colemandlut/MP2645A-BMS/design/02_afe-review-opus-r2.md

# 02_afe 第 2 轮独立复核（复核方：Claude Opus；画图方：DeepSeek）

> 时间：2026-09-27 JST
> 输入：
> - 快照 `review/02-r2/`（sch、erc.json、netlist.xml、sch.pdf 第 3 页）；
> - 第 1 轮快照 `review/02-r1/netlist.xml`；
> - `hardware/mp2645a-bms.kicad_pro`（网络类）；
> - 第 1 轮报告 `design/02_afe-review-opus.md`。
>
> 纪律：只读，没有改任何工程文件，没有运行 git。ERC 和网表由我在 `/tmp/r02/` 下独立重跑。
> **判定：P0 = 0，P1 = 0，P2 = 13（第 1 轮沿用 11 条，本轮新增 2 条版面小项）。02 页判为完成。**

## 0. 独立复跑

| 项 | 结果 |
|---|---|
| `cmp hardware/02_afe.kicad_sch review/02-r2/02_afe.kicad_sch` | 一致，快照就是现行图纸 |
| ERC `--severity-all`（根图） | 共 6 条，全部是 `isolated_pin_label`：DSG_G、CHG_G、SRP、SRN、FET_MID、PACK+。这些都是 01 页还没画的网络，与第 1 轮相同，0 error |
| 重跑网表与快照 `netlist.xml` 比较 | 去掉日期和 tstamp 后，diff 为空 |
| **r1 与 r2 网表逐项比较**（按网络节点集合、网络名、器件的 值/封装/LCSC/DNP、网络类） | 连接拓扑差异 **0**，网络名差异 **0**。器件只有 C209–C211 的 Value 字段变了。网络类只有 VCP 变了 |

## 1. 第 1 轮 P1 的落实情况

| # | 核对内容 | 结论 |
|---|---|---|
| P1-1 | C209、C210、C211 的 Value：`100nF 50V` → **`100nF 16V`**。LCSC 仍是 C1525，封装仍是 0402，两者都没变。与 BOM 第 26、27 行一致 | ✅ 关闭 |
| P1-2 | `.kicad_pro` 里的 `*/VC?` 已拆成 `*/VC0` … `*/VC8` 共 9 条。网表中 VC0–VC8 都是 `CELL_SENSE`，VCP 从 `CELL_SENSE,HV_SIG` 变为 **`HV_SIG`**。VTOP、PACKP、VMID、REG_C 仍是 HV_SIG，没有受影响 | ✅ 关闭 |
| P1-3 | 在 PDF 第 3 页目视逐项核对，见下面 9 个小项 | ✅ 关闭 |

P1-3 的逐项核对：
1. 标题栏 comment 已缩短为「8S LiFePO4 200A BMS · MPS MP2797 AFE · 8S 采集与保护」，完全在图框内。
2. 页首的画图过程文字（「第 1 轮已画完…164 个网表节点」）已删除。
3. §10 标题与说明不再重叠。
4. §4 标题已改为「8 串 9 路」。
5. C226 的「100nF 100V DNP」已回到 C226 下方，C220 旁边不再有 DNP 字样。
6. C219 的值已挪离 C226 的红叉。
7. C213、C221 的 GND 标签不再压在引脚上。
8. REG_C 的两个标签已上下分开。
9. SRN_F 与 GND 已分开。

## 2. P2（全部交用户定夺）

**第 1 轮沿用，P2-1 至 P2-11**，原文见 `design/02_afe-review-opus.md`：
1. GATE 类的间距应提到 0.6mm。
2. C212 在 29V 直流偏压下容量下降。
3. C213 在 29V 直流偏压下容量下降。
4. C221 可改用 C0G。
5. NTC 出板线缺少限流和 ESD 保护。
6. BAT+ 缺失时，C8 会反灌 VTOP/BAT+。
7. VTOP 进入 UVLO 后，整包会变砖。
8. 固件要清除 CELL_DEAD 持久标志。
9. CNTCB 10nF 和 CVREF 0402 的余量问题（U-9）。
10. Q201 的功耗上界为 285mW。
11. PACKP 的负向尖峰。

**本轮新增（纯版面，不影响网表）**：

| # | 位置 | 现象 | 建议 |
|---|---|---|---|
| P2-12 | §6，C219 | C219 的值「100nF 100V」挪到了电容左侧，紧挨着 R214 的「100Ω 1%」，读起来像 R214 的第二行参数 | 把值放到 C219 本体右侧（C219 位号的正下方） |
| P2-13 | §6 / §9 | ① C226 的位号压在它自己的 DNP 红叉下面，看不清。② 「§9 电源」标题的下沿贴着第一行说明「U1.45 VTOP…」。③ PACKP 与 C221 之间仍然叠着两个 `PACKP` 标签（与第 1 轮 REG_C 的情况相同） | 位号挪到红叉外面；标题下移约 1 格；删掉一个多余的标签 |

## 3. 覆盖清单（本轮）

- ⓪ 断线/死头、⓪b 同网多名：ERC 复跑为 0 error；网表拓扑与 r1 完全相同。第 1 轮已逐项核对的结论（48 脚、Figure 27/Table 18 外围件、均衡、耐压、极性件、J5、跨页接口）仍然有效。✅
- LCSC 与 BOM：53 个位号全部一致。C222–C226 带 dnp 属性，图上有红叉。✅
- 网络类：CELL_SENSE 与 HV_SIG 不再交叉匹配。✅
- 可读性：第 1 轮的 P1-3 已全部关闭。剩下的两项小瑕疵列为 P2-12 和 P2-13。✅
- 未核：01 页全部内容、PCB 布局（与第 1 轮相同）。
