colemandlut/MP2645A-BMS/design/02_afe-draw-report.md

# 02_afe 画图报告（第 1 轮 · 分段 A + B）

> **分段 B 的内容在 §6**（2026-09-27 17:00–17:15 JST），§1–§5 是分段 A 的原文（只订正了 §5.1 的
> D201 脚号说法，见 §6.5）。
> 时间戳：2026-09-27 16:00–17:15 JST　画图方：Claude（DeepSeek 画图泳道）
> 设计依据：`design/02_afe-spec.md`（含 §12.1b 用户决定 2026-09-27）
> 本段写入的文件**只有 4 个**：`hardware/02_afe.kicad_sch`、`hardware/gen/gen_02_afe.py`、
> `hardware/gen/check_02_layout.py`、本报告。库 / BOM / docs / 根图 / 其它子图都没动，
> 没跑 `tools/gen_kicad_skeleton.py`，没碰 git。

---

## 0. 本段结论（一句话）

分段 A 的三块（U1 48 脚、§9 电源、§6 高边驱动）已画完并跑通：
`check_02_layout.py` 检查 1–9 **全 PASS**（含 79 项网表逐脚核对），
`kicad-cli sch erc` 只剩 **18 条 `isolated_pin_label`**，全部是「标签挂在一根光棍上等 B/C 段接件」的预期现象，
已逐条列在本报告 §3。**净零意外**：ERC 里没有 `lib_symbol_issues`、没有 `footprint_link_issues`、
没有 `global_label_dangling`、没有 `pin_to_pin` 冲突。

---

## 1. 已画位号（17 个）

| 位号 | 值 / LCSC | 网络（脚 1 ↔ 脚 2，或 1/2/3） | 依据 |
|---|---|---|---|
| **U1** | MP2797DFP-0000-T / C18198873 | 48 脚全部引出，逐脚见 §2 | spec §1.3 |
| R212 | 20Ω 1% / C22950 | `BAT+` ↔ `VTOP` | §9.1 U-1 |
| C212 | 470nF 100V / C5375914 | `VTOP` ↔ `GND` | Table 18 Required |
| R213 | 510Ω 1% / C23193 | `BAT+` ↔ `REG_C` | §9.1 |
| C213 | 1µF 100V / C282823 | `REG_C` ↔ `GND` | §9.1 |
| Q201 | MMBT5551 / C2145 | 1=B `REGCTRL`、2=E `REGIN`、3=C `REG_C` | §9.1 外置 NPN |
| C214 | 10µF 10V / C19702 | `REGIN` ↔ `GND` | §9.1（U-4 改料） |
| C215 | 1µF 25V / C52923 | `AFE_3V3` ↔ `GND` | §1.3 脚 26（局部网络，**不接 +3V3**） |
| C216 | 1µF 25V / C52923 | `AFE_VDD` ↔ `GND` | §1.3 脚 27 |
| C217 | 1µF 25V / C52923 | `AFE_VREF` ↔ `GND` | §1.3 脚 22 |
| C218 | 10nF 50V / C15195 | `NTCB` ↔ `GND` | §1.3 脚 21（Table 18 上限 10nF） |
| R214 | 100Ω 1% / C25076 | `FET_MID` ↔ `VMID` | §6.3 |
| C219 | 100nF 100V / C28233 | `VCP` ↔ `VMID` | §6.3 |
| **C226** | 100nF 100V / C28233，**DNP** | `VCP` ↔ `VMID` | §6.3 备位，**见 §4.2 改名说明** |
| C220 | 100nF 100V / C28233 | `VMID` ↔ `GND` | §6.3 |
| R215 | 100Ω 1% / C25076 | `PACK+` ↔ `PACKP` | §6.4 |
| C221 | 10nF 100V / C282516 | `PACKP` ↔ `GND` | §6.4（Table 18「不得增减」） |

**U1 的 48 脚分布**：电芯脚 17（9 个接 `CELL0–CELL8` 的 RC 网络由 B 段补，8 个并到 `VC8`）、
电源/参考/地 10、电流采样 2、NTC 4、驱动/PACKP 3、通讯/中断 4、**NC 8**（29/33/34/35/36/37/40/41，都放了 NC 标志）。
`C9–C16` 用一条竖干（x=147.32，脚 6 的引线延长线）并到 `VC8`，干上 7 个 junction。

---

## 2. 脚本结构

### 2.1 `hardware/gen/gen_02_afe.py`（生成器，覆盖写出 02 页）

照 `gen_05_mcu_comm.py` 的骨架写，通用函数（`uid/fmt/esc/read_symbol/parse_pins`）是移植的，没改 04/05 的任何文件。

- `COMPONENTS` 是唯一的布局真源，9 元组 `(ref, 符号, 值, LCSC, x, y, rot, dnp, mirror)`。
- **U1 用 `(mirror y)`**（rot 0）——这样符号右侧的电芯脚落到图纸**左**边（x=152.4）朝向 B 段的 RC 阵，
  符号左侧的通讯/NTC/采样脚落到**右**边（x=187.96），符合 spec §11.3 的首选版面。
- 画法沿用 05 页的「标签岛」：每个两脚件自己一段 `[标签]—短线—件—短线—[标签]`，
  件与件之间**不拉导线**，靠标签同名连通。这样没有一根导线会横穿版面，§11.3「交叉少」自然满足。
  `hpart()` / `vpart()` 两个helper 封装这个惯用法（`vpart` 是 rot=90，脚 2 在上、脚 1 在下）。
- 符号从 `hardware/lib/jlc/jlc.kicad_sym` **原样复制**进 `lib_symbols`，只把顶层名改成 `jlc:NAME`；
  引脚名/类型/坐标一字未改。
- 全部端点落 1.27mm 栅格；uuid 用 `uuid5(NS, name)` 派生，脚本可反复跑、产物稳定。
- 版面分区写在本文件末尾的注释块里（①J5+NTC ②电芯 RC ③U1 ④右侧：§9 电源 / §6 驱动 / §5 采样 / §7 NTC / §8 通讯），
  B/C 段照着往里填即可。

### 2.2 `hardware/gen/check_02_layout.py`（自检，9 项）

1–8 项从 `check_05_layout.py` 移植（导线穿过非端点引脚 / 导线穿本体 / T 接点缺 junction /
标签压导线 / 引脚名互相粘连 / 字段压自己本体 / **跨器件**图元盒两两相交 / pymupdf 渲染文字复核），
只改了「符号变换要带 `(mirror y)`」这一处：`pin_world` 与 `pin_dir_world` 多一个 `mirror` 参数，
`load()` 从实例的 `(mirror y)` 读。

**第 9 项是本段新增的网表逐脚核对**（下面 §4.1 说明为什么非加不可）：
以**根图**为准导网表（`--format kicadxml`），
- 9a：U1 的 48 个脚逐个对 spec §1.3 的预期网络；
- 9b：8 个 NC 脚必须在 `unconnected-…` 网络上，且该网只有自己一个节点；
- 9c：分段 A 已画的 16 个外围件的每个端子对 §1.3/§6/§9 的预期网络（共 33 个端子）；
- 9d：DNP 件必须带 `(dnp yes)`，且非 DNP 件不许带；
- 9e：`U1.26`（3V3）不许落到 `+3V3`（§1.3 特别注明「局部，不接 +3V3」）；
- 9f：位号必须是「字母前缀 + 纯数字」（§4.2 的教训）。

环境变量 `AFE_HW` 可换掉硬件目录，专供负例验证用（**第 2 轮补了 10–13 项**，见 §8.3）。

**第 2 轮补充（2026-09-27）**：`check_02_layout.py` 里新增 **墨迹盒**模型
（`ink_width` / `ink_bbox`，标定见 §8.3）与检查 **10/11/12/13**：
标签墨迹压本体、标签叠标签、字段归属跑到别人器件那边、说明文字互压。
`labels` 元组从 8 元扩到 11 元（补字高/水平对齐/垂直对齐），`prop_texts` 从 9 元扩到 10 元。

### 2.3 跑法

```bash
python3 hardware/gen/gen_02_afe.py                    # 生成（幂等）
python3 hardware/gen/check_02_layout.py               # 13 项自检（1–9 + 墨迹版面 10/11/12/13）
AFE_HW=review/02-r1 python3 hardware/gen/check_02_layout.py   # 负例：对冻结的第 1 轮快照跑（应 FAIL 10 条）
kicad-cli sch erc -o /tmp/erc.rpt --severity-all hardware/mp2645a-bms.kicad_sch   # ERC 必须以根图为准
```

**本段实测结果**（2026-09-27 17:0x JST）：

```
图元解析：导线 74 段，junction 7 个，实例 17 个，引脚 81 个，文字 77 处，引脚名 81 个，图元盒 132 个
渲染复核：PDF 文字串 256 段（去重+合并后），字段认领 34/34 个
网表核对：逐脚核对 81 项（U1 48 脚 + 外围件 33 端子）
PASS：检查 1/2/3/4/5/6/7/8/9 全部通过          exit=0

Found 18 violations
```

---

## 3. ERC 的 18 条（全部是预期，全部是 `isolated_pin_label`）

标签只挂了一个脚。这 18 个网络的对端件分别在 B/C 段或 01 页，本段就是「先立柱、后接件」：

| 网络 | 归属 | 等谁来接 |
|---|---|---|
| `VC0`–`VC7` | U1.14–7 | B 段：R201–R208 + C201–C208（电芯 RC） |
| `SRP_F`、`SRN_F` | U1.15/16 | B 段：R210/R211 + C209/C210/C211 |
| `NTC_CELL1/2`、`NTC_FET`、`NTC_SHUNT` | U1.20/19/18/17 | C 段：R216–R219 + C222–C225 + J5 |
| `FET_MID` | R214.1 | 01 页（`FET_MID` 是跨页全局标签，01 页已有） |
| `PACK+` | R215.1 | 01 页 |
| `DSG_G`、`CHG_G` | U1.39/44 | 01 页（驱动网络） |

`BAT+`、`GND`、`+3V3`、`AFE_ALERT`、`AFE_WAKE`、`I2C_SCL`、`I2C_SDA`、`CELL0–CELL8` 这些跨页标签**没有**告警——
它们在根图范围内找到了对端（U6/F11 那侧），说明接口契约是通的。

---

## 4. 本段挖出来的两个坑（都已写进知识库）

### 4.1 `(mirror y)` 会把字段的**水平对齐一起翻转**；连带发现检查 1–8 对 mirror 不敏感

U1 镜像后，位号字段锚点 154.94 却渲染在 152.16–154.70（PDF 实测），
也就是 `(justify left)` 被镜像翻成了**右对齐**，自检的 8a（文字中心 = 锚点）连报两条 FAIL。
**正解：U1 的字段一律用「居中」对齐（干脆不写 `justify` 节点）**——居中对镜像免疫，也正好符合 8a 的判据。

更要紧的是**负例验证的结果**：按知识库的规矩「新检查写完要做负例验证，否则可能是空跑」，
我把 `pin_world`/`pin_dir_world` 的 mirror 分支屏蔽掉（`AFE_HW` 指向一份把 U1 的 `(mirror y)` 删掉的副本），
**检查 1–8 依旧全 PASS**——因为它们比的全是「我自己算的几何 vs 我自己算的几何」，镜像一错就两边一起错。
那次副本的网表里 `U1.1` 已经接到了 `VCP` 上（灾难性接错），几何检查一声不吭。
**这就是第 9 项（网表逐脚核对）的由来**：它量的是 KiCad 自己连出来的网，不吃我自己的几何。

九项检查的负例验证记录：

| 检查 | 负例做法 | 结果 |
|---|---|---|
| 1–8 | `AFE_HW` 指向「U1 去掉 `(mirror y)`」的副本 | **不报**（见上，故补第 9 项） |
| 9a | 同上 | 报 45 条，如 `[9a] U1.1 网络 'VCP'，规格书 §1.3 要求 'VC8'` ✅ |
| 9b | 伪造「NC 网络挂了 2 个节点」的网表喂进去 | 报 `[9b] NC 网络 unconnected-(U1-WDT-Pad29) 挂了 2 个节点` ✅ |
| 9c | 内存里把 `R214.2` 的预期改成 `PACKP`、加一个不存在的 `C999` | 报 `R214.2 网络 'VMID' 要求 'PACKP'`、`网表里没有 C999` ✅ |
| 9d | 把副本里的 `C226` 改名回去 | 报「找不到 C226」「C219B 意外标了 (dnp yes)」✅ |
| 9e | —— | **本页不会触发的守卫**（专盯 §1.3 脚 26 那条注），未做负例 |
| 9f | 把副本里的 `C226` 改回 `C219B` | 报 `[9f] 位号 'C219B' 不合法` ✅ |

### 4.2 规格书 §6 的位号 `C219B` 是**非法位号**，已改 `C226`

根图导网表一直报 `Warning: schematic has annotation errors`。查了一圈：全工程 0 个 `?` 位号、
0 个跨页重号、02 页单独导出**不报**。二分定位到 **`C219B` 这一个实例**——
KiCad 的 annotator 只认「字母前缀 + 纯数字」，尾随字母解析不出序号，于是整张图被判「标注有错」。
改名 `C226`（2xx C 段里 222–225 已留给 NTC 的 DNP 电容）后警告消失。
**这位号是 spec 写的，B 段/C 段画图时别再照抄；`docs/02-BOM.csv` 需要主代理同步这一格。**

> 顺带确认：`Warning: schematic has annotation errors` 与「B/C 段未画」无关，是本段引入的真缺陷，已修。

---

## 5. 留给分段 B / C 的清单

### 5.1 分段 B（电芯 RC + 采样 + 通讯，版面在 x 65–133 与 x 300–360）

| 位号 | 值 / LCSC | 网络 | 备注 |
|---|---|---|---|
| R201–R209 | 33Ω 1% 0805 / C17634 | `CELL0`→`VC0` … `CELL8`→`VC8` | 每只最坏 67mW，§4.3 |
| C201–C208 | 100nF 50V X7R **0402** / C307331 | `VC1`–`VC0` … `VC8`–`VC7` | **8 只不是 9 只**，C0 对地没有电容 |
| D201 | BZT52C3V3 / C353528 | **K→`VC0`，A→`GND`** | 脚 1 在左（脚名 `C`）、脚 2 在右（`A`），见 §6.5 |
| R210, R211 | 100Ω 1% / C25076 | `SRP`→`SRP_F`、`SRN`→`SRN_F` | |
| C209 | 100nF / C1525 | `SRP_F` ↔ `SRN_F` | 差模 |
| C210, C211 | 100nF / C1525 | 各对 `GND` | 共模 |
| R220, R221 | 2.2k 1% / C25879 | `I2C_SCL`/`I2C_SDA` 上拉到 `+3V3` | |
| R222 | 100k 1% / C25741 | `AFE_ALERT` 下拉到 `GND` | **`AFE_ALERT` 是全局标签，A 段已用 `output` 形状，这里必须照抄 `output`**，否则 ERC 报 `pin_to_pin` |
| R223 | 10k 1% / C25744 | `AFE_WAKE` 上拉到 `+3V3` | `AFE_WAKE` 在 A 段是 `input` |

### 5.2 分段 C（J5 + 线束 NTC + 收尾）

| 位号 | 值 / LCSC | 网络 | 备注 |
|---|---|---|---|
| R216–R219 | 10k 1% / C25744 | NTC 各脚上拉到 `NTCB` | |
| C222–C225 | **1nF DNP** / C1523，带 `(dnp yes)` | NTC 各脚到 `GND` | 值写「1nF DNP」 |
| J5 | XH 2.50mm 13P / C40669 | 线束 NTC、均衡、温度 | 1 脚方焊盘 |
| RT1–RT4 | —— | **不在本页** | 移到线束（U-2）/ 01 页 |

### 5.3 给 B/C 的三条硬约束

1. **全局标签的形状必须与 A 段一致**（同页同名标签形状不同会触发 ERC 冲突）。
   A 段 `SHAPE` 表：`output` = `CHG_G`/`DSG_G`/`AFE_ALERT`；`input` = `BAT+`/`PACK+`/`FET_MID`/`GND`/`+3V3`/`AFE_WAKE`/`I2C_SCL`/`I2C_SDA`；
   `passive` = `CELL0..CELL8`/`SRP`/`SRN`/`NTC_*`。新加的同名标签照抄。
2. **U1 是 `(mirror y)` 的**：字段对齐只能用居中（不写 `justify`），写 `justify left` 会渲染成右对齐。
   U1 左边（x=147.32）是电芯脚、右边（x=193.04）是通讯/NTC/采样脚，别按符号库的左右直觉摆。
3. **每加一批件，`check_02_layout.py` 的 `PART_EXPECT` 要同步扩表**，否则 9c 覆盖不到新件
   （这也是「网表核对 81 项」这个数字会随分段变大的原因）。

---

## 6. 分段 B 完成情况（2026-09-27 17:00–17:15 JST）

> 本段只动 4 个文件：`hardware/02_afe.kicad_sch`、`hardware/gen/gen_02_afe.py`、
> `hardware/gen/check_02_layout.py`、本报告。库 / BOM / docs / 根图 / 其它子图**未动**，
> 未跑 `tools/gen_kicad_skeleton.py`，未碰 git。
> 产物 md5：**`d92a9e7589aff4462ca441d922095520`**（连跑两次一致）。

### 6.1 本段新增 24 个位号（分段 A 的 17 个未改）

| 位号 | 值 / LCSC | 网络（脚 1 ↔ 脚 2） | 依据 |
|---|---|---|---|
| J5 | XH-13A 13P / C40669 | 1 `NTC_CELL1`、2 `GND`、3 `NTC_CELL2`、4 `GND`、5–13 `CELL0`–`CELL8` | spec §10 |
| R201–R209 | 33Ω 1% 0805 / C17634 | `CELLn` → `VCn`（n = 0…8） | §4.1 |
| C201–C208 | 100nF 50V X7R 0402 / C307331 | `VCn` ↔ `VCn+1`（n = 0…7，**8 只**） | §4.1 |
| D201 | BZT52C3V3 / C353528 | 1（脚名 `C`）→ `VC0`，2（脚名 `A`）→ `GND` | §4.2 |
| R210 | 100Ω 1% / C25076 | `SRP` → `SRP_F` | §5 |
| R211 | 100Ω 1% / C25076 | `SRN` → `SRN_F` | §5 |
| C209 | 100nF 50V / C1525 | `SRP_F` ↔ `SRN_F`（差模） | §5 |
| C210 | 100nF 50V / C1525 | `SRP_F` ↔ `GND`（共模，rot 90） | §5 |
| C211 | 100nF 50V / C1525 | `SRN_F` ↔ `GND`（共模，rot 90） | §5 |

至此本页共 **41 个实例 / 140 个引脚**。三种网络类的字面匹配核对：

- `*/VC?`：本页 `VC0`–`VC8` 全部以局部标签出现（`lbl`），共 9 个名字，U1.6–14 侧同样以 `VC0`–`VC8` 命名 → **匹配上**。
- `KELVIN`：`SRP`/`SRN` 是全局标签（沿用 A 段 `passive` 形状），`SRP_F`/`SRN_F` 是本页局部标签，
  与 U1.15/16 的脚名对应 → 网络类按 `SRP`/`SRN`/`SRP_F`/`SRN_F` 匹配即可。
- 本页**不出现任何 `BAL*` 网络**（9g 专门守这条，spec §4.4）。

### 6.2 版面说明

- **J5** 落在 **(44.45, 88.90)**，脚 1 的世界坐标 x = 40.64，脚 1…13 的 y = 73.66 → 104.14（2.54 间距）。
  每脚一根 2.54mm 短线往左到 x = 38.10 再挂标签，13 个标签同列竖直排开，不与 §4 的 RC 阵相碰。
  位号/值字段用 `PROP_OVERRIDE` 压到 J5 本体的上下方（`center`，避开 13 根引脚名）。
- **§4 电芯 RC 阵**在 ②区，x ≈ 62–136。行距取 **7.62mm**（不是 5.08mm）：0402 本体 ±2.03 高，
  5.08 行距下相邻两行的预测字段盒会相交；7.62 下每行左右并排放
  `位号 (x−6.35, y−3.81)` / `值 (x+6.35, y−3.81)`，居中，互不重叠。
- **§5** 在 x ≈ 305–375、y 105–150。R210/R211 同一列（x = 325.12，y = 127.00 / 146.05），
  C210/C211 rot 90 挂在同一 y 上，C209 横跨 `SRP_F`↔`SRN_F`。
- **§4 文字块的 1.27mm 上移**（重要，见 §6.3 的教训）：第三行说明文字原锚在 61.60，
  渲染墨迹到 y = 64.0，正好压住第 0 行（R201/D201）的字段文字（y 63.9–65.8）。
  现把整块上移 1.27mm：标题 50.80、正文 55.25 / 57.79 / 60.33，渲染墨迹止于 62.7 →
  **净空 1.2mm**。推导过程写在生成器源码里 §4 文字段上方的注释中。

### 6.3 本段实测

```
图元解析：导线 133 段，junction 7 个，实例 41 个，引脚 140 个，文字 149 处，引脚名 140 个，图元盒 263 个
渲染复核：PDF 文字串 409 段（去重+合并后），字段认领 82/82 个
网表核对：逐脚核对 140 项（U1 48 脚 + 外围件 92 端子）
PASS：检查 1/2/3/4/5/6/7/8/9 全部通过          exit=0

 ** ERC messages: 8  Errors 0  Warnings 8     （全部 isolated_pin_label，见 §6.4）

python3 -m unittest discover -s tests   →  Ran 21 tests … OK
make -C firmware test                   →  38/38 checks passed
```

生成器幂等：连跑两次 md5 均为 `d92a9e7589aff4462ca441d922095520`。

本段新增/改动的检查都做了负例验证（照知识库「新检查不做负例可能是空跑」的规矩）：

| 检查 | 负例做法 | 结果 |
|---|---|---|
| 9g（无 `BAL*` 网络） | 内存里把 `R201.2` 的预期网络改成 `BAL0` 喂进去 | 报 `[9g] R201.2 落在均衡网络 'BAL0' 上…` ✅ |
| 9c（本段新件） | 内存里把 `C210.1` 的预期从 `GND` 改成 `SRN_F` | 报 `C210.1 网络 'GND' 要求 'SRN_F'` ✅ |
| 9c（D201 极性） | 内存里把 `D201` 的两个端子对调 | 报 `D201.1 网络 'GND' 要求 'VC0'` ✅ |

### 6.4 ERC 的 8 条（全部预期，全部 `isolated_pin_label`）

A 段的 18 条里有 10 条被本段接掉了（`VC0`–`VC7`、`SRP_F`、`SRN_F` 都找到了对端），
ERC 从 18 条降到 **8 条**，Errors 0。剩下的 8 条按「等谁接」分两类：

| 网络 | 挂在哪 | 等谁接 |
|---|---|---|
| `NTC_FET`、`NTC_SHUNT` | U1.18/17 | **分段 C**：R216–R219 + C222–C225 |
| `SRP`、`SRN` | R210.1 / R211.1 | **01 页**（开尔文取样来自分流器，跨页全局标签） |
| `FET_MID` | R214.1 | **01 页**（驱动回路中点） |
| `PACK+` | R215.1 | **01 页**（电池组正极） |
| `DSG_G`、`CHG_G` | U1.39/44 | **01 页**（高边驱动栅极） |

已 grep 确认：01 页与其余子图**当前都还没有**这 8 个网络，所以它们是「接口先立、对端后到」，
不是本页缺陷；`BAT+`/`GND`/`+3V3`/`AFE_ALERT`/`AFE_WAKE`/`I2C_SCL`/`I2C_SDA`/`CELL0`–`CELL8`
在根图范围内都能找到对端，**无告警**。

> **订正（分段 C，见 §7.4）**：本段把 `NTC_FET`/`NTC_SHUNT` 接掉（R216–R219 + C222–C225），
> ERC 从 8 条降到 **6 条**。剩下 6 条（`SRP`/`SRN`/`FET_MID`/`PACK+`/`DSG_G`/`CHG_G`）**全部**是
> 01 页的对端 —— 01 页与 03 页**至今仍是空壳子图**，所以这 6 条在第 1 轮结束时的正确状态就是「等 01 页」，
> 不是本页缺陷。01 页画完后应当归零。

### 6.5 两处订正

1. **§5.1 表里 D201 的「脚号」说法已订正**：库符号里 `C`/`A` 是**引脚名**，
   **引脚号是 `1`/`2`**。`PART_EXPECT` 按引脚号（网表口径）写，故为 `{"1": "VC0", "2": "GND"}`。
   画法上 `hpart()` 脚 1 在左、脚 2 在右 → 阴极（`C`）朝 `VC0`、阳极（`A`）朝 `GND`，与规格书一致。
2. **`C219B` → `C226` 已同步**：主代理改了规格书/BOM，本段生成器与 A 段一致沿用 `C226`，
   9f/9d 都会守这条。`docs/02-BOM.csv` 里那一格仍需主代理同步（本段不许改 docs）。

### 6.6 留给分段 C 的清单（更新版）

| 位号 | 值 / LCSC | 网络 | 备注 |
|---|---|---|---|
| R216–R219 | 10k 1% / C25744 | NTC 各脚上拉到 `NTCB` | 接 U1.21 与 J5.1/3 |
| C222–C225 | **1nF DNP** / C1523，带 `(dnp yes)` | NTC 各脚到 `GND` | 值写「1nF DNP」，**并把 C222–C225 加进 9d 的 DNP 清单** |
| R220, R221 | 2.2k 1% / C25879 | `I2C_SCL`/`I2C_SDA` 上拉到 `+3V3` | 形状照抄 A 段 `input` |
| R222 | 100k 1% / C25741 | `AFE_ALERT` 下拉到 `GND` | `AFE_ALERT` 是全局标签，A 段用的是 **`output`**，必须照抄，否则 ERC 报 `pin_to_pin` |
| R223 | 10k 1% / C25744 | `AFE_WAKE` 上拉到 `+3V3` | `AFE_WAKE` 在 A 段是 `input` |

C 段还要做：`RT1–RT4` **不在本页**（移到线束，U-2）；J5 上还剩 4 个空脚位（1/2/3/4 已用），
线束 NTC 的接法按 spec §7 / §10 落；收尾把本页的「分段 A+B 已画…」进度文字改成全页版。

---

# 7. 分段 C 完成情况 / 第 1 轮完成（2026-09-27 JST · 收尾段）

## 7.1 本段新增 12 个位号（A 段 17 + B 段 24 未改，17+24+12 = 全页 53 件）

| 位号 | 值 | LCSC | DNP | 网络 / 说明 |
|---|---|---|---|---|
| R216–R219 | 10k 1% | C25744 | | NTC_CELL1/2、NTC_FET、NTC_SHUNT 各上拉到 `NTCB`（**不是 3V3**） |
| C222–C225 | 1nF | C1523 | **DNP** | NTC 各脚到 `GND`，值写「1nF DNP」并带 `(dnp yes)` |
| R220 | 2.2k 1% | C25879 | | `I2C_SCL` 上拉 `+3V3` |
| R221 | 2.2k 1% | C25879 | | `I2C_SDA` 上拉 `+3V3` |
| R222 | 100k 1% | C25741 | | `AFE_ALERT` **下拉**到 `GND`（xALERT 推挽、ALERT_POL 默认高有效） |
| R223 | 10k 1% | C25744 | | `AFE_WAKE` 上拉 `+3V3`（**不是 `AFE_3V3`**） |

## 7.2 全页位号表（53 件，与本页 BOM 一一对应）

| 位号 | 值 | LCSC | DNP |
|---|---|---|---|
| U1 | MP2797DFP-0000-T | C18198873 | |
| R201–R209 | 33Ω 1% | C17634 | |
| C201–C208 | 100nF 50V | C307331 | |
| D201 | BZT52C3V3 | C353528 | |
| R210, R211, R214 | 100Ω 1% | C25076 | |
| R215 | 100Ω 1% | C25076 | |
| C209–C211 | 100nF 50V | C1525 | |
| C212 | 470nF 100V | C5375914 | |
| R213 | 510Ω 1% | C23193 | |
| R212 | 20Ω 1% | C22950 | |
| C213 | 1µF 100V | C282823 | |
| Q201 | MMBT5551 | C2145 | |
| C214 | 10µF 10V | C19702 | |
| C215–C217 | 1µF 25V | C52923 | |
| C218 | 10nF 50V | C15195 | |
| C219, C220, C226 | 100nF 100V | C28233 | C226 = **DNP** |
| C221 | 10nF 100V | C282516 | |
| J5 | XH-13A 13P | C40669 | |
| R216–R219, R223 | 10k 1% | C25744 | |
| C222–C225 | 1nF | C1523 | **4 件 DNP** |
| R220, R221 | 2.2k 1% | C25879 | |
| R222 | 100k 1% | C25741 | |

**本页具名外部器件（不在本页、由线束或别的页承担）**：RT1–RT4（NTC 热敏电阻，改为线束件 U-2，
本页用 J5.1/3 引出 `NTC_CELL1/2`，`NTC_FET`/`NTC_SHUNT` 到 01 页）；Q_DRV/DZ/PNP 快关网络与
分流器 SRP/SRN 本体在 01 页；`AFE_ALERT`/`AFE_WAKE`/`I2C_SCL`/`I2C_SDA` 的对端是 05 页的 U6。

## 7.3 U1 48 脚逐脚复核：**通过**

网表（根图导出的 kicadxml）逐脚核对 164 项（U1 48 脚 + 外围 116 端子），结论：

- **8 个 NC 脚**（29 WDT / 33 SDO / 34 / 35 GPIO2 / 36 GPIO1 / 37 GPIOHV1 / 40 N/C / 41 SBYDSG）
  在网表里全部是 `unconnected-…` / `N/C-Pad…` 伪网络 → NC 标志生效，**WDT 未接任何东西**；
- **C9–C16（脚 5,4,3,2,1,48,47,46）全部在 `VC8`** 上，不串电阻、不加电容（Table 23 directly connect）；
- 脚 42 = `VCP`，与 `VMID` 之间只有 C219（`C220` 才是 VMID→GND）；
- 电芯链路：`CELLn —R20(n+1)— VCn`（8 条）、`VC(n−1) —C20(n+1)— VCn`（8 条，C201 跨 VC0–VC1 … C208 跨 VC7–VC8）；
- D201：脚 1（C，阴极）→ `VC0`，脚 2（A，阳极）→ `GND`；
- 通讯：`AFE_ALERT` = R222 + U1.28 + U6.40，`AFE_WAKE` = R223 + U1.30 + U6.41，
  `I2C_SCL` = R220 + U1.31 + U6.42，`I2C_SDA` = R221 + U1.32 + U6.43 —— **05 页那四个网络已不是单脚网络**。

## 7.4 自检结果

`python3 hardware/gen/check_02_layout.py` → **`PASS：检查 1/2/3/4/5/6/7/8/9 全部通过`**

```
图元解析：导线 157 段，junction 7 个，实例 53 个，引脚 164 个，文字 192 处，引脚名 164 个，图元盒 323 个
渲染复核：PDF 文字串 494 段（去重+合并后），字段认领 106/106 个，自由文字两两比对 579 段（原始 span）
网表核对：逐脚核对 164 项（U1 48 脚 + 外围件 116 端子）；Footprint/LCSC 核对 53 件
```

- 幂等：连续两次 `gen_02_afe.py` 的 md5 一致 = **`2edd200d19fc3adc0ca4ba8d5560984f`**（209495 字节）。
  （任务书里的 `d92a9e7589aff4462ca441d922095520` 是分段 B 的产物 md5，本段改动后自然变化。）
- 根图 ERC：**6 条 `isolated_pin_label`**，全部是 01/03 页尚未画出的网络，逐条列出：
  `DSG_G`(02:147.32,124.46)、`CHG_G`(02:147.32,182.88)、`SRP`(02:314.96,127.00)、
  `SRN`(02:314.96,146.05)、`FET_MID`(02:320.04,66.04)、`PACK+`(02:320.04,86.36)。
  对端分别是 01 页的隔离驱动/分流器/功率回路，本页无一条属于「本页该配的对端没配」。
  单跑 02 页 ERC 另有 53 条 `lib_symbol_issues` + 53 条 `footprint_link_issues`，那是缺工程库配置的
  固有噪声（知识库已记），**判据以根图为准**。
- 测试：`python3 -m unittest discover -s tests` = **21/21 OK**；`make -C firmware test` = **38/38 checks passed**。
- 出图目视：`kicad-cli sch export pdf` → PNG 全页 + 局部 600dpi 裁图逐块看过（§4–§10 各段、标题栏、J5、NTC、通讯）。

## 7.5 负例验证（本段新增/改写的检查项，逐条记）

| 检查 | 缺陷怎么造的 | 结果 |
|---|---|---|
| 8e（原始 span 两两比） | 把 §9 第 4 行改回改短前的长文本（真实缺陷：压住 `AFE_3V3` 标签） | 报 2 条，纵向重叠 1.026mm = 较矮 span 的 **54%**，无假报 |
| 8f（越框） | 把 §9 第 3 行的 x 从 210.82 改成 370 | 报 1 条：`(369.92, 50.294) → (420.318, 53.19)` 越出 410 |
| 9d/9h/9i（DNP / Footprint+LCSC / 逐脚） | 分段 B 已做过，本段沿用 | 见 §6.3，结论未变 |

反面证据（说明旧的 8e 为什么是空跑）：改 8e 之前，**上面那条真实缺陷在页面上存在了整整两段而检查全 PASS**，
因为旧的 8e 比的是合并后的 runs，而**互相压着的两段文字水平间隙是负的、必然被合并成一段**。

## 7.6 本段挖出来的坑（都已写进知识库）

1. **合并 span 会让重叠检查失明**（最重要）。`rendered_runs()` 的合并规则是「同一行、水平间隙 ≤1.6mm
   就并」，压着的两段文字间隙为负 → 必并 → 8e 永远看不见。新增 `rendered_spans()`（去重但不合并），
   8e 改用它之后立刻报出 **3 类、共 13 处**此前被藏起来的真缺陷。
2. **pymupdf 的 span bbox 不是墨迹**：含字体上/下伸部。同一段文字块里相邻两行（标题 2.4 号压正文 1.8 号）
   的 bbox 会互相穿 0.948mm；J5 位号字段压说明文字 0.929mm。所以 8e 的判据最终定成
   **「纵向重叠 / 较矮 span 高度 > 45%」**（真缺陷 54% vs 假重叠 ≤39%，实测标定）。
   曾试过「按左端是否对齐分档」，失败：同一行文字会被拆成多个 span，左端并不相等。
3. **A3 图框实测**：矩形 x 10.0→410.0、y 10.0→287.0 mm（旧代码写 `PAGE_MARGIN=8.0` 是错的）；
   KiCad 自带的标题栏文字会画到 x≈418.94（**越框**），所以 8f 必须豁免标题栏区域
   `(295.0, 250.0, 420.0, 297.0)`。
4. **笔画字体步进标定**：`宽 = size × (0.9507×窄字数 + 1.3120×宽字数)`，宽字 = U+3000–303F /
   4E00–9FFF / FF00–FFEF / 2E80–2EFF。实测 §9 第 1 行预估 69.34mm、实渲 67.45mm（**高估 2.8%**，
   保守方向正确）。本段所有说明文字的重排都用它先算宽度再落笔。

## 7.7 本段订正的既有缺陷（分段 A/B 带进来的）

| # | 缺陷 | 位置 | 处理 |
|---|---|---|---|
| 1 | §9 说明与 §6 说明**同一 y 上横向压 7.9mm** | §9 x→312.7 vs §6 x 304.72 起 | §9 整块重排为 y 45.72–53.34 四行、每行 ≤89mm |
| 2 | §10 说明第 2 行（写到 x=74）压 §4 表头 | §4 表头 x 63.36–95.13 | §10 说明压到 ≤46.8mm，收在 x≤59 |
| 3 | C220 的 Value 写到 x≈413 **越框** | §6 | C220 左移到 384.81；`PROP_OVERRIDE` 给 C226 单独挪 Value（否则与 C220 同行相撞） |
| 4 | §9 第 4 行压 `AFE_3V3` 标签 1.03mm | §9 | 该行改短为「C213 1µF、R213 510Ω：REG_C→BAT+。」（实测收在 x≈262.7，留 2.3mm） |
| 5 | 本段自查时的一次失误：改 §9 时**漏删**原来 y 48.26 的那一行，页面上同一行出现新旧两段文字 | §9 | 新 8e 立刻报 13 条，删掉旧行后归零 —— 也算 8e 的一次实战负例 |

## 7.8 规格书 §13 自检清单（逐条打勾）

1. ☑ U1 48 脚逐脚对 §1.3：8 个 NC 脚都放了 NC 标志；C9–C16 都在 `VC8`；WDT 没接任何东西（见 §7.3）。
2. ☑ `CELLn`–`VCn` 之间只有 R20(n+1)（8 条）；`VC(n−1)`–`VCn` 之间只有 C20(n+1)（8 条）；
   任何 `CELLn` 都不与 `GND` 相连（J5 的 2/4 脚才是 GND）。
3. ☑ D201 阴极（1 脚）在 `VC0`、阳极（2 脚）在 `GND`。
4. ☑ `AFE_3V3` 只有 U1.26 与 C215 两个节点；`+3V3` 在本页只连 R220/R221/R223。
5. ☑ `NTCB` = U1.21 + C218 + R216–R219 上端（6 个节点），四路上拉全接 `NTCB`。
6. ☑ C219 两端 = `VCP`/`VMID`（不接 GND）；C220 = `VMID`/`GND`；R214 = `FET_MID`/`VMID`。
7. ☑ R215 两端 = `PACK+`/`PACKP`；C221 = `PACKP`/`GND`，10nF/100V C282516 未改值。
8. ☑ `SRP`→R210→U1.15、`SRN`→R211→U1.16 未接反；C209 跨 `SRP_F`↔`SRN_F`；C210/C211 各自到 GND。
9. ☑ Q201：1(B)=`REGCTRL`、2(E)=`REGIN`、3(C)=`REG_C`；R213 与 C213 都在 `REG_C` 上。
10. ☑ R222 是**下拉**到 GND；R223 接 `+3V3`（不是 `AFE_3V3`）。
11. ☑ J5：1=`NTC_CELL1`、2=`GND`、3=`NTC_CELL2`、4=`GND`、5–13=`CELL0…CELL8`；1 脚方焊盘。
12. ☑ 每颗件 `LCSC` 与 §2.2 一致（53 件逐件核过，0 缺失）；C222–C225 标 DNP；C214 = C19702。
13. ☑ ERC（本页）为 0 条真实违规；根图跨页 `isolated_pin_label` 只有 6 条，全部落在 01/03 页尚未画出的
    网络上（`DSG_G`/`CHG_G`/`SRP`/`SRN`/`FET_MID`/`PACK+`，见 §7.4）。

## 7.9 建议（给复核方 / 下一轮）

1. **合并 span 是个通用陷阱**，04/05 页的自检脚本若有「比文字盒」的项，建议照 §7.6.1 换成原始 span；
   阈值照 §7.6.2 用「重叠比例 > 45%」。
2. 页面上还有 **13 处说明文字**是分段 A/B 排的，本段只修了互相压字的那几处；复核方若再动版面，
   请先跑 `check_02_layout.py`，8e/8f 现在真的会报。
3. 01 页画完后，`DSG_G`/`CHG_G`/`SRP`/`SRN`/`FET_MID`/`PACK+` 六条应自动消失；
   若届时还在，说明 01 页的标签形状或名字对不上，**不要**改 02 页去迁就。
4. `AFE_ALERT` 的形状仍按 A 段的 `output`（若改成 `input` 会与 05 页的 MCU 脚构成 `pin_to_pin`）。
5. docs/02-BOM.csv 里 `C226` 那一格仍需主代理确认（本段不改 docs）。

---

# 8. 第 2 轮变更（按 Opus 复核改，2026-09-27 JST）

**前置核对**：动手前 `python3 hardware/gen/gen_02_afe.py` 连跑两次字节相同，
md5 = `2edd200d19fc3adc0ca4ba8d5560984f`（209495 字节），与任务书给的改前指纹一致。
改后 md5 = `3ee64cc3bd6982abc188506395bb2604`（208998 字节），再连跑两次仍相同（幂等）。

**本轮只改字段与版面，未改任何连接**：以根图 `kicad-cli sch export netlist --format kicadxml` 导出
「位号.脚 → 网络」逐行排序后与改前比，**325 行 0 差异**（含 `unconnected-…` 的 NC 网络）。

## 8.1 任务书逐条

| # | 任务书要求 | 本轮改动 |
|---|---|---|
| P1-1 | C209/C210/C211 值 `100nF 50V` → `100nF 16V` | 三行 Value 文本改掉（料号 `CL05B104KO5NNNC`/C1525 本来就是 16V，与 BOM 口径一致）；网络与料号未动 |
| P1-3a | 标题栏 comment 越框 → 缩短/去掉 | comment 1 缩成「8S LiFePO4 200A BMS · MPS MP2797 AFE · 8S 采集与保护」，渲染实测收在 **x=368.15**（改前 418.94，图框右界 410.0） |
| P1-3b | 删画图过程文字；§10 标题与下方说明重叠 → 挪开 | 「第 1 轮已画完（分段 A+B+C）…全页 53 器件、164 个网表节点」整条删除（文字从 192 处降到 191 处）；§10 标题 y 45.72 → **43.18**（墨迹 42.62–46.16，与说明首行留 1.61mm） |
| P1-3c | C226 的位号与「DNP」挪到 C226 旁边 | C226 位号/值都改成**居中于 C226 自己的轴 x=374.65**（位号 y 63.50、值 y 75.57）；C210/C211 随之右移 11.43 → x=381.00 腾开字段列（原 369.57 使两边字段都落在 374.65） |
| P1-3d | C213 的 GND 不压引脚；两个 REG_C 只留一个/分开；SRN_F 与 GND 分开 | ① C213 由 rot=90 改 **rot=0**（引脚竖直），GND 全局标签落到 (255.27, 91.44)，离本体 1.0mm；② C213 上端的 REG_C 随之从 (245.11,83.82) 移到 (250.19,78.74)，与 R213/S 段的 REG_C (238.76,86.36) 由「墨迹横向重叠 91%」变成隔开 11.43×7.62mm；③ C210/C211 右移后，C209 的 SRN_F（左对齐锚 360.68）与 C210 那对标签由 8.89mm 拉到 **20.32mm** |
| P1-3e | 标题「§4（9 串）」→「§4 电芯采样（8 串 9 路）」 | 已改（VC8 那一路是参考地，实际 8 串） |
| 3 | 自检补漏：能抓 b/c/d 四类，并用改前产物做负例 | 新增**墨迹盒模型 + 检查 10/11/12/13**，见 §8.2–8.4 |

## 8.2 新增的墨迹盒模型（`ink_width` / `ink_bbox`）

旧的 `text_width`（0.6×size/拉丁字、1.0×size/汉字）比实测**低估拉丁字约 50%**，`text_bbox`（±size/2）
纵向也偏小 —— 所以「标签压本体」「字段跑到别人器件上」这两类在检查 1–7 里根本量不出来。
本轮按 PDF 实测重新标定（`h` = 字号）：

- 墨迹高度 **1.50h**；拉丁字宽 **0.92h/字**，汉字 **1.50h/字**；
- 锚点 → 墨迹盒：`top` = `[y−0.25h, y+1.25h]`、`bottom` 对称、居中 ≈ `y±0.75h`（有约 0.2mm 系统偏差）；
- **全局标签**的文字画在图形框里，模型盒比真实文字整体偏左约 2.0mm，所以对全局标签额外
  加 `GLBL_PAD = 2.0` 的水平保守外扩（宁可多报，不可漏报）。

## 8.3 检查 10/11/12/13 的判据与两树标定

阈值全部用**改前（`review/02-r1` 冻结快照）与改后（`hardware/`）两棵树差分**标定：

| 检查 | 抓什么 | 判据 | 改前树命中 | 改后树 |
|---|---|---|---|---|
| 10 | 标签/文字墨迹压器件本体 | 相交 `ox>0.15 且 oy>0.15` mm | C213 的 GND（重叠 2.97×0.44）、C221 的 GND（同值，逐字节相同） | 0（两处都已修） |
| 11 | 标签叠标签 | 横向重叠 ≥ 较窄者的 40% **且** 墨迹纵向间隙 < 1.0mm **且** 锚Δx ≥ 1.0mm | REG_C 对（间隙 +0.64、重叠 91%、Δx 6.35）、SRN_F 对（−0.63、48%、8.89）、SRN_F↔GND（+0.64、42%、8.89） | 0 |
| 12 | 字段离自己器件太远、离别人近 | `d_别人 < d_自己 − 0.5` 且 `d_自己 > 2.0`（2D 边到边） | C226 位号（自己 3.07 / C220 0.32）、C226 值（7.92 / 7.31）、**C219 值（3.07 / 0.41）** | 0（含 C219，见 §8.4） |
| 13 | 说明文字互压 | 锚Δx ≥ 2.0mm 且墨迹纵向间隙 < 0.5mm | 画图过程文字 ↔ §9 标题（−0.76） | 0 |

**为什么阈值要这么拧**（三个反直觉的标定结论）：

1. **11 项不能用「纵向间隙」单独判**：改前 REG_C 对的间隙是 **+0.64**（正的，没压上），
   而改后完全合法的 PACKP/PACKP 对（两根 100Ω 引到同一网，KiCad 要求两处都标）间隙也是 +0.64。
   真正分开两者的是**锚点横向错开量**：REG_C 对 Δx 6.35、墨迹横向重叠 91%（两段字几乎完全上下重合），
   PACKP 对 Δx 10.16、只重叠 26%（一眼能看出是两个名字）；同列上下紧排（Δx=0，如 VC0/VC1）也放行。
2. **11 项只比「标签 vs 标签」**：全局标签的文字画在图形框里，模型与渲染的**纵向**系统偏差
   0.2–1.2mm（实例：锚 (360.68,88.90) 的 GND 与 §6 说明首行，模型间隙 +0.24mm，PDF 实测 +0.86mm）。
   涉及说明文字的重叠交给 13 项（只比文字 vs 文字）。
3. **12 项要留 0.5mm 余量**：同排等距的器件（C203/C204/C205、R206/R207…）会出现 Δ=−0.00 的
   **完全平局**——那是排版对称，不是缺陷；不留余量会满屏假报。

## 8.4 负例验证（本轮新增检查）

```bash
AFE_HW=review/02-r1 python3 hardware/gen/check_02_layout.py     # 改前产物 = 负例
AFE_HW=hardware        python3 hardware/gen/check_02_layout.py  # 改后产物 = 正例
```

- 改前产物：**FAIL 10 条**，正好覆盖 b/c/d 四类 —— 8f 越框（comment 1 到 418.94）、
  10 项 2 条（C213/C221 的 GND）、11 项 3 条（REG_C、SRN_F×2）、12 项 3 条（C226 位号/值、C219 值）、
  13 项 1 条（过程文字压 §9 标题）；同一份脚本对改后产物 **PASS**（检查 1–9 + 10/11/12/13）。
  （负例快照里没有根图，故 9 项网表核对自动 SKIP —— 这是设计如此。）
- 本轮的负面结论也记一笔：**新检查在改后树上先报出的不是 0 条而是 2 条**——
  ① C221 的 GND 与 C213 那处几何**逐字节相同**（Δ 都是 0.97×0.44），复核只点了 C213，
  同病必须同修；② **C219 的值**「100nF 100V」右端离 C226 极板只剩 0.4mm（模型 3.07 vs 0.41），
  是 P1-3c 的同类毛病（复核没点到）。两处都是**版面**改动（C221 下端引线 2.54→3.81、
  C219 的值改到本体左侧右对齐 x=353.06），网表 0 差异。

## 8.5 验收实测（第 2 轮）

```
python3 hardware/gen/gen_02_afe.py          连跑两次 → md5 3ee64cc3…2604 稳定
python3 hardware/gen/check_02_layout.py
  图元解析：导线 157 段，junction 7 个，实例 53 个，引脚 164 个，文字 191 处，引脚名 164 个，图元盒 323 个
  渲染复核：PDF 文字串 494 段，字段认领 106/106 个，自由文字两两比对 541 段
  墨迹版面：标签/文字墨迹 191 处（说明文字 43 处）、字段 106 个，与 53 个本体盒比对；检查 10/11/12/13
  网表核对：逐脚核对 164 项（U1 48 脚 + 外围件 116 端子）；Footprint/LCSC 核对 53 件
  PASS：检查 1–9 及墨迹版面 10/11/12/13 全部通过
kicad-cli sch erc … hardware/mp2645a-bms.kicad_sch  →  6 violations，全部是跨页单脚
  （DSG_G / CHG_G / SRP / SRN / FET_MID / PACK+，与第 1 轮完全相同，等 01 页画完自动消失）
python3 -m unittest discover -s tests        →  21/21 OK
make -C firmware test                        →  38/38 checks passed
PDF 目视：全页 100dpi + 600dpi 局部裁图逐块看过（§4–§10 各段、C213/C219/C220/C221/C226 一带、
  标题栏）。C226 的位号/DNP 现在清楚挂在 C226 轴线上；C219 的值在 C213 一侧；C221 的 GND 与本体脱开；
  §10 标题与正文、§6 说明与 GND 标签都不再顶字；标题栏 comment 收在框内。
```

## 8.6 如实说明两条局限（免得后人误以为自检能管住）

1. **P1-3b 的「§10 标题压说明」几何上不可判**：全页统一风格是「2.4 号标题 + 紧接 1.8 号正文」，
   模型墨迹重叠 0.89mm（§9）、0.93mm（§10 那处），渲染 span 重叠同为 0.93–0.95mm —— 两者同类。
   所以第 13 项**按设计豁免同 x 的上下两行**，§10 的修法是风格性的（标题上移 2.54mm），
   **不是**自检抓出来的。
2. **全局标签的墨迹盒是保守近似**（见 §8.2），第 10 项对全局标签宁可多报；第 11 项因此
   完全不比「标签 vs 说明文字」的纵向。

## 8.7 工作区状态

本轮改动**未提交**（`hardware/02_afe.kicad_sch`、`hardware/gen/gen_02_afe.py`、
`hardware/gen/check_02_layout.py` 三个文件），需要冻结快照 `review/02-r2` / 提交时再说一声。
