colemandlut/MP2645A-BMS/design/02_afe-review-opus.md

# 02_afe 独立复核报告（复核方：Claude Opus；画图方：DeepSeek）

> 时间：2026-09-27 17:40 JST
> 输入：`review/02-r1/`（`02_afe.kicad_sch`、`erc.json`、`netlist.xml`、`sch.pdf` 第 3 页）、`design/02_afe-spec.md`、`docs/02-BOM.csv`、`hardware/mp2645a-bms.kicad_pro`（网络类）、`hardware/lib/jlc/`（符号与封装）。
> 手册：**MP** = `datasheets/C18198873_MPS_MP2797DFP-0000-T.pdf`，页码是 PDF 页号；**TK** = `datasheets/C19626224_Tokmas_IPT012N08N5_TOKMAS.pdf`。
> 纪律：按任务书的要求，没有读画图方的报告和 `*-draw-*.out`。没有改任何工程文件，没有运行 git。ERC 和网表是我自己在 `/tmp/r02/` 下重新跑的。
> 判定：**P0 = 0，P1 = 3，P2 = 11。** 本页电路的连接可以定稿，但 P1 的 3 条（值字段写错、网络类误匹配、版面）要先改掉，再进入 PCB。

---

## 0. 独立复跑结果（判据）

| 项 | 结果 |
|---|---|
| `kicad-cli sch erc --severity-all`（根图） | 共 6 条，全部是 `isolated_pin_label`：`DSG_G CHG_G SRP SRN FET_MID PACK+`，都属于 01 页还没画的网络，与预期相符。0 error |
| 重新导出的网表与快照 `netlist.xml` 比较 | 去掉日期和 tstamp 后 **diff 为空**，快照就是现行图纸。另外 `cmp` 确认 `hardware/02_afe.kicad_sch` 与快照逐字节一致 |
| 本页器件数 | 53（U1、J5、Q201、D201、R201–R223、C201–C226） |
| ⚠ ERC 的局限 | jlc 符号的 48 个脚全部是 `passive` 类型，所以 ERC 的「输出对输出」「电源脚无驱动」这类检查在本页不起作用。下面的逐脚核对是人工做的 |

---

## P0（不能投板）

无。

---

## P1（必须改）

### P1-1　C209 / C210 / C211：Value 字段写成「100nF 50V」，实际料号 C1525 是 16V
- **现状**：三只电容的 Value 字段是 `100nF 50V`，LCSC 字段是 `C1525`，库符号是 `CL05B104KO5NNNC`。按 Samsung 的命名，KO5 表示 **16V**。
- **与其他文件不一致**：BOM 第 26、27 行写的是「100nF 16V X7R」，规格书 §2.2 也是 16V。
- **后果**：从原理图导出的 BOM 和图面都会写成 50V。以后如果有人「按值换料」，或者复核时按 Value 判断耐压，就会被误导。
- **电气上没问题**：SRP/SRN 的绝对最大值是 6V（MP p.7），16V 足够。
- **修法**：Value 改成 `100nF 16V`，只改字段，不换符号。

### P1-2　网络类误匹配：`*/VC?` 把 VCP 也匹配进了 CELL_SENSE
- **证据**：网表第 39 号网络是 `/MP2797 采集与保护/VCP`，它的 `class="CELL_SENSE,HV_SIG"`。
- **原因**：通配符 `?` 匹配单个字符，`VCP` 被 X-7 新加的 `*/VC?` 命中了。
- **后果**：KiCad 按网络类的列表顺序合成有效网络类，CELL_SENSE 排在 HV_SIG 前面，所以间距会取 CELL_SENSE 的 0.3mm。这就抵消了 HV_SIG 的 0.6mm 间距。
  - VCP 对地的电压 = VMID + 14.7V（MP p.15）≈ 44V，TVS 钳位瞬态时约 68V。
  - 按 IPC-2221 B2（外层、无涂覆），31–100V 需要 0.6mm，0.3mm 不够。
- **修法**：把 `*/VC?` 换成 9 条明确的模式 `*/VC0` … `*/VC8`（或者等效的精确写法）。改完重新导网表，确认 VCP 只属于 HV_SIG，VC0–VC8 只属于 CELL_SENSE。
- **说明**：这一条落在 `.kicad_pro`，不在本页 sch 里。但它是本页网络名触发的，而且必须在布局之前修好，所以列为 P1。

### P1-3　可读性（规则 00 ③，逐页目视 `sch.pdf` 第 3 页）
下面几项属于「重叠、越界、多余文字」，规则 00 ③ 要求一项都不能留：
1. **越界**：标题栏的 comment 1「8S LiFePO4 200A BMS · … 第 1 轮完成（分段 A+B+C）：U1 + §4 电芯 RC + §5 采样 + …」超出了图框右边线（图纸右下角）。
2. **过程性文字，应删除**：
   - 页首第 4 行「第 1 轮已画完（分段 A+B+C）… 全页 53 器件、164 个网表节点」；
   - 标题栏的同一段 comment。
   这些是画图过程的记录，不是设计说明。
3. **文字与文字重叠**：
   - 页首那一行「…164 个网表节点。」压在「§9 电源：BAT+ 供电（U-1）」标题上；
   - 「§10 J5 采样端子」标题与下面第一行说明重叠。
4. **§6 区，C219 / C226 / C220 三只电容挤在一起**：
   - C226 的位号和「100nF 100V DNP」值字段摆到了 C220 的本体和 GND 标签旁边。读图时很容易把 **C220（VMID 对地，必贴）** 看成 DNP；
   - C219 的值「100nF 100V」压到了 C226 的 DNP 红叉上。
5. **§9 区 C213**：GND 标签压在 C213 的 2 脚和本体上，值「1µF 100V」紧贴 GND 标签；同一段 REG_C 导线上还上下叠着两个 `REG_C` 标签。
6. **§5 区**：C209 右端的 `SRN_F` 标签与 C211 上端的 `SRN_F` 标签、C210 下面的 GND 标签挤成一团，互相压字。
7. **标题写错**：「§4 电芯采样 RC（9 串）」应为「8 串 / 9 路」。电池是 8S，写 9 串会误导。

以上都只是图面问题，网表不受影响。**修改前后各导出一次网表做 diff，必须为空。**

---

## P2（建议，交用户定夺）

| # | 位号 / 网络 | 问题与依据 | 建议 |
|---|---|---|---|
| P2-1 | CHG_G、DSG_G（GATE 类，间距 0.3mm） | 栅极网络最高约为 VCP ≈ BAT+ + 14.7V ≈ 44V（瞬态约 68V），比 VTOP（29V，已归入 HV_SIG 0.6mm）还高，却只有 0.3mm 间距。网络类的逻辑不一致（IPC-2221 B2：31–100V 需要 0.6mm） | GATE 类的间距改为 0.6mm。BAT+、PACK+、FET_MID（HV_POWER 0.5mm）按同一口径也改为 0.6mm |
| P2-2 | C212 470nF/100V 0805（CVTOP，Required 470nF，MP p.123） | 规格书只核了 C214 的直流偏压，没有核这一只。100V 0805 X7R 在 29V 偏压下，经验上约掉 20–35%，只剩约 300–380nF | 样板实测，或换 1206 规格。至少在规格书里补上这一项核算 |
| P2-3 | C213 1µF/100V 1206（CREG，Required 1µF，MP p.124） | 同上，29V 下约剩 0.7µF | 同上 |
| P2-4 | C221 10nF/100V X7R 0603（CPACK_FLT，「Do not use a capacitor larger or smaller」，MP p.123） | X7R 本身 ±10%，再加 29V 偏压（约 −10%）和温漂，实际可能只有 8–9nF | 如果要严格满足「不得增减」，可改用 C0G 10nF/100V（0805），它没有偏压和温漂。现用料也可接受，由用户定 |
| P2-5 | NTC_CELL1/2（U1.20/19 → J5.1/3，直接出板） | NTC 脚的绝对最大值只有 6V，HBM 只有 1.5kV（MP p.7）。线束侧的探头就贴在电芯上，绝缘一旦破损，最高 29V 可能直接加到 NTC 脚，引脚与 J5 之间没有任何限流或钳位 | 在 J5 与 U1 之间串约 1k（固定偏差可在固件里标定），并在脚侧加低容 ESD 钳位。或者保持现状，把「线束绝缘」列为系统要求 |
| P2-6 | BAT+ → R212/R213/F11（BAT+ 取电，U-1） | 反向工况：J5 已经插上而 BAT+ 主线没接（装配时，或主线脱落）。这时 C8 脚（29V）经 R209 和芯片内部结构，可能向 VTOP 和整条 BAT+（包括 04 页的 buck 输入）反灌。手册只写了「Random Cell Connection Tolerant」（p.1），没有给出这种工况的边界 | 在装配规程里规定「先接 BAT+/BAT−，后插 J5」，或者向 MPS FAE 确认 |
| P2-7 | VTOP 下限 | VTOP 的 UVLO 为 14.6–17V（MP p.8），推荐工作范围 ≥ 18V（MP p.7）。8S 在 2.125V/节时就可能进入 UVLO，这时 FET 全关。共漏接法下两只体二极管反向串联，**无法补电，整包变砖** | 固件的 UV 门限加上关断后的自耗电预算，要保证单节 ≥ 2.5V（整包 20V）。说明书里写明深放电恢复的方法 |
| P2-8 | 固件（X-6 补充） | CELL_S_CTRL 的 MTP 默认值是 0xF（16 节，MP p.42）。首次上电时 C9–C16 读数为 0V，如果 `CELL_DEAD_EN` 默认使能，就会置位**持久**的 `CELL_DEAD_LOG_STS`。这个标志在关断和重新开机之后仍然保留，并且阻止芯片进入 active mode（MP p.27、p.30） | X-6 增加一条：先写 CELL_S_CTRL = 0x7，再执行 `CELL_DEAD_DET_CLEAR` 和 `CELL_DEAD_FAULT_CLR`。或者在确认节数之前先关掉 CELL_DEAD_EN |
| P2-9 | C218 10nF ±10%（CNTCB 最大 10nF，MP p.124）；C217 1µF 0402（CVREF Required 1µF，3.3V 偏压下约 0.6µF） | 规格书里已知的余量问题，用户已定（U-9）照原值画 | 样板实测后再决定是否换 4.7nF 与 0603 1µF |
| P2-10 | Q201 MMBT5551 功耗上界 | P = (V_BAT − I·R213 − V_REGIN)·I。在 I = (V_BAT − V_REGIN)/(2·R213) = 23.6mA 时最大：29.2V 下为 **285mW**，已接近 300mW（25°C）额定。5mA 时只有 108mW，没问题 | 规格书 §9.2 的判据「实测 > 5mA 就换 BCX56」继续有效。建议把上面的上界写进规格书 |
| P2-11 | PACKP（绝对最小 −0.5V，MP p.7） | 除了 U-8 的反接充电器，PACK 短路关断时线缆电感会把 PACK+ 拉到 PACK− 以下，由 D1/D2 正向钳位，可能到 −1V 以下。PACKP 经 100Ω 灌出电流。手册拓扑本身也是这样 | 01 页的 TVS 选型核一下正向钳位电压，短路实测 PACKP 的负向尖峰 |

---

## 覆盖清单（已核对，列出结论）

### ⓪ 断线 / 死头 / 悬空；⓪b 同网多名
- ERC 复跑为 0 error。6 条 `isolated_pin_label` 与任务书预期的「01 页未画」一一对应。
- 网表中的 `unconnected-*` 只有 8 个，全部是 U1 的规定悬空脚：29、33、34、35、36、37、40、41。图上已放 NC 标志，没有两脚件悬空。
- 同网多名：网表里每个本页网络只有一个名字。`VC8` 上是 C8 与 C9–C16 共 9 个脚加 R209 和 C208，没有被别的名字吞掉。✅

### MP2797 48 脚逐脚核对（网表 pinfunction 对手册 p.6–7）
- 48 个脚的脚号与脚名全部与手册一致。封装 `LQFP-48 7×7 P0.50`：48 个焊盘，逆时针排序，没有镜像；1 脚在底边左端，即整体转了 90°，是嘉立创库的惯例。✅
- **电芯脚**：C0–C8 依次接 VC0–VC8。C9–C16（脚 5、4、3、2、1、48、47、46）直接并到 VC8，中间不串件，符合 Table 23 p.127「directly connect … to the practical maximum cell channel」。✅
- **未用脚**：
  - SDO、GPIO1–3、GPIOHV1、SBYDSG、N/C、WDT 悬空，与 Table 23 一致；
  - GPIO 要求配成 20k 上拉，规格书已写明默认值为 1。✅
- **WDT（29）**：悬空。p.24 写着「Can be pulled high externally to reset」，所以不能上拉，与规格书一致。✅
- **xALERT（28）**：R222 100k 下拉到 GND。`ALERT_POL` 的 OTP 默认值为 1，即高有效（p.48）。✅
- **NSHDN（30）**：R223 10k 上拉到全局 `+3V3`，不是 AFE_3V3。
  - 与内部 5MΩ 下拉分压后为 3.29V，高于上升门限 2.65V（p.14）；
  - 同时接到 U6.41 PB5。✅
- **I2C**：R220、R221 为 2.2k，上拉到 +3V3。VIH = 0.7 × 3V3（最大 2.43V），VIL = 0.25 × 3V3（p.16）。分别接 U6.42 PB6、U6.43 PB7，05 页没有重复的上拉。✅
- **AFE_3V3**：只接 U1.26 和 C215，没有碰全局 +3V3。✅
- **NTCB**：U1.21、C218、R216–R219 的上端。四路上拉都接 NTCB。✅
- **AGND（23）**：接 GND。按 p.6，它是本板唯一的地脚，TQFP 没有裸焊盘。✅

### ①a Figure 27 / Table 18 逐件点名（本页范围）
| 标识 | 本图 | 结论 |
|---|---|---|
| RVTOP 20Ω / CVTOP 470nF | R212（BAT+→VTOP）/ C212（VTOP→GND） | ✅（C212 的偏压见 P2-2） |
| RREG 500Ω / CREG 1µF / NPN_REGIN | R213 510Ω、C213、Q201：C=REG_C，B=REGCTRL，E=REGIN | ✅ |
| CREGIN 3.3µF | C214 10µF/10V 0603（5.1V 偏压下约 4.5µF） | ✅ |
| RCELL 20–100Ω ×9 / CCELL 100nF ×8 | R201–R209 33Ω / C201–C208 跨在相邻 VC 之间（阶梯，不接地） | ✅ 与 Fig 27 一致 |
| DAGND-C0 3.3V | D201：K（1 脚）接 VC0，A（2 脚）接 GND | ✅ |
| RSRP / RSRN 100Ω；CSRP_GND、CSRN_GND、CSRN_SRP 100nF | R210（SRP）、R211（SRN）；C210、C211 到 GND；C209 跨接 | ✅（Fig 27 中 RSRP 在 PGND-I，即电池侧） |
| RVMID 100Ω / CVMID 100nF | R214（FET_MID→VMID）/ C220（VMID→GND） | ✅ |
| CVCP ≥ ΣCiss（Table 22、p.126「按单组并联数 × Ciss」） | C219 100nF/100V 在 VCP↔VMID 之间，C226 DNP 预留。6 × 14.49nF（TK p.3，VDS = 50V）= 86.9nF → 取 100nF 一档 | ✅ |
| RPACK 100Ω / CPACK_FLT 10nF | R215（PACK+→PACKP）/ C221（PACKP→GND） | ✅（P2-4） |
| C3V3 / CVDD / CVREF / CNTCB | C215 / C216 / C217 / C218 | ✅（P2-9） |
| RNTC_PUP 10k ×4 | R216–R219 | ✅ |
| RCHG/RDSG_DRVER、RMG、R_PUP、DZ、MOSFET、CPACK_E | 在 01 页 | 本页不核（01 未画） |

### 电芯采样 RC 与均衡
- **均衡路径**（Fig 28 p.125）：内部均衡管跨在 Cn 与 Cn−1 两脚之间，所以均衡电流流过 R(n) 和 R(n−1) 两只串阻。
  - 最坏：3.65V ÷ (66 + 15Ω) = 45mA，每只 **67mW**。
  - 0805 在 85°C 降额后约 103mW（额定 125mW，70°C 起线性降到 155°C 为 0），余量 1.5 倍。✅
- **奇偶交替**（p.126）：奇数节和偶数节不同时均衡，所以不会有一只串阻同时流过两节的电流。✅
- **C20x 击穿短路**（0402 开裂）：一节电芯经两只 33Ω 短路，电流 55mA，每只电阻 100mW，0805 可以持续承受。✅
- **均衡时 C0 脚电压**：电芯 1 均衡时，VC0 被抬到约 +1.5V（45mA × 33Ω），超出 C0 的推荐范围 +0.3V，但远低于绝对最大值 5.7V，也低于 D201 的 3.3V。手册 Table 19 允许 RCELL 取到 100Ω，说明这是 MPS 已经考虑过的工况（测量与均衡分时隙进行）。可以接受。
- **CELL 与 BAL 分开**：网表中本页**没有任何 BAL\* 网络**。CELL0–8 只连 J5 和 R201–R209，不与 GND 相连。✅

### 高压耐压
| 器件 | 所在网络 | 最坏电压 | 额定 | 结论 |
|---|---|---|---|---|
| C212、C213 | VTOP、REG_C 对 GND | 29.2V（TVS 瞬态约 53V） | 100V | ✅ |
| C220、C221 | VMID、PACKP 对 GND | 同上 | 100V | ✅ |
| C219、C226 | VCP↔VMID | 14.7V（绝对最大 20V） | 100V | ✅（Table 18 要求 80V） |
| Q201 | VCE | ≤ 48V | VCEO 160V | ✅ |
| Q201 | VEB 反偏（BAT+ 突降时 C214 保持 5V） | 5V | 6V | ✅，余量小 |
| R212、R213（0603） | 稳态两端压差 | 很小 | — | ✅ |
| R214、R215（0402，额定 50V） | 两端瞬态压差 | ≤ 29V | 50V | ✅ |
| U1 | VTOP / PACKP / VMID | 53V | 绝对最大 86V（p.7） | ✅ |
| U1 | CHG / DSG / VCP | 约 68V | 绝对最大 100V（p.7） | ✅ |

- **HV_SIG 网络类**：VTOP、PACKP、VMID、REG_C 已正确归入 HV_SIG。VCP 被 CELL_SENSE 混入（P1-2）；GATE 类的口径偏低（P2-1）。

### 极性件
- **D201**：库符号 1 = C、2 = A。封装 SOD-123 的阴极色带丝印（x = −0.83 / −0.97）在 1 号焊盘一侧，1 号焊盘接 VC0。✅
- **Q201**：库符号 1 = B、2 = E、3 = C。与 SOT-23 上 MMBT5551 的标准脚位一致，网表连接正确。✅
- 本页没有电解电容或钽电容。

### J5
- **针脚定义**：1 = NTC_CELL1，2 = GND，3 = NTC_CELL2，4 = GND，5–13 = CELL0–CELL8，与网表逐针一致。✅
- **封装** `CONN-TH_13P-P2.50_XH-13A`：
  - 实测相邻中心距 12 × 2.50mm（x 从 −15.00 到 +15.00）；
  - 孔 ⌀1.0mm，1 号为方焊盘；
  - 丝印在 1 脚、13 脚两端有标记。
  - 属于板端件。✅

### 跨页接口
| 接口 | 现状 | 结论 |
|---|---|---|
| `BAT+` | 连到 R212、R213 以及 04 页的 F11.1 | 多脚，✅ |
| `AFE_ALERT` | 接 U6.40（PB4） | 多脚，✅ |
| `AFE_WAKE` | 接 U6.41（PB5） | 多脚，✅ |
| `I2C_SCL` / `I2C_SDA` | 接 U6.42 / U6.43 | 多脚，✅ |
| `+3V3`、`GND` | — | ✅ |
| `CHG_G`、`DSG_G`、`SRP`、`SRN`、`FET_MID`、`PACK+` | 单脚，是 01 页未画造成的 6 条告警 | 符合预期 |
| `NTC_FET`、`NTC_SHUNT` | 本页已有多个节点，所以 ERC **不会**因为 01 页漏画 RT3/RT4 而告警 | 01 页画完后要人工确认 RT3/RT4 已接上 |

### ① 电容完备性
- 逐电源脚都有对应电容，与 Table 18 一致：VTOP、REGIN、REG_C、3V3、VDD、VREF、NTCB、VCP↔VMID、VMID、PACKP。✅
- 容值余量的问题见 P2-2、P2-3、P2-4、P2-9。

### ② 封装下探
- R201–R209 用 0805：0603 在 85°C 只有 82mW，小于 67mW 的 1.5 倍余量要求，所以 0805 是必要的。
- R212、R213 用 0603：有脉冲和熔断考虑，可以接受。
- 100V 的 C212、C213、C219、C220、C221 已经是现有料的最小封装。
- 其余阻容全部是 0402。
- 没有发现可以继续下探的件。✅

### ③ 可读性
- 目视检查 PDF 第 3 页的发现，见 P1-3。

### LCSC 与 BOM
- 53 个位号的 LCSC 字段与 `docs/02-BOM.csv` AFE 段逐行一致。
- C222–C225、C226 都带 `dnp` 属性，图上也有红叉。
- 唯一的偏差是 C209–C211 的 Value 字段（P1-1）。✅

### 对规格书本身的质疑（已核）
- **§1.3 逐脚表、§3 点名表、§4 均衡推导、§6.3 CVCP、§8 通讯、§12.1b 用户决定**：已逐条对照手册，**成立**。
- **§0-2「WDT 不得上拉」**：p.24 原文支持。
- **§0-5 C_NTC 改 DNP**：Fig 26/27 的 NTC 脚上都没有电容，Table 18 也没有这一项，支持。
- **规格书的漏项**：
  - 只核了 C214 的直流偏压，没有核 C212、C213、C221（P2-2 至 P2-4）；
  - 网络类模式 `*/VC?` 会误匹配 VCP（P1-2）；
  - 没有考虑 CELL_DEAD 持久标志（P2-8），也没有考虑 BAT+ 缺失时的反灌（P2-6）。

### 未核
- 01 页的一切，包括拓扑 X-1、R_DRV、RMG、DZ、CPACK_E、RT3/RT4。
- PCB 布局。
- MMBT5551（C2145）的原厂手册：库里没有这份 PDF，脚位按 SOT-23 行业惯例和嘉立创库符号判定。
