colemandlut/MP2645A-BMS/design/02_afe-task-draw-r2.md

# 画图任务书：02_afe 第 2 轮（按 Opus 复核改，限时 30 分钟）

工作目录 `/home/user/MP2645A-BMS`。纪律同 `design/02_afe-task-draw-r1a.md`。依据：`design/02_afe-review-opus.md`（可读）。
**先跑 `hardware/gen/gen_02_afe.py` 确认幂等**（md5 `2edd200d19fc3adc0ca4ba8d5560984f`）再改。本轮**只改字段与版面，不改任何连接**：
改完导出网表，与改前比「位号.脚 → 网络」必须 0 差异（写进报告）。

## 要改
1. **P1-1**：C209、C210、C211 的 Value「100nF 50V」→「100nF 16V」（料号 C1525 本来就是 16V，与 BOM 一致）。
2. **P1-3 版面**：
   a. 标题栏 comment 超出图框 → 缩短或去掉；
   b. 删掉画图过程文字（「第 1 轮已画完…164 个网表节点」一类），它还压在 §9 标题上；§10 标题与下方说明重叠 → 挪开；
   c. C226 的位号与「DNP」字样挪到 C226 自己旁边，不能让人看成 C220 是 DNP；
   d. C213 的 GND 标签不能压在引脚上；两个叠放的 REG_C 标签只留一个或分开；SRN_F 标签与 GND 标签分开；
   e. 标题「§4（9 串）」改为「§4 电芯采样（8 串 9 路）」。
3. 自检补漏：让 `check_02_layout.py` 能抓到 b/c/d 这几类（标签压引脚、标签叠标签、字段离自己器件太远而靠近别的器件、文字越出图框含标题栏），并用本轮改前的产物做负例验证。

## 验收
9 项自检全过（加上新增项）；ERC 只剩 01 页那 6 条跨页单脚；网表 0 差异；幂等；PDF 目视。报告加「第 2 轮变更」。最后一行回复 `DONE`。
