colemandlut/MP2645A-BMS/design/02_afe-spec.md

# 02_afe（MP2797 AFE）设计规格书 · 供画图方照画

> 时间戳：2026-09-27 16:22–16:30 JST　编写：parts / 设计核算角色（Claude Opus）
> 纪律：本文件是本轮唯一的写入。原理图、BOM、库、docs 都没有改，也没有运行 `fetch_jlc_parts.py`、`gen_kicad_skeleton.py` 或 git。
> 库存、价格、基础库/扩展库都来自 `python3 tools/jlc_api.py`（嘉立创 SMT 接口，**嘉立创库存**，美元阶梯价），查询时间就是本文时间戳。
> 符号是否存在：逐个到 `hardware/lib/jlc/jlc.kicad_sym` 里按 `LCSC Part` 字段查（117 个符号）。
> **页码一律是 PDF 页号**（MP2797 手册的印刷页码与 PDF 页号相同）。
>
> 手册：**MP** = `datasheets/C18198873_MPS_MP2797DFP-0000-T.pdf`（Rev1.0，2023-06-28，130 页）。
> 引脚图 p.5；引脚功能 p.6–7；绝对最大值与推荐工作条件 p.7；电气特性 p.8–16；典型应用 Figure 26 p.121；外围件详图 Figure 27 p.122；Table 18 p.123–124；均衡 Figure 28 与 Table 19–21 p.125–126；Table 22、Table 23 p.127；PCB 布局 Figure 23–25 p.120。
> 其他手册：`datasheets/C19626224_Tokmas_IPT012N08N5_TOKMAS.pdf`（Ciss）。
>
> 接口契约（全局标签，以 `tools/gen_kicad_skeleton.py` 的 SHEETS 为准）：
> `CELL0..CELL8 SRP SRN CHG_G DSG_G FET_MID PACK+ NTC_CELL1 NTC_CELL2 NTC_FET NTC_SHUNT I2C_SCL I2C_SDA AFE_ALERT AFE_WAKE +3V3 GND`
> 其中 `GND = BAT-`，单点在分流器电池侧。**本文建议新增 `BAT+`**（给 VTOP 和 REGIN 供电，见 §9.1 与 U-1）。

---

## 0. 结论速览（画图方先看这一节）

1. **U1 逐脚分配见 §1.3**。符号 `jlc:MP2797DFP-0000-T` 的 48 个脚名、脚号已逐条与手册 p.6–7 对过，一致。
   - 8S 接法：C0–C8 接电芯。**C9–C16（脚 5、4、3、2、1、48、47、46）在芯片脚侧直接并到 C8（脚 6）**，依据 Table 23（p.127）原文「directly connect all unused cell channels to the practical maximum cell channel」。
   - 悬空并放 NC 标志的脚：SDO(33)、GPIO3/nCS(34)、GPIO2(35)、GPIO1(36)、GPIOHV1(37)、N/C(40)、SBYDSG(41)、**WDT(29)**，依据 Table 23。
2. **WDT 绝对不能上拉**（订正 docs/03 §3.1「xALERT / WDT 开漏上拉 10kΩ」）。
   - 手册 p.24 原文：WDT「Can be pulled high externally to reset the device」。
   - p.48 的 `WDT_RST_EN` OTP 默认值为 1。
   - 所以一上拉，AFE 会被持续复位回出厂设置。**悬空**（Table 23）。
3. **被动均衡电流要流过 VC 串阻，属于 docs/03 §3.2 的情况 B**（Figure 28 p.125：内部均衡管跨在 Cn 与 Cn−1 两脚之间，位于 RCELL_FILTER 之后）。
   - R_CELL 取 33Ω 0805：最坏每只 67mW，0805 在 85°C 时的余量是 1.5 倍（§4.3）。
   - **docs/03 §3.2 的前提写错了**：「58mA」是手册在 4V 锂电、20Ω 条件下的数（p.125）。LFP 3.65V 配 33Ω 时，典型只有 **39mA**（32–45mA）。
4. **C_CELL 是 8 只，不是 9 只**（BOM 写的是 C_CELL1–9）。按 Figure 27，电容跨接在相邻两个 Cn 滤波节点之间，8 节电芯就是 8 只。
   - C0 节点对地没有电容，只有 D_C0 稳压管。
   - 封装由 0603 下探到 **0402 50V C307331**（基础库，符号已在库里）。
5. **C_NTC1–4 由 100nF 改为 DNP**（或 1nF）。
   - 手册 Figure 26/27 的 NTC 脚上都没有电容。
   - `NTCB_DYNAMIC_ON` 的 OTP 默认值为 1（p.90），即 NTCB 只在转换期间通电。
   - 100nF 配 5–8.8kΩ 戴维南内阻，τ = 0.5–0.9ms，偏置接通后来不及稳定，温度读数会偏。见 §7.3 和 U-3。
6. **C_REGIN 由 4.7µF/16V 0603 改为 10µF/10V 0603（C19702，基础库，需取库）**。
   - 手册要求 3.3µF（Table 18 p.124，Required）。
   - 4.7µF 0603 X5R 在 5.1V 偏压下只剩约 2.6–2.8µF，不够。
7. **CVCP 建议改用 C28233（100nF/100V 0805，基础库，与 C_VMID 同料）**。
   - Table 22（p.127）规定 CVCP ≥ 总 Ciss = 6 × 14.49nF = 87nF。
   - 50V 0603 的 100nF 在约 15V 偏压下可能掉到 87nF 以下。
   - 100V 0805 同时满足 Table 18「额定 80V」的原文（不按 8/16 折算）。
8. **高边驱动拓扑（01 页的 P0，跨页事项 X-1）**：手册 Figure 26（p.121）和 Figure 27（p.122）都是**共漏**：
   - 电池 → **CHG 管（源极朝电池）** → VMID（两管漏极）→ **DSG 管（源极朝 PACK+）** → 负载。
   - RCHG_PUP / DCHG_VGS 跨在 CHG 栅极与**电池正**之间；RDSG_PUP / DDSG_VGS 跨在 DSG 栅极与 **PACK+** 之间。
   - docs/03 §2.1 是「DSG 在电池侧、**共源**、两组栅极都以 FET_MID 为参考」，与手册相反。docs/03 自己也写了「本拓扑不对就改成共漏」。
   - **02 页的接口与拓扑无关**：CHG→CHG_G、DSG→DSG_G、VMID→R_VMID→FET_MID、PACKP→R_PACK→PACK+。本页照本规格画即可，01 页按 X-1 改。
9. **SRP 接分流器电池侧（= GND 单点），SRN 接 PACK− 侧**（Figure 26 p.121；p.6 AGND「Connect AGND near the positive connection (SRP) of the low-side sense resistor」）。docs/03 §2.1 的 ASCII 图把 SRN 画在 BAT− 一侧，是反的（X-3）。
10. **AFE 自己的 3V3 输出（脚 26）是本页的局部网络 `AFE_3V3`，绝对不能接全局 `+3V3`**。
    - I2C 上拉 R_I2C1/2 和 R_WAK 接本板 `+3V3`（buck 输出）。
    - R_ALT 100k 下拉到 GND。
11. **J5 画在本页**，建议针脚定义为 1 NTC_CELL1 / 2 GND / 3 NTC_CELL2 / 4 GND / 5–13 CELL0–CELL8（§10，U-4）。
    - NTC 放在低压端，与 CELL8（29V）拉开，防止线束短路把 29V 灌进 NTC 脚（绝对最大 6V）。
    - **RT1/RT2 是 0603 贴片 NTC，装在板上测不到电芯温度**，要换成线束侧 NTC 探头（非嘉立创件，U-2）。
12. **需要取库**：只有 **C19702**（C_REGIN 新料）。本页其余用料的符号全部已在 `jlc.kicad_sym` 里。
13. **位号**：本页件数超过「2x」一段的容量（电阻 23 只、电容 25 只，R40–R42 与 R50–R60 已被 04/05 页占用），所以用**三位数 2xx 段**：R201–R223、C201–C225、D201、Q201。U1、J5 保持原号（U-6）。

---

## 1. U1 MP2797DFP-0000-T（C18198873，TQFP-48）逐脚分配

### 1.1 器件与库

| 项 | 值 | 依据 |
|---|---|---|
| 型号 | MP2797DFP-0000-T：**I2C、通讯 CRC 默认关**（固件可置 `USE_COMM_CRC`=1 打开，0xA3 bit2，p.111） | MP p.3 订购信息 |
| 嘉立创 | C18198873，扩展库，**库存 269**，$4.13（1+）/ $3.42（100+） | jlc_api |
| 符号 | `jlc:MP2797DFP-0000-T`，48 脚，脚名与脚号已逐条对过 p.6–7，一致 | 库 |
| 封装 | `jlc:LQFP-48_L7.0-W7.0-P0.50-LS9.0-BL_1`（48 焊盘，脚距 0.5mm；TQFP-48 7×7 无裸焊盘） | p.128 |
| I2C 地址 | 默认 **0x01**（7 位），`DEVICE_ADD`（0xA3 bits[14:8]，MTP） | p.42、p.111 |

**符号摆放**：库符号的电芯脚（C0–C16）、CHG、DSG、PACKP、xALERT、WDT、3V3 在**右侧**；通讯、NTC、VTOP、VCP、VMID、REGIN、SRP/SRN 在**左侧**。
本页信号流是「J5 与采样 RC 在左 → U1 → 驱动与通讯接口在右」，所以**建议把 U1 左右镜像**（KiCad 选中后按 Y）。镜像后：
- 电芯脚朝左，对着 J5；
- 通讯、NTC、电源脚朝右。

镜像只改图形，不改脚号，**不许替换符号**（规则 00 ⓪）。

### 1.2 电压域（决定哪些脚之间要拉开距离、哪些电容要 100V）

| 电压域 | 脚 | 最高电压（对 GND） |
|---|---|---|
| 电池高压 | VTOP(45)、C8(6) 及并到它的 C9–C16、VMID(43)、PACKP(38) | 29.2V 正常；TVS 钳位时约 53V（docs/03 §2.2） |
| 高压之上 | VCP(42)、CHG(44)、DSG(39) | VMID + 14.7V（p.15 VCP），约 44V，瞬态约 68V。绝对最大值 100V（p.7） |
| 电芯阶梯 | C1–C7 | n × 3.65V |
| 5V 域 | REGIN(25)、REGCTRL(24) | 5.1V（REGCTRL 5.6V） |
| 3.3V 域 | 3V3(26)、VREF(22)、NTCB(21)、NTC1–4、I2C、xALERT、WDT、GPIO | 3.3V；绝对最大值 6V（NSHDN 9V） |
| 1.8V | VDD(27) | 1.8V；绝对最大值 2V |
| 地附近 | C0(14)、SRP(15)、SRN(16)、AGND(23) | C0：−0.25~+0.3V（推荐）；SRP/SRN：±100mV（推荐） |

### 1.3 逐脚表（48 脚，画图方逐行照画）

「网络」列：带 `全局` 的是全局标签，其余是本页局部标签（全部用 `_` 分隔，不含 `/`，符合规则 00 ⓪c）。

| 脚 | 名称 | 类型 | 网络 | 外围件（新位号） | 依据 |
|---|---|---|---|---|---|
| 1 | C13 | I | `VC8` | 未用，并到 C8（6 脚） | Table 23 p.127 |
| 2 | C12 | I | `VC8` | 同上 | 同上 |
| 3 | C11 | I | `VC8` | 同上 | 同上 |
| 4 | C10 | I | `VC8` | 同上 | 同上 |
| 5 | C9 | I | `VC8` | 同上 | 同上 |
| 6 | C8 | I | `VC8` | R209 33Ω ← `CELL8`（全局）；C208 100nF 跨 VC8–VC7 | p.6；Fig 27；Table 18 |
| 7 | C7 | I | `VC7` | R208 ← `CELL7`；C207 跨 VC7–VC6 | 同上 |
| 8 | C6 | I | `VC6` | R207 ← `CELL6`；C206 跨 VC6–VC5 | 同上 |
| 9 | C5 | I | `VC5` | R206 ← `CELL5`；C205 跨 VC5–VC4 | 同上 |
| 10 | C4 | I | `VC4` | R205 ← `CELL4`；C204 跨 VC4–VC3 | 同上 |
| 11 | C3 | I | `VC3` | R204 ← `CELL3`；C203 跨 VC3–VC2 | 同上 |
| 12 | C2 | I | `VC2` | R203 ← `CELL2`；C202 跨 VC2–VC1 | 同上 |
| 13 | C1 | I | `VC1` | R202 ← `CELL1`；C201 跨 VC1–VC0 | 同上 |
| 14 | C0 | I | `VC0` | R201 ← `CELL0`；**D201 BZT52C3V3：K 接 VC0，A 接 GND** | p.6 C0「negative pin of cell 1」；Fig 26/27 DAGND-C0；Table 18 3.3V |
| 15 | SRP | I | `SRP_F` | R210 100Ω ← `SRP`（全局）；C210 100nF 到 GND；C209 100nF 跨 SRP_F–SRN_F | Fig 27；Table 18 |
| 16 | SRN | I | `SRN_F` | R211 100Ω ← `SRN`（全局）；C211 100nF 到 GND | 同上 |
| 17 | NTC4 | I | `NTC_SHUNT`（全局） | R219 10k 上拉到 NTCB；C225 DNP（U-3）。热敏电阻 RT4 在 01 页 | p.6；Fig 26；bms_config.h：NTC 通道 3 = 分流器 |
| 18 | NTC3 | I | `NTC_FET`（全局） | R218 10k 上拉到 NTCB；C224 DNP。RT3 在 01 页 | 同上：通道 2 = MOSFET |
| 19 | NTC2 | I | `NTC_CELL2`（全局） | R217 10k 上拉到 NTCB；C223 DNP；经 J5.3 到线束 NTC | 同上：通道 1 = 电芯 2 |
| 20 | NTC1 | I | `NTC_CELL1`（全局） | R216 10k 上拉到 NTCB；C222 DNP；经 J5.1 到线束 NTC | 同上：通道 0 = 电芯 1 |
| 21 | NTCB | O | `NTCB` | C218 10nF 到 GND（贴脚）；R216–R219 的上端 | p.6；Table 18（**最大 10nF**） |
| 22 | VREF | P | `AFE_VREF` | C217 1µF 到 GND（贴脚） | p.7；Table 18 |
| 23 | AGND | P | `GND`（全局） | 星形接地，见 §9.5 | p.6；Fig 23 p.120 |
| 24 | REGCTRL | P | `REGCTRL` | Q201 基极 | p.6；Fig 27 |
| 25 | REGIN | P | `REGIN` | Q201 发射极；C214 10µF 到 GND（贴脚） | p.6「external 3.3µF bypass」；Table 18 |
| 26 | 3V3 | P | `AFE_3V3`（**局部，不接 +3V3**） | C215 1µF 到 GND（贴脚） | p.6；Table 18 0.47–10µF |
| 27 | VDD | P | `AFE_VDD` | C216 1µF 到 GND（贴脚） | p.6；Table 18 |
| 28 | xALERT | O（推挽） | `AFE_ALERT`（全局） | **R222 100k 下拉到 GND** | p.24；p.48 ALERT_POL 默认 1（高有效）；用户已定 |
| 29 | WDT | I/O | — | **悬空，放 NC 标志**。严禁上拉 | Table 23；p.24；p.48 WDT_RST_EN=1 |
| 30 | NSHDN | I | `AFE_WAKE`（全局） | **R223 10k 上拉到 `+3V3`（全局，buck 轨）** | p.6；p.14；05 规格书 X-4；用户已定 |
| 31 | SCL/SCK | I | `I2C_SCL`（全局） | R220 2.2k 上拉到 `+3V3` | p.36「must be connected to … pull-up」 |
| 32 | SDA/SDI | I/O | `I2C_SDA`（全局） | R221 2.2k 上拉到 `+3V3` | 同上 |
| 33 | SDO | O | — | 悬空，NC | Table 23 |
| 34 | GPIO3/nCS | I/O | — | 悬空，NC。复位后默认已开 20k 上拉（GPIO3_PUP=1，p.48） | Table 23 |
| 35 | GPIO2 | I/O | — | 悬空，NC（GPIO2_PUP=1） | Table 23；FET_SRC 默认 0 = 寄存器控制（p.44），GPIO 不参与 FET 控制 |
| 36 | GPIO1 | I/O | — | 悬空，NC | 同上 |
| 37 | GPIOHV1 | I/O | — | 悬空，NC（不用待机 P-MOS 旁路） | Table 23 |
| 38 | PACKP | I/O | `PACKP` | R215 100Ω ← `PACK+`（全局）；C221 10nF/100V 到 GND（贴脚） | Fig 27；Table 18「不得增减」 |
| 39 | DSG | O | `DSG_G`（全局） | 本页不串件；R_DRV2、DZ、R_PUP、PNP 快关都在 01 页 | Fig 27；用户已定 |
| 40 | N/C | — | — | NC | p.6 |
| 41 | SBYDSG | O | — | 悬空，NC | Table 23 |
| 42 | VCP | P | `VCP` | C219 100nF 跨 VCP–VMID（贴脚） | p.6；Table 18；Table 22 |
| 43 | VMID | P | `VMID` | R214 100Ω ← `FET_MID`（全局）；C220 100nF/100V 到 GND（贴脚） | Fig 27；Table 18 |
| 44 | CHG | O | `CHG_G`（全局） | 本页不串件（R_DRV1 等在 01 页） | Fig 27 |
| 45 | VTOP | P | `VTOP` | R212 20Ω ← `BAT+`（**建议新增全局标签**，U-1）；C212 470nF/100V 到 GND（贴脚） | p.6；Fig 26/27；Table 18 Required |
| 46 | C16 | I | `VC8` | 未用，并到 C8 | Table 23 |
| 47 | C15 | I | `VC8` | 同上 | 同上 |
| 48 | C14 | I | `VC8` | 同上 | 同上 |

**统计**：
- 电芯脚 17 个：9 个接 CELL0–8，8 个并到 C8。
- 电源/参考/地 10 个：VTOP、REGCTRL、REGIN、3V3、VDD、VREF、NTCB、VCP、VMID、AGND。
- 电流采样 2 个；NTC 4 个；驱动与 PACKP 3 个（CHG、DSG、PACKP）；通讯/中断 4 个（SCL、SDA、xALERT、NSHDN）。
- **NC 8 个**：29、33、34、35、36、37、40、41。
- 核对：17 + 10 + 2 + 4 + 3 + 4 + 8 = 48 ✅

**C9–C16 并到 C8 的画法**：
- 在 U1 右侧（镜像后在左侧）用一条竖线把脚 5、4、3、2、1、48、47、46 连到脚 6 的网络，或者给每个脚挂一个局部标签 `VC8`。
- 这 8 个脚**不再串电阻、不加电容**：Table 23 的原文是「directly connect」。
- 固件必须把 `CELL_S_CTRL` 写成 **0x7**（8 节，p.42），把它锁进 MTP。它的 MTP 默认值是 0xF（16 节）；不改的话，C9–C16 两两之间的压差是 0V，会被判为 UV。见 X-6。

---

## 2. 完整器件表（02 页）

### 2.1 位号规则

- U1 保持不变，J5 保持不变（连接器全板统一编号）。
- 无源件与分立件用本页的**三位数 2xx 段**：R201–、C201–、D201、Q201。
- 为什么不用两位数的 2x 段：本页电阻 23 只、电容 25 只，R20–R29/C20–C29 只有 10 个号；往下借 3x 会与 03 页撞号，R40–R42 和 C40–C45 已被 04 页占用。
- 04、05 页是两位数（R40、C50…），这里改三位数，由用户确认（U-6）。

### 2.2 器件表

「库」列：基=基础库，扩=扩展库。「符号」列：✅ 表示 `hardware/lib/jlc/jlc.kicad_sym` 里有这个 LCSC 号的符号（冒号后是符号名）。库存为嘉立创库存，价格为 1+ 单价（美元）。

| 新位号 | BOM 旧位号 | 值 | LCSC | 库 | 库存 / 单价 | 符号（jlc:） | 封装（jlc:） | 状态 |
|---|---|---|---|---|---|---|---|---|
| U1 | U1 | MP2797DFP-0000-T | C18198873 | 扩 | 269 / $4.13 | ✅ `MP2797DFP-0000-T` | `LQFP-48_L7.0-W7.0-P0.50-LS9.0-BL_1` | 贴 |
| R201–R209 | R_CELL1–9 | 33Ω 1% 125mW 0805（R201=CELL0 … R209=CELL8） | C17634 | 基 | 164 万 / $0.0047 | ✅ `0805W8F330JT5E` | `R0805` | 贴 |
| C201–C208 | C_CELL1–9 | 100nF 50V X7R **0402**（C201 跨 VC1–VC0 … C208 跨 VC8–VC7） | **C307331**（原 C14663 0603） | 基 | 1423 万 / $0.0089 | ✅ `CL05B104KB54PNC` | `C0402` | 贴（**BOM 改：9→8 只，0603→0402**） |
| D201 | D_C0 | BZT52C3V3 3.3V 500mW SOD-123 | C353528 | 扩 | 64031 / $0.014 | ✅ `BZT52C3V3_C353528`（1=K，2=A） | `SOD-123_L2.8-W1.8-LS3.7-RD` | 贴 |
| R210, R211 | R_SNS1, R_SNS2 | 100Ω 1% 0402（R210→SRP，R211→SRN） | C25076 | 基 | 466 万 / $0.0012 | ✅ `0402WGF1000TCE` | `R0402` | 贴 |
| C209 | C_SNSD | 100nF 16V X7R 0402（SRP_F–SRN_F 差模） | **C1525**（原 C14663 0603） | 基 | 2466 万 / $0.0045 | ✅ `CL05B104KO5NNNC` | `C0402` | 贴（**BOM 改**） |
| C210, C211 | C_SNSC1, C_SNSC2 | 100nF 16V X7R 0402（SRP_F、SRN_F 各对地） | **C1525** | 基 | 同上 | ✅ | `C0402` | 贴（**BOM 改**） |
| R212 | R_VTOP | 20Ω 1% 0603 | C22950 | 基 | 185 万 / $0.0025 | ✅ `0603WAF200JT5E` | `R0603` | 贴 |
| C212 | C_VTOP | 470nF 100V X7R 0805 | C5375914 | 扩 | 84771 / $0.0247 | ✅ `TCC0805X7R474K101FT` | `C0805` | 贴 |
| R213 | R_REG | 510Ω 1% 0603 | C23193 | 基 | 437 万 / $0.0024 | ✅ `0603WAF5100T5E` | `R0603` | 贴 |
| C213 | C_REG | 1µF 100V X7R 1206 | C282823 | 扩 | 228130 / $0.0488 | ✅ `TCC1206X7R105K101HT` | `C1206` | 贴 |
| Q201 | Q_REG | MMBT5551 NPN 160V 600mA 300mW SOT-23 | C2145 | 基 | 190 万 / $0.0152 | ✅ `MMBT5551_C2145`（1=B，2=E，3=C） | `SOT-23-3_L2.9-W1.3-P1.90-LS2.4-BR` | 贴 |
| C214 | C_REGIN | **10µF 10V X5R 0603**（原 4.7µF/16V C19666） | **C19702** | 基 | 1126 万 / $0.0319 | ❌ **需取库**（CL10A106KP8NNNC） | 取回的 C0603 | 贴（**BOM 改**） |
| C215 | C_LDO1 | 1µF 25V X5R 0402（3V3 脚） | C52923 | 基 | 648 万 / $0.0099 | ✅ `CL05A105KA5NQNC` | `C0402` | 贴 |
| C216 | C_LDO2 | 1µF 25V X5R 0402（VDD 脚） | C52923 | 基 | 同上 | ✅ | `C0402` | 贴 |
| C217 | C_VREF | 1µF 25V X5R 0402（VREF 脚） | C52923 | 基 | 同上 | ✅ | `C0402` | 贴 |
| C218 | C_NTCB | 10nF 50V X7R 0402 | C15195 | 基 | 444 万 / $0.005 | ✅ `CL05B103KB5NNNC` | `C0402` | 贴（见 §7.4 关于「最大 10nF」） |
| C219 | C_VCP | **100nF 100V X7R 0805**（原 50V 0603 C14663） | **C28233** | 基 | 174 万 / $0.0356 | ✅ `CL21B104KCFNNNE` | `C0805` | 贴（**BOM 改**，§6.3） |
| R214 | R_VMID | 100Ω 1% 0402 | C25076 | 基 | — | ✅ | `R0402` | 贴 |
| C220 | C_VMID | 100nF 100V X7R 0805 | C28233 | 基 | 174 万 / $0.0356 | ✅ `CL21B104KCFNNNE` | `C0805` | 贴 |
| R215 | R_PACK | 100Ω 1% 0402 | C25076 | 基 | — | ✅ | `R0402` | 贴 |
| C221 | C_PACK | 10nF 100V X7R 0603 | C282516 | 扩 | 440657 / $0.0054 | ✅ `TCC0603X7R103K101CT` | `C0603` | 贴 |
| R216–R219 | R_NTC1–4 | 10k 1% 0402（R216→NTC1 … R219→NTC4） | C25744 | 基 | 2362 万 / $0.0034 | ✅ `0402WGF1002TCE` | `R0402` | 贴 |
| C222–C225 | C_NTC1–4 | **DNP**（值标「1nF DNP」；原 100nF C14663） | C1523（1nF 50V 0402，调试时需要才贴） | 基 | 382 万 / $0.0042 | ✅ `0402B102K500NT` | `C0402` | **DNP**（U-3） |
| R220, R221 | R_I2C1, R_I2C2 | 2.2k 1% 0402（R220→SCL，R221→SDA） | C25879 | 基 | 248 万 / $0.0053 | ✅ `0402WGF2201TCE` | `R0402` | 贴 |
| R222 | R_ALT | 100k 1% 0402，xALERT 下拉 | C25741 | 基 | 977 万 / $0.0025 | ✅ `0402WGF1003TCE` | `R0402` | 贴 |
| R223 | R_WAK | 10k 1% 0402，NSHDN 上拉到 +3V3 | C25744 | 基 | — | ✅ | `R0402` | 贴 |
| J5 | J5 | XH 2.50mm 13P 立式板端座 | C40669 | 扩 | **244** / $0.0418 | ✅ `XH-13A`（1–13） | `CONN-TH_13P-P2.50_XH-13A`（实测 12 × 2.50mm，孔 1.0mm，1 脚方焊盘） | 贴 |
| （移出本页） | RT1, RT2 | 电芯 NTC 改为线束侧探头（非嘉立创件） | — | — | — | — | — | **U-2** |
| （移出本页） | RT3, RT4 | 画在 01 页：RT3 贴 MOSFET、RT4 贴分流器，另一端接 GND | C52155402 | 扩 | 136302 | ✅ `ANTC1608-103F3380FB` | `R0603` | 01 页 |

合计：本页 **1 + 23 R + 25 C（其中 4 只 DNP）+ 1 D + 1 Q + 1 J = 52 个位号**。

### 2.3 BOM 旧位号 → 新位号对照（供主代理改 `docs/02-BOM.csv`）

| 旧 | 新 | 变化 |
|---|---|---|
| R_CELL1–9 | R201–R209 | — |
| C_CELL1–9 | C201–C208 | **9 → 8 只**；C14663 0603 → **C307331 0402** |
| D_C0 | D201 | — |
| R_SNS1 / R_SNS2 | R210 / R211 | — |
| C_SNSD | C209 | C14663 0603 → **C1525 0402** |
| C_SNSC1 / C_SNSC2 | C210 / C211 | C14663 0603 → **C1525 0402** |
| R_VTOP / C_VTOP | R212 / C212 | — |
| R_REG / C_REG | R213 / C213 | — |
| Q_REG | Q201 | — |
| C_REGIN | C214 | C19666 4.7µF → **C19702 10µF**（需取库） |
| C_LDO1 / C_LDO2 | C215（3V3）/ C216（VDD） | — |
| C_VREF | C217 | — |
| C_NTCB | C218 | — |
| C_VCP | C219 | C14663 → **C28233**（100V 0805） |
| R_VMID / C_VMID | R214 / C220 | — |
| R_PACK / C_PACK | R215 / C221 | — |
| R_NTC1–4 | R216–R219 | — |
| C_NTC1–4 | C222–C225 | 100nF C14663 → **DNP**（1nF C1523 备用） |
| R_I2C1 / R_I2C2 | R220 / R221 | — |
| R_ALT / R_WAK | R222 / R223 | — |
| RT1–RT4 | RT3/RT4 → 01 页；RT1/RT2 → 线束探头 | U-2 |

**成本与上料费的变化**：
- 扩展库种数不变，仍是 6 种：C18198873、C5375914、C282823、C353528、C282516、C40669。
- 基础库方面：C14663 从本页消失；新增 C307331、C19702。基础库没有上料费。
- 单板增量：
  - C_CELL：9 × $0.0122 → 8 × $0.0089，−$0.039。
  - C_SNS：3 × ($0.0122 → $0.0045)，−$0.023。
  - C_REGIN：+$0.0025。
  - C_VCP：+$0.023。
  - C_NTC：4 只 DNP，−$0.049。
  - 合计约 **−$0.09/块**（约 −¥0.6）。**上料费增量 ¥0**。

---

## 3. Figure 27 / Table 18 外围件逐件点名清单（画图方与复核方都按这张核）

依据：Figure 27（p.122）上的每一个标注，Table 18（p.123–124），Table 22（p.127）。「页」列写该件所在的原理图页。

| # | 手册标识 | 手册值 / 要求 | 手册连接 | 本设计 | 页 | 状态 |
|---|---|---|---|---|---|---|
| 1 | RVTOP_FLT | 20Ω（Required） | 电池正 → VTOP | R212 20Ω 0603：BAT+ → VTOP | 02 | ✅（BAT+ 待 U-1） |
| 2 | CVTOP_FLT | 470nF（Required） | VTOP → 地 | C212 470nF/100V 0805 | 02 | ✅ |
| 3 | DBATT | TVS | 电池正 → PGND-I | D3 SMDJ33A | 01 | ✅ |
| 4 | RREG | 500Ω | 电池正 → NPN 集电极 | R213 510Ω 0603 | 02 | ✅ |
| 5 | CREG | 1µF | NPN 集电极 → 地 | C213 1µF/100V 1206 | 02 | ✅ |
| 6 | NPN_REGIN | 外置 BJT（EC 表 p.13 用 FZT853TA 测试） | C = RREG 下端，B = REGCTRL，E = REGIN | Q201 MMBT5551 | 02 | ✅（功耗见 §9.2） |
| 7 | CREGIN | 3.3µF（Required） | REGIN → AGND | C214 10µF/10V 0603（5V 偏压下约 4.5µF） | 02 | ✅（**改料**） |
| 8 | RCELL_FLT ×（N+1） | 20–100Ω（Required） | 电芯抽头 → Cn | R201–R209 33Ω 0805 | 02 | ✅ |
| 9 | CCELL_FLT × N | 100nF（Required） | 相邻 Cn 与 Cn−1 滤波节点之间 | C201–C208 100nF 0402 50V | 02 | ✅（**8 只**） |
| 10 | DAGND-C0 | 3.3V 稳压管 | C0 滤波节点（K）→ AGND（A） | D201 BZT52C3V3 | 02 | ✅ |
| 11 | CSRP_GND | 100nF | SRP 滤波节点 → 地 | C210 | 02 | ✅ |
| 12 | CSRN_GND | 100nF | SRN 滤波节点 → 地 | C211 | 02 | ✅ |
| 13 | CSRN_SRP | 100nF | SRP、SRN 滤波节点之间 | C209 | 02 | ✅ |
| 14 | RSRP_FLT | 100Ω | 分流器**电池侧** → SRP | R210 | 02 | ✅ |
| 15 | RSRN_FLT | 100Ω | 分流器**负载侧** → SRN | R211 | 02 | ✅ |
| 16 | RSENSE | 0.2 / 2 / 5mΩ（最小 / 典型 / 最大） | PGND-I 与 PGND-E 之间 | RS1 0.1mΩ（用户定，低于下限） | 01 | ⚠ 已知偏离 |
| 17 | CVMID | 100nF（Required） | VMID 脚 → 地 | C220 100nF/100V 0805 | 02 | ✅ |
| 18 | RVMID | 100Ω（Required） | 两管中点 → VMID 脚 | R214：FET_MID → VMID | 02 | ✅ |
| 19 | CVCP | 47nF 起，按 Table 22 取 ≥ ΣCiss；额定 80V（16 节），可按节数折算 | VCP ↔ VMID 脚 | C219 100nF/100V 0805 | 02 | ✅（**改料**） |
| 20 | MCHG | N-MOS | **源极朝电池**，漏极朝 VMID | Q7–Q12（docs/03 现为 DSG 在电池侧，**反了**） | 01 | ❌ **X-1** |
| 21 | MDSG | N-MOS | 漏极朝 VMID，**源极朝 PACK+** | Q1–Q6 | 01 | ❌ **X-1** |
| 22 | RMG × 2（每管） | 100Ω（Required） | 各管栅极串联 | RG1–RG12 | 01 | ✅ |
| 23 | RCHG_DRVER | 100Ω（Required） | CHG 脚 → CHG 栅极母线 | R_DRV1（01 页；布局时靠近 U1 的 44 脚） | 01 | ✅ |
| 24 | RDSG_DRVER | 100Ω（Required） | DSG 脚 → DSG 栅极母线 | R_DRV2（同上，靠近 39 脚） | 01 | ✅ |
| 25 | RCHG_PUP | 10MΩ | CHG 栅极母线 ↔ **CHG 源极（电池正）** | R_PUP1（docs/03 现接 FET_MID） | 01 | ⚠ X-1 |
| 26 | RDSG_PUP | 10MΩ | DSG 栅极母线 ↔ **DSG 源极（PACK+）** | R_PUP2（同上） | 01 | ⚠ X-1 |
| 27 | DCHG_VGS | 16V 稳压管（阴极接栅极） | CHG 栅极 ↔ CHG 源极 | DZ1 MM3Z15 | 01 | ⚠ X-1 |
| 28 | DDSG_VGS | 16V 稳压管 | DSG 栅极 ↔ DSG 源极 | DZ2 MM3Z15 | 01 | ⚠ X-1 |
| 29 | RPACK_FLT | 100Ω（Required） | PACK+ → PACKP | R215 | 02 | ✅ |
| 30 | CPACK_FLT | 10nF（Required，「不得增减」） | PACKP → 地 | C221 10nF/100V | 02 | ✅ |
| 31 | DPACK_E | TVS | PACK+ → PGND-E | D1、D2 | 01 | ✅ |
| 32 | CPACK_E | **47µF 典型 / 200µF 最大** | PACK+ → PGND-E | 现为 C1–C4 共 4µF（100V 1206） | 01 | ⚠ **X-4** |
| 33 | C3V3 | 1µF（0.47–10µF，Required） | 3V3 → 地 | C215 | 02 | ✅ |
| 34 | CNTCB | ≤10nF | NTCB → 地 | C218 10nF | 02 | ✅ |
| 35 | RNTC_PUP × 4 | 10k（宜等于 NTC 的 R25） | NTCB → NTCx | R216–R219 | 02 | ✅ |
| 36 | RNTC × 4 | 10k NTC | NTCx → AGND（星形） | 线束探头 ×2（U-2）+ RT3/RT4（01 页） | 02/01/线束 | ⚠ U-2 |
| 37 | CVDD | 1µF（Required） | VDD → 地 | C216 | 02 | ✅ |
| 38 | CVREF | 1µF（Required） | VREF → 地 | C217 | 02 | ✅ |
| — | CLOAD | 系统负载电容 | — | 板外 | — | — |
| — | PGND-I / PGND-E | 电池侧 / 负载侧功率地 | — | BAT− / PACK−（01 页） | 01 | ✅ |

Figure 26（p.121）比 Figure 27 多出来的元素：
- MCU 与 WDT、GPIO1–3 的连线：本设计不接，全部悬空（§8）。
- SBYDSG 待机 P-MOS 与它的电阻、稳压管：本设计不用，SBYDSG、GPIOHV1 悬空。
- NTC 回线星形接到 AGND：见 §7、§9.5。
- REGIN NPN 集电极串联的元件：Figure 26 在集电极上画的是电阻 + 一个带箭头的元件（像 PTC）。Figure 27 与 Table 18 只要求 RREG 500Ω，本设计按 Table 18 取值。

---

## 4. 电芯采样 RC（CELL0..8 → VC0..VC8）

### 4.1 被动均衡电流走不走 VC 串阻：走（情况 B）

- Figure 28（p.125）的「Internal Balancing」子图：集成均衡 MOSFET 接在芯片的 Cn 与 Cn−1 两脚之间，也就是 RCELL_FILTER[n] 与 RCELL_FILTER[n−1] **之后**。
- p.125 原文：「The amount of current … is easily derived by following the RCELL_FILTER resistor value and considering the integrated MOSFET balancing resistance」，并给出算例：4V 电芯、RCELL = 20Ω 时为 58mA。
- 反算：4V / (2 × 20 + 28) = 58.8mA ✅（RDS(ON)_BAL_FET 典型 28Ω，p.13）。
- **结论：均衡电流 = V_cell / (2·R_CELL + R_on)，两只串阻各流过全部电流，属于 docs/03 §3.2 的情况 B。**

### 4.2 取值：R = 33Ω，C = 100nF

- Table 18 与 Table 19（p.123、p.125）：RCELL 20–100Ω（Required），CCELL 100nF（Required）。并注明「If RCELL_FILTER increases, CCELL_FILTER should be proportionally decreased」。33Ω 在范围内，所以 C 保持 100nF。
- 差模转折频率 = 1 / (2π · 2R · C) = 1 / (2π × 66Ω × 100nF) = **24kHz**。
- 33Ω 远小于 1kΩ，所以固件的 `CELL_1K_COMP` 保持关闭（p.126：1kΩ 级才需要打开）。
- 均衡电流（RDS(ON)_BAL_FET 取 15 / 28 / 50Ω，即 p.13 的最小 / 典型 / 最大值）：

| V_cell | Ron 15Ω（最坏发热） | Ron 28Ω（典型） | Ron 50Ω |
|---|---|---|---|
| 2.5V | 30.9mA | 26.6mA | 21.6mA |
| 3.3V | 40.7mA | 35.1mA | 28.4mA |
| 3.65V（OV 门限） | **45.1mA** | **38.8mA** | 31.5mA |

**订正 docs/03 §3.2 与 §4.4**：
- docs/03 用「3.65V ÷ (2R + Ron) ≈ 58mA」反推出 R ≈ 30Ω。但 58mA 是 4V 电芯、20Ω 的数，**LFP 上达不到**。
- 33Ω 时典型 39mA，最大 45mA。「MP2797 内部 58mA 被动均衡」应改为「约 39mA（32–45mA）」。
- 若想要更大的被动电流，可以取 20Ω：最坏 66mA，每只 88mW。但 0805 在 85°C 时的余量只剩 1.17 倍，**不推荐**。

### 4.3 每路功耗与封装（规则 00 ②逐档下探）

每只 R_CELL 的最坏功耗：P = I² · R = 45.1mA² × 33Ω = **67mW**（Ron 最小、电芯在 OV 门限）。
- 手册 p.126：同一时刻只均衡奇数节或偶数节。所以一只 R_CELL(n)（被第 n 节和第 n+1 节共用）不会同时流过两节的电流。
- 均衡按 30ms 时隙交替进行（Figure 13 p.34）。
  - 单节连续均衡时占空比约 50%，平均功耗约 34mW。
  - 按连续 67mW 核算，留出余量。

| 封装 | 额定（70°C） | 85°C 降额后（线性降到 155°C 为 0） | 余量 | 结论 |
|---|---|---|---|---|
| 0402 | 62.5mW | 51mW | 0.77 | ✗ |
| 0603 | 100mW | 82mW | 1.22 | ✗ 余量不够：板温可达 70–85°C，因为 MOSFET 的 Tj 约 105°C（docs/03 §2.2） |
| **0805** | 125mW | 103mW | **1.53** | ✅ **采用 C17634**（基础库） |

- AFE 自身的发热：同时均衡 4 节 × 42mW（典型）= 0.17W。按 θJA 46.6°C/W（p.7）估，温升约 **8°C**。固件按 p.33 要求监视片温。
- C_CELL 的耐压：每只电容只承受一节电压（≤ 3.65V；Cx−Cx−1 绝对最大值 10V，p.7）。选 50V，是为了线束随机插接时电容串的瞬态分压（手册 p.1 写明「Random Cell Connection Tolerant」，但电容本身也要扛住）。
  - 0402 50V X7R（C307331，基础库）在 3.65V 下几乎不掉容。
  - 所以 **0603 → 0402**。

### 4.4 接法（画图方照画）

```
J5.5  CELL0 ─ R201 33Ω ─ VC0 ─ U1.14 (C0)       D201: K→VC0, A→GND
J5.6  CELL1 ─ R202 33Ω ─ VC1 ─ U1.13 (C1)       C201 100nF: VC1 ↔ VC0
J5.7  CELL2 ─ R203 33Ω ─ VC2 ─ U1.12 (C2)       C202: VC2 ↔ VC1
J5.8  CELL3 ─ R204 33Ω ─ VC3 ─ U1.11 (C3)       C203: VC3 ↔ VC2
J5.9  CELL4 ─ R205 33Ω ─ VC4 ─ U1.10 (C4)       C204: VC4 ↔ VC3
J5.10 CELL5 ─ R206 33Ω ─ VC5 ─ U1.9  (C5)       C205: VC5 ↔ VC4
J5.11 CELL6 ─ R207 33Ω ─ VC6 ─ U1.8  (C6)       C206: VC6 ↔ VC5
J5.12 CELL7 ─ R208 33Ω ─ VC7 ─ U1.7  (C7)       C207: VC7 ↔ VC6
J5.13 CELL8 ─ R209 33Ω ─ VC8 ─ U1.6  (C8)       C208: VC8 ↔ VC7
                          VC8 ─ U1.5,4,3,2,1,48,47,46 (C9–C16，直连，不加件)
```

- 电容做成「阶梯」：每只跨在相邻两个 VC 之间，**不接地**（Figure 26/27）。
- **CELLn 与 03 页的 BALn 在任何一页都不许相连**。采样线与均衡线只在电芯极柱上汇合（docs/03 §2.4）。否则安培级的开关电容均衡电流会在采样线上产生几十 mV 的误差。
  - 本页不出现任何 `BAL*` 标签。
  - 复核时在网表里确认 CELLn 与 BALn 是两个网络。
- `CELL0` 是电芯 1 负极的**采样线**，不是 GND。两者只在电芯极柱与分流器电池侧那一段铜排上等电位。
  - C0 对 AGND 的推荐范围是 −0.25 ~ +0.3V（p.7）。200A 时 BAT− 铜排压降约 16mV（docs/03 §2.4：150mm、80µΩ），在范围内。
  - C0 对 AGND 的误差项（p.9）要求 C0 − AGND ≥ −0.25V，才能保证电芯 1 的误差小于 15mV ✅。
- 开路检测：上拉/下拉电流各 100µA（p.32），在 33Ω 上只产生 3.3mV，不影响判定。

---

## 5. 电流采样 SRP / SRN

### 5.1 极性与开尔文接法

- **SRP = 分流器电池侧（BAT−，也是 GND 单点），SRN = 分流器 PACK− 侧**。依据：
  - Figure 26（p.121）：AGND 与 SRP 在电池负极一侧，SRN 在 Pack− 一侧；
  - p.6 AGND「Connect AGND near the positive connection (SRP) of the low-side sense resistor」。
- 由此得到的电流符号：
  - 放电时电流从 PACK− 经 RS1 流向 BAT−，V(SRN) > V(SRP)，读数为负；
  - 充电时读数为正。
  - 这与 `firmware/src/bms_config.h`「充电为正」一致 ✅。
- **docs/03 §2.1 的 ASCII 图把 `↑SRN` 画在 BAT− 旁、`↑SRP` 画在 PACK− 旁，是反的**。01 页必须按上面的定义引出（X-3）。
- 开尔文接法（p.120 第 6、7 条与 Figure 25）：
  - SRP、SRN 两根线从 RS1 两端焊盘的**内侧专用取样点**引出，不走功率铜。
  - 两线平行、紧耦合，一路走到 R210/R211。
  - 本页收到的 `SRP`/`SRN` 已经是 01 页引出的开尔文线。

### 5.2 滤波 RC（Figure 27 + Table 18 原值）

```
SRP (全局) ─ R210 100Ω ─ SRP_F ─ U1.15      C210 100nF: SRP_F → GND
SRN (全局) ─ R211 100Ω ─ SRN_F ─ U1.16      C211 100nF: SRN_F → GND
                                            C209 100nF: SRP_F ↔ SRN_F
```

| 量 | 算式 | 值 | 判据 |
|---|---|---|---|
| 差模转折 | 1 / (2π · 2R · (C_d + C_c/2)) | 1 / (2π × 200Ω × 150nF) = **5.3kHz** | IADC 每次转换 2ms（p.8），积分型，够用 |
| 差模 τ | 2R · (C_d + C_c/2) | **30µs** | SC 最快检测 120µs（p.11），去抖最小 100µs（p.69）。30µs 延迟可以接受 ✅ |
| 共模转折 | 1 / (2π · R · C_c) | 15.9kHz | — |
| 满量程 | 0.1mΩ × I | 200A = 20mV；SCP 800A = 80mV | IADC 范围 ±100mV（p.8）✅ |
| 差分输入电流误差 | 0.5µA × 200Ω | 0.1mV | 相对 20mV 为 0.5%，被标定吸收 |

**0.1mΩ 带来的硬件门限分辨率**（用户已定 0.1mΩ，这里只列后果，供固件与 01 页参考）：
- SC 放电：RNG0 的 LSB 是 5.5mV = 55A；800A = 80mV ≈ 14.5 LSB ✅（Table 8 p.25）。
- OC1/OC2 放电：LSB 2.5mV = 25A；400A = 40mV = 16 LSB ✅（Table 4）。
- **OC 充电**：LSB 1.6mV = 16A。132A 只能取 128A 或 144A。精度 ±15% ±1.5mV（p.12），合起来约 **±35A**。所以 OCC 132A 只能靠固件软件保护，硬件门限设宽（例如 160A）只作兜底（X-6）。
- **单管导通时**（只开 CHG 或只开 DSG，另一组靠体二极管导通）：OC 门限被强制压到 min(设定值, 17.5mV)，去抖压到 ≤16ms（p.24）。
  - 手册设这条是为了保护体二极管。但在 0.1mΩ 下，17.5mV 对应 **175A**。
  - 6 只体二极管流过 175A 时，按 VSD 约 0.9V 计约 **160W**，这条硬件兜底基本不起作用（0.2mΩ 时为 87.5A）。
  - 所以固件必须保证：单管状态下一旦检测到反向电流，就立即把另一组管也打开（常规做法），或者直接关断（X-6）。

### 5.3 与 01 页的接口

- 01 页只引出两根开尔文线 `SRP`、`SRN`，**不放任何滤波件**。滤波件（R210/R211/C209–C211）全部放在本页，布局时紧贴 U1 的 15/16 脚。
- SRP 与 GND 在 RS1 电池侧焊盘上是同一块铜，但在原理图上是两个网络。01 页需要用 **Net-Tie**（KiCad `NetTie_2`）把 `SRP` 与 `GND`/`BAT−` 在该焊盘处连起来，否则 ERC 会报同网多名，或者两者被合并（X-3）。
- 网络类：`KELVIN` 目前只匹配 `SRP`、`SRN`，建议把本页的 `SRP_F`、`SRN_F` 也加进去（X-7）。

---

## 6. 高边驱动（CHG / DSG / VCP / VMID / PACKP）

### 6.1 本页与 01 页的分界（哪些网络在哪页）

| 网络 | 本页 | 01 页 |
|---|---|---|
| `CHG_G`（全局） | U1.44 直连，不串件 | R_DRV1 100Ω → D4 → 栅极母线（RG1–6 → 各管栅极）；R_PUP1、DZ1、Q17 PNP 快关、RQB1 |
| `DSG_G`（全局） | U1.39 直连 | R_DRV2 → D5 → 栅极母线；R_PUP2、DZ2、Q18、RQB2 |
| `FET_MID`（全局） | R214 100Ω → `VMID`（U1.43）；C220 100nF VMID→GND；C219 100nF VCP↔VMID | 两组 MOSFET 的公共节点（按手册是**漏极**公共点，X-1） |
| `PACK+`（全局） | R215 100Ω → `PACKP`（U1.38）；C221 10nF PACKP→GND | PACK+ 端子、TVS D1/D2、C1–C4 |
| `BAT+`（全局，建议新增） | R212 → VTOP；R213 → Q201 集电极 | BAT+ 端子、F1、TVS D3、C5/C6 |

**「参考脚接 FET_MID」只对 VMID 成立**：
- MP2797 没有单独的「栅极参考脚」。VMID 是电荷泵的参考（VCP − VMID = 14.7V，p.15；绝对最大 20V，p.7），经 RVMID 接两管中点。
- **CHG、DSG 驱动的关断电平参考的是各自的源极**：
  - p.14–15 的测试条件：RCHG_ON/OFF 是「PACKP = VTOP」，RDSG_OFF 是「DSG = PACKP + 5V」，说明 DSG 驱动以 PACKP 为参考；
  - Figure 27 中，RCHG_PUP/DCHG_VGS 回到电池正，RDSG_PUP/DDSG_VGS 回到 PACK+。
  - 所以在手册的共漏拓扑里，**CHG 管源极 = 电池正（≈VTOP），DSG 管源极 = PACK+（= PACKP）**，驱动器正是按这两个节点关断栅极。

### 6.2 为什么 docs/03 的共源拓扑不行（X-1 的论证）

docs/03 §2.1 的接法是 BAT+ → DSG（D 接 BAT+，S 接 FET_MID）→ FET_MID ← S CHG D → PACK+，两组栅极的 R_PUP、DZ、PNP 集电极都回到 FET_MID。

| 工况 | 共源（docs/03）下会发生什么 | 依据 |
|---|---|---|
| 两管都关、PACK+ 被短路或拉低（SC 之后） | CHG 驱动器把 CHG 脚拉向 VTOP（≈26V）。经 R_DRV1 → D4 正偏 → CHG 栅极母线被抬到约 25.7V，而 FET_MID 被 CHG 管拉到 PACK+ ≈ 0V → **CHG 管被意外打开**，Vgs 由 DZ1 钳在 15V。DZ1 持续电流约 (26 − 15) / (840 + 100)Ω ≈ **12mA，功耗 0.18W**，接近 MM3Z15 的额定 200mW，而且只要 AFE 保持关断就一直持续 | RCHG_OFF 840Ω（p.15） |
| 两管都关、接上充电器（PACK+ = 30V > BAT+） | DSG 驱动器把 DSG 脚拉向 PACKP = 30V → D5 正偏 → DSG 栅极约 29.7V。FET_MID 被 DSG 体二极管钳在 ≤ BAT+ + 0.7V → **DSG 管 Vgs 为 3–15V，被意外打开** | RDSG_OFF 以 PACKP 为参考（p.15） |
| DSG 软启动（p.23） | 软启动控制的是 DSG 相对 PACKP 的斜率，要求 DSG 源极就是 PACK+。共源时 DSG 源极是 FET_MID，只有 CHG 已导通时才近似成立 | p.23 |
| 待机模式（p.22） | 手册原文：「conducts through the CHG N-channel MOSFET's body diode」，即 CHG 管在电池侧、体二极管顺放电方向。共源拓扑下 CHG 在 PACK 侧，体二极管方向相反 | p.22 |

- 这几种情况下保护方向碰巧没有失效：另一只管的体二极管仍然挡住了危险方向。但栅极处在手册以外的状态，DZ 长期过载。
- **判为 01 页 P0，按 docs/03 §2.1 自己写的「本拓扑不对就改成共漏」执行**，并报用户确认（X-1）。
- 共漏的改法（01 页）：
  - BAT+ → F1 → **CHG 管组（S 朝 BAT+，D 朝 FET_MID）** → FET_MID → **DSG 管组（D 朝 FET_MID，S 朝 PACK+）** → PACK+。
  - R_PUP1、DZ1、Q17 集电极回到 **BAT+ 侧的 CHG 源极母线**。
  - R_PUP2、DZ2、Q18 集电极回到 **PACK+**。
- **本页的接法在两种拓扑下完全相同**，不必等 01 页定案。

### 6.3 CVCP 与电荷泵

- Table 22（p.127）规定 CVCP ≥ 总 Ciss。一组 6 只 Tokmas IPT012N08N5，Ciss = 14.49nF（VDS = 50V，Tokmas 手册），合计 87nF。按 Table 22 取 **100nF**，也是表里的最大一档。
- 耐压：Table 18 要求 80V（16 节），「can be proportionally reduced」→ 8 节为 40V。
- 实际偏压：VCP − VMID ≈ 14.7V（p.15）。
- 取值比较：

| 方案 | 15V 偏压下的有效容量（经验值） | 结论 |
|---|---|---|
| C14663 100nF/50V X7R 0603（BOM 现值） | 约 −15 ~ −25%，即 75–85nF，**< 87nF** | ✗ 不满足 Table 22 |
| **C28233 100nF/100V X7R 0805**（基础库，C220 也用它） | 约 −5 ~ −10%，即 90–95nF | ✅ **采用**。同时满足 80V 原文，不增加料种 |

- **风险提示（P2）**：Table 22 按手册 Ciss 取值。Ciss 是 VDS = 50V 时测得的，导通瞬间 VDS → 0，Ciss 会变大。若按 Qg 等效：6 × 240nC / 10V = 144nF，已经超出 Table 22 的最大档。
  - 样板实测 CHG/DSG 开通时 VCP 的跌落，以及 `FET_TIMEOUT`（p.49）。
  - 若开通失败，在 C219 旁预留一个 0805 焊盘（C226，默认 DNP），并联到 200nF，再找 MPS FAE 确认。**本版建议预留焊盘**（U-7）。

### 6.4 VMID、PACKP 的 RC

- R214 100Ω（RVMID Required）+ C220 100nF（CVMID Required），τ = 10µs。C220 必须贴在 U1.43 旁边，接 GND。
- R215 100Ω（RPACK_FLT Required）+ C221 10nF（CPACK_FLT Required，「Do not use a capacitor larger or smaller than the recommended value」），τ = 1µs。
  - 这个 τ 影响 PACKP 比较器、短路恢复与负载检测的时序（p.15：PACKP 上拉/下拉 250µA）。**不许改值**。
- 电压：PACK+、FET_MID 最高约 53V（TVS 钳位），所以 C220、C221 用 100V。R214/R215 是 0402，额定 50V。
  - 稳态两端压差为 0。瞬态时电容电压跟不上，电阻两端的阶跃电压按最坏 53 − 29 = 24V 计，小于 50V ✅。
  - 能量：24²/100 × 1µs ≈ 6µJ，可以忽略。
- **反接风险（P2，报用户）**：PACKP 的绝对最小值是 −0.5V（p.7）。如果 PACK 端反接了充电器（PACK+ ≈ −30V），PACKP 经 100Ω 灌出 0.3A，芯片必坏。手册拓扑本身不防反接。要防的话需要系统级方案（例如 PACK 端反接检测，或串二极管，但会影响 PACKP 精度），本版不做（U-8）。

---

## 7. NTC ×4

### 7.1 通道分配（与固件一致）

| MP2797 脚 | 固件通道（bms_config.h） | 网络 | 热敏电阻位置 | 模式（NTCx_TYPE_SEL） |
|---|---|---|---|---|
| NTC1（20） | 0：电芯 1 | `NTC_CELL1` | **线束探头**，贴电芯表面（中间那一节），经 J5.1/J5.2 | Cell monitor |
| NTC2（19） | 1：电芯 2 | `NTC_CELL2` | **线束探头**，贴电芯表面（边缘那一节），经 J5.3/J5.4 | Cell monitor |
| NTC3（18） | 2：MOSFET | `NTC_FET` | 01 页 RT3（0603），贴 MOSFET 散热区 | PCB monitor |
| NTC4（17） | 3：分流器 | `NTC_SHUNT` | 01 页 RT4（0603），贴 RS1 | PCB monitor |

模式依据：p.26。电芯 NTC 有充电/放电各自的冷、热门限；PCB NTC 只有一个热门限。

### 7.2 接法（Figure 26 p.121、Figure 27 p.122）

```
NTCB (U1.21) ─┬─ C218 10nF → GND（贴脚）
              ├─ R216 10k ─ NTC_CELL1 ─ U1.20 ；C222 DNP → GND ；→ J5.1 → 探头 → J5.2 → GND
              ├─ R217 10k ─ NTC_CELL2 ─ U1.19 ；C223 DNP        ；→ J5.3 → 探头 → J5.4 → GND
              ├─ R218 10k ─ NTC_FET   ─ U1.18 ；C224 DNP        ；→ 01 页 RT3 → GND
              └─ R219 10k ─ NTC_SHUNT ─ U1.17 ；C225 DNP        ；→ 01 页 RT4 → GND
```

- **上拉接 NTCB，不接 3V3 或 +3V3**。NTC 读数与 NTCB 成比例（p.26 Figure 10），NTCB 的漂移会被消掉。
- NTC 回线在 AGND 处星形汇合（p.120 第 8 条）。J5.2/J5.4 的 GND 用独立走线回到 U1 的 AGND 附近，再进 GND 平面，不要就近打到功率地。
- 板外两路 NTC 用双绞线（p.120 第 9 条），对应 J5 相邻两针（1/2、3/4）。

### 7.3 为什么 C_NTC 由 100nF 改为 DNP

- 手册 Figure 26、27 的 NTC 脚上**都没有电容**，Table 18 里也没有 NTC 滤波电容这一项。
- `NTCB_DYNAMIC_ON`（0x47 bit10）的 OTP 默认值为 1（p.90）：「Enables dynamic bias on NTCB during ADC conversions」。也就是说，NTCB 只在转换时通电，平时关断；如果保持常开，4 路分压会长期消耗约 0.66–1.2mA，待机不可接受。
- 偏置接通后，NTC 节点按 τ = R_th · C 充电，R_th = 10k ∥ R_NTC：

| 温度 | R_NTC（B3380） | R_th | τ（100nF） | τ（1nF） |
|---|---|---|---|---|
| −20°C | 75.0k | 8.8k | **0.88ms** | 8.8µs |
| 25°C | 10.0k | 5.0k | 0.50ms | 5.0µs |
| 100°C | 1.02k | 0.93k | 0.09ms | 0.9µs |

- 要稳定到 11 位（0.05%）需要约 7.6τ。100nF 时是 **3.8–6.7ms**，比一次 ADC 转换（2ms，p.9）还长。NTCB 自身只允许 ≤10nF（Table 18），可见手册预期的建立时间是几十微秒量级。
- 所以 100nF 会让温度读数系统性偏向 NTCB 接通瞬间的电平。**低温时偏得最多，正好在 0°C 禁充门限附近**。
- 处理：
  - C222–C225 保留 0402 焊盘，**默认 DNP**。
  - 值栏写「1nF DNP」：EMC 调试时如果需要，贴 C1523 1nF（τ ≤ 8.8µs，7.6τ ≤ 67µs）。
  - 待用户定（U-3）。

### 7.4 其它核算

- **NTCB 负载**：最热时（100°C）每路 3.3V / (10k + 1.02k) = 0.30mA，4 路共 1.2mA。小于 INTCB_MAXLOAD 的最小值 3.2mA（p.13）✅。
- 单路 NTC 线束对地短路时，该路 0.33mA，其它路不受影响 ✅。
- **CNTCB 10nF 在「最大 10nF」边上**：Table 18 p.124 的 10nF 填在 Max 列。C15195 容差 ±10%，最坏 11nF。
  - 若要严格不超，改用 4.7nF（C1538，基础库，库里有 `0402B472K500NT` 符号）。
  - 这是用户按 Table 18 定过的值，列入 P2（U-9），**本版照 10nF 画**。
- **R_NTC 精度**：1% 上拉 + 1% NTC（C52155402），25°C 时误差约 ±0.5°C，满足保护需要。docs/03 §3.3 提过的 0.1% 上拉没有列进 BOM，这里不强求。
- **温度阈值**要按 APV 的 R-T 表复核 MTP 与固件（B25/50 = 3380K），见 X-6。

---

## 8. 通讯与中断

| 信号 | U1 脚 | 外接 | 核算 / 依据 |
|---|---|---|---|
| `I2C_SCL` | 31 | R220 2.2k → `+3V3` | p.36：SDA/SCL 为开漏，必须上拉。VIH = 0.7 × AFE_3V3，最坏 0.7 × 3.465 = 2.43V < 3.3V ✅（p.16）。上升时间 0.8473 × 2.2k × 50pF ≈ 93ns < 300ns（400kHz）✅。低电平灌电流 3.3 / 2.2k = 1.5mA ✅ |
| `I2C_SDA` | 32 | R221 2.2k → `+3V3` | 同上 |
| CRC | — | — | -0000 版本 CRC 默认关（p.3）。固件初始化时写 `USE_COMM_CRC` = 1（0xA3 bit2，p.111），之后每帧带 CRC-8（多项式 x⁸ + x² + x + 1，p.37–38） |
| `AFE_ALERT` | 28 xALERT | R222 100k → GND | 推挽输出，高电平为 3.3V（p.24）；`ALERT_POL` 的 OTP 默认值为 1，即高有效（p.48）。空闲为低，下拉不耗电；报警为高时耗电 33µA。AFE 关断或未上电时，由 R222 保持为低，表示无中断 ✅ |
| `AFE_WAKE` | 30 NSHDN | R223 10k → `+3V3` | 内部下拉 5MΩ（p.14）：3.3 × 5M / 5.01M = 3.29V > 上升门限 2.65V ✅。MCU 的 PB5 开漏拉低时 < 0.4V，低于下降门限 1V ✅；灌电流 0.33mA。进入关断有 8ms 去抖（p.14）；退出关断后等 ≥ 5ms 再发 I2C（p.22）。NSHDN 的绝对最大值是 9V（p.7） |
| WDT | 29 | **悬空**（NC） | 见 §0 第 2 条。p.24：外部拉高就会复位 MP2797；p.48：`WDT_RST_EN` 默认为 1；Table 23 要求悬空。WDT 输出的是 10ms **高**脉冲（p.14），与 CH32 的 NRST（低有效）极性相反，不接 MCU（05 规格书 §1.5 同一结论） |
| SDO、GPIO3/nCS | 33、34 | 悬空 | I2C 版本不用 SPI。GPIO3 复位后默认开 20k 上拉（p.48），Table 23 的附注已经满足 |
| GPIO1、GPIO2 | 36、35 | 悬空 | `FET_SRC` 默认为 0，即寄存器控制（p.44），GPIO 不参与 FET 开关。GPIO1/2 默认开 20k 上拉（p.47–48）。**固件不得把 FET_SRC 改成 1**，否则悬空脚会决定 FET 状态 |
| GPIOHV1、SBYDSG | 37、41 | 悬空 | 不用待机 P-MOS。固件保持 `STBY_STATE_EN` = 0（p.45） |

**本页不放 MCU 侧的任何件**：MCU 侧的 PB4/PB5/PB6/PB7 已在 05 页直连（05 规格书 §1.3）。

---

## 9. 电源

### 9.1 VTOP 与 REGIN 的来源：从 BAT+ 取（建议新增全局标签，U-1）

- 手册依据：
  - p.6 VTOP「must be connected to the top of the battery stack」；
  - Figure 26/27 中，RVTOP_FLT 和 RREG 都从电池正的**功率线**取电，位置在 CHG 管之前，而不是从某根采样线。
- 契约里本页**没有 BAT+**，只有 CELL8。两种接法对比：

| 方案 | 做法 | 优点 | 缺点 |
|---|---|---|---|
| **A（推荐）** | 本页新增全局标签 `BAT+`（04 页已经在用），R212、R213 的上端接 BAT+ | 与手册一致。REGIN 的 mA 级电流不流过 CELL8 采样线。J5 拔掉时 AFE 仍然有电，开路检测可以报警 | 需要改契约（`gen_kicad_skeleton.py` 的 SHEETS 与 docs/03 §1），X-5 |
| B | R212、R213 的上端接 `CELL8`，接在 J5 一侧、R209 之前 | 不改契约 | REGIN 电流流过 CELL8 采样线。按 5mA、线阻 0.1Ω 计为 0.5mV，而且随负载跳动，会叠加到第 8 节的读数上。J5 一掉线，AFE 就掉电 |

**本规格按 A 画**；用户选 B 时只改 R212、R213 上端的标签。
- 取电点在 F1 之前还是之后：由 01 页的 BAT+ 定义决定。docs/03 §2.1 的 BAT+ 在 F1 之前，所以 F1 熔断后 AFE 仍然供电，可以上报故障 ✅。
- **VTOP 下限**：推荐工作范围 18–75.2V（p.7）。8 × 2.5V（UV 门限）= 20V，余量 2V。VTOP 的 UVLO 在 14.6–17V（p.8）。与 docs/03 §3.1 一致。

### 9.2 REGIN 外置 NPN（Q201 MMBT5551）

```
BAT+ ─ R213 510Ω ─ REG_C ─┬─ C213 1µF/100V → GND
                          └─ Q201.3 (C)
REGCTRL (U1.24) ─ Q201.1 (B)
REGIN   (U1.25) ─ Q201.2 (E) ─ C214 10µF → GND（贴 25 脚）
```

- REGCTRL 输出 5.6V（p.13），REGIN = 5.6 − VBE ≈ 5.0V（p.13：4.65–5.4V）。REGIN 的推荐工作范围是 4.5–5.5V（p.7）。
- 手册在 EC 表里只给了关断电流（1µA）和安全模式电流（23µA）（p.8），**没有给工作模式下 REGIN 的电流**。考虑到内部 ADC、电荷泵（静态只需维持 R_PUP 2 × 1µA 等）、NTCB 动态偏置（每次 1.2mA，只在转换期间），以及 xALERT（33µA），估算平均 < 3mA，按 5mA 核算。
- 功耗核算：P_Q = (V_BAT − I·R213 − 5.1V) · I；P_R = I² · 510Ω。

| I_REGIN | V_BAT | V_CE | P_Q201 | P_R213 |
|---|---|---|---|---|
| 2mA | 29.2V | 23.1V | 46mW | 2mW |
| 5mA | 29.2V | 21.5V | **108mW** | 13mW |
| 5mA | 53V（TVS 钳位瞬态） | 45.4V | 227mW（瞬态） | 13mW |
| 10mA | 29.2V | 19.0V | 190mW | 51mW |

- MMBT5551 额定 300mW（25°C），θJA 按 (150 − 25) / 0.3 ≈ 417°C/W 估。5mA 时温升 45°C，环境 45°C 时 Tj ≈ 90°C ✅。**10mA 时 Tj ≈ 124°C，余量不足**。
- VCEO 160V ≫ 53V ✅。hFE 200–300（嘉立创标注档位）：REGCTRL 驱动能力 1mA（p.13 的测试条件）× 200 = 200mA，远大于需求 ✅。
- 沿用 BOM 的判据：**样板实测 REGIN 电流，> 5mA 时换 BCX56（C24280，SOT-89，扩展库，库存 39.6 万）**。换料时要重新取库（库里没有 C24280），并按规则 0b 核封装。
- R213 0603：5mA 时功耗 13mW，额定 100mW ✅。
  - 3V3 对地短路时，REGIN 限流 55–80mA（p.13），实际被 R213 限到 (29 − 5) / 510 ≈ 47mA，R213 功耗 1.1W。0603 会开路，相当于一只熔丝，C213 与 Q201 不会被连带烧坏。可以接受。
- C213 1µF/100V 1206：电压 = BAT+（约 29V，瞬态 53V），100V ✅。C212 同理。

### 9.3 内部 LDO 输出

| 脚 | 网络 | 电容 | 要求（Table 18） | 偏压下的有效容量 | 结论 |
|---|---|---|---|---|---|
| 25 REGIN | `REGIN` | C214 10µF/10V X5R 0603 | 3.3µF（Required） | 5.1V 下约 4.5µF（−55%） | ✅（原 4.7µF 只剩 2.6–2.8µF ✗） |
| 26 3V3 | `AFE_3V3` | C215 1µF/25V X5R 0402 | 0.47–10µF，典型 1µF | 3.3V 下约 0.6–0.7µF | ✅（> 0.47） |
| 27 VDD | `AFE_VDD` | C216 1µF/25V X5R 0402 | 1µF | 1.8V 下约 0.8µF | ✅ 略低于标称，P2 |
| 22 VREF | `AFE_VREF` | C217 1µF/25V X5R 0402 | 1µF | 3.3V 下约 0.6–0.7µF | ⚠ P2：VREF 是 ADC 基准；可改 0603 1µF/50V C15849（基础库，库里有符号），3.3V 下约 0.9µF（U-9） |
| 21 NTCB | `NTCB` | C218 10nF | ≤ 10nF | — | ✅（见 §7.4） |

- **AFE_3V3 只接 C215**，外面不带任何负载，也不和板上的 `+3V3` 相连。MCU 由 04 页 buck 供电（05 规格书 X-4 的前提）。
- C215、C216 用的是 C52923（0402，用户降本已定）。按规则 00 ② 的表，1µF 本应默认 0603。这里 0402 仍然满足 3V3 的下限；VDD、VREF 的余量偏小，列为 P2，不改。

### 9.4 逐电源脚去耦（规则 00 ①）

| 电源脚 | 去耦 | 回流 | 摆放 |
|---|---|---|---|
| 45 VTOP | C212 470nF/100V（前面串 R212 20Ω） | GND | 贴 45 脚 |
| 25 REGIN | C214 10µF | GND | 贴 25 脚（Figure 24 p.120 点名） |
| Q201 集电极 | C213 1µF/100V（前面串 R213） | GND | 贴 Q201 |
| 26 3V3 | C215 1µF | GND | 贴 26 脚（Figure 24 点名） |
| 27 VDD | C216 1µF | GND | 贴 27 脚（Figure 24 点名） |
| 22 VREF | C217 1µF | GND | 贴 22 脚（Figure 24 点名） |
| 21 NTCB | C218 10nF | GND | 贴 21 脚（Figure 24 点名） |
| 42 VCP | C219 100nF → **VMID**（不是 GND） | VMID | 贴 42/43 脚 |
| 43 VMID | C220 100nF/100V（前面串 R214） | GND | 贴 43 脚 |
| 38 PACKP | C221 10nF/100V（前面串 R215） | GND | 贴 38 脚 |

- MP2797 的每个供电或内部稳压脚，都有手册规定的电容，逐脚无遗漏 ✅。
- **不另外加 100nF**：手册对这几脚的电容都给了定值（C3V3 最大 10µF、CNTCB 最大 10nF、CPACK「不得增减」），多加反而越界。
- 整轨储能：AFE 的各条轨都是片内 LDO 的输出，不需要额外的 bulk 电容。BAT+ 的 bulk 在 01 页（C5/C6）。

### 9.5 AGND 与接地

- p.6：AGND 靠近分流器的 SRP 端连接。
- Figure 23（p.120）：AGND 单独一块地平面，经一只 0Ω 接到电池组负极；二极管等保护件接 PGND。
- 本设计中，全板 `GND` 就是在分流器电池侧开尔文点单点汇合的信号地（docs/03 §1），等效于 Figure 23 的做法，**U1.23 直接接 `GND`，不另设 AGND 网络**。
- 布局要求：
  - U1 下方与周围在顶层铺一小块地，汇集 C214–C218、C210/C211、D201、NTC 回线的回流，再用多个过孔进 In1 的 GND 平面。
  - GND 平面与功率地 BAT− 只在分流器电池侧相连（01 页 Net-Tie，X-3）。
  - **不要让 BAT−/PACK− 的功率电流从 U1 附近的地流过**。

### 9.6 上电时序，以及 05 页「AFE_ALERT 选 5V 容忍脚」的前提是否成立

实际时序（按本规格）：
1. 接上电池：BAT+ 建立。VTOP 经 20Ω/470nF 在约 10µs 内跟上。U1 处于关断模式（NSHDN 被内部 5MΩ 下拉），REGIN 只是松散稳压（p.22）。
2. 04 页 buck 起振，`+3V3` 建立。R223 把 NSHDN 拉高，U1 进入安全模式：FET 全关，通讯可用，AFE_3V3 建立。
3. MCU 起动。**NSHDN 变高后至少等 5ms 再发 I2C**（p.22）。

- 所以在正常上电中，AFE_3V3 **晚于**本板 +3V3，因为 NSHDN 由 +3V3 拉高。05 规格书 §1.2 的说法「AFE 的 3V3 … 上电顺序也与本板的 buck 无关」**不准确**。
- **但「选 5V 容忍脚」这个结论仍然成立**，理由换成下面两条：
  1. 本板 +3V3 可能先掉（F11/R42 熔断、buck 故障、欠压），而 AFE 由 VTOP 独立供电。NSHDN 跌落后要经过 8ms 去抖（p.14）才进入关断；而且 3V3 可以配置成在关断模式下保持开启（p.22、p.32）。这段时间里 xALERT 可能输出 3.3V，而 MCU 的 VDD 已经为 0。
  2. xALERT 是推挽输出（p.24），会主动输出高电平。
- 一个副作用（报用户，不改）：本板 +3V3 一掉，NSHDN 随之变低，8ms 后 AFE 进入关断，FET 全关，PACK 断电。这是**失效安全**的方向，但也意味着 buck 故障会让整包停止输出。
- I2C 反灌：SCL/SDA 的绝对最大值只对 AGND 规定（−0.3~6V，p.7），没有「≤ 3V3 + 0.3」的限制。据此推断这两只脚对 AFE_3V3 没有钳位二极管：AFE 关断、总线被 +3V3 上拉时，不会经引脚向 AFE_3V3 反灌。这是推断，**样板实测确认**：在 NSHDN 为低时测 AFE_3V3 是否被抬起。

---

## 10. 连接器 J5（采样端子）

### 10.1 器件

- **C40669 BOOMELE XH-13A**：XH 2.50mm 13P 立式板端座，扩展库，**嘉立创库存 244**（够 244 块，量产前备货）。
  - 封装 `jlc:CONN-TH_13P-P2.50_XH-13A`，`fp_compare.py` 实测：13 个 PTH，孔 ⌀1.0mm，相邻中心距 12 × 2.50mm ✅，1 脚为方焊盘，丝印有方向标记，有 courtyard。
  - 板端件 ✅（线束端胶壳是 XHP-13）。
  - 采样与 NTC 线的电流只有 µA–mA 级；被动均衡最大 45mA。XH 额定 2–3A，余量充足。
- 备选：C22366169（Megastar，封装实测 2.50mm，库里有符号 `ZX-XH2.54-13PZZ`）。

### 10.2 针脚定义（推荐，U-4）

| J5 针 | 网络 | 说明 |
|---|---|---|
| 1 | `NTC_CELL1` | 电芯 NTC1 信号 |
| 2 | `GND` | NTC1 回线（与针 1 双绞） |
| 3 | `NTC_CELL2` | 电芯 NTC2 信号 |
| 4 | `GND` | NTC2 回线（与针 3 双绞） |
| 5 | `CELL0` | 电芯 1 负极（采样线，**不是 GND**） |
| 6 | `CELL1` | 电芯 1 正极 / 电芯 2 负极 |
| 7 | `CELL2` | — |
| 8 | `CELL3` | — |
| 9 | `CELL4` | — |
| 10 | `CELL5` | — |
| 11 | `CELL6` | — |
| 12 | `CELL7` | — |
| 13 | `CELL8` | 电芯 8 正极（栈顶，约 29.2V） |

理由：
- NTC 脚的绝对最大值只有 6V（p.7）。把 NTC 放在低压端，与它相邻的最高电位只有 CELL0（约 0V），线束或端子一旦短路，也不会把 CELLn 的高压灌进 NTC 脚。
- CELL0–8 按电位顺序排列，相邻两针的压差只有一节电芯（≤ 3.65V）。这样线束随机插接、相邻针短路时，最多只是短路一节电芯；这时由 R_CELL 33Ω 限流，3.65 / 66Ω = 55mA ✅。
- NTC 回线单独占两针，**不与 CELL0 共用**：CELL0 在均衡时流过最多 45mA，共用会给 NTC 读数叠加毫伏级误差（p.120 第 8 条要求星形接地）。
- ⚠ 线束侧：采样线直接从电芯引出，**线束磨破时，单节电芯短路电流可达上千安**。板上的 R_CELL 保护不了线束本身。建议在电芯端的采样线上串保险丝，或者用可熔断的细线段（系统级，列入 U-4 一并确认）。

### 10.3 画在哪一页

- **J5 画在本页**，放在最左侧。
- `CELL0–8` 与 `NTC_CELL1/2` 仍然按契约用全局标签，名字保持不变，便于网络类（`CELL*`）匹配，也便于跨页查找。虽然目前它们只在本页使用，但全局标签只在一页出现不影响 ERC 判读。
- **J6（均衡端子 BAL0–8）在 03 页**，本页不出现。

---

## 11. 规则 00 ② 封装下探、规则 00 ① 电容完备性、版面建议

### 11.1 封装下探（逐颗问「能不能再小一号」）

| 位号 | 现封装 | 能否更小 | 判据 |
|---|---|---|---|
| R201–R209 | 0805 | ✗ 0603 余量 1.22（85°C） | 最坏 67mW（§4.3） |
| C201–C208 | 0603 → **0402** | ✅ 已下探 | 3.65V 工作，50V 0402 基础库 |
| R210/R211、R214、R215、R216–R223 | 0402 | 已经最小 | 功耗 ≪ 1mW；R214/R215 瞬态 24V < 50V |
| C209–C211 | 0603 → **0402** | ✅ 已下探 | SRP/SRN ≤ 6V（绝对最大），16V 0402 足够 |
| R212 VTOP 20Ω | 0603 | ✗ | 稳态几乎无功耗。但 C212 被击穿短路时，电阻两端是 29V：P = 29² / 20 = 42W，哪个封装都会开路。0603 可以承受 VTOP 上 TVS 钳位的瞬态（ΔV 24V，脉冲能量 ½CV² = 0.13mJ）。0402 的额定电压 50V 虽然够，但脉冲耐量偏小。**保持 0603** |
| R213 510Ω | 0603 | ✗ | 3V3 短路时充当熔丝（§9.2）。0402 在正常 5mA 下也够（13mW），但留 0603 让熔断行为可预期，并与 BOM 一致。**保持**。P2：如果用户接受 0402，可以下探 |
| C212 470nF/100V | 0805 | ✗ | 100V 的 470nF 没有 0603 基础库料，也要考虑偏压下的容量 |
| C213 1µF/100V | 1206 | ✗ | 100V 1µF 只有 1206（C282823 与 01、04 页同料，不增加料种） |
| C214 10µF/10V | 0603 | ✗ | 容量与偏压 |
| C215–C217 1µF | 0402 | 已经最小（用户已定） | 见 §9.3 的 P2 |
| C218 10nF、C222–C225 | 0402 | 已经最小 | — |
| C219、C220 100nF/100V | 0805 | ✗ | 100V 且要求偏压下 ≥ 87nF（§6.3） |
| C221 10nF/100V | 0603 | ✗ | 100V 的 10nF 没有 0402 料 |
| D201 BZT52C3V3 | SOD-123 | 可以换 SOD-323（C173439，扩展库，200mW），**不建议** | 随机插接时 C0 钳位可能要吸收百毫安级的瞬态。500mW 的 SOD-123 更稳，而且是用户按 Table 18 定过的料 |
| Q201 | SOT-23 | 已经最小 | 108mW / 300mW |
| J5 | THT | — | 结构件 |

### 11.2 电容完备性（逐 IC、逐电源脚）

| IC | 电源脚 | 去耦 | 状态 |
|---|---|---|---|
| U1 MP2797 | 45 VTOP | C212 470nF（+R212） | ✅ |
| | 25 REGIN | C214 10µF | ✅（改料） |
| | Q201 集电极（REGIN 前级） | C213 1µF | ✅ |
| | 26 3V3 | C215 1µF | ✅ |
| | 27 VDD | C216 1µF | ✅ |
| | 22 VREF | C217 1µF | ✅（P2） |
| | 21 NTCB | C218 10nF | ✅ |
| | 42 VCP ↔ 43 VMID | C219 100nF | ✅（改料） |
| | 43 VMID | C220 100nF | ✅ |
| | 38 PACKP | C221 10nF | ✅ |

**docs/03 §7 的 MP2797 行可以关闭**：原写「BAT/VDD 输入、内部 LDO 输出、电荷泵 — 待核」，逐脚结果见上表。

### 11.3 版面建议（A3，从左到右）

```
┌──────────────────────────────────────────────────────────────────────────────────┐
│ 标题：02 AFE：MP2797（8S，C9–C16 并到 C8；WDT 悬空；xALERT 高有效 100k 下拉）      │
├───────────────┬───────────────────┬────────────────────┬─────────────────────────┤
│ ① J5 + NTC 回线│ ② 电芯采样 RC       │ ③ U1（镜像）         │ ④ 右侧：电源/驱动/通讯      │
│ J5 竖放        │ R201–R209 一列      │ 左：C0–C16、CHG、   │ 上：BAT+ → R212/C212 →  │
│ 针 1–4 NTC     │ C201–C208 阶梯      │  DSG、PACKP、       │  VTOP；R213/C213/Q201/ │
│ 针 5–13 CELL   │ D201（VC0→GND）     │  xALERT、3V3        │  C214 → REGIN          │
│ 全局标签 CELLn │ C9–C16 并线到 VC8   │ 右：通讯、NTC、      │ 中：FET_MID → R214/C220 │
│ 朝左           │                     │  VTOP、VCP、VMID、  │  C219；PACK+ → R215/C221│
│               │ 下：SRP/SRN →        │  REGIN、SRP/SRN     │  CHG_G、DSG_G 全局标签  │
│               │ R210/R211、C209–C211│                    │ 下：R220–R223 → I2C_*、│
│               │                     │                    │  AFE_ALERT、AFE_WAKE   │
│               │                     │                    │ 最下：NTCB、R216–R219、 │
│               │                     │                    │  C218、C222–C225；      │
│               │                     │                    │  C215–C217             │
└───────────────┴───────────────────┴────────────────────┴─────────────────────────┘
```

- U1 镜像以后，CHG/DSG/PACKP/xALERT 与电芯脚同在左侧（原符号的右侧），在电芯列的**上方**。所以 CHG_G、DSG_G、PACK+、AFE_ALERT 的标签从 U1 左上方引出后向上走，再绕到右上角的驱动区。
  - 如果觉得绕，就不镜像：J5 与 RC 放右侧，信号流改成从右到左。两种都可以，由画图方目视选交叉少的一种。**规则 00 ③ 的判据是交叉少、不重叠**。
- 全局标签只用于契约里的名字，外加 `BAT+`（U-1）。页内网络全部用局部标签：
  `VC0…VC8 SRP_F SRN_F VTOP REG_C REGCTRL REGIN AFE_3V3 AFE_VDD AFE_VREF NTCB VCP VMID PACKP`。
  全部用下划线分隔，不含「/」，也不与全局名重名。
- 左侧标签朝左长（justify right），右侧朝右（规则 00 ⓪c）。
- 页内文字只写本页的要点，不写旧型号：MP2797、8S、C9–C16 并到 C8、WDT 悬空、R222 下拉、R223 接 +3V3。

### 11.4 PCB 布局要点（供布局阶段，按手册 p.120）

- 去耦件紧贴对应脚（Figure 24）：C214 贴 25 脚，C215 贴 26，C216 贴 27，C217 贴 22，C218 贴 21，C219 贴 42/43，C220 贴 43，C221 贴 38，C212 贴 45。
- R210/R211 与 C209–C211 紧贴 15/16 脚。SRP/SRN 从 RS1 起成对平行走线（Figure 25）。
- R201–R209 与 C201–C208 靠近 U1 的电芯脚，J5 可以稍远，因为采样线本身只流过 mA 级电流。
- U1 放在中部 AFE 区，远离 MOSFET 和分流器的功率铜（docs/03 §9）。RT3/RT4 在 01 页贴热源，它们的回线单独走到 U1 的地（p.120 第 8 条）。
- R_DRV1、R_DRV2（01 页）在布局时放在 U1 的 44/39 脚附近，`CHG_G`/`DSG_G` 按 GATE 网络类走线。
- 高压信号网络（VTOP、PACKP、VMID、VCP、CHG_G、DSG_G、FET_MID 引线、BAT+ 引线）与 3.3V 信号之间，按 60V 留间距（嘉立创外层，IPC-2221 B2 约 0.6mm）。建议建一个 `HV_SIG` 网络类：0.25mm 线宽、0.6mm 间距（X-7）。

---

## 12. 待用户定清单与跨页事项

### 12.1 待用户定

| # | 事项 | 选项 | 推荐 |
|---|---|---|---|
| **U-1** | VTOP、REGIN 从哪取电 | A：本页新增全局 `BAT+`（改契约）；B：接 CELL8（J5 侧） | **A**（§9.1，手册 Fig 26/27） |
| **U-2** | 电芯温度 NTC 放在哪 | ① 线束侧探头 ×2（10k、B25/50 = 3380K，与固件表同口径），从 BOM 删去 RT1/RT2，另列「非嘉立创件」；② 保留 RT1/RT2 0603 放板上（测的是板温，不是电芯温度）；③ ① 加 ② 的 DNP 焊盘 | **①**。docs/01 §温度写的就是「电芯表面（中间与边缘各一）」 |
| **U-3** | C_NTC1–4（C222–C225） | DNP（手册做法）/ 1nF / 原 100nF | **DNP，值栏写 1nF 备用**。100nF 与 NTCB 动态偏置冲突（§7.3） |
| **U-4** | J5 针脚定义与线束保护 | §10.2 表；电芯端采样线加保险丝 | 按 §10.2。线束保险丝由系统定 |
| **U-5** | BOM 改料（全部是基础库，上料费 ¥0） | C_CELL 9 → 8 只、0603 → 0402 C307331；C_SNS ×3 → C1525；C_REGIN → C19702 10µF（需取库；不取库时可用 2 只 C19666 并联代替）；C_VCP → C28233 | 全改 |
| **U-6** | 位号段 | 三位数 2xx（R201…、C201…）/ 两位数 R20–R39（与 03 页冲突） | **2xx** |
| **U-7** | VCP 电容扩展焊盘 | C219 旁预留 0805 焊盘 C226（DNP） | **预留**（§6.3：按 Qg 等效为 144nF，超出 Table 22 范围，样板实测后再定） |
| **U-8** | PACK 反接保护 | 不做 / 系统级方案 | 本版不做。PACK 反接会烧 PACKP（§6.4） |
| **U-9** | 两处容值余量（P2） | CNTCB 10nF → 4.7nF C1538（Table 18 为最大 10nF）；C_VREF 0402 → 0603 C15849 | 本版照原值画，样板实测 VREF 与 NTC 读数后再议 |
| **U-10** | MTP 编程（NSHDN 需加 7.5V，p.36） | ① 不做 MTP，固件每次上电写寄存器（绝大多数配置寄存器是 R/W）；② 预留测试点，编程时断开 PB5 | **①**。注意：PB5 是 FT 脚，但 7.6V 超出它的耐压，不能在线直接加 7.5V。安全模式下 FET 默认全关，未配置前是安全的 |

### 12.1b 用户决定（2026-09-27，画图方照此画）

用户已对本规格书作出决定，**以下为定稿，§0–§11 中写成「推荐」「待用户定」的地方一律按此执行**：

| # | 决定 | 对本页画图的含义 |
|---|---|---|
| X-1 | 01 页功率管**改为手册共漏拓扑**：CHG 组在电池侧、DSG 组在 PACK 侧，FET_MID 是漏极公共点；R_PUP、DZ、PNP 快关的参考点随之改到各组源极 | 本页不变：CHG→`CHG_G`，DSG→`DSG_G`，VMID→R214→`FET_MID`，PACKP→R215→`PACK+` |
| U-1 | VTOP、REGIN **从 BAT+ 取电**；02 页契约加入 `BAT+`（`gen_kicad_skeleton.py` 的 SHEETS 已记录） | R212、R213 的上端挂全局标签 `BAT+` |
| U-2 | 电芯 NTC **改为线束探头**（非嘉立创件）；BOM 删除 RT1/RT2；RT3/RT4 画在 01 页 | 本页不画任何 RT；NTC_CELL1/2 经 J5 出板 |
| U-3 | C222–C225 **DNP**，值栏写「1nF DNP」（C1523） | 放焊盘，标 DNP |
| U-4 | J5 针脚：1 NTC_CELL1 / 2 GND / 3 NTC_CELL2 / 4 GND / 5–13 CELL0–CELL8；线束侧电芯端的采样线加保险丝（线束件） | 按 §10.2 画 |
| U-5 | 改料全部采纳：C201–C208 共 8 只，用 C307331 0402；C209–C211 用 C1525；C214 用 **C19702**（已由主代理取库，符号 `jlc:CL10A106KP8NNNC`）；C219 用 C28233 | 按 §2.2 |
| U-6 | 位号用 2xx 段 | 按 §2.2 |
| U-7 | 预留 **C226**（100nF/100V 0805 C28233，**DNP**），与 C219 并联在 VCP↔VMID | 在 C219 旁画 C226，标 DNP |
| U-8 | 本版不做 PACK 反接保护 | — |
| U-9 | C218 10nF（C15195）、C217 0402（C52923）照原值画 | — |
| U-10 | 不做 MTP；固件每次上电写寄存器 | 不加 NSHDN 编程测试点 |
| X-4 | 01 页 PACK+ 加 47µF/63V 电解 C48971005（BOM 占位 `C_PACK_E`，01 页画图时再编号） | 与本页无关 |
| X-7 | 网络类已写入 `hardware/mp2645a-bms.kicad_pro`：`CELL_SENSE` 加 `*/VC?`；`KELVIN` 加 `*/SRP_F`、`*/SRN_F`；新建 `HV_SIG`（0.25mm 线宽 / 0.6mm 间距），匹配 `*/VTOP`、`*/PACKP`、`*/VMID`、`*/VCP`、`*/REG_C` | 局部标签名必须严格用 §11.3 列出的名字，否则网络类匹配不上 |

BOM（`docs/02-BOM.csv`）与 docs/03 已按上表同步。

### 12.2 跨页事项（交主代理 / 01 / 03 / 05 页 / 工具 / 固件）

| # | 对象 | 内容 | 等级 |
|---|---|---|---|
| **X-1** | **01 页 + docs/03 §2.1–2.2** | MP2797 手册（Fig 26 p.121、Fig 27 p.122、p.14–15 驱动器参考、p.22 待机模式）是**共漏**：CHG 管在电池侧、源极朝 BAT+；DSG 管在 PACK 侧、源极朝 PACK+；FET_MID 是两组的**漏极**公共点。R_PUP1、DZ1、Q17 集电极回 CHG 源极（BAT+ 侧母线）；R_PUP2、DZ2、Q18 集电极回 PACK+。docs/03 的共源拓扑在两管全关时，会被驱动器把某一组栅极顶开，并让 DZ 长期流过约 12mA（§6.2）。**02 页不受影响**。D4/D5 + PNP 快关（用户已定保留）的参考点要跟着改；闸口 A 专项复核。MOSFET 的发热与 NTC_FET 位置不变 | **P0（01 页）** |
| **X-2** | docs/03 §3.1、§3.2、§4.4、§7 | ① 「xALERT / WDT 开漏上拉 10kΩ」改为：xALERT 推挽，R222 100k 下拉；**WDT 悬空，严禁上拉**（p.24：拉高即复位）。② §3.2 的「58mA、R ≈ 30Ω」改为「33Ω 时典型 39mA、最大 45mA，情况 B 已由 Fig 28 确认」。③ §4.4「58mA 被动均衡」同改。④ §3.1 表中 C_CELL1–9 改为 8 只。⑤ §7 的 MP2797 行按本文 §11.2 关闭。⑥ §3.1 C_REGIN 与 C_VCP 的料号按 U-5 | P1（文档） |
| **X-3** | 01 页 + docs/03 §2.1 图 | **SRP = RS1 电池侧（BAT−/GND 单点），SRN = RS1 PACK− 侧**（Fig 26；p.6 AGND 条）。docs/03 的 ASCII 图画反了。01 页用 Net-Tie 把 `SRP` 开尔文线与 `GND`/`BAT−` 在 RS1 电池侧焊盘处连起来（否则 ERC 会报同网多名，或者两者被合并）。RS1 的开尔文焊盘按 Fig 25 做 | P1 |
| **X-4** | 01 页 | Table 18：**CPACK_E 典型 47µF、最大 200µF**（PACK+ → PACK−）。现在只有 C1–C4 共 4µF（1206 陶瓷，29V 下有效约 2.4µF）。建议在 PACK+ 加一只 47µF/63V 电解（C48971005，与 04 页 C40 同料，不增加料种），它也给短路关断时的 PACK+ 尖峰提供阻尼。需要用户确认（成本约 ¥0.4） | P1 |
| **X-5** | `tools/gen_kicad_skeleton.py` SHEETS + docs/03 §1 | 按 U-1 在 02_afe 的对外网络里加入 `BAT+` | 跟随 U-1 |
| **X-6** | 固件（`firmware/`） | ① `CELL_S_CTRL` = 0x7（p.42，MTP 默认 0xF）。② `USE_COMM_CRC` = 1（p.111）。③ NSHDN 拉高后等 ≥ 5ms 再通讯（p.22）。④ `ALERT_POL` 保持 1。⑤ `FET_SRC` 保持 0；`STBY_STATE_EN` = 0；GPIO1–3 保持 20k 上拉。⑥ `NTCB_DYNAMIC_ON` 保持 1。NTC1/2 设为 Cell 模式，NTC3/4 设为 PCB 模式；门限按 APV R-T 表计算。⑦ `CELL_1K_COMP` = 0。⑧ 硬件门限按 0.1mΩ 换算：SC 800A = 80mV（RNG0）；OC 放电 400A = 40mV；OC 充电硬件设宽，132A 由软件管（§5.2）。⑨ 单管导通时的 17.5mV = 175A 兜底不足以保护体二极管，检测到反向电流就打开另一组管（§5.2）。⑩ 被动均衡按 39mA 典型值估时；均衡期间监视片温（p.33）。⑪ 不依赖 WDT 引脚。⑫ `bms_config.h` 的 `BAL_PASSIVE_*` 注释里的 58mA 改为 39mA | 固件 |
| **X-7** | 网络类（`gen_kicad_skeleton.py` NETCLASSES、`.kicad_pro`） | ① `KELVIN` 加入 `*SRP_F`、`*SRN_F`。② `CELL_SENSE` 加入 `*VC?`（本页的 VC0–VC8）。③ 新建 `HV_SIG`（0.25mm 线宽 / 0.6mm 间距），匹配 `*VTOP`、`*PACKP`、`*VMID`、`*VCP`、`*REG_C`（§11.4） | P2 |
| **X-8** | 03 页 | CELLn 与 BALn 严禁在板上相连（§4.4）；本页不出现 BAL 标签。J6 在 03 页 | 提醒 |
| **X-9** | 05 页规格书 §1.2 | 「AFE 的 3V3 … 上电顺序与本板 buck 无关」不准确：NSHDN 由 +3V3 拉高，正常上电时 AFE_3V3 晚于 +3V3。但 PB4 选 FT 脚的结论仍然成立，理由改为「+3V3 先掉、AFE 仍在工作的 ≥ 8ms 窗口」（§9.6）。05 页图纸不用改 | P2（文档） |
| **X-10** | 取库（规则 0e） | **C19702**（CL10A106KP8NNNC，10µF 10V 0603，基础库）。按 U 项的选择，可能还要取：C24280（BCX56，仅当 REGIN > 5mA）、C1538（仅当 U-9 改 4.7nF）、C15849 已在库 | 取库方 |
| **X-11** | BOM（`docs/02-BOM.csv`） | 按 §2.3 改位号与料号；RT1–RT4 按 U-2 拆分；新增「线束 NTC 探头 ×2（非嘉立创件）」一行 | 主代理 |

---

## 13. 画图方自检清单（画完逐条打勾，复核方逐条复核）

1. U1 的 48 脚逐脚对 §1.3：
   - 8 个 NC 脚放了 NC 标志；
   - C9–C16 共 8 个脚都在 `VC8` 上；
   - WDT 没有接任何东西。
2. 网表中 `CELLn` 与 `VCn` 之间只有 R20x；`VCn` 与 `VC(n−1)` 之间只有 C20x；**任何 `CELLn` 都不与 `GND` 相连**。
3. D201 的方向：阴极（1 脚）在 `VC0`，阳极（2 脚）在 `GND`。
4. `AFE_3V3` 网络只有 U1.26 与 C215 两个节点；`+3V3` 网络在本页只连 R220、R221、R223 三只电阻。
5. NTCB 网络：U1.21、C218、R216–R219 的上端。四路 NTC 的上拉都接 NTCB，不接任何 3V3。
6. C219 的两端是 VCP 和 VMID（**不接 GND**）；C220 的两端是 VMID 和 GND；R214 的两端是 FET_MID 和 VMID。
7. R215 的两端是 PACK+ 和 PACKP；C221 为 10nF/100V（C282516），不许改值。
8. SRP → R210 → U1.15，SRN → R211 → U1.16，没有接反；C209 跨在两个滤波节点之间，C210/C211 各自到 GND。
9. Q201：1 脚（B）接 REGCTRL，2 脚（E）接 REGIN，3 脚（C）接 REG_C；R213 与 C213 都在 REG_C 上。
10. R222 下拉（不是上拉）；R223 接 `+3V3`（不是 `AFE_3V3`）。
11. J5 的针脚定义符合 §10.2，1 脚方焊盘对应 NTC_CELL1。
12. 每颗件的 `LCSC` 字段与 §2.2 一致；C222–C225 标 DNP；C214 取库后使用 C19702 的符号与封装，**不用其它料的符号顶替**。
13. ERC（本页）为 0。根图的跨页 `isolated_pin_label` 只允许出现在 01/03 页尚未画出的网络上。
