colemandlut/MP2645A-BMS/design/05_mcu_comm-review-qwen-adjudication.md

# 05 页第二复核（qwen3.8-27b）P0/P1 裁决（主代理，2026-09-27 JST）

依据：封装文件焊盘坐标（`hardware/lib/jlc/jlc.pretty/*.kicad_mod`）。**KiCad 封装坐标 y 轴向下**（y 为正 = 图上/板上的下方）。
qwen 报告把 y>0 当成「上」，导致下面两条的方位全部上下颠倒。

| 条目 | qwen 结论 | 焊盘实测（y 向下换算后） | 手册 | 裁决 |
|---|---|---|---|---|
| P0-1 Y1 `CRYSTAL-SMD_4P-L3.2-W2.5-BL` | pad1 左上，与手册 Top View #1 左下 180° 错位 | pad1 (−1.10,+0.85)=**左下**、pad2 右下、pad3 右上、pad4 左上；1 脚丝印圆 (−1.60,+1.25)=左下 | Top View：#1 左下、#2 右下、#3 右上、#4 左上 | **不成立**：逐脚一致 |
| P1-1 L2 `FILTER-SMD_4P-..._ACT1210` | pad2/4 与 TDK 4/2 互换 | pad1 (−0.5,+1.57)=左下、pad2 右下、pad3 右上、pad4 左上（长轴竖放）→ 同一端成对 {1,2}、{3,4}，绕组 1↔4、2↔3 各在同一长边 | TDK：1 左上、2 左下、3 右下、4 右上（长轴横放），同端成对 {1,2}、{4,3}，绕组 1↔4、2↔3 | **不成立**：旋转 90° 后同构，编号走向一致 |
| P1-4 SW1 90°/270° 贴装 | 贴装旋转错会让按键恒按下 | 封装 {1,2} 在同一边、{3,4} 在另一边，与手册内部两极一致 | — | **降为 P2（PCB/CPL 阶段注意）**：属贴片坐标旋转核对，不是原理图/封装错误 |
| P1-2、P1-3 | JP1 叠放、r2 空引脚名 | r3/r4 已修 | — | 已关闭 |

结论：第二复核对 r2 快照 **P0 = 0、P1 = 0**（P1-2/P1-3 已在后续轮次关闭）；P2 三条（规格书 §3.3 「±40V」应按 TI SLOS346K p6 订正、J7 符号名 XH2.54 与实测 2.50mm 不符、绿灯算式留档）并入待用户定的 P2。
教训：给第三方复核方的任务书里写明「KiCad 封装坐标 y 轴向下」。
