colemandlut/MP2645A-BMS/design/05_mcu_comm-review-qwen.md

# 05_mcu_comm 第二复核报告（review2 / qwen3.8-27b）

- 复核方：review2（阿里云 qwen3.8-27b，规则 00c 第 6 泳道）；画图方 DeepSeek、第一复核方 Opus，三方不同厂商。
- 快照：`review/05-r2/`（`05_mcu_comm.kicad_sch`、`erc.json`、`netlist.xml`、`sch.pdf`，05 页在 PDF 第 6 页）
- 规格书：`design/05_mcu_comm-spec.md`（第一复核方 Opus 按手册编写，本报告对其前提与页码依据独立质疑）
- 用户决定（docs/03 第 6 节、docs/02-BOM.csv MCU 段）：RS485 不画；调试口 J8 1×6 2.54 DNP；CAN 待机超标接受；HSE 负载电容 33pF；绿灯限流 330Ω；删 PWR_EN；CAN 终端为 R55 串 JP1 跳线可选（已画）。
- 纪律：未读画图方报告（`05_mcu_comm-draw-report.md`、`*-draw-*.out`）与生成脚本注释，独立重推。
- 开工时间：2026-09-27 13:13 JST；收稿 2026-09-27 15:5x JST。
- 方法：网表逐网络重推 + 每颗 IC 按本地数据手册逐脚核对 + 封装与数据手册引脚位/推荐焊盘几何比对 + ERC 复算 + PDF 第 6 页目视。证据图存 `/tmp/`（c9002_*.png、c95572_p3.png、sw1_*.png、sch_p6_05.png 等）。

## P0（停线）

### P0-1  Y1 晶振封装 pin 号与 YXC 数据手册 180° 错位（0°/180° 贴装 HSE 必死）

- 位号/网络：Y1，HSE_IN（pad1）、HSE_OUT（pad3）、GND（pad2/4）。
- 封装 `jlc:CRYSTAL-SMD_4P-L3.2-W2.5-BL`（`hardware/lib/jlc/jlc.pretty/`）：
  pad1 (−1.10,+0.85)=左上、pad2 (+1.10,+0.85)=右上、pad3 (+1.10,−0.85)=右下、pad4 (−1.10,−0.85)=左下；pin1 丝印圆在左上 (−1.60,+1.25)。
- 数据手册 `datasheets/C9002.pdf`（YXC YSX321SL，3225）实读（6x 渲染）：
  - **Top View（贴装后顶视外观，marking 面朝上）：#1 左下、#2 右下（GND）、#3 右上、#4 左上（GND）**，长边 3.20 水平；
  - Bottom View（底视）：#1 左上、#2 右上、#3 右下、#4 左下 —— 与 Top View 沿长边翻转 180°（y→−y、x 不变），两图物理自洽，无二义；
  - Top View Crystal Connection 图确认：#1/#3 为振脚、#2/#4 为 GND（GND 对角=左上–右下，振脚对角=右上–左下）。
- 设计：Y1.1=HSE_IN→pad1（左上）、Y1.3=HSE_OUT→pad3（右下）、Y1.2/4=GND。
- 推演（贴装顶视=数据手册 Top View 方位）：
  - **0°/180° 贴装**：左上位置是物理 #4（GND）而该处焊盘为 pad1=HSE_IN → **HSE_IN 直短 GND**；右下位置是物理 #2（GND）而该处焊盘为 pad3=HSE_OUT → **HSE_OUT 直短 GND**。HSE 不起振，MCU 时钟链（12MHz PLL×144MHz）建立失败。
  - 90°/270° 贴装正确（晶振两电极无极性，270° 时两振脚互换无碍）。对角正交关系决定了 0/180 无法靠旋转自救。
- 定性：r2 快照无 PCB，属**潜在 P0**——默认 0° 贴装即失效，且封装自身 pin1 丝印圆（左上）与数据手册 pin1 位（左下）直接矛盾。
- 修复（库级，二选一，须实物或 JLC 官方封装佐证）：
  (a) 换 pad 号：pad1→左下、pad2→右下、pad3→右上、pad4→左上（即 1↔3、2↔4 互换），并同步修正 pin1 丝印圆；
  (b) 若实物 corner cut 在左上（即数据手册印刷错误），则封装正确、数据手册作废——**两者必居其一错，下单打样前必须用实物裁决**。
- 附注：封装 descr 写「10PPM」而 BOM 写「±20ppm」（见观察项 O6），修库时一并改。

## P1（必改）

### P1-1  L2 共模电感封装 pad2/4 与 TDK 引脚 4/2 互换（贴 L2 时 CAN 总线短接）

- 位号/网络：L2，CAN_H_X（pad1）、CAN_L_X（pad2）、CAN_L（pad3）、CAN_H（pad4）。
- 数据手册 `datasheets/C95572.pdf`（TDK EMC ACT1210-510，4 页）p3 实读：
  物理引脚位 **1 左上、4 右上、2 左下、3 右下**；电路原理图 **绕组 1=pin1↔4（上对）、绕组 2=pin2↔3（下对）、No polarity**；参数 51µH@100kHz、CM 阻抗 2600Ω@10MHz、DCR 0.7Ω、200mA max、80V max、AEC-Q200 —— 与规格书 §3.5 全对。
- 封装 `jlc:FILTER-SMD_4P-L3.2-W2.5-BL_ACT1210`：pad1 左上、pad2 右上、pad3 右下、pad4 左下 → **pad2↔TDK4、pad4↔TDK2 互换**（pad1/3 巧合对）。
- 推演：L2 实际贴装时绕组 A（左上↔右上）把 **CAN_H_X 与 CAN_L_X** 接成、绕组 B（左下↔右下）把 **CAN_H 与 CAN_L 以 ~0.7Ω 直流短接** → CAN 差分总线死短，节点必进错误态。
- 定性：L2 现 DNP 且首版贴 R56/R57 0Ω 旁路（CAN_H_X→R56→CAN_H 直通），**首版无碍；贴 L2 前必须库级修复**（pad 2↔4 换号）。

### P1-2  JP1 与 R55 符号叠放（可读性，r2 页 6 目视确认）

- 位号：JP1（2P 排针）、R55（120Ω 0603）。r2 快照两符号图形重叠，走线/引脚号不可辨。
- 修复：挪开其一（r3 已挪开，git log 可查；本报告针对 r2 如实记录）。

### P1-3  r2 快照 4 类内嵌符号空引脚名，与库符号不一致

- 现象（r2 快照 `05_mcu_comm.kicad_sch`）：
  - X322512MSB4SI（Y1）4 脚全空，库符号为 OSC1/OSC2/GND/GND；
  - 0402CG330J500NT（C56/C57）2 脚空；
  - FC-2012HRK-620D（R55 所用 0603 库符号）2 脚空，库为 −/+；
  - 0805G（LED3）2 脚空，库为 A/K。
- 影响：仅显示层，网表连接按 pin 号不受影响（0 差异）；但冻结快照内嵌副本与库漂移，后续 diff/复核失准。
- 备注：git log 示 r4 已做库级修复（≤4 脚符号 pin_names hide、两脚无源件 pin_numbers hide，`fetch_jlc_parts` 自动执行），本报告仅对 r2 如实记录。

### P1-4  SW1 布局约束：90°/270° 贴装将 KEY 与 GND 常态短路（PCB 阶段强制执行）

- 位号/网络：SW1，{1,2}=KEY（下边一对）、{3,4}=GND（上边一对）。
- 数据手册 `datasheets/C318884_TS-1187A-B-A-B.pdf`（XKB TS-1187A）实读：
  电路图 **A—B（上对）一极、C—D（下对）另一极**，单一触点；顶视 A 左上、B 右上、C 左下、D 右下；引脚距 6.5×3.7（外端距），推荐 PCB 焊盘 7.0/5.0（横）×4.5/3.0（竖）→ 焊盘 1.0×0.75、pitch 6.0×3.75。
- 封装 `jlc:SW-SMD_4P-L5.1-W5.1-P3.70-LS6.5-TL_H1.5`：pad1 左下、pad2 右下、pad3 左上、pad4 右上，1.0×0.75 —— **与数据手册 PCB layout 吻合**（6.5 为引脚外端距，中心距 6.5−0.5=6.0；3.7 vs 3.75 在 ±0.05 容差内）。
- 推演：0°/180° 贴装时 {pad1,2}=下对={C,D} 一极→KEY、{pad3,4}=上对={A,B} 一极→GND，**正确**（按下=KEY 拉低）。**90°/270° 贴装时下对焊盘落到左/右边=横跨两极**，每个内部极（接触片）同时接 KEY 与 GND → 未按时 KEY 恒低，按键恒按。
- 定性：原理图与封装均正确，属 **PCB 阶段硬约束**：SW1 相对本体极轴只能 0°/180° 摆放，须在 PCB 复核时专项检查（漏检症状像固件 bug，难定位）。

## P2（建议）

### P2-1  规格书 §3.3「总线脚绝对最大 ±40V」与 TI 手册不符

- TI SLOS346K（C12084）p6 Absolute Maximum：DC **−4V~+16V**；瞬态（via 100Ω）**±25V**；ESD HBM **±16kV**。
- 「±40V」查无出处；设计本身无误（U8 钳位+用户接受 CAN 待机超标），建议修正规格书文字以免误导 ESD 评估。

### P2-2  J7 符号名 ZX-XH2.54-4PZZ 与实测 2.50mm 间距名不符

- BOM 行 86 备注「封装实测 2.50mm」，封装 `jlc:CONN-TH_4P-P2.50_4PIN` 亦为 2.50。
- 功能无碍（孔距 2.50 正确）；建议统一符号名或 BOM 标注，避免采购/装配按 2.54 对件。

### P2-3  绿灯 LED3@330Ω 偏暗（算式留档，用户已定）

- 算式：(3.3V−VF)/330Ω，VF 2.6–3.1V → **0.6–2.1mA**（红灯 LED1/2@1kΩ：VF 1.5–2.6V → 0.7–1.8mA，中值 ~1.2mA，状态灯可接受）。
- 用户已决定 330Ω（BOM 行 90：1k 只有 0.2–0.7mA 太暗）。留档防后人误改；若要更亮可换高亮绿管或 220Ω（0.9–3.2mA）。

## 观察项（不计 P 级）

- O1  I2C_SCL/I2C_SDA/AFE_WAKE/AFE_ALERT 单节点全局标签（erc.json 根 sheet 5 条 isolated_pin_label 中 4 条）：对端 MP2797 在 02 页未画（WIP，预期）。AFE_WAKE 在 05 页无可见上拉（R_WAK 在 02 页），**02 页画完后须回核**。
- O2  BAT+ 全局标签仅 F11.1 一处（01 页范围，05 页不涉）。
- O3  红 LED ~0.7–1.8mA 偏暗属状态灯正常量级；LED1/2/3 极性已三层证据核过（数据手册 VF/阳极 + 封装丝印三角 + 网表阳极接 +3V3、阴极经限流电阻接 MCU 低有效脚），无接反。
- O4  J8.1=+3V3 带「下载器勿从 1 脚供电」注释；J8 引脚定义（3V3/SWDIO/SWCLK/GND/TX/RX）与 WCH-LinkE 标准 2×5 不同（无 RST、多 TX/RX），BOM 备注「接 WCH-LinkE」实际需转接线——规格书/BOM 建议注明。
- O5  BOM 行 69 备注「原 20pF C1554 频偏约 +34ppm」：34ppm 超出 12MHz 3225 晶振典型牵引范围（~±1ppm 量级），建议实测复核（不影响 33pF 选型：Cext=(33×33)/66+Cstray=16.5+(2–7)=**18.5–23.5pF**，跨 CL20pF，符合 Table 4-11（p46））。
- O6  封装 descr「YSX321SL 12MHZ 20PF **10PPM**」vs BOM「**±20ppm**」：C9002 两档均有，BOM 为准；P0-1 修库时一并修正。
- O7  SW1 电气参数 50mA/12V、100mΩ max、−30~+85℃，按键用途裕量充足；BOM 行 91 规格列为空（小瑕疵）。

## 覆盖清单（33 器件 + BOM 仅件）

| 位号 | 结论 |
|---|---|
| U6 CH32V203C8T6（C3001172，LQFP-48） | 已核对无问题：48 脚符号与 WCH 手册 p18（PDF p21）LQFP48 逐脚 100% 一致、功能映射全对；电源脚 9（1/9/24/36/48=VDD）/GND 8（8/23/35/47）全接，去耦 C50–C54 五颗 100nF+C55 4.7µF 完备；NRST 内部上拉 30–50kΩ（Table 4-22/Fig 4-7，p50-51）+C58 100nF；BOOT0 经 R50 10k 下拉=正常启动；HSE CL 计算合规（O5）；未用脚 20 个 NC 标志齐全 |
| Y1（C9002，3225） | 电气设计正确（33pF×2 跨 CL20pF）；**封装 P0-1**；descr 10PPM 出入 O6 |
| C56/C57（C1562，33pF C0G 0402） | 已核对无问题：值/算式/BOM 一致；O5 涉原 20pF 版 |
| C50–C54（5×C1525，100nF 0402） | 已核对无问题：+3V3–GND 去耦，BOM C1525 与 C58/C59 同料一致 |
| C55（C19666，4.7µF 0603） | 已核对无问题：MCU 储能 |
| C58（C1525，100nF） | 已核对无问题：NRST 滤波，符合 Fig 4-7 |
| C59（C1525，100nF） | 已核对无问题：U7 去耦 |
| R50（C25744，10k） | 已核对无问题：BOOT0 下拉 |
| R51/R52（C25741，100k） | 已核对无问题：PRECHG_EN/BAL_CLK 复位安全态=停（与 BOM 备注一致） |
| R53（C25744，10k） | 已核对无问题：D 脚低有效（HGSEMI C55259679 p3「LOW for dominant」；TI p3 Table 2 D=H/Open→Recessive）→ 复位 GPIO 浮空时 D 被拉高=总线隐性，BOM 备注成立（**此前 P1 候选「复位 dominant」作废**） |
| R56/R57（C17168，0Ω） | 已核对无问题：L2 DNP 时 CAN_H_X→CAN_H / CAN_L_X→CAN_L 直通 |
| R54（C17168，0Ω） | 已核对无问题：Rs=0Ω→GND=高速模式（TI p2/p3 Rs 三模），BOM 备注正确 |
| R55（C22787，120Ω 0603） | 已核对无问题：串 JP1 跳线可选终端（跳线帽合上=120Ω 跨 CANH–CANL）；符号叠放 **P1-2** |
| R58/R59（C11702，1k） | 已核对无问题：红 LED 限流 0.7–1.8mA；极性正确（O3） |
| R60（C25104，330Ω） | 已核对无问题：绿 LED 限流 0.6–2.1mA，用户已定（P2-3 留档）；极性正确（O3） |
| U7 SN65HVD230M（C55259679，SOIC-8） | 已核对无问题：1=D→CAN_TXD（R53 上拉）、2=GND、3=VCC（C59 去耦）、4=RXD→U6.32、5=NC（手册 NC 脚）、6=CANL→CAN_L_X、7=CANH→CAN_H_X、8=Rs→R54=0Ω→GND（高速）；TI C12084 引脚兼容，BOM 备注正确 |
| U8 PESD2CAN（C2687131，SOT-23-3） | 已核对无问题：1/2=CANH/CANL 对称钳位、3=GND；VRWM 24V/VC 41V@5A 覆盖 TI p6 绝对最大（DC −4~+16V、瞬态 ±25V@100Ω） |
| L2（C95572，DNP） | 电气连接正确（绕组对 TDK 引脚映射无误）；参数与规格书 §3.5 全对（51µH/2600Ω/200mA/80V/AEC-Q200）；**封装 P1-1** |
| J7（C7429634，XH 2.50mm 4P THT） | 已核对无问题：1=CAN_H、2=CAN_L、3/4=GND；符号名 2.54 与实测 2.50 出入 **P2-2** |
| J8（C492405，1×6 2.54 THT，DNP） | 已核对无问题：1=+3V3、2=SWDIO、3=SWCLK、4=GND、5=DBG_TX、6=DBG_RX，与 BOM 一致；O4（与 WCH-LinkE 标准定义不同需转接线） |
| JP1（C492401，1×2 2.54 THT） | 已核对无问题：1=CAN_TERM（→R55→CAN_H）、2=CAN_L，跳线可选方案 B 正确；叠放 **P1-2** |
| JP1-CAP（C100114，BOM 仅件） | 已核对无问题：机械件手工装+打胶，不入原理图，符合预期 |
| LED1/LED2（C84256，红 0805） | 已核对无问题：阳极→+3V3、阴极→R58/R59→U6.26/27（低有效驱动）；极性三层证据无接反（O3） |
| LED3（C2297，绿 0805） | 已核对无问题：阳极（pad1）→+3V3、阴极（pad2）→R60→U6.28；极性正确（O3）；P2-3 亮度留档 |
| SW1（C318884，SMD 5.1×5.1） | 0°/180° 正确（{1,2} 下对=一极、{3,4} 上对=另一极，电路图 A—B/C—D 证实）；封装与数据手册 PCB layout 吻合；**P1-4 旋转约束**；电气参数充足（O7） |

**网络层**：⓪ 断线/死头/悬空——05 页 20 个 `unconnected-` 全为预期 NC（U6 未用脚 19 个+U7.5），无意外；⓪b 同网多名——网表逐网重推无重名；跨页接口——全局标签无 RS485 残留（RS485 不画，用户决定）；ERC 5 条警告全定性（O1/O2，05 页自身 0 违规）。
**可读性**：PDF 第 6 页目视，除 P1-2 叠放外布局/标注清晰。
**LCSC 字段**：BOM MCU 段 34 行（行 67–91）LCSC 号、封装、规格与网表/封装文件全对上。

## 未核项（如实标注）

1. Y1 实物裁决：P0-1 修复方案 (a)/(b) 需实物 corner cut 或 JLC 官方封装佐证（本地数据手册与封装矛盾，二者必居其一错）。
2. AFE_WAKE 上拉（R_WAK 在 02 页）：02 页 MP2797 未画，画完后回核。
3. J8 与 WCH-LinkE 实插验证（引脚定义非标准，需转接线，O4）。
4. BOM「原 20pF +34ppm」实测复核（O5）。
5. 02/03 页与本页跨页网络（I2C、AFE_WAKE、AFE_ALERT、BAL_CLK、PRECHG_EN 对端）的最终一致性：待各页复核完成后汇总。
