colemandlut/MP2645A-BMS/design/05_mcu_comm-review-opus-r4.md

# 05_mcu_comm 第 4 轮复核（只看图面）（复核方 Claude Opus）

> 2026-09-27 13:32 JST
> 快照：`review/05-r4/`。只读不改工程，本文件是唯一的写入。
> 复跑：用 kicad-cli 10.0.6 对 `hardware/mp2645a-bms.kicad_sch` 重新做了 ERC 和网表导出。网表去掉日期行后与快照完全一致；hardware/ 下 04、05 两页的原理图文件与快照逐字节相同。

## 结论：**P0 = 0，P1 = 0，P2 = 8（全部沿用），05 页判定完成**

---

## 判据逐条核实

### ① 网表：本轮零差异 ✅

- **05 页**：`review/05-r3/netlist.xml` 对 `review/05-r4/netlist.xml`，去掉日期行后 **diff 为空**。
  - 这是整个根图的网表，所以器件、LCSC、封装、网络成员、pinfunction、网络类也都没变。
- **04 页**：把 `review/04-r6/netlist.xml` 和本快照中属于 `/辅助电源/` 的器件与网络逐条比对：
  - 器件与 LCSC 完全一致。
  - 04 页自己的网络（包括 C40–C45、D7、L1、R40–R42、U4、F11 的全部节点和 pinfunction）完全一致。
  - 唯一的差异在 `+3V3` 和 `GND`：本快照多出了 05 页的节点。04-r6 做快照时 05 页还没并入，这不是 04 页的变化。
- **ERC**（`--severity-all`）：05 页和 04 页都是 0。
  - 根图仍有 5 条跨页的 `isolated_pin_label`：BAT+、I2C_SDA、I2C_SCL、AFE_WAKE、AFE_ALERT。原因是 01–03 页还没画，与前几轮相同。
  - 没有 `lib_symbol_mismatch`。

### ② 嵌入符号与库一致 ✅

- 方法：用 kisexp 把图纸中嵌入的每个符号与 `hardware/lib/jlc/jlc.kicad_sym` 逐节点比对，比对时去掉 `jlc:` 前缀，数值按浮点归一化。
- 结果：
  - 05 页 20 个符号，差异 0。
  - 04 页 12 个符号，差异 0。
- 库的现状：117 个符号里 99 个带 `(pin_names (hide yes))`，与主代理说的一致。
- 嵌入副本确实带上了新属性：
  - LED（`FC-2012HRK-620D`、`0805G`）和 Y1（`X322512MSB4SI`）：只隐藏引脚名，脚号仍显示；
  - 两脚、且引脚名就是「1」「2」的电阻/电容：引脚名和脚号都隐藏；
  - U6、U7、J8（多于 4 脚）：不动。
- 引脚名本身都保留了。网表里仍有 `LED1.1(-_1)`、`LED1.2(+_2)`、`LED3.1(A_1)`、`LED3.2(K_2)`、`Y1.1(OSC1_1)`、`Y1.3(OSC2_3)`，极性语义没有丢。

### ③ 05 页图面（PDF 第 6 页，放大到 220–400dpi）✅

| 对象 | 看到的 | 结论 |
|---|---|---|
| LED1、LED2 | 本体内没有「+」或「−」字样。三角形尖和短竖线在左，左边是 1 脚（阴极）接 R58/R59，右边是 2 脚（阳极）接 +3V3 | ✅ 极性清楚，不误导 |
| LED3 | 本体内没有 A/K 字样。阴极在左，左边是 2 脚接 R60，右边是 1 脚接 +3V3 | ✅ |
| Y1 | 不再出现「GNDOSC2」「OSC1GND」；脚号 1–4 清楚；「12MHz」贴在本体下方 | ✅ 第 3 轮 P1-R3 关闭 |
| C56、C57 | 不再有「1」「2」压在电容极板和导线上；数值「33pF 50V」在本体外 | ✅ |
| 其它 R/C（R50–R60、C50–C59） | 本体内的「1 2」字样都消失了，图面更干净 | ✅ 第 3 轮 P2-R3b 关闭 |
| J7、U8、SW1、L2、JP1 | J7、U8、SW1、L2 只隐藏了引脚名，脚号还在，接线可读；JP1 的脚号也隐藏了，它是跳线、没有方向，不影响读图 | ✅ |
| 全页 | 目视没有新的文字↔文字、文字↔器件、文字↔导线重叠，也没有越界 | ✅ |

### ④ 04 页图面（PDF 第 5 页）没有变坏 ✅

| 对象 | 看到的 | 结论 |
|---|---|---|
| D7 SS210 | 本体内的 K/A 字样消失了；脚号 1（阴极竖线侧）接 SW_3V3，脚号 2 接 GND，续流二极管方向一目了然 | ✅ 老毛病已消失 |
| C45、C41–C44、C43 | 本体内的「1」「2」字样消失了 | ✅ 老毛病已消失 |
| C40（47µF/63V 电解） | 引脚名和脚号隐藏后，**符号图形里自带的「+」号和弧形负极板仍然可见**，极性清楚 | ✅ 有极性的电容没有因隐藏引脚名而丢掉极性标识 |
| R40、R41、R42、F11、L1、U4 | 位置和文字都与改前相同，没有新的重叠 | ✅ |

---

## P0（0 条）· P1（0 条）

无。

## P2（8 条，全部沿用，交用户定夺，不阻塞本页完成）

| 编号 | 内容（详见第 1–3 轮报告） | 状态 |
|---|---|---|
| P2-R3a | JP1 的数值「2P 排针」夹在「R55」和「120Ω 1%」两行字中间，容易看成 R55 的属性；「JP1」位号贴近 CAN_H 标签。建议把 JP1 的文字挪到它本体右侧 | 沿用 |
| P2-N3 | 布局时 JP1、R55 要紧贴 CAN 差分对的直通道，终端支路尽量短；跳线帽要核外壳净空 | 沿用 |
| P2-1 | HSE 激励功率：规格书把 CH32 手册的「HSE drive current」当成了晶体电流，这个前提不成立。负载电容改成 33pF 后，激励功率约升 2.4 倍。建议在 OSC_OUT 预留一颗 0Ω 串联电阻，样板实测后再定值 | 沿用 |
| P2-2 | R55 最坏功耗按 3² / 120 算是 75mW，85°C 降额后余量只有约 1.1 倍；规格书写的是「3 倍」 | 沿用 |
| P2-3 | U8 PESD2CAN 的工作电压 24V 低于 8S 满充 29.2V；钳位电压 41V 高于收发器总线脚的 ±40V | 沿用 |
| P2-4 | BOOT0 和 NRST 没有引出到 J8，J8 不能做串口 ISP 下载 | 沿用 |
| P2-5 | 规格书页码订正（Table 4-19 在 PDF p.49，不是 p.50）；固件注意事项要补一条：不要置 TIM1 的 CC1NE 和 BKE | 沿用 |
| P2-6 / P2-11 | 绿灯亮度离散；KiCad 不会把 CAN_H/CAN_L 识别成差分对 | 沿用（算两条） |

第 3 轮的 P2-R3b（R/C 的脚号画在本体内）已随本轮的库级修复关闭。

---

## 覆盖清单（第 4 轮）

| 对象 | 核对 | 结论 |
|---|---|---|
| 05 页全部 33 个器件与网络 | 网表与第 3 轮 diff | 0 差异 |
| 04 页器件与自有网络 | 与 04-r6 逐条比对 | 0 差异 |
| 两页嵌入符号（20 + 12 个） | 与库逐节点比对 | 0 差异 |
| 05 页图面：LED1–3、Y1、C56/C57、其余 R/C、J7、U8、SW1、L2、JP1 | 目视 | 无引脚名或脚号压在本体上，极性可辨 |
| 04 页图面：D7、C40–C45、R40–R42 | 目视 | 老毛病已消失；C40 的「+」仍可见 |
| 安全态、LCSC、封装 | 网表未变 | 沿用第 1 轮「已核对无问题」 |

## 给主代理

- 05 页满足「P0 = P1 = 0」，**判定完成**。P2 交给用户定夺。
- 本轮的库级修复对 01–03 页同样有效。那几页画完后，照同一判据核一遍即可：网表 diff、嵌入符号与库比对、目视引脚名。
- 建议写进知识库：`hide_small_pin_labels()` 这个做法，以及它的验收三件套（网表零差异、嵌入符号与库逐节点零差异、PDF 目视）。
- 本复核只读，没有写 obsidian-vault。
