colemandlut/MP2645A-BMS/design/05_mcu_comm-review-opus-r3.md

# 05_mcu_comm 第 3 轮独立复核（复核方 Claude Opus）

> 2026-09-27 13:29 JST
>
> - **快照**：`review/05-r3/`
> - **纪律**：同前。没有读画图方的报告和脚本，只读不改工程，本文件是唯一的写入。
> - **复跑**：用 kicad-cli 10.0.6 对 `hardware/mp2645a-bms.kicad_sch` 重新跑 ERC、导出网表。网表去掉日期行后，与快照完全一致。

## 结论

| 档 | 条数 |
|---|---|
| **P0** | **0** |
| **P1** | **1**（Y1、LED 的引脚名重新压回本体，第 1 轮 P1-3 的 b/c 两项回退） |
| **P2** | **9**（新增 2 条，沿用 7 条） |

第 2 轮的 P1-N1（R55 与 JP1 叠放）已关闭，但**本页还不能判定完成**。原因是 P2-N1 的修法恢复了引脚名，却没有用别的办法把它们挪开或隐藏，第 1 轮已经关闭的两处可读性问题又出现了。电气连接没有问题。

---

## 1. 本轮变更逐条核实

### 网表 diff（第 2 轮 → 第 3 轮，本页范围）

| 项 | 变化 | 结论 |
|---|---|---|
| JP1 的 Value | `终端跳线` → `2P 排针`，与 BOM 第 83 行一致 | ✅ 第 2 轮 P2-N2 关闭 |
| 三条 LED 阴极网络 | `Net-(LED1-Pad1)` → `Net-(LED1--)`，LED2 同理；`Net-(LED3-Pad2)` → `Net-(LED3-K)`。成员不变 | ✅ 符合预期 |
| pinfunction | LED1/2 恢复 `-`/`+`，LED3 恢复 `A`/`K`，Y1 恢复 `OSC1`/`GND`/`OSC2`/`GND`，C56/C57 恢复 `1`/`2` | ✅ 网表恢复了极性语义 |
| 其它 | 没有任何网络成员或器件变化 | ✅ |

- ERC（`--severity-all`）：本页 0 条，**没有 `lib_symbol_mismatch`**。根图仍有 5 条 `isolated_pin_label`（BAT+ 属于 04 页，另外 4 条是 AFE_ALERT、AFE_WAKE、I2C_SCL、I2C_SDA），原因是 01–03 页还空着，与前两轮相同。
- 需要注意：第 2 轮引脚名被清空时 ERC 同样没有报 mismatch，所以 **ERC 在这一项上不能当判据**。下面改用逐节点比对。

### 嵌入符号与库是否一致（自写比对）

- **方法**：用 kisexp 解析 `review/05-r3/05_mcu_comm.kicad_sch` 的 `lib_symbols`，与 `hardware/lib/jlc/jlc.kicad_sym` 逐节点比对。比对时去掉 `jlc:` 前缀，数值按浮点数归一化。
- **结果**：**20 个嵌入符号，全部与库一致，差异 0 个** ✅。第 2 轮 P2-N1 关闭。

### 第 2 轮 P1-N1（R55 与 JP1 叠放）：**已关闭**

- 在 PDF 第 6 页放大到 500dpi 看：JP1 已移到 R55 右侧，两个本体不再重叠。
- 连线清楚：R55.1 经 CAN_TERM 到 JP1.1，JP1.2 在节点处并入 CAN_L。
- 网表确认：`CAN_TERM` = {R55.1, JP1.1}，`CAN_L` 包含 JP1.2。

---

## P0（0 条）

无。

## P1（1 条）

### P1-R3 Y1 和 LED 的引脚名又压回本体里，LED 的 `+` 画在阴极一侧（第 1 轮 P1-3 的 b/c 回退）

在 PDF 第 6 页放大到 450dpi 看：

| 位号 | 现象 | 为什么不行 |
|---|---|---|
| Y1 | 引脚名又粘成「GNDOSC2」「OSC1GND」，压在本体上（第 1 轮 P1-3b） | 规则 00 ③：文字↔元件重叠一律不允许 |
| LED1、LED2 | 引脚名 `+` 画在三角形内部、**靠阴极竖线的左侧**（第 1 轮 P1-3c） | 读图的人会以为左边是 `+`。实际左侧 1 脚是阴极 `−`，右侧 2 脚才是 `+`（网表 `LED1.1(-_1)` → R58，`LED1.2(+_2)` → +3V3）。**极性件的图面误导** |
| LED3 | 引脚名 `A` 和 `K` 叠在三角形内 | 同上：文字重叠，而且名字的位置与引脚方向不对应 |

- **原因**：这几个库符号（EasyEDA 转换出来的）没有 `pin_names` 设置，KiCad 按默认偏移把引脚名画在本体内侧。挪位号、数值这些字段的位置，**挪不动引脚名**，所以「靠字段位置规避」这个修法对引脚名无效。
- **改法**（同时满足三点：库与图一致、网表带引脚名、图上不重叠）：
  1. 在**工程库** `hardware/lib/jlc/jlc.kicad_sym` 里，给 `FC-2012HRK-620D`、`0805G`、`X322512MSB4SI` 三个符号加 `(pin_names (hide yes))`。
     - 引脚名本身保留，所以网表仍带 `+`、`−`、`A`、`K`、`OSC1`、`OSC2`。
     - 只改显示属性，不改引脚和图形。
     - 在取库记录 `fetch_report.md` 里注一笔，符合规则 0e「工程级库、不改全局库」。
  2. 在原理图里执行「与库符号同步」，嵌入副本随之更新，库与图继续保持一致。
  3. 重跑 ERC、网表 diff（应为 0 变化）和上面的逐节点比对，再出 PDF 目视确认。
- **定级**：电气连接完全正确。但第 1 轮已把这一项定为 P1，本轮属于回退，而且涉及极性件的图面误导，所以维持 P1。

---

## P2（9 条）

### 新增

**P2-R3a JP1 的数值文字夹在 R55 的两个字段中间，JP1 位号贴着 CAN_H 标签**
- 「2P 排针」落在「R55」和「120Ω 1%」之间，一眼看去像是 R55 的第二行属性。
- 「JP1」位号的上沿几乎碰到 `CAN_H` 全局标签的外框。
- 不算重叠，但读图容易看错。建议把 JP1 的位号和数值移到 JP1 本体的右侧。

**P2-R3b R、C 符号的脚号「1」「2」画在本体内（全工程通病）**
- 这批 EasyEDA 转出的电阻、电容符号（例如 `0402WGF…`、`CL05B…`、`0402CG330J500NT`）都把引脚名「1」「2」画在本体矩形内。
- 在 C56、C57 上还与本体线条交叠。
- 与 P1-R3 同一个根因。建议借同一次改库，对 R、C 类符号统一加 `(pin_names (hide yes))`，其它页一起受益。

### 沿用（本轮图纸和规格书都没有改到这些点）

| 编号 | 内容（详见第 1、2 轮报告） | 状态 |
|---|---|---|
| P2-N3 | JP1、R55 布局时要紧贴 CAN 差分对的直通道，终端支路尽量短；跳线帽要核外壳净空 | 沿用 |
| P2-1 | 晶振激励功率：规格书把「HSE drive current」当成晶体电流，前提不成立；33pF 使激励功率约升 2.4 倍，建议在 OSC_OUT 预留 0Ω 串联电阻 | 沿用 |
| P2-2 | R55 最坏功耗 75mW，85°C 下余量约 1.1 倍；规格书仍写「余量 3 倍」 | 沿用 |
| P2-3 | U8 工作电压 24V 低于 8S 满充 29.2V；钳位 41V 高于收发器 ±40V | 沿用 |
| P2-4 | BOOT0、NRST 没有引出，J8 做不了串口 ISP | 沿用 |
| P2-5 | 规格书页码订正（Table 4-19 在 PDF p.49，不是 p.50）；补 TIM1 的 CC1NE/BKE 固件注意 | 沿用 |
| P2-6 / P2-11 | 绿灯亮度离散；KiCad 不会把 CAN_H/CAN_L 识别成差分对 | 沿用（两条） |

---

## 覆盖清单（第 3 轮）

| 对象 | 本轮核对 | 结论 |
|---|---|---|
| 全页连通性 | ERC、网表与第 2 轮 diff | 无问题（只有预期的网络改名和 JP1 数值） |
| 20 个嵌入符号 | 与 `jlc.kicad_sym` 逐节点比对 | 全部一致 |
| JP1 / R55 | 叠放是否消除、拓扑、Value | 叠放已消除；P2-R3a |
| LED1–3 | 网表极性、图面引脚名 | 网表正确；**P1-R3** |
| Y1 / C56 / C57 | 网表、图面引脚名 | 网表正确；**P1-R3**，P2-R3b |
| 其余器件与安全态 | 网络未变 | 沿用第 1 轮「已核对无问题」 |

## 给主代理

- **05 页还不能判定完成**：P1 = 1。修完 P1-R3 后跑一轮只看图面的第 4 轮复核即可。第 4 轮的判据：
  - 网表 diff 为 0；
  - 嵌入符号与库比对差异为 0；
  - PDF 上 LED 和 Y1 没有引脚名压在本体上。
- 建议写入知识库的经验：**引脚名的重叠只能在符号的 `pin_names` 上解决。给工程库的符号加 `hide`，再与库同步；不要清空引脚名，也指望不上挪字段。**
- 本复核只读，没有写 obsidian-vault。
