colemandlut/MP2645A-BMS/design/05_mcu_comm-draw-report.md

# 05_mcu_comm（MCU 与通讯）画图报告 · 第 3 轮（含第 1、2 轮）

- 生成脚本：`hardware/gen/gen_05_mcu_comm.py`（幂等，UUID 用 `uuid.uuid5` 派生，跑两次 md5 相同）
- 自检脚本：`hardware/gen/check_05_layout.py`（几何检查 1–8，直接解析生成的 `.kicad_sch`；7 = 符号本体/字段两两不相交，8 = 出 PDF 用 pymupdf 读真实文字盒）
- **第 3 轮改动只涉及上面两个文件 + `hardware/05_mcu_comm.kicad_sch` 产物 + 本报告**，库 / BOM / docs / 根图 / 其它子图一个字未动（任务书 §0 纪律）

---

## 第 3 轮变更（2026-09-27）

### 0. 改动前先验幂等（任务书要求）

| 时刻 | md5 | 字节 | 说明 |
|---|---|---|---|
| 改前（基线，连跑两次） | `61b5aba59189b24463741d270b088539` | 164185 | 与任务书给的基线**一致** ✅ 幂等 ✅ |
| 改后（连跑三次） | `2697abea03f53aeb4afe7b35c33f2186` | 164184 | 三次完全相同 ✅ 幂等 ✅ |

### 1. 本轮改动清单

| # | 任务书条目 | 处理 | 结果 |
|---|---|---|---|
| **P1（新）** | R55 与 JP1 符号叠放，JP1 本体压住 R55 的位号与数值 | JP1 沿 CAN_TERM 水平走线（y=143.51）由 `(347.98,139.70)` 右移到 **`(365.76,139.70)`**，朝向/旋转/封装/DNP 均不变；位移 **17.78 mm**（要求 ≥10 mm）。R55 本体右沿 343.92 ↔ JP1 本体左沿 361.95，**净空 18.03 mm**；R55 的数值「120Ω 1%」右端 353.31 ↔ JP1 数值「2P 排针」左端 354.31，**净空 1.00 mm**。JP1 的位号居中放在本体上沿与 CAN_H 走线之间（y=134.62，CAN_H 在 y=133.35 上方 1.27 mm 处经过但不压字），数值左对齐放在本体左侧走道 | ✅ 无重叠，串联关系 CAN_H → R55 → CAN_TERM → JP1 → CAN_L 一目了然 |
| **P2-N1** | 恢复嵌入符号与库完全一致（第 2 轮清空引脚名是错的做法） | 4 个被改动的符号（`FC-2012HRK-620D`、`0805G`、`X322512MSB4SI`、`0402CG330J500NT`）连同全部 20 个嵌入符号，**除 `jlc:` 库名前缀外与 `hardware/lib/jlc/jlc.kicad_sym` 逐字一致**（脚本化比对：不一致 0 个）；引脚名全部回来了：LED `-`/`+`、LED3 `A`/`K`、Y1 `OSC1`/`GND`/`OSC2`/`GND`、C56/C57 `1`/`2`、JP1 `1`/`2`。**没有用 `(pin_names (hide yes))`**——库符号本身没写这个开关，写了就又和库不一致 | ✅ 网表 `pinfunction` 恢复（LED1.1=`-_1`、LED3.2=`K_2`、Y1.3=`OSC2_3`…），极性语义回来了 |
| | 引脚名造成的重叠改用器件朝向/位置/字段位置规避 | LED1–3 值已在本体外、Y1 值在本体下方、C56 值在极板下方、C57 值移到 Y1.2 的 GND 标签右侧空带（见 §1.1） | ✅ 检查 7/8 全过 |
| **P2-N2** | JP1 的 Value 与 BOM 不一致 | Value「终端跳线」→ **「2P 排针」**，与 `docs/02-BOM.csv` 第 83 行一致；页头说明文字仍保留「JP1 插帽接入 120Ω 终端，拔帽不用」 | ✅ |

### 1.1 顺手修掉的一个自己引入的缺陷（检查 8 之外，靠目视发现）

按 P2-N1 把 9 颗竖放电容的 Value 从 y+2.54 下移到 y+3.81 后（避开本体内伸出的极板），**C57 的数值「33pF 50V」压住了 Y1.2 的 `GND` 全局标签文字**：
数值文字盒 y 209.87–211.90 ↔ GND 标签文字 y 211.23–213.26，重叠 0.67 mm（300 dpi 图上「33」被标签框盖住）。
C57 正下方的空带只有 2.19 mm，放不下 2.03 mm 的字，所以改为**右移**到 GND 标签文字右端（122.11）之外：
`("C57", 120.65, 201.93)` + `("Value", 123.50, 210.82)`，距标签文字 1.39 mm、距本页导线 2.9 mm。已渲染复核（§2 第 5 项）。

> **这是第 2 轮 6 项自检的一个漏洞**：第 2 轮只比「字段 ↔ 自己的本体」和「字段 ↔ 字段」，**画在纸上的标签文字（全局标签/局部标签/说明文字）没有任何检查看着**。
> 本轮因此把检查 8 加了一条 **`[8d]`：每个可见字段的真实渲染文字盒，与任何一段「不属于本符号」的渲染文字都不许相交**（本符号本体范围内的文字——即库自带、画在本体内的引脚名/脚号——豁免，属符号库 quirk）。
> 负例验证：把 C57 的值放回旧位置，`[8d]` 会准确报出上面那 0.67 mm 的重叠（详见 §2 第 1 项）。

### 2. 验收自检（第 1 轮任务书 §4 全部项 + 第 3 轮新增项）

| # | 检查 | 命令 | 结果 |
|---|---|---|---|
| 1 | **符号本体/字段两两不相交（第 3 轮新增）** | `python3 hardware/gen/check_05_layout.py` | ✅ **PASS，检查 1–8 全过，0 条**。元数据：导线 113 段 / junction 7 / 实例 33 / 引脚 131 / 文字 100 处 / 引脚名 131 个 / 图元盒 230 个；渲染复核：PDF 文字串 390 段、字段认领 66/66 个 |
| | ↑ 检查 7（本体↔本体，含字段文字与引脚名） | 同上 | ✅ 0 条。**负例验证**：对第 2 轮产物跑同一脚本 → **17 条 FAIL**，其中 `[7] JP1 的本体 (344.17,135.89,351.79,140.97) 与 R55 的字段Reference/Value 相交`、`[8b] JP1 Value「终端跳线」与 R55 Value「120Ω 1%」相交` —— 正是本轮要消灭的 P1，说明新检查确实抓得住这一类 |
| | ↑ 检查 8d（字段文字 ↔ 非本符号文字） | 同上 | ✅ 0 条。**负例验证**：把 C57 值放回旧位置 → **1 条 FAIL** `[8d] C57 字段「Value」渲染文字「33pF50V」(120.634,209.872,129.765,211.899) 与另一段渲染文字「GND」(118.242,211.233,122.112,213.26) 相交` |
| 2 | ERC（`--severity-all`，根图） | `kicad-cli sch erc --format json --severity-all -o /tmp/erc05.json hardware/mp2645a-bms.kicad_sch` | ✅ **error 0 条 / warning 5 条**，5 条全是跨页预期的 `isolated_pin_label`（BAT+ 属 01 页；I2C_SCL/I2C_SDA/AFE_ALERT/AFE_WAKE 属 02 页，两页都还没画）→ **05 页 0 条** |
| 3 | 网表 Footprint/LCSC | `kicad-cli sch export netlist --format kicadxml` | ✅ 33 器件（本页）Footprint/LCSC **全部非空、无 `Pad??`**，无两脚件一端悬空/自短路；`pinfunction` 已恢复 |
| 4 | `sch_conn.py`（仓库技能脚本） | `python3 skills/pcb-workflow/scripts/sch_conn.py hardware/mp2645a-bms.kicad_sch` | ✅ **P0 = 0**（全脚悬空 0 / 两端悬空 0 / 自短路 0）；P1 = 10（= 5 条 isolated_pin_label + 5 条同名单脚网络，均跨页预期，与第 2 轮相同）；③ 本页 图元 252 / 导线 113 / **同网多名 0 / 死头 0 / 孤立引脚 0**、图上网络名 34 个找不到的 0 个 |
| 5 | PDF 渲 PNG 目视（≥200 dpi） | 150 dpi 全页 + 300 dpi 分区（CAN 链 / 晶振组 / 去耦列） | ✅ CAN 链：R55「120Ω 1%」与 JP1「2P 排针」各自清晰、不压本体；晶振组：C57「33pF 50V」已在 GND 标签右侧、不再被盖；去耦列：6 个值全部落在极板下方空带 |
| 6 | 幂等 | 连跑 3 次 `md5sum` | ✅ 均为 `2697abea03f53aeb4afe7b35c33f2186` |
| 7 | 回归测试 | `python3 -m unittest discover -s tests`、`make -C firmware test` | ✅ **21/21**、**38/38 通过** |

### 3. 网表差异（第 2 轮 vs 第 3 轮，`位号.脚 → 网络` 逐条对比）

- 网络数量 51 ↔ 51、节点数 131 ↔ 131；**新增网络 0 / 删除网络 0**。
- **JP1 挪位只带来坐标变化，连通性一字未改** ✅（`位号.脚 → 网络` 差异条数 = 6，全部来自下面这一条）。
- 唯一差异 = 任务书允许的 **3 条 LED 阴极网络改名**（成员集合完全相同）：

| 第 2 轮（引脚名被清空时的自动名） | 第 3 轮（引脚名恢复后的自动名） | 成员（两边相同） |
|---|---|---|
| `Net-(LED1-Pad1)` | `Net-(LED1--)` | {LED1.1, R58.2} |
| `Net-(LED2-Pad1)` | `Net-(LED2--)` | {LED2.1, R59.2} |
| `Net-(LED3-Pad2)` | `Net-(LED3-K)` | {LED3.2, R60.2} |

- `CAN_TERM` = {JP1.1, R55.1}、`CAN_L` 含 JP1.2、`CAN_H` 含 R55.2 —— 与第 2 轮完全一致。

### 4. 符号库 quirk（按任务书要求记录，**不改符号**）

| 符号 | quirk | 本图处理 |
|---|---|---|
| `PZ254V-11-02P`（JP1，C492401） | 引脚名 `1`/`2` 画在本体矩形内 | 本体左侧留走道放数值；引脚名压本体属库自身画法，无法靠挪器件规避 |
| `0402CG330J500NT`（C56/C57，C1562） | 引脚名 `1`/`2` 画在本体内；极板伸到局部 y=±2.03，Value 放 y+2.54 必压极板 | 值下移到 y+3.81（C56）或右移到标签外（C57） |
| `X322512MSB4SI`（Y1，C9002） | 4 个引脚名 `GND`/`OSC2`/`OSC1`/`GND` 沿本体上下边内侧排布，渲染后「GND」「OSC2」相邻读起来像 `GNDOSC2` | 值「12MHz」放本体下方；引脚名属库自身画法。**根治建议**：取库脚本 `tools/fetch_jlc_parts.py` 归一化时给二脚无源件加 `(pin_names (hide yes))`——注意是设隐藏开关，**不是清空引脚名** |
| `FC-2012HRK-620D` / `0805G`（LED1–3） | 引脚名 `-`/`+`、`A`/`K` 画在本体内 | 值移到本体外；极性靠引脚名 + 脚号 + 封装丝印三重可辨 |

> 第 2 轮为规避这些重叠而清空引脚名的做法**已全部撤销**，本表改回「记录 quirk、不改符号」的口径。

---
- 产物：`hardware/05_mcu_comm.kicad_sch`
- 依据：`design/05_mcu_comm-spec.md`（Opus，逐条照画）+ 用户 2026-09-27 决定 U-1…U-9、L2 + `design/05_mcu_comm-task-draw-r2.md`（第 2 轮）
- 参考样板：`hardware/gen/gen_04_power_supply.py` / `check_04_layout.py`（04 页 6 轮踩坑全部沿用）

---

## 第 2 轮变更（2026-09-27）

### 0. 脚本与产物同步（任务书 §0）
重跑 `gen_05_mcu_comm.py`，产物 **md5 = `61b5aba59189b24463741d270b088539`（164185 字节）**，跑两次完全一致（幂等 ✅）。
第 1 轮冻结文件 `review/05-r1/05_mcu_comm.kicad_sch` 实测 **md5 = `ee2841cbe1d97c2531a0e64cea2090fa`（159251 字节）**——与任务书 §0 里写的预期 md5（`6cfdbb…`）不符，以冻结文件实测为准。
两者差异 = 本轮全部改动（见下表），脚本为准（脚本已含第 2 轮改动，产物为其幂等输出）。

### 1. 本轮改动清单（依据任务书 §1）
| # | 项 | 处理 |
|---|---|---|
| P1-1 | CAN 终端改跳线可选 | R55 120Ω 串 **JP1**（`jlc:PZ254V-11-02P`，封装 `jlc:HDR-TH_2P-P2.54-V-M`，LCSC **C492401**，值「终端跳线」）；新增本页网络 **`CAN_TERM`**：CAN_H → R55 → CAN_TERM → JP1 → CAN_L。说明文字改「JP1 插帽接入 120Ω 终端，拔帽不用」 |
| P1-3a | BOOT0 标签横穿 I2C_SDA 连线 | 标签挪开，不再压线 |
| P1-3b | Y1 引脚名「GNDOSC2」「OSC1GND」粘连 | Y1（X322512MSB4SI）引脚名隐藏（`(name …)""`），不再粘连 |
| P1-3c | LED 引脚名画在本体内、值压本体 | LED1/LED2（FC-2012HRK-620D）、LED3（0805G）**引脚名隐藏**（符号自带、无法挪位）；值文字挪到本体外。极性仍可无歧义确认：阳极→+3V3（LED1.2/LED2.2/LED3.1），阴极→R58–R60→MCU `LEDx_K` 脚，配合封装阴极丝印，不会误导 |
| P2 | 可读性小项 | 「12MHz」值文字靠近 Y1；CAN_RXD 标签下拉 1 格（2.54mm）与 +3V3 拉开；「L2 与 R56/R57 二选一」去重（仅 1 处）；加注释「I2C 上拉 R_I2C1/2 在 02 页」；L2 Value 去「(DNP)」（DNP 仅由 `(dnp yes)` 属性表示） |

> 引脚名隐藏的副作用：KiCad 对无名引脚按焊盘号自动生成网络名，导致 3 个 LED 阴极短桩网络改名（见 §3 网表差异，纯名称、拓扑不变）。

### 2. 验收自检（任务书 §2，6 项全部重跑）
| # | 检查 | 结果 |
|---|---|---|
| 1 | `check_05_layout.py` 几何 1–6 | ✅ **PASS 全部 6 项**（导线 113 / junction 7 / 实例 33 / 引脚 131 / 文字 100 / 引脚名 117） |
| 2 | ERC `--severity-all` | ✅ **05 页 0 条**；全图 5 条 `isolated_pin_label` 均跨页预期（BAT+/I2C_SCL/I2C_SDA/AFE_ALERT/AFE_WAKE） |
| 3 | 网表 `kicadxml` | ✅ 46 器件（本页 33 + 04 页 13）Footprint/LCSC 全部非空、无 `Pad??`、无两脚件一端悬空/自短路；**JP1 存在**、Footprint/LCSC 非空；`CAN_TERM` 只连 R55 与 JP1 各一脚；**R55 不再跨接 CAN_H/CAN_L** |
| 4 | `sch_conn.py` | ✅ **P0 = 0**、同网多名 = 0、死头 = 0、孤立引脚 = 0、网表找不到 = 0；P1 = 10（5 条 isolated_pin_label + 5 条同名单脚网络，均跨页预期） |
| 5 | PDF→PNG（200dpi）目视 | ✅ 左/中/右分区清晰，差分对 CAN_H/CAN_L 平行直通道，无穿本体/压线 |
| 6 | 幂等 | ✅ 跑两次 md5 相同（`61b5aba59189b24463741d270b088539`） |

### 3. 网表差异（R1 冻结 vs R2，`(位号.脚) → 网络` 节点集合对比）
- **拓扑变更（本轮预期，仅 2 处）**：
  - 新增网络 `CAN_TERM` = {JP1.1, R55.1}
  - `CAN_L` 成员 {J7.2, L2.3, R55.1, R57.2, U8.2} → {J7.2, **JP1.2**, L2.3, R57.2, U8.2}（R55.1 移入 CAN_TERM，JP1.2 加入）
  - `CAN_H` 不变
- **网络名变更（非电气，引脚名隐藏副作用，节点集合完全相同）**：3 个 LED 阴极短桩网络
  `Net-(LED1--)`→`Net-(LED1-Pad1)`、`Net-(LED2--)`→`Net-(LED2-Pad1)`、`Net-(LED3-K)`→`Net-(LED3-Pad2)`
  （LED1.1↔R58.2、LED2.1↔R59.2、LED3.2↔R60.2 的连接关系一字未变，仅自动命名变化）
- **器件值**：无任何变化。

---

## 0. 本页概览

33 器件、131 脚、113 段导线、7 个 junction、19 个 U6 NC 标志 + 1 个 U7.5 NC 标志。
版面（spec §9）：左 = 电源/时钟/复位（去耦列 C50–C55 + 偏置列 C58/R50–R52 + 晶振组 Y1/C56/C57）；
中 = U6 CH32V203C8T6；右 = CAN 链（J7→U8→R55→JP1→R56/R57‖L2→U7，差分对 CAN_H/CAN_L 平行）+ U7 外围 R53/C59/R54 + J8 调试口 + LED1–3/R58–R60 + SW1。

**用户决定全部落实**：RS485 不画（PA2/PA3/PA4 放 NC）；J8 1×6 2.54mm DNP（`(dnp yes)`，针序 3V3/SWDIO/SWCLK/GND/TX/RX）；
R55 120Ω 串 JP1 跳线做终端（插帽接入/拔帽不用）；SW1=用户键（PB12，KEY）；CAN 待机超标接受（不加断电 MOS）；
晶振负载 33pF C1562（C56/C57）；J7 针序 1 CAN_H / 2 CAN_L / 3 GND / 4 GND；绿灯 330Ω C25104（R60）；PWR_EN 删除；
L2 共模电感 C95572 DNP + R56/R57 0Ω 旁路默认贴。

---

## 1. 位号对照（新位号 ↔ BOM 旧位号）

| BOM 旧位号 | 本图新位号 | 器件（LCSC） | 值 | 封装（取库符号值） |
|---|---|---|---|---|
| U6 | U6 | CH32V203C8T6（C3001172） | CH32V203C8T6 | jlc:LQFP-48_L7.0-W7.0-P0.50-LS9.0-BL |
| Y1 | Y1 | X322512MSB4SI（C9002） | 12MHz | jlc:CRYSTAL-SMD_4P-L3.2-W2.5-BL |
| C_Y1/C_Y2 | **C56/C57** | 0402CG330J500NT（**C1562**，原 C1554 20pF） | **33pF 50V** | jlc:C0402 |
| C_DEC1–5 | **C50–C54** | CL05B104KO5NNNC（C1525） | 100nF 16V | jlc:C0402 |
| C_BULK | **C55** | CL10A475KO8NNNC（C19666） | 4.7µF 16V | jlc:C0603 |
| （新增） | **C58** | CL05B104KO5NNNC（C1525） | 100nF 16V | jlc:C0402 |
| C_CAN | **C59** | CL05B104KO5NNNC（C1525） | 100nF 16V | jlc:C0402 |
| R_BOOT | **R50** | 0402WGF1002TCE（C25744） | 10k 1% | jlc:R0402 |
| （新增） | **R51** | 0402WGF1003TCE（C25741） | 100k 1% | jlc:R0402 |
| （新增） | **R52** | 0402WGF1003TCE（C25741） | 100k 1% | jlc:R0402 |
| （新增） | **R53** | 0402WGF1002TCE（C25744） | 10k 1% | jlc:R0402 |
| R_RS | **R54** | 0402WGF0000TCE（C17168） | 0Ω | jlc:R0402 |
| R_T | **R55** | 0603WAF1200T5E（C22787） | 120Ω 1% | jlc:R0603 |
| （新增） | **R56/R57** | 0402WGF0000TCE（C17168） | 0Ω | jlc:R0402 |
| R_LED_A/B | **R58/R59** | 0402WGF1001TCE（C11702） | 1k 1% | jlc:R0402 |
| R_LED_C | **R60** | 0402WGF3300TCE（**C25104**，原 1k C11702） | **330Ω 1%** | jlc:R0402 |
| U7 | U7 | SN65HVD230M_TR-HG（C55259679） | SN65HVD230M | jlc:SOIC-8_L5.0-W4.0-P1.27-LS6.0-BL |
| U8 | U8 | PESD2CAN_C2687131（C2687131） | PESD2CAN | jlc:SOT-23-3_L2.9-W1.3-P1.90-LS2.4-BR |
| （新增） | **L2**（DNP） | ACT1210-510-2P-TL00（**C95572**） | 51µH CMC | jlc:FILTER-SMD_4P-L3.2-W2.5-BL_ACT1210 |
| J7 | J7 | ZX-XH2.54-4PZZ（C7429634） | XH 2.50mm 4P | jlc:CONN-TH_4P-P2.50_4PIN |
| （新增，取代 SWD 2×5 1.27） | **J8**（DNP） | PZ254V-11-06P（**C492405**） | 1×6 2.54mm | jlc:HDR-TH_6P-P2.54-V-M |
| LED1/LED2 | LED1/LED2 | FC-2012HRK-620D（C84256） | 红 0805 | jlc:LED0805-RD |
| LED3 | LED3 | 0805G（C2297） | 绿 0805 | jlc:LED0805-R-RD |
| SW1 | SW1 | TS-1187A-B-A-B（C318884） | 按键 | jlc:SW-SMD_4P-L5.1-W5.1-P3.70-LS6.5-TL_H1.5 |

删除：JP1、U9、D8、C60、R61–R63（RS485/跳线方案件，用户 U-1/U-3 决定）。PWR_EN 删除（U-9）。

---

## 2. 每颗 IC 外围件点名（spec §7，逐件核对）

### 2.1 U6 CH32V203C8T6（CH32 手册 Fig 4-1/4-5/4-7）

| 手册要求 | 本设计对应 | 状态 |
|---|---|---|
| VDDx/VSSx 各 0.1µF | C52（24 脚）、C53（36 脚）、C54（48 脚） | ✅ 各 100nF |
| VDDA–VSSA 0.1µF | C51（8/9 脚） | ✅ |
| VBAT 接 1.8–3.6V | 接 +3V3 + C50 100nF（1 脚） | ✅ |
| HSE 晶振 + CL1=CL2 | Y1 12MHz + C56/C57 33pF（§2.4 核算） | ✅ |
| LSE | 不用，PC14/15 放 NC | ✅ |
| NRST 0.1µF 到地 | C58 100nF | ✅ |
| BOOT0 下拉 | R50 10k | ✅ |
| 板级储能 | C55 4.7µF（+3V3 轨） | ✅ |

### 2.2 U7 SN65HVD230M（HVD 手册 p.19/20 Figure 20）

| Fig 20 件 | 本设计 | 状态 |
|---|---|---|
| R1（D 上拉/偏置） | R53 10k 上拉到 +3V3；串阻不加 | ✅ |
| C2/C3（VCC 旁路+储能） | C59 100nF 贴脚 + C55 4.7µF 共用 | ✅ |
| R3（Rs 模式） | R54 0Ω 到地（高速）；C4 不加 | ✅ |
| R4（Vref） | Vref 悬空 + NC 标志（p.19 允许） | ✅ |
| R5/R6+C6（分裂终端） | 单电阻 R55 120Ω（用户已定） | ✅ |
| C5/C7（总线对地） | 不加（有理由，见 spec §7.2） | 不采用 |
| D1（TVS 紧靠连接器） | U8 PESD2CAN 紧靠 J7 | ✅ |
| J1 连接器 | J7 | ✅ |

### 2.3 U8 PESD2CAN：1→CAN_H、2→CAN_L、3→GND，无其它外围 ✅

### 2.4 Y1：1/3 接 OSC_IN/OUT，2/4 接 GND ✅

### 2.5 L2（DNP）：绕组 1–4 串 CAN_H、2–3 串 CAN_L，与 R56/R57 二选一 ✅

---

## 3. 48 脚逐脚核对（spec §1.3，网表回读）

| 脚 | 名称 | 网络 | 处理 | 核对 |
|---|---|---|---|---|
| 1 | VBAT | +3V3 | C50 100nF 就近 | ✅ 网表 +3V3 含 U6.1 |
| 2 | PC13/TAMPER_RTC | — | NC | ✅ no_connect |
| 3 | PC14/OSC32IN | — | NC | ✅ |
| 4 | PC15/OSC32OUT | — | NC | ✅ |
| 5 | OSC_IN/PD0 | HSE_IN | Y1.1 + C56 | ✅ HSE_IN={U6.5,C56.2,Y1.1} |
| 6 | OSC_OUT/PD1 | HSE_OUT | Y1.3 + C57 | ✅ HSE_OUT={U6.6,C57.1,Y1.3} |
| 7 | NRST | NRST | C58 100nF | ✅ NRST={U6.7,C58.1} |
| 8 | VSSA | GND | — | ✅ |
| 9 | VDDA | +3V3 | C51 100nF | ✅ |
| 10 | PA0/WKUP/ADC0 | — | NC | ✅ |
| 11 | PA1/ADC1 | PRECHG_EN | R51 100k 下拉 | ✅ PRECHG_EN={U6.11,R51.1} |
| 12 | PA2/ADC2 | — | NC（RS485 不画） | ✅ |
| 13 | PA3/ADC3 | — | NC | ✅ |
| 14 | PA4/ADC4/DAC0 | — | NC | ✅ |
| 15–17 | PA5/PA6/PA7 | — | NC | ✅ |
| 18 | PB0/ADC8 | — | NC | ✅ |
| 19 | PB1/ADC9 | — | NC | ✅ |
| 20 | PB2/BOOT1 | — | NC | ✅ |
| 21 | PB10 | — | NC | ✅ |
| 22 | PB11 | — | NC | ✅ |
| 23 | VSS_1 | GND | — | ✅ |
| 24 | VDD_VIO_1 | +3V3 | C52 100nF | ✅ |
| 25 | PB12 | KEY | SW1（用户键） | ✅ KEY={U6.25,SW1.1,SW1.2} |
| 26 | PB13 | LED1_K | R58 1k → LED1 阴极 | ✅ |
| 27 | PB14 | LED2_K | R59 1k → LED2 阴极 | ✅ |
| 28 | PB15 | LED3_K | R60 330Ω → LED3 阴极 | ✅ |
| 29 | PA8 | BAL_CLK | R52 100k 下拉 | ✅ BAL_CLK={U6.29,R52.1} |
| 30 | PA9 | DBG_TX | J8.5（DNP） | ✅ |
| 31 | PA10 | DBG_RX | J8.6 | ✅ |
| 32 | PA11 | CAN_RXD | U7.4 | ✅ |
| 33 | PA12 | CAN_TXD | U7.1 + R53 10k 上拉 | ✅ CAN_TXD={U6.33,U7.1,R53.1} |
| 34 | PA13/SWDIO | SWDIO | J8.2 | ✅ |
| 35 | VSS_2 | GND | — | ✅ |
| 36 | VDD_2 | +3V3 | C53 100nF | ✅ |
| 37 | PA14/SWCLK | SWCLK | J8.3 | ✅ |
| 38 | PA15 | — | NC | ✅ |
| 39 | PB3 | — | NC | ✅ |
| 40 | PB4 | AFE_ALERT | 直连（02 页 R_ALT） | ✅（单脚，跨页预期） |
| 41 | PB5 | AFE_WAKE | 直连开漏（02 页 R_WAK） | ✅（跨页预期） |
| 42 | PB6 | I2C_SCL | 直连（02 页上拉） | ✅（跨页预期） |
| 43 | PB7 | I2C_SDA | 直连 | ✅（跨页预期） |
| 44 | BOOT0 | BOOT0 | R50 10k 到 GND | ✅ BOOT0={U6.44,R50.1} |
| 45 | PB8 | — | NC（可留 CAN_STB） | ✅ |
| 46 | PB9 | — | NC | ✅ |
| 47 | VSS_3 | GND | — | ✅ |
| 48 | VDD_VIO_3 | +3V3 | C54 100nF | ✅ |

统计：电源/地 9 脚、时钟/复位/启动 4 脚、GPIO 已接 19 脚（含 PA9/PA10 → J8 DNP 焊盘）、**NC 19 脚**
（2/3/4/10/12/13/14/15/16/17/18/19/20/21/22/38/39/45/46）。9+4+19+19 = 51 ≠ 48？

> 说明：spec §1.3 原文「NC 16 脚 + RS485 3 脚 = 19 脚」，统计式 9+4+19+16=48。
> 本页 RS485 不画（U-1 选①），故 NC = 16+3 = **19 脚**，已接 GPIO = 19 脚（含 PA9/PA10 → J8），
> 9 + 4 + 19 + 19 = 51？实际为 **9（电源/地）+ 4（时钟/复位/启动）+ 16（已接 GPIO，不含 PA9/PA10 另算）+ 19（NC）** ——
> 其中 PA9/PA10 既在「已接 GPIO」又各自落在 J8 焊盘上，spec 统计口径是「PA9/PA10 也算已连接」：
> 已接 GPIO = 19（PA1、PA8、PA9、PA10、PA11、PA12、PA13、PA14、PB4、PB5、PB6、PB7、PB12、PB13、PB14、PB15 + RS485 不画省下的 PA2/3/4 为 NC）。
> 逐一核对：48 脚全部在网表中有归属（有网络或 NC），**无遗漏、无错接**。spec 的「9+4+19+16=48」在「RS485 不画时 19 NC」口径下应为 **9+4+16+19=48**（16 已接 GPIO 不含 PA9/PA10，因为 PA9/PA10 属调试串口、接 J8 焊盘）。

**关键网表回读**（`kicad-cli sch export netlist`，局部网名前缀 `/MCU 与通讯/` 已省略）：

| 网络 | 节点 |
|---|---|
| CAN_H（全局） | J7.1, L2.4, R55.2, R56.2, U8.1 |
| CAN_L（全局） | J7.2, L2.3, R55.1, R57.2, U8.2 |
| CAN_H_X（局部） | L2.1, R56.1, U7.7 |
| CAN_L_X（局部） | L2.2, R57.1, U7.6 |
| CAN_TXD | U6.33, U7.1, R53.1 |
| CAN_RXD | U6.32, U7.4 |
| CAN_RS | U7.8, R54.2 |
| HSE_IN | U6.5, Y1.1, C56.2 |
| HSE_OUT | U6.6, Y1.3, C57.1 |
| NRST | U6.7, C58.1 |
| BOOT0 | U6.44, R50.1 |
| KEY | U6.25, SW1.1, SW1.2 |
| LED1_K/LED2_K/LED3_K | U6.26/27/28, R58.1/R59.1/R60.1 |
| BAL_CLK | U6.29, R52.1 |
| PRECHG_EN | U6.11, R51.1 |
| +3V3 | 21 节点（含 U6 5 个电源脚 + U7.3 + LED 阳极 + R53.2 + J8.1 + C50–C55/C59） |
| GND | 35 节点 |

差分对顺序（规则 0c）核对：**J7 → U8 → R55 → R56/R57‖L2 → U7** 一条直通道；
L2 绕组 1–4 = CAN_H、2–3 = CAN_L（L2.1/L2.2 在收发器侧 = CAN_H_X/CAN_L_X，L2.4/L2.3 在连接器侧 = CAN_H/CAN_L），与 spec §3.5 一致。

---

## 4. 极性件核对（规则 00 ② / 任务 §2）

| 器件 | 符号引脚名/号（库读回） | 封装 1 脚 | 本图接法 | 结论 |
|---|---|---|---|---|
| LED1/LED2（C84256，符号 `FC-2012HRK-620D`） | **pin1 = `-`（阴极，左 x=−5.08）、pin2 = `+`（阳极，右 x=+5.08）** | `jlc:LED0805-RD` pad1（x=−1.10 左）/pad2（x=+1.10 右） | 阳极(pin2)→+3V3，阴极(pin1)→R58/R59→MCU 灌电流 | ✅ 符号 pin1 阴极 ↔ 封装 pad1（左）同侧；灌电流低电平点亮正确 |
| LED3（C2297，符号 `0805G`） | **pin1 = `A`（阳极，右 x=+5.08）、pin2 = `K`（阴极，左 x=−5.08）** | `jlc:LED0805-R-RD` pad1（x=+1.05 右）/pad2（x=−1.05 左） | 阳极(pin1)→+3V3，阴极(pin2)→R60→MCU | ✅ 符号 pin1 阳极 ↔ 封装 pad1（右）同侧 |

- 两种 LED 符号引脚号定义相反，本图**按引脚名接**：红灯阳极在右（pin2）、绿灯阳极也在右（pin1），
  网表回读 LED1.2/LED2.2/LED3.1 均落 +3V3，阴极经限流电阻落 MCU 灌电流脚，方向一致。
- ⚠ **遗留（spec X-6）**：C84256 的库符号名 `FC-2012HRK-620D` 与嘉立创型号 `NCD0805R1` 不一致，
  且 `LED0805-RD` 封装**无极性丝印标记**（`fp_poly` 为空）。本图已按符号引脚名保证电气方向正确，
  但贴片方向需按 `NCD0805R1` 手册阴极标记再核一次（取库方/复核方在后续轮处理）。

---

## 5. 自检结果

> **本节是第 1 轮的历史记录**，其中 `check_05_layout.py` 只有 1–3 项、pymupdf 文字重叠是另写的一次性脚本。
> 第 3 轮的检查 1–8 全量结果见本报告顶部「第 3 轮变更 §2」；第 2 轮的见其 §2。

| # | 检查 | 结果 |
|---|---|---|
| 1 | `check_05_layout.py` 几何 1/2/3（导线不穿本体/不经过非端点引脚/T 接点有 junction） | ✅ **PASS，0 条**（导线 110 / junction 6 / 实例 32 / 引脚 129） |
| 2 | ERC `--severity-all`（根图） | ✅ **05 页 0 条**；全图 5 条 `isolated_pin_label` 均为**跨页预期**：BAT+（01 页未画）、I2C_SCL/I2C_SDA/AFE_ALERT/AFE_WAKE（02 页未画） |
| 3 | 网表 `kicadxml` | ✅ 45 器件（本页 32 + 04 页 13）Footprint/LCSC **全部非空**，无 `Pad??`，无两脚件一端悬空，无自短路 |
| 4 | `sch_conn.py`（仓库技能脚本，KiCad 版） | ✅ ②③ **P0 = 0**、同网多名 = 0、死头 = 0、孤立引脚 = 0、网表里找不到的名字 = 0；P1 = 10（= 5 条 isolated_pin_label + 5 条同名单脚网络，均为跨页预期） |
| 5 | 文字 bbox 不重叠（pymupdf 逐 span，容差 0.2mm²） | ⚠ 537 个 span 去重后 **11 处**重叠，全部为**符号级 quirk**（见下）：LED1/2 引脚名 `-`/`+` 与值「红」、LED3 引脚名 `A`/`K` 与值「绿」（各 3 处）、C56/C57（33pF ±3.81）引脚名 `1`/`2`（2 处）。与 04 页 D7 K/A、C45 1/2 同类，不改库无法消除 |
| 6 | PDF 渲 PNG（200dpi）目视 | ✅ 左/中/右分区清晰，CAN_H/CAN_L 差分对平行直通道，无导线穿本体，无文字压线 |
| 7 | 幂等 | ✅ 跑两次 md5 相同（`ee2841cbe1d97c2531a0e64cea2090fa`） |
| 8 | DNP 属性 | ✅ J8、L2 均为 `(dnp yes)`；其余 30 器件 `(dnp no)` |

### 5.1 符号级文字重叠 quirk（第 1 轮记录；**第 2 轮靠清空引脚名「消除」，第 3 轮已撤销该做法**）

> 第 2 轮按当时的任务书对 Y1、LED1–3、C56/C57 的符号引脚名做了清空（`(name …)""`）来「隐藏」它们。
> 第 3 轮任务书 P2-N1 判定这是错的（与库不一致、网表丢 `pinfunction`、将来库同步会被撤销），**已恢复为与库逐字一致的符号**；
> 由此回来的 3 类引脚名重叠改为**靠字段位置规避**，规避不掉的按符号库 quirk 记录（见本报告顶部「第 3 轮变更 §4」），**不动符号**。

1. **LED1/LED2（FC-2012HRK-620D）引脚名 `-`/`+` 与值「红 0805」重叠**（第 3 轮：值已移到本体外 ✅，引脚名保留）。
2. **LED3（0805G）引脚名 `A`/`K` 与值「绿 0805」重叠**（第 3 轮：值已移到本体外 ✅，引脚名保留）。
3. **C56/C57（0402CG330J500NT，33pF，引脚距 ±3.81）引脚名 `1`/`2` 压极板**（第 3 轮：值下移/右移 ✅，引脚名保留）。
   根治需在 `fetch_jlc_parts.py` 库侧归一化时给二脚无源件加 `(pin_names (hide yes))`（04 页复核 P2-6 同建议）——
   **是设隐藏开关，不是清空引脚名**。

---

## 6. 建议 / 遗留（待主代理）

1. **跨页 `isolated_pin_label`**：BAT+（01 页未画）、I2C_SCL/I2C_SDA/AFE_ALERT/AFE_WAKE（02 页未画）——
   对应页画好后自动消失，非本页问题。
2. **spec X-3（网络类）**：`CAN_DIFF` 目前只匹配 `CAN_H`/`CAN_L`/`RS485_A`/`RS485_B`，需把 `CAN_H_X`/`CAN_L_X` 加进
   `mp2645a-bms.kicad_pro` 的 `netclass_patterns`（本任务「只改本页」，未动 `.kicad_pro`）。
3. **spec X-2 / X-4（02 页）**：R_ALT 改 100k 下拉、R_WAK 接 +3V3（本板 buck 轨）——02 页画图时处理。
4. **spec X-1（docs）**：docs/03 §6 的 PWR_EN 删除、SWD 2×5 1.27 改 J8 1×6 2.54 DNP、CH32 VDD 脚数 N=5 关闭。
5. **spec X-6（取库核对）**：C84256 符号名与 NCD0805R1 型号不一致、LED0805-RD 封装无极性丝印（§4 已记录）。
6. **U5 待机超标（用户接受）**：SN65HVD230 高速模式隐性 1–2mA，超 <300µA 待机目标，本版按 U-5 接受，PB8 留空（可作日后断电 MOS 控制）。
7. **文档记录**：晶振负载电容 C1562 33pF、绿灯 330Ω C25104 两处换料已落 BOM（本任务未改 BOM，需主代理确认 docs/02-BOM.csv 与图一致——已核对一致）。
8. **取库脚本（第 3 轮新增建议）**：`tools/fetch_jlc_parts.py` 库侧归一化时给二脚无源件（电阻/电容/电感/跳线）加 `(pin_names (hide yes))`，
   一次根治 LED/Y1/C56/C57/JP1 这几类「引脚名画在本体内」的重叠（04 页复核 P2-6 同建议）。
   **注意是设隐藏开关，不是把 `(name …)` 清空**——清空会让符号与库不一致、网表丢 `pinfunction`（本轮 P2-N1 的教训）。
9. **自检方法论（第 3 轮新增，建议写进知识库）**：
   - 「符号本体/字段两两不相交」必须**跨器件**比对，只比「自己的字段 ↔ 自己的本体」会漏掉「A 的字段压 B 的本体」（第 2 轮的洞）。
   - 比完几何还要**比渲染**：字段文字压到**标签文字/别人的图形文字**上，几何检查看不见——本轮靠给检查 8 加 `[8d]`（字段渲染盒 ↔ 非本符号渲染盒）补上。

最后一行回复 `DONE`。
