colemandlut/MP2645A-BMS/design/05_mcu_comm-review-opus-r2.md

# 05_mcu_comm 第 2 轮独立复核（复核方 Claude Opus）

> 2026-09-27 13:03 JST
>
> - **快照**：`review/05-r2/`。
> - **纪律**：同第 1 轮任务书 `design/05_mcu_comm-task-review.md`。没有读画图方的报告和脚本注释，只读不改工程；本文件是唯一的写入。
> - **复跑**：用 kicad-cli 10.0.6 对 `hardware/mp2645a-bms.kicad_sch` 重新跑 ERC、导出网表。网表去掉日期行后，与快照 `netlist.xml` 完全一致。
> - **比对**：把第 1 轮和第 2 轮网表中本页的器件与网络逐条做了 diff（结果见 §1）。

## 结论

| 档 | 条数 |
|---|---|
| **P0** | **0** |
| **P1** | **1**（新发现：R55 与 JP1 两个符号叠在一起） |
| **P2** | **9**（新增 3 条，沿用第 1 轮 6 条） |

第 1 轮的三条 P1 中，P1-1（JP1）和 P1-2（网络类）已关闭；P1-3（文字重叠）的三处都已改好，但新画的 JP1 又造成了一处同类重叠，记为新的 P1。

---

## 1. 本轮变更逐条核实

### 与第 1 轮网表的 diff（本页范围）

| 变化 | 内容 | 是否符合预期 |
|---|---|---|
| 新增器件 | JP1：`PZ254V-11-02P`，C492401，封装 `jlc:HDR-TH_2P-P2.54-V-M`，贴装（dnp no） | ✅ |
| 新增网络 | `/MCU 与通讯/CAN_TERM` = {R55.1, JP1.1} | ✅ |
| 网络变化 | `CAN_L`：去掉 R55.1，加入 JP1.2 | ✅ |
| 网络不变 | `CAN_H` 仍含 R55.2 | ✅ |
| 字段变化 | L2 的 Value 由 `51µH CMC (DNP)` 改为 `51µH CMC`，DNP 属性仍在 | ✅ |
| 网络改名 | 三条 LED 阴极网络改名，成员不变 | ✅ 见 §1 第 3 项 |
| 字段变化 | LED1/2/3、Y1、C56、C57 的 pinfunction 变成空 | ⚠ 见 P2-N1 |
| 其它 | 没有任何其它网络变化 | ✅ |

- 本页 ERC 为 0。根图仍有 5 条 `isolated_pin_label`（BAT+ 属于 04 页；AFE_ALERT、AFE_WAKE、I2C_SCL、I2C_SDA 只接到 U6），原因同第 1 轮：01–03 页还没画。
- `sch_conn.py`：两脚件一端悬空 0、死头 0、孤立引脚 0、同网多名 0、网络名消失 0。
- 本页 NC 标志 20 个，与 20 个本页 `unconnected-*` 网络（U6 的 19 个空脚 + U7.5）一一对应 ✅。

### 1. 第 1 轮 P1-1（JP1）：**已关闭**

**拓扑**：CAN_H ─ R55 ─ CAN_TERM ─ JP1 ─ CAN_L，与用户 2026-09-27 的决定一致。
- 插上跳线帽 = 120Ω 接入；拔掉 = 开路。
- 电流路径只经过 R55 和跳线帽，跳线帽接触电阻远小于 120Ω。

**封装**：实测 2 个焊盘，中心距 2.54mm，1 脚方形，PTH 孔 ⌀1.2mm。

**LCSC 与 BOM**：C492401 与 `docs/02-BOM.csv` 第 83 行一致。跳线帽 C100114 是机械件，不进原理图，符合 BOM 第 84 行。

### 2. 第 1 轮 P1-2（CAN_DIFF 网络类）：**已关闭**

- `.kicad_pro` 的 CAN_DIFF 模式现在是 `CAN_H`、`CAN_L`、`*CAN_H_X`、`*CAN_L_X`，RS485 已删。
- **判据**：以网表为准，不只看配置文本。网表的 net 节点里，`/MCU 与通讯/CAN_H_X`、`/MCU 与通讯/CAN_L_X`、`CAN_H`、`CAN_L` 都是 `class="CAN_DIFF"` ✅。
- `tools/gen_kicad_skeleton.py` 第 63 行已同步；第 48、50 行的 RS485 残留也删了（第 1 轮 P2-10 前半条关闭）。
- `CAN_TERM` 属于 Default 类。它是终端电阻的短支路，电流约 25mA 级，默认线宽够用，不需要进差分类。

### 3. 第 1 轮 P1-3（文字重叠）：**原来的三处都已改好**

| 位置 | 核实结果 |
|---|---|
| a. BOOT0 | 标签文字已移到 44 脚竖线左侧，不再横穿 43 脚（I2C_SDA）的线，也不碰其它线 ✅ |
| b. Y1 | 引脚名已不显示，脚号 1–4 清楚；数值「12MHz」已贴在 Y1 下方 ✅ |
| c. LED | 引脚名已不显示，数值「红 0805」「绿 0805」已移到本体外 ✅ |

**隐藏引脚名后，LED 极性在图上是否仍可辨（逐颗放大到 350dpi 看）**：可辨，不误导。
- 三颗都是标准二极管图形：三角尖和短竖线都在左侧，也就是阴极朝左，接限流电阻、再到 MCU 的灌电流脚；阳极朝右，接 +3V3。
- 与网表完全吻合：
  - LED1、LED2 的 1 脚是阴极，接 R58/R59；
  - LED3 的 2 脚是阴极，接 R60。
- LED1/2 的阴极是 1 脚，LED3 的阴极是 2 脚，编号不一样，但图形方向一致，人看图不会弄错。

**阴极网络由 `Net-(LED1--)` 改名为 `Net-(LED1-Pad1)` 有没有影响**：没有电气影响。
- 这是 KiCad 自动生成的网络名。改名的原因是引脚名被清空后，KiCad 改用焊盘号来命名。
- 没有任何标签、网络类模式或跨页引用用到这个名字。
- `mp2645a-bms.kicad_pcb` 目前还没有同步本页的封装，所以也不影响 PCB。
- 以后每次从原理图更新 PCB（F8），只会出现「网络改名」一类的提示。
- 如果希望名字稳定，可以给这三个网络加局部标签，例如 `LED1_C`。这一点并入 P2-N1。

### 4. 第 1 轮可读性小项（P2-8、P2-9）：**已关闭**

- 「12MHz」已靠近 Y1。
- U7 左侧 `CAN_RXD` 标签改为经短线引出，不再贴着 +3V3 标签。
- 「L2 与 R56/R57 二选一」只剩 L2 旁一处，页头改写为 JP1 的用法。
- 已加「I2C 上拉 R_I2C1/2 在 02 页。」。
- L2 的 Value 已去掉 DNP 字样。
- docs/03 §6 的去耦一行已关闭为 N = 5（第 1 轮 P2-10 后半条关闭）。

---

## P0（0 条）

无。

## P1（1 条）

### P1-N1 R55 与 JP1 的符号叠在一起（规则 00 ③「重叠一律不允许」）

- **现状**：
  - R55 的符号在 (342.90, 138.43)，旋转 90°；JP1 的符号在 (347.98, 139.70)，旋转 90°。两者 x 只差 5.08mm。
  - 在 PDF 第 6 页放大到 500dpi 看：**JP1 的本体矩形压住了 R55 的位号「R55」和数值「120Ω 1%」**；JP1 的数值「终端跳线」与 R55 的数值叠成一团；JP1 的脚号「1」「2」也压在本体边上。
  - 电气上是对的（网表见 §1），但图上读不出哪颗是电阻、哪颗是跳线。
- **改法**：
  - 把 JP1 在 CAN_TERM 这条线上往右或往下挪出至少 10mm，使 R55 与 JP1 串联一目了然：CAN_H → R55 → CAN_TERM → JP1 → CAN_L。
  - 两颗器件的位号、数值各自放在本体外侧。
  - 改完重跑 ERC 和网表 diff，应当只有坐标变化。

## P2（9 条）

### 新增

**P2-N1 为了「隐藏引脚名」，把嵌入符号的引脚名清空了，而不是设置成隐藏**
- **现状**：图纸内嵌的 `lib_symbols` 中，下面 4 个符号的 `(name ...)` 已被改成空字符串，而工程库 `hardware/lib/jlc/jlc.kicad_sym` 里仍是原名。
  - `jlc:FC-2012HRK-620D`：原名 `-`、`+`
  - `jlc:0805G`：原名 `A`、`K`
  - `jlc:X322512MSB4SI`：原名 `OSC1`、`GND`、`OSC2`、`GND`
  - `jlc:0402CG330J500NT`：原名 `1`、`2`
- **后果**：
  1. 网表的 pinfunction 丢失，LED 的极性语义只剩图形和脚号，自动核对工具与后续复核没法再按引脚名核极性。
  2. 图纸里的符号与库符号不一致（ERC 这次没有报 `lib_symbol_mismatch`），将来谁执行一次「与库符号同步」，引脚名就会回来，本轮的可读性修复会被悄悄撤销。
  3. 偏离规则 0e「符号从嘉立创取、原样使用」的精神。
- **建议**：恢复原引脚名，改用符号属性里的「显示引脚名」开关（`(pin_names (hide yes))`）隐藏。这样网表仍带 `+`/`−`/`A`/`K`。如果需要稳定的网络名，再给三个阴极节点加局部标签。
- **定级理由**：不影响电气连接，所以列 P2；建议下一轮顺手改掉。

**P2-N2 JP1 的 Value 与 BOM 描述不一致**
- JP1 的 Value 是「终端跳线」，BOM 第 83 行的值是「2P 排针」。
- BOM 按 LCSC 字段出，所以不会出错，只是对账时会报差异。可以统一成「2P 排针（终端跳线）」。

**P2-N3（布局提示）JP1 是直插件，挂在差分对上**
- JP1 和 R55 应当紧贴 CAN_H/CAN_L 的直通道放置，放在 U8 与 L2/R56/R57 之间，让 CAN_TERM 支路尽量短，不要让差分对绕过去找它（规则 0c）。
- 跳线帽高于板面，要核外壳净空；BOM 已注明振动场合打胶。

### 沿用第 1 轮（本轮图纸和规格书都没有动，结论不变）

| 编号 | 内容（详见 `design/05_mcu_comm-review-opus.md`） | 状态 |
|---|---|---|
| P2-1 | HSE 激励功率：规格书 §2.4 把「HSE drive current 0.53mA」当成晶体电流，前提不成立；33pF 会使激励功率约升 2.4 倍，建议在 OSC_OUT 预留 0Ω 串联电阻，样板实测。规格书第 260 行仍写「不需要 Rext」 | 沿用 |
| P2-2 | R55 最坏功耗 3²/120 = 75mW；收发器没有显性超时；85°C 降额后余量约 1.1 倍。规格书第 329 行仍写「余量 3 倍」 | 沿用 |
| P2-3 | U8 的 VRWM 24V 低于 8S 满充 29.2V，线束误接到 PACK+ 时 U8 会烧毁；钳位 41V 高于收发器 ±40V | 沿用 |
| P2-4 | BOOT0、NRST 没有引出，J8 的 USART1 做不了 ISP 下载；建议各加一个测试焊盘 | 沿用 |
| P2-5 | 规格书页码订正：Table 4-19 在 PDF p.49，规格书第 77 行仍写 p.50；「显性 35mA」是推算值；另外需要补 TIM1 的 CC1NE/BKE 固件注意事项（原 P2-7） | 沿用（合并了原 P2-7） |
| P2-6 | 绿灯 LED3 电流 0.6–2mA，单板之间亮度可能差约 3 倍 | 沿用 |
| P2-11 | KiCad 不会把 CAN_H/CAN_L 识别成差分对（它只认 `_P`/`_N` 或 `+`/`-` 后缀），布线时要按网络类手动约束 | 沿用 |

- 第 1 轮 P2-9 的后半句（出 BOM 时要确认 DNP 件 J8、L2 被剔除）留到出 BOM 时由 `jlc_fab.py` 检查，这里不再单列。

---

## 覆盖清单（第 2 轮）

| 对象 | 本轮核对 | 结论 |
|---|---|---|
| 全页连通性 | ERC、网表 diff、sch_conn 几何、NC 标志计数 | 无问题 |
| JP1 / R55 / CAN_TERM | 拓扑、LCSC、封装间距、BOM | 电气无问题；P1-N1（重叠），P2-N2，P2-N3 |
| CAN_DIFF 网络类 | 网表里的 class 属性 | 已关闭 |
| LED1–3 | 图形极性与网表一致、网络改名的影响 | 无电气问题；P2-N1 |
| Y1 / C56 / C57 | 连接不变，可读性已改好 | P2-N1（引脚名被清空） |
| U6 / U7 / U8 / L2 / R50–R54 / R56–R60 / C50–C59 / J7 / J8 / SW1 | 网表与第 1 轮 diff 为零（L2 只改了 Value） | 沿用第 1 轮「已核对无问题」 |
| 安全态（BAL_CLK、PRECHG_EN、CAN TXD、AFE_WAKE） | 相关网络未变 | 沿用第 1 轮结论，满足「复位即停」 |
| 跨页标签 | 契约 10 个名字，无 RS485、无 PWR_EN | 无问题 |
| LCSC 与 BOM | 33 个器件（新增 JP1） | 一致 |

## 给主代理

- 本复核只读，没有写 `obsidian-vault/`。
- 建议记一条经验：隐藏引脚名要用 `pin_names hide`，不要清空引脚名，否则网表会丢掉极性语义，而且与库同步后会被撤销。
