colemandlut/MP2645A-BMS/design/05_mcu_comm-task-draw-r3.md

# 画图任务书：子图 05_mcu_comm，第 3 轮（按 Opus 复核第 2 轮改）

工作目录 `/home/user/MP2645A-BMS`。纪律同第 1 轮任务书 `design/05_mcu_comm-task-draw-r1.md`。
依据：`design/05_mcu_comm-review-opus-r2.md`（你可以读）。**先跑一遍脚本确认幂等**（当前产物 md5 `61b5aba59189b24463741d270b088539`）再改。
时间：一次改完、一次验收，不要反复重排整页版面。

## 要改
1. **P1（新）R55 与 JP1 符号叠在一起**：两者只差 5.08mm，JP1 本体压住 R55 的位号与「120Ω 1%」。把 JP1 沿 CAN_TERM 挪开（≥10mm），
   两者的位号/数值互不重叠。改完网表应只有坐标变化（导出前后「位号.脚 → 网络」对比为 0 差异）。
   **补一项自检**：符号本体 ↔ 符号本体（含字段文字）两两不相交——第 2 轮的 6 项自检没抓到这一类，说明检查有漏洞，补上并在全页跑一遍。
2. **P2-N1 不要清空引脚名**：第 2 轮为了「隐藏引脚名」把嵌入符号里 LED（`-`/`+`、`A`/`K`）、Y1（OSC1/OSC2）、C56/C57 的引脚名清空了，
   使嵌入符号与库不一致、网表丢了极性语义，且将来与库同步会被撤销。**恢复为与库完全相同的嵌入符号**（从 `hardware/lib/jlc/jlc.kicad_sym` 原样复制）。
   引脚名造成的重叠改用**器件朝向/位置/字段位置**来避开；实在避不开的（符号自带的引脚名压在本体内），在报告里列为符号库 quirk，不要改符号。
   恢复后 LED 阴极网络名会变回 `Net-(LED1--)` 这类，正常。
3. **P2-N2**：JP1 的 Value 改为 `2P 排针`（与 BOM 一致）；说明文字里保留「JP1 插帽接入 120Ω 终端，拔帽不用」。

其余 P2 不改。

## 验收
第 1 轮任务书第 4 节全部项 + 新的「符号本体/字段两两不相交」检查全过；ERC 本页 0 条（跨页 isolated_pin_label 除外）；
网表与第 2 轮相比只允许 LED 阴极网络名变化；幂等。报告开头加「第 3 轮变更」+ 自检结果 + 网表差异。最后一行回复 `DONE`。
