colemandlut/MP2645A-BMS/design/05_mcu_comm-task-draw-r2.md

# 画图任务书：子图 05_mcu_comm，第 2 轮（接续第 1 轮）

工作目录 `/home/user/MP2645A-BMS`。纪律同第 1 轮任务书 `design/05_mcu_comm-task-draw-r1.md`（全部沿用）。

## 0. 接续说明（上一轮在收尾时因 API 余额不足中断）
- 前任脚本：`hardware/gen/gen_05_mcu_comm.py`、`hardware/gen/check_05_layout.py`；产物 `hardware/05_mcu_comm.kicad_sch`；报告 `design/05_mcu_comm-draw-report.md`（已基本写完）。
  这些都在 git 提交 `0b8bb53` 里，也冻结在 `review/05-r1/05_mcu_comm.kicad_sch`。
- 主代理核查：第 1 轮 ERC 本页 0 条、几何自检 PASS、网表逐脚与规格书一致，Opus 复核 P0 = 0。
- **先跑一遍脚本**确认输出与 `review/05-r1/05_mcu_comm.kicad_sch` 是否逐字节相同（上一轮末尾脚本与产物可能不同步：
  主代理重跑时文件大小 158967 vs 159251）。不同就先查清差在哪、以脚本为准，在报告里说明。

## 1. 本轮要改（依据 `design/05_mcu_comm-review-opus.md`，你可以读它）

1. **P1-1 CAN 终端改跳线可选（用户 2026-09-27）**：R55 120Ω 串 **JP1**（`jlc:PZ254V-11-02P`，封装 `jlc:HDR-TH_2P-P2.54-V-M`，LCSC **C492401**，值 `终端跳线`）。
   CAN_H → R55 → 新本页网络 `CAN_TERM` → JP1 → CAN_L（或 R55/JP1 顺序对调，版面顺手为准）。插跳线帽 = 接入终端。
   跳线帽 C100114 是机械件，不画。在说明文字里加一句「JP1 插帽接入 120Ω 终端，拔帽不用」。
2. **P1-3 三处重叠**：
   a. `BOOT0` 标签文字横穿 I2C_SDA 的连线——挪开；
   b. Y1 的引脚名粘成「GNDOSC2」「OSC1GND」——调整 Y1 朝向/周边走线或字段位置，使引脚名不相互粘连、不压线；
   c. LED 的引脚名（`+`/`A` 等）画在本体内阴极一侧、值文字压在本体上——值文字挪到本体外；引脚名若是符号自带无法挪，在报告里说明并确认极性标注不会误导（必要时在 LED 旁加一个小字「A→K」方向注释）。
   你的文字重叠自检要能抓到这几类（标签文字 vs 导线、引脚名 vs 引脚名、字段 vs 符号本体），抓不到就补检查项。
3. **P2 可读性小项（无争议，一并改）**：「12MHz」值文字靠近 Y1；CAN_RXD 与 +3V3 标签不要贴边；删掉重复出现的「L2 与 R56/R57 二选一」说明（只留一处）；
   加一句注释「I2C 上拉 R_I2C1/2 在 02 页」；L2 的 Value 去掉「(DNP)」字样（DNP 只用 `(dnp yes)` 属性表示）。

**其余 P2 不要改**（交用户定）。

## 2. 验收（全部重跑）
第 1 轮任务书第 4 节 6 项全部通过；另外：
- 网表里 JP1 存在、Footprint/LCSC 非空；`CAN_TERM` 只连 R55 与 JP1 各一脚；R55 不再直接跨接 CAN_H/CAN_L。
- 除 JP1/CAN_TERM 与上面列出的文字位置外，「位号.脚 → 网络」映射与第 1 轮完全一致（导出前后网表对比，写进报告）。

## 3. 交付
更新脚本、原理图、报告（开头加「第 2 轮变更」+ 自检结果 + 网表差异）。最后一行回复 `DONE`。
