colemandlut/MP2645A-BMS/design/05_mcu_comm-review-opus.md

# 05_mcu_comm 独立复核报告（复核方 Claude Opus）

> 时间戳：2026-09-27 11:19 JST　快照：`review/05-r1/`　任务书：`design/05_mcu_comm-task-review.md`
> 纪律：没有读画图方报告和 `*-draw-*.out`；没有改工程文件。本文件是唯一写入。
> 复跑：`kicad-cli 10.0.6 sch erc` 和 `sch export netlist`（在 `hardware/` 下，输出到 /tmp/r05）。**网表与快照 `netlist.xml` 逐行一致**（去掉日期行后 diff 为空），说明快照就是当前工程。另外跑了 `sch_conn.py`。
> 手册页码一律是 **PDF 页号**。简称：CH32 = `C3001172_WCH_CH32V203C8T6.pdf`，HVD = `C55259679.pdf`，ESD = `C2687131.pdf`，XTAL = `C9002.pdf`（YSX321SL），CMC = `C95572.pdf`，LEDR = `C84256_NCD0805R1.pdf`，LEDG = `C2297.pdf`，SW = `C318884.pdf`，LVC = `C7394021_SN74LVC1G17DBVR_UMW.pdf`。

## 结论

| 档 | 条数 |
|---|---|
| **P0 不能投板** | **0** |
| **P1 必须改** | **3**（其中 P1-1 是用户 2026-09-27 定的已知待改项） |
| **P2 建议** | **11** |

本页的连通性、48 个脚的分配、外设复用、极性件、安全态都核对无误。P1 只有三类：已知待画的 JP1、差分网络类没配、原理图文字重叠。

---

## ⓪ 连通性（ERC 与网表）

- ERC（`--severity-all`）共 5 条，全部是根图的 `isolated_pin_label`：`AFE_ALERT`、`AFE_WAKE`、`I2C_SCL`、`I2C_SDA`（都只接 U6），另外一条 `BAT+` 属于 04 页。
  - 原因是 01–03 页还是空的（网表里只有 04、05 两页的器件），02 页画完后这几条应该自动消失。
  - **不算本页问题，但整合时要复查。**
  - `/MCU 与通讯/` 页本身 ERC 为 0。
- 网表 `unconnected-*` 共 20 个：U6 的 19 个空脚（2、3、4、10、12–22、38、39、45、46）加 U7.5 Vref。
  - 20 个都是单节点，图上 `no_connect` 也正好 20 个，与规格书 §1.3「RS485 不画时 19 个 NC」一致 ✅。
- `sch_conn.py` 的结果：两脚件一端悬空 0、自短路 0、死头 0、孤立引脚 0、同网多名 0、网络名消失 0 ✅。
- ⓪b 同网多名：ERC 没有 `multiple_net_names`，几何并查集也是 0 ✅。
- 全局标签只有契约里的名字：`I2C_SCL I2C_SDA AFE_ALERT AFE_WAKE BAL_CLK PRECHG_EN CAN_H CAN_L +3V3 GND`。**图上没有 RS485 或 PWR_EN 残留** ✅。
- DNP 属性：L2、J8 都是 `(dnp yes)`，其余器件都是 `dnp no` ✅。

---

## P0（0 条）

无。

---

## P1（3 条）

### P1-1 【已知待改项】R55 / JP1：CAN 终端还没有做成跳线可选

- **现状**：网表中 `CAN_H = {J7.1, U8.1, R55.2, R56.2, L2.4}`，`CAN_L = {J7.2, U8.2, R55.1, R57.2, L2.3}`。R55 120Ω 直接跨接在 CAN_H 和 CAN_L 之间。
- **依据**：用户 2026-09-27 的决定（docs/03 §6「CAN 终端」一行、`docs/02-BOM.csv` 第 83–84 行）：R55 要串 JP1（C492401，2P 2.54 排针），加跳线帽 C100114（机械件）。本快照还没画 JP1。
- **改法**：把 R55 的一端（例如 R55.1）从 CAN_L 断开，接一个局部网络 `CAN_TERM`，经 JP1 1–2 回到 CAN_L。
  - JP1 的 LCSC 字段填 C492401。C492401 已在 `lib/jlc/fetch_report.md` 第 7 行，库已取回。
  - 跳线帽没有焊盘，不进原理图，只在 BOM 里记为机械件。
  - 按规则 00c 纪律，改完要重跑 ERC 和网表。
- **功耗前提复核**：见 P2-2，终端电阻功耗按最坏工况只有约 1.1 倍余量。

### P1-2 CAN_H_X / CAN_L_X 没有进 CAN_DIFF 网络类（规格书 X-3 未落实）

- **现状**：`mp2645a-bms.kicad_pro` 的 `netclass_patterns` 里 CAN_DIFF 只匹配 `CAN_H`、`CAN_L`、`RS485_A`、`RS485_B`。
  - 收发器一侧的局部网络名是 `/MCU 与通讯/CAN_H_X` 和 `/MCU 与通讯/CAN_L_X`，现在会落到 Default 类。
  - 于是 R56/R57（或 L2）到 U7.6/7 这一段在布线时没有差分线宽和线距约束。
- **依据**：规则 0c 第 3 条，差分线宽/线距必须在布局前写进设计规则，并把这对网络划进该网络类。
- **改法**：
  - 在 `.kicad_pro` 和 `tools/gen_kicad_skeleton.py` 第 63 行加入 `*CAN_H_X` / `*CAN_L_X`（或者直接用全路径名）。
  - 同时删掉 RS485_A/B 的模式（RS485 本版不画）。
- 这条改的是工程设置，不是图，但必须在进 PCB 之前完成，所以列 P1。

### P1-3 原理图有文字与导线、文字与器件的重叠（规则 00 ③「重叠一律不允许」）

逐处目视 `sch.pdf` 第 6 页（放大到 300–400dpi）：

| # | 位置 | 问题 | 改法 |
|---|---|---|---|
| a | U6 上边 44 脚 | 局部标签 `BOOT0` 的文字向右长，**横穿 43 脚 `I2C_SDA` 的竖线** | 标签改为朝左（justify right），或把 BOOT0 线往上多拉一段再放标签 |
| b | Y1 | 符号引脚名互相粘连，显示成「GNDOSC2」「OSC1GND」；C56 的脚号「2」压在电容本体上 | 隐藏 Y1 的引脚名（脚号保留），或换一个引脚名不重叠的符号摆放 |
| c | LED1、LED2、LED3 | 引脚名 `+`、`A` 画在符号本体内阴极一侧，与三角形重叠，而且**容易被误读成阳极在左**；数值「红 0805」「绿 0805」压在本体下沿 | 隐藏 LED 的引脚名，把数值挪到本体外 |

---

## P2（11 条，交用户定夺）

### P2-1 Y1 激励功率：规格书的前提不成立，33pF 会把激励功率抬高约 2.4 倍

- **规格书的推导**：§2.4 用 CH32 p.46 Table 4-11 的「HSE drive current 0.53mA @20pF」当作流过晶体的电流，算出 P = 80 × 0.53² ≈ 22µW。
- **问题**：这个 I2 是振荡器自身的耗电（与 STM32 数据手册同一格式的参数），不是晶体的 RMS 电流。所以这个前提不成立。
- **正确的估算**：激励功率 ≈ ESR × (2πf · C_L2′ · Vrms)²。
  - 取 C_L2′ ≈ 33 + 4 pF，OSC 脚幅值 1Vpp 时约 78µW；2Vpp 时约 310µW，**超过 XTAL 的 DL 上限 200µW**（XTAL p.1）。
  - 负载电容从 20pF 改到 33pF，同幅值下激励功率约升 (37/24)² ≈ 2.4 倍。
  - CH32 手册没有给 OSC 脚的幅值，不能算定。
- **建议**：
  - 在 OSC_OUT 与 Y1.3 之间预留一颗 0402 0Ω 串联电阻（Rext，C17168，基础库，零上料费），样板实测幅值后再定值；
  - 或者至少在样板阶段测一次晶体电流。
- **33pF 这个选择本身是对的**：CL = 16.5 + 杂散 2–7pF（CH32 p.47）= 18.5–23.5pF，把 20pF 包在中间 ✅。
  - 起振裕量已复核：gm_crit = 4 × 80 × (2π × 12M)² × (23p)² = 0.96mA/V，手册 gm = 17.5mA/V（CH32 p.46），裕量 18 倍 ✅。
  - 规格书 +34ppm 的频偏估算里 C1 = 5fF 是假设值，手册没给。好在 CAN 的时钟容差是 0.1% 级，这个数只作参考。

### P2-2 R55 功耗：规格书用典型值，最坏工况余量只有约 1.1 倍

- **规格书**：§3.4 按 VOD = 2V（典型）算出 33mW，得出「余量 3 倍」。
- **按最大值算**：HVD p.5 的 VOD(D) 最大是 3V，P = 3² / 120 = **75mW**。
- **为什么要按连续显性算**：这颗 HGSEMI 收发器没有 TXD 显性超时（手册里找不到 dominant time-out）。固件把 PA12 卡在低电平时，总线会一直处于显性，R55 连续承受上述功率。
- **降额**：0603 额定 100mW 在 70°C 以上线性降额，85°C 时约 82mW，**余量约 1.1 倍**。
- 结论：仍在额定内，0603 不必改；但规格书的「3 倍」应订正。固件要避免 TXD 被长时间拉低。R53 已经保证复位时为隐性。

### P2-3 U8 PESD2CAN 的额定值与 8S 系统的关系

- 击穿电压：VRWM = 24V，VBR = 26.1–30.2V（ESD p.3）。8S LFP 满充 29.2V，**如果线束把 CAN 线误接或短到 PACK+，U8 会持续击穿并烧毁**。
- 钳位电压：41V@5A（ESD p.3），比 HVD 总线脚的绝对最大值 ±40V（HVD p.4）高 1V。
- J7 只有 CAN 和 GND，线束里没有 PACK+ 时风险很低。规格书 §3.3 已经记录并接受了钳位这一点，这里补上误接 PACK+ 的场景，交用户确认线束。

### P2-4 J8 上的 USART1 做不了 ISP 下载，前提缺 BOOT0

- **规格书说法**：§1.2 称「WCH 的 ISP 引导程序也走 USART1」。
- **问题**：进入 System Boot 需要 BOOT0 = 1。现在 BOOT0 只有 R50 10k 下拉，J8 上也没有 BOOT0，所以串口 ISP 实际用不了。另外 NRST 也没有引出。
- **影响**：SDI（SWDIO/SWCLK）下载不受影响。
- **建议**：给 BOOT0 和 NRST 各加一个测试焊盘（不花钱）。或者在规格书里订正为「J8 的 TX/RX 只作调试打印」。

### P2-5 规格书的手册页码与引用订正

- **漏电流、弱上拉/下拉表的页码**：Table 4-19（Ilkg 1µA/3µA，RPU/RPD 30–50k）在 **CH32 PDF p.49**，规格书写的是 p.50。p.50 是 Table 4-20 和 NRST 表。
- **CAN 显性电流**：「显性 ≈35mA（HVD p.5，加 60Ω 负载）」这个数不在 HVD p.5 上。p.5 只给了空载 ICC 1–2mA，35mA 是 2V/60Ω 推算出来的，应注明「推算」。
- **VDDA 必须与 VIO 同压**：依据实际在 CH32 p.14–15（§2.5.3）和 p.39 Table 4-2 两处，结论正确。
- **BAL_CLK 安全态**：规格书写「VT− 约 0.6V 量级」，已按 LVC 手册核实为：
  - VT− 最小值：VCC = 2.3V 时 0.56V，VCC = 1.65V 时 0.35V（LVC p.6）；
  - 输入漏电流 ±1µA（LVC p.7）。
  - 最坏情况 (3µA + 1µA) × (100k ∥ 1M) = 0.36V < 0.56V ✅，结论成立。
  - 但如果电芯低到约 2V，VT− 最小值会低于 0.36V。此时只剩 BMS 的欠压保护兜底，影响很小。

### P2-6 绿灯 LED3 电流余量偏薄

- LEDG p.3：VF = 2.6–3.1V @5mA。
- 330Ω 时 I = (3.3 − 0.1 − VF) / 330 ≈ 0.6–2mA（VF 在小电流下取 2.5–3.0V），单板之间亮度可能差约 3 倍。
- 规格书已经把 1k 改为 330Ω，方向正确。如果嫌暗，可以再降到 220Ω（C25091，要先核是否基础库）。低优先级。

### P2-7 固件注意：TIM1 的互补通道与 LED/按键脚复用

- PB13、PB14、PB15 是 TIM1_CH1N、CH2N、CH3N，PB12 是 TIM1_BKIN（CH32 p.25、p.37）。
- BAL_CLK 用的是 TIM1_CH1（PA8），固件**不得置 CC1NE、BKE**，LED 脚保持 GPIO 模式；否则 PB13 会输出互补 PWM，或者按一下 SW1 就刹停均衡时钟。
- 建议补进规格书 X-5。

### P2-8 可读性小项（不算重叠）

- Y1 的数值「12MHz」离本体约 10mm，孤零零放在下方，应挪到 Y1 旁边。
- U7 左侧的 `CAN_RXD` 局部标签与 `+3V3` 全局标签几乎贴边，应拉开 1 格。
- 「L2 与 R56/R57 二选一」写了两次（页头说明和 L2 旁），留一处即可。
- 规格书 §9 要求加的注释「I2C 上拉 R_I2C1/2 在 02 页」没有单独写。页头只写了「I2C1 PB6/7→02 页 MP2797」。

### P2-9 L2 的 Value 字段里带了「(DNP)」

- L2 的 Value 是 `51µH CMC (DNP)`，BOM 第 79 行是 `51µH`。DNP 应当只用属性表达，Value 与 BOM 保持一致，否则 BOM 对账会报差异。
- 另外，J8 和 L2 都是 `in_bom yes` 加 `dnp yes`。出嘉立创 BOM 时要确认 `jlc_fab.py` 会剔除 DNP 件。

### P2-10 工程其它位置还有残留

- `tools/gen_kicad_skeleton.py` 第 48、50 行的 SHEETS 契约里还有 `RS485_A`、`RS485_B` 和「RS485 可选」。
- docs/03 §6「去耦」一行还写着「【VDD 脚数待手册】」，应按规格书关闭为 N = 5（VBAT、VDDA 和 3 个 VDD）。

### P2-11 KiCad 不会把 CAN_H / CAN_L 识别成差分对

- KiCad 的「布线(差分)」只认 `_P`/`_N` 或 `+`/`-` 后缀（规则 0c 第 1 条）。
- 契约名是用户定的，不建议改名。布线时可以按网络类手动等长，或者只在 PCB 侧另起别名。在这里记一笔，免得到布线时才发现。

---

## ①a 逐 IC 按手册典型应用点名

### U6 CH32V203C8T6（CH32 Fig 4-1 p.38、Fig 4-5 p.46、Fig 4-7 p.51、Fig 4-13 p.56、Note 4–6 p.35）

| 手册要求 | 网表实况 | 结论 |
|---|---|---|
| 每对 VDDx/VSSx 一颗 0.1µF | 24 脚 C52、36 脚 C53、48 脚 C54，另一端都接 GND；23、35、47 脚接 GND | ✅ |
| VDDA–VSSA 0.1µF；VDDA 与 VIO 同压（p.15、p.39） | 9 脚接 +3V3，C51；8 脚接 GND | ✅ |
| VBAT 接 1.8–3.6V（p.38、p.39） | 1 脚接 +3V3，C50 | ✅ |
| NRST 接 0.1µF 到地，内部上拉 30–50k（p.50–51） | 7 脚接 NRST 网络，C58 到 GND | ✅（τ = 4ms，远小于 tRSTTEMPO 24–30ms，p.40） |
| BOOT0 下拉（p.35 Note 6 是 BOOT0/PB8 合封型号的 4.7k 建议；LQFP48 的 BOOT0 是独立脚） | 44 脚经 R50 10k 到 GND | ✅（ISP 可用性见 P2-4） |
| HSE：晶振加 CL1 = CL2（p.46–47） | 5 脚接 HSE_IN（Y1.1，C56 到 GND）；6 脚接 HSE_OUT（Y1.3，C57 到 GND） | ✅（激励功率见 P2-1） |
| LSE 不用 | 3、4 脚放 NC | ✅ |
| 板级储能 | C55 4.7µF 0603（BOM 为 16V X5R） | ✅ |

**48 脚逐脚核对**：

- 引脚号与名称：对照 CH32 p.21 引脚图和 p.23–26 Table 3-1-1 的 LQFP48 列，与库符号的 pinfunction 逐一核对，一致。
- 电源与地：1 VBAT、9 VDDA、24、36、48 接 +3V3；8、23、35、47 接 GND ✅。
- 时钟、复位、启动：5 HSE_IN、6 HSE_OUT、7 NRST、44 BOOT0 ✅。
- 用到的 GPIO：

| 脚 | 口 | 网络 |
|---|---|---|
| 11 | PA1 | PRECHG_EN |
| 25 | PB12 | KEY |
| 26 / 27 / 28 | PB13 / PB14 / PB15 | LED1_K / LED2_K / LED3_K |
| 29 | PA8 | BAL_CLK |
| 30 / 31 | PA9 / PA10 | DBG_TX / DBG_RX |
| 32 / 33 | PA11 / PA12 | CAN_RXD / CAN_TXD |
| 34 / 37 | PA13 / PA14 | SWDIO / SWCLK |
| 40 / 41 | PB4 / PB5 | AFE_ALERT / AFE_WAKE |
| 42 / 43 | PB6 / PB7 | I2C_SCL / I2C_SDA |

- NC（19 脚）：2、3、4、10、12–22、38、39、45、46 ✅。

**外设复用核对**（CH32 p.25–26 的 Table 3-1-1、p.36–37 的 Table 3-2）：

| 外设 | 手册默认复用 | 本设计 | 结论 |
|---|---|---|---|
| I2C1 | PB6 = I2C1_SCL、PB7 = I2C1_SDA（默认复用，不需重映射） | 同 | ✅ |
| CAN1 | PA11 = CAN1_RX、PA12 = CAN1_TX（默认） | 同 | ✅（与 USBD 共用 512B SRAM，不用 USB，无冲突，p.20） |
| TIM1_CH1 | PA8 = TIM1_CH1（默认） | 同 | ✅（144MHz / 1920 = 75.000kHz；PCLK2 最高 144MHz，p.39） |
| USART1 | PA9 = TX、PA10 = RX（默认） | 同 | ✅ |
| SDI | PA13 = SWDIO、PA14 = SWCLK，复位后即为主功能（p.25、p.20 §2.5.23） | 同 | ✅ |
| FT 脚 | PB4、PB5、PB6、PB7、PA8、PB12–15 都是 FT（p.24–26） | AFE 相关的 4 根线都在 FT 脚上 | ✅ |

### U7 SN65HVD230M（HVD p.3 引脚表、p.18–19 文字、p.20 Figure 20）

| 脚 | 手册要求 | 实况 | 结论 |
|---|---|---|---|
| 1 D | 弱偏置，建议外接 1k–10k 上拉或下拉（p.19） | 接 CAN_TXD（U6.33），R53 10k 上拉到 +3V3 | ✅ 复位时为隐性 |
| 2 GND | — | GND | ✅ |
| 3 VCC | 100nF 贴脚（p.18） | +3V3，C59 100nF，C55 共用储能 | ✅ |
| 4 R | VOH ≥ 2.4V（p.5） | 接 CAN_RXD（U6.32）。PA11 是 FT 脚，VIH = 0.42 × (3.3 − 1.8) + 1 = 1.63V（CH32 p.49） | ✅ |
| 5 Vref | 不用时可悬空（p.19） | NC 标志 | ✅ |
| 6 / 7 CANL / CANH | — | CAN_L_X / CAN_H_X，经 R57 / R56（或 L2）到总线 | ✅ |
| 8 Rs | 强下拉到 GND = 高速模式（p.3） | R54 0Ω 到 GND | ✅ |

- D 脚电平：MCU 的 VOH ≥ VDD − 0.4 = 2.9V（CH32 p.50），大于 VIH 2V（HVD p.4）✅。

### U8 PESD2CAN（ESD p.1 引脚图）

- 手册：1、2 脚是两条数据线，3 脚是公共端。
- 实况：U8.1 接 CAN_H，U8.2 接 CAN_L，U8.3 接 GND ✅。
- 封装：`SOT-23-3_L2.9-W1.3-P1.90`，1、2 脚在同侧，3 脚在对侧，与手册一致 ✅。额定值见 P2-3。

### Y1 12MHz（XTAL p.1 Top View Crystal Connection）

- 手册：#1、#3 是晶体两端，#2、#4 接 GND。
- 实况：Y1.1 接 HSE_IN，Y1.3 接 HSE_OUT，Y1.2 和 Y1.4 接 GND ✅。
- 封装：焊盘 1（−1.1, +0.85）、2（+1.1, +0.85）、3（+1.1, −0.85）、4（−1.1, −0.85），与手册顶视图的 #1 左下、#2 右下、#3 右上、#4 左上一致 ✅。
- 负载电容：CL = 16.5 + 2–7 = 18.5–23.5pF，包住 20pF ✅。ESR 在 12MHz 档最大 80Ω，C0 最大 3pF ✅。

### L2 ACT1210-510（CMC p.3 Circuit Diagram）/ R56 / R57

- 手册：绕组 1–4 为一路、2–3 为另一路，1、2 在同一侧（同名端）。
- 实况：
  - L2.1 接 CAN_H_X，L2.4 接 CAN_H；
  - L2.2 接 CAN_L_X，L2.3 接 CAN_L；
  - 两路绕组同向，是共模接法 ✅（接成 1→4 与 3→2 就会变成差模扼流，那样是错的，这里没有）。
- 封装：焊盘 1、2 在同侧，间距 1.0mm；1 对 4、2 对 3 隔着本体，间距 3.14mm；外形 4.29 × 1.15 与推荐焊盘 4.1 / 2.0 / 0.6 相符 ✅。有 1 脚丝印点 ✅。
- R56 跨接 CAN_H_X 与 CAN_H，R57 跨接 CAN_L_X 与 CAN_L，都是 0Ω，与 L2 二选一 ✅。L2 为 DNP ✅。

---

## 极性件（接反即 P0）

| 位号 | 符号引脚名 | 网表 | 封装焊盘 | 手册极性 | 结论 |
|---|---|---|---|---|---|
| LED1 / LED2（C84256，符号 `FC-2012HRK-620D`） | 1 = `−`，2 = `+` | 1 脚接 R58/R59（阴极侧），2 脚接 +3V3 | `LED0805-RD`：焊盘 1 在 x = −1.1，丝印倒角和 1 脚点也在 −x 侧 | LEDR p.2：绿色阴极标记在左侧，符号三角指向左 | ✅ 阴极对阴极 |
| LED3（C2297，符号 `0805G`） | 1 = A，2 = K | 1 脚接 +3V3，2 脚接 R60 | `LED0805-R-RD`：焊盘 2 在 x = −1.05，丝印倒角和三角尖都朝 −x | LEDG p.2：①为 `+`，②为 `−`，绿色标记在②端 | ✅ |
| SW1 | 1 = A，2 = B，3 = C，4 = D | 1、2 接 KEY；3、4 接 GND | 焊盘 1、2 在同一排（y = −1.85），3、4 在另一排 | SW p.1：A–B 常通、C–D 常通，按下时两组接通；焊盘间距 6.0 / 3.7 与手册 7.0/5.0、4.5/3.0 的中心距一致 | ✅ |
| U6 / U7 / J7 / J8 | — | — | LQFP48 与 SOIC-8 都是逆时针编号，且有 1 脚点；J7、J8 的 1 脚是方形焊盘 | — | ✅ |

---

## 安全态（MCU 复位或高阻时）

| 信号 | 串在哪、并在哪 | 最坏工况 | 结论 |
|---|---|---|---|
| BAL_CLK（PA8，FT） | 本页 R52 100k 到 GND，并联 03 页第 1 节的 1M 下拉（RB），再经 R_CLK 1k 到 UD1 输入 | (3µA + 1µA) × 91k = 0.36V，小于 VT− 最小值 0.56V @VCC 2.3V（LVC p.6） | ✅ 复位即停。MCU 跑飞时 PWM 仍会输出，需要靠 IWDG（固件 X-5） |
| PRECHG_EN（PA1） | R51 100k 到 GND | 1µA × 100k = 0.1V | ✅ |
| CAN TXD（PA12） | R53 10k 到 +3V3 | 输入电流最大 10µA（HVD p.5），10µA × 10k = 0.1V 压降，D 脚约 3.2V，大于 VIH 2V，为隐性 | ✅（无 TXD 超时，见 P2-2） |
| AFE_WAKE（PB5，开漏） | 02 页 R_WAK 10k 上拉到 +3V3（BOM 第 30 行），本页没有重复放 | MCU 高阻时 NSHDN 为高，AFE 保持工作，自主保护不中断 | ✅ 语义是「MCU 复位不关 AFE」。02 页画完后要核 R_WAK 确实接在板级 +3V3 上 |
| LED1–3 | 灌电流接法 | 引脚高阻时 LED 熄灭 | ✅ |

---

## ① 电容完备性

| IC | 电源脚 | 去耦 | 结论 |
|---|---|---|---|
| U6 | 1 VBAT | C50 | ✅ |
| U6 | 9 VDDA | C51 | ✅ |
| U6 | 24 VDD_VIO_1 | C52 | ✅ |
| U6 | 36 VDD_2 | C53 | ✅ |
| U6 | 48 VDD_VIO_3 | C54 | ✅ |
| U7 | 3 VCC | C59，C55 共用储能 | ✅ |
| +3V3 轨 | — | C55 4.7µF（3.3V 偏置下约 3.5µF）加 04 页 C43 22µF | ✅ |

- U8、Y1、L2 没有电源脚。

## ② 封装下探

- 电阻 R50–R54、R56–R60 为 0402；电容 C50–C54、C56–C59 为 0402 ✅。
- R55 为 0603：卡在这一档，0402 的 62.5mW 小于最坏 75mW（P2-2），更不能下探 ✅。
- C55 为 0603：按偏压下的有效容量卡在这一档 ✅。
- LED 统一 0805：用户已接受，维持。
- 其余器件按器件本身，不适用。

## ③ 可读性

- 重叠问题见 P1-3，小项见 P2-8。
- 无越界，无废弃线（死头 0），无旧型号文字，也没有 RS485、PWR_EN 残留。
- 局部标签统一用下划线分隔，没有 `/` ✅。

## LCSC 字段与 BOM

- 32 个器件的 LCSC 字段与 `docs/02-BOM.csv` 第 67–91 行逐位号一致：
  - U6 C3001172、Y1 C9002、C56/C57 C1562、C50–C54 C1525、C55 C19666、C58 C1525、C59 C1525；
  - R50 C25744、R51/R52 C25741、R53 C25744、R54 C17168、R55 C22787、R56/R57 C17168；
  - R58/R59 C11702、R60 C25104；
  - U7 C55259679、U8 C2687131、J7 C7429634、J8 C492405（DNP）、L2 C95572（DNP）；
  - LED1/LED2 C84256、LED3 C2297、SW1 C318884。
- 唯一缺的是 JP1 C492401（P1-1）。
- 14 个封装文件在 `hardware/lib/jlc/jlc.pretty` 下全部存在。实测间距：
  - J7 2.50mm（XH，与 BOM 一致）；
  - J8 2.54mm，孔径 1.1mm；
  - LQFP48 0.5mm，SOIC-8 1.27mm。

---

## 覆盖清单（逐器件）

| 位号 | 已核对项 | 结论 |
|---|---|---|
| U6 | 48 脚逐脚、复用、电源、NRST、BOOT0、HSE、VBAT、VDDA、封装、LCSC | 无问题（ISP 见 P2-4，TIM1 复用见 P2-7） |
| U7 | 8 脚逐脚、Rs、Vref、VCC 去耦、D 上拉、电平、封装、LCSC | 无问题 |
| U8 | 引脚、封装、LCSC | 额定值见 P2-3 |
| Y1 | 脚位、封装方位、CL 算式、起振裕量 | 激励功率见 P2-1 |
| C50–C55 | 值、网络、封装、LCSC | 无问题 |
| C56 / C57 | 33pF，网络、LCSC | 无问题 |
| C58 | NRST 电容 | 无问题 |
| C59 | U7 去耦 | 无问题 |
| R50 | BOOT0 下拉 | 无问题 |
| R51 | PRECHG_EN 下拉 | 无问题 |
| R52 | BAL_CLK 下拉，已算最坏电平 | 无问题 |
| R53 | TXD 上拉 | 无问题 |
| R54 | Rs 0Ω | 无问题 |
| R55 | 终端电阻 | P1-1（JP1 待画），P2-2 |
| R56 / R57 | L2 旁路 | 无问题 |
| L2 | 绕组方向、共模接法、封装、DNP | P2-9（Value 字段） |
| R58 / R59 / LED1 / LED2 | 极性、电流 1.4mA | 无问题（引脚名重叠见 P1-3c） |
| R60 / LED3 | 极性、电流 | P2-6，P1-3c |
| SW1 | 触点对、焊盘 | 无问题 |
| J7 | 针脚（U-7 待用户确认线束）、2.50mm | 无问题 |
| J8 | 针脚、2.54mm、DNP | P2-4 |
| 跨页标签 | 契约 10 个名字、无 RS485、无 PWR_EN | 无问题；ERC 的 isolated_pin_label 待 02 页画完后复查 |
| 工程设置 | 网络类 | P1-2，P2-10 |

## 给主代理

- 按 CLAUDE.md，新结论要写回 `obsidian-vault/`。本复核只读，**没有写**。
- 建议写回以下几条：P1-2 的网络类缺口；HSE「drive current」是耗电不是晶体电流；R55 最坏功耗 75mW；J8 不能做 USART ISP。
