colemandlut/MP2645A-BMS/design/05_mcu_comm-spec.md

# 05_mcu_comm（MCU 与通讯）设计规格书 · 供画图方照画

> 时间戳：2026-09-27 00:44 UTC　编写：parts / 设计核算角色（Claude Opus）
> 纪律：本文件是本轮唯一的写入。没有改原理图、BOM、库或 docs，也没有运行 `fetch_jlc_parts.py` 或 `gen_kicad_skeleton.py`。手册用 `tools/fetch_datasheets.py` 下载到 `datasheets/`，不进 git。
> 库存、价格、基础库/扩展库一律来自 `python3 tools/jlc_api.py`（嘉立创 SMT 实时接口，**嘉立创库存**，价格为美元阶梯价），查询时间为本文时间戳。
> **页码一律是 PDF 页号**（例如 CH32 手册印刷页码 33 对应 PDF 第 38 页）。
>
> 手册简称：
>
> | 简称 | 文件 | 器件 |
> |---|---|---|
> | **CH32** | `datasheets/C3001172_WCH_CH32V203C8T6.pdf`（V2.8，64 页） | U6 CH32V203C8T6 |
> | **MP** | `datasheets/C18198873_MPS_MP2797DFP-0000-T.pdf`（Rev1.0，130 页） | 02 页 MP2797，只用它来确定 AFE 接口 |
> | **HVD** | `datasheets/C55259679.pdf`（HGSEMI V1.1，23 页） | U7 SN65HVD230M |
> | **ESD** | `datasheets/C2687131.pdf`（UMW，7 页） | U8 PESD2CAN |
> | **XTAL** | `datasheets/C9002.pdf`（YXC YSX321SL，1 页，扫描件） | Y1 12MHz |
> | **SW** | `datasheets/C318884.pdf` | SW1 TS-1187A |
> | **LEDG / LEDR** | `datasheets/C2297.pdf`、`datasheets/C84256.pdf` | LED3 绿、LED1/2 红 |
> | **CMC** | `datasheets/C95572.pdf`（TDK ACT1210） | L2 共模电感（DNP） |
> | **485** | `datasheets/C8963.pdf`（Exar SP3485） | U9（仅当 RS485 要画时用） |
>
> 接口契约（全局标签，名字以 `tools/gen_kicad_skeleton.py` 的 SHEETS 为准）：
> `I2C_SCL I2C_SDA AFE_ALERT AFE_WAKE BAL_CLK PRECHG_EN CAN_H CAN_L RS485_A RS485_B +3V3 GND`
> **RS485_A/RS485_B 是否保留，见 §9 待用户定 U-1。**

---

## 0. 结论速览（画图方先看这一节）

1. **U6 引脚分配**（详见 §1）：
   - I2C1 用默认脚 PB6/PB7，不重映射。
   - CAN1 用默认脚 PA11/PA12，不重映射。本板不用 USB，所以没有冲突。
   - BAL_CLK 用 **PA8 = TIM1_CH1**：144MHz ÷ 1920 = 75.000kHz，分频是整数，频率没有误差。
   - AFE_ALERT 接 **PB4**。选它是因为它是 5V 容忍（FT）脚，AFE 的 3V3 比 MCU 先上电时也不会往 MCU 灌电流。
   - AFE_WAKE 接 **PB5**，驱动 MP2797 的 **NSHDN**，开漏输出。
   - PRECHG_EN 接 PA1。
   - RS485 预留 PA2/PA3/PA4（USART2 + DE）。
   - LED 接 PB13/PB14/PB15，按键接 PB12。
   - SWD 用 PA13/PA14。
   - 其余 16 个脚悬空，放 NC 标志；RS485 不画时是 19 个。
2. **PWR_EN 删除**：v0.3 已取消电源自保持，LMR16006 的 SHDN 悬空即常开（docs/03 §5）。docs/03 §6 外设分配表里的 PWR_EN 需要主代理同步删掉。
3. **AFE_WAKE 就是 MP2797 的 NSHDN**：MP2797 没有叫 WAKE 的脚（MP p.5–6 引脚表）。
   - NSHDN 拉低进入关断，拉高退出关断（MP p.22）。
   - 上拉用 02 页已有的 R_WAK 10k 到 +3V3，**05 页不重复放**。
   - MCU 用开漏输出。MCU 复位时引脚高阻，NSHDN 由上拉保持为高，**AFE 不会因为 MCU 复位而关断**，FET 也不会掉。
4. **MCU 复位时各输出都进安全态**：
   - BAL_CLK：05 页加 100k 下拉（R52）。PA8 是 FT 脚，漏电流最大 3µA（CH32 p.50）；只靠 03 页的 1M 下拉，入口电平会被抬到 3V，**不够**。
   - PRECHG_EN：05 页加 100k 下拉（R51）。
   - CAN 的 TXD：05 页加 10k 上拉（R53），复位时总线保持隐性（HVD p.19）。
5. **晶振负载电容 20pF → 33pF**（C1562，基础库）：Y1 的 CL = 20pF，手册给的杂散电容是 2–7pF（CH32 p.47）。
   - 用 20pF 时有效 CL 只有 12–17pF，频率偏高约 30ppm，超出晶振 ±20ppm 的标称。
   - 用 33pF 时有效 CL 为 18.5–23.5pF，正好把 20pF 包在中间。
   - 详见 §2.4。**需要改 BOM（C_Y1/C_Y2），并且要取库。**
6. **绿灯限流电阻 1k → 330Ω**（C25104，基础库）：KT-0805G 的 VF 是 2.6–3.1V@5mA（LEDG p.2）。3.3V 串 1k 时只有 0.2–0.6mA，灯会很暗。
7. **调试口推荐 1×6 2.54mm 焊盘，默认不贴（DNP）**：顺序是 3V3 / SWDIO / SWCLK / GND / TX / RX，直接接 WCH-LinkE 的杜邦线。不贴就没有上料费，样板手焊一根排针即可。**待用户定**（U-2）。
8. **需要取库的 C 编号**（`hardware/lib/jlc/jlc.kicad_sym` 里没有）：
   - 必需：**C1562**（33pF）、**C25104**（330Ω）、**C95572**（共模电感，DNP）、**C492405**（1×6 排针封装，DNP）。
   - 视 §9 的决定而定：C8963、C32677（RS485）；C492401、C100114（终端跳线方案 B）；C2691448（1×4 排针备选）。
9. **全部新增料都是基础库或 DNP，上料费增量为 ¥0**。
   - BOM 新增 3 行基础库料：C1562、C25104、C25741。其中 C25741 已在库里，但 BOM 里的 MCU 段没有它。
   - 还有 2 行 DNP：C95572、C492405。

---

## 1. U6 CH32V203C8T6（C3001172，LQFP-48）逐脚分配

### 1.1 依据与原则

- **引脚号与名称**：CH32 p.21 的引脚图（CxT6 LQFP48），以及 p.23–26 的 Table 3-1-1 LQFP48 列，逐脚对过。
  库符号 `jlc:CH32V203C8T6` 的 48 个脚名、脚号也已逐条对过，与手册一致（例如 35=VSS_2、36=VDD_2、44=BOOT0）。
- **复位后状态**：
  - 除 OSC_IN/OSC_OUT 外，所有 GPIO 复位后都是**浮空输入**（CH32 p.23 Table 3-1-1「Main function (after reset)」列为 PAx/PBx，默认功能在参考手册的 GPIO 章节）。
  - PA13/PA14 复位后就是 SWDIO/SWCLK（p.25「Main function (after reset)」= SWDIO/SWCLK）。
  - PD0/PD1 复位后是 OSC_IN/OSC_OUT（p.35 Note 4）。
- **FT（5V 容忍）脚**：PB2、PB10–PB15、PA8–PA15、PB3–PB9（p.24–26 的「I/O structure」列为 FT）。
  - PA0–PA7、PB0、PB1、PC13–PC15 **不是** FT，输入电压上限 VDD+0.3V（p.38 Table 4-1）。
  - 漏电流：普通脚 1µA，FT 脚 3µA；内部弱上拉/弱下拉 30–50kΩ（p.50 Table 4-19）。
- **跨页信号**只在本页挂全局标签（04 页的风格：`+3V3`、`GND` 也用全局标签，不用电源符号）。页内网络用局部标签。

### 1.2 外设分配与选脚理由

| 功能 | 外设 / 脚 | 理由（依据） |
|---|---|---|
| AFE 通讯 | **I2C1：PB6=SCL、PB7=SDA**（默认，不重映射） | 两脚都是 FT（p.26）。MP2797 的 I2C 最高 400kHz，VIH = 0.7×AFE_3V3（MP p.16）。**上拉用 02 页的 R_I2C1/R_I2C2 2.2k 到 +3V3，本页不放**（BOM 第 28 行）。上升时间：设总线电容约 50pF，tr ≈ 0.8473 × 2.2k × 50pF ≈ 93ns，小于 400kHz 的上限 300ns ✅ |
| CAN | **CAN1：PA11=CAN_RX、PA12=CAN_TX**（默认映射） | 手册 p.25、p.36。**与 USB 的关系**：PA11/12 同时是 USBD 的 DM/DP，CAN 和 USBD 共用 512B 专用 SRAM（p.20 §2.5.18）；本板不用 USB，所以没有冲突。用默认映射，固件不需要配置 AFIO。PA11/12 的 HBM 是 3kV，其余脚 4kV（p.39），CAN 这两脚只在板内走线，外部 ESD 由 U8 承担。备选是 PB8/PB9（CAN1_*_2，重映射 10b），本版不用 |
| 均衡时钟 | **TIM1_CH1：PA8 → BAL_CLK** | ① 144MHz / 75kHz = 1920，取 PSC=0、ARR=1919、CCR1=960，得到 **75.000kHz、50% 占空比**，没有误差。② TIM1 是高级定时器，调试暂停时「计数器冻结、PWM 输出被禁止」（p.19），停机状态由 OIS1=0 定为低。③ MCU 复位后 PA8 是浮空输入，由 R52 100k 下拉保持为低，UD1 输入低，均衡停止（见 §1.4）。④ 用 IWDG 兜住 MCU 跑飞：定时器是硬件，MCU 死机时 PWM 会继续输出，**固件必须开 IWDG**（LSI 40kHz，与 LSE 无关），看门狗复位后 GPIO 回到浮空，均衡停止 |
| AFE 中断 | **PB4 ← AFE_ALERT**（EXTI4） | 选 FT 脚：AFE 的 3V3 由 MP2797 自己的 LDO 供电，最高 3.465V（MP p.13 ±5%），上电顺序也与本板的 buck 无关。如果接非 FT 脚，MCU 的 VDD 还没起来时，电流会经钳位二极管灌入。以 MP2797 GPIO 推挽上拉电阻 430Ω（MP p.14）估算，约 (3.3−0.6)/430 ≈ 6mA，**超过注入电流上限 ±5mA**（CH32 p.39）。PB4 与 PB5/PB6/PB7 同在芯片上边，四根 AFE 线可以一起走。代价是放弃 PA0 的 Standby 模式唤醒；固件待机用 STOP 模式（docs/03 §5），任何 EXTI 都能唤醒，不受影响 |
| AFE 唤醒 / 关断 | **PB5 → AFE_WAKE（= MP2797 NSHDN）**，开漏输出 | 见 §1.5 |
| 预充使能 | **PA1 → PRECHG_EN**，推挽输出，高电平有效 | 01 页的预充整块默认 DNP。本页 R51 100k 下拉保证复位时为低（Q20 NPN 不导通）。PA1 不是 FT，但只输出 3.3V，没有问题 |
| RS485 | **USART2：PA2=TX→DI、PA3=RX←RO；PA4 = DE/RE（GPIO）** | USART2 默认脚（p.23）。CH32 的 USART 没有 STM32F0 那种硬件 DE 模式，所以 DE 用 GPIO。**如果 RS485 本版不画（U-1），这三个脚放 NC，但不要分配给别的功能，留给下一版** |
| 调试 | **PA13 = SWDIO、PA14 = SWCLK** | 复位后默认就是这两个功能（p.25）。**固件不得把它们改成 GPIO**，否则只能用 BOOT0 救砖 |
| 调试串口（可选） | **PA9 = USART1_TX、PA10 = USART1_RX** → J8 的 5/6 脚 | WCH 的 ISP 引导程序也走 USART1（参考手册 Boot 章节）。只引到 J8 的 DNP 焊盘上，不贴件，零成本（U-2） |
| LED ×3 | **PB13 → LED1（红，故障）、PB14 → LED2（红，均衡中）、PB15 → LED3（绿，运行）**，灌电流接法、低电平点亮 | 复位时引脚浮空，LED 熄灭。见 §5 |
| 按键 | **PB12 ← SW1**，按下接 GND，用内部上拉 | 用户键（清故障、唤醒、查状态），**不是复位键**（U-4）。PB12 是 FT。去抖由固件做（≥20ms） |
| ~~PWR_EN~~ | **删除** | v0.3 取消了电源自保持与唤醒或门（docs/03 §5 SHDN 行、obsidian 方案笔记第 56 行）。LMR16006 SHDN 悬空即常开 |

### 1.3 逐脚表（48 脚，画图方逐行照画）

「处理」列的说明：
- **NC** = 引脚悬空，放「无连接」标志（快捷键 Q）。
- 固件把 NC 脚设为**带下拉的输入**（p.35 Note 5 对 PB2 有此建议，其余脚同样处理，避免 STOP 模式下浮空耗电）。

| 脚 | 名称（手册 / 库符号） | 网络名 | 方向 | 复位默认态 | 处理 / 外接 |
|---|---|---|---|---|---|
| 1 | VBAT | `+3V3` | 电源 | — | 不用备份电池，直接接 +3V3，C50 100nF 就近到 GND（Fig 4-1，p.38） |
| 2 | PC13/TAMPER_RTC | — | — | 浮空输入 | NC（PC13–15 只能输出 3mA 级弱电流，不用） |
| 3 | PC14/OSC32IN | — | — | 浮空输入 | NC（不用 LSE，见 §2.5） |
| 4 | PC15/OSC32OUT | — | — | 浮空输入 | NC |
| 5 | OSC_IN/PD0 | `HSE_IN` | 模拟 | OSC_IN（p.35 Note 4） | 接 Y1.1；C56 33pF 到 GND |
| 6 | OSC_OUT/PD1 | `HSE_OUT` | 模拟 | OSC_OUT | 接 Y1.3；C57 33pF 到 GND |
| 7 | NRST | `NRST` | 输入 | 内部上拉 30–50k（p.51） | C58 100nF 到 GND（Fig 4-7）。不另加外部上拉，不接按键（U-4） |
| 8 | VSSA | `GND` | 地 | — | 接 GND |
| 9 | VDDA | `+3V3` | 电源 | — | 接 +3V3，C51 100nF 贴脚（Fig 4-13，p.56）。VDDA 必须与 VIO 同压（p.15 §2.5.3） |
| 10 | PA0/WKUP/ADC0 | — | — | 浮空输入 | NC（非 FT，不接 AFE_ALERT，理由见 §1.2） |
| 11 | PA1/ADC1 | `PRECHG_EN`（全局） | 输出（推挽） | 浮空输入，由 R51 保持为低 | R51 100k 到 GND |
| 12 | PA2/ADC2 | `RS485_DI` | 输出（USART2_TX） | 浮空输入 | 接 U9.4（若画）；否则 NC |
| 13 | PA3/ADC3 | `RS485_RO` | 输入（USART2_RX） | 浮空输入 | 接 U9.1 + R63 10k 上拉（若画）；否则 NC |
| 14 | PA4/ADC4 | `RS485_DE` | 输出 | 浮空输入 | 接 U9.2/U9.3 + R62 10k 下拉（若画）；否则 NC |
| 15 | PA5 | — | — | 浮空输入 | NC |
| 16 | PA6 | — | — | 浮空输入 | NC |
| 17 | PA7 | — | — | 浮空输入 | NC |
| 18 | PB0 | — | — | 浮空输入 | NC |
| 19 | PB1 | — | — | 浮空输入 | NC |
| 20 | PB2/BOOT1 | — | — | 浮空输入 | NC。BOOT0=0 时 BOOT1 不起作用；固件设为下拉输入（p.35 Note 5） |
| 21 | PB10 | — | — | 浮空输入 | NC |
| 22 | PB11 | — | — | 浮空输入 | NC |
| 23 | VSS_1 | `GND` | 地 | — | 接 GND |
| 24 | VDD_VIO_1 | `+3V3` | 电源 | — | C52 100nF 贴 23/24 脚 |
| 25 | PB12 | `KEY` | 输入（内部上拉） | 浮空输入 | 接 SW1 的 A/B 脚（SW1 的 C/D 脚接 GND） |
| 26 | PB13 | `LED1_K` | 输出（灌电流） | 浮空输入，LED 灭 | 接 R58 1k → LED1 阴极 |
| 27 | PB14 | `LED2_K` | 输出（灌电流） | 浮空输入，LED 灭 | 接 R59 1k → LED2 阴极 |
| 28 | PB15 | `LED3_K` | 输出（灌电流） | 浮空输入，LED 灭 | 接 R60 330Ω → LED3 阴极 |
| 29 | PA8 | `BAL_CLK`（全局） | 输出（TIM1_CH1 PWM） | 浮空输入，由 R52 保持为低 | R52 100k 到 GND，放在 MCU 旁 |
| 30 | PA9 | `DBG_TX` | 输出（USART1_TX） | 浮空输入 | 接 J8.5（DNP 焊盘） |
| 31 | PA10 | `DBG_RX` | 输入（USART1_RX） | 浮空输入 | 接 J8.6（DNP 焊盘） |
| 32 | PA11/USB1DM | `CAN_RXD` | 输入（CAN1_RX） | 浮空输入 | 接 U7.4（R） |
| 33 | PA12/USB1DP | `CAN_TXD` | 输出（CAN1_TX） | 浮空输入，由 R53 保持隐性 | 接 U7.1（D）+ R53 10k 上拉到 +3V3 |
| 34 | PA13/SWDIO | `SWDIO` | 双向 | SWDIO | 接 J8.2 |
| 35 | VSS_2 | `GND` | 地 | — | 接 GND |
| 36 | VDD_2 | `+3V3` | 电源 | — | C53 100nF 贴 35/36 脚 |
| 37 | PA14/SWCLK | `SWCLK` | 输入 | SWCLK | 接 J8.3 |
| 38 | PA15 | — | — | 浮空输入 | NC |
| 39 | PB3 | — | — | 浮空输入 | NC |
| 40 | PB4 | `AFE_ALERT`（全局） | 输入（EXTI4） | 浮空输入 | 直连，外接电阻在 02 页（R_ALT，见 X-2） |
| 41 | PB5 | `AFE_WAKE`（全局） | 输出（**开漏**） | 浮空输入；02 页 R_WAK 上拉使 NSHDN 为高，AFE 保持工作 | 直连，上拉在 02 页（R_WAK 10k） |
| 42 | PB6 | `I2C_SCL`（全局） | 开漏（I2C1_SCL） | 浮空输入 | 直连，上拉在 02 页 |
| 43 | PB7 | `I2C_SDA`（全局） | 开漏（I2C1_SDA） | 浮空输入 | 直连，上拉在 02 页 |
| 44 | BOOT0 | `BOOT0` | 输入 | — | R50 10k 到 GND（从用户 Flash 启动）。p.35 Note 6 建议 4.7k，那条是针对 BOOT0/PB8 合封的型号；LQFP48 的 BOOT0 是独立脚，10k 足够，并与 BOM 一致 |
| 45 | PB8 | — | — | 浮空输入 | NC（可留作 CAN_STB 控制，见 U-5） |
| 46 | PB9 | — | — | 浮空输入 | NC |
| 47 | VSS_3 | `GND` | 地 | — | 接 GND |
| 48 | VDD_VIO_3 | `+3V3` | 电源 | — | C54 100nF 贴 47/48 脚 |

**统计**：
- 电源/地 9 脚：1、8、9、23、24、35、36、47、48。
- 时钟/复位/启动 4 脚：5、6、7、44。
- 用到的 GPIO 19 脚：PA1、PA2、PA3、PA4、PA8、PA9、PA10、PA11、PA12、PA13、PA14、PB4、PB5、PB6、PB7、PB12、PB13、PB14、PB15。其中 PA9/PA10 只接 J8 的 DNP 焊盘，也算已连接。
- **NC 16 脚**：2、3、4、10、15、16、17、18、19、20、21、22、38、39、45、46。**RS485 不画（U-1 选①）时再加 12、13、14，共 19 脚。**
- 核对：9 + 4 + 19 + 16 = 48 ✅

### 1.4 每个信号的方向、复位默认态与安全态核算

| 信号 | 方向（MCU 视角） | MCU 复位 / 死机时的电平 | 核算 |
|---|---|---|---|
| BAL_CLK | 出 | **低**（R52 100k 下拉）→ 均衡停止 | PA8 是 FT 脚，漏电最大 3µA（p.50）。只靠 03 页的 RB1 1M：3µA × 1M = 3.0V，**可能被判成高电平** ✗。加 R52 后下拉为 100k∥1M = 91k，3µA × 91k = **0.27V**，低于 74LVC1G17 在 VCC≥2.3V 时的负向阈值（UD1 手册 VT− 最小值约 0.6V 量级），可判为低 ✅。正常输出时，100k 负载只多 33µA |
| PRECHG_EN | 出 | **低**（R51 100k 下拉） | PA1 漏电 1µA × 100k = 0.1V ✅。01 页 Q20 的基极网络 DNP 与否都不影响 |
| AFE_WAKE | 出（开漏） | **高**（02 页 R_WAK 10k 到 +3V3）→ AFE 保持工作 | NSHDN 内部下拉 5MΩ（MP p.14），分压得 3.31 × 5M/(5M+10k) = **3.30V** > 退出关断门限 2.65V（MP p.14）✅。MCU 拉低时 VOL < 0.4V，低于门限 1V，灌电流 0.33mA ✅。进入关断有 8ms 去抖（MP p.14）。从关断唤醒后，**至少等 5ms 再发 I2C**（MP p.22）。**固件严禁把 PB5 配成推挽**：推挽高电平也能工作，但会失去复位时的上拉保护语义 |
| AFE_ALERT | 入 | 取决于 02 页 R_ALT，MCU 内部下拉 | 见 §1.5 与 X-2 |
| I2C_SCL/SDA | 开漏 | 高（02 页上拉） | — |
| CAN_TXD | 出 | **高 = 隐性**（R53 10k 上拉） | HVD 的 D 脚内部偏置很弱，p.19 建议外加 1k–10k。浮空时如果被噪声拉到显性，会阻塞整条总线 |
| LED1–3 | 出（灌电流） | 高阻 → 灭 | — |
| KEY | 入 | 内部上拉 | — |

### 1.5 AFE_WAKE / AFE_ALERT 的接法依据（MP2797）

- **MP2797 没有 WAKE 脚**。与主机相关的脚只有这些（MP p.5–7）：xALERT（28）、WDT（29）、NSHDN（30）、SCL（31）、SDA（32）、SDO（33）、GPIO3/nCS（34）。
  - NSHDN 是「Active-low shutdown input」（p.6）。拉低进入关断，拉高进入安全模式（p.22）。
  - 所以契约里的 **AFE_WAKE = NSHDN，高电平 = AFE 工作**。网络名保持不变，含义与电平方向一致。
  - NSHDN 的绝对最大值是 9V（p.7），3.3V 驱动没有问题。
  - **7.6V 是 MTP 编程电压**（VNSHDN_PROG，p.14），本板不产生这个电压，没有风险。
- **WDT（29 脚）不接 MCU**：它在咬狗事件时输出 10ms 的**高**脉冲（p.14、p.24），而 CH32 的 NRST 是低有效，直接接会反相。
  - 按 MP Table 23（p.127）的「Float this pin if it is not used」悬空（由 02 页处理）。
  - 所以 docs/03 §3.1「WDT 开漏上拉 10kΩ」一句需要 02 页复核：WDT 不用就不上拉。
- **xALERT 是推挽输出，不是开漏**：手册写「configured to be an active high **(3.3V)** or active low」（p.24）。**OTP 默认 ALERT_POL = 1，即高有效**（p.48 PINS_CFG 0x0D Bit[0]，Reset 0x1）。
  - 02 页 BOM 的 R_ALT 是「开漏上拉 10k」。在默认的高有效模式下，空闲时引脚被 AFE 拉低，10k 上拉就会**持续消耗 0.33mA**，这对待机目标 < 300µA 是明显的负担。
  - 交 02 页定夺，见 X-2。
  - **本页不管 02 页怎么选，都只做直连 + MCU 内部下拉。**

---

## 2. 电源与时钟外围（规则 00 ①、①a）

### 2.1 电源脚逐一点名去耦（CH32 Fig 4-1 p.38、Fig 4-13 p.56）

手册的典型电源方案（Fig 4-1）：
- 每对 VDDx/VSSx 一颗 0.1µF；
- VDDA/VSSA 一颗 0.1µF；
- VBAT 接 1.8–3.6V 电源。本板不用备份电池，VBAT 接 +3V3，并加一颗 100nF（这是常规做法；手册只说 VBAT 是「Optional backup power supply」，p.15）。

| 电源脚 | 配对地脚 | 去耦 | 位号 | 摆放 |
|---|---|---|---|---|
| 1 VBAT | 47 VSS_3（就近 GND 过孔） | 100nF 0402 C1525 | C50 | 贴 1 脚 |
| 9 VDDA | 8 VSSA | 100nF 0402 C1525 | C51 | 贴 8/9 脚之间 |
| 24 VDD_VIO_1 | 23 VSS_1 | 100nF 0402 C1525 | C52 | 贴 23/24 脚 |
| 36 VDD_2 | 35 VSS_2 | 100nF 0402 C1525 | C53 | 贴 35/36 脚 |
| 48 VDD_VIO_3 | 47 VSS_3 | 100nF 0402 C1525 | C54 | 贴 47/48 脚 |
| +3V3（MCU 区整体） | GND | 4.7µF 0603 16V C19666 | C55 | MCU 与 U7 之间，两者共用 |

- 5 个电源脚对应 5 颗 100nF（BOM 的 C_DEC1–5 共 5 颗），与手册一致 ✅。
- **VDDA 不加磁珠**：本板 ADC 不采精密量（电芯电压、温度都由 AFE 采），而且手册要求 VDDA 与 VIO 同压（p.15）。
- **C55 容量核算**：
  - 4.7µF/16V X5R 0603 在 3.3V 偏置下约剩 3.5µF。
  - 最大负载阶跃按 CAN 显性 ≈ 2V/60Ω ≈ 33mA、持续 2µs 计：ΔV = I·t/C = 33mA × 2µs / 3.5µF ≈ **19mV** ✅。
  - 另外 04 页 C43（22µF，有效约 10µF）也在这条 +3V3 轨上。

### 2.2 NRST（CH32 Fig 4-7 p.51、Table 4-22 p.50）

- 手册电路是：NRST 接 0.1µF 到地，另有一只可选按键到地，芯片内部上拉 RPU 30–50kΩ。
- 本设计：**C58 100nF 0402（C1525）接 NRST–GND，不加外部上拉，不接按键**（U-4）。
- 核算：
  - τ = 40k × 100nF = 4ms。
  - 芯片内部上电复位延时 tRSTTEMPO = 24–30ms（p.40），比 τ 长得多，RC 只起滤波作用。
  - 滤波脉宽 100ns 以内的毛刺被滤掉（p.51 VF(NRST)）。
- NRST 不引到 J8：CH32V203 的 2 线调试不需要 NRST。WCH-LinkE 靠 SWD 命令复位。

### 2.3 BOOT0

R50 10k 0402（C25744）接 BOOT0–GND，从用户 Flash 启动。PB2/BOOT1 悬空（BOOT0 = 0 时 BOOT1 不起作用）。依据：p.35 Note 5/6。

### 2.4 HSE 12MHz：Y1 C9002 与负载电容核算

**晶振参数**（XTAL；嘉立创接口也返回「12MHz 20pF 80Ω ±10ppm ±20ppm」）：

| 参数 | 值 |
|---|---|
| CL | 20pF |
| 12MHz 档 ESR 最大 | 80Ω |
| C0 最大 | 3pF |
| 激励功率 | 10–200µW |
| 脚位 | **1、3 = 晶体两端，2、4 = GND**（库符号：1 OSC1 / 2 GND / 3 OSC2 / 4 GND） |

**负载电容公式**（CH32 p.47）：CL = CL1·CL2/(CL1+CL2) + Cstray，Cstray 典型值 **2–7pF**。取 CL1 = CL2 = C：

- C = 2 × (CL − Cstray) = 2 × (20 − 2…7) = **26–36pF**，取中值约 31pF。

| 选项 | 有效 CL（Cstray 2–7pF） | 结论 |
|---|---|---|
| BOM 现值 **20pF C1554** | 10 + 2…7 = **12–17pF** | 偏小 3–8pF。频偏 Δf/f ≈ (C1/2)·[1/(C0+CL′) − 1/(C0+CL)]，C1 取 12MHz 3225 典型值约 5fF、C0 = 3pF、CL′ = 14.5pF：Δf/f = 2.5fF × (1/17.5 − 1/23)pF⁻¹ ≈ **+34ppm**，超出晶振 ±20ppm 的标称（对 CAN 500k 的 0.1% 级容差仍够用）|
| **推荐 33pF C1562**（0402 C0G，**基础库**，库存 1 103 358，$0.0039） | 16.5 + 2…7 = **18.5–23.5pF** | 20pF 落在区间中间 ✅，不增加上料费 |
| 30pF C1570 | 17–22pF | 扩展库，不选 |
| 27pF C1557 | 15.5–20.5pF | 扩展库，不选 |

**起振裕量**：
- 临界跨导 gm_crit = 4·ESR·(2πf)²·(C0+CL)² = 4 × 80 × (2π × 12MHz)² × (23pF)² ≈ **0.96mA/V**。
- 手册给的 gm = 17.5mA/V（p.46 Table 4-11），裕量 **18 倍**（要求 ≥ 5）✅。

**激励功率**：
- 手册给的 HSE 驱动电流是 0.53mA @20pF（p.46）。
- P = ESR·I² = 80 × (0.53mA)² ≈ **22µW**，小于晶振上限 200µW ✅。
- 不需要串联限流电阻 Rext。

**PLL**：HSE 12MHz × 12 = 144MHz。PLL 输入范围 3–25MHz（p.48 Table 4-15），12MHz 在范围内 ✅。固件 HSE_VALUE = 12MHz（BOM 第 67 行备注）。

**⚠ 这一条需要改 BOM**：C_Y1/C_Y2 由 C1554 20pF 改为 **C1562 33pF**。按规则 0b，先改原理图再改 BOM，由主代理报用户确认（见 U-6）。

### 2.5 LSE：不需要

- RTC 不要求走时（时间戳由上位机给）。IWDG 用内部 LSI 40kHz（p.47），不依赖 LSE。
- PC14/PC15 放 NC。
- 如果日后需要 RTC 计时，另加 32.768kHz 晶振 + 2×12pF（p.47 推荐约 12pF）。本版不做。

### 2.6 功耗与待机（报告性质）

| 负载 | 电流 |
|---|---|
| MCU 运行 | 约 10–20mA（p.41–43） |
| CAN 收发器隐性 | 1–2mA，显性 ≈ 35mA（HVD p.5，加 60Ω 负载） |
| LED | 每只 1–2mA |

**待机的一个硬伤（报用户，U-5）**：
- SN65HVD230 即使把 Rs 拉到高电平进入 Standby，也要 **400µA 典型 / 600µA 最大**（HVD p.5 ICC Standby）。
- 本版 Rs 经 0Ω 接地（常在高速模式），隐性状态就要 1–2mA。
- **单这一颗就已经超过 docs/03 §5 的待机目标 < 300µA**。
- 如果目标必须满足，要给 U7 的 VCC 加 P-MOS 开关（例如 AO3401A C15127，已在库），由 MCU 控制。本规格书不加这颗管，只点出问题。

---

## 3. CAN（U7 / U8 / 终端 / 共模电感 / J7）

### 3.1 信号链与顺序（规则 0c：连接器 → ESD → 芯片）

```
J7.1 CAN_H ─┬─ U8.1 ─┬─ R55 120Ω ─ [终端选择，见 U-3] ─┬─ R56 0Ω ─ CAN_H_X ─ U7.7 CANH
J7.2 CAN_L ─┴─ U8.2 ─┴────────────────────────────────┴─ R57 0Ω ─ CAN_L_X ─ U7.6 CANL
            U8.3 → GND                                 └─ L2 共模电感（DNP，与 R56/R57 并联占位：L2.1–L2.4 串在 CAN_H，L2.2–L2.3 串在 CAN_L）
```

- 全局标签 `CAN_H`/`CAN_L` 挂在 J7 一侧（连接器、ESD、终端都在这个网络上）。
- 收发器一侧用局部标签 `CAN_H_X`/`CAN_L_X`。
- **终端放在共模电感的连接器侧**：终端属于总线本身，不应隔着电感。
- **⚠ 需要主代理配合改网络类**：`CAN_DIFF` 目前只匹配 `CAN_H`、`CAN_L`、`RS485_A`、`RS485_B` 四个名字（gen_kicad_skeleton.py 第 63 行）。要把 `CAN_H_X`/`CAN_L_X` 加进去（见 X-3）。

### 3.2 U7 HGSEMI SN65HVD230M/TR-HG（C55259679，SOP-8）逐脚

依据：HVD p.3 引脚表。库符号 `jlc:SN65HVD230M_TR-HG` 的脚名、脚号逐条对过，一致。

| 脚 | 名称 | 接法 | 依据 |
|---|---|---|---|
| 1 | D（TXD） | `CAN_TXD` ← U6.33（PA12）；**R53 10k 上拉到 +3V3** | p.19：「internal pull up and pull down biasing … is weak … an external 1k to 10k ohm pull-up or down resistor should be used」 |
| 2 | GND | GND | — |
| 3 | VCC | +3V3，**C59 100nF 0402 贴脚** | 工作电压 3–3.6V（p.4）。p.19 Figure 20 的 C2/C3 是旁路 + 储能：储能由 C55 4.7µF 共用（距离 ≤ 10mm） |
| 4 | R（RXD） | `CAN_RXD` → U6.32（PA11），直连 | 推挽输出，VOH ≥ 2.4V（p.5）。R2 串阻可选，不加 |
| 5 | Vref | **NC**（放无连接标志） | p.19：「If this feature is not used, the pin can be left floating」。本版不用分裂终端，Vref 无用 |
| 6 | CANL | `CAN_L_X` | — |
| 7 | CANH | `CAN_H_X` | — |
| 8 | Rs | **R54 0Ω（C17168）到 GND = 高速模式** | p.3：「strong pull down to GND = high speed mode … 10kΩ to 100kΩ = slope control」。BOM 第 74 行 R_RS = 0Ω，用户已定。保留焊盘，EMC 过不了时改 10k–47k 限斜率 |

### 3.3 U8 UMW PESD2CAN（C2687131，SOT-23）

- 引脚（ESD p.1 Pinning）：**1、2 = 两条数据线（对称，可互换），3 = 公共端接 GND**。库符号 `PESD2CAN_C2687131` 的脚名只有 1/2/3，按此接：**1 → CAN_H、2 → CAN_L、3 → GND**。
- 参数（ESD p.3）：VRWM 24V、VBR ≥ 26.1V、钳位 41V@5A、Cj 25pF。
  - CAN 共模工作范围 −2…7V（HVD p.4），VRWM 24V 足够。
  - 钳位电压 41V@5A 比收发器总线脚的绝对最大值 ±40V（HVD p.4）**高 1V**。但 41V 是 5A、8/20µs 大脉冲下的值，常见的 ESD 事件电流远小于此；收发器总线脚本身还有 HBM ±16kV（HVD p.4）。这是业界通用组合（Nexperia 原型号参数相同），接受，并在此记录。
- 摆放：**紧贴 J7**，GND 脚打两颗过孔到 In1 地平面（HVD p.19「Use at least two Vias」）。

### 3.4 终端 R55 120Ω 0603（C22787，基础库）

- 功耗：显性 VOD ≈ 2V（HVD p.5 典型值），P = 2²/120 = **33mW**。
  - 0603 额定 100mW，余量 3 倍 ✅。
  - 0402 额定 62.5mW 余量不足 2 倍，所以不下探（规则 00 ② 原例）。
- 「跳线可选」的三个实现方案，**待用户定（U-3）**：

| 方案 | 做法 | 料号 | 成本 | 优缺点 |
|---|---|---|---|---|
| **A（默认推荐）** | 只放 R55，下单时决定贴不贴（BMS 通常是总线一端，默认**贴**） | R55 C22787 | ¥0 | 零成本。现场要改只能用烙铁拆 0603 |
| B | R55 串 JP1 2P 2.54 排针 + 跳线帽 | JP1 **C492401** PZ254V-11-02P（扩展库，库存 1 305 855，$0.0186）+ 跳线帽 **C100114**（扩展库，库存 588 290，$0.0093，手工装） | 贴装时 +1 种扩展料上料费（¥8–20）；排针也可样板手焊 | 现场插拔可改。跳线帽会被振动震掉，需要打胶 |
| C | R55 串一个焊盘桥（常开，需要时用焊锡短接） | 无 C 编号，属规则 0e「非嘉立创件」，需用户批准手画 | ¥0 | 现场可改。违反「只用嘉立创库」，需用户裁定 |

### 3.5 共模电感 L2（DNP 预留）+ 旁路 R56/R57

- **L2：TDK ACT1210-510-2P-TL00，C95572**。
  - 51µH@100kHz，200mA，80V，AEC-Q200，是专为 CAN 设计的系列（CMC p.1）。
  - 扩展库，库存 10 907，$0.6464。**DNP**：不贴就不收上料费。
  - 绕组：**1–4 为一路、2–3 为另一路**（CMC p.3 外形图：1、2 在左，4、3 在右，线圈横向）。所以 CAN_H 走 1→4，CAN_L 走 2→3。
  - 备选 C48928231（ACT1210-510 仿制型号，$0.238，库存 1 469）。
- **R56、R57：0Ω 0402（C17168，基础库，已在库）**，默认贴装，分别跨接 CAN_H↔CAN_H_X、CAN_L↔CAN_L_X。
- 装 L2 时**必须同时拆掉 R56/R57**。画图时在这组器件旁加文字注释：「L2 与 R56/R57 二选一」。
- 布局：R56/R57 的焊盘紧挨 L2 的焊盘，放在同一段直线通道上。L2 属于电感，**下方禁铜**（规则 2d）。

### 3.6 J7 XH 2.50mm 4P 立式（C7429634，扩展库，库存 1 178 916）

- 封装已实测为 2.50mm（BOM 第 77 行）。库封装是 `jlc:CONN-TH_4P-P2.50_4PIN`。取库方仍需用 `fp_compare.py` 回读焊盘间距与 1 脚标记（规则 0d）。
- **针脚定义（推荐，待用户对照对端线束确认，U-7）**：

| 针 | 网络 | 理由 |
|---|---|---|
| 1 | CAN_H | 差分对放在相邻的 1/2 针，线束可以用双绞线直接压接，两针之间没有其它信号 |
| 2 | CAN_L | 同上 |
| 3 | GND（CAN_GND） | ISO 11898 要求节点之间共地（收发器共模范围只有 −2…7V，HVD p.4）。没有 CAN_GND，逆变器与 BMS 的地电位差会让通讯出错 |
| 4 | GND（屏蔽 / 排扰线） | 给屏蔽双绞线的排扰线一个落点，同时第二根地线降低回流阻抗。XH 带防反插结构，不存在插反问题。**不留 NC**：悬空针会在 ESD 测试时成为放电点，也容易被对端误接 |

- 说明：CAN_GND = GND = BAT−（分流器电池侧）。
  - 逆变器的 DC− 接 PACK−，两者之间只隔着分流器，满载时压差 = 200A × 0.1mΩ = 20mV，远在收发器共模范围内。
  - CAN 地线会与分流器并联一条旁路：若线束地线电阻约 0.1Ω，旁路电流约 0.2A，相当于 200A 的 0.1%，对计量的影响可以忽略。**不需要隔离。**

---

## 4. 缺料补齐（BOM 里没有的）

### 4.1 调试口（docs/03 原写 SWD 2×5 1.27mm）

**评估**：
- CH32V203 的调试接口是 2 线 SWDIO/SWCLK，没有 JTAG（p.25）。
- WCH 官方下载器 WCH-LinkE 用的是 2.54mm 杜邦针。
- 2×5 1.27mm 是 ARM Cortex Debug 的标准口：用 WCH-LinkE 时需要转接线，料也贵（C22438120 $0.084），而且只有扩展库。
- **结论：改用 2.54mm 单排。**

| 方案 | 料号 | 库 | 嘉立创库存 | 单价 | 结论 |
|---|---|---|---|---|---|
| **推荐：J8 1×6 2.54mm 直插，DNP（只留焊盘）** | **C492405** PZ254V-11-06P | 扩展 | 105 498 | $0.0405 | 零上料费。样板手焊排针，量产用弹簧顶针夹具直接压焊盘 |
| 1×4 2.54mm（只接 SWD） | **C2691448** PZ254V-11-04P | 扩展 | 1 009 513 | $0.0273 | 备选，少了调试串口 |
| 2×5 1.27mm 直插 | C22438120 HX PZ1.27-2x5P ZZ | 扩展 | 29 831 | $0.0843 | 不推荐（需转接线、贵、间距小不便手焊） |
| 2×5 1.27mm 贴片 | C41376037 | 扩展 | 52 769 | $0.097 | 不推荐 |

- **J8 针脚**：1 = +3V3（仅作参考电平），2 = SWDIO（PA13），3 = SWCLK（PA14），4 = GND，5 = DBG_TX（PA9），6 = DBG_RX（PA10）。
- 丝印要标注每一针的功能。
- ⚠ 板子由电池供电时，**下载器不要从 1 脚往板上供电**（WCH-LinkE 可关断 3V3 输出），否则两路 3.3V 电源会对顶。在丝印旁加注。
- **取库规则**：C492405 取回后，用 `fp_compare.py` 实测间距必须是 **2.54mm**（规则里 XH 2.50mm 冒充 2.54mm 的教训），孔径约 1.0mm。这是板端件（公针座），不是线束件。

### 4.2 RS485（DNP 预留，还是本版不画）—— **待用户定（U-1）**

**如果要画**，全部用基础库，贴装时也不收上料费：

| 位号 | 料号 | 型号 | 库 | 嘉立创库存 | 单价 | 说明 |
|---|---|---|---|---|---|---|
| U9 | **C8963** | SP3485EN-L/TR（MaxLinear/Exar），3.3V 半双工，10Mbps，SOIC-8 | **基础** | 322 778 | $0.2661 | 引脚（485 p.4）：1 RO / 2 RE（低有效）/ 3 DE（高有效）/ 4 DI / 5 GND / 6 A / 7 B / 8 VCC |
| D8 | **C32677** | PSM712-LF-T7（Protek），RS485 专用非对称 TVS（−7V/+12V），600W，SOT-23 | **基础** | 150 515 | $0.3227 | 紧贴连接器 |
| C60 | C1525 | 100nF 0402 | 基础 | — | — | U9.8 去耦 |
| R61 | C22787 | 120Ω 0603 终端 | 基础 | — | — | 默认 DNP |
| R62 | C25744 | 10k 0402 | 基础 | — | — | RE/DE 下拉：复位时处于接收态，驱动器高阻 |
| R63 | C25744 | 10k 0402 | 基础 | — | — | RO 上拉：发送态 RE=1 时 RO 高阻，USART RX 不浮空 |

**推荐：本版不画，并从接口契约中删除 RS485_A/RS485_B。** 理由：
1. **没有连接器落点**：J7 的 4 针已经给了 CAN（§3.6），RS485 还需要另一个 3P/4P 端子，而本页契约里没有它。
   如果只画全局标签 RS485_A/B，其它页不会引用，ERC 会报「全局标签只出现一次」。
2. **协议未定**：docs/03 §0 写着「RS485 可选（DNP），对接逆变器协议待定」。CAN 是主通讯口。
3. **板面**：目标 130×90mm（docs/00 0f），右侧通讯区还要放 CAN 的直通道。
4. **保留升级路径**：PA2/PA3/PA4（USART2 + DE）不挪作他用，下一版可以直接加。

如果用户选择「画」：J7 改为 XH 6P，或另加 J9 XH 3P（A/B/GND），料号由取库方再查。

---

## 5. LED 与按键

- **接法：灌电流、低电平点亮**。LED 阳极接 +3V3，阴极经电阻接 MCU。MCU 复位时引脚高阻，LED 熄灭；不需要下拉。

| 位号 | 颜色 / 料号 | VF（手册） | 限流 | 电流核算（MCU 灌电流 VOL ≈ 0.1V） |
|---|---|---|---|---|
| LED1 | 红 NCD0805R1 **C84256**（基础） | 2.0（1.5–2.6）V @20mA（LEDR p.1） | R58 1k C11702 | 低电流时 VF 约 1.8V：(3.3 − 0.1 − 1.8)/1k ≈ **1.4mA** ✅ |
| LED2 | 同上 | 同上 | R59 1k C11702 | 同上 |
| LED3 | 绿 KT-0805G **C2297**（基础） | **2.6–3.1V @5mA**（LEDG p.2） | **R60 330Ω C25104**（基础，BOM 原为 1k） | VF 在低电流时约 2.5–2.8V：(3.2 − 2.5…2.8)/330 ≈ **1.2–2.1mA** ✅。原来用 1k 时只有 0.2–0.7mA，亮度只有 5mA 时的 1/10 左右 ✗ |

- **⚠ 两种 LED 符号的引脚号定义相反，必须按引脚名接**：
  - C84256 的库符号叫 `FC-2012HRK-620D`，**1 脚是「−」（阴极）、2 脚是「+」**。
  - C2297 的库符号 `0805G`，**1 脚是 A（阳极）、2 脚是 K（阴极）**。
  - 另外，C84256 的库符号名（FC-2012HRK-620D）与嘉立创型号（NCD0805R1）不一致。**取库方需用 `fp_compare.py` 核对封装极性标记与 NCD0805R1 手册的阴极标记是否同侧**（规则 2 第 0 条「极性丝印」）。
- **SW1 TS-1187A-B-A-B（C318884，基础）**：
  - SW p.1 内部连接：**A–B 常通、C–D 常通，按下时 AB 与 CD 接通**。
  - 库符号 1=A、2=B、3=C、4=D；封装焊盘 1(−3,−1.85)、2(3,−1.85)、3(−3,1.85)、4(3,1.85)，上排 A/B、下排 C/D，与手册的 PCB layout 一致。
  - 接法：**1、2 → KEY（PB12）；3、4 → GND**。四脚都要接，不要留一对悬空，否则焊盘是孤岛。
  - 触点额定 50mA/12V，本处电流约 80µA ✅。

---

## 6. 完整器件表（05 页）

位号规则：IC、晶振、连接器、LED、按键沿用 BOM 位号（U6/U7/U8/Y1/J7/SW1/LED1–3）；无源件按 04 页先例改为「前缀 + 数字」的 5x 段；新增件接着 BOM 已用的号往下排（J8、L2、U9、D8、JP1）。

| 新位号 | BOM 旧位号 | 值 | LCSC | 库 | 符号（jlc.kicad_sym） | 封装 | 状态 |
|---|---|---|---|---|---|---|---|
| U6 | U6 | CH32V203C8T6 | C3001172 | 扩展 | `jlc:CH32V203C8T6` ✅ | `jlc:LQFP-48_L7.0-W7.0-P0.50-LS9.0-BL` | 贴 |
| Y1 | Y1 | 12MHz 20pF ±20ppm | C9002 | 基础 | `jlc:X322512MSB4SI` ✅ | `jlc:CRYSTAL-SMD_4P-L3.2-W2.5-BL` | 贴 |
| C56, C57 | C_Y1, C_Y2 | **33pF** 50V C0G 0402（原 20pF C1554） | **C1562** | 基础 | ❌ **需取库**（0402CG330J500NT） | C0402 | 贴（**改 BOM**） |
| C50–C54 | C_DEC1–5 | 100nF 16V X7R 0402 | C1525 | 基础 | `jlc:CL05B104KO5NNNC` ✅ | `jlc:C0402` | 贴 |
| C55 | C_BULK | 4.7µF 16V X5R 0603 | C19666 | 基础 | `jlc:CL10A475KO8NNNC` ✅ | `jlc:C0603` | 贴 |
| C58 | —（新增） | 100nF 0402（NRST） | C1525 | 基础 | ✅ | C0402 | 贴（**BOM 新增**） |
| C59 | C_CAN | 100nF 0402 | C1525 | 基础 | ✅ | C0402 | 贴 |
| R50 | R_BOOT | 10k 1% 0402 | C25744 | 基础 | `jlc:0402WGF1002TCE` ✅ | `jlc:R0402` | 贴 |
| R51 | —（新增） | 100k 1% 0402（PRECHG_EN 下拉） | C25741 | 基础 | `jlc:0402WGF1003TCE` ✅ | R0402 | 贴（**BOM 新增**） |
| R52 | —（新增） | 100k 1% 0402（BAL_CLK 下拉） | C25741 | 基础 | ✅ | R0402 | 贴（**BOM 新增**） |
| R53 | —（新增） | 10k 1% 0402（CAN_TXD 上拉） | C25744 | 基础 | ✅ | R0402 | 贴（**BOM 新增**） |
| R54 | R_RS | 0Ω 0402 | C17168 | 基础 | `jlc:0402WGF0000TCE` ✅ | R0402 | 贴 |
| R55 | R_T | 120Ω 1% 0603 | C22787 | 基础 | `jlc:0603WAF1200T5E` ✅ | `jlc:R0603` | 贴（U-3） |
| R56, R57 | —（新增） | 0Ω 0402（L2 旁路） | C17168 | 基础 | ✅ | R0402 | 贴（**BOM 新增**） |
| R58, R59 | R_LED_A, R_LED_B | 1k 1% 0402 | C11702 | 基础 | `jlc:0402WGF1001TCE` ✅ | R0402 | 贴 |
| R60 | R_LED_C | **330Ω** 1% 0402（原 1k） | **C25104** | 基础 | ❌ **需取库**（0402WGF3300TCE） | R0402 | 贴（**改 BOM**） |
| U7 | U7 | SN65HVD230M/TR-HG | C55259679 | 扩展 | `jlc:SN65HVD230M_TR-HG` ✅ | `jlc:SOIC-8_L5.0-W4.0-P1.27-LS6.0-BL` | 贴 |
| U8 | U8 | PESD2CAN | C2687131 | 扩展 | `jlc:PESD2CAN_C2687131` ✅ | `jlc:SOT-23-3_L2.9-W1.3-P1.90-LS2.4-BR` | 贴 |
| L2 | —（新增） | ACT1210-510-2P 51µH CMC | **C95572** | 扩展 | ❌ **需取库** | 取回的 SMD-4P 3.2×2.5 | **DNP** |
| J7 | J7 | XH 2.50mm 4P 立式 | C7429634 | 扩展 | `jlc:ZX-XH2.54-4PZZ` ✅ | `jlc:CONN-TH_4P-P2.50_4PIN` | 贴 |
| J8 | —（新增，取代「SWD 2×5 1.27」） | 1×6 2.54mm 直针 | **C492405** | 扩展 | ❌ **需取库** | 取回的 1×6 P2.54 | **DNP**（U-2） |
| LED1, LED2 | LED1, LED2 | 红 0805 | C84256 | 基础 | `jlc:FC-2012HRK-620D` ✅（名不符，见 §5） | `jlc:LED0805-RD` | 贴 |
| LED3 | LED3 | 绿 0805 | C2297 | 基础 | `jlc:0805G` ✅ | `jlc:LED0805-R-RD` | 贴 |
| SW1 | SW1 | 5.1×5.1 轻触开关 | C318884 | 基础 | `jlc:TS-1187A-B-A-B` ✅ | `jlc:SW-SMD_4P-L5.1-W5.1-P3.70-LS6.5-TL_H1.5` | 贴 |
| JP1 | — | 2P 2.54 + 跳线帽 | C492401 + C100114 | 扩展 | ❌ 需取库 | — | **仅方案 B**（U-3） |
| U9 | — | SP3485EN-L/TR | C8963 | 基础 | ❌ 需取库 | SOIC-8 | **仅 U-1 选「画」时，DNP** |
| D8 | — | PSM712-LF-T7 | C32677 | 基础 | ❌ 需取库 | SOT-23 | 同上 |
| C60, R61–R63 | — | 100nF / 120Ω 0603 / 10k / 10k | C1525 / C22787 / C25744 / C25744 | 基础 | ✅ | — | 同上 |

**BOM 旧位号 → 新位号对照**（供主代理改 `docs/02-BOM.csv`）：

| 旧 | 新 |
|---|---|
| C_Y1 / C_Y2 | C56 / C57（值 20pF → 33pF，C1554 → C1562） |
| C_DEC1–5 | C50–C54 |
| C_BULK | C55 |
| C_CAN | C59 |
| R_BOOT | R50 |
| R_RS | R54 |
| R_T | R55 |
| R_LED_A–C | R58–R60（R60 值 1k → 330Ω，C11702 → C25104） |

新增：C58、R51、R52、R53、R56、R57（均为基础库），以及 L2、J8（DNP）。

**成本增量**（10 块板，汇率按 `tools/cost.py` 的 7.10）：
- 新增基础库件约 9 颗/块，合计约 $0.02/块 ≈ ¥0.15/块。
- 20pF → 33pF、1k → 330Ω 两处替换，差价可以忽略。
- 上料费增量：**¥0**。DNP 件不收上料费；如果以后贴 J8 或 L2，每种各加一次上料费。

---

## 7. 每颗 IC 的 Typical Application 外围件点名清单（画图方与复核方都按这张核）

### 7.1 U6 CH32V203C8T6

| 手册图 / 页 | 手册要求的外围件 | 本设计对应 | 状态 |
|---|---|---|---|
| Fig 4-1（p.38）电源方案 | VDDx/VSSx 各 0.1µF | C52（24 脚）、C53（36 脚）、C54（48 脚） | ✅ |
| Fig 4-1 / Fig 4-13（p.56） | VDDA–VSSA 0.1µF | C51 | ✅ |
| Fig 4-1 | VBAT 接 1.8–3.6V | 接 +3V3 + C50 | ✅ |
| Fig 4-5（p.46）HSE | 晶振 + CL1 = CL2 | Y1 + C56/C57 33pF | ✅（值已按 §2.4 核算） |
| Fig 4-6（p.47）LSE | 32.768k + 2×约 12pF | 不用，PC14/15 放 NC | ✅（不需要） |
| Fig 4-7（p.51）NRST | 0.1µF 到地（按键可选） | C58 | ✅ |
| Note 6（p.35）BOOT0 | 下拉 | R50 10k | ✅ |
| Note 5（p.35）PB2/BOOT1 | 低功耗时设为下拉输入 | 固件处理，引脚 NC | ✅ |
| 板级储能 | — | C55 4.7µF | ✅ |

### 7.2 U7 SN65HVD230M（HVD p.19 文字 + p.20 Figure 20）

| Fig 20 件 | 作用 | 本设计 | 状态 |
|---|---|---|---|
| R1（D 串阻 / 上拉） | 限流 / 偏置 | **R53 10k 上拉**；串阻不加 | ✅ |
| C1（D 滤波） | 可选 | 不加（会拖慢 TXD 边沿，影响 1Mbps） | 不采用，有理由 |
| C2、C3（VCC 旁路 + 储能） | 必需 | C59 100nF 贴脚 + C55 4.7µF 共用 | ✅ |
| R2（R 串阻） | 可选 | 不加 | 不采用 |
| R3、C4（Rs） | 模式选择 | R54 0Ω 到地（高速）；C4 不加 | ✅ |
| R4（Vref） | 接分裂终端中点 | Vref 悬空 + NC 标志（p.19 允许） | ✅ |
| R5、R6 + C6（分裂终端） | 共模滤波 | 用户已定单电阻终端（BOM 备注「去掉分裂终端」），用 R55 | ✅（用户决定） |
| C5、C7（总线对地滤波） | 可选 | 不加（每只会给总线增加几十 pF 负载，限制节点数与速率）；EMC 由 L2 的 DNP 预留兜底 | 不采用，有理由 |
| D1（TVS，紧靠 J1） | 必需 | U8 PESD2CAN 紧靠 J7 | ✅ |
| J1 | 连接器 | J7 | ✅ |

### 7.3 U8 PESD2CAN

1/2 脚接 CAN_H/CAN_L，3 脚接 GND，GND 打两颗过孔。没有其它外围件 ✅。

### 7.4 Y1

1、3 脚接 OSC_IN/OUT，**2、4 脚接 GND**（不能悬空，XTAL 接线图标 GND）✅。

### 7.5 L2

1–4 串在 CAN_H，2–3 串在 CAN_L，与 R56/R57 二选一 ✅。

### 7.6 U9 SP3485（仅当画 RS485 时）

- 手册应用电路：VCC 0.1µF、A/B 间终端电阻、RE/DE 控制。本设计对应 C60、R61（DNP）、R62、R63、D8。
- 失效保护偏置电阻（A 上拉 / B 下拉，约 680Ω）：总线是否需要取决于对端设备，本版不放。

---

## 8. 规则 00 ② 封装下探、规则 00 ① 电容完备性

### 8.1 封装下探（逐颗问「能不能再小一号」）

| 位号 | 现封装 | 能否更小 | 结论 |
|---|---|---|---|
| R50–R54、R56–R60（R62、R63） | 0402 | 0201 嘉立创可贴，但手工返修困难，信号电阻用 0402 已是规则 00 ② 的默认值 | **0402** ✅ |
| R55 120Ω（R61） | 0603 | 0402 额定 62.5mW，而显性功耗 33mW，余量不足 2 倍（规则 00 ② 原例） | **0603** ✅（卡在 0603） |
| C50–C54、C58、C59（C60） | 0402 | 100nF 去耦的默认档 | **0402** ✅ |
| C56、C57 33pF | 0402 | — | **0402** ✅ |
| C55 4.7µF | 0603 16V | 0402 4.7µF 有 C23733（10V，基础库），但 3.3V 偏置下 0402 X5R 约剩 40–50%（≈ 2µF），0603 16V 约剩 3.5µF。§2.1 的 19mV 核算以 3.5µF 为前提 | **0603** ✅（按偏压有效值卡在 0603） |
| LED1–3 | 0805 | 红灯有 0603 基础库 C2286；绿灯 0603 没有有货的基础库料（C72043 扩展库，库存 1）。为三只 LED 统一外观、统一封装，保持 0805 | **0805**（P2：红灯可换 C2286 0603，面积约省 1mm²/只，收益很小） |
| SW1、J7、J8、U6、U7、U8、Y1、L2 | 按器件本身 | 不适用 | — |

### 8.2 电容完备性（逐 IC、逐电源脚）

| IC | 电源脚 | 去耦 | 状态 |
|---|---|---|---|
| U6 | 1 VBAT | C50 100nF | ✅ |
| U6 | 9 VDDA | C51 100nF | ✅ |
| U6 | 24 VDD_VIO_1 | C52 100nF | ✅ |
| U6 | 36 VDD_2 | C53 100nF | ✅ |
| U6 | 48 VDD_VIO_3 | C54 100nF | ✅ |
| U6 | 整体储能 | C55 4.7µF | ✅ |
| U7 | 3 VCC | C59 100nF + C55 共用 | ✅ |
| U9（若画） | 8 VCC | C60 100nF | ✅ |
| +3V3 轨 | 04 页 C43 22µF（有效约 10µF）+ 本页 C55 | 阶跃核算见 §2.1 | ✅ |

docs/03 §7 表中 CH32V203C8T6 一行的「待核 N（按 C3001172 手册）」可以关闭：**N = 5**（VBAT、VDDA、3 个 VDD），另加 1 颗 4.7µF。

---

## 9. 版面建议（A3 图纸，从左到右）

```
┌──────────── 左 ────────────┬──────── 中 ────────┬──────────────── 右 ────────────────┐
│ 电源 / 时钟 / 复位          │ U6 CH32V203        │ CAN 链（差分对，标 CAN_H/CAN_L）      │
│  +3V3/GND 全局标签          │ （符号放大、四边   │  J7 → U8 → R55 → R56/R57‖L2 → U7   │
│  C50–C55 去耦列（逐脚标注   │  引脚照手册顺序）  │   → CAN_TXD/CAN_RXD（局部）+ R53    │
│   所属引脚号）              │                    │  R54、C59 贴 U7                      │
│  Y1 + C56/C57               │ AFE 组（上边）：   │ 调试：J8（1×6，DNP）                 │
│  C58（NRST）                │  PB4–PB7 → 全局    │ 人机：LED1–3 + R58–R60、SW1          │
│  R50（BOOT0）               │  标签 AFE_ALERT/   │ （RS485 若画：U9、D8、R61–R63、C60） │
│                             │  AFE_WAKE/I2C_SCL/ │                                      │
│                             │  I2C_SDA           │                                      │
│                             │ BAL_CLK + R52、    │                                      │
│                             │ PRECHG_EN + R51    │                                      │
└─────────────────────────────┴────────────────────┴──────────────────────────────────────┘
```

- **差分对**：CAN_H/CAN_L 与 CAN_H_X/CAN_L_X 在原理图上平行走线，旁边加文字「差分对 120Ω，规则 0c：J7 → U8 → L2 → U7 直通道，顶层，不换层」。
- 全局标签只用于契约里的那 12 个名字（RS485 两个视 U-1 而定）。页内网络全部用局部标签：`HSE_IN HSE_OUT NRST BOOT0 CAN_TXD CAN_RXD CAN_RS CAN_H_X CAN_L_X KEY LED1_K LED2_K LED3_K SWDIO SWCLK DBG_TX DBG_RX`（以及 RS485 的 `RS485_DI RS485_RO RS485_DE`），全部用下划线分隔，不含「/」（规则 00 ⓪c）。
- NC 脚（16 个，RS485 不画时 19 个）逐一放无连接标志；U7.5 Vref 也要放。
- 加文字注释：
  - 「AFE_WAKE = MP2797 NSHDN，高 = 工作；上拉 R_WAK 在 02 页」
  - 「I2C 上拉 R_I2C1/2 在 02 页」
  - 「L2 与 R56/R57 二选一」
  - 「J8 DNP，下载器勿从 1 脚供电」
- 画图用幂等脚本生成（规则 00c「可接续」）。按 04 页已记录的教训：换符号时，二脚件的内部朝向可能不同，一律按引脚世界坐标接线。

---

## 10. 待用户定清单

| # | 事项 | 选项 | 本规格书的建议 |
|---|---|---|---|
| **U-1** | RS485 画不画 | ① 不画，并从接口契约删除 RS485_A/B（改 `gen_kicad_skeleton.py` SHEETS 与 docs/03 §1）；② 画成 DNP（全部基础库，另需 3P/4P 端子） | **①**（§4.2 的 4 条理由）；PA2/PA3/PA4 保留不挪用 |
| **U-2** | 调试口形式 | ① 1×6 2.54mm 焊盘 DNP（C492405）；② 1×4（C2691448）；③ 原 2×5 1.27mm | **①** |
| **U-3** | 终端 120Ω 跳线 | A 只放 R55（下单时决定贴不贴）；B 2P 排针 + 跳线帽；C 焊盘桥（非嘉立创件） | **A，默认贴**（BMS 是总线一端） |
| **U-4** | SW1 的作用 | ① 用户键（PB12）；② 复位键（接 NRST） | **①**（复位可由 SWD 或断电完成；用户键能清故障、唤醒） |
| **U-5** | 待机功耗与 CAN | 收发器 Standby 最小也要 400–600µA，超过 < 300µA 的目标。① 接受；② 加 P-MOS 给 U7 断电（AO3401A C15127 + 1 个 GPIO，如 PB8）；③ Rs 改由 GPIO 控制，只能降到 400µA | 由用户按待机指标定；本版默认 ①，PB8 留空 |
| **U-6** | 晶振负载电容 20pF → 33pF（C1562，基础库） | 改 / 不改 | **改**（§2.4 算式） |
| **U-7** | J7 针脚定义 | 1 CAN_H / 2 CAN_L / 3 GND / 4 GND | 按对端线束确认 |
| **U-8** | 绿灯 1k → 330Ω（C25104） | 改 / 不改 | **改**（§5 算式） |
| **U-9** | PWR_EN 删除 | 删除，并同步 docs/03 §6 | **删** |

### 跨页事项（交主代理 / 02 页 / 工具）

| # | 事项 |
|---|---|
| **X-1** | docs/03 §6 需要同步：「PWR_EN」删除；「调试 SWD 2×5 1.27mm」改为 J8 1×6 2.54mm DNP；「每个 VDD 脚 100nF…【VDD 脚数待手册】」关闭为 N = 5。docs/03 §7 的 CH32 行关闭 |
| **X-2** | **02 页 R_ALT**：MP2797 的 xALERT 是推挽输出，OTP 默认高有效（MP p.24、p.48）。现在 BOM 是 10k 上拉，空闲时持续消耗 0.33mA。建议二选一：(a) R_ALT 改为 **100k 下拉**，保持默认高有效（零电流，AFE 关断时读到低 = 无中断）；(b) 保留上拉，固件在初始化时把 ALERT_POL 置 0（低有效），但 AFE 每次复位后到固件重新配置之前仍会耗电。**推荐 (a)**。同时 docs/03 §3.1「xALERT / WDT 开漏上拉 10kΩ」一句要订正：WDT 不接，悬空（MP p.127） |
| **X-3** | `CAN_DIFF` 网络类要加入 `CAN_H_X`、`CAN_L_X`（`tools/gen_kicad_skeleton.py` 第 63 行，以及 `.kicad_pro`） |
| **X-4** | 02 页 R_WAK 10k 必须接在 NSHDN 与 **+3V3（本板 buck 轨）** 之间，不能接 MP2797 自己的 3V3 脚：关断状态下 AFE 的 3V3 可能是关闭的（MP p.14 NSHDN rising 2V/2.65V 两档说明），接到那里就再也唤不醒 |
| **X-5** | 固件（`firmware/`）要点：①TIM1 PSC=0、ARR=1919、CCR1=960、OIS1=0，调试暂停时停 TIM1；② 必须开 IWDG；③ PB5 只能配置为开漏；④ NC 脚设为下拉输入；⑤ AFE 唤醒后等 ≥5ms 再发 I2C；⑥ CAN 500k 示例：PCLK1 = 72MHz，BRP = 9，1 + 13 + 2 = 16tq，采样点 87.5% |
| **X-6** | 取库清单（规则 0e，取回后都要跑 `fp_compare.py`）：**C1562、C25104、C95572、C492405**；按决定可能还要 C8963、C32677、C492401、C100114、C2691448。另外核对 C84256 的符号名与封装极性（§5） |
