colemandlut/MP2645A-BMS/design/04_power_supply-review-opus-r3.md

# 04_power_supply（辅助电源）独立复核报告 · 第 3 轮（复核方 Claude Opus）

> 时间戳：2026-09-26 15:26 UTC
> 快照：`review/04-r6/`。`04_power_supply.kicad_sch` 的 md5 为 `81c8c50b…`，与 `hardware/04_power_supply.kicad_sch` 逐字节相同。
> 独立复跑：在本机用 `kicad-cli 10.0.6` 对根图重跑 ERC（`--severity-all`），本页 0 条；根图只有 1 条 `isolated_pin_label BAT+`（01 页还没画）。网表与快照一致：13 个器件，全部带封装。
> 纪律：只读不改工程，没有读画图方报告和脚本注释。取料报告 `design/04_power_supply-parts-r5.md` 只用作线索，下面的数值都是独立复算的。
> 手册简称（页码均为 PDF 页号）：
> - FCR = `datasheets/C153337.pdf`
> - JDT = `C136343.pdf`
> - Tokmas = `C54823941.pdf`
> - RV = `C48971005.pdf`
> - CCTC = `C282823.pdf`

## 结论速览

| 档 | 条数 |
|---|---|
| **P0 不能投板** | **0** |
| **P1 必须改** | **0** |
| **P2 建议** | **15**（本轮新增 3 条；沿用第 2 轮 7 条，其中 2 条部分关闭；沿用第 1 轮 5 条） |

### 第 2 轮 P1 的关闭情况

| 第 2 轮 | 本轮结论 | 依据 |
|---|---|---|
| P1-1 R42/F11 保护协调 | ✅ **关闭**，残余风险转为本轮 P2-N1（需台架验证） | 见 §1 |
| P1-2 输入陶瓷与尖峰余量 | ✅ **关闭** | R42 = 56Ω 后我独立复算的最坏值是 **39.2V**，与取料方一致；C45 100nF 已贴近 VIN（手册第 14 页要求）。见 §2 |

---

## 1. R42 = C153337（Ever Ohms FCR1206，56Ω ±5% 熔断型）专项核算

**手册依据（FCR）**
- 第 2 页：1206 额定 0.25W @70°C，**Max Hold-Off Voltage 200V**，**「Fusing Time & Min. Fusing Power：< 30 sec at 5W」**。56Ω 落在 48–470Ω 档，TCR ±400ppm。
- 第 6 页：短时过载 2.5×RCWV，5 秒。
- 第 7 页：推荐焊盘。
- 全部 9 页都**没有**阻燃（UL94 / flame）声明，也**没有**脉冲曲线。

### 1.1 VIN_F 对地短路：谁先断、多久、多少能量
回路电阻 = R42 56Ω + F11 冷阻 0.49Ω（JDT 第 3 页）。R42 取 5% 公差下限 53.2Ω 时，功耗会略高于下表。

| 电池电压 | 短路电流 I | R42 功耗 | 相对 5W 熔断门槛 | 熔断时间（手册） | 熔断前能量上限 | F11 |
|---|---|---|---|---|---|---|
| 16.9V 及以下 | ≤0.30A | ≤5.0W | ≤1× | **不保证熔断** | 持续发热 ≤5W | 0.3In，不动作 |
| 20V（欠压点） | 0.354A | 7.0W | 1.4× | < 30s | ≤210 J | 0.35In，不动作 |
| 29.2V（满充） | 0.517A | 15.0W | 3.0× | < 30s（实际应短得多） | ≤450 J | 0.52In，不动作 |
| 53V（瞬态） | 0.938A | 49W | 9.9× | < 30s | — | 0.94In，不动作 |

- **协调方向已经正确**：VIN_F 短路时，F11 在所有电压下都不到 1In，不会动作；由 R42 受控熔断开路。熔断后 R42 两端 ≤53V，在 200V 隔离电压内。✅
- **F11 作 VIN_R 短路的二级保护**：VIN_R（F11 与 R42 之间）对地短路时，电流 = 29.2/0.49 ≈ 60A，在 JDT 150A@32Vdc 的分断能力内。✅
  53V 瞬态下约 108A，超过 50A@63V，所以布局上仍要把 VIN_R 做短（沿用第 2 轮 P2-7）。
- 残余风险有两项：
  - 电池 ≤16.9V（约 2.1V/节，已深度过放）时，手册不保证熔断，1206 可能持续承受最多 5W（额定值的 20 倍）。
  - 16.9V 以上时手册只保证 < 30s，熔断前最多有数百焦耳的热量进入板子。
  - 手册没有阻燃声明，这是本轮 **P2-N1** 的内容。

### 1.2 上电冲击（C40 47µF + 陶瓷约 1µF + C45，合计 ≈ 48µF）
| 工况 | R42 吸收能量 ≈ ½CV²·R/(R+0.49+ESR) | 峰值电流 / 峰值功率 | τ | F11 上电 I²t（占熔化 I²t 0.10 A²s 的比例） |
|---|---|---|---|---|
| 0→29.2V | ≈19–20 mJ | 0.52A / 15W | ≈2.7–2.9 ms | 29.2²×48µ/(2×57) ≈ 3.6×10⁻⁴ A²s（0.4%）✅ |
| 0→53V（假想上界） | ≈64–67 mJ | 0.94A / 49W | 同上 | 1.2×10⁻³ A²s（1.2%）✅ |

- 绝热温升估算（手册没有脉冲曲线，这是估算）：
  - 2.7ms 内氧化铝的热扩散深度 √(α·t) ≈ √(1×10⁻⁵ × 2.7×10⁻³) ≈ 0.16mm；
  - 受热体积 ≈ 膜区 2.9mm² × 0.16mm ≈ 0.46mm³，热容 ≈ 1.4 mJ/K；
  - 温升：**29.2V 约 14K，53V 约 48K**，远低于熔断所需温度。✅
- 对照手册的短时过载项（FCR 第 6 页）：RCWV = √(0.25×56) = 3.74V，2.5 倍 = 9.35V，即 1.56W 持续 5s、共 7.8 J 不劣化。上电能量只有它的 1/400～1/120。
- 快关尖峰时 R42 吸收的能量（§2 的仿真）：270V/3.3µs 约 3.2mJ，90V/13µs 约 0.8mJ。✅ 但极端情况下 R42 两端瞬时约 240V，超过 200V（见 P2-N2）。

### 1.3 56Ω 对 buck 正常工作的影响（Tokmas U4）
- **稳态**：负载 80mA 时 Pin ≈ 3.3×0.08/0.75 ≈ 0.35W。
  - 20V 电池时解 V² − 20V + 56×0.35 = 0，得 VIN_F = **18.96V**。R42 压降 1.04V，I_in = 18.6mA，功耗 **19mW**（额定值的 8%）。✅
  - 16V 时 VIN_F = 14.7V。
  - Tokmas 要求 VIN ≥ Vo + 4.5V = 7.8V（第 3 页），UVLO 3.9V（第 4 页），余量都很大。✅
- **启动**：Tokmas 内部软启动 5ms（第 4 页）。
  - C43 有效约 10µF 充到 3.3V 只需约 7mA；全板 3V3 电容若按 50µF 计，约 33mA。加 80mA 负载，合计约 0.12A 输出，Pin ≈ 0.5W。
  - 20V 电池时 VIN_F ≈ 18.5V。✅
  - U4 上电前 C40 经 R42 充电（τ ≈ 2.7ms），UVLO 很快就能越过。
- **负阻稳定**：
  - 源阻抗 |Zs| ≤ 56Ω；buck 的负输入阻抗 |Zin| = V²/P ≈ 18.96²/0.35 ≈ 1.0kΩ，比值约 18 倍。✅
  - 直流工作点稳定的条件是 R < V²/(4P) ≈ 284Ω。✅
- **能力上限**：最大可传输功率 V²/(4R)，20V 时约 1.8W 输入，折合约 0.4A @3.3V。超过这个负载，VIN_F 会塌陷。本设计负载 <80mA，没有问题，但要写进设计约束（P2-N3）。

---

## 2. P1-2 复算：VIN_F 尖峰峰值
模型与第 2 轮相同：R = 56.49Ω → 陶瓷 C1 ∥（C40 47µF 串联 ESR）。数值积分步长 1ns。尖峰伏秒按 L·I = 800µV·s 计。

| BAT+ 尖峰 | 陶瓷有效 C1 | ESR 1Ω | ESR 4Ω | ESR 10Ω |
|---|---|---|---|---|
| 270V / 3.3µs | 0.9µF | 33.4V | **39.2V** | 41.9V |
| 270V / 3.3µs | 1.2µF | 33.2V | 37.5V | 39.2V |
| 400V / 2.16µs（更极端） | 0.9µF | 35.2V | 40.8V | 42.9V |
| 90V / 13µs（FET 雪崩限幅） | 0.9µF | 30.5V | 33.3V | 36.7V |
| D3 钳在 53V 持续 1ms | 0.9µF | — | 37.3V | — |

- 与取料方的 39.2V **完全一致**。即使 ESR 取到 10Ω、尖峰取到 400V，也 ≤ 43V，距离 Tokmas 推荐上限 60V、绝对最大 65V 还有 17V 以上。
- 只有 BAT+ 持续高于 60V（D3 不存在或失效）时，VIN_F 才会跟随超限。这是 01 页的问题（沿用第 2 轮 P2-7）。
- C45（CL21B104KCFNNNE，100nF/100V X7R 0805，C28233）满足 Tokmas 第 14 页「0.1µF … as close as possible to the VIN pin」，在 PCB 上要紧贴 U4.5/U4.2。
- 输入陶瓷有效容量仍然低于 Tokmas 推荐的 4.7µF。但 R42 = 56Ω 后，输入纹波只取决于本地电容：80mA 负载、600kHz 下 ΔV ≈ 0.08/(1.0µ×600k) × 0.11 ≈ 15mV，可以接受。
- 结论：**P1-2 关闭。**
- CCTC 手册只给出了容量范围表（第 13–15 页），没有直流偏压曲线。0.9–1.2µF 是估算值，建议上板实测 VIN_F 纹波。

---

## P0 不能投板
无。

## P1 必须改
无。

## P2 建议

**本轮新增：**

**P2-N1　R42 的熔断只有一个保证点（≥5W 时 < 30s），手册没有阻燃声明，需要台架验证后才能认定 VIN_F 短路是受控失效**
- 依据：FCR 第 2 页；全 9 页没有 flame/UL94 条目。
- 风险等级判定为 P2，理由：
  - 触发条件是二次故障（VIN_F 短路），器件本身就是专门的熔断型；
  - 嘉立创上没有更好的有货料（取料报告 §1.1 的检索记录我复核过，合理）。
- **台架项**（建议在投板前用样品做，至少各 3 片）：
  1. 限流电源分别以 16V / 20V / 29.2V 短接 VIN_F，记录熔断时间、表面最高温度、有无明火或冒烟、PCB 是否碳化；
  2. 上电冲击 100 次（29.2V）后 ΔR ≤ 2%（FCR 第 6 页 5% 档判据是 ±(2.0%+0.1Ω)）。
- **布局**：R42 周围 ≥1mm 净空，下方不走其它网络，远离电解电容和线束。
- 16.9V 以下不保证熔断：这时电芯已过放到约 2.1V/节，AFE 早已报 UV，属于三重故障叠加，可以记录为已知限制。

**P2-N2　极端尖峰时 R42 两端瞬时超过 200V**
- 270V/3.3µs 情况下，R42 两端约 240V，持续约 3µs，超过 FCR 第 2 页的 200V（手册没有给出瞬态耐压）；能量 3.2mJ。
- 只在 01 页 D3 电流远超 IPP 的极端假设下才会出现。建议在 01 页复核 SCP 关断速率时一并确认，或者在台架上用浪涌源（2µs 级、250V）验证 R42 不劣化。

**P2-N3　56Ω 限制了 3V3 的可用功率，并且型号字段不统一**
- **功率上限**：20V 电池时 VIN_F 最多能提供约 1.8W 输入，折合约 0.4A @3.3V；超过后 VIN_F 塌陷。建议在详细设计 §5 写明「3V3 总负载 ≤ 0.3A（含启动时的电容充电）」，防止以后加负载（例如 RS485、LED）时误用。
- **型号字段**：原理图的 Value/libsource 用的是嘉立创商品名 `FCR1206J56RP055W`，而库符号的 `MPN` 与手册编码（FCR 第 2 页：FCR 1206 J 56R0 P 05 Z）是 **`FCR1206J56R0P05Z`**。BOM 的「制造商型号」列应填真实 MPN。
- **焊盘**：`jlc:R1206` 已被 C153337 覆盖，焊盘 1.208×1.701mm、中心 ±1.48mm，内间隙约 1.75mm。FCR 第 7 页推荐 A = 2.20mm（内间隙）、B = 4.20、C = 1.80。按规则 0e 以嘉立创封装为准，但两者差异要在 PCB 阶段用 `fp_compare` 确认可焊性。

**沿用第 2 轮：**
- **沿用第 2 轮 P2-1**：EN 直接接 VIN。页面说明文字仍写「SHDN 悬空=常开」，符号引脚名仍是 SHDN。
- **沿用第 2 轮 P2-2**：C43 有效约 10µF，环路裕量无法从手册核实。建议 2×C59461 并联，或上板做负载阶跃测试。
- **沿用第 2 轮 P2-3**：待机电流预算（Tokmas IQ 最大 109µA + C40 漏电流规格 ≤29.6µA + 分压约 13µA）。R42 对待机电流没有影响。
- **沿用第 2 轮 P2-4**：SW 负压绝对最大 −0.6V，SS210 在短路限流时压降超过这个值，需上板实测。
- **沿用第 2 轮 P2-5（部分关闭）**：U4 的 Datasheet 已改为 C54823941 ✅。F11 仍然用共享的 `jlc:F1206`，而这个文件现在的 `LCSC Part` 已经被覆盖成 **C163126**（另一颗保险丝），焊盘 1.19×1.728mm、中心 ±1.45mm，与 JDT 推荐焊盘（1.52×2.03mm、间隙 1.52mm，JDT 第 2 页）不同。共享封装名被不同料号反复覆盖，这是库管理层面的风险：建议按料号命名封装，或逐颗用 `fp_compare` 确认。
- **沿用第 2 轮 P2-6（部分关闭）**：T 形连接的结点已补齐 ✅（(215.9,104.14)、(241.3,104.14)、(289.56,71.12)、(304.8,71.12) 四处都有）。但两脚件的引脚名仍然压在符号本体上（R42「1 2」、各电容「1|2」、D7「K/A」）。新增的 C45 符号（CL21B104KCFNNNE）引脚较短（±3.81mm），「1/2」与极板重叠得更严重。建议在库里设置 `(pin_names hide)`。
- **沿用第 2 轮 P2-7**：01 页仍然是空的，D3 不在网表里；VIN_R 在 53V 瞬态下对地短路时约 108A，超过 50A@63V，所以布局上 VIN_R 要做短。

**沿用第 1 轮：**
- **P2-2**：R40/R41 放大 10 倍（330k/100k），可省约 12µA 待机电流。
- **P2-3**：+3V3 短路时 D7 耗散约 1.1W，结温超过 125°C。
- **P2-4**：L1 的 Isat 保证值是 1.60A。详细设计 §5 仍写 1.9A（那是典型值），应改。
- **P2-7（D7 部分）**：D7 可以从 SMA 换 SOD-123FL，但会从基础库变成扩展库。
- **P2-8 第 3 点**：封装文件里 `LCSC Part` 的旧编号问题，同上面第 2 轮 P2-5 的覆盖问题。

---

## 覆盖清单

### A. 连通性
| 项 | 结果 |
|---|---|
| 本页 ERC / 根图 ERC | 0 / 1（`isolated_pin_label BAT+`，跨页项）✅ |
| 单节点网络 | 只有 `unconnected-(U4-SHDN-Pad4)`（有 NC 标志）|
| 两脚件一端悬空 / 同网多名 / 名字消失 | 无 ✅ |
| 网络 | BAT+ = {F11.1}；VIN_R = {F11.2, R42.1}；VIN_F = {R42.2, C40.1(+), C42.2, C44.2, C45.2, U4.5}；CB_3V3 = {U4.1, C41.1}；SW_3V3 = {U4.6, C41.2, D7.K, L1.1}；+3V3 = {L1.2, C43.2, R40.1}；FB_3V3 = {U4.3, R40.2, R41.1}；GND = {U4.2, C40.2, C42.1, C43.1, C44.1, C45.1, D7.A, R41.2} ✅ |
| 导线几何 | 没有导线端点落在另一段导线中间；4 处 T 形连接都有结点 ✅ |

### B. 手册外围件（Tokmas 第 13 页 Figure 13）
| 手册 | 本图 | 结论 |
|---|---|---|
| C1 0.1µF（VIN 旁路） | **C45 100nF/100V 0805** | ✅ 本轮补齐 |
| C2 / C3（输入陶瓷） | C42、C44（2×1µF/100V，C282823）+ C40 | 低于推荐值，但尖峰和纹波都已核算通过（§2）✅ |
| C4 BOOT 0.1µF | C41 | ✅ |
| L1 | L1 22µH | ✅（沿用第 1 轮 P2-4）|
| D1 | D7 SS210，阴极接 SW | ✅（沿用第 2 轮 P2-4）|
| R1 / R2 | R40 / R41，Vout = 3.311V | ✅ |
| C5 输出电容 | C43 | 沿用第 2 轮 P2-2 |
| EN（R3/R4 可选） | 悬空 | 沿用第 2 轮 P2-1 |

### C. 器件级（符号 ↔ 封装 ↔ LCSC ↔ BOM ↔ 额定值）
| 位号 | LCSC（原理图 / BOM 第 54–65 行） | 封装 | 额定值 / 工况 | 结论 |
|---|---|---|---|---|
| U4 | C54823941 / 同 | SOT-23-6 | 见第 2 轮核算 | ✅ |
| F11 | C136343 / 同 | F1206（共享封装）| 72V/50A；VIN_F 短路时 <1In 不动作；上电 I²t 占 0.4% | ✅（沿用第 2 轮 P2-5）|
| **R42** | C153337 / 同 | R1206（C153337 自己的封装）| 0.25W / 200V / ≥5W 时 <30s 熔断；正常功耗 19mW | ✅（P2-N1～N3）|
| C40 | C48971005 / 同 | 6.3×7.7，焊盘 1 = + | 63V | ✅ |
| C41 | C1525 / 同 | 0402 | 16V，BOOT–SW ≤6.5V | ✅ |
| C42、C44 | **C282823** / 同 | C1206 | 100V X7R | ✅（有效容量为估算）|
| **C45** | **C28233** / 同 | C0805 | 100V X7R；VIN 最高 ≤43V | ✅ |
| C43 | C59461 / 同 | C0603 | 6.3V X5R | 沿用第 2 轮 P2-2 |
| D7 | C14996 / 同 | SMA，焊盘 1 = K | 100V | ✅ |
| L1 | C68434 / 同 | 5×5 | Isat 1.6A | 沿用 |
| R40、R41 | C25779、C25744 / 同 | 0402 | — | ✅ |

### D. 电容完备性 / 封装下探
- VIN：C45（高频）+ C42/C44（陶瓷）+ C40（电解，工业输入必须有电解）✅。
- BOOT：C41 ✅。
- 输出：C43 ✅。
- 封装下探：R42 必须用 1206 熔断型（嘉立创有货且合规的只有这一档）；C45 用 0805 是因为 100V（0603 的 100nF/100V 可选，但 C28233 是基础库且 BOM 已在用）。其余器件结论与第 2 轮相同。

### E. 可读性（PDF 第 5 页目视，规则 00 ③）
| 项 | 结果 |
|---|---|
| 多余文字 / 废弃线 / 越界 | 无 ✅ |
| 网络名按功能命名 | ✅ |
| 交叉线 | 无 ✅ |
| T 形结点 | 已补齐 ✅ |
| 文字重叠 | 引脚名压在符号本体上（沿用第 2 轮 P2-6）；U4 的 Value「LMR16006XDDCR (Tokmas)」右端离 C45 导线约 1.5 格，没有重叠 |
| 说明文字 | 「SHDN 悬空」应改为 EN（沿用第 2 轮 P2-1）|
