colemandlut/MP2645A-BMS/design/04_power_supply-draw-report.md

# 04_power_supply（辅助电源）画图报告 · 第 6 轮

- 生成脚本：`hardware/gen/gen_04_power_supply.py`（幂等，UUID 用 `uuid.uuid5` 派生，跑两次输出逐字节相同）
- 自检脚本：`hardware/gen/check_04_layout.py`（几何检查 1–3，直接解析生成的 `.kicad_sch`）
- 产物：`hardware/04_power_supply.kicad_sch`
- 依据：第 6 轮任务书 `design/04_power_supply-task-draw-r6.md`（C42/C44 换符号后修版面）
- 上一轮：第 5 轮报告见本文件「附 · 第 5 轮历史报告」，纪律全部沿用

---

## 0. 第 6 轮变更（C42/C44 换符号后修版面）

### 根因

- C42/C44 符号 `CL31B105KCHNNNE` → `TCC1206X7R105K101HT`（LCSC `C13832` → **`C282823`**，Footprint 不变 `jlc:C1206`）。
- 新旧符号引脚几何不同（规则 00 ⓪：换符号 → 引脚平移、导线留在原地）：

  | 符号 | 引脚内部坐标 / 朝向 |
  |---|---|
  | 旧 `CL31B105KCHNNNE` | pin1 (−5.08, 0) 朝右、pin2 (+5.08, 0) 朝左 —— 横向符号 |
  | 新 `TCC1206X7R105K101HT` | pin1 (0, −5.08) 朝上、pin2 (0, +5.08) 朝下 —— 竖向符号 |

- 脚本本就从库读引脚坐标（`parse_pins` / `pin_world`），**没有按旧符号硬编码的引脚偏移**；但「竖放」所需的旋转角度取决于符号内部朝向：
  旧符号（横）rot 90 才是世界竖向；新符号（竖）rot 0 即世界竖向。开工前 C42/C44 仍残留 rot 90，
  于是两脚都落到 y=109.22 的水平线上（pin2 左、pin1 右）：VIN_F 导线穿过 C42.1、C42.2 处形成无 junction 的 T 型连接，
  `check_04_layout.py` 报 3 条。

### 修改

- `COMPONENTS` 表：C42/C44 的 rot **90 → 0**。引脚世界坐标与第 5 轮完全一致（pin2 上=104.14、pin1 下=114.30）。
- 导线 / junction / GND 标签**一律未动**（沿用第 5 轮）：VIN_F 轨 y=104.14 串 C45.2→C42.2→C44.2；三颗 GND 竖线到 y=121.92；
  junction 仍 4 个（+3V3 三线 T + C45.2/C42.2/C43.2 引脚 T）。
- 脚本头部注释补「第 6 轮变更」；`title_block.rev → v0.3-draw-r6`。
- 其它 11 个器件的位置 / 旋转 / 连接 / LCSC / Footprint 全部未动。

## 1. 自检结果（第 3/4/5 轮全部重跑）

| # | 检查 | 结果 |
|---|---|---|
| 1 | `check_04_layout.py` 几何检查 1/2/3 | ✅ **PASS，0 条**（导线 26 / junction 4 / 实例 13 / 引脚 30） |
| 2 | ERC `--severity-all`（根图） | ✅ `/辅助电源/` 页 **0 条**；全图仅根图 1 条 `isolated_pin_label BAT+`（01 页未画，预期） |
| 3 | 网表「位号.脚 → 网络」 | ✅ 与第 5 轮**完全一致**（逐网比对，见下方全表）；C42/C44 LCSC = **C282823**、Footprint = `jlc:C1206` |
| 4 | 文字重叠（pymupdf 逐 span bbox，容差 0.2mm） | ⚠ 199 个 span，**2 处**重叠，均为**已记录的符号级 quirk**：D7 K/A（第 3 轮已记录）+ C45 1/2（第 5 轮已记录），无新增 |
| 5 | PDF 目视 | ✅ C45/C42/C44 三颗输入陶瓷竖排、VIN_F 轨在上 / GND 标签在下、无导线穿本体、文字不压线 |
| 6 | 幂等 | ✅ 跑两次 md5 相同（`81c8c50bdd368d6fb62307da96c26d3a`） |
| 7 | Footprint / Datasheet / LCSC 非空且与库一致 | ✅ 13/13；C42/C44 Datasheet = CCTC 商品页、LCSC = C282823 |

### 网表全表（第 6 轮回读，与第 5 轮一致）

| 网络 | 节点（位号.脚） |
|---|---|
| BAT+ | F11.1 |
| VIN_R | F11.2, R42.1 |
| VIN_F | R42.2, C40.1, C45.2, C42.2, C44.2, U4.5 |
| CB_3V3 | U4.1, C41.1 |
| SW_3V3 | U4.6, C41.2, D7.1, L1.1 |
| +3V3 | L1.2, C43.2, R40.1 |
| FB_3V3 | U4.3, R40.2, R41.1 |
| GND | U4.2, C40.2, C45.1, C42.1, C44.1, C43.1, D7.2, R41.2 |
| unconnected-(U4-SHDN-Pad4) | U4.4（SHDN 悬空 = 常开，NC 标志，预期） |

## 2. 备份说明

- 本会话 `/tmp` **可写**（ERC 曾成功写到 `/tmp/erc_r6.json`）；但改动前 git HEAD（`8192fde`）已含上一版
  （C42/C44 新符号但 rot=90 的版面错误状态），第 5 轮定稿另由提交 `18f6f01` 与冻结快照 `review/04-r5/` 双重保留。
  本次仅把 C42/C44 的 rot 由 90 改 0 两个数字，改前状态可直接从 git 还原，未另做文件备份。

## 3. 遗留 / 待主代理

1. C45 引脚名 1/2、D7 引脚名 K/A 两处符号级文字重叠（历史已记录，纯观感，不改库）。
2. `docs/02-BOM.csv` 中 C42/C44 的 LCSC 已由主代理在前置提交改为 C282823，本图网表已一致，无需再改。
3. BAT+ `isolated_pin_label`：01 页未画导致，01 页画好后自动消失（跨页项）。

---

## 附 · 第 5 轮历史报告（以下为第 5 轮交付时内容，仅作追溯，不再更新）

# 04_power_supply（辅助电源）画图报告 · 第 5 轮

- 生成脚本：`hardware/gen/gen_04_power_supply.py`（幂等，UUID 用 `uuid.uuid5` 派生，跑两次输出逐字节相同）
- 自检脚本：`hardware/gen/check_04_layout.py`（几何检查 1–3，直接解析生成的 `.kicad_sch`）
- 产物：`hardware/04_power_supply.kicad_sch`
- 依据：复核报告 `design/04_power_supply-review-opus-r2.md`（P1-1 / P1-2 / P2-5 / P2-6）+ 取料报告 `design/04_power_supply-parts-r5.md`
- 上一轮：第 4 轮报告见本文件「附 · 第 4 轮历史报告」，纪律全部沿用

---

## 0. 第 5 轮变更

### P1-1　R42 换成熔断型电阻（C153337）

- 位号 R42：符号 `1206W4F100JT5E`（10Ω 普通厚膜）→ **`FCR1206J56RP055W`**（Ever Ohms 熔断电阻）。
- 值 `10Ω 1% 1206` → **`56Ω 5% 熔断 1206`**；LCSC `C17903` → **`C153337`**；Footprint 取库值 `jlc:R1206`（与任务书一致）。
- 理由：VIN_F 对地短路时 10Ω 普通厚膜会先于 F11 烧开起火；56Ω 熔断电阻在 20V 时 ≥7W、手册保证 <30s 受控开路，F11 留作 VIN_R 短路的二级保护。
- 位置不变（114.30, 71.12）；新符号引脚 ±5.08 与旧符号一致，接线不用动。

### P1-2　新增 C45 100nF/100V 贴 U4.VIN（C28233）

- 位号 **C45**：符号 `CL21B104KCFNNNE`（三星 0805 X7R），值 `100nF 100V`，LCSC **`C28233`**，Footprint `jlc:C0805`。
- 接 VIN_F–GND。三颗输入陶瓷按「最靠 U4.VIN」排序，C45 在最左列：C45（215.90, 107.95）、C42（241.30, 109.22）、C44（266.70, 109.22），各距 25.4mm；C45 的 GND 标签在下方（215.90, 121.92）。
- 网表回读：`VIN_F` 新增 `C45.2`、`GND` 新增 `C45.1`。

### P2-5　U4 Datasheet 字段改 Tokmas 件

- 新增 `DATASHEET_OVERRIDE`，把 U4 的 `Datasheet` 从 TI C87080 商品页改为 **`https://www.lcsc.com/datasheet/C54823941.pdf`**（其余字段不动），网表 `<datasheet>` 已回读确认。

### P2-6　T 型接点补 junction

- 三处「引脚 + 两段共线导线」三方相接补 `junction`：C45.2（215.90, 104.14）、C42.2（241.30, 104.14）、C43.2（289.56, 71.12）。
- `check_04_layout.py` 检查 3 扩展：新增「引脚处 ≥2 段导线端点相接必须有 junction」，能抓到复核 P2-6 这一类（第 4 轮的 C42.2 / C43.2 正是这一类）。

### 说明文字

- R42 句改为：`R42 56Ω 熔断电阻与 C40 构成输入 RC：限上电浪涌与短路电流，VIN_F 短路时受控开路；C45 100nF/100V 贴 VIN（Tokmas 手册 p14）`。
- `title_block.rev` → `v0.3-draw-r5`。

---

## 1. 器件字段表（网表回读，13 器件 Footprint / LCSC 全部非空）

| 位号 | 值 | Footprint | LCSC |
|---|---|---|---|
| F11 | 1A 63V | jlc:F1206 | C136343 |
| R42 | 56Ω 5% 熔断 1206 | jlc:R1206 | C153337 |
| C40 | 47µF 63V | jlc:CAP-SMD_BD6.3-L6.6-W6.6-LS7.3-FD | C48971005 |
| U4 | LMR16006XDDCR (Tokmas) | jlc:SOT-23-6_L2.9-W1.6-P0.95-LS2.8-BR | C54823941 |
| C41 | 100nF 16V | jlc:C0402 | C1525 |
| C45 | 100nF 100V | jlc:C0805 | C28233 |
| C42 | 1µF 100V | jlc:C1206 | C13832 |
| C44 | 1µF 100V | jlc:C1206 | C13832 |
| D7 | SS210 | jlc:SMA_L4.3-W2.6-LS5.2-RD | C14996 |
| L1 | 22µH | jlc:IND-SMD_L5.0-W5.0 | C68434 |
| C43 | 22µF 6.3V | jlc:C0603 | C59461 |
| R40 | 33k 1% | jlc:R0402 | C25779 |
| R41 | 10k 1% | jlc:R0402 | C25744 |

> Datasheet 字段：U4 = `https://www.lcsc.com/datasheet/C54823941.pdf`（第 5 轮改）；其余 12 器件取库符号值（商品页），未动。

## 2. 网表「位号.脚 → 网络」全表（`kicad-cli sch export netlist`，局部网名前缀 `/辅助电源/` 已省略）

| 网络 | 节点（位号.脚） |
|---|---|
| BAT+ | F11.1 |
| VIN_R | F11.2, R42.1 |
| VIN_F | R42.2, C40.1, C45.2, C42.2, C44.2, U4.5 |
| CB_3V3 | U4.1, C41.1 |
| SW_3V3 | U4.6, C41.2, D7.1, L1.1 |
| +3V3 | L1.2, C43.2, R40.1 |
| FB_3V3 | U4.3, R40.2, R41.1 |
| GND | U4.2, C40.2, C45.1, C42.1, C44.1, C43.1, D7.2, R41.2 |
| unconnected-(U4-SHDN-Pad4) | U4.4（SHDN 悬空 = 常开，NC 标志，预期） |

- 无 `Pad??`、无两脚件一端悬空、无自短路；`VIN_R` 与 `VIN_F` 分离正确（短路防护闭环）。
- 反馈输出：VFB = 0.770V（Tokmas），Vout = 0.770×(1+33/10) = **3.31V**。

---

## 3. 自检结果（第 3/4 轮全部自检重跑）

| # | 检查 | 结果 |
|---|---|---|
| 1 | 导线不许经过非端点的引脚 | ✅ PASS（check_04_layout.py，26 段导线） |
| 2 | 导线不许穿过符号本体 | ✅ PASS |
| 3 | T 型连接必须有 junction（含引脚处 2+ 导线端点这一类） | ✅ PASS（4 个 junction：304.80/71.12 三线 T + C45.2/C42.2/C43.2 引脚 T） |
| 4 | 文字不重叠（pymupdf 逐 span bbox，容差 0.2mm） | ⚠ 199 个 span，2 处重叠，均为**符号级自动摆位 quirk**（见 §4 第 1、2 条）：D7 引脚名 K/A（第 3 轮已记录）、**C45 引脚名 1/2**（本轮新增） |
| 5 | 连通性（网表逐脚） | ✅ 13 器件 30 脚全在网表；无 `Pad??`、无孤立脚、无同网多名；唯一单脚网 `BAT+`（01 页未画，跨页预期） |
| 6 | 网表逐脚与 §2 全表一致 | ✅ `VIN_F` 新增 C45.2、`GND` 新增 C45.1，VIN_R/VIN_F 分离正确 |
| 7 | PDF 04 页渲 PNG 目视 | ✅ C45 在最靠 U4.VIN 的一列、R42 值 `56Ω 5% 熔断 1206`、说明文字已同步 |
| 8 | 幂等 | ✅ 跑两次 md5 相同（`1f16918a8cd811299e85684b4602d89c`） |
| 9 | ERC `--severity-all` | ✅ `/辅助电源/` 页 **0 条**；根图 1 条 `isolated_pin_label BAT+`（预期） |
| 10 | Footprint 非空且与库一致 | ✅ 13/13（§1 表）；U4 Datasheet 已指向 Tokmas PDF |

---

## 4. 遗留 / 待主代理

1. **C45 引脚名 1/2 重叠（0805 竖放符号 quirk，本轮新增）**：`CL21B104KCFNNNE`（0805，引脚距 ±3.81）竖放时，KiCad 自动摆放的引脚名 `1`（距下脚 4.23mm）与 `2`（距上脚 3.28mm）在符号中心重叠约 1.1mm（实测 span bbox (214.95, 107.42) 与 (214.95, 107.53)）。1206 的 C42/C44 引脚距 ±5.08 不重叠，只有 0805 的 C45 中招。**根治同复核 P2-6 建议**：在 `fetch_jlc_parts.py` 库侧归一化时对二脚无源件加 `(pin_names hide)`（本轮不改库，纪律同第 3/4 轮）。纯观感，不影响 ERC/网表。
2. **D7 引脚名 K/A 重叠**：第 3 轮已记录的 SS210 符号 quirk，未变。
3. **R42（C153337）与 C45（C28233）的 BOM 行**：`docs/02-BOM.csv` 需主代理补/改（R42 换料、C45 新增；本轮交付不含 BOM 更新）。
4. **BAT+ `isolated_pin_label`**：01 页未画导致，01 页画好后自动消失（跨页项）。
5. **台架验证（写入测试计划，取料报告 §6）**：上电 100 次后 R42 ΔR ≤2%；20V/29.2V 限流源短接 VIN_F 记录熔断时间并确认无明火。

---

## 附 · 第 4 轮历史报告（以下为第 4 轮交付时内容，仅作追溯，不再更新）

# 04_power_supply（辅助电源）画图报告 · 第 4 轮

## 0. 第 4 轮变更

### P0-1　器件实例补 `Footprint` / `Datasheet` / `LCSC` 字段（网表封装全空 → 全补上）

每个器件**实例**（不再只写在嵌入库符号里）写全字段，`Footprint` 取 `jlc.kicad_sym` 对应符号的
`Footprint` 值（与库符号一致），`Datasheet` 取库符号值，`LCSC` 保留原有值；三字段均 `hide`。
生成脚本新增 `symbol_props()`，从库符号块读 `Footprint`/`Datasheet`，逐实例写入。
验收：`kicad-cli sch export netlist --format kicadxml` 里 12 个 `<comp>` 的 `<footprint>` 全部非空，
且与库符号逐一对得上（见 §1 表）。

### P1-1 / P1-2　F11 与 VIN_F 之间串 R42 10Ω 抗浪涌电阻

- 拓扑改为 `BAT+ ─ F11 ─ VIN_R ─ R42 10Ω ─ VIN_F ─┬─ C40 ─┬─ C42/C44 ─ U4.VIN`。
- **新网络 `VIN_R`**（保险丝后、串阻前）= {F11.2, R42.1}；`VIN_F` 现在 = {R42.2, C40.1, C42.2, C44.2, U4.5}。
- R42 = `1206W4F100JT5E`（`jlc:1206W4F100JT5E`，Footprint 取库值 `jlc:R1206`），值 `10Ω 1% 1206`，LCSC **C17903**（基础库）。
- 图上说明文字加一句：`R42 10Ω 与 C40 构成输入 RC：限上电浪涌与短路电流，替代已删的 D6`。
- 效果（复核报告算式）：短路电流 ≤ 53/10 = 5.3A（远低于 F11 50A 分断能力）；上电 I²t ≈ 0.002A²s（约为熔化 I²t 的 5%）；VIN_F 浪涌被 RC 压住。

### 换料（用户 2026-09-26 13:57 第 2 轮，已落 BOM，本轮照做）

| 位号 | 符号名 | 值 | LCSC | 封装 |
|---|---|---|---|---|
| U4 | LMR16006XDDCR（符号沿用 TI） | **LMR16006XDDCR (Tokmas)** | **C54823941** | jlc:SOT-23-6_L2.9-W1.6-P0.95-LS2.8-BR（不变） |
| F11 | JFC1206-1100FS | **1A 63V** | **C136343** | jlc:F1206 |
| C42 | CL31B105KCHNNNE | 1µF 100V | C13832 | jlc:C1206 |
| C44（新增，与 C42 并联） | CL31B105KCHNNNE | 1µF 100V | C13832 | jlc:C1206 |
| C43 | CL10A226MQ8NRNC | 22µF 6.3V | C59461 | jlc:C0603 |

- U4 的 Tokmas 件 VFB = 0.770V、fsw = 600kHz：33k/10k → 3.31V；说明文字「700kHz」→「600kHz（Tokmas）」。
- F11 值按新料写 **1A 63V**（JDT JFC1206-1100FS）。63V 依据：BOM 行「1A 63V 50A 快熔」+ 库符号 Datasheet 链接
  `…/Surface-Mount-Fuses_1A-63V_C136343.html`，两者一致；换料说明「不用再核 Littelfuse 手册」，故未再查 C151135。
- **C44 与 C42 并排、同样接 VIN_F–GND，紧挨 U4.VIN**（串阻后高频回路就近）：C42 在 (215.90,109.22)、C44 在 (241.30,109.22)，
  二者均竖放，中心距 25.4mm（与第 3 轮 C40↔C42 电容间距一致），避免 C42 的值 `1µF 100V` 与 C44 引脚号重叠。

### 可读性（复核 P2-9）+ 版面

- `FB_3V3`/`SW_3V3`/`CB_3V3`/`VIN_F` 等标签：第 3 轮已移到 U4 各脚短线末端（左 stub 到 x=165.10、右 stub 到 x=200.66），本轮确认仍不在引脚上。
- U4 的值 `LMR16006XDDCR (Tokmas)` 紧贴 U4 本体下方（185.42, 113.03），远离 D7。
- 图名「辅助电源（LMR16006X 直降 3.3V）」与说明文字**回图纸左上角**（y=20.32 / 33.02 / 38.10）。
- `title_block.rev` → `v0.3-draw-r4`。

---

## 1. 器件字段表（网表回读，12 器件 Footprint / LCSC 全部非空）

| 位号 | 值 | Footprint | LCSC |
|---|---|---|---|
| F11 | 1A 63V | jlc:F1206 | C136343 |
| R42 | 10Ω 1% 1206 | jlc:R1206 | C17903 |
| C40 | 47µF 63V | jlc:CAP-SMD_BD6.3-L6.6-W6.6-LS7.3-FD | C48971005 |
| U4 | LMR16006XDDCR (Tokmas) | jlc:SOT-23-6_L2.9-W1.6-P0.95-LS2.8-BR | C54823941 |
| C41 | 100nF 16V | jlc:C0402 | C1525 |
| C42 | 1µF 100V | jlc:C1206 | C13832 |
| C44 | 1µF 100V | jlc:C1206 | C13832 |
| D7 | SS210 | jlc:SMA_L4.3-W2.6-LS5.2-RD | C14996 |
| L1 | 22µH | jlc:IND-SMD_L5.0-W5.0 | C68434 |
| C43 | 22µF 6.3V | jlc:C0603 | C59461 |
| R40 | 33k 1% | jlc:R0402 | C25779 |
| R41 | 10k 1% | jlc:R0402 | C25744 |

> Footprint 与 `hardware/lib/jlc/jlc.kicad_sym` 中对应符号的 Footprint 字段逐一比对，全部一致（P0-1 验收通过）。

---

## 2. 网表「位号.脚 → 网络」全表（`kicad-cli sch export netlist`，XML 内局部网名前缀 `/辅助电源/` 已省略）

| 网络 | 节点（位号.脚） |
|---|---|
| BAT+ | F11.1 |
| VIN_R | F11.2, R42.1 |
| VIN_F | R42.2, C40.1, C42.2, C44.2, U4.5 |
| CB_3V3 | U4.1, C41.1 |
| SW_3V3 | U4.6, C41.2, D7.1, L1.1 |
| +3V3 | L1.2, C43.2, R40.1 |
| FB_3V3 | U4.3, R40.2, R41.1 |
| GND | U4.2, C40.2, C42.1, C43.1, C44.1, D7.2, R41.2 |
| unconnected-(U4-SHDN-Pad4) | U4.4（SHDN 悬空 = 常开，NC 标志，预期） |

- 无 `Pad??`、无两脚件一端悬空、无自短路；`VIN_R` 与 `VIN_F` 分离正确（短路防护闭环）。
- 反馈输出：VFB = 0.770V（Tokmas），Vout = 0.770×(1+33/10) = **3.31V**。

---

## 3. 自检结果（第 3 轮 8 项全部重跑 + 第 4 轮新增项）

| # | 检查 | 结果 |
|---|---|---|
| 1 | 导线不许经过非端点的引脚 | ✅ PASS（check_04_layout.py） |
| 2 | 导线不许穿过符号本体 | ✅ PASS |
| 3 | T 型连接必须有 junction | ✅ PASS（唯一 T 接点 x=304.80 有 junction） |
| 4 | 文字不重叠（pymupdf 逐 span bbox，容差 0.2mm） | ✅ 187 个 span，仅 **1 处**重叠：D7 符号自带引脚名 K/A（符号级 quirk，同第 3 轮 §1.1） |
| 5 | `sch_conn.py` 连通性 | ✅ **P0 = 0**；P1 = 2（`isolated_pin_label` + 网络名单脚，均为 BAT+，01 页未画的跨页预期）；同网多名 0、死头 0、孤立引脚 0、网表找不到的名字 0 |
| 6 | 网表逐脚 | ✅ 12 器件 28 脚 + 1 NC，与 §2 全表一致；`VIN_R` 新增正确 |
| 7 | PDF 04 页渲 PNG 目视 | ✅ 图名/说明回左上角、无导线穿 U4 本体、C42/C44 间距足够、文字不压线 |
| 8 | 幂等 | ✅ 跑两次 md5 相同（`0d2f6dc5a4b1eb13708ec55b6e4f6275`） |
| 9 | ERC `--severity-all` | ✅ `/辅助电源/` 页 **0 条**；根图 1 条 `isolated_pin_label BAT+`（预期） |
| 10 | Footprint 非空且与库一致 | ✅ 12/12（§1 表） |

---

## 4. 遗留 / 待主代理

1. **R42（C17903，10Ω 1% 1206）是新器件，`docs/02-BOM.csv` 尚无该行**，需主代理补 BOM 行（本轮交付不含 BOM 更新）。
2. **D7 引脚名 K/A 重叠**：嘉立创 SS210 符号的引脚名 K/A 无显式位置、被 KiCad 自动摆到本体中心彼此重叠，纯观感、
   不影响 ERC/网表（第 3 轮已记录在案）；若要在图内消除只能改本图嵌入符号（得不偿失），留主代理定夺。
3. **BAT+ `isolated_pin_label`**：01 页（功率回路）未画导致，01 页画好后自动消失（跨页项）。
4. `lib_symbol_mismatch`（L1 电感 arc 归一化误报）本轮 ERC **未再出现**（与第 3 轮一致），无需处理。

---

## 附 · 第 3 轮历史报告（以下为第 3 轮交付时内容，仅作追溯，不再更新）

# 04_power_supply（辅助电源）画图报告 · 第 3 轮

- 生成脚本：`hardware/gen/gen_04_power_supply.py`（幂等，UUID 用 `uuid.uuid5` 派生，跑两次输出逐字节相同）
- 自检脚本：`hardware/gen/check_04_layout.py`（几何检查 1–3，直接解析生成的 `.kicad_sch`）
- 产物：`hardware/04_power_supply.kicad_sch`
- 依据：`docs/03-详细设计.md` 第 5 节 + `datasheets/C87080_TI_LMR16006XDDCR.pdf` 第 3 / 11 / 13 页
- 上一轮：第 2 轮报告见本文件「历史（第 2 轮）」章节，纪律全部沿用

---

## 0. 第 3 轮变更（版面返工，只改版面不改连接）

1. **消灭「VIN_F 导线横穿 U4 本体」P0**：U4 每个脚引 ≥5.08mm 短线，线端放局部标签
   （`VIN_F`/`SW_3V3`/`CB_3V3`/`FB_3V3`）或 `GND` 全局标签，组与 U4 之间靠同名标签相连。
   不再有任何导线穿过 U4 本体或其它引脚端点。
2. **分组重排（左→右、电源上地在下）**：输入保护（BAT+→F11→C40/C42）一组 →
   续流/电感/输出（D7→L1→C43）一组 → 反馈（R40→R41）一组；C41 自举电容放 U4 上方，
   两端各用 `CB_3V3`/`SW_3V3` 标签；D7 改为横放（阴极左接 SW、阳极右接 GND）。
3. **位号/值重排**：竖放两脚件位号与值都放器件右侧、水平书写（字段角 `(360−rot)%360`
   抵消符号旋转）；横放件位号在上、值在下；U4 位号在上、值在下。修正「4.7µF 100V 竖排压线」、
   「LMR16006XDDCR 跑到 D7 下方」「C40/C42/C43 位号值压线」等第 2 轮问题。
4. **放大布局**：器件间距 ≥12.7mm，电路居中偏上（约 x 40–320mm / y 66–128mm），
   说明文字移到电路下方（y≈175/188），不与任何图元重叠。
5. `title_block.rev` → `v0.3-draw-r3`。

**网表逐脚与第 2 轮完全一致**（只改版面，不改连接）：见 §1 自检第 6 项。

---

## 1. 自检结果（第 3 轮任务书 8 项）

| # | 检查 | 结果 |
|---|---|---|
| 1 | 导线不许经过非端点的引脚 | ✅ PASS（`check_04_layout.py`，22 段导线逐一判） |
| 2 | 导线不许穿过符号本体 | ✅ PASS（符号 rectangle/polyline/arc/circle 包络 + 实例坐标变换） |
| 3 | T 型连接必须有 junction | ✅ PASS（唯一 T 接点 x=304.80 已放 junction） |
| 4 | 文字不重叠（pymupdf 逐 span bbox，容差 0.2mm） | ✅ 电路区 143 个 span 两两检查 **0 重叠**（唯一例外：D7 符号自带的引脚名 K/A 重叠，见 §1.1） |
| 5 | `sch_conn.py --show` | ✅ ②③ 部分 **P0 = 0**；③「同网多名」= 0；ERC 只剩 BAT+ `isolated_pin_label`（P1，预期） |
| 6 | 网表逐脚与第 2 轮一致 | ✅ 24 脚「位号.脚→网络名」映射 **0 diff** |
| 7 | PDF 04 页渲 PNG 目视 | ✅ 问题 1–3 全部消失（无导线穿 U4 本体、文字不压线、布局放大居中偏上） |
| 8 | 幂等 | ✅ 跑两次 md5 相同（`7c6c3570328407a6e9d7e61621cfc988`） |

### 1.1 自检第 4 项的唯一例外（符号级 quirk，非本图文字摆放问题）

`D7`（jlc:SS210 二极管）的**引脚名 `K`/`A`** 被 KiCad 自动摆到符号本体中心、彼此重叠约 1.9mm。
- 证据：pymupdf 实测 `K` bbox=(227.8,79.2,229.1,81.1)、`A` bbox=(228.1,79.2,229.2,81.1)（mm），
  二者几乎完全重合；而引脚号 `1`/`2` 分别正确落在左右引脚处。
- 根因：SS210 库里两条 pin 的 `(name "K")`/`(name "A")` 未给显式位置，KiCad 自动摆放时把两个
  名字都归到本体中心。这与第 2 轮 `lib_symbol_mismatch`（电感 arc）同类，属**嘉立创符号库 quirk**。
- 影响：仅 D7 一处、纯观感；不影响 ERC/网表/连通（第 5、6 项已证）。横放、竖放都重叠。
- 处置：不改库（纪律）；若要在图内消除，只能改本图嵌入符号（会在 `lib_symbol_mismatch` 上新增一条，
  得不偿失），故本轮记录在案、留主代理定夺是否值得为 D7 单独处理。

---

## 附 · 第 2 轮历史报告（以下为第 2 轮交付时的内容，仅作追溯，不再更新）

## 第 2 轮变更（主代理核查结论，全部照做）

1. **lib_id 带库昵称 `jlc:`**：嵌入 `(lib_symbols …)` 的顶层符号名写 `(symbol "jlc:NAME" …)`（与 lib_id 完全一致），
   其下子单元仍写 `(symbol "NAME_0_1" …)`（不带昵称）。改后第 1 轮 11 条 `lib_symbol_issues`
   （"does not include the symbol library ''"）**全部消失**。
2. **引脚电气类型不再在脚本里改**：库 `jlc.kicad_sym` 全部 497 脚已由 `fetch_jlc_parts.py` 归一为 `passive`，
   本图从库**原样复制**（只改顶层符号名加 `jlc:` 前缀），保证嵌入符号与库一致。
3. **位号统一「前缀+数字」40 段**（见 §1 对照表）：`C_IN_E→C40`、`C_BST→C41`、`C_IN1→C42`、
   `C_OUT1→C43`、`R_FB1→R40`、`R_FB2→R41`；`U4/F11/D7/L1` 不变。
4. **删 D6（SMBJ33A）**：BAT+ 上 01 页 D3 SMDJ33A 已钳位 ≈53V < LMR16006 VIN 绝对最大 65V，本页不再有输入 TVS。
5. **C40（原 C_IN_E）换料**：JIERR **RV63V47M6X8**，47µF **63V** 105℃，LCSC **C48971005**，
   封装 `jlc:CAP-SMD_BD6.3-L6.6-W6.6-LS7.3-FD`。电解正负极引脚号已重新核对（见 §3）。
6. 电路说明文字同步（去掉 D6、标注 C40 47µF/63V）；title_block `rev` → `v0.3-draw-r2`。

**新发现（需主代理定夺）**：改对后 ERC 出现 1 条 `lib_symbol_mismatch`（L1 电感），经二分定位是
KiCad 10.0.6 对电感符号「4 段半圆 arc」的失配误报，**本图嵌入符号与库逐字节一致**，非本图电路问题。详见 §4.1。

---

## 1. 位号对照表（新位号 ↔ `docs/02-BOM.csv` 旧位号，BOM 由主代理统一改）

| BOM 旧位号 | 本图新位号 | 器件（LCSC） | 值 | 封装 |
|---|---|---|---|---|
| C_IN_E | **C40** | RV63V47M6X8（C48971005） | 47µF **63V** | jlc:CAP-SMD_BD6.3-L6.6-W6.6-LS7.3-FD |
| C_BST | **C41** | CL05B104KO5NNNC（C1525） | 100nF 16V | jlc:C0402 |
| C_IN1 | **C42** | FS32X475K101EGG（C381466） | 4.7µF 100V | jlc:C1210 |
| C_OUT1 | **C43** | CL21A226MAQNNNE（C45783） | 22µF 25V | jlc:C0805 |
| R_FB1 | **R40** | 0402WGF3302TCE（C25779） | 33k 1% | jlc:R0402 |
| R_FB2 | **R41** | 0402WGF1002TCE（C25744） | 10k 1% | jlc:R0402 |
| U4 / F11 / D7 / L1 | 不变 | LMR16006XDDCR / 0466001.NRHF / SS210 / SWPA5040S220MT | — | — |
| D6 | **删除** | （SMBJ33A，本轮删） | — | — |

---

## 2. 手册外围件点名表（规则 00 ①a，第 11 页 Figure 9）

Figure 9 是「5V/0.6A 典型应用」，逐件与本图对应（第 1 轮已核，位号按 §1 更新）：

| Figure 9 外围件 | 功能 | 本图位号 | 连接 | 核对 |
|---|---|---|---|---|
| Cboot 100nF | 自举电容 | **C41** | U4.CB(1) — C41 — SW_3V3 | ✅ 手册 Pin 1「Connect Cboot cap between CB and SW」 |
| L1 22µH | 输出电感 | **L1** | SW_3V3 — L1 — +3V3 | ✅ 22µH |
| D1（续流肖特基） | 非同步 buck 续流 | **D7** | 阴极接 SW_3V3、阳极接 GND | ✅ 手册 Pin 6；方向：阴极接 SW |
| Cin | 输入电容 | **C40 + C42** | VIN_F — GND | ✅ 电解 47µF/63V + 陶瓷 4.7µF/100V |
| R1（上分压） | 反馈上电阻 | **R40** | +3V3 — FB_3V3 | ✅ 33k |
| R2（下分压） | 反馈下电阻 | **R41** | FB_3V3 — GND | ✅ 10k |
| Cout | 输出电容 | **C43** | +3V3 — GND | ✅ 22µF/25V |
| SHDN 100k 上拉 | 使能 | —（未画） | SHDN 悬空 | 见 §5 建议 |

**Pin Functions（第 3 页）逐脚点名**（U4 = LMR16006XDDCR，TSOT-6）：同第 1 轮，未变（1=CB、2=GND、3=FB、4=SHDN、5=VIN、6=SW）。

**续流二极管反压校核（第 13 页）**：手册要求 ≥1.25×VIN_max；VIN_max = 53V → 66.25V；SS210 = 100V ✅。

---

## 3. 极性件引脚核对（本轮重点：新 C40 电解）

| 器件 | 符号引脚名/号 | 封装极性丝印 | 本图方向 | 结论 |
|---|---|---|---|---|
| **C40 RV63V47M6X8** | 符号（横放）：pin 1 在左、带「+」号（两条线段交叉），pin 2 在右、弧形极板（负极） | 封装 `CAP-SMD_BD6.3-L6.6-W6.6-LS7.3-FD`：pad 1（x=−2.67，左）丝印「+」（竖条 + 横条交叉），pad 2（x=+2.67，右）丝印单横条「−」 | 正极(pin1)→VIN_F，负极(pin2)→GND | ✅ 符号 pin1=正极 ↔ 封装 pad1=正极 一致；接线正极接高电位 |
| D7 SS210 | 1=K（阴极）、2=A（阳极） | SMA 封装色带标阴极 | 阴极→SW_3V3，阳极→GND | ✅ 续流管方向正确（阴极接 SW） |

> 核对方法：读符号 `pin name/number`（RV63V47M6X8 的 pin 1 在符号坐标 x=−5.08 侧、附近画有「+」；
> pin 2 在 x=+5.08 侧、对应弧形极板）与 `jlc.pretty/CAP-SMD_BD6.3-L6.6-W6.6-LS7.3-FD.kicad_mod` 的
> 3 个 `fp_poly` 丝印（左竖条+左横条交叉成「+」= 正极；右单横条 = 负极）。符号与封装一致。
> 网表回读确认 C40 pin1 落在 VIN_F、pin2 落在 GND。

---

## 4. 连接表（网表逐脚回读，`kicad-cli sch export netlist`）

| 网络 | 节点（引脚） |
|---|---|
| BAT+ | F11.1 |
| VIN_F（局部） | F11.2、U4.5、C40.1、C42.2 |
| +3V3 | L1.2、C43.2、R40.1 |
| SW_3V3（局部） | U4.6、D7.1、L1.1、C41.2 |
| CB_3V3（局部） | U4.1、C41.1 |
| FB_3V3（局部） | U4.3、R40.2、R41.1 |
| GND | U4.2、C40.2、C42.1、D7.2、C43.1、R41.2 |
| unconnected-(U4-SHDN-Pad4) | U4.4（无连接标志，预期） |

- **无 `Pad??`** ✅；**无 `unconnected-*`**（除 SHDN 预期的 no_connect）✅。
- 每个器件实例的 **`LCSC` 字段在网表可见**（`<property name="LCSC" value="…">`），值与 §1 一致 ✅。
- 反馈输出电压：VFB=0.765V，Vout = 0.765×(1+33/10) = **3.29V** ✅。
- 与第 1 轮连接逐网一致（仅位号变化、D6 删除）。

---

## 5. 自检结果

| 检查 | 结果 |
|---|---|
| 幂等性 | ✅ 跑两次输出 md5 相同（`e10b0aa9370acc2d04ccef1272cddd65`） |
| ERC：`lib_symbol_issues` | ✅ **0 条**（第 1 轮 11 条「library ''」全部消失） |
| ERC：其余 | `isolated_pin_label` ×1（BAT+，01 页画好后消失，预期）；`lib_symbol_mismatch` ×1（L1，KiCad 误报，见 §5.1） |
| 网表逐脚核对 | ✅ 全部 10 器件、28 脚 + 1 no_connect 与 §4 一致 |
| 断线/死头 | ✅ 无 `pin_not_connected`（除 SHDN 预期）、无 `unconnected_wire_endpoint`、无 `label_dangling` |
| 短路/同网多名 | ✅ 无 `multiple_net_names` |
| 引脚号↔符号↔封装 | ✅ 符号引脚号与手册一致；封装 `jlc:*` 均存在于 `jlc.pretty/` |
| LCSC 字段 | ✅ 每器件实例带隐藏 `LCSC` 字段，值与 BOM 一致 |
| 无交叉线 / 无越界 / 文字不压线 | ✅ 目视 PDF 第 5 页：信号左→右、电源上地在下、D6 已删、C40 标 47µF/63V |

### 5.1 `lib_symbol_mismatch`（L1）—— KiCad 10.0.6 误报，非电路问题

- **现象**：ERC 报 `Symbol 'SWPA5040S220MT' doesn't match copy in library 'jlc'`（L1 电感），severity=warning。
- **证据 1（逐字节一致）**：本图 `(lib_symbols …)` 内嵌入的 `jlc:SWPA5040S220MT` 符号与库
  `hardware/lib/jlc/jlc.kicad_sym` 中 `SWPA5040S220MT` **token 级逐字节一致**（仅顶层名加 `jlc:` 前缀、
  缩进不同），符合任务书「原样复制」要求。
- **证据 2（二分定位）**：把库与本图 L1 符号**同时**删除 4 段 `(arc …)` 后失配消失；单独改 pin length
  1.27→2.54、删 `ki_description`、反转 arc start/end 均不消除。→ 根因是电感符号的 **4 段半圆 arc**
  在 KiCad 10.0.6 的「库加载路径」与「嵌入加载路径」内部归一化不一致导致的比较误报。
- **影响面**：库中另一颗同结构电感 **SLO0618H2R2MTT**（C216189，03_balancer 用，同样 4 段半圆 arc +
  pin length 1.27），画 03 页时会遇到同样的 `lib_symbol_mismatch`。
- **建议（不擅自改，留主代理定夺）**：在 `tools/fetch_jlc_parts.py` 增加「电感 arc 归一化」（类似现有
  `normalize_pin_types`，把电感符号的 4 段 arc 按 KiCad 规范重写或替换为 polyline），重新取库后即可消除。
  此为**库侧改动**，超出本图任务范围（纪律：不改库）。
- **说明**：该 warning 不影响网表/PDF/连通性——§4 网表逐脚核对全部正确。

---

## 6. 建议（未擅自改）

1. **SHDN 是否加上拉**：Figure 9 里 SHDN 经 100kΩ 上拉到 VIN；本设计按正文「Float to enable」悬空，
   手册明说「Internal pull-up … Float to enable」，悬空是正式用法，无需外加。若担心 EMI 可加 100k 上拉（DNP），
   本轮未加。
2. **`lib_symbol_mismatch`（L1 电感）**：见 §5.1，建议库侧归一化电感 arc。
3. **运输模式**（交接 §5-5）：如需硬件断电，预留 NMOS 拉低 SHDN（DNP），本轮未画。

---

最后一行回复 `DONE`。
