colemandlut/MP2645A-BMS/design/04_power_supply-review-opus-r2.md

# 04_power_supply（辅助电源）独立复核报告 · 第 2 轮（复核方 Claude Opus）

> 时间戳：2026-09-26 14:36 UTC
> 快照：`review/04-r4/`。`04_power_supply.kicad_sch` 的 md5 为 `0d2f6dc5…`，与 `hardware/04_power_supply.kicad_sch` 逐字节相同。
> 我在本机用 `kicad-cli 10.0.6` 对根图重新导出网表、重跑 ERC（`--severity-all`），结果与快照一致。本页 ERC 为 0；根图只有 1 条 `isolated_pin_label BAT+`，原因是 01 页还没画。
> 纪律：只读不改工程；没有读画图方的报告和生成脚本的注释。
> 手册页码按 PDF 页号引用，简称如下：
> - Tokmas = `datasheets/C54823941.pdf`
> - JDT = `C136343.pdf`
> - UR = `C17903.pdf`
> - RV = `C48971005.pdf`
> - SS210 = `C14996_SS210.pdf`

## 结论速览

| 档 | 条数 |
|---|---|
| **P0 不能投板** | **0** |
| **P1 必须改** | **2** |
| **P2 建议** | **12**（新增 7 条，沿用第 1 轮 5 条） |

### 第 1 轮问题的关闭情况

| 第 1 轮 | 状态 | 核实依据 |
|---|---|---|
| P0-1 Footprint 字段为空 | ✅ 关闭 | 网表 12 个器件都有 `<footprint>`，封装名与 `jlc.kicad_sym` 一致 |
| P1-1 删 D6 的前提 / VIN 缺少限幅 | ⚠ 部分关闭 | 已加 R42 10Ω，拓扑正确（`VIN_R` = {F11.2, R42.1}，`VIN_F` = {R42.2, C40.1, C42.2, C44.2, U4.5}）。残留问题见本轮 P1-2：输入陶瓷换成 2×1µF 后，尖峰余量取决于 C40 的高频 ESR |
| P1-2 F11 分断能力 / I²t | ✅ 关闭（换 JDT 后重核）| 见下方「F11 重核」。新的保护协调问题见本轮 P1-1 |
| P2-1 SHDN 悬空 | 改写为本轮 P2-1 | Tokmas 允许把 EN 直接接 VIN |
| P2-5 C40 手册缺失 | ✅ 关闭 | `C48971005.pdf` 已入库 |
| P2-6 陶瓷电容降额 | 改写为本轮 P1-2、P2-2 | 电容已换料 |
| P2-8 BOM 位号 / 制造商 | ✅ 位号已统一；C381466 已不用 | 第 3 点（封装库里的旧 LCSC 编号）沿用 |
| P2-9 可读性 | ✅ 原有 4 项都已改好 | 本轮新问题见 P2-6 |

---

## P0 不能投板

无。

---

## P1 必须改

### P1-1　R42 与 F11 的保护协调是反的：VIN_F 对地短路时，R42（通用 250mW 厚膜）先烧，F11 反而断不了

- **位号 / 网络**：F11（JDT JFC1206-1100FS）→ `VIN_R` → R42（C17903，1206W4F100JT5E）→ `VIN_F`。

- **故障电流**：假设 VIN_F 对地短路（C42/C44 1206 MLCC 板弯裂纹、C40 短路或 U4 VIN–GND 击穿）。
  - 回路电阻 = R42 10Ω + F11 冷阻 0.49Ω（JDT 第 3 页表，1A 档 490mΩ）。
  - 短路电流 I = V/10.49：电池 20V（低电量）时 1.91A，29.2V（满充）时 2.78A，53V（TVS 钳位）时 5.05A。
  - 这只相当于 F11 额定电流的 **1.9–2.8 倍**。JDT 第 2 页时间–电流规格只写了「1.0In ≥4h，2.5In ≤5s」，所以在 1.9–2.8A 下，F11 的熔断时间是**秒级**，1.9A 时甚至不保证会断。

- **R42 的耗散**：P = I²R，20V 时 36W，29.2V 时 77W，是额定 0.25W 的 **146–308 倍**。
  - UR 手册（第 5–6 页）只给出「2.5×RCWV（√(0.25×10) = 1.58V → 3.95V，即 1.56W）持续 5s」这一项短时过载，**没有脉冲曲线，也没有熔断或阻燃规格**。
  - 按热容估算：1206 整片氧化铝约 2.6mm³ × 3mJ/(mm³·K) ≈ 7.9mJ/K。77W 下初始升温约 1×10⁴ K/s，几十 ms 内膜层就会开裂或烧断，远早于 F11 熔断。
  - 厚膜在 29V 直流下断开时可能拉弧、使 PCB 碳化。这不是一个受控的失效方式，F11 在这种场景下形同虚设。

- **正常工况下 R42 没问题**：
  - 上电冲击能量 ≈ ½·48µF·29.2² × 10/(10.49 + ESR) ≈ 14–18mJ，持续约 0.5ms。热扩散深度 √(α·t) ≈ 70µm，受热体积约 0.17mm³，温升约 30–40K。✅
  - BAT+ 快关尖峰：90V（FET 雪崩限幅）时约 4mJ、13µs，温升几十 K。✅ 270V 极端情况下约 16–18mJ、3.3µs，R42 两端 241V，超过 1206 的最大工作电压 200V、低于最大过载电压 400V（UR 第 5 页），能量集中在膜层，**裕量不清楚**。

- **改法**（由取料方选具体料号，这里不代选 C 编号）：
  1. **首选**：R42 换成**熔断型阻燃电阻**（fusible / flame-proof，手册须给出「过载功率–熔断时间」曲线和阻燃等级），同时满足抗浪涌。这样短路时由 R42 受控开路，F11 作为二级保护。
  2. 或者 R42 用有脉冲曲线的**抗浪涌**型（2512 或同级），并把 F11 换成**慢熔、小额定**的型号，使 20V 下的短路电流 ≥ 约 10·In，熔断时间降到 ms 级。约束条件：
     - 上电 I²t 0.002 A²s 必须远小于该保险丝的熔化 I²t（JDT 0.25A 档的熔化 I²t 只有 0.0004 A²s，快熔型不行）；
     - R42 在熔断前吸收的能量 I²t·R 必须落在它的脉冲曲线内。
  3. 无论选哪种：PCB 上 R42 周围留净空，避开可燃物和其它网络。

### P1-2　输入陶瓷有效容量低于 Tokmas 推荐值；在设计假定的最坏 BAT+ 尖峰下，VIN_F 的余量取决于 C40 未知的高频 ESR

- **位号 / 网络**：C42、C44（2×CL31B105KCHNNNE，1µF/100V X7R 1206，C13832）与 C40，网络 `VIN_F`。
- **与手册的差距**：Tokmas 第 14 页写明「A X7R ceramic capacitor **4.7µF to 22µF** is recommended … and a **0.1µF** ceramic bypass … as close as possible to the VIN pin」。
  - 现在是 2×1µF，在 29–53V 直流偏压下合计只有约 **0.9–1.2µF**（BOM 第 63 行备注是 0.8–1.2µF；三星手册没有偏压曲线，这里是估算）。
  - 手册要求的 0.1µF 高频旁路也没有。
- **尖峰时的 VIN_F 峰值**：用 R42 10Ω → C_cer ∥（C40 47µF + ESR）数值积分。C40 的 ESR 手册只给了 120Hz 的 tanδ 0.14（RV 第 5 页，RV63V47M6X8），折算 **3.95Ω@120Hz**，高频值不详。

  | BAT+ 尖峰（L·I = 800µV·s） | ESR 1Ω | 2Ω | 4Ω |
  |---|---|---|---|
  | 90V / 13µs（FET 雪崩限幅），C_cer 1.2µF | 35.9V | 40.1V | 46.7V ✅ |
  | 270V / 3.3µs（设计 §2.2 的 800A 全部转入 D3 外推），C_cer 1.2µF | 50.6V | **61.9V** | **71.8V ❌ >65V** |
  | 同上，C_cer 按推荐值 4.7µF | 41.1V | 43.0V | 44.2V ✅ |

  结论：realistic 情况没有问题；极端情况下能否守住 65V，取决于一个手册没给的参数。按推荐值（4.7µF）配输入陶瓷时，对 ESR 不敏感。
- **改法（二选一，交用户定夺）**：
  1. 输入陶瓷恢复到**有效容量 ≥ 约 2.2µF**（例如名义 4.7µF/100V，或 2×2.2µF/100V），并在 U4.5 旁加 **100nF/100V 0402–0603** 高频旁路（详细设计 §2.2 已在用的 100V 料，不增加扩展库种类）。
  2. 保持 2×1µF，但在 VIN_F 上（R42 之后）加一颗 **SMAJ33A 级 TVS**。R42 已经把它的电流限在 ≤(270−53)/10 ≈ 22A、约 3µs，所以现在加是安全的。它短路失效时的保护，靠 P1-1 修正后的 R42/F11 协调。
- **说明**：这一条和用户 13:57「C42/C44 = 2×1µF」的换料决定冲突。我没有评估要不要换料，只核了额定值和手册推荐值，两边的依据都列在上面，请用户裁定。

---

## P2 建议

**本轮新增：**

**P2-1　Tokmas 允许把 EN（U4.4）直接接 VIN，建议接上，不再悬空**
- 依据：Tokmas 第 2 页「This pin supports high voltage input up to VIN supply to be connected VIN directly」；第 9 页「Connecting EN pin to VIN directly starts up the device automatically」；第 3 页 EN 绝对最大 65V。
- 好处：一根线就能消除悬空节点被 SW 耦合的顾虑。
- 顺带修正：符号上的引脚名还是 TI 的「SHDN」，页面说明文字也写「SHDN 悬空」，应改为 EN；阈值改为 1.21V 上升 / 1.07V 下降（Tokmas 第 4 页），不再是 TI 的 1.25V。
- 运输模式的下拉 NMOS 仍按详细设计 §5 的【待定】处理。

**P2-2　C43（C59461，22µF/6.3V X5R 0603）在 3.3V 偏压下有效约 10µF（估算），环路裕量无法从手册核实**
- 纹波没问题：600kHz、22µH 下 ΔIL ≈ (29.2−3.3)×0.113/(22µ×600k) ≈ 0.22A，ΔV ≈ 0.22/(8×600k×10µ) ≈ 4.6mV，满足 Tokmas 式 6 的 5mV 目标（第 15 页）。
- 环路存疑：Tokmas 的特性曲线和应用例都是 L = 33µH、Cout = 22µF（第 6、13 页；第 16 页选的是 22µF/16V X7R，有效值明显更高）。手册没有给出误差放大器跨导和补偿参数。按峰值电流模式估算，交越频率 ∝ (VFB/Vout)/Cout，本设计大约是参考点的 2.4 倍，相位裕量无法核实。
- 建议：用 **2×C59461 并联**（基础库，不增加上料种类），或者在台架上做 10→80mA 负载阶跃，确认没有振铃。

**P2-3　待机电流预算（目标 < 300µA）**
- Tokmas 静态电流 IQ 80µA 典型 / **109µA 最大**（第 4 页，4–60V 范围）。
- C40 漏电流规格 ≤ 0.01CV = **29.6µA**（RV 第 1 页，63V 下 2 分钟测得；29.2V 长期极化后通常低得多）。
- 反馈分压折算到输入约 13µA（第 1 轮 P2-2）。
- 这三项加起来最坏约 150µA，已占预算一半，再加 MP2797 和 MCU STOP 电流后需要重新核算。

**P2-4　SW 负压绝对最大值 −0.6V（直流）/ −4V（≤20ns）（Tokmas 第 3 页），SS210 的续流压降接近这个值**
- SS210 手册只给出 VF 最大 0.85V@2A 和典型曲线（第 1–2 页）。
- 输出短路时（限流 1.5A 典型，Tokmas 第 4 页），VF 约 0.7–0.8V，**整个关断期间**都超过 −0.6V。
- 正常 80mA 时 VF 接近 0.5V，低温下会更高。
- 建议上板后实测 SW 负压。TI 原件的规格是 −0.3V，同样的问题只是被普遍忽略。

**P2-5　字段与封装来源（规则 0e）**
- U4 的 `Datasheet` 字段仍然指向 TI C87080 的商品页，应改为 C54823941。
- F11 用的 `jlc:F1206` 是为 C151135（Littelfuse）取的封装，焊盘 1.19×1.728mm、中心距 ±1.45mm。JDT 推荐焊盘是 1.52 × 2.03mm、间隙 1.52mm（JDT 第 2 页）。应按 C136343 重新取封装，或用 `fp_compare` 核对后再决定。
- C42/C44 的 `jlc:C1206` 内的 `LCSC Part` 是 C15008。
- U4 沿用 C87080 的封装：Tokmas 第 18 页 D 2.92、E 2.80、E1 1.60、e 0.95，与封装一致 ✅。

**P2-6　可读性（规则 00 ③，PDF 第 5 页目视）**
- **T 形连接没有结点**：(289.56, 71.12) 处，C43.2 与 L1→+3V3 的两段导线三方相接；(215.90, 104.14) 处，C42.2 与 VIN_F 的两段导线三方相接。网表是连通的，但图上没有结点圆点，读图时会怀疑是否连接。
- **两脚无源件和二极管的符号同时显示引脚号与引脚名**，文字压在符号本体上：R42 本体里写着「1 2」，各电容的极板上有「1 | 2」，D7 的三角形里有「K / A」。建议在 jlc 库里对这些符号设置 `(pin_names hide)`。
- 说明文字「SHDN 悬空=常开」要改（见 P2-1）。

**P2-7　跨页依赖与布局约束**
- 01 页仍然是空的，D3 不在网表里。本页已经不再依赖 D3 的精确钳位值，但 P1-2 表中的「极端情况」要在 01 页复核 D3 与 SCP 关断速率后才能定论。
- `VIN_R`（F11 与 R42 之间）如果在 PCB 上对地短路，电流不受 R42 限制：29.2V/0.49Ω ≈ 60A，在 JDT 150A@32Vdc 的分断能力内 ✅；53V 瞬态时 ≈ 108A，超过 50A@63V（JDT 第 3 页）。所以 `VIN_R` 的铜皮要尽量短，并远离 GND。

**沿用第 1 轮（不展开）：**
- 沿用第 1 轮 P2-2：R40/R41 放大 10 倍（330k/100k）可省约 12µA。
- 沿用第 1 轮 P2-3：+3V3 短路时 D7 耗散约 1.1W（Tokmas 限流 1.5A 典型），结温超过 125°C。
- 沿用第 1 轮 P2-4：L1 的 Isat 保证值是 1.60A，Tokmas 限流 1.5A 典型。详细设计 §5 仍写「Isat 1.9A」（那是典型值），应改。
- 沿用第 1 轮 P2-7（D7 部分）：SMA 可以换 SOD-123FL，但会从基础库变成扩展库。
- 沿用第 1 轮 P2-8 第 3 点：封装库内的 `LCSC Part` 旧编号（C0402→C1554、R0402→C17168、C1206→C15008、F1206→C151135）。BOM 只能从符号的 `LCSC` 字段导出。

---

## 专项核算（主代理本轮点名的问题）

### R42 本身
| 工况 | 算式 | 结果 |
|---|---|---|
| 正常 80mA 负载，输入 20V | I_in ≈ 3.3×0.08/(0.8×20) ≈ 16.5mA；压降 0.165V，功耗 2.7mW | ✅ |
| Tokmas 满载 1A，输入 20V | I_in ≈ 0.194A → 1.94V、**0.38W > 0.25W** | ⚠ 本设计负载 <80mA，不构成问题；但 R42 把 3V3 的可用电流限制在约 0.8A 以下（按 R42 达到 0.25W 计） |
| 上电冲击 | 14–18mJ，约 0.5ms，温升约 30–40K | ✅ |
| 快关尖峰 90V / 270V | 4mJ ✅ / 16–18mJ、241V ⚠ | 并入 P1-1 的选型要求 |
| VIN_F 对地短路 | 36–77W 持续到 F11 秒级熔断 | ❌ P1-1 |

### buck 输入稳定性（RC 滤波器与负输入阻抗）
- buck 的负输入阻抗 |Zin| = V²/P：80mA 负载、20V 输入时 ≈ 20²/0.33 ≈ 1.2kΩ；1A 满载时约 103Ω。
- RC 滤波器（没有电感）的输出阻抗 |Zs| ≤ R42 = 10Ω，所以 |Zs| ≪ |Zin|，比值大于 10–100 倍。✅
- 直流工作点稳定的条件是 R < V²/(4P)：80mA 时约 300Ω，满载时约 25Ω，都大于 10Ω。✅
- C40 的 ESR 较大（120Hz 下 3.95Ω）只会增加阻尼，对稳定性无害；它的影响只在 P1-2 的尖峰分压里体现。

### F11 重核（JDT JFC1206-1100FS，C136343）
| 项 | 手册 | 核算 | 结论 |
|---|---|---|---|
| 额定电压 / 分断能力 | 0.25–4A 档：72V/50A、63V/50A、32V/150A、24V/300A（第 3 页） | VIN_F 短路最大 5.05A ≪ 50A | ✅ |
| 熔化 I²t（10In 下测得） | 0.10 A²s | 上电 I²t = 29.2²×48µF/(2×(10.49 + ESR)) ≈ 0.0015–0.002 A²s，为熔化值的 1.5–2% | ✅ |
| 冷阻 | 490mΩ | 17mA 下压降 8mV，功耗 0.14mW | ✅ |
| 故障时的熔断速度 | 2.5In ≤5s | 短路电流只有 1.9–2.8In | ❌ P1-1 |

### Tokmas U4
| 项 | 算式 / 依据 | 结果 |
|---|---|---|
| 引脚 | Tokmas 第 2 页：1 BOOT、2 GND、3 FB、4 EN、5 VIN、6 SW；与 TI 符号的引脚号逐一对应，网表连接 CB/GND/FB/NC/VIN/SW 一致 | ✅（引脚名见 P2-1） |
| Vout | 0.770×(1+33/10) = **3.311V**。极限：0.750×(1+32.67/10.1) = 3.18V，0.790×(1+33.33/9.9) = 3.45V | 在 CH32V203（≤3.6V）和 SN65HVD230（3.0–3.6V）范围内 ✅ |
| R2 取值 | Tokmas 第 11 页建议 1k–100k；本设计 10k | ✅ |
| 最小导通时间 80ns（第 4 页），按 fsw 最高 690kHz 算，周期 T = 1.449µs | 53V：D = 3.8/53.5 = 0.071 → 103ns；60V：91ns；65V：84ns | 均 ≥ 80ns ✅（加 RC 后 VIN_F 实际 ≤ 约 47V，余量更大） |
| 输出电压上限 | Vo ≤ VIN − 4.5V（第 3 页） | VIN ≥ 7.8V 即可，而输入最低 16–20V ✅ |
| BOOT 电容 | 手册要求 ≥ 0.1µF、X5R/X7R、≥10V（第 16 页）；C41 为 100nF X7R 16V；BOOT–SW 绝对最大 6.5V | ✅ |
| 续流管 | 反压 ≥ 1.25×VIN_max = 66V；SS210 为 100V | ✅（负压见 P2-4） |
| 电感 | 按式 5（KIND 0.3、600mA）得 LMIN ≈ 28.6µH，实际 22µH 时纹波比约 0.39；80mA 负载下工作在 PSM | ✅（Isat 见沿用条目） |
| 耗散 | 导通 0.08²×0.95Ω×0.13 ≈ 0.8mW；开关损耗 < 30mW | 温升 < 3°C ✅ |

### C43 / C42 / C44
见 P2-2 与 P1-2。

---

## 覆盖清单

### A. 连通性
| 项 | 结果 |
|---|---|
| 本页 ERC / 根图 ERC | 0 / 1（`isolated_pin_label BAT+`，01 页未画，属跨页项）✅ |
| 单节点网络 | 只有 `unconnected-(U4-SHDN-Pad4)`，有 NC 标志（P2-1 建议改为接 VIN）|
| 两脚件一端悬空 / 同网多名 / 名字消失 | 无 ✅（13 个标签都在网表里；`VIN_R`/`VIN_F` 分开）|
| 网络清单 | BAT+ = {F11.1}；VIN_R = {F11.2, R42.1}；VIN_F = {R42.2, C40.1+, C42.2, C44.2, U4.5}；CB_3V3 = {U4.1, C41.1}；SW_3V3 = {U4.6, C41.2, D7.K, L1.1}；+3V3 = {L1.2, C43.2, R40.1}；FB_3V3 = {U4.3, R40.2, R41.1}；GND = {U4.2, C40.2, C42.1, C43.1, C44.1, D7.A, R41.2} ✅ |
| 第 1 轮提到的「VIN_F 导线穿过 GND 脚、共线重叠」 | 已重画，现在 24 段导线里没有共线重叠，也没有导线端点落在另一段导线中间 ✅ |

### B. 手册外围件逐一点名（Tokmas 第 13 页 Figure 13）
| Figure 13 | 本图 | 结论 |
|---|---|---|
| C1 0.1µF（VIN 旁路） | 无 | P1-2 |
| C2 2.2µF + C3 10µF（输入陶瓷） | C42 + C44（2×1µF）+ C40 电解 | P1-2 |
| C4 0.1µF（BOOT） | C41 | 已核对无问题 |
| L1 33µH | L1 22µH | 已核对（P2-2、沿用 P2-4）|
| D1 | D7 SS210，阴极接 SW | **方向正确**；P2-4 |
| R1 / R2 | R40 33k / R41 10k | 已核对无问题 |
| C5 22µF（输出） | C43 22µF/6.3V 0603 | P2-2 |
| C7 100pF 前馈（可选） | 无 | 手册标为可选；可作为 P2-2 的补救手段 |
| R3 / R4（EN 分压 UVLO，可选） | 无（EN 悬空） | P2-1 |

### C. 器件级：符号 ↔ 封装 ↔ LCSC ↔ BOM
| 位号 | 符号 / 封装 | 极性 | LCSC（原理图 / BOM） | 额定值 | 结论 |
|---|---|---|---|---|---|
| U4 | TI 符号 / SOT-23-6（尺寸与 Tokmas 一致） | — | C54823941 / C54823941 | VIN 65V 绝对最大 | 已核对（P2-1、P2-5）|
| F11 | `jlc:F1206` | — | C136343 / C136343 | 72V / 50A | P1-1、P2-5 |
| R42 | `jlc:R1206`（取库对应 C17903）；料号 1206W4F100JT5E 解码为 F = 1%、100J = 10.0Ω（UR 第 2 页）| — | C17903 / C17903 | 0.25W、最大工作电压 200V | **P1-1** |
| C40 | 6.3×7.7 封装，焊盘 1 = + | 1 接 VIN_F，正确 | C48971005 / C48971005 | 63V、纹波 63mA | 已核对（P1-2、P2-3）|
| C41 | C0402 | — | C1525 / C1525 | 16V X7R | 已核对无问题 |
| C42、C44 | C1206 | — | C13832 / C13832 | 100V X7R | P1-2 |
| C43 | C0603（取库对应 C59461）| — | C59461 / C59461 | 6.3V X5R，3.3V 下为额定的 52% | P2-2 |
| D7 | SMA，焊盘 1 = K | K 接 SW，正确 | C14996 / C14996 | 100V / 2A | P2-4、沿用 |
| L1 | IND 5×5 | — | C68434 / C68434 | Isat 1.6A（保证值）| 沿用 |
| R40、R41 | R0402 | — | C25779、C25744 / 同 | 0.25mW | 已核对无问题 |
| D6 | 已删除 | — | — | — | 本页已不再需要 D6 保护，但条件是 P1-1、P1-2 落实 |

### D. 电容完备性
- U4.5 VIN：P1-2。
- U4.1 BOOT：C41 ✅。
- +3V3 输出：C43（P2-2）。
- 工业输入电解：C40 ✅。

### E. 封装下探
- C43 已从 0805 降到 0603 ✅。
- R42 是 1206：按 P1-1，应往更可靠的方向选（熔断型 / 抗浪涌），不能再缩。
- D7 沿用第 1 轮意见。
- 其余件已经是满足约束的最小档 ✅。

### F. 可读性（PDF 第 5 页目视）
- 多余文字：无 ✅。
- 废弃线：无 ✅。
- 网络名：`VIN_R`/`VIN_F`/`*_3V3` 按功能命名 ✅。
- 越界：无 ✅。
- 重叠：两脚件的引脚名压在符号本体上（P2-6）。
- 交叉线：无 ✅。
- T 形连接缺结点：2 处（P2-6）。
