colemandlut/MP2645A-BMS/design/04_power_supply-task-draw-r3.md

# 画图任务书：子图 04_power_supply，第 3 轮（版面返工，接续第 2 轮）

工作目录 `/home/user/MP2645A-BMS`。纪律同第 1、2 轮任务书（`design/04_power_supply-task-draw-r1.md`、`-r2.md`）。
**先备份** `cp hardware/04_power_supply.kicad_sch /tmp/draw-backup/04_power_supply.r2.kicad_sch`，**先跑一遍脚本确认幂等**再改。
注意：主代理已用 `kicad-cli sym upgrade` 把 `hardware/lib/jlc/jlc.kicad_sym` 重存为 KiCad 当前格式（缩进变成 tab、去掉了重复定义），
你的脚本读库的解析逻辑若依赖旧格式要一并调整；嵌入符号仍从库**原样复制**（只把顶层名改成 `jlc:NAME`）。现在 ERC 只剩 BAT+ 一条，连接全对。

## 主代理目视 PDF 的结论：连接对，但版面不合格（规则 00 ③），本轮只改版面

1. **P0 级误导：VIN_F 的导线横穿 U4 本体**，从左侧 GND 脚（2 脚）端点上穿过、一直画到右侧 VIN（5 脚）。
   网表碰巧没把它们连上，但任何人看图都会读成「VIN 与 GND 短路」；而且 x≈（C42 右侧）处还有一条往下接 GND 标签的竖线端点落在这条 VIN_F 线上（没有结点）——同样误导。
   `sch_conn.py` 的几何并查集因此报了 `[P0] 同一连通域挂了多个网络名 ['GND', 'VIN_F']`。
2. **文字重叠**：C42 的值「4.7µF 100V」竖排压在自己的引脚和导线上；C40/C42/C43 的位号与值离器件很远或压线；
   「LMR16006XDDCR」这个值文字跑到了 D7 下方，像是 D7 的型号；CB_3V3 / FB_3V3 标签贴着 U4 引脚号。
3. **整张电路挤在 A3 左上角约 1/4 的区域**，器件间距太小。

## 本轮要求

- **U4 的引脚分布**：这个嘉立创符号左侧是 CB/GND/FB，右侧是 SW/VIN/SHDN。
  **不许让任何导线穿过符号本体或经过别的引脚端点**。做法：U4 每个脚都引出一段 ≥5.08mm 的短线，
  线端放**本页局部标签**（`VIN_F`、`SW_3V3`、`CB_3V3`、`FB_3V3`）或 `GND` 全局标签；输入保护/电容一组、续流/电感/输出一组、反馈一组，
  各组内部用导线，组与 U4 之间靠同名标签相连。自举电容 C41 放在 U4 上方，两端分别用 `CB_3V3`/`SW_3V3` 标签。
- 信号从左到右、电源在上地在下；每个接地器件的地用下方 `GND` 标签；器件间距 ≥ 12.7mm；整张电路放在图框中部偏上，放大布局，占 A3 可用区的一半左右。
- 位号与值：竖放的两脚件，位号和值都放在器件**右侧**、水平书写、互不重叠；横放的放在上方（位号）和下方（值）。U4 的位号在本体上方、值在本体下方。
- 说明文字保留一段（第 2 轮那段即可），放在电路下方，不与任何图元重叠。

## 自检（你必须写进脚本或单独的检查脚本并运行，结果写进报告）

1. **导线不许经过非端点的引脚**：对每段导线，任何引脚端点若落在它的内部（不是两端点）→ 失败。
2. **导线不许穿过符号本体**：导线段与任何符号本体矩形（用符号 rectangle/polyline 包络 + 实例坐标变换）相交且不是从引脚进入 → 失败。
3. **T 型连接必须有结点**：导线端点落在另一段导线内部时必须有 `junction`；**否则必须避免这种几何**。
4. **文字不重叠**：`kicad-cli sch export pdf` 后用 pymupdf `page.get_text("dict")` 取 04 页每个文字 span 的 bbox，两两不相交（容差 0.2mm）。
5. 跑 `python3 /tmp/pcbws/scripts/sch_conn.py hardware/mp2645a-bms.kicad_sch --show 'SW_3V3|VIN_F|FB_3V3|CB_3V3|\+3V3|GND'`：
   ② ③ 部分的 P0 必须为 0（③ 的「同网多名」也要 0），ERC 只剩 BAT+ `isolated_pin_label`。
6. 网表逐脚与第 2 轮完全一致（只改版面，不改连接）：导出前后两份网表，比较「位号.脚 → 网络名」映射，必须相同。
7. PDF 04 页渲成 PNG（dpi≥200）自己看一遍，确认上面 1–3 条问题都消失。
8. 幂等（跑两次 md5 相同）。

## 交付
更新脚本、原理图、报告（开头加「第 3 轮变更」与自检结果）。最后一行回复 `DONE`。
