colemandlut/MP2645A-BMS/design/04_power_supply-task-review.md

# 独立复核任务书：子图 04_power_supply（辅助电源）

你是**复核方**（规则 00c：与画图方不同厂商）。只读不改工程文件；报告写到
`design/04_power_supply-review-opus.md`（**必须落盘**，本轮第 N 轮的写法见文末）。
工作目录 `/home/user/MP2645A-BMS`。全部用中文。

## 纪律
- **不要读**画图方的自评/报告（`design/04_power_supply-draw-report.md`、`*-draw-*.out`），也不要读 `hardware/gen/` 里的生成脚本的注释来"采信"它的结论；独立重推。
- 输入只有：原理图 `hardware/04_power_supply.kicad_sch`、主代理导出的 ERC 与网表（路径见文末）、
  PDF 渲染（`review/04_power_supply.pdf`，可用 pymupdf 渲 PNG 目视）、数据手册 `datasheets/`、需求文档 `docs/03-详细设计.md` 第 1、5、7、8、9 节、`docs/02-BOM.csv`、上一轮复核报告（若有）。
- 可以自己跑 `kicad-cli sch erc` / `kicad-cli sch export netlist`（命令在本机可用，输出写到 /tmp）。
- 核约束时不能只问「器件在不在、值对不对」，必须问「**它串在哪里、并在哪里、电流从哪条路径走**」，并**算一遍最坏工况下每颗器件的耗散/电压应力**；推导链上游的前提也要核。

## 用户需求（原文要点）
8S LiFePO4 电池包 BMS（满充 29.2V，单节 3.65V；电池侧 TVS 钳位后最坏约 53V），持续放电 200A、充电 120A、SCP 800A。
辅助电源：由 BAT+ 直接降压到 +3V3（无 5V 轨），负载 < 80mA（MCU ~20mA、CAN 显性 ~17mA、LED/IO ~10mA），
待机目标总电流 < 300µA；器件全部用嘉立创料（符号 `LCSC` 字段），EDA 只用 KiCad。
接口契约：`BAT+`、`GND`（GND = BAT-，在 01 页分流器电池侧单点汇合，本页不出现 BAT- 标签）、`+3V3`。

## 必查清单（规则 00 原文要点）
- ⓪ 断线/死头：ERC `pin_not_connected`、`unconnected_wire_endpoint`；网表里 `unconnected-*` 单节点网络；两脚件一端悬空 = P0。
- ⓪b 短路：同一连通域两个名字（ERC `multiple_net_names`；网表里图上出现过的名字消失）。
- ①a 拓扑完备：打开 `datasheets/C87080_TI_LMR16006XDDCR.pdf`，第 3 页 Pin Functions 每一脚、第 11 页 Figure 9 每一个外围件，逐个在网表里点名。**非同步 buck 的 SW→GND 续流肖特基必须在，且方向正确（阴极接 SW）**；CB 电容接 CB–SW；反馈分压算输出电压。
- ① 电容完备：每个电源脚去耦；输入轨（工业/电池输入）**必须有电解**；陶瓷电容直流偏压降额（4.7µF/100V 在 29–53V、22µF/25V 在 3.3V 下的有效容量）；输出电容是否满足手册推荐范围与环路稳定。
- ② 封装下探：每颗无源件问"能不能再小一号"（判据：功率、耐压、电流、手焊）。
- ③ 可读性：目视 PDF——多余文字、废弃线、网络名按功能、无意义交叉、重叠、越界。
- 器件级：逐颗核**符号引脚号 ↔ 手册引脚功能 ↔ 封装焊盘**（打开 `hardware/lib/jlc/jlc.kicad_sym` 与 `hardware/lib/jlc/jlc.pretty/*.kicad_mod`），极性件（D6、D7、C_IN_E）接反 = P0；额定值（耐压、电流、功率、结温）按最坏工况算；`LCSC` 字段是否与 `docs/02-BOM.csv` 一致。
- 保护：F11（1A，0466001.NRHF）的额定电压/分断能力对 29.2V 电池源是否够；D6 SMBJ33A 的位置（保险丝前/后）与失效模式（TVS 短路失效时谁来断开）；SHDN 悬空的抗干扰与手册 Figure 9 的 100k 上拉差异；最小导通时间/占空比（29.2V→3.3V、53V→3.3V 在 700kHz 下）是否在手册能力内；续流管反压 ≥1.25×VIN_max。

## 输出格式（固定）
`P0 不能投板 / P1 必须改 / P2 建议` 三档，每条给 **位号 + 引脚/网络 + 依据（数据手册页码或算式）**，没有依据的意见不写。
另附**覆盖清单**：逐器件、逐手册外围件写「已核对无问题」或问题编号——只报问题不报覆盖的报告按未完成处理。
