colemandlut/MP2645A-BMS/docs/03-详细设计.md

# 8S LFP 200A BMS 详细设计（v0.3）

> 2026-09-26 · 上承 `01-系统设计说明.md`（v0.1 方案），本文与 v0.1 冲突处以本文为准。
> **v0.3 变更（用户指令）**：主动均衡先由 MP2645A ×2 改为 MP2643 ×7，又因成本改为**分立开关电容均衡（方案 B）**；
> 电源改为 LMR16006X 直降 3.3V；MOSFET/MCU 降本。改动集中在第 1、2.4、4、5、6、7、9、10 节与固件均衡策略。
> EDA：**KiCad 10.0.6**，工程骨架在 `hardware/`（由 `tools/gen_kicad_skeleton.py` 生成）。
> 计算：`python3 tools/bms_calc.py`，全部数值均可复算。
>
> **【待核】**＝需对照正式数据手册确认。手册已下载到 `datasheets/`（`tools/fetch_datasheets.py`），
> 第 4、5 节所用器件已按手册核对（注明出处）；其余 IC 的引脚级核对在画原理图时逐项完成
> （pcb-workflow 规则 00 ①a：按每颗 IC 手册的 Typical Application 图逐件点名外围件）。

---

## 0. 设计输入（冻结）与待确认项

| 项 | 取值 | 状态 |
|---|---|---|
| 电芯 | 8S LFP，**120Ah**（用户 2026-09-26 确认；1C = 120A，组能量 25.6V × 120Ah ≈ 3.07kWh） | ✅ 容量已定；❓ 型号/规格书待提供（持续放电倍率、充电倍率、温度窗口） |
| 放电 | 200A 持续 | 用户给定 |
| 充电 | **120A 持续（1C，同口）**，OCC 132A/3s | ✅ 用户 2026-09-26：电芯充电 1C、放电 10C |
| 通讯 | CAN 2.0B 500k（主），RS485 本版不画（用户 2026-09-27） | ❓ 对接逆变器协议待定 |
| 板框 | 占位 160×110mm，4 × M4 安装孔 | ❓ 待外壳/结构确认（规则 0 ①） |
| 板厂 | 嘉立创 4 层 1.6mm，外层 2oz / 内层 1oz【待核工艺可选项】 | — |

---

## 1. 层次划分与接口契约

| 页 | 文件 | 内容 | 对外网络 |
|---|---|---|---|
| 1 | `01_power_path` | 熔断器、CHG/DSG 各 8 并联 NMOS、栅极网络、分流器、TVS、预充、端子 | BAT+ BAT- PACK+ PACK- FET_MID CHG_G DSG_G SRP SRN NTC_FET NTC_SHUNT PRECHG_EN |
| 2 | `02_afe` | MP2797、采样 RC、NTC、通讯、采样端子 J5 | CELL0..8 SRP SRN CHG_G DSG_G FET_MID PACK+ **BAT+**（VTOP/REGIN 取电，用户 2026-09-27） NTC_* I2C_* AFE_ALERT AFE_WAKE +3V3 GND |
| 3 | `03_balancer` | 分立开关电容均衡：8 个互补半桥（AO3416/AO3415A，R-D 死区）、8 个施密特缓冲驱动、每节 100µF 本地储能、7 级飞电容、均衡节点熔断 | BAL0..8 BAL_CLK（**不含 GND**：VB0 不接 GND，首级交流耦合；用户 2026-09-27，`design/03_balancer-spec.md`） |
| 4 | `04_power_supply` | 输入保护、LMR16006X（直降 3.3V） | BAT+ BAT- +3V3 GND |
| 5 | `05_mcu_comm` | CH32V203C8T6、调试口、CAN、LED、按键（RS485 本版不画，用户 2026-09-27） | I2C_SCL I2C_SDA AFE_ALERT AFE_WAKE BAL_CLK PRECHG_EN CAN_H CAN_L +3V3 GND |

**地的定义**：`GND` = `BAT-`，在分流器**电池侧开尔文端子单点**汇合（功率地与信号地唯一汇合点，
规则 0 ⑤）。PACK- 是分流器的另一端，不是 GND。

**命名规则**：跨页一律用全局标签，统一用 `_` 分隔、按功能加前缀（`CELLn`、`BALn`、`NTC_*`、`I2C_*`），
符合规则 00 ⓪c。

---

## 2. 功率回路（01_power_path）

### 2.1 拓扑：高边、背靠背、**共漏**（用户 2026-09-27 按 MP2797 手册 Fig 26 p.121 / Fig 27 p.122 改定）

```
BAT+ ─F1─┬─ S[Q7..Q12 CHG]D ─┬─ FET_MID ─┬─ D[Q1..Q6 DSG]S ─┬─ PACK+
         │  (栅极参考=BAT+侧) │ (漏极公共点)│ (栅极参考=PACK+)  │
      TVS D3            Gate CHG_G    VMID←R214   Gate DSG_G      TVS D1,D2 + C1–C4 + C_PACK_E 47µF
BAT- ─────────── RS1 100µΩ ────────────────────────────────── PACK-
  (GND 单点, Net-Tie)  ↑SRP(电池侧)   ↑SRN(PACK− 侧)
```

- **CHG 管放电池侧，源极朝 BAT+**：关断时体二极管方向 BAT+→FET_MID，只能放电不能充电。
  **DSG 管放 PACK 侧，源极朝 PACK+**：关断时体二极管方向 PACK+→FET_MID，只能充电不能放电。
- **FET_MID 是两组的漏极公共点**，经 R214 100Ω 接 MP2797 的 VMID（电荷泵参考，VCP = VMID + 14.7V）。
- **栅极网络参考各自的源极**（手册 RCHG_PUP/DCHG_VGS 回电池正、RDSG_PUP/DDSG_VGS 回 PACK+；驱动器关断电平 CHG 参考 VTOP、DSG 参考 PACKP，p.14–15）：
  R_PUP1、DZ1、Q17 集电极接 **CHG 源极母线（BAT+ 侧）**；R_PUP2、DZ2、Q18 集电极接 **PACK+**。
- 旧版（v0.3 前）是「DSG 在电池侧、共源、两组栅极以 FET_MID 为参考」：两管全关时会被驱动器把某组栅极顶开、DZ 长期过流（论证见 `design/02_afe-spec.md` §6.2），已废弃。
- 待机模式（p.22）经 CHG 管体二极管导通，与本拓扑一致。

### 2.2 器件与取值（逐件算最坏工况耗散）

| 位号 | 器件 | 取值/型号 | 所在支路 | 最坏工况 | 耗散 / 裕量 |
|---|---|---|---|---|---|
| F1 | 熔断器 | 300A ANL/MEGA | 串联于 BAT+ | 200A 持续 | 选型 ≥1.5×，自身压降按手册 |
| Q1–Q12 | N-MOSFET | **Tokmas IPT012N08N5，C19626224**（v0.3 降本），85V/300A，Rds(on) 典型 0.9 / 最大 1.2mΩ，Qg 240nC，**Tj,max 150°C**，HSOF-8（封装 jlc:HSOF-8_IPT007N06N） | 每组 **6** 并联，两组串联 | 200A、Rds 取最大值、热态、均流偏差 15% | 单管 3.0W，**Tj≈105°C**（Rθja 20K/W，45°C 环境），距 Tj,max 余 45°C；通路 27.2W |
| RG1–12 | 栅极电阻（手册 RMG） | **100Ω 0402，C25076**（MP2797 Table 18「Required」100Ω；原 10Ω） | 与各管栅极串联 | 开关瞬态；关断 τ ≈ 100Ω×14.5nF ≈ 1.5µs | 平均功耗 ≪ 1mW |
| R_PUP1, R_PUP2 | 栅极 G-S 电阻（手册 RCHG_PUP / RDSG_PUP） | **10MΩ 0603，C7250**，每组 1 只：R_PUP1 接 CHG 栅极母线↔CHG 源极（BAT+ 侧），R_PUP2 接 DSG 栅极母线↔PACK+（共漏，用户 2026-09-27） | 并联 | Vgs 常通 | ≈0。**取代原 RGS1–12（100k×12）**：每组 6×100k=16.7kΩ 与驱动导通电阻 RDSG_ON 2.6kΩ 分压，Vgs 会从 10V 掉到约 8.6V |
| R_DRV1, R_DRV2 | 驱动输出保护电阻（手册 RCHG_DRVER / RDSG_DRVER） | **100Ω 0402，C25076**（Required） | CHG/DSG 引脚 → D4/D5 阳极与 RQB 公共点 | — | ≪ 1mW |
| DZ1, DZ2 | 栅极钳位稳压管（手册 DCHG/DDSG_VGS ≤16V） | MM3Z15，**C65676**，15V SOD-323（每组 1 只，阴极接栅极母线、阳极接本组源极：DZ1→BAT+ 侧，DZ2→PACK+） | 并联 | 驱动过冲时 | 驱动能力 mA 级，功耗 <50mW |
| Q17, Q18 | PNP 快速关断（**手册拓扑之外的增强，闸口 A 需专门复核**） | **长电 SS8550 Y2，C8542**（基础库），−25V/−1.5A，SOT-23（栅极母线 ≤15V，余量 10V） | E 接栅极母线，C 接本组源极（Q17→BAT+ 侧，Q18→PACK+，用户 2026-09-27） | 关断时释放 6×240nC = 1.44µC | 单次脉冲，平均 ≈0 |
| D4, D5 | 驱动隔离二极管 | **1N5819WS，C191023**（基础库），40V/1A，SOD-323 | 串在 R_DRV 与栅极母线之间（Vgs 少约 0.3V） | 导通时 | 电荷泵电流 µA–mA 级 |
| RQB1, RQB2 | PNP 基极电阻（原位号 RB1/RB2，与均衡 RB1–15 重号，已改名） | 1kΩ 0402 | R_DRV 之后 → PNP 基极 | — | ≪ 1mW |
| RS1 | 分流器 | **业展 ASR-S-7-0.1F，C6075508**（降本采用），100µΩ ±1%，15W，TCR ±200ppm，5930 封装（2 端子；MP2797 手册建议 0.2–5mΩ；**用户 2026-09-26 定为 0.1mΩ**，保护阈值按 0.1mΩ 换算） | 串联于 BAT-→PACK- | 200A | 4W / 15W；**TCR ±300ppm**，用 NTC_SHUNT 做固件温度补偿；2 端子，靠焊盘切分做开尔文取样；**SRP 取电池侧焊盘（=GND 单点，01 页用 Net-Tie 连 SRP 与 GND/BAT-），SRN 取 PACK- 侧**（手册 Fig 26 p.121、p.6 AGND 条；用户 2026-09-27 订正，旧 ASCII 图画反） |
| D1, D2 | TVS | SMDJ33A ×2，**DOWO C2976503**（第 1 轮可选项，用户 2026-09-26 14:46 采用）（参数同晶导微 C438163）（PACK+→PACK-） | 并联 | 关断尖峰 | VC≈53V < 80V×0.8=64V ✅ |
| D3 | TVS | SMDJ33A ×1（BAT+→BAT-） | 并联 | 电池侧线束电感能量 | 800A 下 ½LI²（L=1µH）=0.32J |
| C1–C4 | MLCC | 1µF/100V X7R 1206，**CCTC C282823**（第 1 轮可选项，用户 2026-09-26 14:46 采用），14 颗减为 6 颗 | PACK+→PACK- | 29.2V | 100V 在 29V 偏置下有效容量约 60%；只作高频旁路，浪涌能量由 TVS 吸收。**短路关断实测必须确认 PACK+ 峰值 < 64V，否则补回** |
| C5–C6 | MLCC | 1µF/100V X7R 1206，C282823 | BAT+→BAT- | 同上 | — |
| C_PACK_E（01 页画图时编号） | 电解 | 47µF/63V，**C48971005**（与 04 页 C40 同料） | PACK+→PACK- | 29.2V，尖峰 ≤53V | 手册 Table 18 CPACK_E 典型 47µF / 最大 200µF；兼作短路关断尖峰阻尼（用户 2026-09-27 采用） |

**快速关断原理**：驱动输出为高时，经 D4 给栅极母线充电，PNP 的 BE 结反偏、截止。
驱动输出拉低时，栅极母线电压高于基极，PNP 导通，直接把 6 颗管的栅极电荷（各经自己的 100Ω RMG）泄放到本组源极（CHG 组→BAT+ 侧，DSG 组→PACK+；共漏，用户 2026-09-27）。
两组各一套（充电方向短路同样需要快关）。

### 2.3 预充电路（可选，默认 DNP）

MP2797 的 DSG 软启动能限制浪涌，负载电容不大时不需要预充。若负载电容 > 10mF（如逆变器），就贴上：

| 位号 | 器件 | 取值 | 计算 |
|---|---|---|---|
| Q19 | P-MOSFET（BAT+ → 预充电阻） | Vishay SQ2361ES，**C727403**，-60V/-2.8A，177mΩ，SOT-23 | 峰值 0.97A：导通损耗 0.97²×0.177 = 0.17W，仅持续约 1s |
| Q20 | NPN / 小信号 NMOS | 电平转换，由 MCU PRECHG_EN 驱动 | — |
| RP1, RP2 | 预充电阻 | 2 × 15Ω 5W（**C334293**，是否绕线、能否承受 4.26J 脉冲【待核】；串联 = 30Ω） | 峰值 0.97A、28W；单次能量 ½CV² = **4.26J**（10mF）；t95 = 0.9s |
| DZ3 + R | PMOS 栅极钳位 | 12V 稳压管 + 10k/10k 分压 | Vgs 不超过 ±20V |

**软件保护**：预充超过 1.5s 仍 PACK+ < 90%×BAT+，判定为负载短路，立即关闭 Q19。
否则 RP 会持续承受 28W 并烧毁。电阻上消耗的能量恒等于 ½CV²，与阻值无关，所以只能靠限时保护。

### 2.4 端子与线束

| 位号 | 用途 | 型号建议 | 依据 |
|---|---|---|---|
| J1–J4 | BAT+ BAT- PACK+ PACK- | M8 螺柱 + 20×2mm 紫铜排 | 200A 下电流密度 5A/mm²；150mm 长、80°C 时 79.7µΩ、3.2W |
| J5 | 采样 CELL0..8 + NTC_CELL1/2 | **BOOMELE XH-13A，C40669**（第 1 轮可选项，用户 2026-09-26 14:46 采用）（XH 2.50mm 13P 立式，嘉立创封装实测 2.50mm、孔 1.0mm；嘉立创库存 244，量产前备货；前一版 Megastar C22366169，替代封装错成 2.54mm 的 C158025） | 规则 0b 取库教训。**画在 02 页；针脚 1 NTC_CELL1 / 2 GND（NTC1 回线）/ 3 NTC_CELL2 / 4 GND（NTC2 回线）/ 5–13 CELL0–CELL8**（NTC 放低压端，防线束短路把高压灌进 NTC 脚；用户 2026-09-27） |
| J6 | 均衡 BAL0..8 | **连欣 XDWF-C3030WV-2*5P，C18202166**（Micro-Fit 3.0 兼容 2×5 立式，手册 6A/针，嘉立创标 5A）。⚠ 封装针号之字形（奇数针 A 行、偶数针 B 行；连欣手册图上**没有针号**），**焊盘 n 接 BAL(n−1)，焊盘 10 空**（用户 2026-09-27）：A1 BAL0 / B1 BAL1 / A2 BAL2 / B2 BAL3 / A3 BAL4 / B3 BAL5 / A4 BAL6 / B4 BAL7 / A5 BAL8 / B5 空（防错位）；A 行 = 定位柱侧（手册 0.94mm），卡扣侧待样品确认。直线相邻针最多差 2 节。线束侧 Micro-Fit 胶壳按行编号，**按物理位置对针，不按针号**（`design/03_balancer-spec.md` §4） | 最重一根线 2I：300mV 时约 1A |

- **采样线与均衡线分开进板、分开连到电芯极柱**，否则安培级均衡电流会在采样线上产生几十 mV 误差。
- **每个均衡节点串 3A 快熔保险丝（1206，F300–F308（原 F2–F10），大毅 TA-I CFS12V3T3R00，C163126，32V，50A 分断，冷阻 23mΩ，工作温度 −20~105℃（第 1 轮可选项，用户 2026-09-26 14:46 采用；用户 2026-09-27 保持本料）**）。
  它们串在 J6 与板内节点之间，**只保护板上故障**（CB/CF 裂片、MOS 击穿：单节被短路时约 40–73A，约 1ms 内熔断；3.65–7.3V 下维持不了电弧，超过 50A 的低压分断按工程判断接受，用户 2026-09-27）。
- ⚠ **已知风险（用户 2026-09-27 决定）：均衡线束的电芯端暂不加保险丝**。线束磨破、相邻导线短路时，短路电流从电芯经线束直接回到电芯，**不经过板上的 F300–F308，没有任何保护**，单节电芯可提供上千安电流，存在线束烧毁/起火风险。缓解靠线束走向、护套、固定与防磨；如后续要加，建议每根 BAL 线在电芯极柱端串 5A 保险丝（大于板上 3A，保证板上故障先断板上）。
- 采样线的电流很小（被动均衡最大 45mA），板上靠 AFE 输入端的串联电阻限流（见 3.2）；**线束侧电芯端的采样线加保险丝**（线束件，用户 2026-09-27），板上电阻保护不了线束本身。

---

## 3. AFE：MP2797（02_afe）

### 3.1 外围件：按手册 Figure 27 / Table 18 逐件点名（用户 2026-09-26 同意补全；用户 2026-09-27 按 `design/02_afe-spec.md` 订正）

依据：`datasheets/C18198873_MPS_MP2797DFP-0000-T.pdf` p.122 Figure 27、p.123–124 Table 18、p.127 Table 22/23。
**逐脚分配、完整器件表与画法以 `design/02_afe-spec.md` 为准**（位号 2xx 段，用户 2026-09-27）。

| 手册位号 | 手册值 | 本设计位号 | 取值 / 料号 | 备注 |
|---|---|---|---|---|
| RVTOP_FLT / CVTOP_FLT | 20Ω / 470nF（Required） | R212 / C212 | 20Ω 0603 C22950 / 470nF 100V 0805 C5375914 | **BAT+** → VTOP（02 页接口加 BAT+，用户 2026-09-27） |
| NPN_REGIN | FZT853 示例 | Q201 | MMBT5551 C2145（160V、300mW） | 按 REGIN ≤5mA（≈0.11W）选；样板实测 REGIN 电流，>5mA 换 BCX56 C24280 |
| RREG / CREG | 500Ω / 1µF | R213 / C213 | 510Ω 0603 C23193 / 1µF 100V 1206 C282823 | BAT+ → RREG → NPN 集电极，CREG 在集电极对地 |
| CREGIN | 3.3µF（Required） | C214 | **10µF 10V 0603 C19702**（用户 2026-09-27；原 4.7µF C19666 在 5V 偏压下只剩约 2.7µF） | 5V 偏压下约 4.5µF |
| CVDD / C3V3 | 1µF / 1µF | C216 / C215 | 1µF 0402 C52923 | 3V3 脚是 AFE 自身输出（局部网络 AFE_3V3），**不接板上 +3V3** |
| CVREF | 1µF | C217 | 1µF 0402 C52923 | |
| CNTCB | ≤10nF | C218 | 10nF 0402 C15195 | |
| CVCP | ≥ΣCiss（Table 22），额定 80V×8/16=40V | C219（+C226 预留 DNP） | **100nF 100V 0805 C28233**（用户 2026-09-27；原 50V 0603 在 15V 偏压下可能 <87nF） | ΣCiss = 6 × 14.49nF = 87nF；按 Qg 等效 144nF 超表，样板实测 VCP 跌落 |
| CVMID / RVMID | 100nF / 100Ω | C220 / R214 | 100nF 100V 0805 C28233 / 100Ω 0402 | FET_MID（漏极公共点）→ VMID |
| CPACK_FLT / RPACK_FLT | 10nF（不得增减）/ 100Ω | C221 / R215 | 10nF 100V 0603 C282516 / 100Ω 0402 | |
| CSRP_GND / CSRN_GND / CSRN_SRP | 100nF ×3 | C210 / C211 / C209 | **100nF 16V 0402 C1525**（用户 2026-09-27） | |
| RSRP_FLT / RSRN_FLT | 100Ω | R210 / R211 | 100Ω 0402 | **SRP = 分流器电池侧，SRN = PACK- 侧** |
| RCELL_FLT / CCELL_FLT | 20–100Ω / 100nF | R201–R209 / **C201–C208（8 只）** | 33Ω 0805 / **100nF 50V 0402 C307331**（用户 2026-09-27） | C_CELL 跨相邻 VC 节点，8S 为 8 只（原写 9 只错）；见 3.2 |
| DAGND-C0 | 3.3V 稳压管 | D201 | BZT52C3V3 SOD-123 C353528 | K→VC0，A→GND |
| RCHG/RDSG_PUP、RCHG/RDSG_DRVER、RMG、DCHG/DDSG_VGS | 10MΩ / 100Ω / 100Ω / 16V | 见 2.2 | | 参考各自源极（共漏，见 2.1） |
| DBATT / DPACK_E / CPACK_E | TVS / TVS / 47µF | D3 / D1, D2 / C_PACK_E | SMDJ33A / 47µF 63V C48971005 | CPACK_E 为 用户 2026-09-27 新增 |
| RNTC_PUP / RNTC | 10k / 10k | R216–R219 / 线束探头 ×2 + RT3/RT4 | 上拉接 NTCB | 见 3.3 |
| RSENSE | 0.2–5mΩ | RS1 | 0.1mΩ（用户定） | 低于手册下限：电流 ADC 分辨率减半，固件温补 + 标定 |

其余（用户 2026-09-27 订正）：
- I2C 上拉 R220/R221 2.2kΩ 到 +3V3；-0000 版本通讯 CRC 默认关，固件置 `USE_COMM_CRC`=1。
- **xALERT 是推挽输出（高有效）→ R222 100k 下拉**；**WDT 悬空，严禁上拉**（手册 p.24：外部拉高即复位 MP2797；p.48 `WDT_RST_EN` 默认 1）。原文「xALERT / WDT 开漏上拉 10kΩ」作废。
- NSHDN（AFE_WAKE）R223 10k 上拉到本板 +3V3。
- 未用 C9–C16 按 Table 23 在芯片脚侧直接并到 C8；SDO、GPIO1–3、GPIOHV1、SBYDSG、N/C、WDT 悬空（Table 23）；固件 `CELL_S_CTRL` = 0x7。
- C_NTC 原 100nF 删除，改 **DNP（值 1nF 备用）**：NTCB 默认动态偏置（p.90），100nF 时 τ 0.5–0.9ms 建立不及。
- 本版不做 PACK 反接保护（PACK 反接会烧 PACKP），不做 MTP 编程（固件每次上电写寄存器）。

**VTOP 工作下限 18V**（EC 表 VTOP = 18–75.2V）：8 串 = 2.25V/节。欠压保护 2.5V/节 = 20V，余 2V；电芯过放到 2.25V/节以下时 AFE 超出规格，固件 UV 必须先于此动作。

### 3.2 电芯采样 RC 的取值（用户 2026-09-27 按手册定案：情况 B）

- **被动均衡电流流经 VC 串阻**：手册 Figure 28（p.125）的集成均衡管跨在 Cn 与 Cn−1 两脚之间，位于 RCELL_FILTER 之后；p.125 算例 4V、20Ω → 58mA（= 4 / (2×20 + 28)）。
- 取 R = 33Ω、C = 100nF（Table 18/19：R 20–100Ω，C 100nF）。均衡电流 I = V / (2R + Ron)，Ron 15/28/50Ω（p.13）：
  3.65V 时**典型 39mA、最大 45mA**（原文「58mA、R≈30Ω」是 4V 锂电 20Ω 的数，LFP 上达不到，作废）。
- 每只串阻最坏 P = 45.1mA² × 33Ω = **67mW**：0603（85°C 降额后 82mW）余量 1.22 不够，**用 0805（C17634，85°C 103mW，余量 1.5×）**。
- 同一时刻只均衡奇数节或偶数节（p.126），AFE 内部发热 4 × 42mW ≈ 0.17W，温升约 8°C。

### 3.3 NTC（用户 2026-09-27：电芯 NTC 改线束探头；RT3/RT4 在 01 页）

| MP2797 | 固件通道 | 网络 | 热敏电阻 | 模式 |
|---|---|---|---|---|
| NTC1 | 0 电芯 1 | NTC_CELL1 | **线束探头**（非嘉立创件，10k B25/50 = 3380K），经 J5.1/J5.2 双绞 | Cell |
| NTC2 | 1 电芯 2 | NTC_CELL2 | **线束探头**，经 J5.3/J5.4 双绞 | Cell |
| NTC3 | 2 MOSFET | NTC_FET | RT3 APV ANTC1608-103F3380FB C52155402（01 页，贴 MOSFET） | PCB |
| NTC4 | 3 分流器 | NTC_SHUNT | RT4 C52155402（01 页，贴 RS1） | PCB |

- 上拉 R216–R219 10k 接 **NTCB**（比例测量），均在 02 页；NTC 回线在 AGND 星形汇合（手册 p.120）。
- 板上 0603 的 RT1/RT2 测不到电芯温度，已从 BOM 删除。
- 立创标注 B 值为 **B25/50 = 3380K**，v0.1 写的“B3435”其实是这颗料的 B25/85。下表按 B25/50 = 3380K 计算，适用于 0~50°C。高温段（65°C、100°C）的保护阈值和固件查表，**直接用 APV 的 R-T 表**；线束探头须选同口径 B 值，或按其 R-T 表另建查表。

| 温度 °C | -20 | 0 | 25 | 45 | 55 | 65 | 100 |
|---|---|---|---|---|---|---|---|
| V_NTC / V_REF | 0.882 | 0.738 | 0.500 | 0.329 | 0.262 | 0.207 | 0.093 |

保护阈值（0°C、55°C、65°C、100°C）对应的比值相互间隔都 ≥ 0.05，ADC 分辨率足够区分。上拉电阻 1% 0402（C25744）。

---

## 4. 主动均衡：分立开关电容（03_balancer）—— v0.3 方案 B（用户 2026-09-26 选定；2026-09-27 按规格书修订）

> 历史：v0.2 MP2645A ×2（买不到）→ v0.3 初 MP2643 ×7（均衡部分约 ¥186/块，太贵）→ **本方案**（全部嘉立创料，均衡部分约 ¥40/块）。
> **画图以 `design/03_balancer-spec.md` 为准**（逐网连接表、J6 针脚、器件表）。用户 2026-09-27 采纳其中 U-1～U-5、U-7（保持 C163126）、U-8；U-6（线束电芯端保险丝）暂不加，见 2.4 的已知风险。

### 4.1 原理

```
板内节点 VB0…VB8（= BAL0…BAL8 经 F300–F308 之后）；每节电芯 k（VB(k-1)..VBk）一个互补半桥，输出 Xk：
    Q31k（AO3415A，S=VBk） ─┬─ Xk     GPk ← R32k 330Ω ∥ D31k（快关）← DRVk
    Q30k（AO3416， S=VB(k-1)）┘         GNk ← R31k 330Ω ∥ D30k（快关）← DRVk
    DRVk = U30k（74LVC1G17，VCC=VBk，GND=VB(k-1)）的输出
    DRVk 高 → Q30k 通 → Xk = VB(k-1)；  DRVk 低 → Q31k 通 → Xk = VBk
    每节本地储能 C31k 100µF 跨 VB(k-1)–VBk（线束只流直流）
飞电容 C33k ∥ C34k（2×100µF）接在 Xk 与 X(k+1) 之间（k = 1..7）：
    相位 1（全部高）：CFk 并在第 k 节上；  相位 2（全部低）：CFk 并在第 k+1 节上
时钟：BAL_CLK → R300 1k → C321 1nF → IN1；DRV(k-1) → C32k 1nF → INk；每节 R30k 100k 下拉到本节负极
```

全部 8 个半桥**同相**切换（每级都不反相），每个飞电容轮流并到相邻两节上，电荷自动从电压高的一节流向低的一节，**不用判断方向**。

**均衡电流**（`tools/bms_calc.py` 的 `sc_equalizer`，口径见规格书 §6.1，用户 2026-09-27 采纳）：

- 板上：R_SSL = 1/(f·C_eff) = 1/(75kHz × 100µF) = 0.133Ω（2×100µF 在 3.3V 偏置下有效约 100µF，样板实测）；
  R_FSL = 4 × (R_N 0.020 + R_P 0.042 + ESR/走线 0.015) × 1.08（死区修正）= 0.333Ω；R_板 = √(R_SSL² + R_FSL²) = 0.358Ω。
- 线束：有本地储能后线束只流直流，中间那根 BAL 线流 2I、两侧各 I，折算为 **6·R_w** 串联。R_w = 保险丝冷阻 23mΩ + 导线（0.5m 20AWG 约 17mΩ）+ J6 接触 + PCB ≈ 45mΩ，6·R_w = 0.27Ω。
- I = ΔV / (R_板 + 6·R_w) = ΔV / 0.628Ω。

| 相邻压差 | 10mV | 30mV | 100mV | 300mV |
|---|---|---|---|---|
| 典型（25°C） | 16mA | 48mA | **0.16A** | 0.48A |
| 热态 60°C / 最坏（最大 Rds、85°C、C 偏低） | 14 / 12mA | — | 0.14 / 0.12A | 0.43 / 0.37A |

- 原文的 0.19A 未计导线与端子电阻，已作废（用户 2026-09-27 改为 0.16A 口径）。
- 线束越短越粗电流越大：18AWG、≤0.3m 时约 0.18A@100mV；线束电阻为 0 时的上限约 0.28A。
- 增强选项（N/P 各并一只 + 时钟提到 100kHz）未采用。

### 4.2 器件（全部嘉立创，逐件核对手册；位号 3xx，旧位号见 `docs/02-BOM.csv` 备注）

| 位号 | 器件 | 立创 | 依据 |
|---|---|---|---|
| Q301–Q308（原 QN1–8） | PUOLOP AO3416，20V，21 典型 / 26 最大 mΩ@2.5V，Vth 0.45–1.0V | C479060 扩展库 | 1 G / 2 S / 3 D；Vgs = 本节电压 ≥ 3.0V 时约 19–20mΩ（手册 Fig 9） |
| Q311–Q318（原 QP1–8） | ElecSuper AO3415A，−20V，36/47mΩ@−2.5V（曲线约 42mΩ@−3V） | C5350990 扩展库 | 1 G / 2 S / 3 D；每管只承受一节电压 |
| U301–U308（原 UD1–8） | 74LVC1G17 非反相施密特缓冲，1.65–5.5V | C7394021（UMW） | 本节电芯供电；1 脚 NC |
| R311–R318、R321–R328（新增） | 330Ω 0402，栅极慢开 | C25104 基础库 | 与二极管组成死区网络（见 4.3） |
| D301–D308、D311–D318（新增） | 1N5819WS 肖特基，栅极快关 | C191023 基础库 | D30k：K→DRVk、A→GNk；D31k：A→DRVk、K→GPk |
| C301–C308（原 CD1–8） | 100nF/16V 0402，跨本节 | C1525 基础库 | U30k 去耦 |
| C311–C318（新增） | 100µF/6.3V X5R 1206，跨本节 | C15008 基础库 | 本地储能：没有它时线束电感（约 0.7µH）与 100nF 谐振，本节电源约 ±1V 振铃；加上后约 ±50mV；热插拔时 8 颗串联均压 |
| C331–C337、C341–C347（原 CF1–14） | 100µF/6.3V X5R 1206，每级 2 颗 | C15008 基础库 | 只承受单节电压（≤ 3.65V） |
| C321（新增）、C322–C328（原 CC2–8） | 1nF/50V 0402 | C1523 基础库 | C321：首级交流耦合；C32k：DRV(k−1) → INk |
| R301–R308（取代 RB1–15 的 1M×15） | 100k 0402，只下拉到本节负极 | C25741 基础库 | 空闲态确定为全低（见 4.3） |
| R300（原 R_CLK） | 1kΩ 0402 | C11702 | BAL_CLK（PA8，**75kHz**，50%）→ C321；限制地电位瞬变时的钳位电流 |
| F300–F308（原 F2–F10） | 3A 快熔 1206，32V，50A，冷阻 23mΩ，−20~105℃ | C163126 大毅（扩展库） | F30k 接 BALk；只保护板上故障（见 2.4） |

新增件全部是基础库且 BOM 已有同料号，上料费增量 ¥0；元器件约 +¥5.9/块。

### 4.3 时钟传递、死区与失效安全

- **死区（用户 2026-09-27 采纳 U-1）**：一个 74LVC 要驱动 N、P 两管的栅极，约 3.2nF（Qg 合计约 10.5nC），输出内阻 16–29Ω，边沿约 50–90ns，而不是手册 50pF 负载下的 2.9ns。
  共栅直驱时两管在这段时间里同时导通，估算直通峰值约 10A、每节 0.1–0.2W，而且各节不相等，会造成节间偏差。
  现在每个栅极接 330Ω（慢开）并联肖特基（快关），典型死区 20–50ns，最坏角点只剩阈值附近的小电流重叠。代价是 R_FSL 约 +8%（已计入 4.1）。
- **逐级交流耦合**：第 k−1 节的输出摆幅 VB(k−2)..VB(k−1)，经 1nF 耦合到第 k 节输入。输入只有 100k 下拉到本节负极，低于地的半波被 74LVC 输入对地钳位二极管拉住，所以输入实际摆幅约 −0.3V .. V_cell−0.3V。
  高电平比 VT+ 最大值高 0.4V 以上（发送节 3.0V、接收节 3.3V 这一最坏情况），低电平比 VT− 最小值低 1.2V。τ = 100k × 1nF = 100µs，75kHz 下下垂约 6%，**BAL_CLK 不能低于约 20kHz**。
- **首级也交流耦合，VB0 不接 GND（U-3）**：板上 GND 是分流器电池侧的 BAT−，VB0 是 BAL0 线束接的电芯 1 负极。两者在板上相连，BAL0 线束就和 200A 主回路并联，会分走约 0.8A。所以本页不用 GND，只用 BAL0..8 与 BAL_CLK。
- **失效安全（U-2）**：原方案「输入偏置到中点、靠迟滞保持最后状态」不成立（VCC 3.0V 时 VT+ 最小 1.48V，低于中点 1.50V；输入漏电 ±1µA 流过 500k 还有 ±0.5V 偏移）。一旦出现「第 k 节高、第 k+1 节低」，CFk 会长期跨在两节上（6.0–7.3V，超过 6.3V 额定）。
  现在是只接下拉：
  - MCU 停 PWM（停在低电平），或 MCU 复位（05 页 R52 100k 下拉），各节都回到**全低**：所有 P 管导通，CF1–CF7 分别并在第 2–8 节上，**无持续电流**，每颗飞电容只承受一节电压。
  - BAL_CLK 卡在高电平（MCU 死机）时，各节输入以 100µs 的时间常数衰减，也回到全低。其间最多约 30µs 的短暂混相。
  - **不需要光耦**。
- **静态功耗**：每节 74LVC 的 ICC ≤ 1µA（25°C），下拉电阻 0 电流。唯一的不对称是第 1 节上没有飞电容，少一份 MLCC 漏电，规格上限约 13µA，实际小一个数量级，可以忽略。
- **均衡运行时**：栅极驱动约 2.6mW/节（每节电芯 0.8mA），各节基本一致。整板功耗 100mV 时约 50mW，300mV 时约 0.2W。

### 4.4 约束与保护（固件，`firmware/src/bms_logic.c`）

- 只在**顶部区**（最高节 ≥ 3.40V 且压差 ≥ 30mV）或**静置 30min 且压差 ≥ 80mV** 时输出 BAL_CLK；压差 ≤ 10mV 时停止。开关电容只能按电压拉平，所以不能在 LFP 平台区常开。
- **压差 > 300mV 禁止均衡**，只告警。坏电芯或采样断线时电流可达安培级：1.3V 压差时约 2A，中间那根线流 4A，超过 3A 保险丝。
- **任一节 < 3.0V 禁止均衡**：半桥栅压取自本节电芯。
- 主动均衡结束后，仍由 MP2797 内部被动均衡做 mV 级微调（33Ω 串阻时典型 39mA、最大 45mA）。
- 单元测试：含顶部起停、平台区不开、压差异常禁止、低压禁止、静置、故障停止，以及电荷交换仿真（90mV → 10mV 收敛）。
- **规格书 X-5 的固件待办（尚未改代码）**：
  - BAL_CLK 保持 50–100kHz、50%；
  - 停时钟时停在低电平（TIM1 空闲电平 OIS1 = 0）；
  - 保留 IWDG；
  - 新增「均衡开着但相邻压差不下降」告警。BAL 线断、保险丝熔断、驱动失效，都只能这样发现，因为采样线是另一套，读 CELL 电压看不出来。

### 4.5 布局要点

- 8 节按电芯顺序排成一列：J6 在板边，F300–F308 靠近 J6。每节的半桥、本地储能 C31k、缓冲器、去耦、R-D 网络放在一起，C31k 紧贴两管源极。
- **各节的本地参考不同（VB0..VB7）**。相邻节之间只经飞电容和 1nF 耦合电容相连；均衡区不打 GND 过孔，VB0 不接 GND。
- 飞电容与两个半桥输出之间的回路尽量短而宽（最大约 1A，走线 ≥ 0.6mm）。
- 时钟耦合线远离功率 MOSFET 和分流器采样线；CELL 线与 BAL 线在板上完全分开。

### 4.6 性能说明（与 MP2643 方案对比）

- **优点**：均衡部分约 ¥40/块（MP2643 方案约 ¥186/块），全部嘉立创现货，大部分是基础库；无客供件、无光耦；固件简单。
- **缺点**：电流随压差减小（100mV 时约 0.16A）。120Ah 电芯 5% SOC 偏差（6Ah），按 0.16A 算需要约 **38h**（计 95% 效率约 39.5h）的累计顶部均衡时间；平台区基本不搬。适合**同批次、一致性好的电芯**做日常维护，电芯离散度大时应回到 MP2643 方案。

---

## 5. 辅助电源（04_power_supply）—— v0.3：LMR16006X 直降 3.3V，取消 5V 轨与 LDO

```
BAT+ ─F11 1A（JDT JFC1206-1100FS C136343，63V）─ VIN_R ─ R42 56Ω 1206 熔断电阻（C153337）─ VIN_F
        （D6 已删除；R42 与 C40 组成输入 RC：限上电 I²t、压 BAT+ 快关尖峰（最坏 VIN_F ≈39V），VIN_F 短路时 R42 受控熔断 —— 04 复核 P1，见 design/04_power_supply-parts-r5.md）
VIN_F ─┬─ C40 47µF/63V 电解（C48971005） + C42/C44 2×1µF/100V X7R 1206（C282823）+ C45 100nF/100V 0805（C28233）贴 VIN（规则 00 ①：工业输入必须带电解）
       └─ U4 Tokmas LMR16006XDDCR（C54823941）── L1 22µH ── +3V3（≤ 600mA，实际 < 80mA）；C43 22µF/6.3V 0603（C59461）
            SW→GND：D7 SS210（续流，必需）   CB–SW：C41 100nF   FB：R40 33k / R41 10k → 3.31V   SHDN：悬空 = 常开（内部上拉）
原理图位号（04 页）：U4 F11 R42 C40 C41 C42 C44 C45 C43 D7 L1 R40 R41
```

依据：`datasheets/C54823941.pdf`（Tokmas LMR16006，v0.3 第 2 轮降本采用，用户 2026-09-26）、`datasheets/C87080.pdf`（TI 原件，引脚兼容，保留作备选）。

| 检查项（规则 00 ①a 拓扑完备性） | 设计 |
|---|---|
| 器件 | **Tokmas LMR16006XDDCR，C54823941**，TSOT-23-6：VIN 4–60V（绝对最大 **65V** > 浪涌钳位 53V），1A，**600kHz**，PSM 轻载，**Iq 80µA 典型 / 109µA 最大**（TI 为 28µA，待机多约 50µA），VFB 0.770V；嘉立创库存 2670，10 片 ≈ ¥1.78（TI C87080 ¥3.40）。EasyEDA 无此料号的库，**符号/封装沿用嘉立创 C87080 的**（引脚与封装尺寸已按 Tokmas 手册逐项核对一致） |
| **非同步 buck → 续流肖特基必需** | **D7 SS210，C14996（基础库）**，100V/2A：手册要求反压 ≥ 1.25 × VIN_max（53V × 1.25 = 66V） |
| 自举电容 CBOOT（CB→SW） | 100nF 0402（C1525），手册典型应用值 |
| 电感 | 22µH SWPA5040S220MT（C68434，1.9A）：29.2V→3.3V、600kHz 纹波 ≈ 0.22A（峰值限流 1.5A < Isat 1.9A）；下方禁铜（规则 2d） |
| 反馈分压 | VFB = 0.770V（Tokmas）：R1 = 33kΩ（C25779）、R2 = 10kΩ（C25744），Vout = 0.770×(1+33/10) = **3.31V**（TI 0.765V 时 3.29V；均为基础库） |
| 输入 / 输出电容 | C_IN1、C_IN2 2×1µF/100V X7R 1206（C282823，29–53V 偏置下有效约 0.8–1.2µF）+ 47µF/63V 电解（C48971005，原 50V 低于 53V 浪涌）；C_OUT1 22µF/6.3V X5R 0603（C59461，3.3V 下有效约 10µF） |
| SHDN | 高压容忍、内部上拉，悬空即开启；拉低 < 1.25V 关断。本版常开，**不再需要 MCU 自保持和唤醒或门**；运输模式如需断电，预留一只 NMOS 拉低 SHDN（DNP）【待定】 |

**功耗预算（+3V3）**：MCU 约 20mA、CAN 显性约 17mA、LED 与 AFE IO 约 10mA，合计 < 50mA（开关电容均衡由电芯自身供电，不占 3.3V）。
**待机**：MCU 进 STOP，buck 轻载 PSM（Tokmas Iq 80µA 典型 / 109µA 最大）；总待机电流需加上 MP2797 与 MCU STOP 电流后校核（目标 < 300µA）。

---

## 6. MCU 与通讯（05_mcu_comm）

| 项 | 设计 |
|---|---|
| MCU | **WCH CH32V203C8T6，C3001172**（v0.3 降本，替代嘉立创库存为 0 的 STM32G0B1）：RISC-V 144MHz，64KB，CAN 2.0B，I2C×2，USART×4，12 位 ADC，LQFP48【引脚分配按 `datasheets/C3001172.pdf`】 |
| 时钟 | **12MHz 晶振 YXC X322512MSB4SI（C9002，基础库，降本采用；3225，±20ppm，CL=20pF）+ 2×33pF（C1562，用户 2026-09-27：CL20pF+杂散 2–7pF）**；CH32V203 HSE 12MHz × PLL12 = 144MHz（固件 HSE_VALUE 按 12MHz）（CAN 对时钟精度要求高，HSI 的 ±1% 在 500k 下余量偏小） |
| 外设分配 | I2C1 → AFE；CAN1（2.0B）→ CAN；USART2 + DE 预留（RS485 本版不画）；SWD + 调试串口 USART1（PA9/PA10）；EXTI ← AFE_ALERT；**定时器 PWM → BAL_CLK（75kHz，开关电容均衡时钟）**；GPIO → PRECHG_EN、LED×3、按键（PWR_EN 已删：v0.3 取消电源自保持，用户 2026-09-27）；逐脚分配见 `design/05_mcu_comm-spec.md` §1.3 |
| CAN 收发器 | **HGSEMI SN65HVD230M/TR-HG，C55259679**（第 2 轮降本采用，TI C12084 引脚兼容替代；待机 400µA 典型）（v0.3：**3.3V 单电源**，取消 5V 轨；VCC 一颗 100nF；**Rs 经 0Ω 接地 = 高速模式**（原 10kΩ 实为斜率控制约 15V/µs；通讯速率未定，取高速以兼容到 1Mbps；保留焊盘，EMC 不过时改 10k–47k 限斜率）） |
| CAN 终端 | 单电阻 120Ω **0603** R55（C22787，基础库；显性位约 33mW，0402 余量偏紧）**串 JP1 2P 2.54 排针（C492401）+ 跳线帽（C100114）**：插帽接入终端、拔帽不用（用户 2026-09-27）；去掉分裂终端 |
| CAN 保护 | **UMW PESD2CAN，C2687131**（SOT-23，第 2 轮降本采用，参数同 Nexperia C75176）紧靠连接器；共模电感预留（DNP） |
| RS485 | **本版不画**（用户 2026-09-27：协议未定、无连接器落点）；PA2/PA3/PA4 保留不挪用，下一版需要时按规格书 §4.2（SP3485EN C8963 + PSM712 C32677） |
| 调试 | **1×6 2.54mm 焊盘 J8（C492405，DNP）**：3V3/SWDIO/SWCLK/GND/TX/RX，接 WCH-LinkE（用户 2026-09-27） |
| 去耦 | 每个 VDD 脚 100nF 0402（N = 5，含 VDDA、VBAT；见 design/05_mcu_comm-spec.md §2.1）+ 整体 4.7µF 0603 |

---

## 7. 电容完备性表（规则 00 ①，引脚号待手册补齐）

| IC | 电源脚（按功能） | 去耦 | 状态 |
|---|---|---|---|
| MP2797 | 45 VTOP：C212 470nF（+R212 20Ω）；25 REGIN：C214 10µF；Q201 集电极：C213 1µF（+R213）；26 3V3：C215 1µF；27 VDD：C216 1µF；22 VREF：C217 1µF；21 NTCB：C218 10nF；42 VCP↔43 VMID：C219 100nF；43 VMID：C220 100nF（+R214）；38 PACKP：C221 10nF（+R215） | 全部按手册 Table 18 定值，不另加 100nF（C3V3 ≤10µF、CNTCB ≤10nF、CPACK 不得增减） | ✅ 已点名（用户 2026-09-27，见 design/02_afe-spec.md §11.2） |
| 74LVC1G17 ×8 | VCC（本节电芯） | 各 100nF | ✅ 已点名 |
| CH32V203C8T6 | 每个 VDD（含 VDDA、VBAT） | 100nF ×N + 4.7µF | 待核 N（按 C3001172 手册） |
| SN65HVD230 | VCC | 100nF | ✅ 已点名 |
| LMR16006X | VIN、CB | 4.7µF/100V + 47µF 电解；CBOOT 100nF | ✅ 已点名 |

---

## 8. 封装下探（规则 00 ②）

| 类别 | 封装 | 理由 |
|---|---|---|
| 信号/分压/上拉/栅极电阻 | **0402** | 功耗 ≪ 62.5mW |
| 电芯采样串阻（情况 B） | **0805 33Ω**（C17634 基础库） | 0.10W，0603 余量为 0 |
| CAN 终端 | **0603** | 33mW，0402 余量偏紧 |
| 100nF 去耦 | **0402** | 接电芯/BAT+/PACK+ 的用 50V **C307331**；嘉立创常用的 C1525 只有 16V，只能用在 ≤5V 轨 |
| 开关电容飞电容 100µF/6.3V | 1206（C15008 基础库） | 只承受单节电压；0805 的 100µF 多为扩展料 |
| 100V MLCC | 1206/1210 | 耐压 |
| 预充电阻 | 5W 绕线 | 4.26J 脉冲能量 |

---

## 9. PCB 规划（KiCad）

- **叠层（规则 0a，已写入骨架）**：F.Cu 信号 / In1.Cu **GND 平面** / In2.Cu **电源平面** / B.Cu 信号。
- **分区（规则 0 ④）**：左侧功率区（铜排、MOSFET、分流器、TVS，背面贴散热器）；
  中部 AFE 与均衡区（远离功率开关节点）；右侧 MCU、电源、通讯区，连接器统一放在板边。
- **网络类（已写入 `.kicad_pro`）**：

| 网络类 | 线宽 | 间距 | 过孔 | 匹配 |
|---|---|---|---|---|
| HV_POWER | 3.0 | 0.5 | 1.0/0.5 | BAT± PACK± FET_MID（主体走铜排和铺铜） |
| BAL_3A | 1.2 | 0.3 | 0.8/0.4 | `BAL?`（BAL0–BAL8，不含 BAL_CLK）、`/开关电容主动均衡/X?`、`/开关电容主动均衡/VB?`（本页局部网络的路径用图纸名，用户 2026-09-27；原 `/03_balancer/X*` 匹配不上） |
| CELL_SENSE | 0.25 | 0.3 | 0.6/0.3 | CELL*、02 页 VC0–VC8（*/VC?，用户 2026-09-27） |
| GATE | 0.4 | 0.3 | 0.6/0.3 | CHG_G DSG_G |
| KELVIN | 0.2 | 0.2 | 0.6/0.3 | SRP SRN（成对走线）、02 页 SRP_F SRN_F（用户 2026-09-27） |
| HV_SIG | 0.25 | 0.6 | 0.6/0.3 | 02 页 VTOP PACKP VMID VCP REG_C（高压信号与 3.3V 信号拉开间距，用户 2026-09-27；只写入 `.kicad_pro`，`gen_kicad_skeleton.py` 的 NETCLASSES 未同步） |
| CAN_DIFF | 0.2/0.2 占位 | 0.2 | 0.6/0.3 | CAN_H/L、RS485_A/B |
| LV_POWER / GND | 0.5 | 0.2 | 0.6/0.3 | +3V3 / GND |

  所有过孔都 ≥ 0.3/0.45mm，满足嘉立创四层板下限（规则 2b）；板框铜间距 0.3mm。
- **差分对（规则 0c，布局前定）**：CAN_H/L 120Ω、RS485_A/B 120Ω，按嘉立创实际叠层用阻抗计算器重算线宽线距；
  顺序为连接器 → ESD → 收发器，走顶层直通道。SRP/SRN 不是阻抗线，但要紧耦合成对走，远离 MOSFET。
- **禁铜区（规则 2d）**：LMR16006 电感，所有铜层都禁铜（开关电容均衡没有电感）。
- **均衡区**：8 个半桥各在本节电位上（V0..V7），不接板级 GND（见 4.5）。
- **收尾**：泪滴（规则 2c）→ DRC=0 → Gerber 自检（规则 2b）。

---

## 10. 立创选料结论

完整料表见 `docs/04-立创选料.md`（29 项，全部来自立创/LCSC 的搜索结果，没有打开过商品页）。对设计的主要影响：

- **主动均衡最终改为分立开关电容**（v0.3 方案 B）：MP2645A 买不到，MP2643 需 MPS 客供且约 ¥186/块，开关电容约 ¥35/块、全部嘉立创料。
- 分流器：立创上没有同时满足 0.1mΩ、≥10W、4 端子、锰铜的料，本版选业展 ASR-S-7-0.1F（C6075508，15W、2 端子，降本采用），并用 NTC_SHUNT 做温漂补偿。精度不够的话，就从立创以外的渠道买 4 端子锰铜分流器，这需要你来决定。
- 嘉立创库存、基础库/扩展库、单价：已可用 `python3 tools/jlc_api.py <C编号>` 直接查询（嘉立创 SMT 料号接口），成本见 `docs/05-成本估算.md`。

## 11. 阻塞项与下一步

| # | 事项 | 状态 |
|---|---|---|
| 1 | 数据手册 | ✅ 已下载 30 份到 `datasheets/`；MP2645A 手册因 MPS 官网反爬未取到（已改用 MP2643，不再需要） |
| 2 | 画图模型（规则 00c） | ❓ `models.toml` 的 cloud 配置档 draw 未配置，需用户指定（必须与复核方不同厂商） |
| 3 | 通讯协议、结构尺寸；电芯温度窗口 | ❓ 用户确认（电芯 120Ah、充电 1C、放电 10C 已定：BMS 的 200A 放电与 800A 短路阈值都在电芯能力内；CAN；160×110mm） |
| 4 | JST XH 13P 封装间距错误（嘉立创封装 2.54mm，实物 2.50mm） | ❓ 用户裁定 |
| 5 | 降本（Tokmas ×12、CH32V203、基础库阻值）已采用；Tokmas 库存 746（够 62 块） | ✅ 2026-09-26 用户同意 |

下一步：按手册逐 IC 点名外围件 → 画原理图 → 规则 00 检查 → 闸口 A 五维审查 → 布局 → 布线 → 闸口 B → 下单。
