colemandlut/MP2645A-BMS/obsidian-vault/首页.md

# 知识库首页

- [[偏好/用户偏好]]
- [[BMS/8S-LFP-200A-BMS 方案]]
- [[BMS/MPS 芯片笔记]]
- [[BMS/LFP 均衡要点]]
- [[BMS/KiCad 原理图自检要点]]
