colemandlut/MP2645A-BMS/docs/00-会话交接.md

# 会话交接（2026-09-26，第 1 个会话 → 新会话）

> 新会话开工第一件事：**完整读完本文件**，再读 `CLAUDE.md` 和 `obsidian-vault/`（用户的永久记忆知识库）。

## 0. 紧急补充（2026-09-26 11:59，降本排查代理的发现，画图前必须处理）

1. **MP2797 外围与手册 Table 18 不一致**（画 02_afe 前逐项对照 `datasheets/C18198873_*.pdf` Table 18 重新点名）：
   - BOM 缺 **REGIN 外置 NPN 管**，以及 **3.3µF、VREF、CREG** 等电容；
   - **VCP 电容应为 47nF**；**VMID 电容需 100V 耐压**；
   - 手册建议分流电阻 **0.2–5mΩ**，当前 0.1mΩ 低于下限。可选 0.2mΩ（如 C469442），但 200A 时分流器发热 8W。**这属于方案取舍，报告用户定**。
2. **开关电容均衡电流被高估**：每相回路要经过 2 只 BAL 节点保险丝（冷阻），100mV 压差下约 **0.157A**（文档写 0.207A）。
   保险丝冷阻要作为选型约束，`tools/bms_calc.py` 的 `sc_equalizer` 需把 `r_extra` 加上 2×保险丝冷阻并更新文档。
3. 降本提案见 `docs/06-降本排查.md`（推荐项全采纳 10 块档约省 ¥15/块），**均须用户同意**；其中 J5 可换 C22366169（封装实测 2.50mm，顺带修掉 C158025 的 2.54mm 问题），J6 候选针号为之字形需重新对针。

## 0b. 降本推荐项已采用（用户 2026-09-26 12:00）

`docs/02-BOM.csv` 已更新：RS1 → C6075508（5930 封装）、QP1–8 → AO3415A C5350990、Q17/18 → SS8550 C8542、
Y1 → 12MHz C9002（固件 HSE 12MHz、PLL×12）、D4/D5 → 1N5819WS C191023、J5 → C22366169（封装 2.50mm ✅）、
**J6 → C18202166（针号之字形，原理图按物理位置对针）**、J7 → C7429634、C_LDO1/2 → C52923（0402）。
开关电容均衡估算更新为 100mV ≈ 0.18A（含保险丝冷阻）。**画图以最新 BOM 为准，开工前 `git pull`。**

## 0c. 第 2 轮决定已落 BOM（用户 2026-09-26 12:18）

分流器保持 **0.1mΩ**；**MP2797 外围按 Figure 27 / Table 18 补全**（见 `docs/03-详细设计.md` 3.1，CVCP 按 Table 22 取 100nF）；
**栅极网络改为手册拓扑**：RG1–12 100Ω、RGS1–12 删除 → R_PUP1/2 10MΩ、新增 R_DRV1/2 100Ω，PNP 快关保留（闸口 A 专门复核）；
功率区 RB1/RB2 **改名 RQB1/RQB2**（与均衡 RB1–15 重号）；**D6 删除**；C_IN_E → C48971005 63V；R_RS → 0Ω（高速模式）。
**画 01_power_path、02_afe、04_power_supply、05_mcu_comm 前必须 `git pull` 取最新 BOM。**

## 0d. 第 2 轮推荐 + 可选全采用（用户 2026-09-26 13:57）

C_IN1 → C_IN1/C_IN2 2×C13832；C_OUT1 → C59461；U8 → C2687131；U4 → **Tokmas C54823941（符号/封装沿用嘉立创 C87080，已核对一致）**；
U7 → C55259679；F11 → C136343。成本 10 块 ≈ ¥166.0/块、100 块 ≈ ¥130.2/块。

## 0e. 第 1 轮可选项采用（用户 2026-09-26 14:46）

D1–D3 → C2976503；C1–C14 → **C1–C6**（6 颗）；1µF/100V 1206 全部 → C282823；QN1–8 → AO3416 C479060；
**CF 每级 2 颗（CF1–CF14），BAL_CLK 75kHz**；F2–F10 → C163126；RT1–4 → C52155402；J5 → C40669。
成本 10 块 ≈ ¥166.0/块、100 块 ≈ ¥130.2/块。**画 01/02/03 子图前 `git pull`。**
（04 子图 C42/C44 已改 C282823，见 1d10c91。）

## 0f. 布局与成本约束（用户 2026-09-27 00:30 同意交接）

1. **外层铜厚暂定 2oz**（内层 0.5oz）。200A 纯靠 PCB 铜不现实（IPC-2221 温升 30℃：2oz 单层需约 115mm 宽），
   主电流走 **20×2mm 紫铜排 + M8 螺柱**（BOM 机械件 BUS，贴片后手工装，板厂/SMT 都不做）；
   MOS 管之间与到铜排的一段在 PCB 上走：厚铜 + **开窗堆锡**（阻焊开窗）。布局时评估主电流能否全压在铜排上，能则再议外层 1oz（10 块档约 −¥32/块，但要扣铜条与手工成本）。
2. **目标板面 130×90mm**（占位 160×110）：裸板 100 块档约 −28%。
3. 待查：嘉立创有无可 SMT 的大电流贴片端子（贴片螺母/铜柱），有则端子也交贴片厂。
4. 成本全貌见 `docs/05-成本估算.md`（元器件）、`docs/08-PCB与贴片费估算.md`（裸板实时报价 `tools/pcb_quote.py` + PCBA 估算）、`docs/07-扩展库合并.md`（基础库无可替代；优选扩展库 3 项待确认是否免上料费）。
5. **库存风险**：Tokmas MOS C19626224 仅够 62 块、D1–D3 C2976503 约 241 块、J5 C40669 约 244 块、MP2797 269 片。
6. 04 子图 C42/C44 已由画图会话改为 C282823（1d10c91），04 页复核 P0=P1=0 已完成。

## 0g. 模型分工（用户 2026-09-27 规定：**有新版本就用新版本**；11:39 JST 按最新版重排）

| 角色 | 主力 | 回退 |
|---|---|---|
| 画图 draw | **deepseek-flash**（`tools/llm_agent.sh deepseek` 或 `tools/deepseek_claude.sh`；用户 13:07 JST 规定不再用 deepseek-v4-pro） | qwen3.8-27b → qwen3-coder-next |
| 复核 review | Opus 5.5（Agent 别名 opus） | Sonnet 5 |
| 第二复核 review2（规则 00c 第 6 泳道） | **qwen3.8-27b**（`tools/llm_agent.sh aliyun`；用户 13:10 JST 规定替换 qwen3.8-max） | qwen3.8-flash |
| 五维泳道 | A3/A4/B2：Opus 5.5；其余：qwen3.8-27b | Sonnet 5 |
| 取库 parts | Opus 5.5 | — |
| 跑工具 tool | Haiku 4.5 | deepseek-flash |

开工前查最新版：`python3 tools/llm.py models deepseek`；百炼 `…/compatible-mode/v1/models`（Anthropic 兼容端点不支持列表）；新模型先跑 `tools/llm_agent_selftest.sh` 再上岗。
合格测试 2026-09-27：deepseek-v4-pro 3/3（33s）、deepseek-flash 3/3（17s）、qwen3.8-max 3/3（170s，已停用）、qwen3.8-27b 3/3（52s）、qwen3.8-flash 3/3（55s）、qwen3-coder-next 3/3（32s）。旧版 qwen3-max / qwen-plus 停用。
技能压缩包 `transfer/pcb-workflow-skill.tar.gz` 已同步，新容器解压后 `python3 <skill>/scripts/models.py use cloud`。

## 1. 用户偏好（必须遵守）

- 全程中文回复；**每条回复前加时间戳，用 JST**（`TZ=Asia/Tokyo date` 实查，用户 2026-09-27 规定，不要估算——上个会话估错过多次，被迫更正）。
- **测试跑完要通知用户**（给出通过数）。
- Obsidian 知识库 = 仓库 `obsidian-vault/`：每次回复前先检索，新结论写回。
- 任何原理图/PCB/制造文件任务前加载 `pcb-workflow` 技能并严格遵守（见第 3 节恢复方法）。
- **EDA 只用 KiCad 10**；嘉立创只作板厂/贴片厂。
- **器件都用嘉立创的**（带立创 C 编号），**封装形状从嘉立创取得**（easyeda2kicad），不许用 KiCad 官方库顶替；非嘉立创件（MPS 客供等）用原厂库并核对手册。
- 选料去立创/嘉立创查；取库/选料用 Opus（parts 角色）。
- 模型分工单独放在技能的 `models.toml`，按环境分配置档，**随时可改**；画图方与复核方必须不同厂商。
- 用户在对话里发过一次 MPS 账号密码——**不要记录、不要复用**；MPS 官网有 Fastly 反爬，不要尝试绕过。

## 2. 项目现状（v0.3）

8S LiFePO4、200A 持续放电、主动均衡 BMS。分支 `claude/sleepy-sagan-yybd0a`。

| 模块 | 方案 |
|---|---|
| AFE | MPS **MP2797**（C18198873），7–16S，高边 NMOS 驱动 |
| 功率 | **Tokmas IPT012N08N5 ×12**（C19626224，每方向 6，共源背靠背，DSG 在电池侧），PNP 快关，分流器 WSLP5931 0.1mΩ（C2091034，2 端子，固件温补） |
| 主动均衡 | **分立开关电容（方案 B，用户选定）**：8 个互补半桥 AO3400A/AO3415A + 74LVC1G17（本节电芯供电），7 级飞电容 3×100µF，MCU 输出 BAL_CLK 50kHz；100mV 压差约 0.18A（含保险丝冷阻）。MP2643 方案（`hardware/lib/mps/` 原厂库）保留作备选 |
| 电源 | **Tokmas LMR16006XDDCR**（C54823941，TI C87080 兼容）直降 3.3V + 续流 SS210（C14996）；取消 5V 轨与 LDO |
| MCU/通讯 | **WCH CH32V203C8T6**（C3001172，CAN 2.0B）；CAN 收发器 **HGSEMI SN65HVD230M**（C55259679，3.3V） |
| 固件 | `firmware/`：保护状态机 + 开关电容均衡使能策略（顶部/静置、压差>300mV 或 <3.0V 禁止），主机测试 38/38 |
| 成本 | `python3 tools/cost.py`：10 块 ≈ ¥166.0/块、100 块 ≈ ¥130.2/块（元器件，不含 PCB/SMT 费） |

主要文档：`docs/03-详细设计.md`（v0.3，最权威）、`docs/02-BOM.csv`、`docs/05-成本估算.md`、
`docs/06-降本排查.md`（全器件降本提案：第 1 轮推荐项**已全部采用**，见 0b；第 2 轮进行中）、`docs/04-立创选料.md`（v0.2 旧表，部分过时）。

## 3. 环境恢复（新容器必做）

```bash
cd /home/user/MP2645A-BMS
sudo bash tools/setup_kicad.sh            # KiCad 10.0.6（Docker Hub 镜像解包 + chroot）+ Freerouting 2.4.1 + OpenJDK 25
pip install easyeda2kicad pymupdf         # 取嘉立创库 / 读 PDF
python3 tools/fetch_datasheets.py         # 手册下载到 datasheets/（PDF 不进 git）
python3 tools/fetch_jlc_parts.py          # 3D 模型（jlc.3dshapes 不进 git）
```

- chroot 挂载会随容器重启丢失：用 KiCad 前 `mountpoint -q /opt/kicad-root/home/user || sudo bash tools/setup_kicad.sh`。
- Playwright/Chromium 访问 https 需信任代理 CA：`apt-get install -y libnss3-tools && certutil -d sql:$HOME/.pki/nssdb -A -t "C,," -n ccr-agent-proxy -i /root/.ccr/agent-proxy-ca.crt`，并在 launch 时传 `proxy: {server: process.env.HTTPS_PROXY}`。
- 嘉立创料号查询：`python3 tools/jlc_api.py <C编号>` / `-k 关键词`（jlcpcb.com SMT 接口，库存/基础库/扩展库/阶梯价）。

### 恢复 pcb-workflow 技能（KiCad 版 + 模型配置）

上个会话按用户要求**只在云主机上**改写了技能（删掉嘉立创EDA、改为全 KiCad、新增规则 0e、`models.toml` + `scripts/models.py`）。
这些改动不在用户的 claude.ai 账号里，新容器会同步回旧版。压缩包随仓库带来，**解压回云主机的技能目录**（不要当作仓库技能使用）：

```bash
D=$(ls -d /root/.claude/skills/synced/*/pcb-workflow)
cp -a "$D" /tmp/pcb-workflow.orig-backup
tar -xzf transfer/pcb-workflow-skill.tar.gz -C "$D" --strip-components=1
python3 "$D/scripts/models.py" show
```

## 4. DeepSeek 画图方（用户刚在环境变量里加了 `DEEPSEEK_API_KEY`）

`models.toml` 的 `cloud` 配置档：draw = DeepSeek（vendor deepseek，launcher codex，模型名待定），review/lanes/parts = Opus，tool = Haiku。
待办：
1. `echo ${DEEPSEEK_API_KEY:+已设置}` 确认变量存在（**不要打印密钥**）。
2. `curl -s https://api.deepseek.com/models -H "Authorization: Bearer $DEEPSEEK_API_KEY"` 取实际模型名。
3. `npm i -g @openai/codex`，在 `~/.codex/config.toml` 配 DeepSeek 为 OpenAI 兼容提供方（`base_url = "https://api.deepseek.com"`、`env_key = "DEEPSEEK_API_KEY"`）和配置档 `[profiles.deepseek]`；用一个小任务实测能写文件、能跑 `kicad-cli`。
4. `python3 <skill>/scripts/models.py set cloud draw <实际模型名> --vendor deepseek --launcher codex --cmd "codex exec -p deepseek -s workspace-write --skip-git-repo-check - < {task} > {out}"`，再 `models.py show` 校验通过（画图 deepseek ≠ 复核 anthropic）。
5. 建议先拿最小的子图（`04_power_supply`）试画一轮，按规则 00c/00d 复核。

## 5. 待用户决定

1. `docs/06-降本排查.md` 第 1 轮推荐项已采用；可选项与第 2 轮提案待确认；分流器 0.1 vs 0.2mΩ、MP2797 外围补齐（见 0）。
2. 开关电容均衡是否采用增强版（N/P 各 2 并 + 100kHz，约 0.37A@100mV，+¥9/块）；样板实测直通损耗与静态漏电。
3. ~~J5 封装间距问题~~ 已换 C22366169 解决。
4. 电芯 **120Ah、充电 1C（120A，OCC 132A）、放电 10C** 已定；待定：电芯温度窗口、通讯协议、外壳尺寸（占位 160×110mm）。
5. 运输模式是否需要硬件断电（LMR16006 SHDN 预留 NMOS）。

## 6. 下一步

DeepSeek 画图链路打通 → 逐 IC 按手册点名外围件 → 画原理图（`hardware/`，层次图骨架已在）→ 规则 00 检查 → 闸口 A 五维审查 → 布局 → 布线 → 闸口 B → 下单。
