colemandlut/MP2645A-BMS/docs/07-扩展库合并.md

# 07 扩展库合并排查（parts 角色，2026-09-26 15:18）

> 只给提案和数据，**没有改** `docs/02-BOM.csv`、设计文档和库文件。
> 口径与 `06-降本排查.md` 相同：嘉立创 SMT 接口实时美元阶梯价 × 7.1，按「单板用量 × 板数」取价格档；
> 扩展库上料费按每种每单 ¥8 计（10 块档折合 ¥0.80/块，100 块档折合 ¥0.08/块）；库存指**嘉立创 SMT 库存**。

## 0. 先说结论

1. **嘉立创基础库现在只剩 351 种料。** 我用 `componentLibraryType:"base"` 把整个基础库翻完了，全表存在 scratchpad 的 `base.json`。
   里面**没有**稳压管、100V 的 10nF/470nF/1µF 电容、保险丝、NTC、功率电感、铝电解、单门施密特、CAN ESD，也没有 3kW 的 33V TVS。
   基础库里 ≥100V 的 MLCC 只有 C28233（100nF/100V 0805，BOM 已在用）和 C9196（1nF/2kV）两种。
2. **能换成基础库的只有 QN 和 QP，但换了都不划算。** QN 可换 AO3400A C20917，QP 可换 AO3401A C15127。
   可是这两颗基础库料的单价比现在的扩展库料还贵，差价超过省下的上料费；QP 换 AO3401A 还会让均衡电流少 17%。结论是**不推荐**。
   **在「只算基础库」这个口径下，没有一项能在不降裕量、不涨成本的前提下减少扩展库种类。**
3. **BOM 内部也没有能合并的料号：**
   - DZ1/DZ2 是 15–16V，D_C0 是 3.3V，电压不同，不能统一。
   - C_VTOP 手册写的是 470nF「Required」，C_PACK 手册写的是 10nF「Do not use a capacitor larger or smaller」（MP2797 Table 18，第 123 页），
     所以都不能并到 BOM 里已有的 1µF/100V（C282823）或 100nF/100V（C28233）上。
   - F11 不能并入 F2–F10，原因见表 1。
4. **另一条路是「优选扩展库」（Preferred Extended，1235 种）。** JLCPCB 官方 FAQ 的原话：*"exempt from the Feeders Loading fee for **Economic** PCB assembly"*。
   也就是说，只有经济型贴片才免上料费；标准型贴片免不免，页面没说。
   **如果这块板实际走的订单类型确实能免**，下面 3 种可以推荐：DZ1/DZ2 → BZT52C16S，D_C0 → BZT52C3V3（优选），U8 → H24VNT2B。
   三种都是同封装、同脚位、规格不降，扩展库减 3 种，10 块档每块省约 ¥2.20，100 块档每块省约 ¥0.13。
   **这一条要由用户在下单页核实（见 §3 存疑 1），核实之前不要改。**

## 1. 逐项表

「单价」是**每块板**该位号的元器件费用，单位元，格式为「10 块档 / 100 块档」。
「净变化」= 单价差 + 上料费变化，负数表示省钱。

### 表 1：候选（按位号）

| 位号 | 原料 | 候选 | 规格对比 | 封装 | 每块单价 原→新（10 / 100 块档） | 库别 | 库存（100 块需求） | 净变化/块（10 / 100） | 结论 |
|---|---|---|---|---|---|---|---|---|---|
| DZ1 DZ2 | MM3Z15 C65676（15V，13.8–15.6V，300mW） | **BZT52C16S C19077449**（宏嘉诚） | 16V，Vz 15.3–17.1V，200mW，IR 100nA。手册 DCHG/DDSG_VGS 推荐值就是 **16V**（Table 18，第 123 页，适用于 ±20V 栅压的 MOSFET）。Vz 最大 17.1V < IPT012N08N5 的 Vgs 最大 20V；驱动电压 VCHG/VDSG 最大 10.7V（第 14–15 页），离 Vz 最小值 15.3V 还有 4.6V，正常工作时不导通。功耗只在瞬态出现，200mW 够用 | SOD-323 → SOD-323 | 0.254 → 0.253 / 0.254 → 0.253 | **优选扩展** | 70 094（200）✅ | −0.80 / −0.08（**前提是免上料费**） | **推荐（有条件）** |
| DZ1 DZ2 | 同上 | BZT52C15S C19077448（宏嘉诚） | 与原件同为 15V，Vz 13.8–15.6V，200mW | SOD-323 → SOD-323 | 0.254 → 0.275 / 同左 | 优选扩展 | 408 763 ✅ | −0.78 / −0.06（有条件） | 可选（想保持 15V 时用） |
| DZ1 DZ2 | 同上 | 并入 D_C0（3.3V） | 电压不同 | — | — | — | — | — | 不可行 |
| D_C0 | 晶导微 BZT52C3V3 C353528（3.1–3.5V，500mW） | **BZT52C3V3 C19077396**（宏嘉诚） | 3.3V，Vz 3.14–3.47V，350mW，IR 5µA@1V。手册 DAGND-C0 只要求 3.3V。500mW 降到 350mW：这颗管子只在 AGND 和 C0 之间出现瞬态时导通，不影响使用 | SOD-123 → SOD-123 | 0.099 → 0.136 / 同左 | **优选扩展** | 796 207 ✅ | −0.76 / −0.04（有条件） | **推荐（有条件）** |
| U8 | UMW PESD2CAN C2687131（VRWM 24V，5A，250W，25pF） | **H24VNT2B C20615827**（宏嘉诚） | VRWM 24V，VBR 26.7–30V，**7A / 385W**（8/20µs），VC ≤55V@7A，Cj **≤36pF**（原件 25pF）。抗浪涌更强；电容多 11pF，对 CAN 1Mbps 可以接受。数据手册写明用于 CAN Bus | SOT-23 → SOT-23，**脚位相同**：1、2 脚接线，3 脚公共端（数据手册第 1 页功能图） | 0.256 → 0.417 / 0.256 → 0.334 | **优选扩展** | 196 212 ✅ | −0.64 / 0.00（有条件） | **推荐（有条件）** |
| QN1–8 | PUOLOP AO3416 C479060（20V，21/26mΩ@2.5V，Vth 0.45–1.0V） | AO3400A C20917 | 30V，24/48mΩ@2.5V，Vth 0.65–1.45V。`sc_equalizer` 算出 100mV 压差时 193 → 189mA（**−2.3%**）。Vth 更高，N/P 共栅时两管同时导通的电压窗口反而更窄。电芯 3.0V（固件允许均衡的下限）时栅压仍高于 2.5V 测试点 | SOT-23，G1 S2 D3 相同 | 2.522 → 3.851 / 1.795 → 2.954 | **基础库** | 1 069 835 ✅ | **+0.53 / +1.08** | 不推荐（基础库单价比扩展库还高） |
| QN1–8 | 同上 | HL3416 C28646273（宏嘉诚） | 20V，18/26mΩ@2.5V，Vth 0.45–1.0V，Vgs ±10V（单节电芯栅压 ≤3.65V，够用）。规格与 AO3416 基本相同，电流 +2% | SOT-23，G1 S2 D3 相同（数据手册第 1 页） | 2.522 → 3.340 / 1.795 → 2.329 | 优选扩展 | 119 062 ✅ | +0.02 / +0.45（有条件） | 不推荐（只作为 AO3416 断货时的备选，AO3416 库存 9188） |
| QP1–8 | ElecSuper AO3415A C5350990（−20V，36/47mΩ@−2.5V） | AO3401A C15127 | −30V，60/85mΩ@−2.5V。和 AO3400A 一起用时电流降到 157mA（**−19%**）；只换 QP 时降到 160mA（−17%） | SOT-23 相同 | 1.766 → 4.294 / 1.352 → 3.306 | **基础库** | 858 198 ✅ | **+1.73 / +1.87** | 不推荐（电流少 17%，而且更贵） |
| QP1–8 | 同上 | HL3415A C28646270（宏嘉诚） | −20V，41/55mΩ@−2.5V，Vgs ±12V。与 HL3416 配对时电流 −2%；与 AO3416 配对时 −4% | SOT-23 相同 | 1.766 → 2.971 / 1.352 → 2.050 | 优选扩展 | 118 382 ✅ | +0.41 / +0.62（有条件） | 不推荐 |
| D1–D3 | DOWO SMDJ33A C2976503（单向，3kW，VC 53.3V） | SMDJ33CA C42371555 | **双向**，3kW，VC 53.3V。单向管在 PACK+ 相对 PACK− 变负时（感性负载关断）会正向导通到约 1V，起续流钳位作用；换成双向后要到 −36.7V 才导通，保护行为变了。优选库里的单向 33V 只有 SMCJ33A（1.5kW），功率减半，不能用 | SMC 相同 | 3.902 → 4.795 / 2.705 → 3.376 | 优选扩展 | 32 256 | +0.09 / +0.59 | 不推荐（行为改变，而且更贵） |
| F11 | JDT JFC1206-1100FS C136343（1A 63V） | 并入 F2–F10（C163126，3A 32V） | 额定 32V < BAT+ 浪涌 53V | 1206 | — | — | — | — | 不可行 |
| F11 / F2–F10 | 两种 | 统一成一颗「3A ≥63V 低冷阻」的保险丝 | F11 如果升到 3A：下游短路电流被 R42 10Ω 限在 ≤5.3A，只有 1.8 倍额定，熔断变慢，R42 会先烧（53V²/10Ω ≈ 280W）。这降低了安全裕量 | 1206 | — | — | — | — | 不可行 |
| C_VTOP | CCTC 470nF 100V 0805 C5375914 | 并入 C1–C6 的 1µF 100V（C282823） | 手册 CVTOP_FLT「**Required capacitance** 470nF」（Table 18，第 123 页） | 0805 → 1206 | — | — | — | — | 不可行 |
| C_VTOP | 同上 | 基础库 470nF：CL21B474KBFNNNE C13967 | 只有 **50V**，低于 VTOP 浪涌 53V | 0805 相同 | — | 基础库 | — | — | 不可行（耐压不够） |
| C_PACK | CCTC 10nF 100V 0603 C282516 | 基础库 10nF：0603B103K500NT C57112 | 只有 **50V**，低于 PACK+ 53V；手册要求 10nF 不得增减，1nF/2kV（C9196）容值不符 | — | — | 基础库 | — | — | 不可行 |
| C1–C6、C42 C44、C_REG | CCTC 1µF 100V 1206 C282823 | 基础库 1µF：CL31B105KBHNNNE C1848 / CL21B105KBFNNNE C28323 | 只有 **50V**，低于 53V | — | — | 基础库 | — | — | 不可行（这一种已经被 9 个位号共用，本身就是合并后的结果） |

### 表 2：没有基础库或优选库替代的扩展库料（已查过，保留原料）

| 位号 | 原料 | 查过的方向 | 结论 |
|---|---|---|---|
| L1 | SWPA5040S220MT C68434 | 基础库只有 2 颗多层电感（10µH，mA 级）；优选库 11 颗也都是多层或信号电感，没有 22µH、Isat ≥1.5A 的功率电感 | 保留 |
| F2–F10 | CFS12V3T3R00 C163126 | 基础库和优选库都没有保险丝 | 保留 |
| F11 | JFC1206-1100FS C136343 | 同上；不能并入 F2–F10（见表 1） | 保留 |
| RT1–4 | ANTC1608-103F3380FB C52155402 | 基础库和优选库都没有 NTC（改成 B3950 也找不到基础库的料） | 保留 |
| UD1–8 | 74LVC1G17 C7394021 | 基础库只有 74HC14（六反相器，SOIC-14，2–6V）。它是**反相**的；8 个 UD 分别以 V0..V7 为参考、跨 8 个电位，一颗六反相器装不下；单节 2.5V 电源时驱动能力弱。优选库也没有单门施密特 | 保留 |
| C40 | RV63V47M6X8 C48971005 | 基础库只有钽电容（16V / 6.3V），没有铝电解；规则 00 ① 要求输入端用电解 | 保留 |
| C1–C6 等 | C282823 | 见表 1 | 保留 |
| D1–D3 | SMDJ33A C2976503 | 基础库 TVS 只有 SMBJ6.5CA 和 P6SMB6.8CA；优选库见表 1 | 保留；**库存只有 725，只够 241 块** |
| J5 / J6 / J7 | XH-13A C40669 / XDWF-C3030WV-2*5P C18202166 / ZX-XH2.54-4PZZ C7429634 | 基础库和优选库都没有连接器；三颗针数和间距各不相同，不能合并 | 保留；**J5 嘉立创库存只有 244** |
| U8 | PESD2CAN | 基础库里的 PSM712 C32677 是给 RS-485 用的（−7/+12V 不对称），单价 ¥2.3，贵约 ¥2.0/块，不划算 | 基础库方向不行；优选库方向见表 1 |

## 2. 汇总

| 方案 | 扩展库种类 | 10 块档 每块 | 100 块档 每块 |
|---|---|---|---|
| A：只换基础库（QN→AO3400A，QP→AO3401A） | −2 | **+¥2.26**（元件 +3.86，上料 −1.60） | **+¥2.95** | 
| A′：只换 QN→AO3400A | −1 | +¥0.53 | +¥1.08 |
| **B：优选扩展库，3 项推荐**（DZ→C19077449，D_C0→C19077396，U8→C20615827）<br>前提：该订单类型免上料费 | **−3** | **−¥2.20**（元件 +0.20，上料 −2.40） | **−¥0.13**（元件 +0.11，上料 −0.24） |
| B 再加 QN→HL3416 | −4 | −¥2.18 | +¥0.33 |

- 方案 A 是在花钱减种类，而且 QP 那一步还会让均衡电流少 17%。**不推荐。**
- 方案 B 的收益几乎全来自免上料费。如果订单类型不免费（例如标准型贴片照收），这 3 项的净变化是 10 块档每块 +¥0.20、100 块档每块 +¥0.11，那就**不要换**。
- 单价是 2026-09-26 15:10 左右从接口实时取的，汇率按 7.1。

## 3. 存疑（交用户定夺）

1. **优选扩展库在本项目的订单类型里免不免上料费？** JLCPCB 官方 FAQ 只说经济型贴片免。
   本板有 TOLL MOSFET、3 个直插连接器、SMC TVS，可能只能走标准型贴片。还有一点要注意：国内嘉立创下单页的计费规则可能和海外站不同。
   **建议在下单页把 C19077449 加进 BOM，看它显示的上料费是 0 还是 ¥8，再决定是否采纳方案 B。**
2. 规则 0e 要求封装从嘉立创取。方案 B 的 3 颗料封装名都相同（SOD-323 / SOD-123 / SOT-23），但**采纳前**仍要用新 C 编号跑一遍 `easyeda2kicad` 取库，
   再用 `fp_compare.py` 和原封装逐个焊盘比对；U8 还要核对符号的引脚号对应关系（1、2 脚接线，3 脚公共端）。
   本次没有取库：取库要求放行 easyeda.com，而且另一个会话正在同一分支上改图，不能动库文件。
3. DZ1/DZ2 从 15V 改成 16V 是向手册推荐值靠拢（Table 18 写的是 16V）。如果设计方有意选 15V 留裕量，就用 C19077448（15V 优选）。
4. **库存风险**：D1–D3 C2976503 的库存 725 只够 241 块，J5 C40669 的库存 244 只够 244 块。量产前要备货或另选料。
   QP 的 AO3415A 库存 5293，100 块的用量够，但库存偏少。
5. 本次按标准型上料费 ¥8/种计算。`tools/cost.py` 注释写的是「经济型 ¥20」，这与 JLCPCB FAQ「经济型免优选扩展库上料费、普通扩展库 $3/种」的说法对不上，两个站点的计费规则需要用户核实。

## 4. 数据来源

- 嘉立创 SMT 接口：`tools/jlc_api.py`。基础库的全表加了请求参数 `componentLibraryType:"base"`（共 351 条），优选扩展库的全表加了 `preferredComponentFlag:true`（共 1235 条）。
- 数据手册：`datasheets/C18198873_MPS_MP2797DFP-0000-T.pdf`（第 14–15 页、第 123 页）；`datasheets/C479060.pdf`、`C5350990.pdf`、`C20917.pdf`、`C15127.pdf`；
  候选料的手册从 `datasheet.lcsc.com/lcsc/<C编号>.pdf` 下载，放在 scratchpad（C19077449、C19077396、C20615827、C28646273、C28646270、C42371555）。
- 均衡电流：`tools/bms_calc.py` 的 `sc_equalizer(0.1)`。各管的导通电阻按「2.5V 典型值之比」缩放文档默认值：N 管 22mΩ、P 管 42mΩ。
- JLCPCB FAQ（优选扩展库）：https://jlcpcb.com/help/article/pcb-assembly-faqs
