colemandlut/MP2645A-BMS/docs/08-PCB与贴片费估算.md

# 08 PCB 与贴片费估算（2026-09-26）

> 元器件成本见 `docs/05-成本估算.md`。本文补上**裸板**与**贴片（PCBA）**两块，按 7.1 汇率折人民币。
> 数据口径：**嘉立创国际站（JLCPCB）**。国内嘉立创（jlc.com）价格体系不同（通常更便宜），下单以实际报价页为准。

## 1. 裸板：实时报价（`python3 tools/pcb_quote.py`）

重放 JLCPCB 报价页的 `calculationGoodsCostsNew` 接口（模板 `tools/jlc_pcb_quote_template.json`：FR4 TG135、1.6mm、绿油白字、HASL 有铅、单板出货、无阻抗控制），2026-09-26 15:14 UTC 实测，美元总价（每块）：

| 层 | 尺寸 mm | 外/内铜 oz | 5 块 | 10 块 | 50 块 | 100 块 |
|---|---|---|---|---|---|---|
| 4 | 160×110 | 1/0.5 | 35.9（7.18） | 46.8（4.68） | 133.6（2.67） | 222.1（2.22） |
| **4** | **160×110** | **2/0.5（当前设想）** | 74.9（14.98） | **91.6（9.16）** | 225.0（4.50） | **371.7（3.72）** |
| 4 | 160×110 | 2/1 | 92.2（18.43） | 109.6（10.96） | 248.8（4.98） | 402.8（4.03） |
| 2 | 160×110 | 2/— | 68.2（13.64） | 82.6（8.26） | 210.2（4.20） | 342.5（3.42） |
| 4 | 130×90 | 2/0.5 | 69.3（13.86） | 80.4（8.04） | 169.0（3.38） | 266.5（2.67） |

## 2. 贴片（PCBA）：按公开费率估算

焊点数由 `docs/02-BOM.csv` 按封装引脚数统计：**贴片 662 个 / 板，插件 27 个 / 板**（J5 13、J6 10、J7 4）。
费率（[JLCPCB 帮助页](https://jlcpcb.com/help/article/pcb-assembly-price)、[PCBA 成本说明](https://jlcpcb.com/blog/pcba-cost-breakdown)）：
经济型开机费 $8.18 + 钢网 $1.53、焊点 $0.0016；标准型开机费约 $25 + 钢网约 $7.9、焊点 $0.0017（标准型数值为经验值，待报价页确认）；
插件手焊 $3.68/单 + $0.02/焊点（报价页接口 `getOrderSmtMaxQty` 实测）。扩展库上料费已计入 05（国内 ¥8/种；**国际站为 $3/种 ≈ ¥21**）。

| 项（USD） | 10 块 经济型 | 10 块 标准型 | 100 块 经济型 | 100 块 标准型 |
|---|---|---|---|---|
| 开机 + 钢网 | 9.7 | 32.9 | 9.7 | 32.9 |
| 贴片焊点 | 10.6 | 11.3 | 105.9 | 112.5 |
| 插件手焊 | 9.1 | 9.1 | 57.7 | 57.7 |
| **PCBA 小计** | **29.4** | **53.2** | **173.3** | **203.1** |

经济型能否接单取决于板厚铜、TOLL 大封装与数量上限（接口 `maxQty` 为 50），布局定型后在报价页确认；保守按标准型计。

## 3. 每块总成本（人民币，4 层 160×110、外层 2oz）

| 批量 | 元器件（05） | 裸板 | PCBA | **电路板合计** | 机械件（熔断器/铜排/散热器） |
|---|---|---|---|---|---|
| 10 块 | 166.0 | 65.0 | 20.9–37.8 | **≈ ¥252–269** | ¥90–200 |
| 100 块 | 130.2 | 26.4 | 12.3–14.4 | **≈ ¥169–171** | ¥90–200 |

## 4. 优化点（按省钱多少）

1. **外层铜厚 2oz → 1oz**：10 块档每块省约 ¥32，100 块档省约 ¥10.6。前提是 200A 主回路完全走铜排（MOSFET 漏/源焊盘直接压在铜排或焊接铜条上），板上铜只走栅极、采样和均衡（≤3A）。**布局前要定主电流路径**。
2. **板面 160×110 → 130×90**：10 块档每块省约 ¥8，100 块档省约 ¥7.5（100 块时裸板 −28%）。
3. **2 层不划算**：比 4 层只省约 ¥6/块（10 块），却失去完整地平面，不建议。
4. **插件改自焊**：10 块档约省 ¥6/块，100 块约 ¥4/块，量小可以考虑，量产不值。
5. 小批量（≤10 块）时开机费、工程费占比高，**一次多做几块**比分批做便宜：4 层 2oz 从 5 块到 10 块只贵 $17。
