colemandlut/MP2645A-BMS/docs/06-降本排查.md

# 06 降本排查（元器件替代提案）

> 2026-09-26 11:55 UTC · parts（取料/选料）角色 · **只出提案，未改任何 BOM / 设计 / 库文件**。
> 依据：`docs/02-BOM.csv` 当前版（v0.3 **方案 B：分立开关电容均衡**）、`docs/05-成本估算.md`（11:40 版）、`docs/03-详细设计.md`，以及手册 `datasheets/`（本次新下载的候选料手册也放在这里，`*.pdf` 已被 .gitignore）。
> 价格：嘉立创 SMT 接口实时美元阶梯价 × 7.1，按「单板用量 × 板数」取档，与 `tools/cost.py` 的口径一致；扩展库上料费按每种每单 ¥8，基础库免（10 块档每种折合 ¥0.80/块，100 块档折合 ¥0.08/块）。
> 封装核对：候选料用 `easyeda2kicad` 取到 scratchpad，再用 pcb-workflow 的 `fp_compare.py` 与工程库现有封装逐焊盘比对；**没有写入 `hardware/lib/jlc/`，也没有覆盖 `fetch_report.md`**。

## 0. 范围

- **不在本次范围**（另有人负责）：电源模块（U4 LMR16006、D7、L1、C_BST、R_FB1/2、F11、D6、C_IN_E、C_IN1、C_OUT1），以及 CAN 收发器 U7 SN65HVD230 和它的 C_CAN、R_RS。Tokmas MOSFET、MP2797、CH32V203 不提换型号。
- **任务单里点名的 MP2643 相关料已随方案 B 作废，本报告不再评估**：C45783×14（CCU/CCL）、J6 Molex 43045-1812、F2–F10 7A 2410、L_BAL、OK1–14、C15849（4V5）、R_FB 392k 等。
- 方案 B 新增的均衡件（QN/QP、UD、CF、CC、CD、RB、F2–F10 3A、J6 2×5）按协调方给出的约束一并评估：N/P 管必须标出 Vgs=2.5V 下的 Rds(on)，越低越好；飞电容只承受 ≤3.65V；保险丝 ≥3A、快熔、≥32V。

---

## 表 1：替代提案

「每块省」= 元器件差价 + 上料费变化，写成「10 块档 / 100 块档」，单位是元/块。库存是**嘉立创 SMT 库存**，括号里是 100 块的需求量。

| # | 位号 | 原料 | 新料（C 编号 / 型号） | 规格对比 | 封装 | 10 块单价 原→新 | 每块省（10 / 100 块） | 库别变化 | 嘉立创库存（需） | 结论 |
|---|---|---|---|---|---|---|---|---|---|---|
| 1 | RS1 | Vishay WSLP5931L1000FEA C2091034 | **C6075508 业展 ASR-S-7-0.1F** | 0.1mΩ ±1%、15W@70℃（相同）；CuMnSn 合金、电子束焊；TCR **±200ppm**（原 ±300ppm，更好）；Rth 2℃/W；AEC-Q200。200A 下 4W / 15W。两端子，和原料一样 | 5931→**5930**：焊盘中心距 12.0→10.8mm，焊盘 6.0×8.5→5.5×8.8mm。需要换封装，PCB 还没画，可以接受 | ¥9.59→¥4.62 | **4.97 / 3.69** | 扩→扩 | 21012（100）✅ | **推荐** |
| 1b | RS1 | 同上 | C55113232 毫欧电子 HoLRS5930-15W-0.1mR-1% | 0.1mΩ ±1%、15W；承认书标 TCR ±100ppm（依据写的是「见实测曲线」）；最大 387A | 5930，但 EasyEDA 取封装失败，只能照承认书自己画 | ¥9.59→¥2.88 | 6.71 / 5.10 | 扩→扩 | 944（100）✅ | 可选（小厂，资料弱） |
| 2 | QP1–QP8 | AO3401A C15127（AOS） | **C5350990 ElecSuper AO3415A** | −20V（每只管只承受一节电压 ≤3.65V，够用）；Rds(on) **36 typ / 47 max mΩ @−2.5V**（原 85mΩ@−2.5V）；Vth −0.5~−0.9V；Qg 9.5nC@4.5V；4.9A。只换 P 管时，100mV 压差下的均衡电流由 0.207A 升到 **0.277A（+34%）**，按 `bms_calc.sc_equalizer` 计算 | SOT-23，焊盘 1.07×0.6@±1.24mm，原为 1.0×0.8@±1.15mm，需要换封装；引脚 1G 2S 3D，与原来相同 | ¥0.537→¥0.221 | **1.73 / 1.87**（已扣 +¥8） | **基础→扩展**（+1 种） | 5302（800）✅ | **推荐**（需实测直通电流，见存疑 6） |
| 3 | QN1–QN8 | AO3400A C20917（AOS） | C479060 PUOLOP AO3416 | 20V；Rds(on) **21 typ / 26 max mΩ @2.5V**（原 48mΩ max）；Vth 0.45–1.0V（原约 0.65–1.45V）。N、P 管都换时 100mV 下电流为 **0.334A（+61%）** | SOT-23，焊盘与工程库现有 SOT-23 逐焊盘一致（0 差异） | ¥0.481→¥0.315 | 0.53 / 1.08 | 基础→扩展（+1 种） | 9188（800）✅ | 可选（Vth 更低，直通窗口更宽，需实测） |
| 4 | CF1–CF21 | C15008 100µF/6.3V 1206 ×21 | **同料，每级 3 颗减为 2 颗（21→14 颗），BAL_CLK 由 50kHz 提到 75kHz** | C_eff 150→100µF，R_SSL = 1/(f·C) 仍为 0.133Ω，R_eq 仍为 0.483Ω（计算结果不变）。代价：开关次数和直通次数各增加 50%，每颗电容的纹波电流是原来的 1.5 倍（均衡电流 <1A，MLCC 发热可以忽略）。固件只改 PWM 频率 | 不变 | 单价 ¥0.644 不变（100 块档 ¥0.417→¥0.524，因为用量降档） | 4.51 / 1.42 | 不变（基础） | — | 可选（改固件后要实测） |
| 5 | F2–F10 | Littelfuse 0466003.NRHF C14165 | C163126 大毅 TA-I CFS12V3T3R00 | 3A、32V DC、分断 **50A@DC32V**（和原料一样）；快熔（250% 额定电流下 ≤5s；原料为 200% ≤5s、300% ≤0.2s）；冷阻 **23mΩ ±25%**（原 20mΩ，见存疑 1）；**工作温度 −20~105℃**（原 −55~90℃） | F1206，逐焊盘一致（0 差异） | ¥0.746→¥0.297 | 4.04 / 3.09 | 扩→扩 | 11220（900）✅ | 可选（需确认 −20℃ 下限能接受） |
| 6 | Q17 Q18 | Nexperia PBSS5140T C89581 | **C8542 长电 SS8550 Y2** | Vceo **−25V**（原 −40V，降级；栅极母线最高 15V，由 DZ 钳位，余量 10V）；Ic −1.5A（原 −1A，升级）；hFE 200–350@100mA、≥40@800mA；Vce(sat) −0.5V@800mA。泄放 1.44µC 的峰值电流由约 1A 降到约 0.5–1A，关断时间约从 1.5µs 变为 3µs，仍远小于 AFE 的短路延时 | SOT-23，逐焊盘一致；引脚 1B 2E 3C，与原料相同 | ¥0.790→¥0.110 | **2.16 / 0.92** | **扩→基础**（−1 种） | 107 万（200）✅ | **推荐** |
| 7 | C1–C14 | C13832 ×14 | **同料，减为 6 颗**（PACK 侧 10→4，BAT 侧 4→2） | 电气理由：浪涌能量由 TVS 吸收（D3 按 0.32J 设计），14×1µF 在 53V 下总储能只有约 20mJ，这些电容只负责高频旁路和减缓 dv/dt。风险：关断沿更陡、振铃更大 | 不变 | 单价 ¥0.351→¥0.454（用量降档） | 2.19 / 2.38 | 不变 | — | 可选（**必须在短路关断实测中确认 PACK+ 峰值 < 64V**） |
| 7b | C1–C14、C_VDD | C13832 Samsung CL31B105KCHNNNE | C282823 CCTC 三环 TCC1206X7R105K101HT | 1µF 100V X7R ±10% 1206，规格完全一致 | C1206，逐焊盘一致 | ¥0.351→¥0.273 | 1.19 / 0.94 | 扩→扩 | 228173（1500）✅ | 可选 |
| 8 | Y1 | YXC X32258MSB4SI C2682774（8MHz） | **C9002 YXC X322512MSB4SI（12MHz）** | 同系列：3225、CL 20pF（C_Y1/C_Y2 仍用 20pF）、±10ppm / ±20ppm、−40~85℃，ESR 80Ω（原 180Ω，更容易起振）。只有频率从 8MHz 改为 12MHz。CH32V203 的 HSE 支持 3–25MHz，12MHz×12 = 144MHz（原来是 8×18），CAN 仍由 APB1 分频 | 逐焊盘一致 | ¥1.370→¥0.672 | **1.50 / 0.60** | **扩→基础**（−1 种） | 66649（100）✅ | **推荐**（固件要改 HSE_VALUE 和 PLL 倍频） |
| 9 | J5 | JST B13B-XH-A C158025 | **C22366169 Megastar ZX-XH2.54-13PZZ** | 与 JST XH 兼容，2.50mm 13P 立式直插板端座（尽管型号里写 2.54，实际是 XH 系列）；额定 2A（原 3A；采样线和 NTC 线只有 µA 级电流）。**嘉立创封装实测间距 2.50mm ✅**，原 C158025 的封装错成 2.54mm，换成这颗料顺带修复 | 13 焊盘，间距 2.50，孔 0.91mm | ¥1.901→¥0.532 | **1.37 / 1.09** | 扩→扩 | 1400（100）✅ | **推荐** |
| 9b | J5 | 同上 | C40669 BOOMELE XH-13A | XH 2.50 13P 立式；封装实测 2.50mm ✅，孔 1.0mm | 同上 | ¥1.901→¥0.297 | 1.60 / 1.30 | 扩→扩 | 244（100）⚠ 余量小 | 可选 |
| 10 | J6 | CJT C3030WV-2x5P C239457 | **C18202166 连欣 XDWF-C3030WV-2\*5P** | 2×5、3.00mm、立式直插板端座，与 Micro-Fit 3.0 兼容；每针 **5A**（原标 12.5A；设计正常电流 ≤0.7A，保险丝 3A，余量够）；−55~105℃ | 焊盘网格相同（间距和排距都是 3.00mm），带 2 个定位柱（±9mm，y=−2.44，与 Molex 标准位一致；原封装 y=−2.5）。孔径 1.5→1.02mm。**针号是之字形（奇数针一排、偶数针一排），原封装是按排编号**，原理图和线束要按物理位置重新对针 | ¥3.159→¥2.110 | **1.05 / 0.73** | 扩→扩 | 2915（100）✅ | **推荐**（先买样品和线束端试插） |
| 10b | J6 | 同上 | C53151698 宏诚 HC-5557-MX3.0-2x5A | 2×5 3.00mm，5A | 嘉立创封装没有定位孔，要自己补 | ¥3.159→¥1.655 | 1.50 / 1.08 | 扩→扩 | 617（100）✅ | 可选 |
| 11 | D1–D3 | 晶导微 SMDJ33A C438163 | C2976503 DOWO SMDJ33A | 3kW@10/1000µs、Vrwm 33V、Vbr 36.7V、Vc 53.3V@56.3A，全部参数相同，满足钳位 < 64V | SMC，逐焊盘一致 | ¥1.648→¥1.301 | 1.04 / 0.94 | 扩→扩 | 725（300）✅ | 可选 |
| 11b | D1–D3 | 同上 | C2994125 MDD SMDJ33A | 参数相同 | EasyEDA 取封装失败，采纳前要重取核对 | ¥1.648→¥1.398 | 0.75 / 0.75 | 扩→扩 | 2725（300）✅ | 可选 |
| 12 | D4 D5 | CJ BAT54WS C22629 | **C191023 1N5819WS** | 40V / 1A（原 30V / 200mA，升级）；小电流下 Vf 与 BAT54 相当；IR 最大 500µA@40V（原 2µA，降级）。这两颗管导通时正偏，只在关断泄放的瞬间承受反压，漏电方向反而帮助泄放，所以不影响功能；结电容几十 pF，和 6×Ciss 相比可以忽略 | SOD-323，逐焊盘一致 | ¥0.169→¥0.097 | **0.94 / 0.15** | **扩→基础**（−1 种；新电源方案取消了唤醒或门，BAT54WS 只剩 D4/D5 在用） | 511 万（200）✅ | **推荐** |
| 13 | C_LDO1 C_LDO2 | C15849 1µF 50V 0603 | **C52923 Samsung CL05A105KA5NQNC** | 1µF 25V X5R。这两颗接 MP2797 的 3V3 / VDD 脚（3.3V / 1.8V），手册要求 C3V3 0.47–10µF、CVDD 1µF；3.3V 偏置下有效容量约 0.7µF，仍在范围内 | 0603→**0402**，封装变小 | ¥0.534→¥0.070 | **0.93 / 0.93** | 基础→基础 | 649 万（200）✅ | **推荐** |
| 14 | RT1–RT4 | Murata NCP18XH103F03RB C13564 | C52155402 APV 爱普微 ANTC1608-103F3380FB | R25 10k ±1%、B25/50 3380K、B25/85 3435K，B 值口径和数值都与 Murata 相同；−40~125℃ | R0603，逐焊盘一致 | ¥0.329→¥0.140 | 0.76 / 0.44 | 扩→扩 | 136302（400）✅ | 可选（65℃、100℃ 阈值要用 APV 的 R-T 表重核，固件现在用的是 Murata 表） |
| 15 | J7 | JST B4B-XH-A C144395 | **C7429634 Megastar ZX-XH2.54-4PZZ** | XH 2.50 4P 立式，3A；封装实测间距 2.50mm ✅ | 4 焊盘，间距 2.50，孔 1.1mm | ¥0.436→¥0.083 | **0.35 / 0.28** | 扩→扩 | 117 万（100）✅ | **推荐**（另外：原 C144395 的封装实测也是 2.50mm，BOM 里「封装间距待核」这一项可以关闭） |
| 16 | U8 | Nexperia PESD2CAN C75176 | C2687131 UMW PESD2CAN | 24V、250W@8/20µs（原 230W）、25pF（相同）、Vc 41V（相同） | SOT-23，逐焊盘一致 | ¥0.554→¥0.256 | 0.30 / 0.18 | 扩→扩 | 675185（100）✅ | 可选 |
| 17 | C_AFE1–3 | YAGEO C113803 100nF 100V 0603 | C28233 Samsung CL21B104KCFNNNE | 100nF **100V** X7R，耐压不变 | 0603→0805 | ¥0.091→¥0.253 | 0.31 / **−0.41** | **扩→基础**（−1 种） | 174 万（300）✅ | 可选（只在小批量时划算；这 3 颗的取值本身需要先按手册改，见存疑 2） |
| — | CF1–CF21 | C15008 | C380356 CCTC TCC1206X5R107M6R3HT | 规格相同 | 1206 | ¥0.644→¥0.535 | 1.48 / **−0.80** | 基础→扩展 | 246908 | 不推荐（100 块档反而更贵） |
| — | F2–F10 | C14165 | C2838898 prosemi 1206FA-3A、C136347 JDT JFC1206-1300FS | 快熔、分断能力更高，但冷阻 **48mΩ**（原 20mΩ）。每一相均衡回路经过 2 只保险丝，R_eq 会增加约 0.22Ω，均衡电流下降约 25–30% | F1206 | ≈¥0.746→¥0.44 | ≈2.8 / 2.2 | 扩→扩 | ✅ | 不推荐（性能损失大）；C182445 12H1300C 属于 High I²t 慢断型，不合规 |
| — | D1–D3 | C438163 | SMCJ33A（1.5kW，如 C438109） | 动态电阻约为原料的 2 倍：钳位到 64V 时能泄放的电流从约 94A 降到约 46A | SMC | 约省 ¥0.3/颗 | — | — | — | 不推荐（违反钳位 < 64V 约束的风险变大） |
| — | C1–C14 | C13832 | 基础库 1µF 50V 1206 C1848 | TVS 钳位 53V 高于 50V 额定电压 | — | — | — | — | — | 不合规 |
| — | DZ1 DZ2 | MM3Z15 C65676 | C5359791 FOSAN MM3Z15 | 同规格 | SOD-323 | ¥0.127→¥0.088 | 0.08 / 0.08 | 扩→扩 | ✅ | 不值得改 |
| — | UD1–UD8 | UMW SN74LVC1G17 C7394021 | — | UMW 已经是嘉立创上最便宜的 74LVC1G17（100 片档 $0.031），其他品牌都 ≥$0.033；基础库没有单路缓冲器；74HC14 这类反相器会破坏「各级同相」的时钟链 | — | — | — | — | — | 不换 |

CC2–CC8（1nF）、CD1–CD8（100nF/16V）、RB1–RB15（1M）、R_CLK 以及其余阻容都已经是基础库、单价 ≤ ¥0.03，没有继续降本的空间。

---

## 表 2：扩展库 → 基础库清单（当前 BOM，范围内的料）

当前扩展库共 25 种（见 `05-成本估算.md`）。

| 位号 | 扩展库料 | 能否换基础库 | 基础库料 / 原因 |
|---|---|---|---|
| Q17 Q18 | PBSS5140T C89581 | ✅ | **C8542 SS8550 Y2**（表 1 第 6 项） |
| D4 D5 | BAT54WS C22629 | ✅ | **C191023 1N5819WS**（表 1 第 12 项） |
| Y1 | X32258MSB4SI C2682774 | ✅（需改固件） | **C9002 12MHz**，同系列（表 1 第 8 项） |
| C_AFE1–3 | CC0603KRX7R0BB104 C113803 | ✅（小批量才划算） | C28233 100nF/100V 0805（表 1 第 17 项；先按存疑 2 定取值） |
| Q1–Q12 | Tokmas C19626224 | ✗ | 用户指定 |
| U1 / U6 | MP2797 / CH32V203 | ✗ | 用户指定 |
| RS1 | C2091034 | ✗ | 基础库没有毫欧级分流器 |
| D1–D3 | SMDJ33A C438163 | ✗ | 基础库 TVS 只有 SMBJ6.5CA / P6SMB6.8CA（600W、低压），不符合要求 |
| C1–C14、C_VDD | C13832 | ✗ | 基础库 100V 电容只有 100nF 0805（C28233）；1µF 最高只有 50V，低于 53V 钳位电压 |
| UD1–UD8 | C7394021 | ✗ | 基础库只有 74HC14（反相、6 路），不适用 |
| F2–F10 | C14165 | ✗ | 基础库没有贴片保险丝 |
| RT1–RT4 | C13564 | ✗ | 基础库没有 NTC |
| DZ1 DZ2 | C65676 | ✗ | 基础库没有 15V 稳压管 |
| J5 / J6 / J7 | 连接器 | ✗ | 基础库没有这类连接器 |
| U8 | PESD2CAN C75176 | ✗ | 基础库只有 PSM712（RS-485 用，−7/+12V 非对称），不适合 CAN，而且更贵 |
| QP1–QP8 / QN1–QN8 | （现为基础库） | 反向：如果采纳表 1 第 2、3 项，会各**增加** 1 种扩展库 | 已在「每块省」中扣除 ¥8 |
| （排除范围） | U4 C87080、L1 C68434、F11 C151135、D6 C78419、C_IN_E C92059、C_IN1 C381466、U7 C12084 | 未评估 | 由电源 / CAN 负责人处理 |

结论：范围内有 3 种可以直接改成基础库（Q17/18、D4/D5、Y1），第 4 种（C_AFE）可选，每单省 ¥24–32。只采纳「推荐」项时，QP 换料会新增 1 种扩展库，**净减少 2 种（25→23 种）**。

---

## 汇总：采纳全部「推荐」项后

> 这是第一轮（均衡 / 功率 / AFE / MCU / 连接器）的汇总。加上第二轮电源、CAN 和 MP2797 补全后的总账，见文末「第二轮汇总」。

「推荐」项：RS1、QP、Q17/18、Y1、J5、J6、D4/D5、C_LDO、J7。

| | 10 块档 | 100 块档 |
|---|---|---|
| 元器件差价 | −¥13.40/块 | −¥10.10/块 |
| 上料费变化（扩展库净减 2 种 × ¥8） | −¥1.60/块 | −¥0.16/块 |
| **合计每块下降** | **−¥15.00** | **−¥10.26** |
| 元器件合计/块（05 表 → 采纳后） | ¥202.26 → **≈¥187.3（−7.4%）** | ¥156.24 → **≈¥146.0（−6.6%）** |

按项目拆分（10 块档 / 100 块档，元/块）：RS1 4.97/3.69，Q17/18 2.16/0.92，QP 1.73/1.87，Y1 1.50/0.60，J5 1.37/1.09，J6 1.05/0.73，D4/D5 0.94/0.15，C_LDO 0.93/0.93，J7 0.35/0.28。

如果再采纳「可选」项（每行取第一方案、互不重复：CF 减量、F2–F10 TA-I、C1–C14 减量、TVS DOWO、QN AO3416、NTC APV、U8 UMW），10 块档每块还能再省约 **¥13.4**，100 块档约 **¥9.5**。推荐加可选合计：10 块档 ≈ ¥173.9/块，100 块档 ≈ ¥136.5/块。

另有一个设计层面的选项（见存疑 2）：RS1 改为 0.2mΩ 的 **C469442 ASR-M-7-0.2F**（锰铜，±100ppm，15W，¥2.63，库存 5729），比推荐的 0.1mΩ 方案每块再省约 ¥2，并且符合 MP2797 手册推荐的 0.2–5mΩ 范围；代价是 200A 下分流器发热 8W。

---

## 存疑 / 需用户确认

1. **均衡回路的串联电阻没有算全（影响保险丝选型）**：方案 B 每一相回路都经过两个 BAL 节点，也就是 2 只 F2–F10 保险丝，外加 J6 接触电阻和线束电阻。`sc_equalizer` 的 r_extra=0.015Ω 没有包括这些。只加上 2×20mΩ 的保险丝，R_eq 就从 0.483Ω 变成 0.638Ω，100mV 时的电流从 0.207A 降到 **0.157A**。所以保险丝冷阻应作为选型约束（≤ 约 25mΩ），表 1 否决 48mΩ 的两颗就是这个原因。采纳 QP（加 QN）换料后，电流能回到约 0.21–0.22A。
2. **MP2797 外围与手册 Table 18 / Figure 27 不一致**，会影响成本估算，需要设计方核对：
   - BOM 缺 **REGIN 外置 NPN**（手册用 FZT853TA，REGCTRL 驱动）、**CREGIN 3.3µF**、**CVREF 1µF**、**CREG 1µF + RREG 500Ω**、**CNTCB 10nF**。
   - **CVCP 应为 47nF**，额定电压按手册「80V × 8/16 = 40V」；**CVMID 100nF**，VMID 可能达到 PACK+ 的钳位电压 53V，需要 100V 耐压。C_AFE1–3 应按这些取值拆开再选料，所以表 1 第 17 项先列为可选。
   - VTOP 滤波手册要求 20Ω + 470nF，BOM 是 100Ω + 1µF。
   - **RSENSE 手册建议 0.2–5mΩ**，本设计 0.1mΩ 低于下限。
3. **Y1 改 12MHz** 需要固件改时钟配置（HSE=12MHz，PLL×12）。firmware 目录里还没有时钟初始化代码，现在改没有返工成本。
4. **J6 XDWF**：针号按之字形排列，与现有封装的按排编号不同；额定 5A/针（原料标 12.5A）。需要买样品，和实际使用的 Micro-Fit 线束端试插确认锁扣和针位。
5. **F2–F10 大毅 CFS12V3T3R00** 的工作温度下限是 −20℃。如果 BMS 要在更冷的环境工作，就不要采纳。
6. **QP/QN 换成低 Vth、低 Rds 的管子后**：N/P 共栅，切换沿上的直通峰值电流会更大，AO3416 的 Vth 最低只有 0.45V，需要实测直通损耗。好处是单节电压低到 3.0V 时栅驱动更充足。
7. **CF 减为 2 颗/级**：必须同时把 BAL_CLK 提到 75kHz（固件改动），然后实测均衡电流。
8. **C1–C14 减量**：必须做短路关断实测，确认 PACK+ 峰值低于 64V。
9. **4 端子分流器**：嘉立创没有合适的现货（HoFL3-9420 0.1mΩ 库存只有 55），本版仍用 2 端子加焊盘切分做开尔文取样。
10. **封装待核**：C55113232、C2994125 在 EasyEDA 取封装失败，采纳前要重取并逐焊盘核对。所有「需要换封装」的项采纳时都按规则 0b 在 PCB 上替换并复核。
11. 表 1 的品牌大多是国产二线厂（业展、ElecSuper、PUOLOP、连欣、Megastar、DOWO、APV）。「推荐」项都已核对手册参数；首批建议小批量验证，量产前再定。

---

# 第二轮（2026-09-26 12:40 UTC）：电源、CAN、MP2797 外围补全

> 仍然只出提案，没有改 BOM、设计和库文件。价格和库存口径同第一轮。候选封装仍取到 scratchpad 里比对，没有写入工程库。
> 本轮依据：`datasheets/C87080.pdf`（TI LMR16006）、`C54823941.pdf`（Tokmas LMR16006 兼容件）、`C55259679.pdf`（HGSEMI SN65HVD230）、`C18198873_MPS_MP2797DFP-0000-T.pdf`（Table 18、电气特性、Table 4–9），以及 `docs/03-详细设计.md` 第 5、6 节。

## 表 3：辅助电源与 CAN（上一轮排除的部分）

约束：VIN 浪涌最高约 53V（TVS 钳位），续流管反压 ≥ 66V，输入必须有电解（规则 00 ①），3.3V 负载 < 50mA。TI 手册要求输入陶瓷电容 1–10µF X5R/X7R；峰值限流 1.2A 典型、1.7A 最大；手册典型曲线的 Cout 为 10µF。

| # | 位号 | 原料 | 新料 | 规格对比 | 封装 | 10 块单价 原→新 | 每块省（10 / 100 块） | 库别变化 | 嘉立创库存（需） | 结论 |
|---|---|---|---|---|---|---|---|---|---|---|
| P1 | D6 | Brightking SMBJ33A C78419（**库存 47，不够 100 块**） | **C353366 晶导微 SMBJ33A**（与 D1–D3 同品牌） | 600W@10/1000µs、Vrwm 33V、Vbr 36.7–40.6V、Vc 53.3V@11.3A，参数相同 | SMB：焊盘 2.05×2.19@±2.36mm → 2.0×2.4@±2.4mm，差异很小，换封装即可 | ¥0.501→¥0.290 | 0.21 / 0.17 | 扩→扩 | 77002（100）✅ | **推荐（因为原料库存不足，必须换）**；备选 C173526 MDD，库存 17060 |
| P1b | D6 | 同上 | **直接删除 D6** | BAT+ 母线上已经有 D3 SMDJ33A（3kW，钳位 53.3V）。buck 经 F11 接在同一条母线上，VIN 绝对最大值 65V，仍高于 D3 的钳位电压 | 少一颗 SMB | — | 在 P1 基础上再省 1.09 / 0.31 | −1 种 | — | 可选（要由设计方确认 F11 之后的走线电感不会让 VIN 过冲到 65V） |
| P2 | C_IN_E | Panasonic EEE-FT1H470AP C92059（47µF **50V**，6.3×5.8） | **C48971005 jieerrui RV63V47M6X8** | 47µF ±20%，**63V**（原 50V 低于 53V 浪涌，属于升级），105℃ 2000h，纹波 63mA@120Hz（负载 <50mA，够用） | 焊盘与现有 CAP-SMD_BD6.3 逐焊盘一致（0 差异）；高度 5.8→7.7mm | ¥2.051→¥0.388 | **1.66 / 1.53** | 扩→扩 | 383429（100）✅ | **推荐**（品牌小，首批要验证；同品牌 C47023121 RVT 系列可作备选） |
| P3 | C_IN1 | 风华 FS32X475K101EGG C381466（4.7µF 100V 1210） | **2 × C13832**（1µF 100V X7R 1206，BOM 里已经在用） | 总标称容量 2µF；29–53V 偏置下有效约 0.8–1.2µF，满足 TI 手册 1–10µF 的要求。如果 C1–C14 改用 CCTC C282823，这里也跟着改 | 1210 → 2×1206，需要改 PCB | ¥1.718→2×¥0.454 | **1.61 / 0.76**（含少 1 种扩展库） | −1 种（C381466 取消） | 1215300（200）✅ | **推荐**；只换单颗料的备选：C153036 FS32X225K101EGG（2.2µF 100V 1210），每块省 1.09 / 0.87 |
| P4 | C_OUT1 | Samsung CL21A226MAQNNNE C45783（22µF 25V 0805） | **C59461 CL10A226MQ8NRNC** | 22µF 6.3V X5R 0603；3.3V 偏置下有效约 9–11µF，与 TI 典型曲线用的 10µF 相当；输出 3.3V，6.3V 耐压够用 | 0805→0603 | ¥1.561→¥0.221 | **1.34 / 1.34** | 基础→基础 | 831 万 ✅ | **推荐** |
| P5 | U4 | TI LMR16006XDDCR C87080 | C54823941 **Tokmas** LMR16006XDDCR | 引脚相同（1 BOOT、2 GND、3 FB、4 EN、5 VIN、6 SW；EN 悬空即使能）；VIN 4–60V，绝对最大 65V（与 TI 相同）；1A（TI 0.6A）；**VFB 0.770V**（TI 0.765V，现有 33k/10k 分压输出 3.31V）；**fsw 600kHz**（TI 700kHz，22µH 下纹波约增加 17%，可以接受）；**Iq 80µA 典型 / 109µA 最大**（TI 28µA，**降级**，待机多耗约 50µA） | TSOT-23-6。EasyEDA 取封装失败，需要重取核对（引脚排列已经按手册确认一致） | ¥3.402→¥1.776 | 1.63 / 1.13 | 扩→扩 | 2670（100）✅ | 可选（要看待机电流 <300µA 的目标能否接受） |
| — | U4 | 同上 | 其他 60V buck | SSP9459 C411010（Iq 860µA）、LMR16006-MS C54539952（Iq 0.7mA）静态电流太大；TPS560430 只到 36V；LM2594HV、TPS54060 等更贵，而且要改外围 | — | — | — | — | — | 不推荐 |
| P6 | F11 | Littelfuse 0466001.NRHF C151135 | C136343 JDT JFC1206-1100FS | 1A、**63V**、50A 分断、快熔（与原料相同）；冷阻约 0.49Ω，在 50mA 下压降 25mV，可以忽略 | F1206，逐焊盘一致 | ¥0.693→¥0.310 | 0.38 / 0.31 | 扩→扩 | 96611（100）✅ | 可选 |
| — | L1 | Sunlord SWPA5040S220MT C68434 | C83472 SWPA4030S220MT | 22µH，Isat 约 1.0–1.3A，低于 LMR16006 最大限流 1.7A；每块只省 ¥0.10 | 4×4 | — | 0.10 | — | — | 不推荐 |
| — | D7 / C_BST / R_FB1 / R_FB2 | SS210 等 | — | 都已经是基础库，而且单价很低 | — | — | — | — | — | 不换 |
| P7 | U7 | TI SN65HVD230DR C12084 | C55259679 HGSEMI SN65HVD230M/TR-HG | 引脚相同；VCC 3.0–3.6V；Rs 三种模式与 TI 相同；总线 ESD ±16kV HBM；5Mbps；待机电流 400µA 典型 / 600µA 最大（TI 370 / 600µA）；共模范围 −2~7V（相同） | SOIC-8：焊盘从 0.59×1.8@±2.6 变为 0.57×1.95@±2.71，差异很小 | ¥3.725→¥2.618 | 1.11 / 0.78 | 扩→扩 | 2435（100）✅ | 可选；另一个备选 C46596299 JSM，库存 20967，每块省 0.90 / 0.66，但它的手册是扫描件，没有核对参数 |
| — | C_CAN / R_RS | 基础库 | — | 不换料。但要注意：**R_RS = 10kΩ 接地是「斜率控制」模式**（手册写明 10k 约 15V/µs），不是 BOM 备注里说的「高速模式」。高速模式要把 Rs 直接接地，或者经 < 1V 压降接地。500kbps 用斜率控制一般也能工作，由设计方决定 | — | — | — | — | — | 存疑（见存疑 12） |

## 表 4：MP2797 外围按手册 Table 18 逐件点名与选料

表中「耐压」按 8 串的电位来选：VTOP 和 PACKP 取 BAT+ / PACK+，浪涌 53V，所以选 100V；VCP 按手册「80V × 8/16 = 40V」折算。

| 手册位号 | 手册值 | 所在电位 / 耐压要求 | 现 BOM | 建议嘉立创料 | 库 | 10 块单价 |
|---|---|---|---|---|---|---|
| CVTOP_FLT | 470nF（Required） | VTOP，≥63V → 100V | C_VDD 1µF 100V 1206（C13832）**值不符** | C5375914 CCTC 470nF 100V X7R 0805 | 扩（+1 种） | ¥0.175 |
| RVTOP_FLT | 20Ω（Required） | — | R_VDD 100Ω **值不符** | C22950 20Ω 0603 | 基础 | ¥0.018 |
| CPACK_FLT | 10nF（手册写明不能增大也不能减小） | PACKP，100V | **缺** | C282516 CCTC 10nF 100V X7R 0603 | 扩（+1 种） | ¥0.038 |
| RPACK_FLT | 100Ω | — | R_PACK1/2 为 2×1MΩ，**与手册不同** | C25076 100Ω 0402（BOM 里已有） | 基础 | ¥0.009 |
| RVMID | 100Ω | — | **缺** | C25076 | 基础 | ¥0.009 |
| CVMID | 100nF | VMID 可能到 PACK+ 的 53V → 100V | 在 C_AFE1–3（C113803，100V）里 | **C28233** 100nF 100V X7R 0805 | 基础 | ¥0.253 |
| CVCP | **47nF**，额定电压 80V×8/16 = 40V | VCP 到 VMID | C_AFE 为 100nF，**值不符** | **C1622** 47nF 50V X7R 0603 | 基础 | ¥0.052 |
| CVDD | 1µF | 1.8V | C_LDO1 | C52923（第一轮推荐）或维持 C15849 | 基础 | ¥0.070 |
| C3V3 | 1µF（0.47–10µF） | 3.3V | C_LDO2 | 同上 | 基础 | ¥0.070 |
| CVREF | 1µF | VREF 3.3V | **缺**（C_AFE 的第三颗可以改作 CVREF） | C52923 1µF 25V 0402 | 基础 | ¥0.070 |
| CREGIN | **3.3µF** | REGIN 4.5–5.5V | **缺** | C19666 4.7µF 16V X5R 0603（BOM 已有；5V 下有效约 3.3µF） | 基础 | ¥0.209 |
| NPN_REGIN | 手册示例 FZT853TA（SOT-223，100V） | 集电极接 VTOP（经 RREG），≥60V | **缺** | **C2145 MMBT5551**（160V、600mA、300mW、SOT-23）。REGIN 实际负载只有 MP2797 自身和少量 3V3 负载，按 ≤5mA 估算功耗约 0.11W。**如果实测超过 5mA**，改用 C24280 BCX56（80V、SOT-89，¥0.32，+1 种扩展库） | 基础 | ¥0.108 |
| RREG | 500Ω | 限流电阻 | **缺** | C23193 510Ω 0603 | 基础 | ¥0.017 |
| CREG | 1µF | Figure 27 中接在 RREG 与 NPN 之间，保守按 VTOP 电位取 100V | **缺** | C13832 1µF 100V 1206（BOM 已有，不增加种类） | 扩（不新增种类） | ¥0.454 |
| CNTCB | 10nF | NTCB 3.3V | **缺** | C15195 10nF 50V 0402（BOM 已有） | 基础 | ¥0.036 |
| CSRN_GND / CSRP_GND | 100nF ×2 | SRP/SRN 在 GND 附近 | C_SNSC1/2 为 10nF，**值不符** | C14663 100nF 50V 0603 | 基础 | ¥0.087 |
| CSRN_SRP | 100nF | — | C_SNSD 100nF ✅ | 不变 | 基础 | — |
| RSRN_FLT / RSRP_FLT | 100Ω | — | R_SNS1/2 100Ω ✅ | 不变 | 基础 | — |
| RCELL_FLT / CCELL_FLT | 20–100Ω / 100nF | — | 33Ω / 100nF ✅ | 不变 | 基础 | — |
| RCHG_PUP / RDSG_PUP | **10MΩ** ×2 | 栅极上拉 | **缺**（BOM 用的是 RGS 100kΩ×12，G-S 下拉） | C7250 10MΩ 0603 ×2 | 基础 | ¥0.026 |
| RCHG_DRVER / RDSG_DRVER | 100Ω ×2 | 驱动输出保护 | **缺**（BOM 用 D4/D5 加 PNP 快关结构） | C25076 ×2 | 基础 | ¥0.009 |
| RMG | 100Ω / 管 | 栅极电阻 | RG1–12 为 10Ω，**值不符** | 改用 C25076（价格与原料相当） | 基础 | ≈0 |
| DCHG-VGS / DDSG-VGS | 16V 稳压管 | — | DZ1/DZ2 MM3Z15 15V ✅（≤16V 可以用） | 不变 | — | — |
| DAGND-C0 | 3.3V 稳压管（Recommended） | AGND 到 C0 | **缺** | C353528 晶导微 BZT52C3V3 SOD-123 | 扩（+1 种；嘉立创基础库没有稳压管） | ¥0.099 |
| RNTC_PUP / RNTC | 10k / 10k | — | ✅ | 不变 | — | — |
| RSENSE | 0.2–5mΩ | — | 0.1mΩ，**低于手册下限** | 见表 5 | — | — |
| CPACK_E | 47–200µF | 负载侧（逆变器输入电容），不在本板 | — | 不计入 BOM | — | — |

### 补全前后的差异与成本

- **取消或替换**：C_AFE1–3（C113803×3）、C_VDD（C13832）、R_VDD（100Ω）、R_PACK1/2（1M×2）、C_SNSC1/2（10nF×2）。
- **新增或替换为**：CVCP、CVMID、CVREF、CREGIN、CREG、RREG、NPN_REGIN、CVTOP、RVTOP、CPACK、RPACK、RVMID、RCHG/RDSG_PUP×2、RCHG/RDSG_DRVER×2、CSRN/CSRP_GND×2、CNTCB、DAGND-C0，共 20 颗。
- **成本**：原来这些料 10 块档 ¥0.84/块，补全后 ¥1.79/块，差价 **+¥0.95/块**。扩展库种类 −1（C113803）+3（C5375914、C282516、C353528），**净增 2 种**，10 块档上料费 +¥1.60/块。
- **合计补全后 AFE 模块新增：10 块档 +¥2.55/块，100 块档 +¥1.05/块**。
- RG 从 10Ω 改 100Ω、RGS 100kΩ 与手册 10MΩ 上拉不一致这两处，需要设计方按 Figure 27 定拓扑，成本影响约为 0，所以没有计入。

## 表 5：分流器 0.1mΩ 与 0.2mΩ 对比（数据供用户决定，不替用户做选择）

依据 MP2797 电气特性（电流 ADC ±100mV、16 位、失调 ±12µV）、Table 4（放电 OC：RNG0 每档 2.5mV、满量程 80mV；RNG1 每档 7.5mV、满量程 240mV）、Table 6（充电 OC：每档 1.6mV、满量程 51.2mV）、Table 8（放电 SC：RNG0 每档 5.5mV、满量程 176mV）、Table 9（充电 SC：RNG0 每档 2.5mV、满量程 80mV），以及手册 p25「只有单侧 MOS 导通时 OC 限值取配置值与 17.5mV 中较小者」。阈值取自 `firmware/src/bms_config.h` 和 `03-详细设计.md`。

| 项 | 0.1mΩ（C6075508 ASR-S-7-0.1F） | 0.2mΩ（**C469442 ASR-M-7-0.2F**） |
|---|---|---|
| 规格 | CuMnSn，±1%，TCR ±200ppm，15W，5930 | 锰铜 CuMn，±1%，**TCR ±100ppm**，15W，5930（封装同一系列） |
| 单价（10 / 100 块） | ¥4.62 / ¥3.56 | **¥2.63 / ¥1.98**（再省 1.99 / 1.58） |
| 嘉立创库存 | 21012 | 5729 |
| 是否在手册推荐范围 0.2–5mΩ 内 | 否（低于下限） | 是 |
| 200A 持续发热 / 120A 充电 | 4.0W / 1.44W | **8.0W / 2.88W**（15W 额定下用到 53%；热量进 PCB 和铜排，要重新做热评估） |
| 800A 短路脉冲（200µs） | 64W，12.8mJ | 128W，25.6mJ（脉冲能量很小，没有问题） |
| 200A 时 SRP−SRN | 20mV | 40mV |
| 电流 ADC 量程 / 分辨率 / 失调 | ±1000A / 30.5mA / ±120mA | ±500A / 15.3mA / **±60mA**（待机库仑计误差减半） |
| SCP 800A（放电 SC，RNG0） | 80mV，每档 55A（可设 770A 或 825A） | 160mV，每档 27.5A（可设 797.5A 或 825A） |
| 硬件 OCD 400A / 10ms | 40mV，RNG0 每档 25A，可以精确设到 400A | 80mV，**正好是 RNG0 满量程**，只能改用 RNG1（每档 37.5A，可设 375A 或 412.5A） |
| 固件 OCD1 220A / OCD2 300A | 22mV / 30mV（RNG0 每档 25A） | 44mV / 60mV（RNG0 每档 12.5A） |
| OCC 132A（充电 OC，每档 1.6mV） | 13.2mV，每档 16A（可设 128A 或 144A） | 26.4mV，每档 8A（可设 128A 或 136A） |
| 充电短路（Table 9 RNG0） | 每档 25A，满量程 800A | 每档 12.5A，满量程 400A |
| 单侧 MOS 导通时的 OC 上限（17.5mV） | 175A | **87.5A**：预充阶段或欠压后只开 CHG 管充电时，充电电流超过 87.5A 就会触发；120A 满流充电必须在两侧 MOS 都导通后才能进行 |
| 固件需要改的地方 | — | 电流换算系数 ×2、OCD 量程改用 RNG1、单侧导通状态的电流限制 |

## 表 6：第一轮「可选」项的补充核对

| 项 | 规格（已查手册） | 封装 | 价格 / 库存 | 结论 |
|---|---|---|---|---|
| D1–D3 → C2976503 DOWO SMDJ33A | 手册：3000W，Vbr 36.70–40.60V，Ipp 56.29A，Vc 53.3V，与原料一致 | SMC，0 差异 | 省 1.04 / 0.94，库存 725（需 300） | 维持**可选**，四项都满足；MDD C2994125 仍未取到封装 |
| QN → C479060 PUOLOP AO3416 | 手册：20V，Rds 21 典型 / 26 最大 mΩ@2.5V，Vth 0.45–1.0V，±10V 栅压 | 与 AO3400A 现有封装 0 差异 | 省 0.53 / 1.08（已扣 +¥8），库存 9188 | 维持可选（需实测直通） |
| RT1–4 → C52155402 APV ANTC1608-103F3380FB | 手册：10kΩ ±1%，B25/50 3380K，B25/85 3435K，−40~125℃，与 Murata 同口径 | R0603，0 差异 | 省 0.76 / 0.44，库存 136302 | 维持可选（固件 R-T 表要复核） |
| U8 → C2687131 UMW PESD2CAN | 手册：Vrwm 24V，Vbr 26.1–30.2V，Ipp 5A（8/20µs），Vc 41V@5A，Cj 25pF 典型 / 30pF 最大 | SOT-23，0 差异 | 省 0.30 / 0.18，库存 675185 | 可以升为**推荐**（参数与 Nexperia 原料相同） |

---

## 第二轮汇总（取代第一轮汇总的总计）

基准：第一轮时 `05-成本估算.md` 的元器件合计，10 块档 ¥202.26/块，100 块档 ¥156.24/块，扩展库 25 种。
（核对：第一轮推荐项已写入 BOM（提交 da55443），`05-成本估算.md` 12:05 版重算的 10 块档是 **¥187.26、23 种**，与本报告预测的 202.26 − 15.00 = 187.26、25→23 种一致。下表各行都是相对这个旧基准的累计变化。）

| 方案 | 10 块档每块 | 100 块档每块 | 扩展库种类 |
|---|---|---|---|
| 第一轮「推荐」（RS1、QP、Q17/18、Y1、J5、J6、D4/D5、C_LDO、J7） | −15.00 | −10.26 | −2 |
| 第二轮「推荐」（D6 换料、C_IN_E、C_IN1、C_OUT1） | −4.82 | −3.80 | −1 |
| **「推荐」合计** | **−19.82 → ≈ ¥182.4** | **−14.06 → ≈ ¥142.2** | **25→22** |
| MP2797 按 Table 18 补全（必须做，是成本增加项） | +2.55 | +1.05 | +2（→24） |
| **推荐 + 补全** | **≈ ¥185.0（−8.5%）** | **≈ ¥143.2（−8.3%）** | **24** |
| 第一轮「可选」（CF 减量、F2–F10、C1–C14 减量、TVS、QN、NTC、U8） | −13.37 | −9.53 | +1（QN） |
| 第二轮「可选」（U4 Tokmas、U7 HGSEMI、F11 JDT、删 D6） | −4.21 | −2.53 | −1（删 D6） |
| **推荐 + 补全 + 全部可选** | **≈ ¥167.4（−17%）** | **≈ ¥131.2（−16%）** | **24** |
| 另：RS1 改 0.2mΩ（表 5，由用户决定） | 再 −1.99 | 再 −1.58 | 0 |

说明：第一轮表 1 第 17 项（C_AFE 改用 C28233）已经被 MP2797 补全取代，不再单独计算。

## 存疑（第二轮新增）

12. **CAN 的 R_RS 模式**：10kΩ 接地是斜率控制模式，约 15V/µs，不是 BOM 备注写的高速模式。如果要高速模式，需要把 Rs 直接接地（或接 0Ω）。两种接法成本相同，由设计方决定。
13. **REGIN 外置 NPN 的功耗**：MMBT5551 按 REGIN 电流 ≤5mA 选型。手册示例用 FZT853（SOT-223），是按 REGIN 最大 50mA 设计的。需要实测 MP2797 工作时的 REGIN 电流，超过 5mA 就改用 BCX56（C24280）。CREG 和 RREG 的具体位置要按 Figure 27 核对。
14. **MP2797 VTOP 测量 / 工作范围下限 18V**（电气特性里 VTOP = 18–75.2V）：8 串 LFP 在 2.25V/节（18V）以下时，AFE 的 VTOP 相关功能超出规格范围。需要设计方确认欠压保护阈值（例如 2.5V/节 = 20V）留有足够裕量。
15. **栅极网络与手册拓扑不一致**：MPS 用 10MΩ 上拉、100Ω 驱动电阻、每管 100Ω 栅阻；BOM 用 RGS 100kΩ×12 下拉、10Ω 栅阻，再加 D4/D5 和 PNP 快关。其中 12 只 100kΩ（每组并联约 16.7kΩ，12V 下约 0.72mA）会不会超过 MP2797 电荷泵的驱动能力，需要按手册核实。这会影响第一轮 Q17/18、D4/D5 的换料是否仍然需要。
16. **D6 删除**、**U4 换 Tokmas**（静态电流 80µA）都要由设计方确认。U4 的 Tokmas 封装在 EasyEDA 取不到，采纳前要重取。

---

## 采纳记录（2026-09-26）

- 用户 12:18：分流器保持 0.1mΩ；MP2797 外围按 Table 18 补全（**CVCP 按 Table 22 取 100nF**，不是表 4 的 47nF）；D6 删除（P1b）；C_IN_E 换 C48971005（P2）；R_RS 由设计方定为 0Ω 高速模式。
- 用户 13:57：第 2 轮剩余推荐（P3、P4、U8）与可选（P5 U4、P6 F11、P7 U7）全部采用，已写入 `docs/02-BOM.csv`。
- 表 6 另外三项可选（D1–D3、QN、RT1–4）尚未确认。
- 用户 14:46：第 1 轮可选项采用：3（QN AO3416）、4（CF 2 颗 + 75kHz）、5（F2–F10 大毅）、7（C1–C14 减为 6）、7b（C282823）、9b（J5 C40669）、11（D1–D3 DOWO）、14（RT APV）。
  未采用：1b（EasyEDA 无封装，自画违反规则 0e）、10b（封装缺定位孔需自补，待用户定）、11b（与 11 二选一）、17（C_AFE 已随外围补全取消）。
