colemandlut/MP2645A-BMS/docs/04-立创选料.md

# 04 立创选料（8S LiFePO4 200A BMS）

> 查询日期：2026-09-26。lcsc.com / szlcsc.com / jlcpcb.com / datasheet.lcsc.com 网页被网络策略拦截，
> 表中信息**全部来自 WebSearch 的搜索结果标题和摘要**，没有打开过商品页。
> 库存、价格是搜索引擎抓取时的快照（LCSC 国际站多为美元价），**下单前必须到立创商城核实**。
> 表中写「未见」的，就是搜索结果里没看到，不是没有。
> 「嘉立创库/库存」一栏：搜索结果里**都看不到**基础库/扩展库标记和嘉立创 SMT 库存（这和立创商城库存是两个独立的库存），
> 所以统一写「未见，需在嘉立创核实」。

## 料号表

| 序号 | 用途 | 立创编号 | 制造商型号 | 封装 | 关键参数 | 库存/价格（立创商城） | 嘉立创库/库存 | 是否替代及差异 | 来源 |
|---|---|---|---|---|---|---|---|---|---|
| 1 | AFE 电池监测保护 | **C18198873** | MPS MP2797DFP-0000-T | TQFP-48(7x7) | 7–16S，双 ADC（16 路电芯电压 + 4 路 NTC + 芯片温度；另一路 ADC 采电流），内置 CHG/DSG 驱动，OCP/SCP/OVP/UVP/温度保护；托盘 120 片/盘 | 未见 | 未见，需在嘉立创核实 | 原型号 | [szlcsc 19353268](https://item.szlcsc.com/19353268.html) |
| 2a | 5 节主动均衡 | **未查到** | MPS MP2645A（pre-release） | QFN-19(4x4)（新闻稿） | 5 节双向 buck-boost，均衡电流最高 3.75A，单线可级联到 33 串，支持 LiFePO4；2026-07-21 才发布 | 立创未见 | 未见 | 立创**没有搜到**，也没有同规格替代 | [MPS 新品页](https://www.monolithicpower.com/en/products/new-products.html)、[PR Newswire 新闻稿](https://www.prnasia.com/story/541313-1.shtml) |
| 2b | 同上（非 A 版） | **未查到** | MPS MP2645 | 未见 | MPS 官网有产品页；GitHub 上有 MPQ2645 编程工具 | 立创未见 | 未见 | 立创**没有搜到**。立创只有一篇 MPS 直播新闻稿提到「高性价比主动均衡方案」 | [MPS MP2645](https://www.monolithicpower.com/en/mp2645.html)、[立创新闻 15805](https://www.szlcsc.com/news/15805.html) |
| 3 | 100V 输入 buck → 5V | **C404013** | MPS MP9486AGN-Z | SOIC-8-EP | 输入 4.5–100V；连续输出 1A；只集成**上管**高压 MOSFET，峰值电流限 3.5A（典型）；**迟滞电压控制**，不需要补偿；频率由迟滞环路决定，最高 1MHz；FB 平均电压约 **0.2V**；Iq 170µA；**需外接低 Vf 肖特基续流管到地**（数据手册原话 "A low forward voltage Schottky rectifier to ground is required"）→ **非同步** | 未见（第三方统计 2021–2025 市场均价约 0.63 USD，不是立创价） | 未见，需在嘉立创核实 | 原型号 | [szlcsc 391004](https://item.szlcsc.com/391004.html)、[JLCPCB C404013](https://jlcpcb.com/partdetail/Monolithic_PowerSystems-MP9486AGNZ/C404013)、[MP9486A 手册(Mouser)](https://www.mouser.com/datasheet/2/277/mp9486a_r1.0-1382496.pdf)、[MPS MP9486A](https://www.monolithicpower.com/en/mp9486a.html) |
| 4 | 3.3V LDO | **C6096988** | MPS MP2013AGQ-33-Z | QFN-8(3x3) | 输入 2.5–40V，150mA，Iq 3.3µA，固定 3.3V；带 EN；过温和限流保护 | 未见（搜索摘要里有 $0.0391，MPS 料不太可能这么便宜，**存疑**） | 未见，需在嘉立创核实 | 原型号（MP2013A 存在，已确认）。立创还有可调版 **MP2013AGQ-Z**（立创商品页 4313933，C 编号没搜到） | [JLCPCB C6096988](https://jlcpcb.com/partdetail/7038721-MP2013AGQ_33Z/C6096988)、[szlcsc 4313933](https://item.szlcsc.com/4313933.html)、[MPS MPQ2013A](https://www.monolithicpower.com/en/mpq2013a.html) |
| 5 | MCU | **C2847904** | ST STM32G0B1CBT6 | LQFP-48(7x7) | Cortex-M0+，128KB Flash，带 FDCAN | 起价约 $1.3872（LCSC）；库存未见 | 未见，需在嘉立创核实 | 原型号 | [LCSC C2847904](https://www.lcsc.com/product-detail/C2847904.html)、[JLCPCB](https://jlcpcb.com/partdetail/Stmicroelectronics-STM32G0B1CBT6/C2847904) |
| 6 | CAN 收发器 | **C38695** | NXP TJA1051T/3/1J | SOIC-8 | 高速 CAN，ISO 11898-2；VCC 4.5–5.5V；/3 版带 **VIO**，可直接接 3.3V MCU；支持 5Mbps CAN FD | 30,400 片，起价 $0.3561（LCSC） | 未见，需在嘉立创核实 | 原型号。同款另一个编号：TJA1051T/3,118 = **C58988** | [LCSC C38695](https://www.lcsc.com/product-detail/C38695.html)、[JLCPCB C58988](https://jlcpcb.com/partdetail/NXPSemicon-TJA1051T_3118/C58988)、[szlcsc 60033](https://item.szlcsc.com/60033.html) |
| 7 | CAN ESD | **C75176** | Nexperia PESD2CAN,215 | SOT-23 | 双路 CAN 线保护，230W(8/20µs)，5A 下钳位 41V | 起价 $0.0793（LCSC）；库存未见 | 未见，需在嘉立创核实 | 原型号 | [LCSC C75176](https://www.lcsc.com/product-detail/C75176.html)、[JLCPCB](https://jlcpcb.com/partdetail/Nexperia-PESD2CAN215/C75176) |
| 8a | 主功率 N-MOS（首选） | **C531199** | Infineon IPT012N08N5 | TOLL（HSOF-8） | N 沟道，80V，300A，Rds(on) ≤ 1.2mΩ@10V，Qg ≈ 178nC，OptiMOS 5 | **1,762 片**，起价 $1.4659（LCSC） | 未见，需在嘉立创核实 | 原型号。16 颗用量（8 并 × 2）**库存够** | [LCSC C531199](https://www.lcsc.com/product-detail/C531199.html)、[Infineon](https://www.infineon.com/part/IPT012N08N5) |
| 8b | 同上（备选 1） | **C19626224** | Tokmas IPT012N08N5(TOKMAS) | TOLL | 标称与 Infineon 同规格：80V、300A、1.2mΩ@10V；Qg 未见 | 起价 $0.9553；库存未见 | 未见 | **国产 pin-to-pin 仿制版**；Qg、SOA、雪崩能量未核对，必须看它自己的手册 | [LCSC C19626224](https://www.lcsc.com/product-detail/C19626224.html) |
| 8c | 同上（备选 2） | **C108964** | Infineon IPT015N10N5 | TOLL（HSOF-8） | N 沟道，**100V**，350A，Rds(on) ≤ 1.5mΩ@10V；Qg 未见 | 约 34,000 片，起价约 $0.7694（这个摘要可能混了 Tokmas 版，**存疑**） | 未见 | 替代。**升级**：耐压 80V→100V；**降级**：Rds(on) 1.2→1.5mΩ（+25%，200A 单管导通损耗随之 +25%） | [LCSC C108964](https://www.lcsc.com/product-detail/C108964.html)、[JLCPCB](https://jlcpcb.com/partdetail/InfineonTechnologies-IPT015N10N5/C108964) |
| 8d | 同上（备选 3） | 未查到 C 编号 | AGMSEMI 芯控源 AGM016T08LL | TOLL | 80V；Rds(on) 标称约 1.6mΩ（型号推断，未见参数）；Qg 未见 | 约 $1.19–1.27；库存未见 | 未见 | 国产替代，Rds(on) 可能超过 1.5mΩ，**参数不全，不推荐**。另有 onsemi FDBL86361-F085（C900881，80V/1.1mΩ 典型，H-PSOF8L 封装，与 TOLL 不同）只有 1 片库存、$4.75，也不推荐 | [szlcsc 6251868](https://item.szlcsc.com/6251868.html)、[LCSC C900881](https://www.lcsc.com/product-detail/MOSFETs_onsemi-FDBL86361-F085_C900881.html) |
| 9 | PACK 端 TVS 3000W | **C438163** | 晶导微 SMDJ33A | SMC(DO-214AB) | 单向，3000W(10/1000µs)，Vrwm 33V，钳位 53.3V | 2,085 片，起价 $0.1331 | 未见，需在嘉立创核实 | 原型号（国产品牌）。Littelfuse 只搜到**双向** SMDJ33CA（C151293，$0.3284），和单向 SMDJ33A 不是一个东西 | [LCSC C438163](https://www.lcsc.com/product-detail/C438163.html)、[LCSC C151293](https://www.lcsc.com/product-detail/TVS_Littelfuse_SMDJ33CA_Littelfuse-SMDJ33CA_C151293.html) |
| 10 | TVS 600W | **C78419** | Brightking SMBJ33A | SMB(DO-214AA) | 单向，600W，Vrwm 33V | 未见 | 未见，需在嘉立创核实 | 原型号。其它品牌：晶导微 C353366、EIC C3015319、SMC C499719 | [LCSC C78419](https://www.lcsc.com/product-detail/esd-and-surge-protection-tvs-esd_brightking-smbj33a_C78419.html)、[LCSC C353366](https://www.lcsc.com/product-detail/C353366.html) |
| 11 | PNP 三极管 | **C89581** | Nexperia PBSS5140T,215 | SOT-23 | PNP，40V，1A，hFE 300@100mA，450mW | 起价 $0.0371；库存未见 | 未见，需在嘉立创核实 | 原型号 | [LCSC C89581](https://www.lcsc.com/product-detail/Bipolar-Transistors-BJT_Nexperia-PBSS5140T-215_C89581.html) |
| 12 | 小信号肖特基 | **C22629** | 长电 CJ BAT54WS | SOD-323 | 30V，200mA（BAT54 通用规格；Vf 未见，一般 ≤0.8V@100mA） | 未见 | 未见，需在嘉立创核实 | 原型号（国产）。其它：扬杰 C699104、High Diode C466657、FUXINSEMI C3040452 | [CJ 手册 C22629](https://datasheet.lcsc.com/lcsc/1809140116_Jiangsu-Changjing-Electronics-Technology-Co---Ltd--BAT54WS-L9_C22629.pdf)、[LCSC C699104](https://www.lcsc.com/product-detail/C699104.html) |
| 13 | 15V 稳压管 | **C65676** | 先科 ST(Semtech) MM3Z15 | SOD-323 | Vz 15V，约 300mW（同系列 MM3Z3V3 标 300mW） | 未见 | 未见，需在嘉立创核实 | 原型号。另：晶导微 MM3Z15 C128716 | [LCSC C65676](https://www.lcsc.com/product-detail/Zener-Diodes_MM3Z15_C65676.html) |
| 14a | 预充 P-MOS（SOT-23） | **C727403** | Vishay SQ2361ES-T1_GE3 | SOT-23 | P 沟道，-60V，Id -2.8A（Tc=25°C）/-1.6A（125°C），Rds(on) 177mΩ@-10V、246mΩ@-4.5V，AEC-Q101 | 起价 $1.1814；库存未见 | 未见 | 满足本次料单的 ≥2A；**但 03-详细设计.md 写的是 ≥3A，2.8A 不满足**。预充峰值 0.97A，实际够用 | [LCSC C727403](https://lcsc.com/product-detail/MOSFET_Vishay-Intertech-SQ2361ES-T1-GE3_C727403.html)、[Vishay 手册](https://www.vishay.com/doc/?66894=) |
| 14b | 同上（电流更大） | **C727331** | Vishay SI3127DV-T1-GE3 | **TSOP-6** | P 沟道，-60V，-5.1A，Rds(on) 74mΩ，4.2W | 未见 | 未见 | **封装替代**：不是 SOT-23/SOT-89，是 TSOP-6；电流和 Rds(on) 都比 14a 好得多 | [LCSC C727331](https://lcsc.com/product-detail/MOSFET_Vishay-Intertech-SI3127DV-T1-GE3_C727331.html)、[Vishay 手册](https://www.vishay.com/docs/64282/si3127dv.pdf) |
| 15 | NTC | **C13564** | Murata NCP18XH103F03RB | 0603 | 10kΩ ±1%；**立创标的 B 值是 3380K ±1%（这是 B25/50）**；Murata 这颗料的 B25/85 约 3435K | 约 400,000 片，起价 $0.0296 | 未见，需在嘉立创核实 | 原型号。**注意 B 值口径**，见下文「对设计的影响」 | [LCSC C13564](https://www.lcsc.com/product-detail/C13564.html)、[JLCPCB](https://jlcpcb.com/partdetail/MurataElectronics-NCP18XH103F03RB/C13564) |
| 16a | 分流器 100µΩ | **C2091034** | Vishay WSLP5931L1000FEA | 5931（15.0×7.75mm） | 0.1mΩ ±1%，**15W**，TCR ±300ppm/°C，金属带（Power Metal Strip），AEC-Q200 | 起价 $0.9338；库存未见 | 未见 | 替代。功率满足（≥10W）；**但它是 2 端子**，不是 4 端子开尔文，要靠焊盘切分做开尔文取样；TCR ±300ppm 偏大（200A 发热时误差明显） | [LCSC C2091034](https://www.lcsc.com/product-detail/Current-Sense-Resistors-Shunt-Resistors_Vishay-Intertech_C2091034.html)、[Vishay 手册](https://www.vishay.com/docs/30176/wslp3921-wslp5931.pdf) |
| 16b | 同上（锰铜，TCR 好） | **C2927618** | Milliohm 毫欧 HoLRS6568-5W-0.1mR-1% | 6.6×6.6mm | 0.1mΩ ±1%，**5W**，TCR ±50ppm/°C | 未见 | 未见 | 替代。**降级**：5W < 10W 要求（200A 下 I²R = 4W，余量只有 25%），端子数未见 | [JLCPCB C2927618](https://jlcpcb.com/partdetail/Milliohm-HoLRS6568_5W_0_1mR_1/C2927618) |
| 16c | 同上 | **C5127845** | Milliohm HoLRS1575-0.1mR-1% | 15×7.5mm | 0.1mΩ ±1%；功率、端子数未见 | 160 片，$0.2179 | 未见 | 参数不全，需看手册 | [LCSC C5127845](https://www.lcsc.com/product-detail/current-sense-resistors-shunt-resistors_milliohm-holrs1575-0-1mr-1_C5127845.html) |
| 17 | 均衡线保险丝 5A | **C553937** | 南京萨特 SART S1206-SD-5.0A | 1206 | 5A，**63V**，大电流系列，-55~125°C；快熔还是慢熔**未见** | 起价 $0.0447；库存未见 | 未见，需在嘉立创核实 | 原规格。另：AEM F1206SB5000V032TM（C311004，5A/32V，$0.1742） | [LCSC C553937](https://www.lcsc.com/product-detail/C553937.html)、[LCSC C311004](https://lcsc.com/product-detail/Surface-Mount-Fuses_AEM_F1206SB5000V032TM_AEM-F1206SB5000V032TM_C311004.html/en) |
| 18 | 辅助电源输入保险丝 1A | **C151135** | Littelfuse 0466001.NRHF | 1206 | 1A 快熔，63V，466 系列薄膜 | 起价 $0.0332；库存未见 | 未见，需在嘉立创核实 | 原规格 | [LCSC C151135](https://www.lcsc.com/product-detail/Fuses_Littelfuse-0466001-NRHF_C151135.html)、[JLCPCB](https://jlcpcb.com/partdetail/Littelfuse-0466001NRHF/C151135) |
| 19 | buck 续流肖特基 | **C15874** | MDD 辰达 SS310 | SMA(DO-214AC) | 100V，3A，Vf 850mV@3A | 未见 | 未见，需在嘉立创核实 | 以 SS310 代替 SS3H10（SS3H10 没查）。其它品牌：GOODWORK C2848687、晶导微 C116705。**别选 DIOFIT C169164，它是 SMC 封装** | [LCSC C15874](https://lcsc.com/product-detail/Schottky-Diodes_MDD-Microdiode-Semiconductor-SS310_C15874.html)、[LCSC C116705](https://www.lcsc.com/product-detail/Schottky-Barrier-Diodes-SBD_SS310_C116705.html) |
| 20 | 采样端子 13P | **C158025** | JST B13B-XH-A(LF)(SN) | 直插，1×13P | **JST 原厂 XH，2.50mm 间距，板端直插座**（B 开头 = 顶插；S13B 是侧插 C157939；XHP-13 C157887 是**线束端胶壳**，不要选） | 3,535 片，起价 $0.1489 | 未见，需在嘉立创核实 | 原型号。不是 2.54mm 的国产 2501 系列 | [LCSC C158025](https://www.lcsc.com/product-detail/Wire-To-Board-Wire-To-Wire-Connector_JST-Sales-America-B13B-XH-A-LF-SN_C158025.html) |
| 21 | 均衡端子 2×5 | **C277725** | Molex 43045-1012 | 直插，2×5P，3.00mm | Micro-Fit 3.0，**立式（Vertical）板端座**，双排 10P，带 PCB 定位柱，镀锡 | 起价 $0.4719；库存未见 | 未见，需在嘉立创核实 | **替代原料单的 43045-1000**：Molex 官网写明 **43045-1000 是弯针（Right-Angle）座**，不是直插；43045-1012 才是同系列 10P 立式座。43045-1000 在立创没搜到 | [LCSC C277725](https://www.lcsc.com/product-detail/C277725.html)、[Molex 430451000](https://www.molex.com/en-us/products/part-detail/0430451000)、[Molex 430451012](https://www.molex.com/en-us/products/part-detail/0430451012) |
| 22 | 8MHz 晶振 | **C2682774** | YXC 扬兴 X32258MSB4SI | SMD3225-4P | 8MHz，±20ppm（精度），负载电容 20pF，ESR 120Ω，-40~85°C | 52,080 片，起价 $0.0928 | 未见，需在嘉立创核实 | 原规格。负载 20pF → 外接电容约 2×(20−Cstray)≈ 2×27–33pF，按 STM32 手册算 | [LCSC C2682774](https://www.lcsc.com/product-detail/C2682774.html)、[JLCPCB](https://jlcpcb.com/partdetail/YXC-X32258MSB4SI/C2682774) |
| 23 | MLCC 1µF 100V | **C13832** | Samsung CL31B105KCHNNNE | 1206 | 1µF ±10%，100V，X7R | 1,271,130 片，起价 $0.0572 | 未见，需在嘉立创核实 | 原规格 | [LCSC C13832](https://www.lcsc.com/product-detail/Multilayer-Ceramic-Capacitors-MLCC-SMD-SMT_Samsung-Electro-Mechanics-CL31B105KCHNNNE_C13832.html) |
| 24 | MLCC 10µF 25V | **C14860** | Samsung CL31B106KAHNNNE | 1206 | 10µF ±10%，25V，X7R | 961,300 片，起价 $0.0904 | 未见，需在嘉立创核实 | 原规格 | [LCSC C14860](https://www.lcsc.com/product-detail/C14860.html) |
| 25 | MLCC 4.7µF 100V | **C162515** | Murata GRM32ER72A475KE14L | 1210 | 4.7µF ±10%，100V，X7R | 起价 $0.2175；库存未见 | 未见，需在嘉立创核实 | 原规格 | [LCSC C162515](https://www.lcsc.com/product-detail/C162515.html) |
| 26 | 铝电解 47µF 50V | **C92059** | Panasonic EEE-FT1H470AP | 贴片（尺寸未见） | 47µF ±20%，50V，FT 低 ESR 系列 | 未见 | 未见，需在嘉立创核实 | 原规格。另：国产 RVT1H470M0607（C3349，6.3×7.7mm）、Rubycon 50SKV47M8X10.5（C2164312，8×10.5mm，预订料） | [LCSC C92059](https://www.lcsc.com/product-detail/Aluminum-Electrolytic-Capacitors-SMD_PANASONIC_EEE-FT1H470AP_47uF-20-50V_C92059.html)、[LCSC C3349](https://lcsc.com/product-detail/Aluminum-Electrolytic-Capacitors-SMD_47uF-50V_C3349.html) |
| 27 | 预充电阻 15Ω 5W | **C334293** | CCO 千佳 CR-L5W-15Ω 5% P | 直插 | 15Ω ±5%，5W；**是不是绕线未见** | 未见 | 未见（直插件不走 SMT） | 替代待核。4.26J 脉冲能量要看手册的脉冲/过载曲线；绕线型更耐脉冲 | [LCSC C334293](https://www.lcsc.com/product-detail/Others_Chian-Chia-Elec-CR-L5W-15RJ_C334293.html) |
| 28 | MLCC 100nF 50V | **C307331** | Samsung CL05B104KB54PNC | 0402 | 100nF ±10%，**50V**，X7R | 起价 $0.0024；库存未见 | 未见，需在嘉立创核实 | 原规格。注意：嘉立创常用的 0402 100nF 基础料 **C1525（CL05B104KO5NNNC）只有 16V**，接到电芯/高压节点不能用 | [LCSC C307331](https://www.lcsc.com/product-detail/C307331.html)、[LCSC C1525](https://www.lcsc.com/product-detail/C1525.html) |
| 29a | 电阻 10kΩ 1% 0402 | **C25744** | UNI-ROYAL 0402WGF1002TCE | 0402 | 10kΩ ±1%，62.5mW，±100ppm | 未见 | 未见（搜索结果把它列在嘉立创热销料里，但没写基础库/扩展库） | 原规格 | [JLCPCB C25744](https://jlcpcb.com/partdetail/26487-0402WGF1002TCE/C25744) |
| 29b | 电阻 100kΩ 1% 0402 | **C25741** | UNI-ROYAL 0402WGF1003TCE | 0402 | 100kΩ ±1%，62.5mW，±100ppm | 未见 | 未见，需在嘉立创核实 | 原规格 | [JLCPCB C25741](https://jlcpcb.com/partdetail/0402WGF1003TCE/C25741) |
| 29c | 电阻 10Ω 1% 0402 | **C25077** | UNI-ROYAL 0402WGF100JTCE | 0402 | 10Ω ±1%（厚声命名：F=1%，100J=10.0Ω） | 未见 | 未见，需在嘉立创核实 | 原规格。**别选 C25086（0402WGF100KTCE），那是 1Ω** | [JLCPCB C25077](https://jlcpcb.com/partdetail/25820-0402WGF100JTCE/C25077) |
| 29d | 电阻 62Ω 1% 0603 | **未查到** | UNI-ROYAL 0603WAF620JT5E | 0603 | 62Ω ±1%，100mW | 未见 | 未见 | 型号已确认存在（TME 有），但立创 C 编号没搜到。60.4Ω 的 0603WAF604JT5E 也没搜到 | [TME 0603WAF620JT5E](https://www.tme.eu/gb/details/0603waf620jt5e/smd-resistors/royalohm/) |
| 29e | 电阻 30Ω 1% 0805 | **未查到** | UNI-ROYAL 0805W8F300JT5E（按命名规则推出来的） | 0805 | 30Ω ±1%，125mW | 未见 | 未见 | 型号是按厚声命名规则推出来的，C 编号没搜到 | — |

## ① 查不到或存疑的项

1. **MP2645A / MP2645（第 2 项）**：立创商城和 LCSC 都没搜到。MP2645A 2026-07-21 才发布，还是 pre-release，封装是 QFN-19(4x4)。**这是整个项目最大的供货风险**，只能找 MPS 代理或官网申请样品。
2. **MP2013AGQ-33-Z 价格（第 4 项）**：搜索摘要里的 $0.0391 很可能是抓错了，不能当真。
3. **80V TOLL 替代（第 8 项）**：Tokmas 版 IPT012N08N5 的 Qg、SOA、雪崩能量都没查到；IPT015N10N5 的库存和价格可能和 Tokmas 版混在一起；AGM016T08LL 的 C 编号和 Rds(on) 都没查到。
   Qg 只确认了 Infineon IPT012N08N5 ≈ 178nC，**其它候选的 Qg 都没搜到，没法按 Qg 比较**。
4. **分流器（第 16 项）**：立创上**没有搜到**同时满足「0.1mΩ + ≥10W + 4 端子 + 锰铜」的料。WSLP5931 功率够但只有 2 端子、TCR ±300ppm；HoLRS6568 TCR 好但只有 5W。
   Isabellenhuette BVS/BVE/BVR 系列立创有货，但搜到的最低阻值是 0.2mΩ（BVR-Z-R0002-1.0，C6869644），没搜到 0.1mΩ。
5. **5A 保险丝是否快熔（第 17 项）**：S1206-SD 是「耐大浪涌」系列，是快熔还是慢熔没查到。
6. **预充电阻（第 27 项）**：C334293 是不是绕线、能不能扛 4.26J 脉冲，都没查到。
7. **62Ω 0603 和 30Ω 0805（29d/29e）**：C 编号没搜到。
8. **P-MOS 的 SOT-89 款（第 14 项）**：没搜到 -60V、≥2A 的 SOT-89 P-MOS。
9. **MP9486A 的 FB 电压 0.2V**：只来自搜索摘要，手册原文没打开过，要用手册核实（包括迟滞宽度和分压公式）。

## ② 需要用户在嘉立创 / 立创亲自核实的项

- **全部 29 项的嘉立创 SMT 库存和基础库/扩展库属性**：这次一项都没看到。尤其是：
  - C18198873（MP2797）、C404013（MP9486A）、C6096988（MP2013A）、C2847904（STM32G0B1）、C531199（IPT012N08N5）。这几颗扩展库料单价高，嘉立创库存可能是 0，可能要走「代购」或「自备料」。
  - 阻容（C25744 / C25741 / C25077 / C307331 / C13832 / C14860）是不是基础库（影响换料费）。
- **立创商城实时库存和价格**：表里的数都是搜索快照，而且多为 LCSC 国际站美元价。
- **IPT012N08N5 数量**：需要 16 颗，LCSC 快照显示 1,762 片，够用，但要核实嘉立创库存。
- **C277725 的封装图**：确认是 43045-1012 立式、2×5、3.00mm、有定位柱，并且和线束端 43025-1000 配套。
- **C158025 的封装图**：确认是 B13B-XH-A（2.50mm，顶插），嘉立创 EDA 的封装不要被换成 2.54mm 的「XH2.54」国产座。
- **C13564 的 B 值**：打开手册，确认 B25/50 = 3380K、B25/85 = 3435K（3434K）。
- **晶振 C2682774 负载电容**：搜索摘要同时出现 12pF 和 20pF，要确认下单的是 20pF 那档。

## ③ 对设计的影响

1. **MP9486A 是非同步 buck → 必须加续流肖特基 D7**
   手册原话「A low forward voltage Schottky rectifier to ground is required」，而且芯片只集成了上管，
   所以 03-详细设计.md 第 174 行的【待核】可以关掉：**SW→GND 必须加 100V/3A 肖特基，选 SS310（C15874，SMA）**。
   其它要改的地方：
   - FB 调节点约 0.2V（待手册核实），5V 输出的分压比约 1:24，和常见 0.8V/1.2V 方案不一样，**不能照抄**；
   - 迟滞控制的频率随 Vin、L、输出电容 ESR 变化（最高 1MHz），不是固定频率。输出如果全用 MLCC、ESR 很低，FB 上的纹波可能不够，
     手册一般要求加前馈电容或纹波注入网络（这一条是推断，需用手册核实）；
   - 连续输出 1A，峰值限流 3.5A，按设计的 ≤300mA 负载，余量足够。
2. **LDO 确定用 MP2013AGQ-33-Z（C6096988）**：QFN-8(3x3)，150mA，Iq 3.3µA，输入最高 40V。它接在 5V 后面，150mA 要够 MCU + CAN（TJA1051 的 VCC 接 5V，VIO 接 3.3V）。
3. **MP2645A 在立创买不到**：BOM 里要把 U 均衡器标成「客供料」，嘉立创 SMT 下单时走自备料流程；或者先做一版不贴均衡器（DNP）的板子。
4. **均衡端子 43045-1000 是弯针座**：如果设计要直插座，BOM 和封装要改成 **43045-1012（C277725）**；如果本来就要弯针，43045-1000 在立创没搜到，需要另找。
5. **NTC 的 B 值口径**：Murata NCP18XH103F03RB 在立创标的是 B25/50 = 3380K，「B3435」是它的 B25/85。
   03-详细设计.md 第 142 行的 V_NTC/V_REF 表，以及 MP2797 的 NTC 阈值和固件查表，要确认用的是哪个 B 值（最好直接用 Murata 的 R-T 表），否则高温保护点会偏几 °C。
6. **分流器**：立创没有完全符合要求的料。建议二选一：
   (a) WSLP5931L1000FEA（15W，2 端子），PCB 上做开尔文取样焊盘，并在固件里做温度补偿（TCR ±300ppm）；
   (b) 立创以外渠道买 4 端子锰铜分流器（如 Isabellenhuette BVS/BVR 0.1mΩ），螺栓固定，按 03-详细设计.md 的铜排方案走。
7. **预充 P-MOS**：SQ2361ES（SOT-23）只有 2.8A，不满足 03-详细设计.md 第 90 行「≥3A」的写法，但实际峰值只有 0.97A，可以把文档要求改成 ≥2A；
   如果坚持 ≥3A，就改用 TSOP-6 的 SI3127DV（C727331），封装要跟着改。
8. **0402 100nF 电容别用 16V 的 C1525**：凡是接在电芯采样、BAT+ 或 PACK+ 上的，都要用 50V 的 C307331 或更高耐压。
9. **TVS**：SMDJ33A 单向，Vrwm 33V > 8S LiFePO4 满电 29.2V，钳位 53.3V < MOSFET 耐压 80V，匹配。
