colemandlut/MP2645A-BMS/obsidian-vault/BMS/8S-LFP-200A-BMS 方案.md

---
tags: [BMS, LFP, MPS, 项目]
created: 2026-09-26
repo: colemandlut/MP2645A-BMS
---
# 8S LFP 200A BMS 方案

- 需求：8S 磷酸铁锂、最大 200A、自动均衡、用 MPS 芯片
- 电芯：**120Ah，充电 1C（120A），放电 10C（1200A）**（用户 2026-09-26）；BMS 持续放电 200A、充电 120A（OCC 132A/3s）、SCP 800A，均在电芯能力内；同口
- AFE：[[MPS 芯片笔记#MP2797|MP2797]]；均衡：[[MPS 芯片笔记#MP2645A|MP2645A]] ×2 级联
- 功率：高边背靠背 NMOS，每方向 8 颗 80V/1.2mΩ TOLL；200A 通路损耗约 20W，最坏 Tj≈79°C（45°C 环境）
- 分流器 100µΩ：200A→20mV/4W；SCP 800A→80mV
- 保护参数见仓库 `firmware/src/bms_config.h`
- 均衡策略见 [[LFP 均衡要点]]
- 详细文档：仓库 `docs/01-系统设计说明.md`

## 待办
- [ ] 获取 MP2645A 正式数据手册（pre-release），确认 8S 接法（C1~C5 + C4~C8 或 4 节配置）
- [ ] 确认 MP2797 高边驱动能力是否足够驱动 8 并联 MOSFET
- [ ] 确认实际电芯容量
- [ ] 编写 MP2797 寄存器驱动

## v0.2 详细设计（2026-09-26）
- 文档 `docs/03-详细设计.md`；KiCad 10 骨架 `hardware/`（`tools/gen_kicad_skeleton.py` 生成，ERC=0）
- 功率拓扑：BAT+ → F1 → DSG×8 → FET_MID(共源) → CHG×8 → PACK+；两组各 PNP 快关 + 15V 钳位【共源/共漏按 MP2797 手册定】
- 均衡线每根 5A 快熔；采样/均衡分线；GND 单点在分流器电池侧
- 电芯采样串阻：若被动均衡电流流经串阻 → 30Ω 0.1W → 0805
- 预充可选：30Ω（2×15Ω 5W），单次 4.26J，1.5s 超时保护
- MP9486A 若为非同步 buck 必须加续流肖特基（规则 00 ①a）
- 阻塞：数据手册全部被网络拦截；codex(gpt-6-astra) 不可用 → 规则 00c 画图分工待用户裁定

## v0.3（2026-09-26）均衡改为 MP2643 ×7
- 用户指令：MP2645A 买不到 → 用 MP2643（MPS 官网：1 片 ¥19.28 / 10 片 ¥17.25 / 100 片 ¥14.46，库存 3639，运费 $5/单），客供给嘉立创贴片
- 第 k 颗：PGND=BAL(k-1)、CL=BALk、CU=BAL(k+1)；7 个本地地铜岛
- 外围（手册 Table 10/9）：L 2.2µH SLO0618H2R2MTT C216189；CCU/CCL 22µF 25V 0805 C45783；C4V5 1µF；CBST 100nF（值待 MPS 确认）
- RUBC 120k → 1.78A（含容差 ≤2A）；RLBC 150k；R1/R2 = 2M/392k → VCU_LIM 7.32V
- EN/MODE：每颗 2 只光耦 EL3H7(C) C92243（共 14），输出侧由 CL 供电、100k 下拉；MCU 复位即全部停止
- 不照搬手册 Fig.7（EN 接 AFE 被动均衡开关），因我们还要用 MP2797 被动微调
- 固件：边界电荷盈亏 E_k 决定方向（>0 buck 上→下，<0 boost 下→上），相邻两颗不同时开；仿真 90mV→10mV 44 步收敛
- 均衡端子改 2×9 Micro-Fit（每节点 2 针），节点保险丝 7A 2410 C99548
- 成本（元器件，不含 PCB/SMT 费）：10 块 ≈ ¥587/块，100 块 ≈ ¥460/块；MOSFET ×16 ≈ ¥214 最大头，MP2643 ≈ ¥121
- 风险：STM32G0B1 与 4.7µF/100V 1210 嘉立创库存 0；降本候选：Tokmas MOSFET（省 ≈¥118）、CH32V203（省 ≈¥38）
- 工具：tools/jlc_api.py（嘉立创 SMT 料号接口：jlcpcb.com/api/overseas-pcb-order/v1/shoppingCart/smtGood/selectSmtComponentList）、tools/cost.py

## v0.3 降本（2026-09-26 用户同意全部降本选项）
- MOSFET：Tokmas IPT012N08N5 C19626224 ×12（每方向 6）；Rds 0.9 typ/1.2 max，Tj,max 150°C，Qg 240nC；最坏 Tj≈105°C、通路 27.2W；封装 jlc:HSOF-8_IPT007N06N（与英飞凌 TOLL 焊盘略不同，符号 1G/2S/3D 已核）；嘉立创库存 746（够 62 块）
- MCU：CH32V203C8T6 C3001172（CAN 2.0B）替代 STM32G0B1（嘉立创库存 0）
- 4.7µF/100V 1210：风华 C381466 替代库存 0 的 C162515
- 基础库化：MP2643 的 120k/150k/2M 改 0603 基础库；33Ω 0805；CAN 单 120Ω；MP9486A 反馈 470k/20k → 4.9V；100nF/50V 用 0603 C14663
- 与规则 00②（封装下探）冲突：为省扩展库上料费选 0603，已在文档注明
- 成本（元器件，不含 PCB/SMT 费）：10 块 ≈ ¥393/块（原 ¥587），100 块 ≈ ¥294/块（原 ¥460）
- MP2643 封装：用户提供 MPS 原厂（Ultra Librarian）KiCad 库 → hardware/lib/mps，已核对手册 p22（FCQFN 无散热焊盘）
- 云端 KiCad 的 chroot 挂载会随容器重启丢失：用前 `mountpoint /opt/kicad-root/home/user || sudo bash tools/setup_kicad.sh`

## v0.3 电源改版（2026-09-26 用户同意换通用降压）
- MP9486A + MP2013A + TJA1051(5V) → **TI LMR16006XDDCR C87080 直降 3.3V** + SS210 C14996 续流 + **SN65HVD230DR C12084（3.3V CAN）**；取消 5V 轨、唤醒或门
- LMR16006：VIN abs 65V，VFB 0.765V（33k/10k→3.29V），SHDN 悬空=常开，ECO 28µA
- 成本（元器件）：10 块 ≈ ¥359/块，100 块 ≈ ¥267/块
- 全器件降本排查由 Opus 取料代理完成 → docs/06-降本排查.md（待用户决定）

## 会话交接
- 2026-09-26 用户在环境变量加了 DEEPSEEK_API_KEY，要求开新会话并转移上下文 → docs/00-会话交接.md；技能压缩包 transfer/pcb-workflow-skill.tar.gz

## v0.3 方案 B：主动均衡改为分立开关电容（2026-09-26 用户选定）
- 原因：MP2643×7 方案均衡部分约 ¥186/块（10 块档），太贵
- 结构：每节一个互补半桥 AO3400A(C20917)/AO3401A(C15127)（均基础库）+ 74LVC1G17(C7394021) 由本节电芯供电驱动共栅；7 级飞电容各 3×100µF/6.3V 1206(C15008 基础库)；时钟 MCU PWM 50kHz → 第 1 节，经 1nF 逐级耦合、1M 偏置；全部同相切换
- 性能：I ≈ ΔV/R_eq，R_eq≈0.48Ω（R_SSL 0.133 + R_FSL 0.464，P 管是瓶颈）→ 100mV≈0.21A，300mV≈0.62A；增强版（N/P 各 2 并 + 100kHz）≈0.37A@100mV，+¥9
- 固件：单个 BAL_CLK 使能；顶部/静置才开；压差 >300mV 或任一节 <3.0V 禁止；测试 37/37
- 保险丝 3A 1206 0466003.NRHF(C14165)；均衡端子 2×5 国产 C3030WV-2x5P(C239457，实测 3.0mm)
- 成本（元器件）：均衡部分 ≈ ¥35/块；整板 10 块 ≈ ¥202/块、100 块 ≈ ¥156/块
- 局限：平台区基本不搬；适合一致性好的同批电芯；离散大时应回到 MP2643 方案

## 降本推荐项全采用（用户 2026-09-26 12:00）
- RS1 业展 ASR-S-7-0.1F C6075508（5930）；QP AO3415A C5350990（36/47mΩ@2.5V）；Q17/18 SS8550 C8542；Y1 12MHz C9002（固件 HSE 12MHz、PLL×12）；D4/D5 1N5819WS C191023；J5 ZX-XH2.54-13PZZ C22366169（实测 2.50mm，修掉 C158025 的 2.54 问题）；J6 连欣 XDWF-C3030WV-2*5P C18202166（针号之字形！按物理位置对针）；J7 C7429634；C_LDO1/2 C52923（0402）
- 开关电容均衡按 AO3415A + 2 只保险丝冷阻重算：100mV ≈ 0.18A，300mV ≈ 0.55A；120Ah 5% 偏差 ≈ 35h
- 成本（元器件）：10 块 ¥202→¥187/块，100 块 ¥156→¥146/块

## 第 2 轮决定（用户 2026-09-26 12:18）
- 分流器定 **0.1mΩ**（低于 MP2797 手册 0.2–5mΩ 下限，接受；固件温补 + 标定）
- **MP2797 外围按手册 Figure 27 / Table 18 补全**：R_VTOP 20Ω + C_VTOP 470nF/100V；REGIN 外置 NPN MMBT5551 C2145 + R_REG 510Ω + C_REG 1µF/100V + C_REGIN 4.7µF；C_VREF、C_NTCB 10nF；C_VMID 100nF/100V + R_VMID 100Ω；R_PACK 100Ω + C_PACK 10nF/100V（不得增减）；SRP/SRN 对地改 100nF；D_C0 BZT52C3V3
- **CVCP 按 Table 22 取 100nF**（ΣCiss = 6×14.49nF = 87nF），不是 47nF —— 第 2 轮代理的 47nF 建议有误
- **栅极网络按手册改**：RG 10Ω→100Ω（RMG Required）；RGS 100k×12 → R_PUP 10MΩ×2（100k×6 并联 16.7k 与 RDSG_ON 2.6kΩ 分压会把 Vgs 从 10V 拉到约 8.6V）；新增 R_DRV 100Ω×2；PNP 快关（Q17/18、D4/5）保留，属手册外增强，闸口 A 专门复核
- 位号重号修正：功率区 PNP 基极电阻 RB1/RB2 → RQB1/RQB2（与均衡 RB1–15 冲突）
- D6 删除；C_IN_E → 63V C48971005；R_RS → 0Ω（高速模式，原 10k 实为斜率控制）
- 成本（元器件）：10 块 ≈ ¥186.5/块，100 块 ≈ ¥144.8/块，扩展库 24 种
- 未决：第 2 轮其余推荐（C_IN1→2×C13832、C_OUT1→C59461、U8 UMW）与可选（U4 Tokmas、U7 HGSEMI、F11 JDT）

## 原理图绘制（2026-09-26 会话 2）
- 流程：DeepSeek（`tools/deepseek_claude.sh`）按任务书写幂等脚本 `hardware/gen/gen_<子图>.py` 生成子图 → 主代理核 ERC/网表 → Opus 复核（`design/<子图>-review-opus.md`）
- KiCad 要点：嵌入 `lib_symbols` 的顶层符号名必须等于 lib_id（`jlc:NAME`），子单元名不带昵称（`NAME_0_1`），否则引脚成 `Pad??`、ERC 报 library ''
- 位号必须「前缀+数字」（`C_IN_E` 这种字母结尾会报 annotation error）→ 04 页用 C40–C43、R40–R41
- jlc 库引脚电气类型已统一为 passive（`fetch_jlc_parts.py --normalize-only`，取库后自动做）
- 🔴 **lib_symbol_mismatch 误报（KiCad 10.0.6）**：嵌入符号与库**逐字节一致**时，带「4 段半圆 arc」的电感符号（SWPA5040S220MT、SLO0618H2R2MTT，pin length 1.27）仍会被 ERC 报 `doesn't match copy in library`——库加载路径与嵌入加载路径对 arc 的内部归一化不一致。二分定位：同时删两侧 arc 即消失，改 pin length / 删 ki_description / 反转 arc start/end 均无效。**非电路问题**，不影响网表/PDF；根治需在 `fetch_jlc_parts.py` 加「电感 arc 归一化」（类似 normalize_pin_types），画 03 页（用 SLO0618H2R2MTT）前应处理
- ⚠ 上一个会话（session_01Ey…）仍在并行推送用户决定（第 2 轮：删 D6、C_IN_E→C48971005 63V、栅极网络改手册拓扑、MP2797 外围按 Table 18 补全、R_RS 0Ω）→ 每步前 `git pull --rebase`，画图以最新 BOM 为准

## 第 2 轮推荐 + 可选全采用（用户 2026-09-26 13:57）
- 推荐：C_IN1 → C_IN1/C_IN2 2×1µF/100V 1206 C13832；C_OUT1 → 22µF/6.3V 0603 C59461；U8 → UMW PESD2CAN C2687131
- 可选：U4 → Tokmas LMR16006XDDCR C54823941（600kHz、VFB 0.770V→3.31V、Iq 80µA，待机 +50µA）；U7 → HGSEMI SN65HVD230M C55259679；F11 → JDT JFC1206-1100FS C136343
- **U4 Tokmas 在 EasyEDA 取不到库** → 符号/封装沿用嘉立创 C87080（TI 同名件）：引脚与 TSOT-23-6 尺寸按 Tokmas 手册核对一致；原理图 LCSC 字段填 C54823941
- 成本（元器件）：10 块 ≈ ¥180.1/块，100 块 ≈ ¥140.3/块，扩展库 23 种
- 表 6 另外三项可选（D1–D3 DOWO C2976503、QN AO3416 C479060、RT APV C52155402）未在本次采用范围，待用户确认
- 🔴 **字段文字角是相对符号的（KiCad 10）**：符号旋转后 Reference/Value 会跟着竖起来（竖放两脚件位号/值「竖排」）。要水平书写，字段角设 `(360-rot)%360`（rot 90→270、rot 270→90、rot 0→0）；字段 `(at x y 角)` 的坐标是图纸绝对坐标，不受抵消角影响
- 🔴 **二脚无源件引脚名==引脚号（只显示数字）**，故竖放不重叠；但 **JLC SS210 二极管符号 quirk**：引脚名 K/A 未给显式位置，KiCad 自动把两个名字都摆到本体中心、彼此重叠约 2mm（横放竖放都这样），引脚号 1/2 正常。纯观感、不影响 ERC/网表；不改库时只能记录在案（04 页 D7 处）
- 版面返工（04 第 3 轮）教训：**坐标必须全落在 1.27mm 栅格**，否则 ERC 刷 31 条 `endpoint_off_grid`；「漂亮整数」（85/115/140/185…）都不是 1.27 倍数，要用 1.27×N（如 86.36/114.30/139.70/185.42）
- 版面（04 第 4 轮）教训：**竖放二脚件并排时，位号/值在器件右侧、引脚号落在器件竖直轴上**（JLC 符号 pin name==number 且无显式位置，KiCad 自动摆）；两颗竖放电容中心距取 **25.4mm**，否则左侧电容的值（如 `1µF 100V`）会压到右侧电容的引脚号。自查文字重叠用 pymupdf 逐 span bbox，先按「同文同位置」去重（KiCad 双绘伪影），只剩真重叠再改
- 04 第 4 轮结论：删 D6 后本页用 **R42 10Ω（C17903 基础库）串在 F11 与 VIN_F 之间** + C40 组 RC 自保（短路 ≤5.3A、上电 I²t≈0.002A²s），新网络 VIN_R={F11.2,R42.1}；F11 换 JDT JFC1206-1100FS（1A 63V C136343）、U4 换 Tokmas C54823941（600kHz、VFB 0.770V→33k/10k=3.31V）、C42/C44 2×C13832 1µF/100V、C43 C59461 22µF/6.3V；P0-1 每个实例补 Footprint/Datasheet 隐藏字段（网表才出封装）

## 第 1 轮可选项采用（用户 2026-09-26 14:46）
- D1–D3 → DOWO C2976503；C1–C14 → C1–C6 共 6 颗（短路关断实测 PACK+ 峰值必须 < 64V，否则补回）；所有 1µF/100V 1206 统一 CCTC C282823
- QN1–8 → AO3416 C479060（基础→扩展，Vth 更低需实测直通）；CF 每级 3→2 颗（21→14），**BAL_CLK 50→75kHz**；F2–F10 → 大毅 C163126（冷阻 23mΩ，−20℃ 下限）
- RT1–4 → APV C52155402（温度阈值按 APV R-T 表复核）；J5 → BOOMELE XH-13A C40669（实测 2.50mm，库存 244）
- 开关电容均衡：100mV ≈ 0.19A，300mV ≈ 0.58A（R_eq 0.52Ω）
- 未采用：1b RS1 毫欧电子（EasyEDA 无封装，只能自画，违反规则 0e，且已选 C6075508）；10b J6 宏诚（嘉立创封装缺定位孔需自补）；11b D1–D3 MDD（与 11 二选一，已选 DOWO）；17 C_AFE（外围补全后已不存在）
- 成本（元器件）：10 块 ≈ ¥166.0/块，100 块 ≈ ¥130.2/块，扩展库 24 种

## 04 子图第 5 轮（2026-09-26，按 Opus 复核第 2 轮 P1 + 取料报告 parts-r5）
- **R42 换熔断电阻**：嘉立创**没有有货的 10Ω 贴片熔断电阻**；有货的是 Ever Ohms FCR1206 系列，**56Ω C153337**（库存 4712，熔断门槛「5W / <30s 受控开路」）→ R42 = `FCR1206J56RP055W` 56Ω 5% 熔断 1206。10Ω→56Ω 后 VIN_F 尖峰峰值 **77V→39V**（270V/3.3µs、C40 ESR 4Ω 最坏），P1-2 的 A/B 改法都不再必须。
- **新增 C45 100nF/100V C28233**（三星 CL21B104KCFNNNE，0805 基础库，库存 174 万）贴 U4.VIN，接 VIN_F–GND，三颗输入陶瓷最靠 U4 的一列；依据 Tokmas 手册 p14「0.1µF ceramic bypass … as close as possible to VIN」。
- **教训（0805 竖放二脚电容引脚名重叠）**：JLC 0805 电容符号引脚距 ±3.81，竖放时 KiCad 自动摆的引脚名 `1`（距下脚 4.23mm）与 `2`（距上脚 3.28mm）在符号中心**重叠约 1.1mm**（pymupdf 实测）；1206（±5.08）的 C42/C44 不重叠，只有 0805 的 C45 中招。根治：库侧归一化给二脚无源件加 `(pin_names hide)`（复核 P2-6 建议，本轮不改库、记录在案）。
- U4 的 Datasheet 字段改 Tokmas 件 PDF `https://www.lcsc.com/datasheet/C54823941.pdf`（原指向 TI C87080 商品页）。
- T 型接点补 junction：C45.2/C42.2/C43.2 三处「引脚 + 两段共线导线」三方相接；`check_04_layout.py` 检查 3 扩展为「引脚处 ≥2 段导线端点相接必须有 junction」。

## 04 子图第 6 轮（2026-09-26，C42/C44 换符号后修版面）
- C42/C44 符号 CL31B105KCHNNNE → **TCC1206X7R105K101HT**（LCSC C13832 → **C282823**，全板 1µF/100V 1206 统一 CCTC，用户 14:46 决定）。网表不变，但换符号后 `check_04_layout.py` 报 3 条（导线穿 C42.1、C42.2 无 junction T 接）。
- **教训（换符号 = 引脚几何变，规则 00 ⓪）**：JLC 二脚无源件的符号「内部朝向」不统一——旧三星 CL31B105KCHNNNE 引脚**横向**（pin1 (−5.08,0) 朝右、pin2 (+5.08,0) 朝左），新 CCTC TCC1206X7R105K101HT 引脚**竖向**（pin1 (0,−5.08) 朝上、pin2 (0,+5.08) 朝下）。**「竖放」所需的 rot 取决于符号内部朝向**：旧符号 rot 90 才竖放，新符号 rot 0 即竖放。换符号后 rot 不变 → 引脚世界坐标平移、导线留在原地。
- 修法：C42/C44 rot **90→0**（脚本 `parse_pins`/`pin_world` 本就从库读引脚坐标，无硬编码偏移；唯一隐含旧几何的是 rot）。引脚世界坐标与第 5 轮完全一致（pin2 上=104.14、pin1 下=114.30），导线/junction/GND 标签一律未动。
- 自检：`check_04_layout.py` 0 条；ERC `/辅助电源/` 0 条（仅根图 BAT+ 预期）；网表与第 5 轮逐网一致、C42/C44 LCSC=C282823；文字重叠仅 D7 K/A、C45 1/2 两处已记录 quirk；幂等 md5 `81c8c50b`。

## 04_power_supply 完成（2026-09-26 15:26，Opus 复核第 3 轮 P0=P1=0）
- 6 轮画图（DeepSeek）+ 3 轮复核（Opus）；快照 `review/04-r6/`；报告 `design/04_power_supply-review-opus{,-r2,-r3}.md`
- 输入链：BAT+ → F11 JDT 1A 63V（C136343）→ VIN_R → **R42 56Ω 熔断电阻 C153337** → VIN_F（C40 47µF/63V + C42/C44 2×1µF/100V C282823 + C45 100nF/100V C28233）→ U4 Tokmas LMR16006（C54823941）
- 关键结论：删 D6 必须靠 R42 与 C40 的 RC 成立（最坏 VIN_F ≈39V）；10Ω 普通厚膜会在 VIN_F 短路时先于 F11 烧开 → 改熔断电阻；56Ω 限 3V3 总负载 ≤0.3A（20V 电池时上限约 0.4A）
- 台架待验：R42 在 16/20/29.2V 短路下熔断时间/温度/明火、100 次上电后阻值漂移；SW 脚负压；C43 负载阶跃
- 库风险：easyeda2kicad 共享封装名（R1206、F1206、C0402…）会被最后取的料覆盖（F11 的 F1206 已被 C163126 覆盖），PCB 前要按料号逐个核焊盘

## 画 05 页起（2026-09-27 00:32 主会话交接，已读 docs/00 0c–0f）
- 画 01/02/03/05 以最新 `docs/02-BOM.csv` 为准；布局约束：外层 2oz / 内层 0.5oz，200A 走 20×2mm 紫铜排 + M8 螺柱，MOS 间走厚铜 + 开窗堆锡，目标板 130×90mm
- 库存风险：Tokmas MOS 够 62 块、D1–D3 约 241、J5 约 244、MP2797 269 片
- 05 页流程：先由 Opus 写设计规格书 `design/05_mcu_comm-spec.md`（逐脚分配、外围点名、缺料补齐），再交 DeepSeek 画
- 05 规格书 `design/05_mcu_comm-spec.md`（Opus，2026-09-27 00:49）：I2C1 PB6/7、CAN1 PA11/12、BAL_CLK PA8 TIM1_CH1（144M/1920=75kHz）、AFE_ALERT PB4（5V 容忍脚，防 AFE 先上电灌电流）、AFE_WAKE=MP2797 NSHDN（PB5 开漏）、PRECHG_EN PA1、LED PB13–15 低有效、键 PB12、PWR_EN 删；复位即停：BAL_CLK/PRECHG_EN 100k 下拉、CAN TXD 10k 上拉
- 订正建议：晶振负载 20pF→33pF（C1562，CL20pF+杂散 2–7pF）；绿灯 1k→330Ω；02 页 R_ALT 10k 上拉→100k 下拉（xALERT 推挽高有效）；CAN 收发器 Standby 400–600µA 超待机目标
- 固件：必须开 IWDG（死机时 BAL_CLK 不停）；AFE 唤醒后 ≥5ms 再 I2C
- 用户 2026-09-27 05 页决定：RS485 不画、调试口 J8 1×6 2.54 DNP、CAN 待机超标接受、晶振 33pF、绿灯 330Ω、删 PWR_EN、02 页 R_ALT 100k 下拉；**CAN 终端 120Ω 要做跳线可选**：R55 串 JP1（C492401 2P 排针）+ 跳线帽 C100114（机械件）
- 05 Opus 复核 r1（2026-09-27 11:19 JST）：P0=0 P1=3（JP1 未画、CAN_H_X/L_X 未进网络类→已改 .kicad_pro、三处文字重叠）P2=11
  - 规格书前提纠错：CH32 手册「HSE drive current 0.53mA」是振荡器耗电不是晶体电流；33pF 后激励功率约 ×2.4，可能超晶振 200µW → OSC_OUT 串 0Ω 预留、样板实测
  - R55 按 VOD 最大 3V 算 75mW（非 33mW），85°C 降额余量约 1.1 倍；PESD2CAN Vrwm 24V < 29.2V，误接 PACK+ 会烧；J8 串口做不了 ISP（BOOT0/NRST 未引出）
- 05 第 2 轮（2026-09-27 13:03 JST）：Opus 复核 r2 P0=0 P1=1（JP1 与 R55 符号叠放）P2=9；教训：「隐藏引脚名」不能清空嵌入符号的 pin name（与库不一致、丢极性语义、同步库会撤销）→ 保持嵌入符号 = 库；自检要有「符号本体/字段两两不相交」
- llm_agent.sh 默认超时 1h 对整页画图/复核不够（DeepSeek 画 05 第 2 轮、qwen3.8-max 复核都超时无产出）→ 画图用 AGENT_TIMEOUT=5400、复核 7200，且复核任务书要求「先建报告、边查边写」
- ✅ 05_mcu_comm 完成（2026-09-27 13:32 JST，Opus 复核 r4 P0=P1=0，P2=8 待用户定）：3 轮画图（DeepSeek v4-pro→flash）+ 4 轮 Opus 复核；快照 review/05-r4；库级 pin_names hide 后 01–03 页画完按「网表 diff / 嵌入符号与库比对 / PDF 目视」三步验收
- 05 第二复核 review2（qwen3.8-27b，2026-09-27 14:18 JST 收稿，审 r2 快照，报告 design/05_mcu_comm-review-qwen.md）：**P0=1 P1=4 P2=3**
  - P0-1：Y1 晶振封装 `CRYSTAL-SMD_4P-L3.2-W2.5-BL` pin 号与 YXC C9002 数据手册 Top View **180° 错位**（pad1 左上 vs 手册贴装外观 pin1 左下；Top/Bottom View 翻转几何自洽无二义）→ 0°/180° 贴装 HSE_IN/HSE_OUT 双双落 GND 焊盘，HSE 不起振 MCU 不起机；r2 无 PCB 属潜在 P0，**PCB 布局前必须库级重编号（1→左下、2→右下、3→右上、4→左上）或实物 corner cut 裁决**
  - P1：① r2 内嵌符号 4 类空引脚名与库不一致（r4 已库级修复，如实记录）② JP1/R55 符号叠放（r3 已挪）③ **L2 封装 `FILTER-..._ACT1210` pad2/4 与 TDK 引脚 4/2 互换**（TDK p3：1 左上/4 右上/2 左下/3 右下、绕组 1-4/2-3；贴 L2 时 CANH↔CANL 经绕组 ~0.7Ω 短接，DNP 首版无碍，贴前库级修）④ **SW1（XKB TS-1187A）90°/270° 贴装约束**：内部两极=上对/下对（电路图 A—B/C—D 证实），设计 0°/180° 正确，90° 旋转时每极各桥 KEY 与 GND=按键恒按下，PCB 阶段须专项防旋转（封装尺寸与手册 PCB layout 一致，无问题）
  - P2：规格书 §3.3「±40V」与 TI SLOS346K p6 不符（DC −4~+16V、瞬态 ±25V@100Ω、HBM 16kV）；J7 符号名 XH2.54 与实测 2.50mm 不符；绿灯 330Ω 0.6–2.1mA 算式留档（用户已定）
  - 确认正确：U6 48 脚逐脚、U7 D 脚低有效（R53 上拉=复位隐性，P1 候选作废）、U8 钳位、R54=0Ω 高速模式、33pF 算式 18.5–23.5pF 跨 CL20pF、LED×3 极性、BOM MCU 段 34 行 LCSC 号、ERC 5 条警告全预期（I2C/AFE 对端在 02 页未画）
- 05 第二复核 qwen 的 P0（Y1 封装 180° 错位）与 P1（L2 pad2/4 互换）经主代理按焊盘坐标核对**均不成立**：qwen 把 KiCad 封装坐标 y>0 当成「上」（KiCad y 轴向下）；裁决 design/05_mcu_comm-review-qwen-adjudication.md；复核任务书已加坐标约定
- 🔴 用户 2026-09-27 16:3x JST 决定（02 规格书）：**01 页功率管改手册共漏拓扑**（CHG 电池侧、DSG PACK 侧、FET_MID=漏极公共点）；VTOP/REGIN 从 BAT+ 取（02 页契约加 BAT+）；电芯 NTC 改线束探头（非嘉立创件，BOM 删 RT1/RT2，RT3/RT4 在 01 页）；其余推荐全采纳（C_NTC DNP、J5 针脚 1 NTC1/2 GND/3 NTC2/4 GND/5–13 CELL0–8、基础库改料、2xx 位号、不做 PACK 反接保护、不做 MTP、01 页 PACK+ 加 47µF/63V 电解 C48971005）
- 02_afe 分段 A 完成（2026-09-27 17:10 JST，DeepSeek 画）：U1 48 脚 + §9 电源（R212/C212/R213/C213/Q201/C214/C215/C216/C217/C218）+ §6 高边驱动（R214/C219/C220/R215/C221 + DNP 备位）共 17 个位号；`check_02_layout.py` 检查 1–9 全 PASS（含 79 项网表逐脚核对）、ERC 剩 18 条 `isolated_pin_label`（全是等 B/C 段接件的立柱标签，逐条列在 `design/02_afe-draw-report.md`）；U1 用 `(mirror y)`（电芯脚朝左）；**规格书 §6 的位号 `C219B` 非法（尾随字母 → 根图导网表报 annotation errors），已改 `C226`，`docs/02-BOM.csv` 待主代理同步**
- 02_afe 分段 B 完成（2026-09-27 17:15 JST，DeepSeek 画）：新增 24 个位号——J5（XH-13A 13P，1 NTC_CELL1/2 GND/3 NTC_CELL2/4 GND/5–13 CELL0–CELL8）、R201–R209（33Ω `CELLn`→`VCn`）、C201–C208（100nF `VCn`↔`VCn+1`，**8 只**）、D201（3V3 稳压，阴极→`VC0`）、R210/R211（100Ω → `SRP_F`/`SRN_F`）、C209（差模）+C210/C211（共模）；本页共 41 实例/140 引脚；9 项自检全 PASS（140 项网表逐脚核对），**ERC 从 18 条降到 8 条**（Errors 0，全是等 01 页/C 段的 `isolated_pin_label`：NTC_FET/NTC_SHUNT/SRP/SRN/FET_MID/PACK+/DSG_G/CHG_G），测试 21/21 与 38/38 通过，产物 md5 `d92a9e7589aff4462ca441d922095520`（幂等）
  - **教训（写进检查方法的坑）**：`check_02_layout.py` 的检查 8d 有 −0.15mm 容差，且**完全不检查文字与文字的互压**——本段 §4 第三条说明文字的渲染墨迹（止于 y=64.0）与第 0 行字段文字（y 63.9–65.8）**重叠 0.1mm 却不报**，是**肉眼审渲染 PDF 才发现的**，整块文字上移 1.27mm 解决。结论：**几何自检过了仍要看渲染图**，相邻文字的行距要按「墨迹高 ≈2.1–2.9mm」而不是「字段盒高 1.27mm」留量；已在生成器源码里写下推导注释
  - **订正**：库符号 D201 的 `C`/`A` 是**引脚名**，**引脚号是 1/2**（阴极 `C` = 脚 1 在左）；A 段报告 §5.1 原来的「1=K 2=A」说法错误，已订正，`PART_EXPECT` 按引脚号写 `{"1":"VC0","2":"GND"}`
  - **负例验证**：9g（无 `BAL*` 网络，spec §4.4）、9c 新件、9c D201 极性三项都造负例确认会报错（新检查不做负例可能是空跑）
  - 留给 C 段：R216–R219（10k，NTC 上拉 `NTCB`）、C222–C225（1nF DNP，**记得加进 9d 的 DNP 清单**）、R220/R221（2.2k I2C 上拉）、R222（100k `AFE_ALERT` 下拉，**必须沿用 A 段的 `output` 形状否则 ERC 报 pin_to_pin**）、R223（10k `AFE_WAKE` 上拉）；`docs/02-BOM.csv` 的 `C219B`→`C226` 一格仍待主代理同步
- ✅ 02_afe 完成（2026-09-27 18:1x JST，Opus 复核 r2 P0=P1=0，P2=13 待用户定）：DeepSeek-flash 分 A/B/C 三段各 ≤30 分钟画完 + 第 2 轮字段/版面；53 器件 164 脚；快照 review/02-r2；网络类 */VC? 拆成 VC0–VC8（避免 VCP 误入 CELL_SENSE）
  - 固件必做：CELL_S_CTRL=0x7 后 CELL_DEAD_DET_CLEAR（出厂按 16 节，首次上电 C9–C16 读 0V 会锁坏电芯标志）；单节 ≥2.5V（VTOP UVLO 14.6–17V，共漏关断后整包无法补电）
- 2026-09-27 18:56 JST 用户：先画 03 均衡页（01 功率页放最后）→ Opus 写 design/03_balancer-spec.md
- 🔴 用户 2026-09-27 03 页决定：U-1~U-4 四项都改（死区网络、只接 100k 下拉、首级电容耦合 VB0 不接 GND、每节 100µF 本地储能）；均衡电流口径 0.16A@100mV；**线束电芯端保险丝暂不加**（已知风险：线束磨破短路无保护）；BAL 保险丝保持 C163126；接受低压分断工程判断
- 02 第二复核（qwen3.8-27b，审 r1，2026-09-27 19:16 JST 收稿）：P0=0、P1=1（CVCP 100nF vs 栅荷等效 144nF 矛盾，需样板实测）——已被用户决定 U-7（C226 100nF DNP 预留）覆盖，按样板实测项处理；P2=14 多与 Opus 重合
- ✅ 03_balancer 完成（2026-09-28 12:15 JST，Opus 复核 r2 P0=P1=0，P2=3）：DeepSeek-flash 分段 A/B/C + 第 2 轮换料；113 器件、60 网络；快照 review/03-r2
  - 330k 方案（R301 100k、R302–R308 330k）的时序余量依赖固件门限「≥3.0V 才均衡、压差 ≤300mV」；固件还需实现「停时钟停低（OIS1=0）」与 IWDG；死区绝对值样板实测，重叠则 330Ω→470Ω（C25117）
- 03 第二复核 qwen P1-A（74LVC 快关峰值 70–140mA 超手册 ±50mA）经 Opus 裁决降为 P2：±50mA 是 DC 额定，纳秒级容性峰值属正常，平均 0.9mA/有效值 5.6mA；串电阻会吃掉死区反而更差；P2-9「TI 1G17 是反相器」驳回（1G17 缓冲、1G14 反相）→ 03 页维持完成
