colemandlut/MP2645A-BMS/obsidian-vault/BMS/LFP 均衡要点.md

---
tags: [LFP, 均衡]
---
# LFP 均衡要点

- LFP OCV 平台 3.28~3.33V 很平，平台区电压差 ≠ SOC 差 → 不要在平台区按电压均衡
- 主策略：顶部均衡（最高节 ≥3.40V 且压差 ≥30mV 启动，≤10mV 停止）
- 静置 30min 后压差 ≥80mV 可均衡，有电流立即退出
- 主动均衡线与采样线要分开，否则 A 级均衡电流造成采样误差
- 0°C 以下禁止充电（析锂）
- 大容量电芯靠主动均衡更快：120Ah 5% 偏差（6Ah）开关电容 @100mV≈0.21A 约 30h，50mA 被动约 120h

## 开关电容均衡（方案 B）画图前核定（2026-09-27 19:1x JST，Opus 规格书 design/03_balancer-spec.md）
- N/P 共栅直驱会直通：栅负载约 **1.4nF**（Ciss 660+750pF；旧稿「约 3.2nF」是 Qg/V 假象 10.5nC/3.2V，2026-09-28 review2 更正）、74LVC 输出内阻 16–29Ω → 边沿 50–90ns（不是 50pF 下的 3ns），直通峰值约 10A、每节 0.1–0.2W 且各节不等 → 需死区（330Ω×2 + 1N5819WS×2 慢开快关，r2 换 BAT54WS）
- 「停时钟后偏置中点 + 施密特迟滞保持」不成立：VCC=3.0V 时 VT+ 最小 1.48V < 中点 1.50V，输入漏电 ±1µA×500k=±0.5V → 可能停在「k 高 k+1 低」，飞电容长期跨两节 6–7.3V > 6.3V 额定 → 改为只接 100k 下拉 + LVC 输入钳位恢复直流，停时钟/复位都收敛到全低
- 首级不能以 GND=V0 直连（BAL0 线束会与 BAT− 主回路并联分流）→ 首级也交流耦合
- 每节需本地储能 100µF（线束 0.7µH 与 100nF 谐振 ±1V）
- 含线束电阻后 100mV 压差典型 0.16A（60°C 0.14A，最坏 0.12A），非 0.19A
- 板上 BAL 保险丝保护不了线束 → 线束电芯端另加保险丝
- 网络类 `/03_balancer/X*` 匹配不上：网表路径用图纸名「开关电容主动均衡」

## 开关电容均衡（方案 B）画图进度（2026-09-28 11:4x JST，**第 1 轮完成**：分段 A+B+C）
- 03 页已画 **113 件 / 274 脚 / 289 段导线 / 46 个 junction**：8 节（每节 11 件，k=1..4 左栏、k=5..8 右栏）+ 7 级飞电容（C33j∥C34j，100µF）+ J6 线束端子 + F300–F308（3A，`CFS12V3T3R0`/C163126，未做 0603 降规）+ 首级 R300 1k/C321 1nF
- 接法：J6 焊盘 n → `BAL(n−1)`，**焊盘 10 空放 NC**；F30k 脚 1 → `BALk`、脚 2 → `VBk`；U301–U308 脚 1 全 NC
- 右栏整体上移 26.67mm（否则第 5 节最低的下管 D 字段压到右下角标题栏）；本页**无 GND、无电源符号**（VB0 不接地，首级改交流耦合）
- 自检 13 项全 PASS（逐脚 274/274、Footprint/LCSC 113/113）、生成器幂等；**ERC 本页 0 条**（全工程剩 6 条 `isolated_pin_label` 都在 01/02 页，与本页无关）
- 已知偏差（电气等价，已记报告）：F300–F308 与 `VBk` 不同高（两栏行距不同，9 只排不齐）；第 4–5 级飞电容 C334/C344 放右栏最下
- C 段补齐：标题「（8 级半桥 + 飞电容，75kHz）」+ 6 行说明（内容/全级交流耦合含首级 VB0 不接地/死区慢开快关/停时钟收敛全低/接口网络清单/已知风险）；删掉临时提示文字。文件 md5 `9caa8c53fcb304c45472574c5d2f5c59`，连跑两次不变（幂等）
- C 段把「自检 13 项」扩到 **18 项**（新增 9j/9l/9m/9n/9o），每项都做过负例实测（确认非空跑）：**9j 网络→脚集合**（与 9c 反方向，R/C/F 二端件按规格书放行对调）；**9l 本页网络全集=60 且无 GND/电源/CELL\***；**9m 网络类**（`Xk`/`VBk`/`BALk` ∈ `BAL_3A`、`BAL_CLK` 不被卷入、无网络落进 `CELL_SENSE`，并拦 `BAL*` 这种会吞时钟的通配符）；**9n ERC 按 `sheets[].path` 取本页**；**9o 8 节同构**（角色归一化后逐字段比 + 跨节只许相邻 + 全局标签全集）
- 网络类那条**已在网表上证实**：pattern 必须写图纸名路径 `/开关电容主动均衡/X?`（写文件名 `/03_balancer/X?` 会 8 条全不命中）→ 改图纸名会静默退掉 3A 线宽，改了就重跑 9m
- 8 节同构实测：第 2–8 节归一化结构完全一致，第 1 节只差 `C321.1 = CLK_R`（其余 `C32k.1 = DRV(k−1)`）；`DRV1–7` 各 6 脚、`DRV8` 5 脚（无 C329）
- 第 1 轮收尾状态：18 项自检全 PASS、**ERC 本页 0 条**（全工程 6 条 `isolated_pin_label` 都在根图页）、`BAL0–8` 各 2 节点（J6 + F30k，本页内闭环）、`BAL_CLK` 3 节点（本页 R300.1 + 05 页 2）→ **本页不存在跨页单脚网络**；测试 22/22 + firmware 38/38
- 仍缺：**规则 00c 的独立复核（换厂商模型）没做**；F300–F308 的 0603 降规（C163117，U-7）用户未定，维持 1206
- 03 Opus 复核 r1（2026-09-28）：死区二极管要看**结电容**（1N5819WS 约 110pF 与栅电容分压会把待开通管抬过阈值）→ BAT54WS ≤10pF；各级输入下拉 RC 不同步衰减会混相 → 首级 100k、其余 330k 让首级先翻并同步带低（用户 2026-09-28 同意换料）

## 开关电容均衡（方案 B）**第 2 轮换料完成**（2026-09-28 12:0x JST，03 页）
- P1-1：D301–D308、D311–D318 由 `1N5819WS`/C191023 换为 **`BAT54WS`（`jlc:BAT54WSL9`，C22629）**，SOD-323 封装不变；库符号引脚坐标与旧符号**完全相同**（`1`=(-5.08,0)/`2`=(5.08,0)）→ 未动一根导线；K/A 方向按图形复核（顶点＝脚 1＝阴极，与旧符号同一画法），未变
- P1-2：R302–R308 100k/C25741 → **330k/C25778**（`0402WGF3303TCE`）；**R301 保持 100k**（首级先泄放，避免混相）
- P2-4：C30k 位号挪开不再压字；Q311–Q318 字段角度 `fa=0` 修好倒置（根因见 `KiCad 原理图自检要点`）；标题栏改 `v0.3-draw-r2` / `2026-09-28`
- 验收：生成器幂等 md5 `8e57b0ecc86f58e3d9b49bf7c53b8c1a`（第 1 轮 `9caa8c53fcb304c45472574c5d2f5c59`）；自检全 PASS（新增 **9p 值/符号/LCSC 24 件**、**9q 二极管 K/A 16 只**，两者都做过负例实测）；**ERC 本页 0 条**；与第 1 轮网表 **连接差异 0**，只有 23 件的值/LCSC/符号变化（D 16 只 + R 7 只）
- 报告：`design/03_balancer-draw-report.md` §9（第 2 轮变更）

## 03 页独立复核 review2（qwen3.8-27b，2026-09-28 12:3x JST，对象 = r1 快照 `9caa8c53`）
- 报告：`design/03_balancer-review-qwen.md`（独立重推，未读画图方/第一复核报告）；**P0=0；P1=3（B/C 为 r1 缺陷、r2 已修且本复核独立核实；A 开放）；P2=10**
- **器件身份（重要）**：UMW/UTD `SN74LVC1G17DBVR`（C7394021）是**非反相施密特缓冲器**（手册 p1 标题 "Non-inverting Schmitt Trigger Buffer"/引脚图 + p3 功能表 L→L、H→H），借用 TI 反相器 1G17 料号；TI 原装是反相器且引脚不同（TI 1=GND/2=CEXT/3=A/4=Y/5=VCC，UMW 1=NC/2=INA/3=GND/4=OUTY/5=VCC）→ **BOM/规格书应加注「勿代换 TI 原装 1G17」**（拓扑依赖同相：若反相则各级交替 N/P，CF1/3/5/7 常态跨两节 6.6–7.3V）。所购 C7394021 = 缓冲器 = 设计正确
- P1-A（**开放**，r2 未覆盖）：U30x 栅驱峰流 ≈(Vcell−0.7−Vf)/ro ≈ 85mA/边沿（ro≈24Ω 为 TI 同族估计，UMW 手册**未列 ro**），×75kHz×2 边沿×8 级 → 超 UMW abs max **IO ±50mA（p4）**（Features 保证 24mA@3.0V p1；JLC API/BOM 写 32mA，规格源不一致备注）→ 端点电压由二极管钳位、与 ro 无关，功能不受影响，但 75kHz 永久工作下长期超 abs max = 可靠性风险 → 样机实测/UMW 书面确认；备选 DRVk 串 10–33Ω
- P1-B（r2 已修 ✓）：1N5819WS Cj 110pF 馈通按正确模型重推（电容分压 + 缓冲器方向）：P 栅 −0.42V → Vgs_P≈−1.4V 仍关断（比 |Vth|max 0.9V 低 0.5V）、N 栅 +0.47V 发生在预期换相处（10–30mA、µW 级）→ 后果比「死区失效」框定轻（边沿提前 ~10–30ns）；BAT54WS（CT≤10pF）降一个量级 → 有效改进
- P1-C（r2 已修 ✓，机制独立重推成立）：r1 全 100k 时停钟/掉电各级独立衰减 t_k≈100µs·ln(Vk/VT−k)，ΔV≲100mV 剖面相邻级可能逆序翻转（窗口典型 1–3µs、最坏角 ~30µs）→ (k=N 通, k+1=P 通) CF 跨两节 6.6–7.3V，τ_CF≈(Rds_N+Rds_P+ESR)×**200µF（C33k∥C34k）**≈18–30µs → 最坏角 CF 峰值 ~6.0–6.5V（**边际**超 6.3V 额定，每掉电一次；典型角 0.4–1.1V 不超——比早期 τ=9µs「超压 0.1–1.0V」口径更正）；r2：R301=100k 首级 t1≈101–131µs 恒先翻（其余级 ≥415µs）→ DRV1 下降沿经 C322 拉低 IN2（t1 时 IN2 自由衰减仅 ~0.72–0.74·Vcell，拉低量 ~0.9975·Vcell）→ U302 输入钳位 → ~5ns/级级联带翻 2–8 级 → 残留 ~0.3µs → CF 过压 ≈24mV
- 死区机制正确表述（网表 D 引脚方向核完 8/8）：D30k K=DRVk/A=GNk → **N 慢开**（R31k 充，τ≈0.22–0.25µs）**快关**（D30k 放，~40ns 过 Vth max）；D31k K=GPk/A=DRVk → **P 慢开**（R32k，τ≈0.28µs）**快关**（D31k 钳，跟上升沿 ~5ns）；DRV 下降沿重叠 ~30–350ns，Thevenin 峰值 10–20A 被电芯 ESR（10–30mΩ）+ 线束 0.7µH 限到数 A → ~10–80mW/级（P2-1，SPICE/样机；AO3416 abs max 6A 在边界）
- 其他 P2：N 关断地板 VOL+Vf≈0.75–0.9V（r1）/0.54–0.8V（r2）vs Vth max 1.0V 最坏角关断、典型角贴边 ~50mV（µA）；P 关断端点 Vgs_P≈−(0.7+Vf)≈−0.94…−1.15V vs |Vth| max 0.9V，BAT54WS 低 Vf 角（0.24V）贴导通边界（µA–mA，仿真）；BAT54WSL9 单管符号已核实单 die（K=pin1，JLC API "Independent…Diodes" 系分类套话）；J6 连欣手册 6A/针 vs JLC 5A（均被 3A 保险丝覆盖）；保险丝 I²t「40–73A 约 1ms」**未核**（手册已读页无 I²t 表）；固件门控（X-5 TODO 未落地）：无门控且相邻 ΔV≳1.1–1.2V 时该级停摆（CF≤1 节，非破坏，均衡降级）
- **r2 验收（独立重跑 Kicad CLI 10.0.6）**：网表 175/175、本页子集 69/69，**名/连接/网络类 0 差异**；符号 diff = 恰好 23 件（16 D→BAT54WS C22629 + 7 R→330k C25778，R301 不动，113/113）；ERC 本页 0 条；冻结 `review/03-r2` = 工作树 md5 `8e57b0ec` ✓
- 口径澄清：C30k=100nF/**16V**/0402（C1525，U30x 去耦）≠ C31k=100µF/**6.3V**/1206（C15008，每节本地储能）≠ C33k∥C34k=2×100µF/6.3V（C15008，飞电容 7 级）；停钟/MCU 复位/时钟卡任意电平的 DC 终态 = 全 IN/DRV 低 → **全 P 通**（N 全关，地板 < Vth max）→ CFk=Vcell_{k+1}≤3.65V ✓
