colemandlut/MP2645A-BMS/obsidian-vault/偏好/用户偏好.md

---
tags: [偏好]
updated: 2026-09-26
---
# 用户偏好

- 必须使用汉语回复
- 每条回复前加时间戳；🔴 2026-09-27 起**一律用 JST（日本时间）显示**：`TZ=Asia/Tokyo date '+%F %T %Z'` 实查，不估算
- 测试跑完要通知
- 用 Obsidian 作为永久记忆知识库，每次回复前先检索本知识库（本目录 `obsidian-vault/`）

## PCB 工作流
- 🔴 2026-09-26 用户规定：**不再使用嘉立创EDA专业版，所有 EDA 工作一律用 KiCad**（嘉立创仍作为板厂/贴片厂）
- 用户有自定义技能 `pcb-workflow`，任何原理图定稿/PCB/导出制造文件任务前必须加载并严格遵守；2026-09-26 按用户指令就地改写云主机上的 skill 为纯 KiCad 版（原版备份在会话 scratchpad，不进仓库）
- 要点：画图 gpt-6-astra(codex) / 复核 Opus 5（不同厂商）；每次导出跑五维并行审查（闸口 A/B）；四层板 顶信号/内1 GND/内2 电源/底信号；泪滴强制；电感下方全层禁铜
- 云端容器：KiCad 10.0.6 用 `sudo bash tools/setup_kicad.sh` 安装（Docker Hub 官方镜像解包 + chroot；PPA 与 downloads.kicad.org 被网络策略拦截），命令 `kicad-cli` / `kicad-python` / `freerouting`（Maven Central + OpenJDK 25）；容器重建后需重跑；实测 DSN→Freerouting→SES→DRC 全链路可用
- 云端容器无 codex（gpt-6-astra），画图/复核跨厂商分工需在用户本机执行

## 选料
- 🔴 2026-09-26 用户规定：**所有元器件都去立创商城查**（料号 C 编号、参数、库存、价格）
- 云端环境 lcsc.com / szlcsc.com / jlcpcb.com 直连被拦截，只能用 WebSearch（域名限定 szlcsc.com/lcsc.com）从搜索结果取信息；嘉立创 SMT 库存需用户本机核实
- 取库/选料号用 Opus（用户 2026-09-22 规定）

## 模型分工（2026-09-26 用户规定）
- 审查、画图等各角色的模型**单独提出来**，不同环境/时期用不同模型，随时可改
- 配置：pcb-workflow 技能目录 `models.toml`（配置档 local-mac / cloud），`scripts/models.py show|use|set`
- 选档优先级：环境变量 PCB_MODEL_PROFILE > ~/.config/pcb-workflow/profile > models.toml active
- ~~cloud 档（2026-09-27 用户批准）：画图 deepseek-v4-pro（备 qwen3-max）、复核 Opus（备 Sonnet）、第二复核 qwen3-max、泳道 Opus(A3/A4/B2)+qwen3-max(其余)、取库 Opus、跑工具 Haiku（备 deepseek-flash）；第三方模型经 tools/llm_agent.sh 带工具运行，合格测试 tools/llm_agent_selftest.sh（qwen3-coder-plus 2/3 不合格）~~（**已废止**：2026-09-27 13:07 JST 起 deepseek-v4-pro 禁用，一律 deepseek-flash）

## 器件与封装（2026-09-26 用户规定）
- 器件都用嘉立创的；**封装形状从嘉立创取得**（easyeda2kicad 按 C 编号），不用 KiCad 官方库顶替（官方库只作对照）
- 项目脚本 `tools/fetch_jlc_parts.py`；云端 easyeda.com 被网络策略拦截，需用户在环境网络设置放行

## 云端画图模型（2026-09-26）
- 用户：云端画图用 **DeepSeek 官方 API**（环境变量 DEEPSEEK_API_KEY，不要打印/记录密钥），经 codex CLI 调用；复核仍 Opus（不同厂商）

## 云端画图链路（2026-09-26 第 2 个会话实测打通）
- ~~DeepSeek 官方 API 实有模型：`deepseek-v4-pro`（DeepSeek-V4-Pro，画图用）、`deepseek-flash`（V4.1-Flash）~~（**已废止**：2026-09-27 13:07 JST 起 deepseek-v4-pro 禁用，一律 deepseek-flash）
- codex-cli 0.157：`~/.codex/config.toml` 只放 `[model_providers.deepseek]`（base_url https://api.deepseek.com，env_key DEEPSEEK_API_KEY，**wire_api = "responses"**——"chat" 已不再支持）；配置档必须放单独文件 `~/.codex/deepseek.config.toml`（model_provider/model/model_reasoning_effort），不能写 `[profiles.deepseek]` 表
- ~~`models.toml` cloud 档：draw = deepseek-v4-pro（codex，`-s workspace-write`），review/lanes/parts = opus，tool = haiku；`models.py use cloud` 校验通过~~（**已废止**：2026-09-27 13:07 JST 起 deepseek-v4-pro 禁用，一律 deepseek-flash）
- ⚠ codex 的 workspace-write 沙箱里 **kicad-cli 跑不了**（chroot 被拦，Operation not permitted）；完全访问模式被自动权限分类器拒绝 → 画图方只写脚本/生成图，**ERC、网表由主代理跑**再回灌下一轮任务书
- 🔴 2026-09-26 12:20 用户：「deepseek 你可以使用 claude 去跑」→ 画图方改为 **Claude Code CLI + DeepSeek Anthropic 兼容接口**（`https://api.deepseek.com/anthropic`）：包装脚本 `tools/deepseek_claude.sh <任务书> <输出>`（`env -i` 干净环境、独立 HOME、ANTHROPIC_API_KEY 取自 DEEPSEEK_API_KEY、`-p --permission-mode acceptEdits` + 限定工具白名单）；实测能写文件、能直接跑 kicad-cli。models.toml cloud.draw：launcher=claude，cmd=`tools/deepseek_claude.sh {task} {out}`
- 注意：宿主会话的 CLAUDE_CODE_* 认证变量会让子 claude 报 Authentication error，必须 `env -i` 清掉
- ⚠ 2026-09-26 教训（规则 00b⑤ 再犯）：用 `until ! pgrep -f "claude -p --model deepseek"` 等画图代理，pgrep 匹配到了等待循环自己的命令行 → 两个僵尸循环空转 1 小时+，用户看到后才清理。以后等后台代理只用 `run_in_background` 的完成通知，或记 PID 用 `kill -0 $PID`

## 第三方大模型密钥（2026-09-27）
- DeepSeek：环境变量 DEEPSEEK_API_KEY（已设置；实测可用模型 deepseek-flash、deepseek-v4-pro）
- 阿里云百炼（通义千问）：用户已在云端环境加 **DASHSCOPE_API_KEY**（及 Anthropic 兼容端点地址）；2026-09-27 09:53 JST 新会话实测 **qwen3-max 对话成功**，models 列表接口 404（需手动指定模型名）。环境变量只对新会话生效；**密钥不得贴进对话或仓库**
- 调用：`python3 tools/llm.py providers|models <deepseek|aliyun>|chat <提供方> <模型> <任务文件>`
- 2026-09-27 11:10 JST：**DeepSeek 账户余额不足（HTTP 402）**，05 页第 1 轮因此中断；画图按 fallback 改 qwen3-max，第二复核暂停；阿里云地址为 Anthropic 兼容端点（DASHSCOPE_BASE_URL）。充值后恢复 deepseek-v4-pro
- 🔴 2026-09-27 用户规定：回复时间戳用 **JST**（`TZ=Asia/Tokyo date` 实查）
- 2026-09-27 画图会话：DeepSeek 402 余额不足后用户答复「我去充值 DeepSeek」→ 画图暂停等充值（fallback qwen3-max 已配但未启用）；期间只做复核/取库等不需画图方的工作
- 2026-09-27 11:13 JST 实测 DeepSeek 已恢复（deepseek-v4-pro / flash 均 HTTP 200）→ 画图继续用 DeepSeek，不启用 qwen3-max 回退；第三方模型统一用 tools/llm_agent.sh 启动
- 🔴 2026-09-27 用户规定：**模型有新版本就用新版本，不用旧版本**。11:39 JST 重排：画图 deepseek-v4-pro（备 qwen3.8-max、qwen3-coder-next）、复核 Opus 5.5（备 Sonnet 5）、第二复核 qwen3.8-max（备 qwen3.8-flash）、泳道 Opus 5.5(A3/A4/B2)+qwen3.8-max、取库 Opus 5.5、跑工具 Haiku 4.5（备 deepseek-flash）；qwen3-max/qwen-plus 停用。新模型先跑 tools/llm_agent_selftest.sh（其中画图 deepseek-v4-pro 已于 13:07 JST 改为 deepseek-flash、qwen3.8-max 已于 13:10 JST 改为 qwen3.8-27b；「用新版本」这条规则本身继续有效）
- 2026-09-27 11:40 JST：阿里云 DashScope 对 qwen3-max / qwen-plus 均返回 403 AccessDenied.Unpurchased（模型未开通/未购买）（这两个已按用户规定停用）→ 第二复核改用 qwen3.8-max；11:43 JST 复测 qwen3.8-max 已 200（用户确认可跑）
- 🔴 2026-09-27 13:07 JST 用户规定：**原来用 deepseek-v4-pro 的地方一律换成 deepseek-flash**（画图主力 deepseek-flash；合格测试 3/3、17s）；起因是 v4-pro 在 05 页第 2 轮跑满 1 小时超时
- 🔴 2026-09-27 13:10 JST 用户规定：**原来用 qwen3.8-max 的地方全部换成 qwen3.8-27b**（第二复核、轻泳道、画图回退）；qwen3.8-27b 合格测试 3/3、52s（qwen3.8-max 170s，且复核 05 页超时）
- 🔴 2026-09-27 13:07 JST 用户：所有 deepseek-v4-pro 一律换 deepseek-flash；任务大时拆成小任务书、每次限时 30 分钟（画图会话 13:11 停掉 v4-pro 的 05 第 3 轮，改 flash 重跑）
- 🔴 2026-09-27 13:10 JST 用户：qwen3.8-max 全部换 qwen3.8-27b（第二复核、轻泳道、画图回退）；05 第二复核 qwen3.8-max 跑了约 90 分钟的部分稿存为 design/05_mcu_comm-review-qwen38max-partial.md，改 27b 重跑

- 🔴 2026-09-27 16:14 JST 查出**隐蔽调用 v4-pro 的途径**：DeepSeek 的 Anthropic 兼容接口把 `claude-opus-*` 模型名自动映射成 deepseek-v4-pro（sonnet/haiku 映射成 flash）。claude CLI 内部或子代理若请求 opus 名就会偷偷用 v4-pro。已在 tools/llm_agent.sh、tools/deepseek_claude.sh 钉死 ANTHROPIC_DEFAULT_OPUS_MODEL / SONNET / CLAUDE_CODE_SUBAGENT_MODEL = 所选模型，并拒绝 deepseek-v4-pro。**DeepSeek-V4.1-Flash 的 API 名就是 `deepseek-flash`**（接口只认 deepseek-flash、deepseek-v4-pro 两个名字）- 2026-09-27 16:13 JST 主会话查明：DeepSeek Anthropic 兼容接口把 claude-opus-* 名自动映射成 deepseek-v4-pro（sonnet/haiku→flash）；llm_agent.sh/deepseek_claude.sh 已钉死 ANTHROPIC_DEFAULT_OPUS_MODEL/SONNET/CLAUDE_CODE_SUBAGENT_MODEL 并拒绝 v4-pro → 只用这两个脚本启动 DeepSeek
