colemandlut/MP2645A-BMS/obsidian-vault/BMS/降本排查要点.md

---
tags: [BMS, 选料, 降本]
updated: 2026-09-26
---
# 降本排查要点（2026-09-26，详见 docs/06-降本排查.md）

- 基于 v0.3 方案 B（开关电容均衡）BOM；MP2643 相关料已作废，不再评估。
- 推荐项合计：10 块档每块省约 ¥15.0，100 块档约 ¥10.3；扩展库 25→23 种。
  - RS1 → 业展 ASR-S-7-0.1F（C6075508，5930 封装，需换封装）
  - QP → AO3415A（C5350990，36mΩ@2.5V），Q17/18 → SS8550（C8542，基础库），Y1 → 12MHz C9002（基础库，需改 PLL）
  - J5 → ZX-XH2.54-13PZZ（C22366169，封装实测 2.50mm，顺带修复 C158025 的 2.54 错误）；J7 → C7429634；J6 → XDWF-C3030WV-2*5P（C18202166，针号为之字形）
  - D4/D5 → 1N5819WS（C191023，基础库），C_LDO → C52923（0402）
- 教训：开关电容均衡回路每相经过 2 只 BAL 保险丝，保险丝冷阻必须当作选型约束（≤25mΩ）。48mΩ 的便宜 1206 保险丝会让均衡电流降 25–30%。
- MP2797 手册 Table 18：CVCP 47nF（额定电压按 80V×N/16 折算）、CVMID 需 100V、REGIN 需外置 NPN（FZT853TA）和 3.3µF；RSENSE 推荐 0.2–5mΩ。当前 BOM 与这些要求不一致，待设计方确认。
- 查料技巧：jlc_api 请求体加 `componentLibraryType:"base"` 可以只搜基础库；候选封装用 easyeda2kicad 取到 scratchpad 再跑 fp_compare，不会污染工程库。

## 第二轮（2026-09-26 12:40，电源、CAN、MP2797 补全）
- D6 SMBJ33A C78419 的嘉立创库存只有 47，必须换：晶导微 C353366（库存 7.7 万）。也可以考虑直接删掉 D6，因为 BAT+ 上已有 D3。
- C_IN_E 原 Panasonic 50V 低于 53V 浪涌，改 63V 的 C48971005（¥0.39）。C_IN1 改 2×C13832，少一种扩展库。C_OUT1 改基础库 C59461（22µF 6.3V 0603）。
- LMR16006 的 Tokmas 兼容件 C54823941：引脚相同、绝对最大 65V，但 Iq 80µA（TI 28µA）、600kHz，列为可选。其他 60V buck 都因 Iq 太大或更贵被否。
- SN65HVD230：R_RS=10k 接地是斜率控制模式，不是高速模式。HGSEMI 兼容件 C55259679 列为可选。
- MP2797 按 Table 18 补全：新增约 20 颗，10 块档 +¥2.55/块，100 块档 +¥1.05/块，扩展库净 +2 种（CVTOP 470nF/100V、CPACK 10nF/100V、3.3V 稳压管）。CVCP 用 47nF/50V 基础库 C1622，CVMID 用 100nF/100V 基础库 C28233，REGIN 的 NPN 用 MMBT5551 C2145（负载 ≤5mA 时可用）。
- 分流器 0.2mΩ 用 C469442（锰铜，±100ppm，¥2.63）：符合手册 0.2–5mΩ，发热 8W@200A；硬件 OCD 400A 正好落在 RNG0 满量程上，要改用 RNG1；单侧 MOS 导通时限流只有 87.5A。
- 全部采纳后总账：推荐 + 补全，10 块档 ≈ ¥185，100 块档 ≈ ¥143；再加上所有可选项 ≈ ¥167 / ¥131。
- MP2797 的 VTOP 下限 18V，8S LFP 的欠压阈值要留裕量。

## PCB 与贴片费（2026-09-26）
- `tools/pcb_quote.py` 重放 JLCPCB 报价页接口 `calculationGoodsCostsNew` 取裸板实时价（模板 `tools/jlc_pcb_quote_template.json`）
- 4 层 160×110 外 2oz：10 块 $91.6、100 块 $371.7；外层 1oz 约减半；130×90 省约 28%（100 块）
- BOM 焊点：贴片 662/板、插件 27/板；PCBA 10 块约 ¥21–38/块、100 块约 ¥12–14/块
- 每块电路板合计（不含机械件）：10 块 ≈ ¥252–269，100 块 ≈ ¥169–171
- 最大杠杆：主电流全走铜排 → 外层 1oz（10 块档 −¥32/块）；缩板

## 扩展库合并排查（2026-09-26 15:18，详见 docs/07-扩展库合并.md）
- 嘉立创基础库全表只有 351 种（接口参数 `componentLibraryType:"base"` 可翻完）：没有稳压管、没有 ≥100V 的 10nF/470nF/1µF、没有保险丝、NTC、功率电感、铝电解、单门施密特、CAN ESD → 按基础库口径，本 BOM 的扩展库**一种都换不掉**。
- 基础库的 AO3400A/AO3401A 单价反而比 AO3416/AO3415A 贵，差价盖过上料费；AO3401A 还会让均衡电流 −17% → 不换。
- 优选扩展库（Preferred Extended，1235 种，接口参数 `preferredComponentFlag:true`）：JLCPCB FAQ 写明「经济型贴片免上料费」，标准型没说。若订单类型确实免，推荐换 DZ→BZT52C16S C19077449（手册推荐 16V）、D_C0→C19077396、U8→H24VNT2B C20615827（同脚位，7A/36pF），扩展库 −3 种，10 块档每块省 ¥2.2。**要先在下单页确认上料费是否为 0。**
- C_VTOP 470nF 和 C_PACK 10nF 在手册里都是 Required（后者不得增减），不能并入 1µF；F11 不能并入 F2–F10（32V 不够；统一改成 3A 会让 R42 先烧）。

## 铜排与外层铜厚（2026-09-27 答用户问）
- 铜排 = BOM 里的机械件「BUS 20×2mm 紫铜排 + M8 螺柱」，板厂不做、SMT 也不贴，是贴片后手工装（螺丝压接或焊接）
- 200A 纯靠 PCB 铜（IPC-2221 外层、温升 30℃）：1oz 需约 230mm 宽，2oz 约 115mm；多层并联也要几十 mm，160×110 板只能靠厚铜 + 开窗堆锡或焊铜条
- 「外层 1oz 省 ¥32/块」不是净省：要扣掉铜排/铜条与手工后焊的成本；布局时再定，暂保持 2oz
- 可 SMT 的替代：贴片式功率端子/焊接螺母（如 REDCUBE 类），需查嘉立创是否有货
