colemandlut/MP2645A-BMS/design/04_power_supply-task-draw-r6.md

# 画图任务书：子图 04_power_supply，第 6 轮（C42/C44 换符号后修版面）

工作目录 `/home/user/MP2645A-BMS`。纪律同第 1–5 轮任务书；第 3–5 轮的版面要求与全部自检继续有效。

## 背景
用户 2026-09-26 14:46 决定：全板 1µF/100V 1206 改用 **CCTC TCC1206X7R105K101HT，LCSC C282823**（符号 `jlc:TCC1206X7R105K101HT`，封装 `jlc:C1206`）。
主代理已按清单在 `hardware/gen/gen_04_power_supply.py` 第 145–146 行把 C42/C44 的符号名与 LCSC 换掉并重新生成（见脚本头部第 29 行注释）。
网表仍然正确，但**新符号的引脚几何与旧符号 CL31B105KCHNNNE 不同**（规则 00 ⓪：换符号 → 引脚平移、导线留在原地），
`python3 hardware/gen/check_04_layout.py` 现在报：
```
[1] 导线#11 (236.22,109.22)→(261.62,109.22) 穿过 C42.1 引脚端点 (246.38,109.22)（非端点）
[3] 导线#13 端点 (246.38,109.22) 落在导线#11 内部，但无 junction
[3] 引脚 C42.2 (236.22,109.22) 有 2 段导线端点相接（T 型连接），但无 junction
```

## 要求
1. 先读新符号 `TCC1206X7R105K101HT` 在库里的引脚坐标/方向，**按新几何重排 C42/C44 的导线与标签**，不要改其它器件的位置与连接。
   注意脚本里是否有按旧符号硬编码的引脚偏移——改成从符号读取。
2. 全部自检重跑并通过：`check_04_layout.py` 0 条；ERC 只剩 BAT+；网表「位号.脚 → 网络」与现在完全一致（C42/C44 的 LCSC 为 C282823）；文字重叠只允许已记录的 D7 K/A、C45 1/2 两处符号级 quirk；PDF 目视；幂等。
3. 备份若 `/tmp` 不可写，就确认 git HEAD 里有上一版即可（在报告里说明）。

## 交付
更新脚本、原理图、报告（开头加「第 6 轮变更」+ 自检结果）。最后一行回复 `DONE`。
