colemandlut/MP2645A-BMS/docs/05-成本估算.md

# 成本估算（元器件）

> 生成：`python3 tools/cost.py`，2026-09-28 01:38 UTC。嘉立创价为实时接口的美元阶梯价 × 7.1（假设汇率）；MP2643 为 MPS 官网人民币价。
> **不含 PCB 制板、SMT 工程/钢网/焊点费、运费、税**，这些以嘉立创下单页报价为准。

## 每块板成本（元）

| 批量(块) | 嘉立创元器件 | MPS 客供件 | MPS 运费分摊 | 扩展库上料费分摊 | **元器件合计/块** | 客供件占比 |
|---|---|---|---|---|---|---|
| 1 | 169.51 | 0.00 | 0.00 | 208.00（26 种 × ¥8） | **377.51** | 0% |
| 5 | 164.31 | 0.00 | 0.00 | 41.60（26 种 × ¥8） | **205.91** | 0% |
| 10 | 156.20 | 0.00 | 0.00 | 20.80（26 种 × ¥8） | **177.00** | 0% |
| 50 | 140.01 | 0.00 | 0.00 | 4.16（26 种 × ¥8） | **144.17** | 0% |
| 100 | 134.62 | 0.00 | 0.00 | 2.08（26 种 × ¥8） | **136.70** | 0% |

非嘉立创机械件（300A 熔断器、铜排与 M8 螺柱、散热器）粗估 **¥90–200/套**，未计入上表。

## 明细（按 10 块批量取价，单位：元）

| 模块 | 位号 | 数量 | 型号 | 编号 | 库 | 嘉立创库存 | 单价 | 单板小计 |
|---|---|---|---|---|---|---|---|---|
| 功率 | Q1-Q12 | 12 | Tokmas IPT012N08N5(TOKMAS) | C19626224 | 扩展库 | 746 | 5.5344 | 66.41 |
| AFE | U1 | 1 | MPS MP2797DFP-0000-T | C18198873 | 扩展库 | 269 | 29.3258 | 29.33 |
| 均衡 | C331-C337 C341-C347 | 14 | Samsung CL31A107MQHNNNE | C15008 | 基础库 | 2058509 | 0.6440 | 9.02 |
| 均衡 | C311-C318 | 8 | Samsung CL31A107MQHNNNE | C15008 | 基础库 | 2058509 | 0.8896 | 7.12 |
| MCU | U6 | 1 | WCH CH32V203C8T6 | C3001172 | 扩展库 | 10270 | 5.1198 | 5.12 |
| 功率 | RS1 | 1 | 业展 ASR-S-7-0.1F | C6075508 | 扩展库 | 21012 | 4.6235 | 4.62 |
| 功率 | D1 D2 D3 | 3 | DOWO SMDJ33A | C2976503 | 扩展库 | 725 | 1.3007 | 3.90 |
| 均衡 | F300-F308 | 9 | 大毅 TA-I CFS12V3T3R00 | C163126 | 扩展库 | 11220 | 0.2968 | 2.67 |
| MCU | U7 | 1 | HGSEMI SN65HVD230M/TR-HG | C55259679 | 扩展库 | 2435 | 2.6178 | 2.62 |
| 均衡 | Q301-Q308 | 8 | PUOLOP AO3416 | C479060 | 扩展库 | 9222 | 0.3152 | 2.52 |
| 均衡 | U301-U308 | 8 | SN74LVC1G17DBVR(UMW) | C7394021 | 扩展库 | 11569 | 0.2726 | 2.18 |
| 连接器 | J6 | 1 | 连欣 XDWF-C3030WV-2*5P | C18202166 | 扩展库 | 2915 | 2.1101 | 2.11 |
| 功率 | C1-C6 | 6 | CCTC TCC1206X7R105K101HT | C282823 | 扩展库 | 228062 | 0.3465 | 2.08 |
| 电源 | U4 | 1 | Tokmas LMR16006XDDCR | C54823941 | 扩展库 | 2670 | 1.7757 | 1.78 |
| 均衡 | Q311-Q318 | 8 | ElecSuper AO3415A | C5350990 | 扩展库 | 5293 | 0.2208 | 1.77 |
| 均衡 | D301-D308 D311-D318 | 16 | 1N5819WS | C191023 | 基础库 | 5074287 | 0.0973 | 1.56 |
| 电源 | C42 C44 | 2 | CCTC TCC1206X7R105K101HT | C282823 | 扩展库 | 228062 | 0.3465 | 0.69 |
| MCU | Y1 | 1 | YXC X322512MSB4SI | C9002 | 基础库 | 158129 | 0.6724 | 0.67 |
| 电源 | L1 | 1 | Sunlord SWPA5040S220MT | C68434 | 扩展库 | 49118 | 0.5389 | 0.54 |
| 电源 | R42 | 1 | Ever Ohms FCR1206J56RP055W | C153337 | 扩展库 | 4712 | 0.5353 | 0.54 |
| AFE | C201-C208 | 8 | Samsung CL05B104KB54PNC | C307331 | 基础库 | 14182012 | 0.0632 | 0.51 |
| 均衡 | R311-R318 R321-R328 | 16 | UNI-ROYAL 0402WGF3300TCE | C25104 | 基础库 | 1303012 | 0.0284 | 0.45 |
| 功率 | C_PACK_E | 1 | jieerrui RV63V47M6X8 | C48971005 | 扩展库 | 383149 | 0.3877 | 0.39 |
| 电源 | C40 | 1 | jieerrui RV63V47M6X8 | C48971005 | 扩展库 | 383149 | 0.3877 | 0.39 |
| AFE | C213 | 1 | CCTC TCC1206X7R105K101HT | C282823 | 扩展库 | 228062 | 0.3465 | 0.35 |
| 电源 | F11 | 1 | JDT JFC1206-1100FS | C136343 | 扩展库 | 96605 | 0.3096 | 0.31 |
| AFE | R201-R209 | 9 | UNI-ROYAL 0805W8F330JT5E | C17634 | 基础库 | 1639389 | 0.0334 | 0.30 |
| 连接器 | J5 | 1 | BOOMELE XH-13A | C40669 | 扩展库 | 244 | 0.2968 | 0.30 |
| 功率 | RT3 RT4 | 2 | APV ANTC1608-103F3380FB | C52155402 | 扩展库 | 136302 | 0.1399 | 0.28 |
| MCU | U8 | 1 | UMW PESD2CAN | C2687131 | 扩展库 | 675065 | 0.2563 | 0.26 |
| 均衡 | C301-C308 | 8 | Samsung CL05B104KO5NNNC | C1525 | 基础库 | 24533663 | 0.0319 | 0.26 |
| 功率 | DZ1 DZ2 | 2 | MM3Z15 | C65676 | 扩展库 | 1576 | 0.1271 | 0.25 |
| AFE | C219 | 1 | Samsung CL21B104KCFNNNE | C28233 | 基础库 | 1735708 | 0.2528 | 0.25 |
| AFE | C220 | 1 | Samsung CL21B104KCFNNNE | C28233 | 基础库 | 1735708 | 0.2528 | 0.25 |
| 电源 | C45 | 1 | Samsung CL21B104KCFNNNE | C28233 | 基础库 | 1735708 | 0.2528 | 0.25 |
| 均衡 | C321-C328 | 8 | 0402B102K500NT | C1523 | 基础库 | 3761636 | 0.0298 | 0.24 |
| 电源 | D7 | 1 | SS210 | C14996 | 基础库 | 843707 | 0.2286 | 0.23 |
| AFE | C214 | 1 | Samsung CL10A106KP8NNNC | C19702 | 基础库 | 11222604 | 0.2265 | 0.23 |
| 电源 | C43 | 1 | Samsung CL10A226MQ8NRNC | C59461 | 基础库 | 8283978 | 0.2208 | 0.22 |
| 功率 | Q17 Q18 | 2 | CJ SS8550 Y2 | C8542 | 基础库 | 1057555 | 0.1100 | 0.22 |
| MCU | C55 | 1 | Samsung CL10A475KO8NNNC | C19666 | 基础库 | 2709120 | 0.2087 | 0.21 |
| 功率 | D4 D5 | 2 | 1N5819WS | C191023 | 基础库 | 5074287 | 0.0973 | 0.19 |
| MCU | LED1 LED2 | 2 | NCD0805R1 | C84256 | 基础库 | 5253023 | 0.0951 | 0.19 |
| AFE | C212 | 1 | CCTC TCC0805X7R474K101FT | C5375914 | 扩展库 | 84671 | 0.1754 | 0.18 |
| MCU | C50-C54 | 5 | Samsung CL05B104KO5NNNC | C1525 | 基础库 | 24533663 | 0.0319 | 0.16 |
| MCU | SW1 | 1 | TS-1187A-B-A-B | C318884 | 基础库 | 572214 | 0.1456 | 0.15 |
| 均衡 | R301-R308 | 8 | UNI-ROYAL 0402WGF1003TCE | C25741 | 基础库 | 9741270 | 0.0177 | 0.14 |
| AFE | C215 C216 | 2 | Samsung CL05A105KA5NQNC | C52923 | 基础库 | 6498415 | 0.0703 | 0.14 |
| MCU | JP1 | 1 | PZ254V-11-02P | C492401 | 扩展库 | 1304546 | 0.1321 | 0.13 |
| MCU | LED3 | 1 | KT-0805G | C2297 | 基础库 | 1190733 | 0.1157 | 0.12 |
| AFE | Q201 | 1 | CJ MMBT5551 | C2145 | 基础库 | 1895577 | 0.1079 | 0.11 |
| 功率 | RG1-RG12 | 12 | UNI-ROYAL 0402WGF1000TCE | C25076 | 基础库 | 4638498 | 0.0085 | 0.10 |
| AFE | D201 | 1 | 晶导微 BZT52C3V3 | C353528 | 扩展库 | 64031 | 0.0994 | 0.10 |
| AFE | R216-R219 | 4 | UNI-ROYAL 0402WGF1002TCE | C25744 | 基础库 | 23489094 | 0.0241 | 0.10 |
| MCU | J7 | 1 | Megastar ZX-XH2.54-4PZZ | C7429634 | 扩展库 | 1176883 | 0.0831 | 0.08 |
| AFE | R220 R221 | 2 | UNI-ROYAL 0402WGF2201TCE | C25879 | 基础库 | 2479356 | 0.0376 | 0.08 |
| AFE | C217 | 1 | Samsung CL05A105KA5NQNC | C52923 | 基础库 | 6498415 | 0.0703 | 0.07 |
| AFE | C210 C211 | 2 | Samsung CL05B104KO5NNNC | C1525 | 基础库 | 24533663 | 0.0319 | 0.06 |
| MCU | C56 C57 | 2 | 0402CG330J500NT | C1562 | 基础库 | 1098445 | 0.0277 | 0.06 |
| 功率 | R_PUP1 R_PUP2 | 2 | UNI-ROYAL 0603WAF1005T5E | C7250 | 基础库 | 323686 | 0.0263 | 0.05 |
| 电源 | R40 | 1 | UNI-ROYAL 0402WGF3302TCE | C25779 | 基础库 | 1293857 | 0.0412 | 0.04 |
| AFE | C221 | 1 | CCTC TCC0603X7R103K101CT | C282516 | 扩展库 | 440603 | 0.0383 | 0.04 |
| AFE | C218 | 1 | Samsung CL05B103KB5NNNC | C15195 | 基础库 | 4418625 | 0.0355 | 0.04 |
| MCU | R51 R52 | 2 | UNI-ROYAL 0402WGF1003TCE | C25741 | 基础库 | 9741270 | 0.0177 | 0.04 |
| MCU | R56 R57 | 2 | UNI-ROYAL 0402WGF0000TCE | C17168 | 基础库 | 10197113 | 0.0177 | 0.04 |
| AFE | C209 | 1 | Samsung CL05B104KO5NNNC | C1525 | 基础库 | 24533663 | 0.0319 | 0.03 |
| 电源 | C41 | 1 | Samsung CL05B104KO5NNNC | C1525 | 基础库 | 24533663 | 0.0319 | 0.03 |
| MCU | C59 | 1 | Samsung CL05B104KO5NNNC | C1525 | 基础库 | 24533663 | 0.0319 | 0.03 |
| MCU | C58 | 1 | Samsung CL05B104KO5NNNC | C1525 | 基础库 | 24533663 | 0.0319 | 0.03 |
| MCU | R60 | 1 | UNI-ROYAL 0402WGF3300TCE | C25104 | 基础库 | 1303012 | 0.0284 | 0.03 |
| 功率 | RQB1 RQB2 | 2 | UNI-ROYAL 0402WGF1001TCE | C11702 | 基础库 | 8571652 | 0.0128 | 0.03 |
| MCU | R58 R59 | 2 | UNI-ROYAL 0402WGF1001TCE | C11702 | 基础库 | 8571652 | 0.0128 | 0.03 |
| AFE | R223 | 1 | UNI-ROYAL 0402WGF1002TCE | C25744 | 基础库 | 23489094 | 0.0241 | 0.02 |
| 电源 | R41 | 1 | UNI-ROYAL 0402WGF1002TCE | C25744 | 基础库 | 23489094 | 0.0241 | 0.02 |
| MCU | R50 | 1 | UNI-ROYAL 0402WGF1002TCE | C25744 | 基础库 | 23489094 | 0.0241 | 0.02 |
| MCU | R53 | 1 | UNI-ROYAL 0402WGF1002TCE | C25744 | 基础库 | 23489094 | 0.0241 | 0.02 |
| MCU | R55 | 1 | UNI-ROYAL 0603WAF1200T5E | C22787 | 基础库 | 1887840 | 0.0220 | 0.02 |
| AFE | R212 | 1 | UNI-ROYAL 0603WAF200JT5E | C22950 | 基础库 | 1852562 | 0.0177 | 0.02 |
| AFE | R222 | 1 | UNI-ROYAL 0402WGF1003TCE | C25741 | 基础库 | 9741270 | 0.0177 | 0.02 |
| MCU | R54 | 1 | UNI-ROYAL 0402WGF0000TCE | C17168 | 基础库 | 10197113 | 0.0177 | 0.02 |
| AFE | R210 R211 | 2 | UNI-ROYAL 0402WGF1000TCE | C25076 | 基础库 | 4638498 | 0.0085 | 0.02 |
| AFE | R213 | 1 | UNI-ROYAL 0603WAF5100T5E | C23193 | 基础库 | 4309440 | 0.0170 | 0.02 |
| 均衡 | R300 | 1 | UNI-ROYAL 0402WGF1001TCE | C11702 | 基础库 | 8571652 | 0.0128 | 0.01 |
| AFE | R214 | 1 | UNI-ROYAL 0402WGF1000TCE | C25076 | 基础库 | 4638498 | 0.0085 | 0.01 |
| AFE | R215 | 1 | UNI-ROYAL 0402WGF1000TCE | C25076 | 基础库 | 4638498 | 0.0085 | 0.01 |

## 按模块（元/块，10 块批量）

| 模块 | 小计 | 占比 |
|---|---|---|
| 功率 | 78.53 | 50% |
| AFE | 32.26 | 21% |
| 均衡 | 27.93 | 18% |
| MCU | 10.03 | 6% |
| 电源 | 5.04 | 3% |
| 连接器 | 2.41 | 2% |

## ⚠ 嘉立创库存不足 100 块用量的料

- Q1-Q12 Tokmas IPT012N08N5(TOKMAS)（C19626224）：库存 746，单板用 12

## 已采用的降本（2026-09-26 用户同意）

- **主动均衡改为分立开关电容（方案 B）**：替代 MP2643×7 及其电感、22µF、光耦、7A 保险丝、2×9 端子；均衡部分约 ¥186/块 → 约 ¥25/块；代价：电流随压差变化（100mV≈0.18A），平台区几乎不搬。

| 项 | 原方案 | 现方案 | 风险 / 代价 |
|---|---|---|---|
| 主 MOSFET | Infineon IPT012N08N5 ×16（C531199） | **Tokmas IPT012N08N5 ×12（C19626224）**，每方向 6 颗 | Rds(on) 典型 0.9 / 最大 1.2mΩ（同原厂），但 **Tj,max 150°C**（原厂 175°C），Qg 240nC；最坏值下 200A 通路 27.2W、最坏单管 Tj ≈ 105°C（45°C 环境），裕量 45°C；嘉立创库存 746（够 62 块） |
| MCU | STM32G0B1CBT6（C2847904，嘉立创库存 0） | **WCH CH32V203C8T6（C3001172）** | CAN 2.0B（非 FD）够用；固件底层驱动改写，逻辑层不变 |
| 4.7µF/100V 1210 | Murata GRM32ER72A475KE14L（C162515，库存 0） | **风华 FS32X475K101EGG（C381466）** | 同规格 X7R；封装同为 1210 |
| 扩展库种类 | 120k/150k/2M（0402 扩展库）、30Ω、62Ω×2、240k、100nF/50V 0402 | 改为 **0603 基础库** 120k/150k/2M、33Ω 0805、单 120Ω 终端、470k/20k 反馈、100nF/50V 0603 | 与规则 00②「封装下探」冲突：为减少扩展库上料费而选 0603；MP9486A 输出 4.9V |

## 库存风险

- Tokmas MOSFET 嘉立创库存 746：每块 12 颗，最多 62 块；量产前需备货或确认补货。
- MP2013A 已由 LMR16006 取代；SMBJ33A D6（C78419，库存约 47）已删除（D1–D3 已钳在 BAT+）。
- v0.3 起主动均衡改为分立开关电容（全部嘉立创料），不再有 MPS 客供件。
