colemandlut/MP2645A-BMS/design/04_power_supply-parts-r5.md

# 04_power_supply 取料报告 · 第 5 轮（取料方 parts，Claude Opus）

> 时间戳：2026-09-26 14:47 UTC
> 对象：复核报告 `design/04_power_supply-review-opus-r2.md` 中的 P1-1（R42/F11 保护协调）和 P1-2（输入陶瓷有效容量）。
> 纪律：只读工程文件，只写本报告。没有改原理图、BOM 或库，也没有运行 `fetch_jlc_parts.py`。
> 数据来源：
> - 库存和价格：`python3 tools/jlc_api.py`（嘉立创 SMT 实时接口，**嘉立创库存**，价格为美元阶梯价）。折人民币按 `tools/cost.py` 的假设汇率 7.10。
> - 手册：`python3 tools/fetch_datasheets.py` 下载到 `datasheets/`，用 pymupdf 读。页码一律是 **PDF 页号**。
> - 知识库：已检索 `obsidian-vault/BMS/降本排查要点.md`，里面没有熔断电阻相关的旧结论。

---

## 0. 结论速览

| 项 | 推荐 | 料号 | 库 | 嘉立创库存 | 10 块板增量 |
|---|---|---|---|---|---|
| **P1-1** | **方案 (a)**：R42 换成**熔断型贴片电阻 56Ω 1206** | **C153337** Ever Ohms FCR1206J56R0P05Z | 扩展 | 4 712 | **+¥12.6**（¥1.26/块） |
| P1-1 (b) | **否决**：嘉立创上找不到能在保险丝熔断前吸收 1–30 J 的 10Ω 贴片电阻（见 §2） | — | — | — | — |
| 手册要求的 VIN 旁路 | 100nF/100V 0805，紧贴 U4.5 | **C28233** CL21B104KCFNNNE（BOM 已有，C_VMID 在用） | **基础** | 1 741 299 | +¥2.5（¥0.25/块） |
| P1-2 (A) | C42 改为 4.7µF/100V 1210（PDC FS 系列，内部串联结构），C44 保留 1µF | **C381466** FS32X475K101EGG | 扩展 | 193 415 | +¥20.7（¥2.07/块） |
| P1-2 (B) | VIN_F 对地加 SMAJ33A | **C353454** 晶导微 SMAJ33A（备选 C113966 MDD） | 扩展 | 49 365 | +¥10.4（¥1.04/块） |

**关键发现：R42 从 10Ω 改成 56Ω 以后，P1-2 描述的风险基本消失。**
- 数值积分的最坏情况：270V/3.3µs 尖峰、C40 的 ESR 取 4Ω、陶瓷有效容量只剩 0.9µF。此时 VIN_F 峰值为 **39.2V**（10Ω 时是 77V）。与 Tokmas 的工作上限 60V、绝对最大值 65V 相比，都有 20V 以上的余量。
- 所以 P1-2 的 A、B 两种改法都**不再是必须项**。我建议只加 C28233 这颗 100nF 旁路，它是手册第 14 页明确要求的，而且不产生上料费。A 和 B 的料号与成本都列在下面，由用户定夺。

**推荐组合（P1-1 选 a + 100nF 旁路）**：10 块板合计增加 **≈ ¥15.1**（约 ¥1.5/块），扩展库**净增 1 种**（C153337；C17903 是基础库，删掉它不涉及上料费）。

---

## 1. 候选检索记录（嘉立创 SMT 库）

### 1.1 熔断电阻（fusible / flameproof）

检索用过的关键词：`熔断电阻` `保险电阻` `Fusible resistor` `Flameproof resistor` `fusing resistor` `Fuse Resistor`（另加 0603/0805/1206/1210/2010/2512/MELF/10Ω 等后缀）`FRN` `FKN` `FCR1206J` `FCR2512` `FCR0805J` `贴片保险电阻` `熔断 贴片电阻`。

| C 编号 | 型号 / 厂家 | 封装 | 规格 | 库 | 嘉立创库存 | 单价（美元） | 结论 |
|---|---|---|---|---|---|---|---|
| **C153337** | FCR1206J56R0P05Z / Ever Ohms | 1206 | 56Ω ±5% 0.25W 200V，Fuse Resistor | 扩展 | **4 712** | 1+ 0.0754 / 100+ 0.0606 / 300+ 0.0532 / 1000+ 0.0476 | ✅ 推荐 |
| C153338 | FCR1206J100RP05Z / Ever Ohms | 1206 | 100Ω ±5% 0.25W | 扩展 | 1 733 | 1+ 0.0739 | ❌ 20V 下只有 4W，低于 5W 的熔断门槛（见 §3.1） |
| C153336 / C153334 / C153329 | 同系列 47Ω / 39Ω / 4.7Ω | 1206 | — | 扩展 | 3 / 2 / 5 | — | ❌ 缺货 |
| C2093001 | FCR1206J10R（另一家，薄膜） | 1206 | 10Ω 125mW | 扩展 | 0 | — | ❌ 缺货，也不是熔断型 |
| C2534183 | FCR2512KT10R0 | 2512 | 10Ω 1W | 扩展 | 0 | — | ❌ 缺货 |
| C3039440 / C3039443 / C3039442 | KNP 1WS 10R J H2 Fuse（P11 / WF / SL）/ TyoHM | **插件** D4×L6 | 10Ω 1W 250V，线绕阻燃，带温度熔断元件 | 扩展 | 660 / 650 / 188 | 1+ 0.0793 | ⚠ 插件备选（见 §3.4） |
| C111941、C9900038492 等 | 10Ω 1W 插件保险电阻 | 插件 | — | 扩展 | 0 | — | ❌ 缺货 |

**结论**：嘉立创**没有有货的 10Ω 贴片熔断电阻**。有货的贴片熔断电阻里，Ever Ohms FCR1206 系列只有 56Ω、100Ω、820Ω 三档，其中只有 56Ω 能在 20V 欠压时满足熔断门槛。

### 1.2 抗浪涌 / 脉冲电阻（方案 b 用）

检索用过的关键词：`Anti-Surge` `pulse resistor 10Ω` `Surge Resistor` `抗浪涌` `ESR18/ESR10/ESR25`（ROHM）`SG73S2E`（KOA）`ERJ-P08/P06/P14`（Panasonic）`SR1206/SR2512`（Yageo）`2512 10Ω` `1210 10Ω` `MELF 10Ω`。

| C 编号 | 型号 | 封装 | 规格 | 库 | 嘉立创库存 | 单价（美元） |
|---|---|---|---|---|---|---|
| C2077830 | Panasonic ERJ-P08J100V | 1206 | 10Ω 0.66W 抗浪涌 | 扩展 | 705 | 1+ 0.0307 |
| C441940 | Panasonic ERJP06J100V | 0805 | 10Ω 0.5W 400V 抗浪涌 | 扩展 | 20 943 | 1+ 0.0187 |
| C2074340 / C2087764 | ROHM ESR18 / ESR25 10Ω | 1206 / 1210 | — | 扩展 | 0 / 0 | — |
| C723415 | Yageo SR1206JR-0710RL | 1206 | — | 扩展 | 0 | — |
| C16861 / C47019 | UNI-ROYAL 2512 10Ω 1W（普通厚膜） | 2512 | — | 扩展 | 116 295 / 236 039 | 1+ 0.043 / 0.040 |
| MELF 10Ω 各型号 | — | MELF | — | 扩展 | 全部 0 | — |

**手册核查**：
- C2077830 的 Panasonic ERJ-P 系列手册第 1–8 页只给了两项：
  - ESD 特性（第 3 页）；
  - 过载 2.0×额定电压、5 秒（第 4 页）。
  - **没有单脉冲功率–时间曲线**。
- C441940 是同系列 2023 版手册，第 3–5 页同样没有。
- C16861 是普通厚膜，手册 9 页里没有 pulse、surge 这类条目。

### 1.3 小额定保险丝（方案 b 用）

| C 编号 | 型号 | 封装 | In | 额定电压 | 熔化 I²t（A²s） | 冷阻 | 库 | 嘉立创库存 | 单价（美元） |
|---|---|---|---|---|---|---|---|---|---|
| C151119 | Littelfuse 0452.375MRL（慢熔） | 2410 | 0.375A | 125V | 0.101 | 1.2Ω | 扩展 | 1 982 | 1+ 0.360 |
| C151120 | Littelfuse 0452.500MRL（慢熔） | 2410 | 0.5A | 125V | 0.240 | 0.70Ω | 扩展 | 5 656 | 1+ 0.478 |
| C136342 | JDT JFC1206-0750FS（快熔） | 1206 | 0.75A | 63V | 0.0057 | 0.601Ω | 扩展 | 14 044 | 1+ 0.0738 |
| C136341 | JDT JFC1206-0500FS（快熔） | 1206 | 0.5A | 63V | 0.0019 | 1.028Ω | 扩展 | 15 946 | 1+ 0.0678 |

- Littelfuse 的数据见 `C151119.pdf` 第 1 页表格。I²t 按 8ms 计。
- JDT 的数据见 `C136342.pdf` 第 3 页表格。I²t 是 10In 下的熔断前 I²t。
- 1206 封装的慢熔型号，用 `Slow Blow 1206`、`慢断 保险丝 0.5A 1206`、`0.25A 63V`、`time delay 1206 fuse` 都没有检出。

---

## 2. P1-1 方案 (b) 为什么否决（定量）

方案 (b) 有一个绕不过去的矛盾：**上电冲击电流和短路电流都由同一个 R42 限流**。10Ω 时，上电峰值 I = 29.2/10.49 = 2.8A，**比** 20V 短路电流 1.9A 还大。保险丝只能靠持续时间来区分两者（0.5ms 对比持续短路）。能躲过上电的保险丝，在 1.9A 下就一定慢；这段时间内，R42 要吸收的能量 = I²t(熔断) × R。

| 候选 | 能否躲过上电（I²t_inrush = 0.0021 A²s @29.2V） | 20V 短路（≈1.8A）时的熔断时间 | 这段时间内 R42 吸收的能量 |
|---|---|---|---|
| JFC1206-0500FS | ❌ 0.0019 < 0.0021，上电就会误熔 | — | — |
| JFC1206-0750FS | ⚠ 只有 2.7 倍，达不到常见 3–5 倍的脉冲降额余量 | 2.4In：手册只保证「2.5In ≤ 5s」（`C136342.pdf` 第 2 页） | 最多约 32W × 5s ≈ **160 J** |
| 0452.375MRL | ✅ 0.101，余量 48 倍 | 4.8In：介于 300%（0.2–3s）和 800%（0.02–0.1s）之间（`C151119.pdf` 第 1 页），约 0.05–1s | ≈ 32W × (0.05–1s) = **1.6–32 J** |

- 嘉立创上有货的 10Ω 贴片电阻，**没有一颗在手册里给出能证明扛得住 1 J 以上的脉冲曲线**：
  - ERJ-P08 只有「2×RCWV（5.1V → 2.6W）5 秒」一项（`C2077830.pdf` 第 4 页）。
  - 32W 是这个值的 12 倍。
- 用 2512 或插件线绕电阻硬扛也不行：失效方式依旧不可控。而且这等于把「让电阻受控开路」的任务推给了保险丝，而保险丝恰恰做不到。
- 所以 (b) 否决，采用 (a)。

---

## 3. P1-1 推荐：方案 (a) R42 → C153337（Ever Ohms FCR1206J56R0P05Z，56Ω 熔断贴片电阻）

### 3.1 手册依据（`datasheets/C153337.pdf`，共 9 页）

| 项 | 数值 | 页 |
|---|---|---|
| 系列定位 | 「Fusible Chip Resistor — FCR Series … accurate fusibility is applicable to safety circuits」 | 第 1 页 |
| 额定功率 | 1206：0.25W @70°C | 第 2 页 |
| 最大隔离电压（熔断后） | 1206：**200V** | 第 2 页 |
| **熔断特性** | 1206：「Fusing Time & Min. Fusing Power：**< 30 sec at 5W**」 | 第 2 页 |
| TCR / 阻值范围 | 48Ω–470Ω：±400ppm；56Ω 在范围内 | 第 2 页 |
| 短时过载 | 2.5×RCWV（或最大过载电压，取小者），5 秒，ΔR ≤ ±(2.0%+0.1Ω)（5% 档） | 第 6 页 |
| 降额曲线 | 70°C 起线性降额，155°C 降到 0 | 第 7 页 |
| 推荐焊盘 | 1206：A 2.20、B 4.20、C 1.80（mm） | 第 7 页 |
| 工艺 | 适用回流焊，**不适用波峰焊** | 第 8 页 |
| **阻燃 / 不起明火** | **手册没有声明**（没有 UL94 或 flame 相关条款） | 全部 9 页 |
| **脉冲耐受曲线** | **手册没有给出** | 全部 9 页 |

### 3.2 最坏工况核算（R42 = 56Ω ±5%，F11 冷阻 0.49Ω）

**① VIN_F 对地短路：谁先断、多久、多少能量**

| 电池电压 | 短路电流 | R42 功耗（标称 / −5% / +5%） | 相对 5W 熔断门槛 | F11（1A 快熔）的动作 |
|---|---|---|---|---|
| 16.7V（深度过放） | 0.30A | 4.9 / 5.2 / 4.7W | ≈1×，**临界** | 0.3In，不熔 |
| **20V（欠压点）** | 0.35A | **7.0** / 7.4 / 6.7W | 1.3–1.5× → **< 30s 熔断** | 0.35In，不熔 |
| 29.2V（满充） | 0.52A | **15.0** / 15.7 / 14.3W | 2.9–3.1× | 0.52In，不熔 |
| 53V（瞬态） | 0.94A | 49W | ≈10× | 0.94In，不熔 |

- **R42 先断**，是受控开路，符合复核报告首选改法 1 的意图。F11 保留，作二级保护，负责 `VIN_R` 对地短路（复核 P2-7）。
- 熔断前 R42 最多吸收约 7W × 30s ≈ 210 J（20V、手册上限）。实际大功率下会快得多，但**手册只保证 < 30s**。按复核 P1-1 第 3 条，PCB 上 R42 周围要留净空、远离可燃物。
- 熔断后两端承受的电压 ≤ 53V（瞬态可到 270V），在最大隔离电压 200V 以内。270V 尖峰是 µs 级瞬态，而且这时 F11 仍在路上，风险可以接受。

**② 上电冲击（C40 + 陶瓷 ≈ 50µF）**

| 工况 | R42 吸收能量 ½CV² | 峰值电流 | 峰值功率 | τ = R·C | F11 的上电 I²t |
|---|---|---|---|---|---|
| 29.2V 上电 | 21 mJ | 0.54A | 16W | 2.7ms | 0.0004 A²s（F11 熔化 I²t 0.10，余量 250 倍） |
| 53V 全充（假想上界） | 70 mJ | 0.99A | 52W | 2.7ms | 0.0013 A²s |

- 对照手册第 6 页的短时过载项：RCWV = √(0.25×56) = 3.74V → 2.5 倍 = 9.35V → 1.56W × 5s = **7.8 J** 不劣化。上电能量只有它的 1/370（29.2V）到 1/110（53V）。但峰值功率高于 1.56W，所以还要看绝热温升。
- 绝热温升估算（手册没有脉冲曲线，这里是估算）：
  - 2.7ms 内氧化铝的热扩散深度 √(α·t) = √(9×10⁻⁶ × 2.7×10⁻³) ≈ 0.16mm；
  - 受热体积 ≈ 膜区 3.3mm² × 0.16mm ≈ 0.5mm³，ρc ≈ 3.4 mJ/(mm³·K)，热容 ≈ 1.8 mJ/K；
  - 温升：**29.2V 约 12K，53V 约 40K**。离熔断温度（膜层需要几百 °C）很远。✅
- 与 10Ω 方案比：峰值功率从 85W 降到 16W，所以 56Ω 对熔断元件更温和。
- **待台架验证**：上电 100 次后 ΔR ≤ 2%。另外用 20V 限流源短接 VIN_F，实测熔断时间，并确认不起明火。手册没写阻燃，这一项只能靠实测。

**③ 正常工作**

- 输入电流约 16.5mA（20V，3.3V/80mA，效率 0.8）→ 压降 0.93V，功耗 **15mW**，为额定的 6%。
- VIN_F ≥ 19V，远高于 Tokmas 的 4V 工作下限和 3.9V UVLO（`C54823941.pdf` 第 4 页）。

**④ 副作用：必须写进设计文档**

- 56Ω 限制了 3V3 能拿到的功率：20V 时理论最大传输功率 V²/4R ≈ 1.8W。R42 保持 ≤ 0.25W 时，**3V3 的持续负载应 ≤ 约 0.15–0.2A**。本设计 < 80mA，满足。
- 3V3 硬短路时，Tokmas 限流 1.5A，输出电压 ≈ 0，输入功率约 1.5W（主要是 D7 的损耗），输入电流约 50mA → R42 约 0.15W，**不会误熔**。
- 3V3 被拉到 0.5–1A 的**部分过载**是病态区：VIN_F 塌陷、UVLO 反复打嗝，R42 平均约 2–4W。这低于保证熔断的 5W，属于「热但不保证断」。原方案 10Ω 在同样工况下也超过 0.25W（复核「专项核算」第 2 行），不是新引入的问题，但要点名。
- 输入滤波稳定性（Middlebrook 判据）：
  - buck 的负输入阻抗 |Zin| = V²/P ≈ 20²/0.33 ≈ 1.2kΩ；
  - RC 滤波器的输出阻抗 ≤ 56Ω ≪ 1.2kΩ，稳定 ✅。
- 电池低于约 16.7V（每串 2.1V）时，短路功耗会跌到 5W 以下，熔断就不再有保证。这属于深度过放后的残余风险。

### 3.3 换料四项（规则 0b）

| # | 项 | 结论 |
|---|---|---|
| 1 | 规格 | **阻值变了**：10Ω ±1% → **56Ω ±5%**。<br>相同：250mW、200V、1206 厚膜。<br>新增：熔断特性（< 30s @ ≥ 5W）。<br>TCR 同为 ±400ppm。降低：精度从 1% 降到 5%，对 RC 限流无影响。<br>收益：VIN_F 尖峰峰值从 77V 降到 39V，上电峰值功率从 85W 降到 16W。 |
| 2 | 封装 | 都是 1206。但 `hardware/lib/jlc/` 里**没有 C153337 的符号和封装**（grep 无命中）。现有的 `jlc:R1206` 是为 C17903 取的。主代理需要用 `fetch_jlc_parts.py` 取 C153337，再用 `fp_compare.py` 和 `jlc:R1206` 比对。手册推荐焊盘见第 7 页：A 2.20 / B 4.20 / C 1.80。 |
| 3 | 价钱 | C17903 是**基础库** $0.0113，换成 **扩展库** $0.0754（1+ 档，10 片）。<br>10 块板：零件 +$0.64 ≈ **+¥4.6**，上料费 **+¥8**，合计 **+¥12.6**（¥1.26/块）。<br>C17903 只有 R42 在用（BOM 第 61 行），删掉它不省上料费（基础库本来不收）。<br>这是「基础库 → 扩展库」的方向，**硬理由**：安全，P1-1 必须改。 |
| 4 | 可采购性 | **嘉立创库存 4 712**，够 10 块板。<br>单一来源（Ever Ohms）。同系列 47Ω、39Ω 已经缺货，要留意这颗断货。<br>断货时的后备：插件 C3039443（KNP 1WS 10R Fuse，库存 650），见 §3.4。 |

### 3.4 后备：插件阻燃熔断线绕电阻 C3039440 / C3039443（TyoHM KNP 1WS 10R J H2 Fuse）

`datasheets/C3039440.pdf`，共 8 页：

- **阻燃涂层**，耐 800°C（第 4 页 §4.3.2）。
- **温度熔断元件**：260±10°C 动作，1A 最大工作电流（第 5 页 §4.3.4）。
- 5 倍额定功率、5 秒，无电弧、无火焰（第 5 页 §7.3）。
- **Non-flammability**：无火焰、无爆炸、无电弧（第 6 页 §7.10）。
- **熔断特性**：「80 VAC–420 VAC 直接施加 5 秒内熔断，无火焰，熔断后 > 2MΩ」（第 6 页 §7.11）。⚠ 这只在 ≥ 80V 市电条件下保证，**20–29V 直流（36–77W）下的熔断没有保证**。不过 1W 线绕件在 36W 下几秒内就会超过 260°C，应该能动作，需要实测。
- **抗冲击**：33A 脉冲 10 000 次（第 7 页 §7.13），远超上电的 2.8A。
- 缺点：插件，需要嘉立创插件焊接或手焊，有额外费用；P11 引脚成形是为 AC-11 机型设计的，SL 直脚版 C3039442 库存只有 188；另外还要新建 THT 封装。

所以只作后备。它的优点是保持 10Ω，阻燃也有明文。

---

## 4. P1-2：A、B 两种改法的料号与核算

### 4.1 先说前提：R42 = 56Ω 时 VIN_F 的尖峰峰值

**模型**：
- 尖峰：BAT+ = 29.2V + 矩形尖峰（与复核口径一致，伏秒约 800µV·s）；
- 串联：F11 0.49Ω + R42；
- VIN_F 节点：C_cer ∥（C40 47µF + ESR）∥ 可选的 TVS；
- 数值积分，步长 1ns。
- 为核对模型：R42 = 10Ω 这一行的结果与复核报告的表基本一致（复核给的是 61.9 / 71.8V）。

| R42 | C_cer 有效值 | TVS | 90V/13µs，ESR 1 / 2 / 4Ω | 270V/3.3µs，ESR 1 / 2 / 4Ω |
|---|---|---|---|---|
| 10Ω | 1.2µF | 无 | 35.6 / 39.7 / 46.0 | 49.7 / 60.5 / **70.0 ❌** |
| 10Ω | 0.9µF | 无 | 35.6 / 39.8 / 46.4 | 50.5 / 63.8 / **77.1 ❌** |
| 10Ω | 2.2µF | 无 | 35.4 / 39.2 / 44.0 | 46.4 / 52.1 / 56.1 ✅ |
| 10Ω | 1.2µF | SMAJ33A | 35.6 / 39.7 / 42.8 | 47.0 / 53.3 / 58.4 ✅ |
| **56Ω** | **0.9µF** | 无 | 30.5 / 31.5 / 33.3 | 33.4 / 36.3 / **39.2 ✅** |
| **56Ω** | 1.2µF | 无 | 30.5 / 31.4 / 33.1 | 33.2 / 35.5 / 37.5 ✅ |
| 58.8Ω（+5%） | 0.9µF | 无 | 30.4 / 31.4 / 33.1 | 33.2 / 35.9 / 38.7 ✅ |

- **56Ω 下，即使 C40 完全失效（开路），VIN_F 也 ≤ 约 45V**。计算：Q ≈ (270−30)/56 × 3.3µs ≈ 14µC，除以 0.9µF 得 ΔV ≈ 16V。
- 结论：采用 §3 的推荐后，**A、B 都不是必须的**。仍然建议加：
  - **C28233**（100nF/100V X7R 0805，Samsung CL21B104KCFNNNE）：**基础库**，嘉立创库存 1 741 299，$0.0356（1+）。BOM 已有（第 33 行 C_VMID），`jlc.kicad_sym` 里已有符号。
  - 依据：Tokmas 手册第 14 页「a 0.1µF ceramic bypass capacitor is recommended to be placed as close as possible to the VIN pin」。
  - 10 块板 +¥2.5，**不增加上料种类**。
  - 说明：复核建议用 0402–0603，这里取 0805，因为复用 BOM 已有的基础库料最省；100V 的 0603 只有扩展库（例如 C113803，$0.0128），会多 ¥8 上料费。

### 4.2 (A) 输入陶瓷有效容量 ≥ 2.2µF（29–53V 偏压下）

先说明：**下面三份候选手册都没有直流偏压曲线**。
- Murata `C2997285.pdf` 第 1 页只写了「X7R(MURATA)：施加 50% 额定电压时温度特性 −15 ~ +15%」，那是温度特性，不是偏压曲线。
- Samsung `C170101.pdf` 共 84 页的目录册里没有。
- CCTC `C5449052.pdf` 也没有。

所以有效容量只能估算：按同类 100V X7R 的典型偏压衰减，1210 在 30V / 50V 下约剩 60% / 40%，1206 高容值件约剩 45–55% / 30–40%。这与第 1 轮复核对 C381466 的估算（≈2.8→1.9µF）同一口径。**上板后要用 LCR 加直流偏置实测。**

| 方案 | 料号 | 封装 | 29V → 53V 估算有效值 | 库 / 库存 | 单价（美元） | 10 块板增量 |
|---|---|---|---|---|---|---|
| **A1（推荐）** C42 → 4.7µF/100V，C44 保留 C13832 | **C381466** PDC FS32X475K101EGG | 1210 | 4.7µF：2.8→1.9，加上 1µF：0.5→0.4，**合计 3.3→2.3µF** ✅ | 扩展 / **193 415** | 1+ 0.242 / 50+ 0.194 | 零件 +¥12.7（新增 10 颗 C381466 ¥17.2，减去 10 颗 C13832 ¥4.5），上料 +¥8，**合计 +¥20.7** |
| A2：C42、C44 → 2×2.2µF/100V 1210 | C5449052 CCTC TCC1210X7R225K101MT | 1210 | 2×(1.3→0.9) ≈ 2.6→1.8µF ⚠ 53V 时不足 | 扩展 / 80 230 | 1+ 0.0866 / 50+ 0.0687 | 零件 +¥3.2，上料 +¥8，合计 +¥11.2 |
| A3：C42、C44 → 2×4.7µF/100V 1206 | C2997285 Murata GRM31CZ72A475KE11L | 1206（可原位替换） | 2×(2.3→1.6) ≈ 4.6→3.2µF ✅ | 扩展 / 41 457 | 1+ 0.737 | 零件 +¥95.6，上料 +¥8，合计 +¥103.6 ❌ 太贵 |

**A1 推荐理由**：
- PDC FS 系列是**内部串联结构**。手册第 3 页原文：「series connection of multi-layer capacitor units … distribute voltage gradients … **so as to prevent short circuit failure**」。这直接降低了 P1-1 的触发概率（MLCC 板弯裂纹导致短路）。
- 库里现成就有：`jlc.kicad_sym` 中仍保留 C381466 的符号，`jlc:C1210` 的 `LCSC Part` 也是 C381466。它是第 1 轮 C42 用过的料，**不需要重新取库**。
- C13832 还有 C1–C14、C_REG 在用（BOM 第 11、40 行），所以换掉 C42 省不掉它的上料费。

**换料四项（A1）**：
1. 规格：1µF → 4.7µF，100V X7R，耐压相同。
2. 封装：1206 → **1210，需要改 PCB**，`fp_compare`。
3. 价钱：+¥20.7 / 10 块板，扩展库 +1 种。
4. 可采购性：嘉立创库存 19 万，没有问题。

注意：这正是用户 13:57 降本时撤掉的料，与那次「2×1µF」的决定冲突，需要用户确认。

### 4.3 (B) 保留 2×1µF，VIN_F 对地加 SMAJ33A

四颗候选的手册参数一致：VRWM 33V，VBR 36.7–40.6V，Vc 53.3V @ Ipp 7.5A（10/1000µs），PPPM 400W。

| C 编号 | 厂家 | 嘉立创库存 | 单价（美元） | 手册页 |
|---|---|---|---|---|
| **C353454（推荐）** | 山东晶导微 | **49 365** | 1+ 0.0337 / 200+ 0.0267 | `C353454.pdf` 第 1 页额定值，第 2 页 Table 1，第 3 页 Fig.1 脉冲功率–脉宽曲线 |
| C113966 | MDD 辰达 | 42 695 | 1+ 0.0413 | `C113966.pdf` 第 1 页额定值（PM(AV) 3.3W，IFSM 40A），第 2 页参数表（SMAJ33A 在第 2 页末），第 3 页 Figure 1 |
| C320536 | LGE | 3 981 | 1+ 0.0536 | 未下载核对 |
| C223988 | Littelfuse | 11 565 | 1+ 0.1319 | 未下载核对（太贵） |

**TVS 核算**：
- 取 Rdyn ≈ (Vc − VBRmax)/Ipp = (53.3 − 40.6)/7.5 ≈ 1.7Ω（保守）。
- R42 = 10Ω 时（原方案）：
  - 270V/3.3µs、ESR 4Ω：TVS 峰值 **10.5A**、吸收 1.4mJ，VIN_F 峰值 58.4V，低于 65V ✅；
  - ESR 2Ω：7.5A、0.86mJ，VIN_F 53.3V；
  - 90V 尖峰：≤ 1.3A。
  - 几 µs 脉冲下的允许功率远高于 400W @1ms（Fig.1），单次能量 < 2mJ，余量充足 ✅。
- R42 = 56Ω 时（推荐方案）：上面所有尖峰工况下 VIN_F ≤ 39.2V。只有最坏的 ESR 4Ω 叠加 VBR 下限 36.7V 时，TVS 才会微导通（< 1A），**基本不起作用**。
- **持续直流过压的失效顺序**（例如充电器故障，BAT+ 持续 53V）：
  - 10Ω：TVS 电流 ≈ (53−38)/10.5 ≈ 1.4A，约 55W，很快短路失效。随后普通 R42 承受 267W 烧开，回到 P1-1 的问题。
  - 56Ω 熔断电阻：TVS 约 0.27A、约 10W，超过 PM(AV) 3.3W，TVS 可能短路失效。随后 FCR 承受 53²/56 ≈ 50W，≥ 5W，受控熔断 ✅。
  - 结论：**B 只有和 P1-1 (a) 搭配才安全**。
- 成本：C353454 10 片 ≈ ¥2.4，上料 +¥8，**合计 +¥10.4**（¥1.04/块），扩展库 +1 种。
- 封装：SMA。库里 `jlc:SMA_L4.3-W2.6-LS5.2-RD` 是为 C14996 SS210 取的，C353454 本身的符号和封装不在库里，需要取库后 `fp_compare`。
- 规则 0b 四项：新增件，不是换料。规格、封装、价钱、库存如上，无问题。

---

## 5. 成本增量汇总（10 块板，汇率 7.10，扩展库上料费标准型 ¥8/种）

| 组合 | 零件增量 | 上料费 | 合计 | 每块 | 扩展库种类 |
|---|---|---|---|---|---|
| **推荐：P1-1 (a) C153337 + 100nF C28233** | ¥7.1 | ¥8 | **¥15.1** | **¥1.51** | +1 |
| 推荐 + P1-2 (A1) C381466 | +¥12.7 | +¥8 | ¥35.8 | ¥3.58 | +2 |
| 推荐 + P1-2 (B) C353454 | +¥2.4 | +¥8 | ¥25.5 | ¥2.55 | +2 |
| 推荐 + A2 C5449052×2 | +¥3.2 | +¥8 | ¥26.3 | ¥2.63 | +2 |

我的建议：**只做「推荐」这一行**。A1、B 留作用户可选：如果一定要满足 Tokmas「4.7–22µF」的字面推荐，选 A1；如果担心 01 页 D3 还没定稿、BAT+ 上可能出现持续过压，选 B。

---

## 6. 交给主代理的动作（取料方不执行）

1. 取库：`python3 tools/fetch_jlc_parts.py C153337`；如果用户选了 A1 / B，再加 C381466 / C353454。
2. `fp_compare.py`：C153337 与 `jlc:R1206` 比对；C381466 已在库中（`jlc:C1210`），不需要比对；C353454 与 `jlc:SMA_L4.3-W2.6-LS5.2-RD` 比对。
3. 原理图：
   - R42 Value 改为 56Ω，LCSC 改为 C153337；
   - U4.5 旁加 C28233，贴 VIN 引脚；
   - BOM 第 61 行的备注「限流 ≤5.3A」改为「≤0.94A（53V）；熔断电阻，≥5W 时 < 30s 开路」；
   - 设计文档注明「3V3 持续负载 ≤ 0.15A」。
4. 台架验证（写入测试计划）：
   - 上电 100 次后 ΔR ≤ 2%；
   - 20V 和 29.2V 限流源短接 VIN_F，记录熔断时间，确认无明火；
   - C42/C44 加偏置实测有效容量（如果改了）。
5. 知识库待写回（取料方按任务只写本报告，由主代理写入 `obsidian-vault/`）：
   - 嘉立创没有有货的 10Ω 贴片熔断电阻；有货的是 Ever Ohms FCR1206 系列，56Ω C153337 库存 4 712，熔断门槛「5W / < 30s」。
   - 保险丝配合方案 (b) 在「上电峰值电流 ≥ 短路电流」的拓扑下不可行。
   - R42 从 10Ω 改 56Ω 后，VIN_F 尖峰峰值从 77V 降到 39V。
