colemandlut/MP2645A-BMS/review/04-r5/sch.pdf

层次结构（v0.3 骨架）：主动均衡为分立开关电容；电路按 datasheets/ 手册逐 IC 核对后再画

8S LiFePO4 200A BMS · MPS MP2797 + 开关电容均衡
MP2645A-BMS
Sheet: /
File: mp2645a-bms.kicad_sch
Title: 8S LFP 200A BMS — 总图

Size: A3 | Rev: v0.3-skeleton | F Date: 2026-09-26
KiCad E.D.A. 10.0.6 | Id: 1/6


内容：B+ 熔断器 / CHG、DSG 各 8 并联 NMOS / 栅极网络与 PNP 快速关断 / 分流器 / TVS / 预充 / P+ P- 端子

状态：待画。详细设计见 docs/03-详细设计.md；按 pcb-workflow 规则 00/00c/00d 执行。


内容：电芯采样 RC / 电流采样滤波 / 4 路 NTC / 高边驱动输出 / 通讯与中断 / 被动均衡

状态：待画。详细设计见 docs/03-详细设计.md；按 pcb-workflow 规则 00/00c/00d 执行。


内容：8 个互补半桥 QN/QP(AO3400A/AO3401A) + 8 个 74LVC1G17（本节电芯供电）+ 7 级飞电容 3x100µF / 时钟 BAL_CLK 逐级电容耦合 / 均衡节点 3A 保险丝

状态：待画。详细设计见 docs/03-详细设计.md；按 pcb-workflow 规则 00/00c/00d 执行。

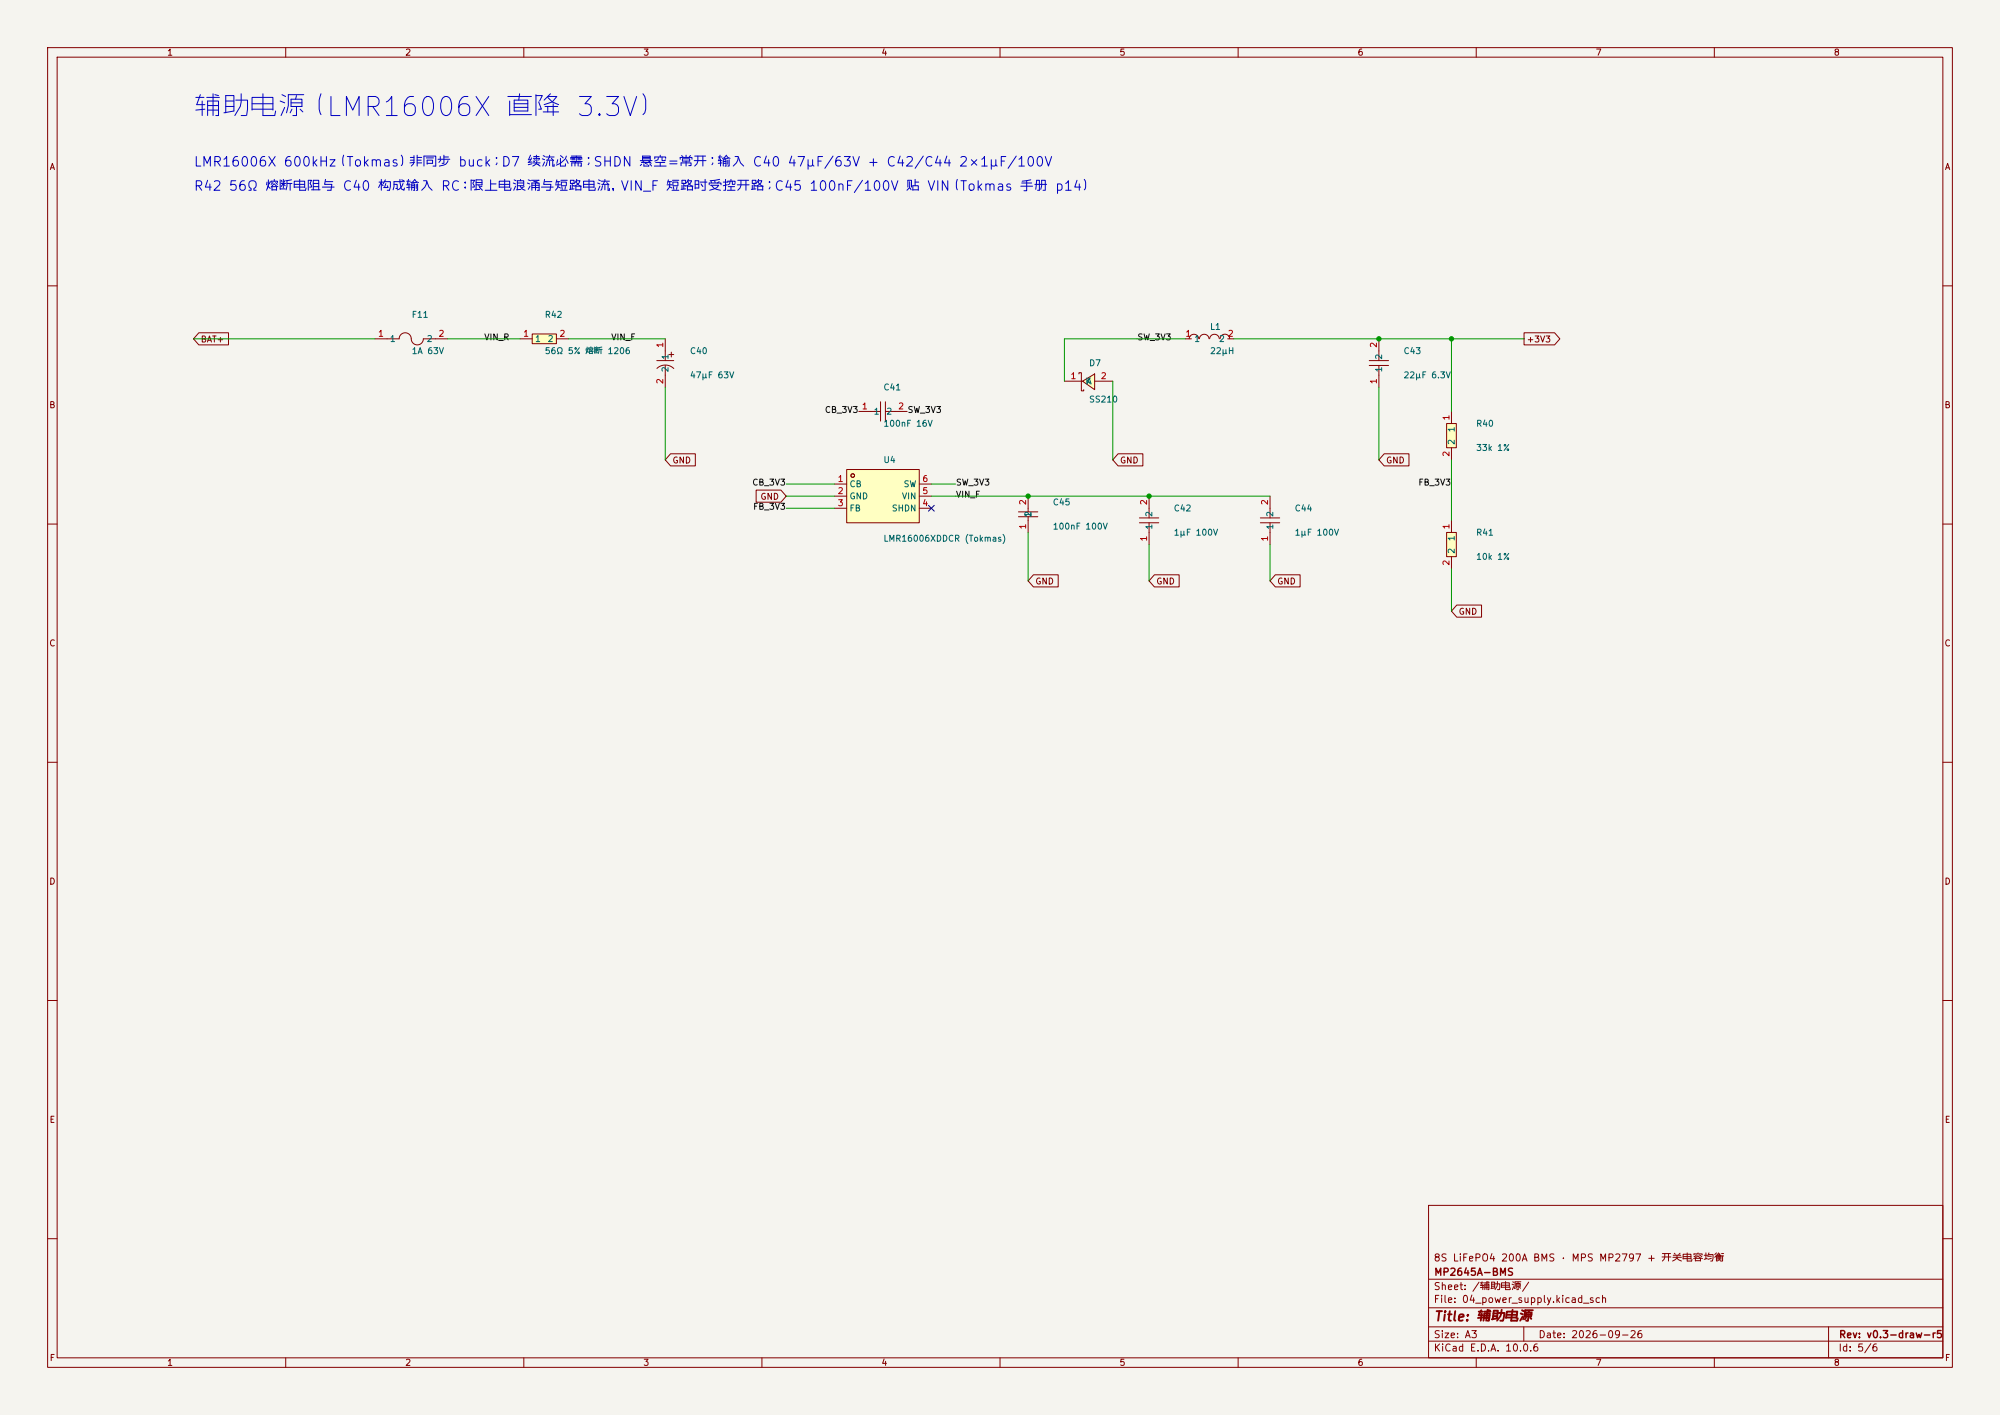
[picture p15: page 5]

LMR16006X 600kHz（Tokmas）非同步 buck；D7 续流必需；SHDN 悬空=常开；输入 C40 47µF/63V + C42/C44 2×1µF/100V

R42 56Ω 熔断电阻与 C40 构成输入 RC：限上电浪涌与短路电流，VIN_F 短路时受控开路；C45 100nF/100V 贴 VIN（Tokmas 手册 p14）

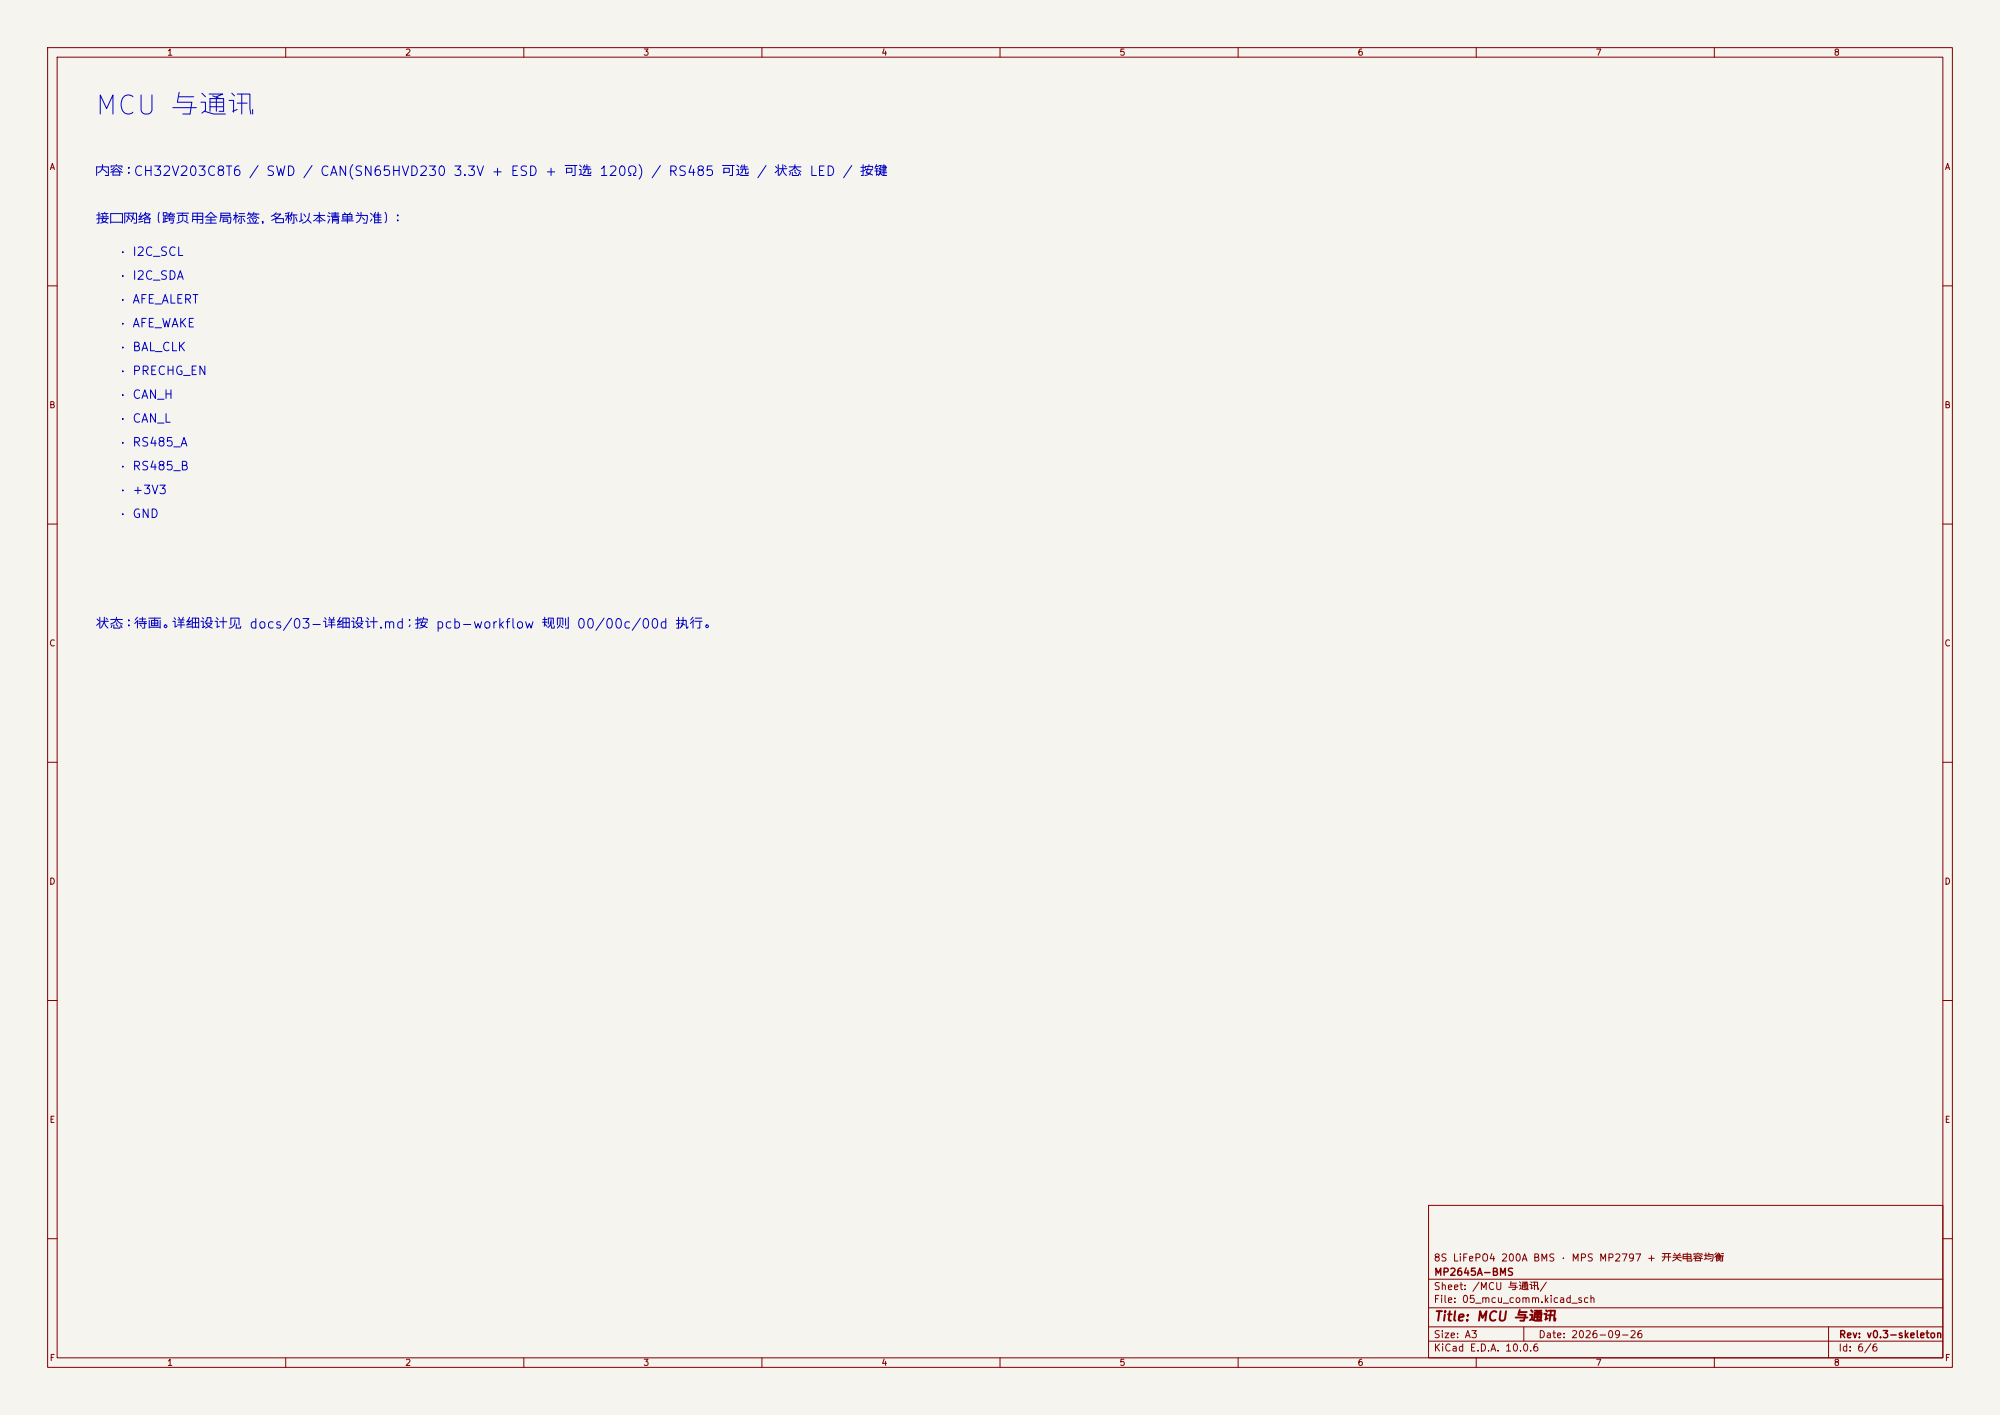
[picture p16: page 6]

内容：CH32V203C8T6 / SWD / CAN(SN65HVD230 3.3V + ESD + 可选 120Ω) / RS485 可选 / 状态 LED / 按键

状态：待画。详细设计见 docs/03-详细设计.md；按 pcb-workflow 规则 00/00c/00d 执行。
