colemandlut/MP2645A-BMS/review/02-r2/02_afe.kicad_sch

## KiCad design review/02-r2/02_afe.kicad_sch (2026-09-27)

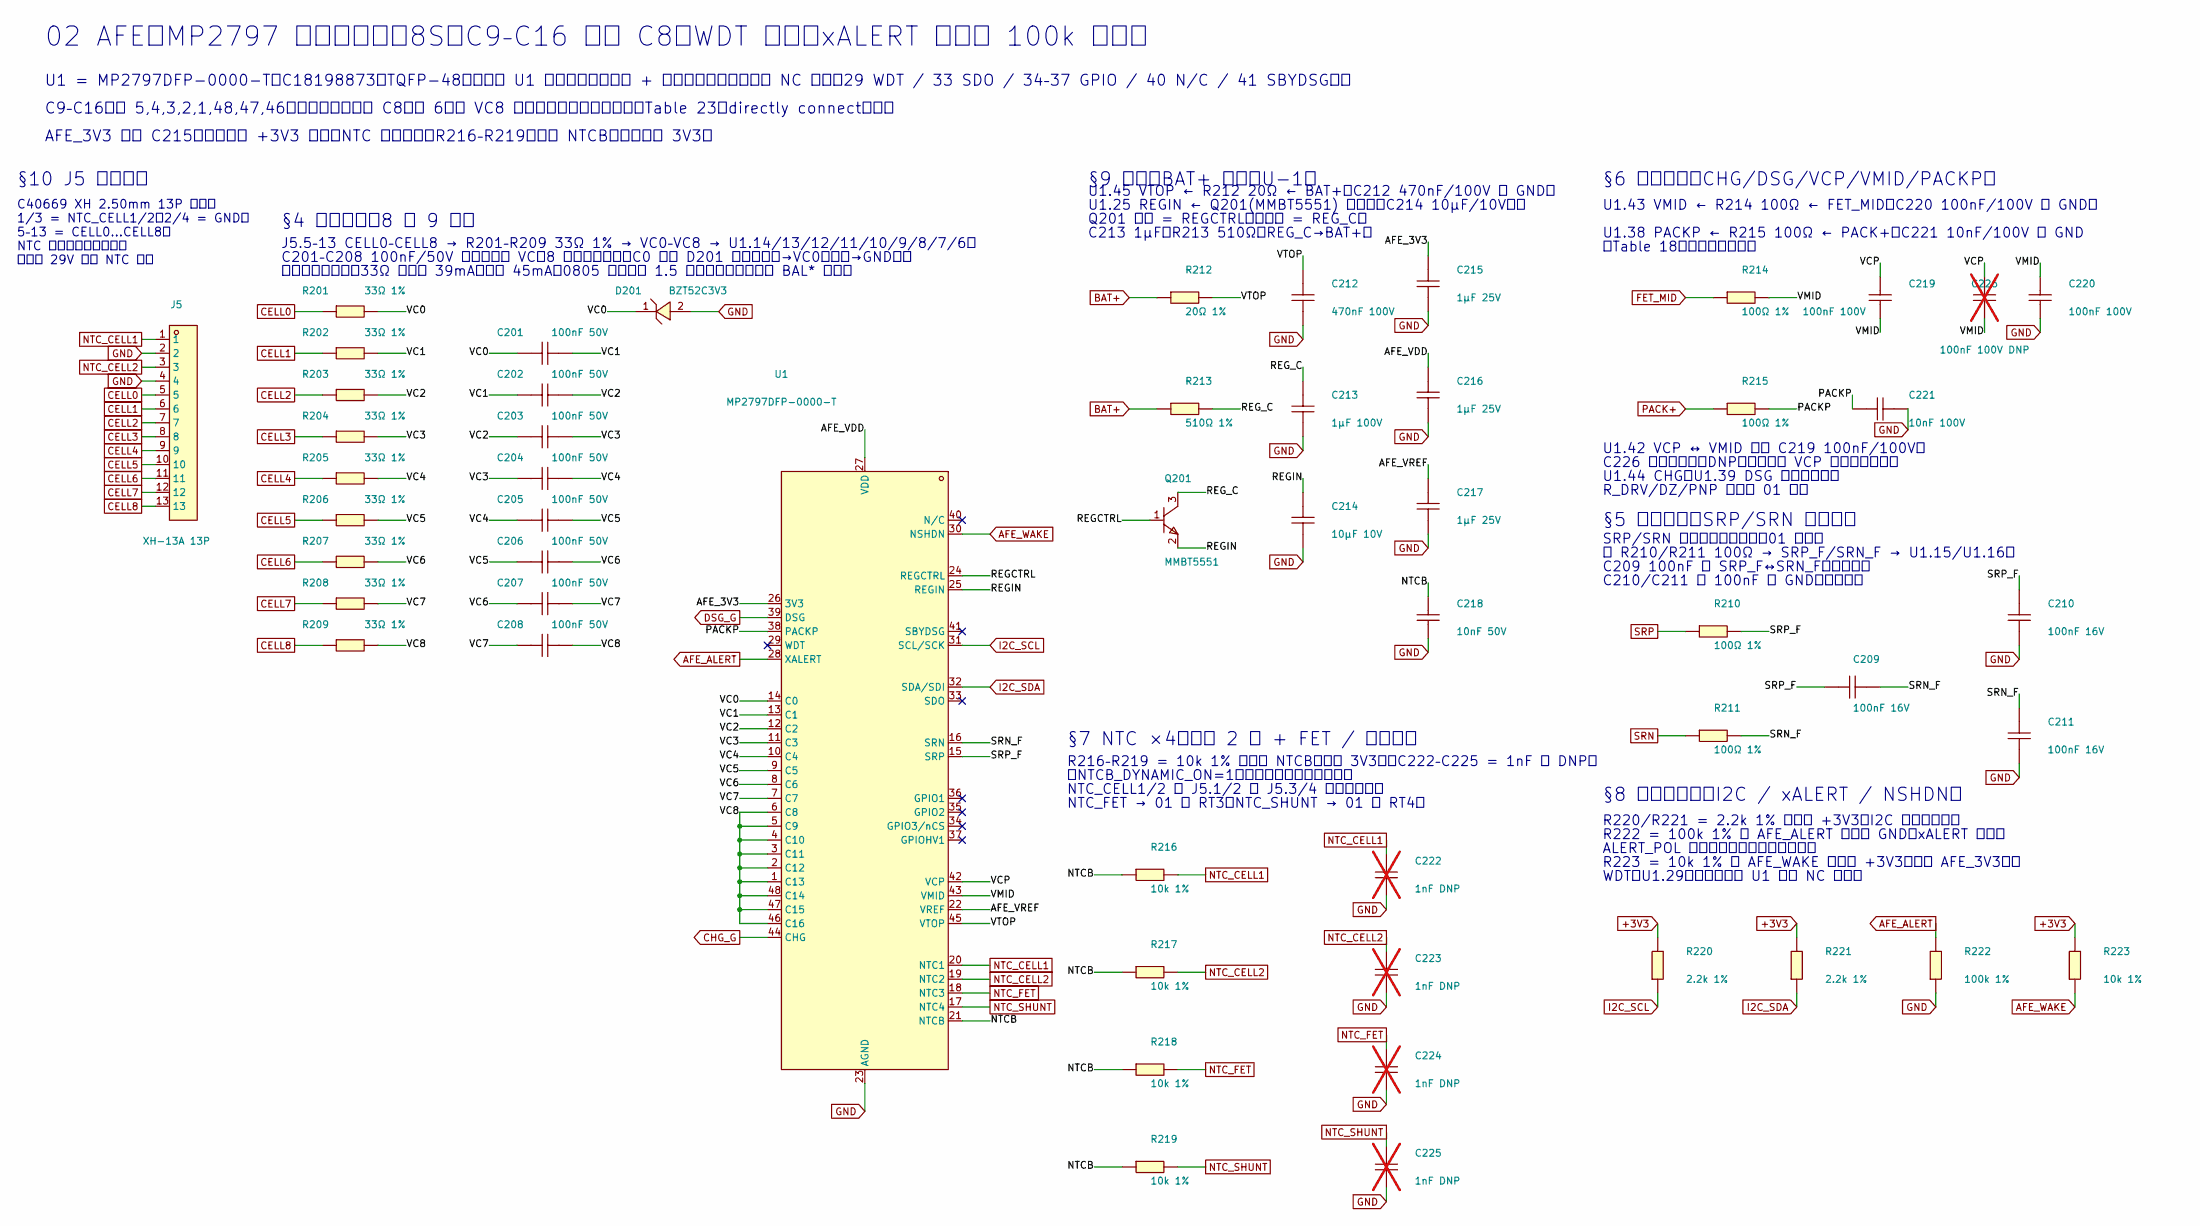
[picture p17: schematic 02_afe.kicad_sch]

Parts:
C201, C202, C203, C204, C205, C206, C207, C208: 100nF 50V; C0402; LCSC C307331
C209, C210, C211: 100nF 16V; C0402; LCSC C1525
C212: 470nF 100V; C0805; LCSC C5375914
C213: 1µF 100V; C1206; LCSC C282823
C214: 10µF 10V; C0603; LCSC C19702
C215, C216, C217: 1µF 25V; C0402; LCSC C52923
C218: 10nF 50V; C0402; LCSC C15195
C219, C220: 100nF 100V; C0805; LCSC C28233
C221: 10nF 100V; C0603; LCSC C282516
C222, C223, C224, C225: 1nF DNP; C0402; LCSC C1523; not fitted
C226: 100nF 100V DNP; C0805; LCSC C28233; not fitted
D201: BZT52C3V3; SOD-123_L2.8-W1.8-LS3.7-RD; LCSC C353528
J5: XH-13A 13P; CONN-TH_13P-P2.50_XH-13A; LCSC C40669
Q201: MMBT5551; SOT-23-3_L2.9-W1.3-P1.90-LS2.4-BR; LCSC C2145
R201, R202, R203, R204, R205, R206, R207, R208, R209: 33Ω 1%; R0805; LCSC C17634
R210, R211, R214, R215: 100Ω 1%; R0402; LCSC C25076
R212: 20Ω 1%; R0603; LCSC C22950
R213: 510Ω 1%; R0603; LCSC C23193
R216, R217, R218, R219, R223: 10k 1%; R0402; LCSC C25744
R220, R221: 2.2k 1%; R0402; LCSC C25879
R222: 100k 1%; R0402; LCSC C25741
U1: MP2797DFP-0000-T; LQFP-48_L7.0-W7.0-P0.50-LS9.0-BL_1; LCSC C18198873

Connections:
+3V3: R220.2, R221.2, R223.2
AFE_3V3: C215.2, U1.26 (3V3)
AFE_ALERT: R222.2, U1.28 (XALERT)
AFE_VDD: C216.2, U1.27 (VDD)
AFE_VREF: C217.2, U1.22 (VREF)
AFE_WAKE: R223.1, U1.30 (NSHDN)
BAT+: R212.1, R213.1
CELL0: J5.5, R201.1
CELL1: J5.6, R202.1
CELL2: J5.7, R203.1
CELL3: J5.8, R204.1
CELL4: J5.9, R205.1
CELL5: J5.10, R206.1
CELL6: J5.11, R207.1
CELL7: J5.12, R208.1
CELL8: J5.13, R209.1
CHG_G: U1.44 (CHG)
DSG_G: U1.39 (DSG)
FET_MID: R214.1
GND: C210.1, C211.1, C212.1, C213.1, C214.1, C215.1, C216.1, C217.1, C218.1, C220.1, C221.1, C222.1, C223.1, C224.1, C225.1, D201.2 (A), J5.2, J5.4, R222.1, U1.23 (AGND)
I2C_SCL: R220.1, U1.31 (SCL/SCK)
I2C_SDA: R221.1, U1.32 (SDA/SDI)
NTCB: C218.2, R216.1, R217.1, R218.1, R219.1, U1.21 (NTCB)
NTC_CELL1: C222.2, J5.1, R216.2, U1.20 (NTC1)
NTC_CELL2: C223.2, J5.3, R217.2, U1.19 (NTC2)
NTC_FET: C224.2, R218.2, U1.18 (NTC3)
NTC_SHUNT: C225.2, R219.2, U1.17 (NTC4)
PACK+: R215.1
PACKP: C221.2, R215.2, U1.38 (PACKP)
REGCTRL: Q201.1 (B), U1.24 (REGCTRL)
REGIN: C214.2, Q201.2 (E), U1.25 (REGIN)
REG_C: C213.2, Q201.3 (C), R213.2
SRN: R211.1
SRN_F: C209.2, C211.2, R211.2, U1.16 (SRN)
SRP: R210.1
SRP_F: C209.1, C210.2, R210.2, U1.15 (SRP)
VC0: C201.1, D201.1 (C), R201.2, U1.14 (C0)
VC1: C201.2, C202.1, R202.2, U1.13 (C1)
VC2: C202.2, C203.1, R203.2, U1.12 (C2)
VC3: C203.2, C204.1, R204.2, U1.11 (C3)
VC4: C204.2, C205.1, R205.2, U1.10 (C4)
VC5: C205.2, C206.1, R206.2, U1.9 (C5)
VC6: C206.2, C207.1, R207.2, U1.8 (C6)
VC7: C207.2, C208.1, R208.2, U1.7 (C7)
VC8: C208.2, R209.2, U1.1 (C13), U1.2 (C12), U1.3 (C11), U1.4 (C10), U1.5 (C9), U1.6 (C8), U1.46 (C16), U1.47 (C15), U1.48 (C14)
VCP: C219.2, C226.2, U1.42 (VCP)
VMID: C219.1, C220.2, C226.1, R214.2, U1.43 (VMID)
VTOP: C212.2, R212.2, U1.45 (VTOP)

Notes on the sheet:
02 AFE：MP2797 采集与保护（8S，C9–C16 并到 C8；WDT 悬空；xALERT 高有效 100k 下拉）
U1 = MP2797DFP-0000-T（C18198873，TQFP-48）。本页 U1 全部引脚以「短线 + 标签」引出；未用脚放 NC 标志（29 WDT / 33 SDO / 34–37 GPIO / 40 N/C / 41 SBYDSG）。
C9–C16（脚 5,4,3,2,1,48,47,46）用一条竖线并在 C8（脚 6）的 VC8 上，不串电阻、不加电容（Table 23「directly connect」）。
AFE_3V3 只接 C215，不与板上 +3V3 相连；NTC 四路上拉（R216–R219）都接 NTCB，不接任何 3V3。
§9 电源：BAT+ 供电（U-1）
U1.45 VTOP ← R212 20Ω ← BAT+；C212 470nF/100V 到 GND。
U1.25 REGIN ← Q201(MMBT5551) 发射极（C214 10µF/10V）；
Q201 基极 = REGCTRL、集电极 = REG_C；
C213 1µF、R213 510Ω：REG_C→BAT+。
§6 高边驱动（CHG/DSG/VCP/VMID/PACKP）
U1.43 VMID ← R214 100Ω ← FET_MID，C220 100nF/100V 到 GND。
U1.38 PACKP ← R215 100Ω ← PACK+，C221 10nF/100V 到 GND
（Table 18「不得增减」）。
U1.42 VCP ↔ VMID 跨接 C219 100nF/100V；
C226 为扩展焊盘（DNP，样板实测 VCP 跌落后再定）。
U1.44 CHG、U1.39 DSG 本页不串件，
R_DRV/DZ/PNP 快关在 01 页。
§10 J5 采样端子
C40669 XH 2.50mm 13P 立式；
1/3 = NTC_CELL1/2，2/4 = GND；
5–13 = CELL0…CELL8；
NTC 放低压端，线束短路
不会把 29V 灌进 NTC 脚。
§4 电芯采样（8 串 9 路）
J5.5–13 CELL0–CELL8 → R201–R209 33Ω 1% → VC0–VC8 → U1.14/13/12/11/10/9/8/7/6。
C201–C208 100nF/50V 跨相邻两个 VC（8 只，不接地）；C0 只挂 D201 稳压（阴极→VC0、阳极→GND）。
均衡电流走串阻：33Ω 时典型 39mA、最坏 45mA，0805 耗散余量 1.5 倍；本页不出现任何 BAL* 标签。
§5 电流采样（SRP/SRN 开尔文）
SRP/SRN 取自分流器电池侧（01 页），
经 R210/R211 100Ω → SRP_F/SRN_F → U1.15/U1.16；
C209 100nF 跨 SRP_F↔SRN_F（差模）；
C210/C211 各 100nF 到 GND（共模）。
§7 NTC ×4（电芯 2 路 + FET / 分流器）
R216–R219 = 10k 1% 上拉到 NTCB（不是 3V3）；C222–C225 = 1nF 为 DNP。
（NTCB_DYNAMIC_ON=1；装了会让低温读数偏低）
NTC_CELL1/2 走 J5.1/2 与 J5.3/4 的线束探头；
NTC_FET → 01 页 RT3；NTC_SHUNT → 01 页 RT4。
§8 通讯与中断（I2C / xALERT / NSHDN）
R220/R221 = 2.2k 1% 上拉到 +3V3（I2C 开漏必需）；
R222 = 100k 1% 把 AFE_ALERT 下拉到 GND（xALERT 推挽、
ALERT_POL 默认高有效，空闲低电平）；
R223 = 10k 1% 把 AFE_WAKE 上拉到 +3V3（不是 AFE_3V3）。
WDT（U1.29）悬空，已在 U1 侧放 NC 标志。
