colemandlut/MP2645A-BMS/review/03-r2/03_balancer.kicad_sch

## KiCad design review/03-r2/03_balancer.kicad_sch (2026-09-28)

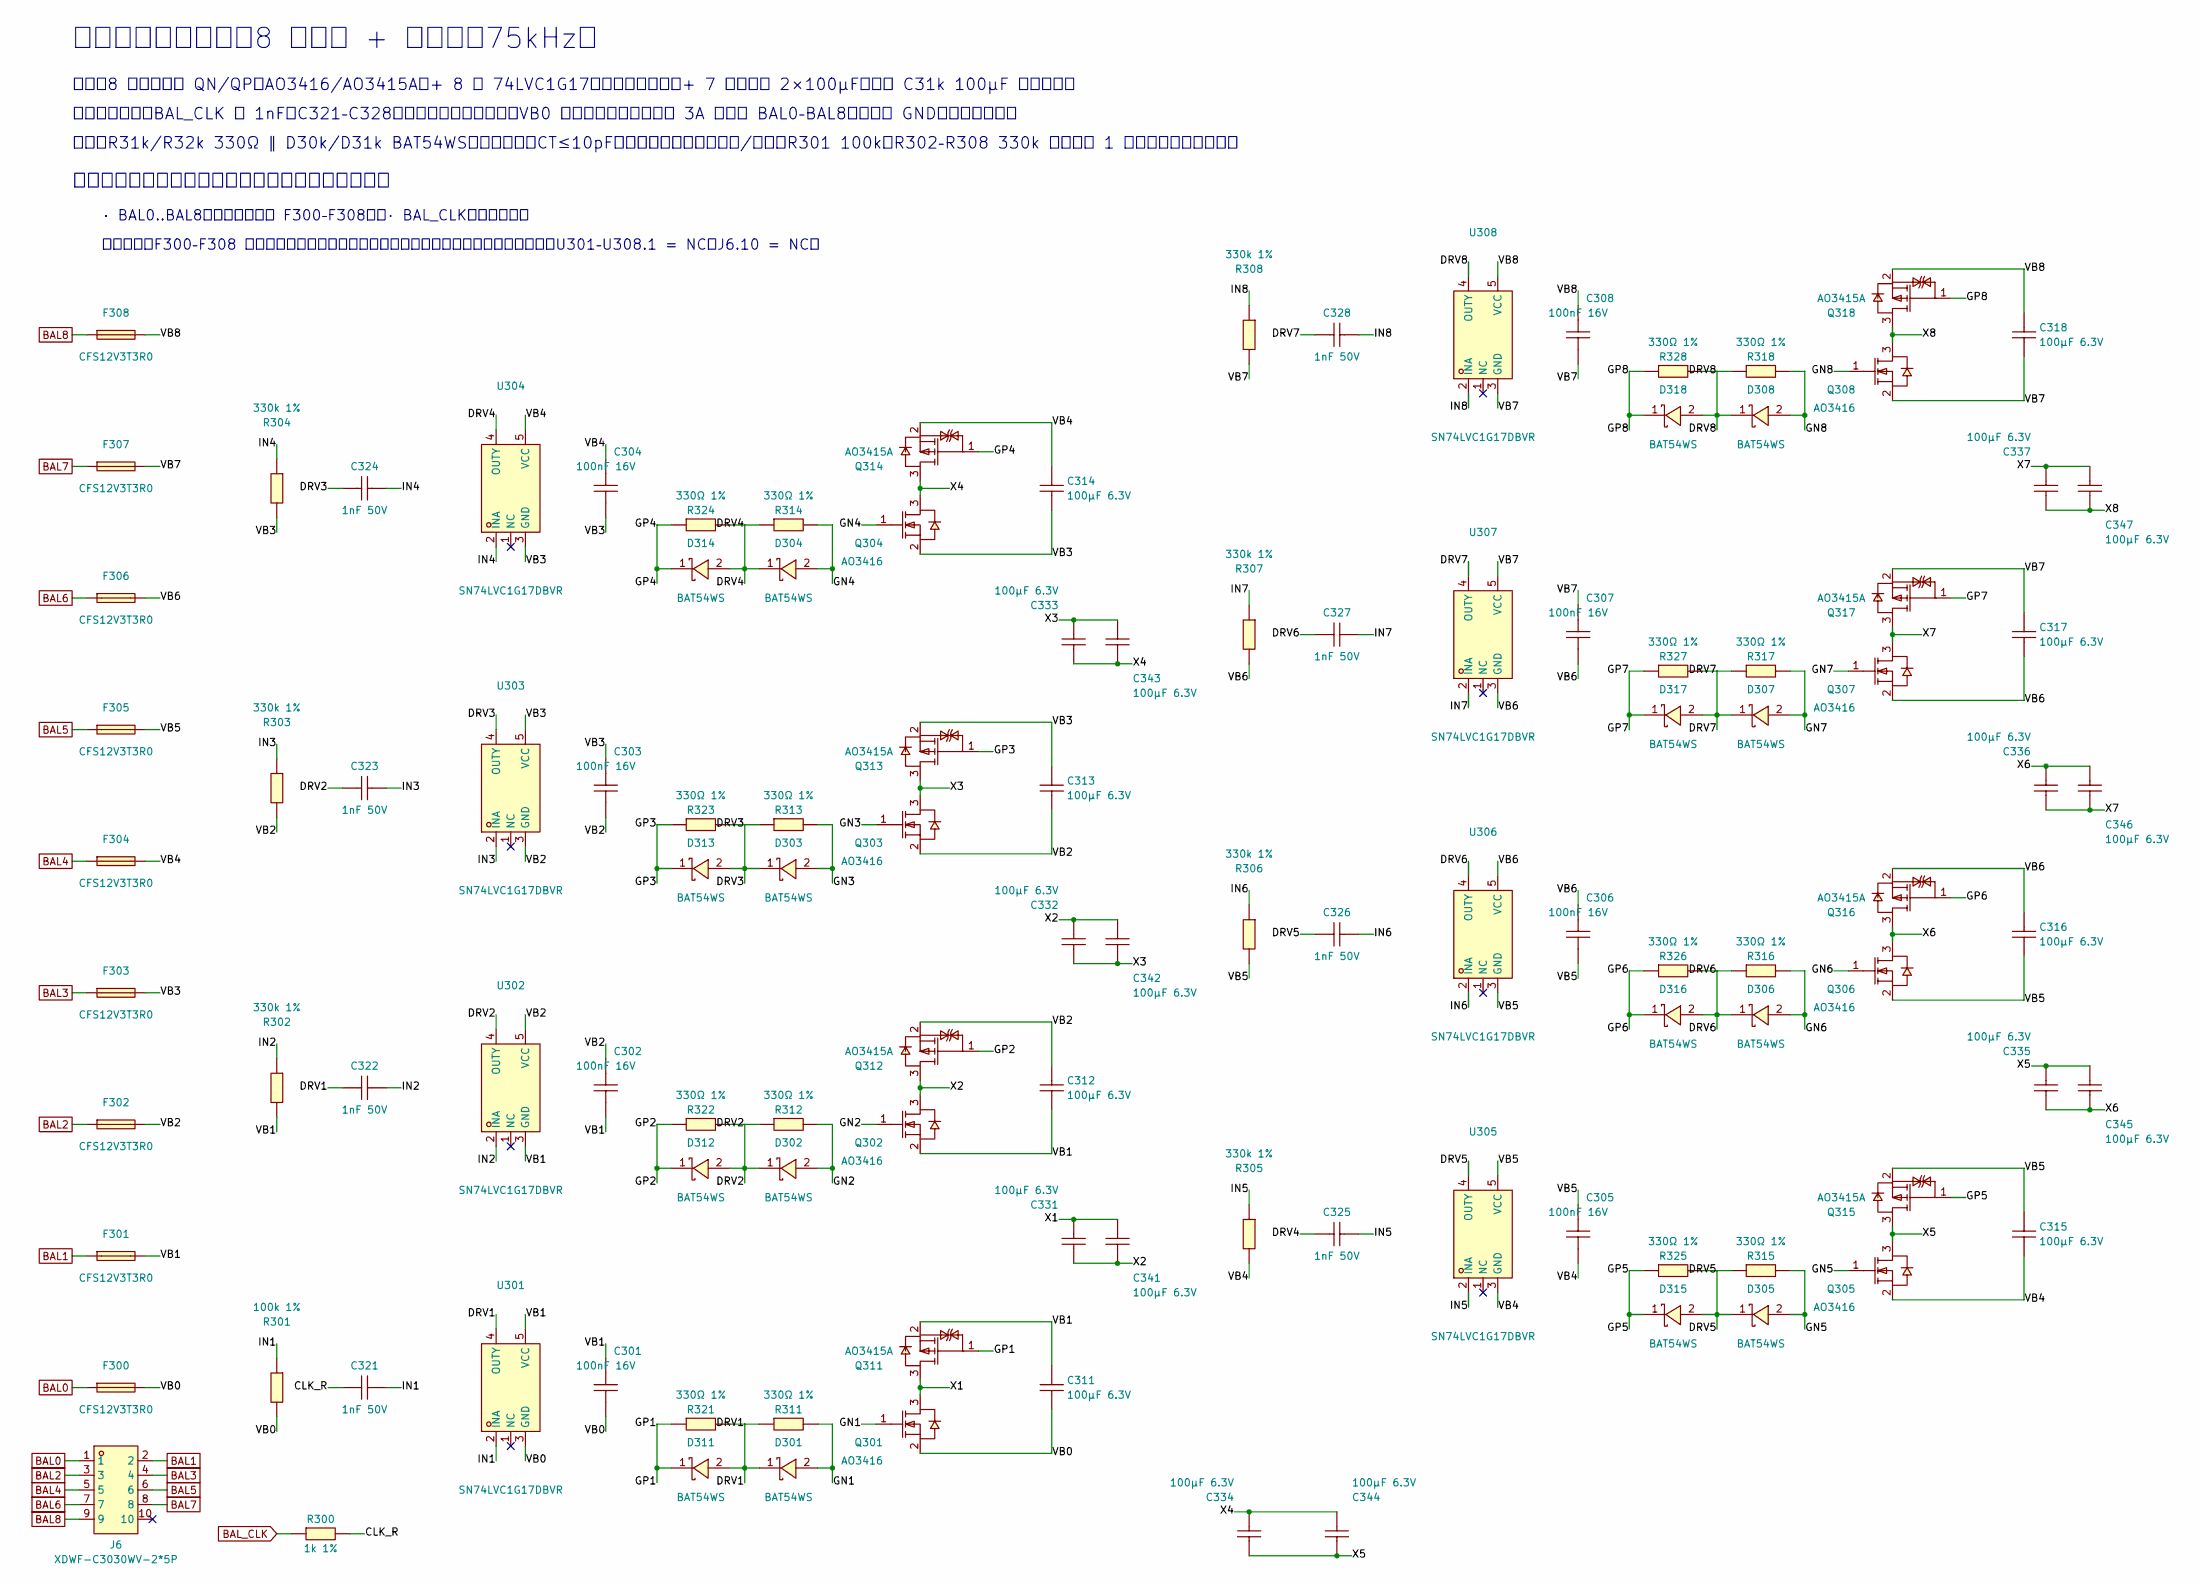
[picture p18: schematic 03_balancer.kicad_sch]

Parts:
C301, C302, C303, C304, C305, C306, C307, C308: 100nF 16V; C0402; LCSC C1525
C311, C312, C313, C314, C315, C316, C317, C318, C331, C332, C333, C334, C335, C336, C337, C341, C342, C343, C344, C345, C346, C347: 100µF 6.3V; C1206; LCSC C15008
C321, C322, C323, C324, C325, C326, C327, C328: 1nF 50V; C0402; LCSC C1523
D301, D302, D303, D304, D305, D306, D307, D308, D311, D312, D313, D314, D315, D316, D317, D318: BAT54WS; SOD-323_L1.8-W1.3-LS2.5-RD; LCSC C22629
F300, F301, F302, F303, F304, F305, F306, F307, F308: CFS12V3T3R0; F1206; LCSC C163126
J6: XDWF-C3030WV-2*5P; CONN-TH_XDWF-C3030WV-2-5P; LCSC C18202166
Q301, Q302, Q303, Q304, Q305, Q306, Q307, Q308: AO3416; SOT-23-3_L2.9-W1.3-P1.90-LS2.4-BR; LCSC C479060
Q311, Q312, Q313, Q314, Q315, Q316, Q317, Q318: AO3415A; SOT-23-3_L2.9-W1.6-P1.90-LS2.8-BR; LCSC C5350990
R300: 1k 1%; R0402; LCSC C11702
R301: 100k 1%; R0402; LCSC C25741
R302, R303, R304, R305, R306, R307, R308: 330k 1%; R0402; LCSC C25778
R311, R312, R313, R314, R315, R316, R317, R318, R321, R322, R323, R324, R325, R326, R327, R328: 330Ω 1%; R0402; LCSC C25104
U301, U302, U303, U304, U305, U306, U307, U308: SN74LVC1G17DBVR; SOT-23-5_L2.9-W1.6-P0.95-LS2.8-BR; LCSC C7394021

Connections:
BAL0: F300.1, J6.1
BAL1: F301.1, J6.2
BAL2: F302.1, J6.3
BAL3: F303.1, J6.4
BAL4: F304.1, J6.5
BAL5: F305.1, J6.6
BAL6: F306.1, J6.7
BAL7: F307.1, J6.8
BAL8: F308.1, J6.9
BAL_CLK: R300.1
CLK_R: C321.1, R300.2
DRV1: C322.1, D301.1 (K), D311.2 (A), R311.1, R321.2, U301.4 (OUTY)
DRV2: C323.1, D302.1 (K), D312.2 (A), R312.1, R322.2, U302.4 (OUTY)
DRV3: C324.1, D303.1 (K), D313.2 (A), R313.1, R323.2, U303.4 (OUTY)
DRV4: C325.1, D304.1 (K), D314.2 (A), R314.1, R324.2, U304.4 (OUTY)
DRV5: C326.1, D305.1 (K), D315.2 (A), R315.1, R325.2, U305.4 (OUTY)
DRV6: C327.1, D306.1 (K), D316.2 (A), R316.1, R326.2, U306.4 (OUTY)
DRV7: C328.1, D307.1 (K), D317.2 (A), R317.1, R327.2, U307.4 (OUTY)
DRV8: D308.1 (K), D318.2 (A), R318.1, R328.2, U308.4 (OUTY)
GN1: D301.2 (A), Q301.1 (G), R311.2
GN2: D302.2 (A), Q302.1 (G), R312.2
GN3: D303.2 (A), Q303.1 (G), R313.2
GN4: D304.2 (A), Q304.1 (G), R314.2
GN5: D305.2 (A), Q305.1 (G), R315.2
GN6: D306.2 (A), Q306.1 (G), R316.2
GN7: D307.2 (A), Q307.1 (G), R317.2
GN8: D308.2 (A), Q308.1 (G), R318.2
GP1: D311.1 (K), Q311.1 (G), R321.1
GP2: D312.1 (K), Q312.1 (G), R322.1
GP3: D313.1 (K), Q313.1 (G), R323.1
GP4: D314.1 (K), Q314.1 (G), R324.1
GP5: D315.1 (K), Q315.1 (G), R325.1
GP6: D316.1 (K), Q316.1 (G), R326.1
GP7: D317.1 (K), Q317.1 (G), R327.1
GP8: D318.1 (K), Q318.1 (G), R328.1
IN1: C321.2, R301.1, U301.2 (INA)
IN2: C322.2, R302.1, U302.2 (INA)
IN3: C323.2, R303.1, U303.2 (INA)
IN4: C324.2, R304.1, U304.2 (INA)
IN5: C325.2, R305.1, U305.2 (INA)
IN6: C326.2, R306.1, U306.2 (INA)
IN7: C327.2, R307.1, U307.2 (INA)
IN8: C328.2, R308.1, U308.2 (INA)
VB0: C301.2, C311.2, F300.2, Q301.2 (S), R301.2, U301.3 (GND)
VB1: C301.1, C302.2, C311.1, C312.2, F301.2, Q302.2 (S), Q311.2 (S), R302.2, U301.5 (VCC), U302.3 (GND)
VB2: C302.1, C303.2, C312.1, C313.2, F302.2, Q303.2 (S), Q312.2 (S), R303.2, U302.5 (VCC), U303.3 (GND)
VB3: C303.1, C304.2, C313.1, C314.2, F303.2, Q304.2 (S), Q313.2 (S), R304.2, U303.5 (VCC), U304.3 (GND)
VB4: C304.1, C305.2, C314.1, C315.2, F304.2, Q305.2 (S), Q314.2 (S), R305.2, U304.5 (VCC), U305.3 (GND)
VB5: C305.1, C306.2, C315.1, C316.2, F305.2, Q306.2 (S), Q315.2 (S), R306.2, U305.5 (VCC), U306.3 (GND)
VB6: C306.1, C307.2, C316.1, C317.2, F306.2, Q307.2 (S), Q316.2 (S), R307.2, U306.5 (VCC), U307.3 (GND)
VB7: C307.1, C308.2, C317.1, C318.2, F307.2, Q308.2 (S), Q317.2 (S), R308.2, U307.5 (VCC), U308.3 (GND)
VB8: C308.1, C318.1, F308.2, Q318.2 (S), U308.5 (VCC)
X1: C331.1, C341.1, Q301.3 (D), Q311.3 (D)
X2: C331.2, C332.1, C341.2, C342.1, Q302.3 (D), Q312.3 (D)
X3: C332.2, C333.1, C342.2, C343.1, Q303.3 (D), Q313.3 (D)
X4: C333.2, C334.1, C343.2, C344.1, Q304.3 (D), Q314.3 (D)
X5: C334.2, C335.1, C344.2, C345.1, Q305.3 (D), Q315.3 (D)
X6: C335.2, C336.1, C345.2, C346.1, Q306.3 (D), Q316.3 (D)
X7: C336.2, C337.1, C346.2, C347.1, Q307.3 (D), Q317.3 (D)
X8: C337.2, C347.2, Q308.3 (D), Q318.3 (D)

Notes on the sheet:
开关电容主动均衡（8 级半桥 + 飞电容，75kHz）
内容：8 个互补半桥 QN/QP（AO3416/AO3415A）+ 8 个 74LVC1G17（本节电芯供电）+ 7 级飞电容 2×100µF；每节 C31k 100µF 本地储能。
全级交流耦合：BAL_CLK 经 1nF（C321–C328）逐级耦合，首级亦然（VB0 不接地）；均衡节点经 3A 熔丝到 BAL0–BAL8；本页无 GND、无电源符号。
死区：R31k/R32k 330Ω ∥ D30k/D31k BAT54WS（慢开快关，CT≤10pF）防上下管直通；停时钟/复位：R301 100k、R302–R308 330k 下拉，第 1 级先泄放完避免混相。
接口网络（跨页用全局标签，名称以本清单为准）：
· BAL0..BAL8（均衡节点，经 F300–F308）；· BAL_CLK（时钟输入）
已知风险：F300–F308 保护不了线束段，线束电芯端保险丝未加（用户决定的已知风险）；U301–U308.1 = NC；J6.10 = NC。
