colemandlut/MP2645A-BMS/review/05-r4/04_power_supply.kicad_sch

## KiCad design review/05-r4/04_power_supply.kicad_sch (2026-09-27)

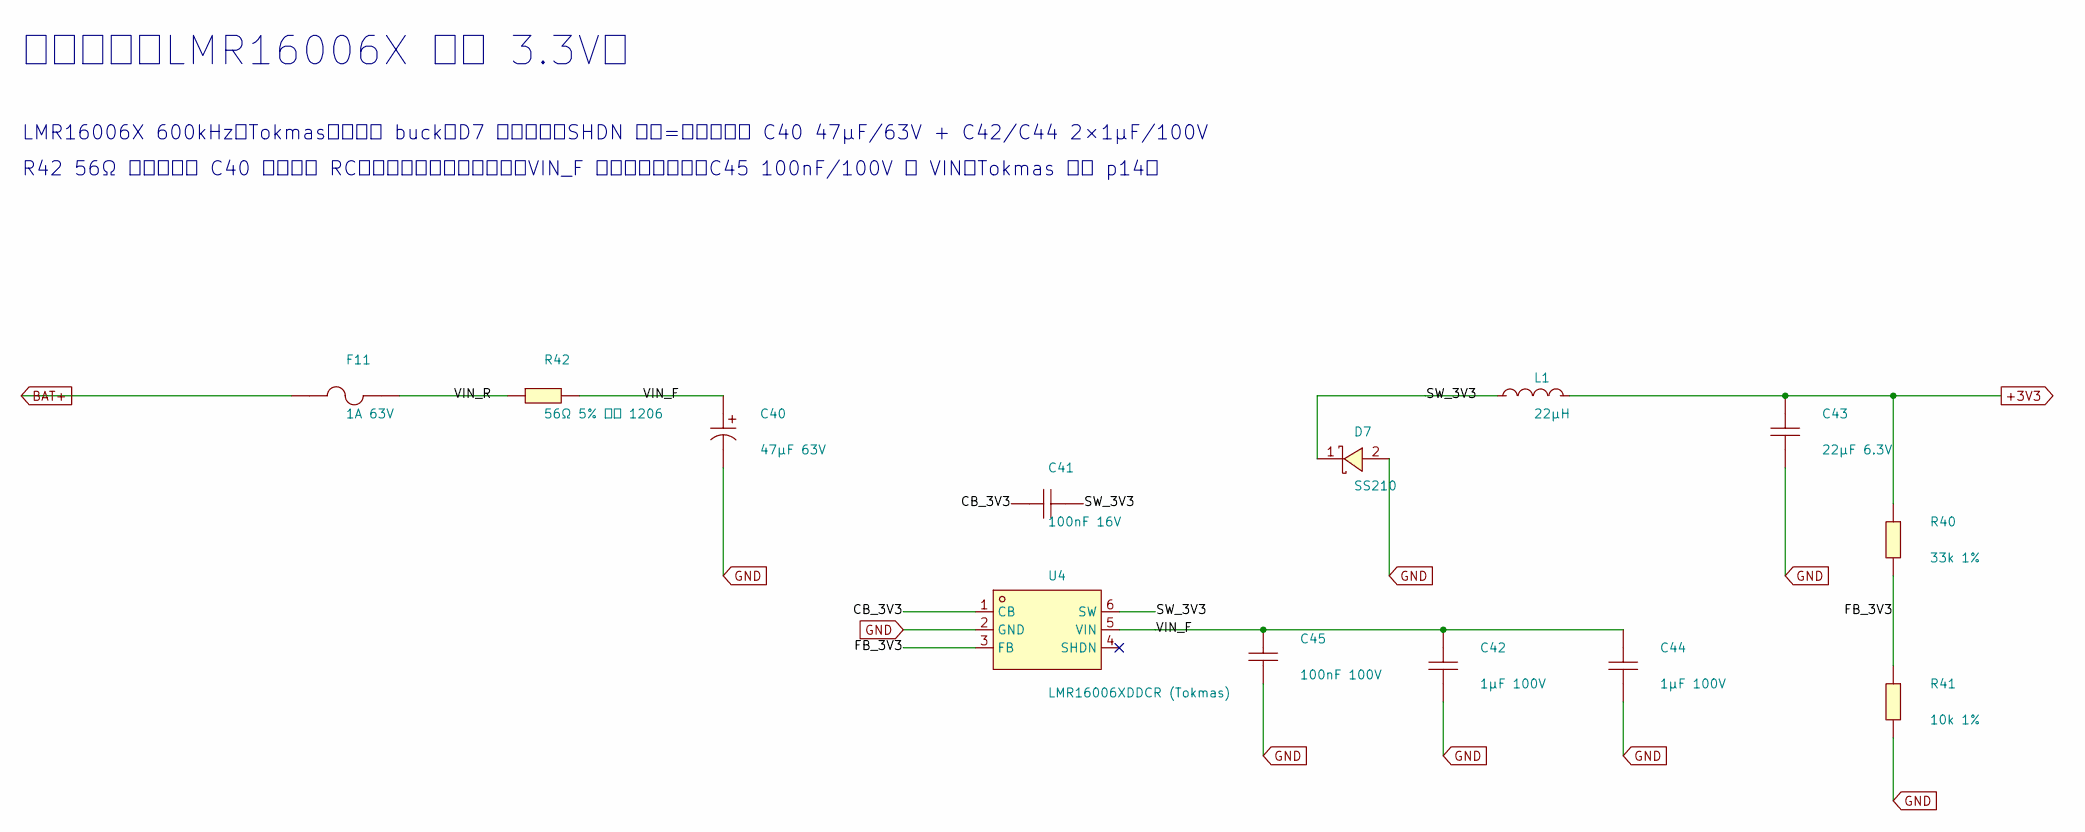
[picture p19: schematic 04_power_supply.kicad_sch]

Parts:
C40: 47µF 63V; CAP-SMD_BD6.3-L6.6-W6.6-LS7.3-FD; LCSC C48971005
C41: 100nF 16V; C0402; LCSC C1525
C42, C44: 1µF 100V; C1206; LCSC C282823
C43: 22µF 6.3V; C0603; LCSC C59461
C45: 100nF 100V; C0805; LCSC C28233
D7: SS210; SMA_L4.3-W2.6-LS5.2-RD; LCSC C14996
F11: 1A 63V; F1206; LCSC C136343
L1: 22µH; IND-SMD_L5.0-W5.0; LCSC C68434
R40: 33k 1%; R0402; LCSC C25779
R41: 10k 1%; R0402; LCSC C25744
R42: 56Ω 5% 熔断 1206; R1206; LCSC C153337
U4: LMR16006XDDCR (Tokmas); SOT-23-6_L2.9-W1.6-P0.95-LS2.8-BR; LCSC C54823941

Connections:
+3V3: C43.2, L1.2, R40.1
BAT+: F11.1
CB_3V3: C41.1, U4.1 (CB)
FB_3V3: R40.2, R41.1, U4.3 (FB)
GND: C40.2, C42.1, C43.1, C44.1, C45.1, D7.2 (A), R41.2, U4.2 (GND)
SW_3V3: C41.2, D7.1 (K), L1.1, U4.6 (SW)
VIN_F: C40.1, C42.2, C44.2, C45.2, R42.2, U4.5 (VIN)
VIN_R: F11.2, R42.1

Notes on the sheet:
辅助电源（LMR16006X 直降 3.3V）
LMR16006X 600kHz（Tokmas）非同步 buck；D7 续流必需；SHDN 悬空=常开；输入 C40 47µF/63V + C42/C44 2×1µF/100V
R42 56Ω 熔断电阻与 C40 构成输入 RC：限上电浪涌与短路电流，VIN_F 短路时受控开路；C45 100nF/100V 贴 VIN（Tokmas 手册 p14）
