colemandlut/MP2645A-BMS/review/05-r4/05_mcu_comm.kicad_sch

## KiCad design review/05-r4/05_mcu_comm.kicad_sch (2026-09-27)

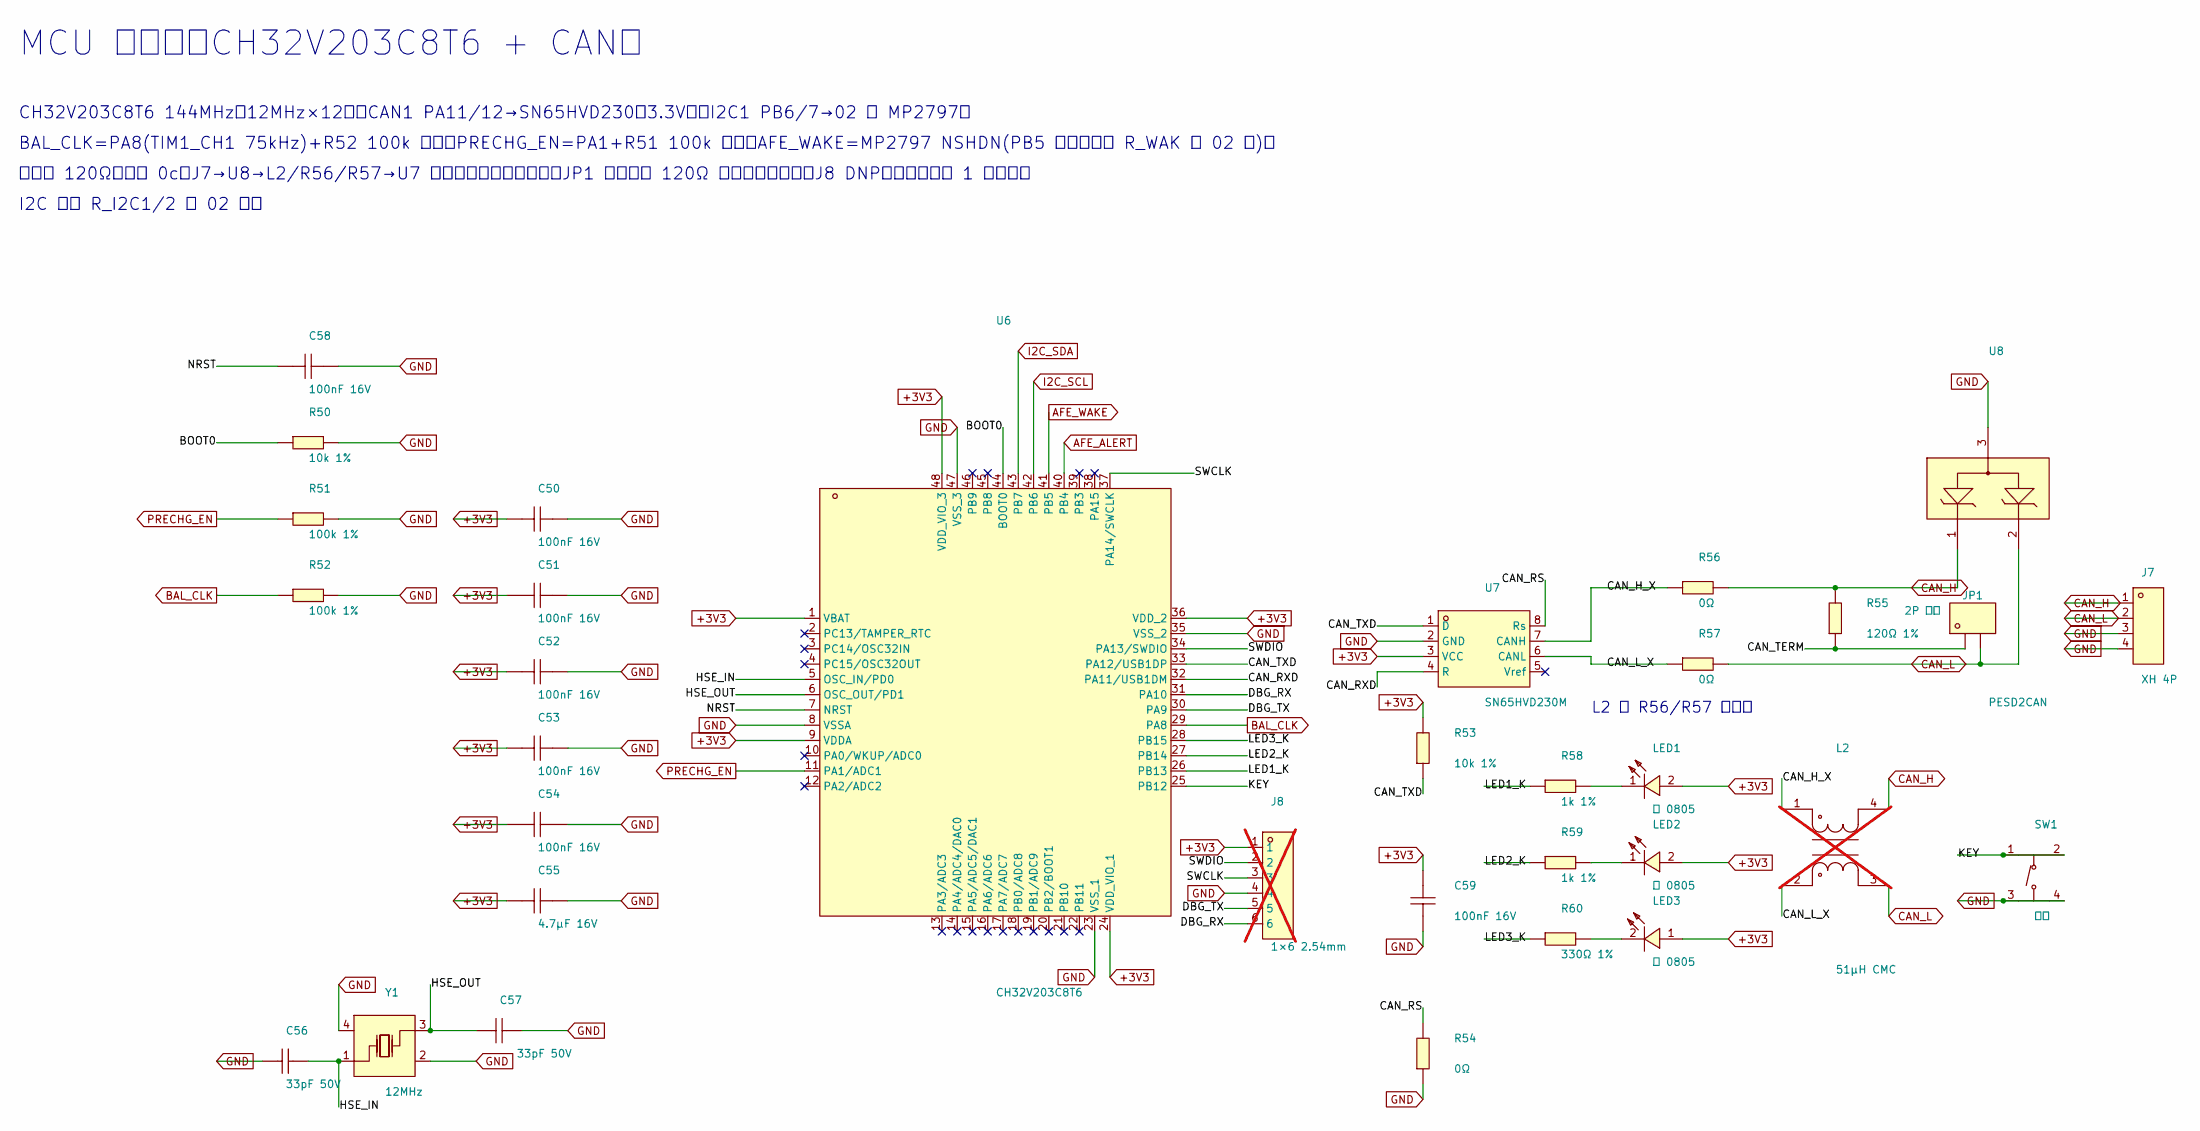
[picture p20: schematic 05_mcu_comm.kicad_sch]

Parts:
C50, C51, C52, C53, C54, C58, C59: 100nF 16V; C0402; LCSC C1525
C55: 4.7µF 16V; C0603; LCSC C19666
C56, C57: 33pF 50V; C0402; LCSC C1562
J7: XH 4P; CONN-TH_4P-P2.50_4PIN; LCSC C7429634
J8: 1×6 2.54mm; HDR-TH_6P-P2.54-V-M; LCSC C492405; not fitted
JP1: 2P 排针; HDR-TH_2P-P2.54-V-M; LCSC C492401
L2: 51µH CMC; FILTER-SMD_4P-L3.2-W2.5-BL_ACT1210; LCSC C95572; not fitted
LED1, LED2: 红 0805; LED0805-RD; LCSC C84256
LED3: 绿 0805; LED0805-R-RD; LCSC C2297
R50, R53: 10k 1%; R0402; LCSC C25744
R51, R52: 100k 1%; R0402; LCSC C25741
R54, R56, R57: 0Ω; R0402; LCSC C17168
R55: 120Ω 1%; R0603; LCSC C22787
R58, R59: 1k 1%; R0402; LCSC C11702
R60: 330Ω 1%; R0402; LCSC C25104
SW1: 按键; SW-SMD_4P-L5.1-W5.1-P3.70-LS6.5-TL_H1.5; LCSC C318884
U6: CH32V203C8T6; LQFP-48_L7.0-W7.0-P0.50-LS9.0-BL; LCSC C3001172
U7: SN65HVD230M; SOIC-8_L5.0-W4.0-P1.27-LS6.0-BL; LCSC C55259679
U8: PESD2CAN; SOT-23-3_L2.9-W1.3-P1.90-LS2.4-BR; LCSC C2687131
Y1: 12MHz; CRYSTAL-SMD_4P-L3.2-W2.5-BL; LCSC C9002

Connections:
+3V3: C50.1, C51.1, C52.1, C53.1, C54.1, C55.1, C59.2, J8.1, LED1.2 (+), LED2.2 (+), LED3.1 (A), R53.2, U6.1 (VBAT), U6.9 (VDDA), U6.24 (VDD_VIO_1), U6.36 (VDD_2), U6.48 (VDD_VIO_3), U7.3 (VCC)
AFE_ALERT: U6.40 (PB4)
AFE_WAKE: U6.41 (PB5)
BAL_CLK: R52.1, U6.29 (PA8)
BOOT0: R50.1, U6.44 (BOOT0)
CAN_H: J7.1, L2.4, R55.2, R56.2, U8.1
CAN_H_X: L2.1, R56.1, U7.7 (CANH)
CAN_L: J7.2, JP1.2, L2.3, R57.2, U8.2
CAN_L_X: L2.2, R57.1, U7.6 (CANL)
CAN_RS: R54.2, U7.8 (Rs)
CAN_RXD: U6.32 (PA11/USB1DM), U7.4 (R)
CAN_TERM: JP1.1, R55.1
CAN_TXD: R53.1, U6.33 (PA12/USB1DP), U7.1 (D)
DBG_RX: J8.6, U6.31 (PA10)
DBG_TX: J8.5, U6.30 (PA9)
GND: C50.2, C51.2, C52.2, C53.2, C54.2, C55.2, C56.1, C57.2, C58.2, C59.1, J7.3, J7.4, J8.4, R50.2, R51.2, R52.2, R54.1, SW1.3 (C), SW1.4 (D), U6.8 (VSSA), U6.23 (VSS_1), U6.35 (VSS_2), U6.47 (VSS_3), U7.2 (GND), U8.3, Y1.2 (GND), Y1.4 (GND)
HSE_IN: C56.2, U6.5 (OSC_IN/PD0), Y1.1 (OSC1)
HSE_OUT: C57.1, U6.6 (OSC_OUT/PD1), Y1.3 (OSC2)
I2C_SCL: U6.42 (PB6)
I2C_SDA: U6.43 (PB7)
KEY: SW1.1 (A), SW1.2 (B), U6.25 (PB12)
LED1_K: R58.1, U6.26 (PB13)
LED2_K: R59.1, U6.27 (PB14)
LED3_K: R60.1, U6.28 (PB15)
NRST: C58.1, U6.7 (NRST)
unnamed: LED1.1 (-), R58.2
unnamed: LED2.1 (-), R59.2
unnamed: LED3.2 (K), R60.2
PRECHG_EN: R51.1, U6.11 (PA1/ADC1)
SWCLK: J8.3, U6.37 (PA14/SWCLK)
SWDIO: J8.2, U6.34 (PA13/SWDIO)

Notes on the sheet:
MCU 与通讯（CH32V203C8T6 + CAN）
CH32V203C8T6 144MHz（12MHz×12）；CAN1 PA11/12→SN65HVD230（3.3V）；I2C1 PB6/7→02 页 MP2797；
BAL_CLK=PA8(TIM1_CH1 75kHz)+R52 100k 下拉；PRECHG_EN=PA1+R51 100k 下拉；AFE_WAKE=MP2797 NSHDN(PB5 开漏，上拉 R_WAK 在 02 页)；
差分对 120Ω（规则 0c：J7→U8→L2/R56/R57→U7 直通道，顶层不换层）；JP1 插帽接入 120Ω 终端，拔帽不用；J8 DNP，下载器勿从 1 脚供电。
I2C 上拉 R_I2C1/2 在 02 页。
L2 与 R56/R57 二选一
